alexiosc/cft/documentation/latex/cft_book/cft-hard-fdc.tex

% -*- latex -*-

\HtmlMetaDescription{This chapter (still empty) describes the Floppy
  Drive Controller (FDC) board which allows the connection of up to
  four floppy drives to the CFT. Both Shugart and IBM-style interfaces
  are supported, so that 8-inch units can be attached too.}
%\HtmlMetaGoogleDescription{}
%\HtmlMetaBanner{}
%\HtmlMetaTags{}

\section{Design}

\section{Theory of Operation}

\section{Implementation}

\section{Operation}

\section{Schematics}

The following page shows the full schematic drawing of the FDC
board.

\cleardoublepage
\includeschns{47}{Floppy Drive Controller}{sch2:fdc}
