alexiosc/cft/documentation/latex/cft_book/cft-hard-vdu.tex

% -*- latex -*-
\HtmlMetaDescription{The Video Display Board gives the CFT the ability to display colourful graphics on a monitor, and allows keyboards (and potentially mice) to be attached.}
%\HtmlMetaGoogleDescription{}
%\HtmlMetaBanner{}
%\HtmlMetaTags{}

\label{chap:hard-vdu}

The VDU card is a semi-intelligent Video Display Unit controller inspired by
both the Motorola MC6845 (and various designs based on it) and the Texas
Instruments TMS9918. It is capable of a number of useful features designed to
offload simple tasks from the processor:

\begin{itemize}
\item 640×480 and 320×480 native resolutions.
\item Square pixels at a 4:3 aspect ratio.
\item Text modes include: 40×30, 40×60, 80×30 and 80×60.
\item Low resolution graphics from 40×30 to 160×120.
\item High resolution bitmap graphics include 320×240, 320×480, 640×240 and
  640×480.
\item Any permuation of horizontal and vertical resolution can be used,
  including ones with exotic pixel aspect ratios.
\item Analogue VGA Output.
\item 64 colours (6 bits per pixel) with no look-up tables (palettes).
\item Hardware cursor with blink and colour control.
\item Inverse and Blink attributes.
\item Fully reprogrammable character generator capable of 4,096 16-line
  characters.
\item Up to 1,024 different characters can appear per mode.
\item 24-bit planar storage model multiplexed on 256K×16 Static RAM memory.\footnote{Physical memory may be larger than needed.}
\item Limited terminal-like behaviour.
\item Smooth (pixel-level) horizontal and vertical srolling.
\item Cell-level scrolling and paging in all modes using a 128×512 virtual
  screen.
\item Fully programmable independent split screen modes (top-bottom).
\item Can generate interrupts on vertical sync or when an arbitrary scanline is
  reached.
\end{itemize}

Some of these features were implemented as ‘bells and whistles’ (the generic
nature of split screens and smooth scrolling is an example), but most are side
effects of the simplicity of the rest of the design.

Much of this chapter assumes knowledge of how raster displays work. A full
explanation is beyond the scope of this document, but many can be found online.

\todo{Move these unconnected sections into the standard outline.}

\section{History}

The VDU card has undergone various revisions. The original version
used discrete HC family CMOS logic, and was meant to drive up to
640×400 using the canonical 25.175~MHz VGA pixel clock.

The second revision refined the design, keeping the discrete logic. It
was simulated successfully up to a point, but meeting constraints and
fixing timing bugs became too much of a hassle.

The third revision rebuilt the design on a Xilinx CPLD using the same
resolution and pixel clock.

The fourth and current revision migrated to an Altera Max V CPLD. The
resolution increased to 640×480 using a slightly non-standard 32~MHz
clock — the standard VGA clock is 31.5~MHz. The pixel clock is derived
from a 64~MHz clock used to drive a complex SDRAM memory controller
state machine.

\section{Design}

The main design constraint for the VDU card has been allowing easy access from
the CFT host to the video memory. Most home computer with video capacibilities
were designed {\em around\/} their graphic subsystems rather than vice
versa. This was often done to the extreme: in many cases, the processor clock
rate was lowered a lot to simplify the host/video memory sharing logic. In the
case of the CFT this was never a consideration, and so the processor and VDU
subsystem are in two different clock domains. The CFT runs in a 4 MHz clock
domain, while the VDU card runs in a 25 MHz clock domain.

Also, the CFT uses banked memory, and this considerably limits the convenience
of accessing memory directly, as well as the amount of memory that can easily
be mapped.

The solution to both problems is (somewhat counter-intuitively) to {\em
  never\/} let the CFT access video display memory directly. Once video memory
is entirely the domain of the VDU card, its design is simplified greatly.

Instead of direct access to the memory, an indirect system is provided. In this
way, both the processor and VDU can run at optimal speeds, and communicate
asynchronously.

\subsection{VDU Engine}

The VDU card is designed to be built around a CPLD chip. Like the DEB card,
this may be seen as ‘breaking project rules’, but I have my reasons:

\begin{itemize}
\item Ability to debug. More likely than not, I would need to locate and fix
  numerous issues with the implementation after construction. This would be
  much easier with a CPLD, where the connections between units are described
  rather than made with a soldering iron.
\item Board size. Early on in the project, the VDU board started to compete
  against the processor boards in size and complexity. The chip count of the
  yet unfinished board was nearly 100.
\item Cost. Board size, chip count, and complexity directly translate to
  cost. Building the processor is the heart of the project — having the VDU
  card is nice, but beyond the original scope of the project.
\item Timings. A CPLD chip has 1ns propagation delays. With discretes,
  a large portion of the design effort centres around not violating
  timing constraints.
\item Better derating margins. CPLD chips are designed to run at over
  100~MHz, and this design runs mostly at 32~MHz, with a small portion
  clocked at 64~MHz.
\item Chip availability. A number of 74AC family chips are required
  due to their low (6ns) propagation delays. These are quite hard to
  find in through-hole packages, and costlier.
\item Image quality. I have a good eye, and bad image quality grates on me. With a
  CPLD chip the timings can be tighter, and display quality can be crisp
  without pushing the limits of the technology.
\item Still a learning experience. This would be my first ever surface mount
  project, my first CPLD project, my second 3.3V-based project, my first
  multi-voltage project, and my first video-generating project.
\item Backplane space. There are 19 slots on the CFT backplane, and I would
  like to avoid using all of them. With a CPLD, the entire design can fit
  comfortably on one board.
\end{itemize}

This change in direction may affect other boards, too, to keep costs down.

Using a CPLD opens up the design to cheaper, 3.3V components, but it
also makes it significantly simpler. There are seven active components
on the board: the CPLD, three SRAM chips, two \HCT{245} buffers used
as level shifters, and a 64~MHz oscillator. A rendered version of this
board can be seen in~\fcf{fig:vdu-board}.

\begin{figure}
\centering
\includelarge[width=0.85\columnwidth]{figs/video-max5-revF-top.jpg}\vspace{1em}\\
\caption{\label{fig:vdu-board}A rendered image of the VDU board. The CPLD makes
  the design quite sparse, and routing the board is easy — after all, the pins
  can be assigned any function and re-ordered at will to match the board
  layout.}
\end{figure}

\subsection{Video Format}

A video frame consists of a number of scan lines, each made of a
number of pixels, as shown in~\fcf{fig:video-frame-format}.

Each line is sent to the display serially, left to right. To help monitor
timing, lines start with a horizontal sync pulse (\ns{HSYNC}) to help
synchronise the framebuffer and display. This pulse is preceded by a number of
‘blank’ pixels known as the ‘front porch’, and followed by a similar zone
called the ‘back porch’. The horizontal sync pulse signals the display to begin
a new field. So, counter-intuitively, the front porch is the {\em end\/}
(right) of the previous field, and the back porch is the beginning of the
next. The formal horizontal waveform is shown in~\fcf{fig:vdu-horz-timing}.

Multiple fields are sent to the display serially, top to bottom. A blanked Front
Porch is sent first, followed by a vertical sync pulse (\ns{VSYNC}), followed
by a Back Porch and a number of fields in the format described above. Since
\ns{VSYNC} instructs the display to move to the top of the screen, starting a
new frame, the vertical Front Porch will appear at the bottom of the {\em
  previous\/} frame, while the Back Porch will appear at the top of the next
frame. The formal vertical waveform is shown in~\fcf{fig:vdu-vert-timing}.

The width of each of these subfields of each field and frame is expressed in
ticks of a {\em pixel clock\/}. A video format or mode is thus defined in terms
of the following nine parameters (often expressed in terms of other parameters,
arithmetically derived from these):

\begin{itemize}
\item The frequency or period of the pixel clock. This controls the physical size of each pixel on the screen, as well as the display resolution. It serves as the unit of timing, and all other parameters are expressed in terms of integer multiples of the pixel clock period.
\item The number of horizontal front porch pixels.
\item The number of horizontal video pixels. This is the same as the horizontal resolution in pixels.
\item The number of horizontal back porch pixels.
\item The number of pixels for which horizontal sync is active.
\item The number of vertical front porch pixels.
\item The number of vertical video pixels. This is the same as the vertical resolution in pixels.
\item The number of vertical back porch pixels.
\item The number of pixels for which vertical sync is active.
\end{itemize}

The CFT's VDU produces a single timing mode which produces an almost standard
VESA 640×480 resolution (at 74 frames per second, where VESA specifies 75)
using the following timings:

\begin{center}
\label{table:vdu-timings}
\zebra
\begin{tabular}{lrlrl}
            & Value & Unit & Time & Unit \\
\hline
Pixel clock frequency            &   32.000 & MHz    &  31.2500 & ns \\
\hline
Horizontal Front Porch width     &       24 & pixels &  0.7500 & μs \\
Horizontal Sync width            &       40 & pixels &  1.2500 & μs \\
Horizontal Back Porch width      &      128 & pixels &  4.0000 & μs \\
Horizontal Line width            &      640 & pixels & 20.0000 & μs \\
Total line width                 &      832 & pixels & 26.0000 & μs \\
Line (horizontal sync) frequency &   38.462 & kHz    & 26.0000 & μs \\
\hline
Vertical Front Porch height      &        9 & lines &   0.2340 & ms \\
Vertical Sync height             &        3 & lines &   0.0780 & ms \\
Vertical Back porch height       &       28 & lines &   0.7280 & ms \\
Vertical video height            &      480 & lines &  12.4800 & ms \\
Total frame height               &      520 & lines &  13.5200 & ms \\
Frame frequency (refresh rate)   &   73.965 & Hz    &  13.5200 & ms \\
\hline
\end{tabular}
\end{center}

These timings were generated using the VESA Co-ordinated Timing Generator
spreadsheet\footnote{Available at
  \url{http://files.bedroomlan.org/cft/video-board/CVTd6r1.xls}.} to maximise
compatibility and were tested on a number of monitors.

A horizontal resolution of 640 was chosen because it allows for 80 columns of
8-pixel wide characters. The vertical resolution of 480 was a more difficult
choice. 480 lines provide a classical 4:3 aspect ratio. Even though this is
running at a very slightly non-standard refresh rate, it is well within
tolerance for most, if not all multisync devices and works particularly well
with TFT monitors, producing images as crisp as can be expected from an
interpolated scaled up image.

A number of other resolutions were originally considered and ruled out:

\begin{itemize}
\item the 320×200 MCGA resolution is actually a 640×400 resolution with
  horizontal and vertical pixel doubling, implemented this way because the
  horizontal scan frequency of single-frequency VGA monitors was 31.15~kHz. As
  such, this would reduce the pixel resolution but still have the same timing
  requirements.
\item the 640×200 CGA resolution is, again, a 640×400 resolution with vertical
  line doubling and pixels with an aspect ratio of 8:3 — not particularly
  pleasing or useful. Since the horizontal resolution is the biggest hurdle in
  timing, this was also abandoned.
\item The 640×350 EGA-compatible resolution is a VGA 640×400 resolution with taller front
  and back porches, and the wrong pixel aspect ratio for modern monitors. Like
  the resolutions above, it made no sense to use it.
\item 640×400 was also attempted, and the design ran on this resolution for a
  while.  This is a 16:10 aspect ratio mode, so displays either slightly
  distorted on modern 16:9 devices, or using pillarboxes (narrow black bars at
  the left and right edge of the screen). This depends on the monitor
  used. However, many TFT monitors had trouble displaying a crisp image at this
  resolution. Additionally, the standard VGA pixel clock (25.175~MHz) for
  640×400 could not be used: the VDU design needed a clock double that of the
  pixel clock to allow both video and host accesses to the video memory, and
  there are no 50.35~MHz oscillators in the market.
\end{itemize}

\begin{figure}
 \centering     
 \inputfigure{figure-vdu-frame-format}
 \caption[Video frame format]{\label{fig:video-frame-format} Format of a video
   frame, showing porches, sync signals and video data. The frame is not drawn
   to scale. The definitions of ‘front’ and ‘back’ are sometimes reversed.}
\end{figure}

\subsection{Output Format}

Video data is output via a standard analogue VGA socket, as illustrated
in~\fcf{fig:vdu-vga-pinout}. The video data is split into RGB data and
synchronisation signals.

Video data is output in separate Red, Green and Blue channels as analogue
waveforms in the range 0–0.7V, where 0V ideally represents an absence of colour
in that channel, and 0.7V represents full intensity of that colour. The VDU
card can put four voltages on each line (shown in~\fcfp{fig:vdu-analogue-ramp}):

\begin{center}
\zebra
\begin{tabular}{rccc} 
  Voltage & Intensity & Value & Equivalent X11 hex value \\
  \hline
  0~mV      & 0\%      & 0 &  \hex{00} \\
  233~mV    & 33\%     & 1 & \hex{55} \\
  466~mV    & 66\%     & 2 & \hex{AA} \\
  700~mV    & 100\%    & 3 & \hex{FF} \\
  \hline
\end{tabular}
\end{center}

Since each channel may have four values and there are three channels, there are
$4^3=64$ total colours available. These intensities are identical to the
intensities used in the vast majority of 64-colour display platforms, including
the IBM CGA (though the CGA could only generate 16 of these colours) and IBM
EGA. The entire gamut of colours is illustrated
in~\fcf{fig:vdu-colour-palette}\footnote{But only in principle — printed
documents cannot display video colours correctly.}.

In the spirit of supporting badly calibrated or designed drivers, many monitors
allow for variations in the voltage ramp: some monitors calibrate the minimum
intensity based on voltage measurements during horizontal or vertical
sync. Other devices extend the maximum intensity based on what the driver is
producing, perhaps up to 1V. The VESA standard dictates 0–700mV, however.

\begin{figure*}
  \centering
  \inputfigure[width=6cm]{figs/DE15_Connector_Pinout}
  \vspace{1em}\par

  \zebra
  \begin{tabular}{rlll}
    Pin & Standard VGA & CFT VDU \\
    \hline
    1  & Red video & Red video \\
    2  & Green video & Green video \\
    3  & Blue video & Blue video \\
    4  & ID2/Reserved & Not connected \\
    5  & Ground & Ground \\
    6  & Red return & Analogue ground \\
    7  & Green return & Analogue ground \\
    8  & Blue return & Analogue ground \\
    9  & Key/+5V~DC & +5V~DC \\
    10 & Ground & Ground \\
    11 & ID0/Reserved & Not connected \\
    12 & ID1/SDA & Not connected \\
    13 & Horizontal sync & Horizontal sync \\
    14 & Vertical sync & Vertical sync \\
    15 & ID3/SCL & Not connected \\
    \hline
  \end{tabular}
  \caption[VGA Connector Pin-Out]{\label{fig:vdu-vga-pinout}VGA Connector
    pin-out. This is a view of the mating side of a VGA socket. The \ps{ID0–3}
    signals are obsolete and have been replaced (on a conformant VGA) with an
    I²C two-wire interface to transfer monitor parameters to the host. This is
    ignored on the CFT. The ‘key’ pin was missing on original VGAs to allow
    socket keying, but now carries 5V power.}
\end{figure*}

\begin{figure}
 \centering
 \inputfigure{figure-vdu-analogue-ramp}
 \caption[Analogue Channel Ramp]{\label{fig:vdu-analogue-ramp} Analogue channel
   ramp. The black line represents the VDU's ramp superimposed on the ideal
   (analogue) ramp.}
\end{figure}

\subsection{Memory}

The VDU board addresses 17 bits of 16-bit memory, for a 262,144×16 address
space. This memory is implemented as a single static RAM chip with an access
time of 15~ns or below. This memory is used for three distinct memory blocks,
discussed in~\cf{sec:vdu:memory-org}. Using a single chip keeps the design
simpler, reduces the number of bus signals between the CPLD and memory, keeps
signal integrity high by minimising trace lengths, and simplifies routing the
PCB.

\subsection{Indirect Host Access}

Rather than a complex scheme of multiplexed memory accesses, the VDU card
accesses its memory privately. To facilitate host access, it makes available
addresses, data and VDU commands via I/O ports. All communication with the
processor is now achieved via a mere three registers, with additional ones used
to change other variables of the VDU subsystem.

On most computers, a three-port access would constitute a severe
bottleneck. This is certainly the case for architectures with relative indirect
addressing and linear memory. On the CFT, however, accessing a linearly mapped
VDU device would involve performing address arithmetic, storing the result in a
register, then using this value to perform an indirect memory access. This is
precisely the way it is done by the VDU card. Rather than using a memory space
register to store the intermediate address result, a VDU register is used
instead. Commands allow autoincrement of these addresses in the X and/or Y
direction, and reduce the number of CFT instructions needed to perform most
tasks.

Commands are dispatched to the VDU card asynchronously (as far as it is
concerned), and executed at first opportunity. This can be longer than a CFT
write cycle, especially when using repeated commands. Four techniques may be
combined freely to detect if a command has completed execution:

\begin{enumerate}
\item Polling the \port{CRR} register (for repeated commands only). While the
  value is non-zero, the VDU is busy.
\item Polling the \field{GO} bit in the \port{CMD} register.
\item Reading from the \port{HAR} or \port{CPORT} registers will block with
  with zero or more wait states until the VDU host interface is idle. This
  allows synchronous access without the tedium of polling loops.
\item Interrupt-based operation: if configured to do so, the VDU will signal an
  interrupt when command execution has completed.
\end{enumerate}

%% \subsection{Video}

%% The video side of the VDU card is a simple analogue VGA output using either a
%% DB15 socket or a 5×2 header. Analogue output is achieved by using a resistor
%% ladder with two values per channel. This gives six bits of colour, or 64
%% colours.

%% The timing of the video frame is a compromise between easily obtained
%% oscillators for the pixel clock and compatibility with a wide range of display
%% devices. As illustrated in~\pageref{table:vdu-timings}, the mode displa

%% output is timed for approximate (but not match) the timings of VESA CVT 0.26MA, which is a 640×480
%% display mode with a 31.500~MHz pixel clock and a 75~Hz (actually, 74.228~Hz)
%% refresh rate. This mode is guaranteed to work with a very wide range of display
%% devices because it happens to be the same display mode PC compatibles use to
%% display their power on self-test messages.

%% The video card lacks a programmable frame engine, but this particular set of
%% timings can be used to provide a wide range of modes, from 40×30 to
%% 640×480. That is five octaves per dimension, allowing 25 different base modes.

\section{Logical Design}

This section describes the design in greater detail, focusing on how the VDU
behaves from a software perspective. The discussion is based on the high level
block diagram of the VDU, shown in~\fcf{fig:vdu:block-diagram}.

\begin{description}

\li{The display registers} (\cfp{sec:vdu:display-registers}) allow the VDU's
behaviour to be modified by the host.

\li{The frame engine} (\cfp{sec:vdu:frame-engine}) generates a properly timed
image frame, including video enables and sync signals.

\li{The character generator} (\cfp{sec:vdu:chargen}) receives codepoints,
character set information and screen geometry data from the sequencer, and
yields pixel patterns for the video generator.

\li{The colour/attribute engine} (\cfp{sec:vdu:colour-engine}) receives colour
information from the sequencer, combines it with hardware cursor data, and
provides foreground and background colours for the video generator.

\li{The video out circuitry} (\cfp{sec:vdu:video-out}) receives pixel and
colour data and produces RGB colour and synchronisation signals used to
directly drive a monitor.

\li{The display memory} (\cfp{sec:vdu:memory-org}) stores video data received
from the host, and transmitted to the video generation circuitry via the memory
sequencer.

\li{The memory sequencer} (\cfp{sec:vdu:memory-sequencer}) uses the timing
signals from the video engine to co-ordinate memory accesses, reading from
display memory and generating a data stream used to drive the character
generator and colour/attribute engine.

\li{The host interface} (\cfp{sec:vdu:host-interface}) provides an additional
set of host-accessible registers which give the CFT indirect access to display
memory, but make up for it by providing some advanced functionality to offload
common tasks from the processor to the VDU.

\end{description}

\begin{figure}
 \centering
 \inputfigure{figure-vdu-block-diagram}
 \caption[High Level Block Diagram of the VDU
   Card]{\label{fig:vdu:block-diagram} High Level Block diagram of the VDU
   card.}
\end{figure}

\subsection{Display Registers}
\label{sec:vdu:display-registers}

From the host's point of view, there are twelve display registers (including
the keyboard register), most of which are write-only. They are meant to be
accessible in a block of 16 at I/O addresses \hex{1F0}–\hex{1FF}, the remaining
locations allocated to the host interface and keyboard interface.

From the VDU's point of view, there are many more, narrower registers; they are
simply bundled up into groups of up to 16 bits for easier, simultaneous access
by the host.

There are two copies of some registers, numbered with a ‘0’ or ‘1’
suffix. These are used in split screen layouts, each copy performing the same
task for the top and bottom part of the split.

The register file is shown in~\fcf{fig:vdu-register-file}.

\subsection{Frame Engine}
\label{sec:vdu:frame-engine}

The video engine generates a properly timed image frame, including video
enables and sync signals. It also generates strobes for the sequencer, which it
uses to start memory reads early. This is done so that a full character is read
for display as soon as video is enabled. Since this takes three memory reads
plus decoding, the frame engine signals the sequencer early. This phase
difference is adjustable to allow for implementation differences. It is also
runtime-adjustable between zero and seven pixel clocks. This can be used to
shift the screen one to seven pixels to the left, facilitating smooth
horizontal scrolling.

The horizontal and vertical frame waveforms are very similar. They are shown
in~\fcf{fig:vdu-horz-timing} and~\fcf{fig:vdu-vert-timing}.

Internally, the frame engine is implemented as a relatively unremarkable video
frame state machine, using two counters (for horizontal and vertical
positions), comparators, and a number of single-bit registers to hold the
current state of sync, video enable, and other signals.

The frame engine is clocked at one eighth the pixel clock frequency, because it
deals with whole 8-pixel cells and horizontal frame timings are more often than
not multiples of 8. This is a remnant of the days when the frame engine was a
bank of \HC{590} counters and \HC{688} comparators, where the cell rate was
well within tolerances but the pixel rate was tough to meet. This is also the
historical reason for the frame measurements' divisibility by 8 in the CGA, EGA
and VGA. Even though VGAs never used discrete ICs for frame generation, the
CGA's MC6845 used this technique to meet timings.

\begin{figure*}
\centering
\inputfigure{figure-vdu-horz-timing}
\caption[Horizontal Timing]{\label{fig:vdu-horz-timing} Horizontal video timing. The polarity of \ps{HSYNC} is reversed before driving the monitor (negative horizontal sync).}
\end{figure*}

\begin{figure*}
\centering
\inputfigure{figure-vdu-vert-timing}
\caption[Vertical Timing]{\label{fig:vdu-vert-timing} Vertical video timing. The polarity of \ps{VSYNC} is reversed to drive the monitor (negative vertical sync).}
\end{figure*}

\subsection{Character Generator}
\label{sec:vdu:chargen}

The Character Generator is responsible for interpreting the codepoints in the B
plane and producing their actual, visible representation in pixels. In many
respects, it may be considered as a font renderer. It always renders fonts in
an 8×16 pixel cell, although depending on the mode, not all lines need be
used. It does this by providing an address scheme for a 65,536×8 area in
display memory, using information from various sources.

\begin{bitfield}
  \bitfieldGroup{4}{cfthl!50}{Line}
  \bitfieldGroup{8}{cfthl!25}{B Plane Value}
  \bitfieldGroup{2}{cfthl!50}{CS1}
  \bitfieldGroup{2}{cfthl!25}{CS2}
\end{bitfield}

The \field{Line} field identifies which line of the character cell is
required. An 8×16 character cell means there are 16 lines in each character
shape. The character itself is identified by the the remaining bits in the
address.

The primary source of information comes from the B plane, in the form of the
character codepoint within a character set. There are 256 codepoints (and thus
characters) per character set.

There are sixteen character sets, and four of these may be used per mode,
according to the values of \field{CS1} and \field{CS2}. \field{CS1} is set in
the C plane, so may be set independently for each character displayed. This
implies that up to 1,024 different character shapes may appear simultaneously
on-screen. \field{CS2} is set in the mode register, and thus globally for the
entire screen. The following table shows the character sets and their origin
addresses:

\begin{center}
  \zebra
  \begin{tabular}{rrrc}
    %\noalign{\smallskip}\hline\noalign{\smallskip}
    %\\\hline
    \field{CS2} & \field{CS1} & Set & Start Address\\
    %\noalign{\smallskip}\hline\noalign{\smallskip}
    \hline
    0 & 0 &  0 & \hex{0000} \\
    0 & 1 &  1 & \hex{1000} \\
    0 & 2 &  2 & \hex{2000} \\
    0 & 3 &  3 & \hex{3000} \\
    \hline
    1 & 0 &  4 & \hex{4000} \\
    1 & 1 &  5 & \hex{5000} \\
    1 & 2 &  6 & \hex{6000} \\
    1 & 3 &  7 & \hex{7000} \\
    \hline
    2 & 0 &  8 & \hex{8000} \\
    2 & 1 &  9 & \hex{9000} \\
    2 & 2 & 10 & \hex{a000} \\
    2 & 3 & 11 & \hex{b000} \\
    \hline
    3 & 0 & 12 & \hex{c000} \\
    3 & 1 & 13 & \hex{d000} \\
    3 & 2 & 14 & \hex{e000} \\
    3 & 3 & 15 & \hex{f000} \\
    \hline
  \end{tabular}
\end{center}

Since four bits of the character generator RAM address are always used for the
cell line, all character patterns are formed in a 16-line cell and character
patterns are always aligned with a 16-byte boundary. Depending on the mode,
only some of these patterns will be used:

\begin{center}
  \zebra
  \begin{tabular}{rrll}
    %\noalign{\smallskip}\hline\noalign{\smallskip}
    %\\\hline
    Screen Lines & Cell & Cell lines & CG Address range\\
    %\noalign{\smallskip}\hline\noalign{\smallskip}
    \hline
     30 & 8×16 & 0–15 & \hex{XXXX} (all)\\
     60 & 8x8  & 0–7  & \hex{XXX0}–\hex{XXX7}\\
    120 & 8×4  & 0–3  & \hex{XXX0}–\hex{XXX3}\\
    240 & 8×2  & 0–1  & \hex{XXX0}–\hex{XXX1}\\
    480 & 8×1  & 0    & \hex{XXX0}\\
    \hline
  \end{tabular}
\end{center}

Each 8-bit value in display memory corresponds to a group of eight pixels. A
set bit (\bin{1}) corresponds to a foreground pixel, and a \bin{0} bit
corresponds to a background pixel. The most significant bit is shifted out
first and corresponds to the leftmost pixel in the group. This is the de facto
standard behaviour for most bitmap-based character generators.

\subsection{Colour/Attribute Engine}
\label{sec:vdu:colour-engine}

The colour/attribute engine controls how the character generator's outputs are
interpreted. The character generator outputs binary patterns corresponding to
foreground and background colours. These colours are selected by the
colour/attribute engine using the following information:

\begin{itemize}
  \item The foreground and background colours at this position, as read from the
  C plane.

  \item Whether or not this position contains the hardware cursor, and
  the cursor is on or blinking (and currently in the ‘on’ blink state). If the
  cursor is steadily on or blinking and in the ‘on’ state, the cursor
  foreground and background colours override the current positions's colours as
  retrieved by the C plane.

  \item Whether or not this position has the inverse video attribute. If so, the
  foreground and background colours specified in the C plane are swapped.

  \item Whether or not this position has the blink video attribute, and blinking
  is in the ‘off’ state. If this is the case, the foreground is made equal to
  the background, making pixels ‘disappear’. This is identical to the CGA's
  (and VGA's) blink behaviour, where characters disappear and reappear against
  their background. If both inverse video and blinking are selected, both
  work. The net effect is that inverted blinking has a 180° phase difference to
  normal blinking: characters appear when normal blink characters disappear,
  and vice versa. This is illustrated in \fcf{fig:attribute}.
\end{itemize}

\subsubsection{Colour Space}

The VDU card has a palette of 64 RGB colours. No look-up tables (LUTs)
are used and all colours may be present on the same frame. Colours are
defined in traditional RGB format, with two bits per channel, for a
total of six bits (64 colours).

\begin{nbitfield}{6}
    \bitfieldGroup{2}{red!25}{Red}
    \bitfieldGroup{2}{green!25}{Green}
    \bitfieldGroup{2}{blue!25}{Blue}
\end{nbitfield}

\begin{datastructure}[Bits]{Colour}
  \dsdesc{\hex{0}–\hex{1}}{Bits}{%
    The value of the colour's red component.
  }
  %
  \dsdesc{\hex{2}–\hex{3}}{Bits}{%
    The value of the colour's green component.
  }
  %
  \dsdesc{\hex{4}–\hex{5}}{Bits}{%
    The value of the colour's blue component.
  }
  %
\end{datastructure}

Possible colour components are 0\%, 33\%, 66\% and 100\%. In hexadecimal,
components are \hex{00}, \hex{55}, \hex{AA} and \hex{FF}, which match the
colour components of IBM display cards from the CGA to the EGA (which has the
exact same palette, though it can only display up to 16 colours at a time).

\begin{figure*}
 \centering
 \inputfigure{figure-vdu-colour-palette}
 \caption[The 64-colour palette]{\label{fig:vdu-colour-palette} The 64-colour
   palette. Each colour swatch is numbered as on the CFT, and includes its
   X11-style 24-bit hexacedimal RGB triplet for reference. Please note that
   colours may render slightly differently depending on the medium used. The
   eight classic video colours are 0 (black), 3 (red), 12 (green), 15 (yellow),
   48 (blue), 51 (magenta), 60 (cyan) and 63 (white). There is a four-stage
   grey ramp with 0 (black), 21 (dark grey), 42 (light grey), 63 (white).}
\end{figure*}

\subsubsection{Blinking}

There are two schools of thought on implementing blinking. The Sinclair
approach did it by toggling the inverse video attribute at set intervals. This
resulted in characters' foreground and background colours alternating for a
characteristic look, which does not quite resemble true blinking. The IBM
approach is what most people would expect from blinking: text disappears and
reappears at set intervals. This is the method used by the VDU, as mentioned
above. It is implemented by assigning the background colour to the foreground
colour at set intervals, which effectively makes foreground pixels disappear
into the background.

The intervals in question are using the vertical synchronisation
signal (defining the frame rate) as a clock, so blinking is
synchronised with the frame and all blinking characters on the screen
blink in unison. Three blink rates are produced: fast blink, where the
frame rate is divided by 8, slow blink, where it is divided by 16, and
character blink, where it is divided by 32. Character blinking is used
to blink characters. Slow or fast blink may be used to blink the
hardware cursor, to enhance its visibility. Blink rates are outlined
in the following table, based on the VDU's 73.965~Hz refresh rate.

\begin{tabular}{lrrr}
  Blink type & Divider & Frequency (Hz) & Period (ms) \\
  \hline
  Fast       &   8   &   9.25   &   108 \\
  Slow       &  16   &   4.62   &   216 \\
  Character  &  32   &   2.31   &   432 \\
  \hline
\end{tabular}

\begin{figure}
  \centering
  \ifxetex
    
  \else
    \begin{htmldiv}{includegraphics small png}%
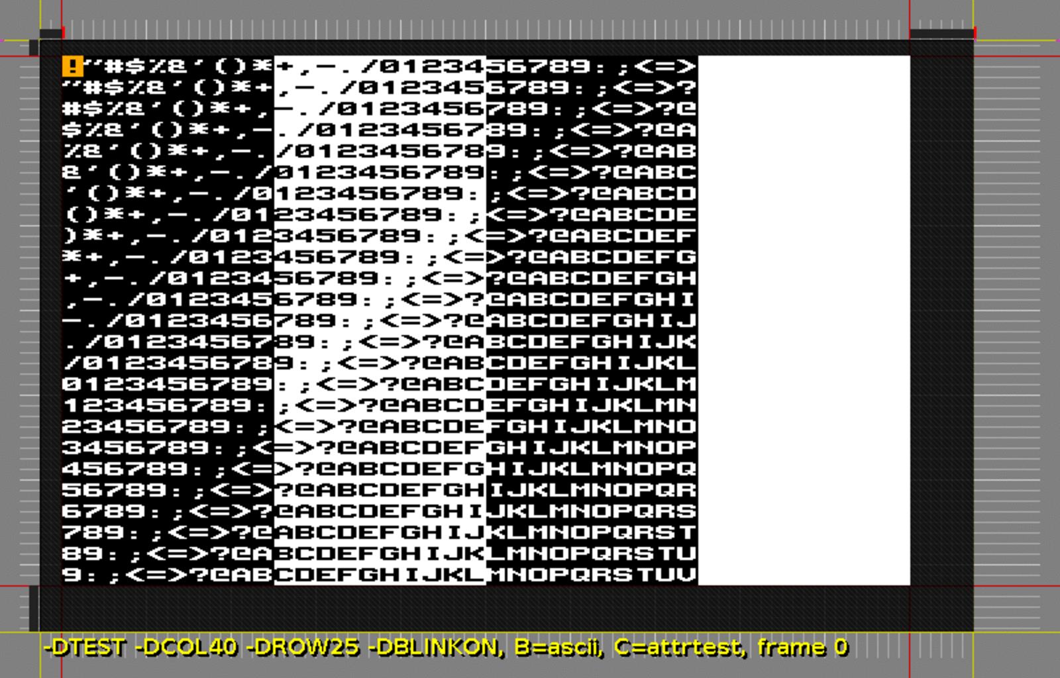
[picture p1: documentation/latex/figs/attribute-test.gif]
      %
    \end{htmldiv}%
  \fi
  \caption[Demonstration of Attributes]{\label{fig:attributes}A demonstration
    of all four attribute combinations using white text on a black
    background. From left to right: normal text, inverse video (black on
    white), blinking, and inverse video with blinking. The top frame is phase 0 of the
    blinking timer, the bottom frame is phase 1, showing how blinking text
    changes over time.}
\end{figure}

\subsubsection{Hardware Cursor}
\label{sec:vdu:cursor}

The hardware cursor is merely a location in video memory where colours are
altered to highlight where data entry is taking place. The location, foreground
and background are freely adjustable using two registers. Additionally, the
cursor appearance may be changed: it may be steadily on, blink slowly, blink
rapidly, or be altogether disabled.

The cursor may be hidden by assigning it to an off-screen location, or by
turning it off using its control register.

There is only one cursor, even in split screen mode. If the two halves of a
split screen mode partially (or wholly, for whatever reason) overlap and the
cursor is within their intersection, it will appear in both, with an identical
appearance. Its size may differ, depending on the modes set in the two halves.

The standard appearance of the cursor is orange background (colour 11, or
\hex{\#FFAA00}), black foreground and fast blink.

Due to the way the cursor is generated, it will always cover the entire cell it
is positioned at. Underline and half-block cursors are not possible, and
neither are shaped cursors like the Apple chequered box. These may, however, be
implemented in software.

\subsubsection{Attributes and the Cursor in Graphics Modes}

High-resolution graphics modes are functionally identical to text modes, and
the colour and attribute engine treats them as such. Conventional use of
graphics modes disables attributes and the hardware cursor. Not so on the VDU
board. The programmer is free to disable the hardware cursor and not use
attributes, but they are still there and can be used.

Special effects may be achieved by using the blink and/or invert attributes,
and even altering the character set field may be useful in some cases. The
cursor may be made visible, but will not be particularly useful: it will appear
as an 8 or 16-pixel wide line.

\subsection{Video Out Circuitry}
\label{sec:vdu:video-out}

This part of the VDU is responsible for generating the video signal as sent to
the monitor. It is sent sync and video enable signals, as well as a pixel
pattern from the character generator and foreground and background RGB data
from the colour/attribute engine.

It enforces video blanking by sending out black pixels while video enable is
off (outside of the visible areas of the image frame). It also appropriately
formats the sync signals — currently, by inverting both of them.

At the centre of the video out circuitry is a shift register and
multiplexer. The shift register shifts the pixel data one bit at a time, most
significant bit first, and uses each bit to select between the background (when
the bit is clear) and foreground (when the bit is set). Both foreground and
background are expressed as three pairs of RGB signals, two bits per
channel.

The colour bits selected by the multiplexer, along with the sync signals are
registered to synchronise them fully, then output to the monitor. The sync
signals are output as is, while the RGB signals directly drive three 2-bit
resistor networks to generate the appropriate voltages.

This is the most timing-critical part of the VDU, as the shift register and
colour registers must be loaded simultaneously, and immediately after the end
of the previous cell data. This is easy with a CPLD, but not as trivial with
discrete logic.

\subsection{Video Memory}
\label{sec:vdu:memory-org}

The VDU board uses three 65,536 sections of memory, one 16 bits wide and two 8
bits wide. This memory is arranged around a 16-bit data bus. The CPLD
multiplexes these sections to fit a single 128K×16 SRAM device, although a
256K×16 device is used. 16-bit SRAM devices may be operated as two disjoint
8-bit devices, which allows the VDU to take better advantage of the space, as
shown in~\fcf{fig:vdu-memory-map}.

Using this feature, two of the three memory areas are folded together and
stored in the same addresses. The 17th address line is used to select between
these two areas and the third, 16-bit one. To reduce the number of signals
between display memory and CPLD, the memory sequencer accesses these areas
sequentially, not simultaneously.

\begin{figure}
 \centering
 \inputfigure{figure-vdu-memory}
 \caption[VDU Memory Map]{\label{fig:vdu-memory-map} Internal VDU memory organisation.}
\end{figure}

The three memory sections are as follows:

\begin{description}
  \li{The B Plane} is 8 bits wide and has one location per character cell. This plane
  contains the \gls{codepoint} of a character in the current character set.

  \li{The C Plane} is 16 bits wide and matches the B plane location for location. It
  describes the colour and appearance of the character contained in the
  corresponding location of the B plane\footnote{There is no A plane — B is for
    ‘bitmap’ and C is for ‘colour’.}.

  For obvious reasons, both B and C planes are the same size. They contain 65,536
  locations.

  \li{The Character Generator RAM} is the third section of memory. For each
  codepoint in the B plane, this section of display memory contains the pixel
  patterns for each line of the character. This section of memory is organised as
  65,536×8 bits. Each character shape is described by 16 bytes, which allows for
  up to 4,096 characters.
\end{description}

\subsubsection{Plane Organisation}

Each plane is organised as 512 rows of 128 columns each, as shown
in~\fcf{fig:plane-org}. This implies that the organisation of a plane is not
linear as is the case with other graphics systems: it is more like a
two-dimensional geometric plane. Each location is identified uniquely by a
16-bit address which may be seen as a co-ordinate data structure:

%\pagebreak

\begin{bitfield}
  \bitfieldGroup{7}{cfthl!50}{Column}
  \bitfieldGroup{9}{cfthl!25}{Row}
\end{bitfield}

\begin{datastructure}[Bits]{PlaneAddressVector}
  \dsdesc{\hex{0}–\hex{6}}{Integer}{%
    The X ordinate in the range 0–127.
  }
  %
  \dsdesc{\hex{7}–\hex{15}}{Integer}{%
    The Y ordinate in the range 0–511.
  }
  %
\end{datastructure}

\noindent This is word-packed as follows:

\noindent This scheme has a number of advantages: it simplifies plane
organisation from the hardware standpoint, avoiding additional counters and
possible modulo-N circuitry. It also makes it very easy to calculate addresses
on a computer that has no hardware multiply instruction. The downside is an
apparent waste of memory, but this is not actually so. The additional memory is
used as a large virtual screen, with the visible portion treated as a smaller
viewport.

To calculate the address of co-ordinates $(x,y)$, it is enough to
evaluate $128y+x$. This may be reduced to a bitwise left shift and a
bitwise or. In C, this would be something as simple as:

\begin{ccode}
#define addr(x,y) (((x) << 7) | (y))
\end{ccode}

In CFT Assembly, assuming $y < 512$ and $x < 128$ and using two left nybble rolls
and one right shift to get a seven-bit shift:

\begin{cftasmcode}
         LOAD y                      ; Load y
         CLL RNL                     ; Clear L and roll left 4 bits
         RNL                         ; Roll left another 4 bits
         SBR                         ; Shift right 1 bit
         OR x                        ; OR X (no addition needed)
\end{cftasmcode}

\noindent Since the X and Y ordinates are encoded separately in the address word, an
address may be seen as a two-dimensional vector. This provides additional
useful side-effects, discussed below.

\begin{itemize}
\item Virtual screens.
\item Hardware scrolling.
\item Double buffering and animation.
\item Toroidal (modulo N) virtual screen topology.
\item Limiting the virtual screen size with Modulo Vectors. 
\end{itemize}

\begin{figure}
 \centering
 \inputfigure{figure-vdu-plane-org}
 \caption[Plane Organisation]{\label{fig:plane-org} Plane organisation and
   addressing.}
\end{figure}

\subsubsection{Virtual Screens}

The visible part of the screen is smaller than the video memory and can be seen
as a viewport into a larger framebuffer. This viewport may be moved arbitrarily
by modifying the Start Address register vector (\cftin{SAR}), allowing a
logical resolution of 128×512. This vector is available as one of the VDU
card's registers.

This layout is illustrated in~\fcf{fig:vdu-virtual-screen}.

\begin{figure}
 \centering
 \inputfigure{figure-vdu-virtual-screen}
 \caption[Virtual Screen]{\label{fig:vdu-virtual-screen} Virtual Screen and
   Viewport. The viewport (which is what the physical screen displays) can be
   moved arbitrarily around the virtual screen. Please note that the diagram is not to scale.
 }
\end{figure}

\subsubsection{Hardware Scrolling}

Moving the visible screen downwards with respect to the logical screen is
indistinguishable from scrolling downwards. All that is needed to implement
scrolling is a single register write and (possibly) clearing the last line.

Of course, scrolling in any of the four cardinal directions is equally trivial.

\subsubsection{Double Buffering and Animation}

Double buffering involves constructing an image off-screen while another image
is being displayed. When the off-screen image is ready, the viewport is set to
display it, and a new image may be constructed in the area that was previously
visible. This allows for smooth animations and gives the impression that images
are set up instantly — a very important feature when the truth is actually far
from that.

The feasibility of a double-buffering setup depends on the mode being used. At
640×480, there is not enough video memory: of the 512 rows, 480 are used. At
640×240, there is space for a whole off-screen page. At 320×240, there is space
for {\em six\/} off-screen pages, arranged in a 3×2 formation in video
memory. All modes based on 40-columns have space for three pages (horizontally
arranged). The rest depends on the vertical size of each mode and whether or
not split screen is used.

A variation on double buffering can also be combined with hardware scrolling:
rather than using an entire page of off-screen data, the next row (for vertical
scrolling) or column (for horizontal scrolling) may be generated off-screen
before being scrolled into view. This technique saves considerable amounts of
video memory and can easily be used even at the full 640×480.

\subsubsection{Toroidal (Modulo N) Virtual Screen Topology}

When the viewport origin is set too close to the right or bottom edge of the
virtual screen, the co-ordinates shown on the physical screen will wrap around
to zero as a side effect of 7-bit and 9-bit ordinates wrapping
around. Ordinates are thus displayed modulo 128 horizontally and modulo 512
vertically and this defines a torus shape\footnote{The same topology as the
  maze in Pac-Man.}. This wrap-around effect is illustrated
in~\fcf{fig:vdu-virtual-screen-torus}.

\begin{figure}
 \centering
 \inputfigure{figure-vdu-virtual-screen-torus}
 \caption[Toroidal Topology of the Virtual
   Screen]{\label{fig:vdu-virtual-screen-torus} Co-ordinates are calculated
   modulo 128 horizontally, and modulo 512 vertically. Here, the viewport wraps
   around to the left of the virtual screen, displaying two disjoint sections
   of the display memory. The viewport can also wrap around the bottom, which
   would make it display four disjoint sections of the virtual screen.}
\end{figure}

\subsubsection{Limiting Virtual Screen Size with Modulo Vectors}
\label{vdu:sec:modulo-address}
Additional, generalised modulo N circuitry limits what is visible on the
viewport. A Modulo Address register (\cftin{MAR}) is provided, the two
ordinates of which are compared to the current address displayed. If an
ordinate equals the modulo ordinate, that ordinate of the display address is
reset back to zero. In C, these two checks (for x and y ordinates) would look
like this:

\begin{ccode}
  current_address.x = current_address.x % (modulo.x + 1);
  current_address.y = current_address.y % (modulo.y + 1);
\end{ccode}

The modulo is off by one, so the address listed is inclusive: it {\em does\/}
get displayed.

There are two distinct behaviours of this. If a modulo ordinate if off-screen
(e.g. greater by 80 or more for the x ordinate in for 80-column modes), the
size of the virtual screen is reduced. If a modulo ordinate is on-screen, part
of the screen will repeat. Some examples:

If \cftin{SAR} is \hex{0000} and \cftin{MAR} is \hex{0000}, the cell at
\hex{0000} will repeat on every column and row of the screen.

If \cftin{SAR} is \hex{0000} and \cftin{MAR} is \hex{007F}, the first line will
repeat down the screen.

In an 80×30 mode, if \cftin{SAR} is \hex{0000} and \cftin{MAR} is \hex{77F}
(co-ordinates $(14,127)$), the top half of the screen will repeat twice.

In an 80×30 mode, with \cftin{SAR} equal to \hex{0000} and \cftin{MAR} equal to
\hex{0ECF} (co-ordinates $(79,29)$), an 80×30 virtual screen is defined and scrolling is limited to this
area.

\begin{figure}
 \centering
 \inputfigure{figure-vdu-mar}
 \caption[Effects of the Modulo Address Register]{\label{fig:vdu-mar} Effects
   of using the Modulo Address Registers to change the point where addresses
   wrap around to zero. The shaded area will never be used. A number of visual
   effects can be achieved this way, including creating two separate areas of
   video memory to be used for split-screen setups, where one may freely use
   hardware-assisted scrolling while the other is slightly more limited in this
   way.}
\end{figure}

\subsection{Memory Sequencer}
\label{sec:vdu:memory-sequencer}

The Memory Sequencer co-ordinates scanline generation using timing hints from
the frame engine. It intermeshes three memory reads per character cell and uses
the spare time to allow host-issued commands to access video memory. It also
produces numerous strobe signals controlling most of the time-critical units in
the VDU.

In its test version, running on an FPGA with \gls{SDRAM} memory, the memory sequencer
also initialises video memory with a test pattern stored in the FPGA's ROM, and
includes an SDRAM state machine capable of issuing all necessary signals for
memory reads and writes, as well as refreshing the dynamic RAM (refresh cycles
happen during horizontal sync). SDRAM is slower than 10~ns SRAM, so the
FPGA-based sequencer implements a limited set of commands.

The \gls{SRAM} version is greatly simplified. The complex dynamic RAM state
machine is no longer needed, and neither are the additional states for
initialising the video memory — on the real VDU card, this is up to the
host. The simplicity allows all host commands to be implemented, and also
allows host commands to run throughout the video frame, not just while video is
enabled.

\todo{Draw SRAM waveforms once CPLD version is tested.}

\subsection{Host Interface}
\label{sec:vdu:host-interface}

The host interface comprises three read/write registers which give commands to
the VDU and access data in display memory. It is also responsible for
signalling various interrupts, if configured to do so.

Register \port{CPORT} provides read/write access to C plane data. \port{CMD}, A
shared command, BPORT and CGPORT register allows commands to be sent to the
VDU, and provides read/write access to B plane data, as well as write-only
access to the character generator RAM. Finally, register \port{CRR} allows
bursts of commands to be repeated up to 512 times.

In terms of design, the host interface is fairly complex since it provides
bridges across the clock domains of the CFT and VDU. On the CFT side, the
interface includes wait state logic to block the CFT from accessing crucial
registers while the VDU is using them. On the VDU side, the host interface is
implemented as a number of states in the memory sequencer state machine. These
states perform one or two memory reads, one or two memory writes, or, in the
case of the high-resolution graphics operators, one memory read and one or two
memory writes.

%% \section{Theory of Operation}

%% \subsection{Video Format}

%% A video frame consists of a number of scan lines called {\em fields}, each
%% made of a number of pixels, as shown in~\fcf{fig:video-frame-format}.

%% Each field is sent to the display serially, left to right. To help monitor
%% timing, fields start with a horizontal sync pulse (\ns{HSYNC}) to help
%% synchronise the framebuffer and display. This pulse is preceded by a number of
%% ‘blank’ pixels known as the ‘front porch’, and followed by a similar zone
%% called the ‘back porch’. The horizontal sync pulse signals the display to begin
%% a new field. So, counter-intuitively, the front porch is the {\em end\/}
%% (right) of the previous field, and the back porch is the beginning of the
%% next. The formal horizontal waveform is shown in~\fcf{fig:vdu-horz-timing}.

%% Multiple fields are sent to the display serially, top to bottom. A blanked Front
%% Porch is sent first, followed by a vertical sync pulse (\ns{VSYNC}), followed
%% by a Back Porch and a number of fields in the format described above. Since
%% \ns{VSYNC} instructs the display to move to the top of the screen, starting a
%% new frame, the vertical Front Porch will appear at the bottom of the {\em
%%   previous\/} frame, while the Back Porch will appear at the top of the next
%% frame. The formal vertical waveform is shown in~\fcf{fig:vdu-vert-timing}.

%% The width of each of these subfields of each field and frame is expressed in
%% ticks of a {\em pixel clock\/}. A video format or mode is thus defined in terms
%% of the following nine parameters (often expressed in terms of other parameters,
%% arithmetically derived from these):

%% \begin{itemize}
%% \item The frequency or period of the pixel clock.
%% \item The number of horizontal front porch pixels.
%% \item The number of horizontal video pixels.
%% \item The number of horizontal back porch pixels.
%% \item The number of pixels for which horizontal sync is active.
%% \item The number of vertical front porch pixels.
%% \item The number of vertical video pixels.
%% \item The number of vertical back porch pixels.
%% \item The number of pixels for which vertical sync is active.
%% \end{itemize}

%% The CFT's VDU produces a single timing mode which produces a standard VESA
%% 640×400 resolution (at 74 frames per second) using the following timings:

%% \begin{center}
%% \zebra
%% \begin{tabular}{lrlrl}
%%             & Quantity & Unit & Time & Unit \\
%% \hline
%% Pixel clock frequency &   25.000 & MHz    &  40.00000 & ns \\
%% \hline
%% Horizontal Front Porch width     &       16 & pixels &  0.64000 & μs \\
%% Horizontal Sync width            &       64 & pixels &  2.56000 & μs \\
%% Horizontal Back Porch width      &       80 & pixels &  3.20000 & μs \\
%% Horizontal Line width            &      640 & pixels & 25.60000 & μs \\
%% Total line width                 &      800 & pixels & 32.00000 & μs \\
%% Line frequency                   &   31.250 & kHz    & 32.00000 & μs \\
%% \hline
%% Vertical Front Porch height      &        3 & lines &   0.09600 & ms \\
%% Vertical Sync height             &        6 & lines &   0.19200 & ms \\
%% Vertical Back porch height       &       12 & lines &   0.38400 & ms \\
%% Vertical video height            &      400 & lines &  12.80000 & ms \\
%% Total frame height               &      421 & lines &  13.47200 & ms \\
%% Frame frequency (refresh rate)   &   74.228 & Hz    &  13.47200 & ms \\
%% \hline
%% \end{tabular}
%% \end{center}

%% These timings were generated using the VESA Co-ordinated Timing Generator
%% spreadsheet\footnote{Available at
%%   \url{http://files.bedroomlan.org/cft/video-board/CVTd6r1.xls}.} to maximise
%% compatibility.

%% A horizontal resolution of 640 was chosen because it allows for 80 columns of
%% 8-pixel wide characters. The vertical resolution of 400 was a more difficult
%% choice, as it provides a 16:10 aspect ratio, not a more classical 4:3 one or
%% the currently fashionable 16:9. However, a 640×400 monochrome bitmap resolution
%% fits in the 32~kByte SRAMs available to the VDU board, and simplifies the
%% design. As a bonus, 32~kByte addresses fit in 15 bits. The remaining bit can be
%% used to address a 32 kWord colour plane.

%% 640×400 at 74 Hz might seem ambitious. Unfortunately, this is the lowest viable
%% resolution that can be dislayed on modern devices. A lower resolution would not
%% make a big difference in complexity, because the majority of currently
%% available monitors expect a minimum horizontal refresh rate of 30~kHz. Having a
%% slower pixel clock would be a great boon in building the VDU board. At 25 MHz,
%% many components cannot be derated enough for comfortable operation, and can be
%% expected to run hot, have a reduced operating life, and produce sub-standard
%% waveforms. However, 25 MHz also produces a valid horizontal refresh rate and is
%% close to one of the two standard VGA pixel clocks (25.175~MHz).

%% A number of other, lower resolutions supported on VGAs are not suitable:

%% \begin{itemize}
%% \item The 320×200 MCGA resolution is actually a 640×400 resolution with
%%   horizontal and vertical pixel doubling, implemented this way because the
%%   horizontal scan frequency of single-frequency VGA monitors was 31.15~kHz.
%% \item The 640×200 CGA resolution is, again, a 640×400 resolution with vertical
%%   line doubling.
%% \item The 640×350 EGA resolution is a VGA 640×400 resolution with taller front
%%   and back porches, and the wrong pixel aspect ratio for modern monitors.
%% \end{itemize}

%% \subsection{The Frame State Machine}

%% The Frame State Machine is responsible for generating the control signals for
%% frame generation, and observing appropriate timings, as shown
%% in~\fcf{fig:video-frame-format}.

%% To keep the state machine simple and allow component reuse, it is customary for
%% many framebuffers to start each frame with the top-left pixel of the visible
%% video frame. This has a number of advantages, and a single disadvantage: the
%% top-most (blanked) field of each frame is truncated, but the first frame is
%% very rarely visible on the screen\footnote{Incidentally, the original IBM VGA
%%   used this exact counting scheme, and this was clearly visible on a standard
%%   IBM VGA monitor.}. This state machine acts in exactly this way.

%% The state machine uses one \HC{590} 8-bit counter, four \HC{688} 8-bit
%% comparators and two \HC{74} D flip-flops for each of the horizontal and
%% vertical parts.

%% The horizontal counter is an 8-bit device, incrementing on every eightth pixel
%% clock tick (counting 8-pixel character cells, not pixels). The four comparators
%% each generate an active low pulse at the end of the video data, front porch,
%% sync pulse, and back porch. The fourth comparator's output (end of back porch)
%% is connected to the counter's active-low reset input, forming a modulo 100
%% counter (modulo 800 in pixel clock ticks).

%% The vertical counter is a 9-bit device made up of an 8-bit counter and a D-flip
%% flop. The four \HC{688} comparators generate pulses at the end of the video
%% data, front porcc, sync pulse, and back porch. Since the comparators are 8-bit
%% units, their active-low enable is used as an implicit ninth bit comparison (for
%% \bin{0} values). Bit 6 of the count is zero for all four of the values, so this
%% one is used. The remaining eight bits are compared against in the normal
%% manner. As is the case with the horizontal counters, the output of the fourth
%% comparator (end of the back porch) is connected back to the counter's reset
%% input. The vertical counter thus counts modulo 421.

%% The eight signals are interpeted as the horizontal and vertical video on, video
%% off, sync on and sync off signals. They all feed the inputs of a \HC{574} 8-bit
%% D flip-flop to synchronise them. The flip-flop is clocked on the rising edge of
%% the \ps{PXCLK÷4} signal, since the counts (and thus the signals) change with a
%% minimum period of 8 pixel clocks.

%% Once synchronised, each active low ‘on’ signal is connected to half a D
%% flip-flop's asynchronous preset input, and each ‘off’ signal drives the same
%% flip-flop's asynchronous clear input. The complement output (\ns{Q}) of each
%% flip-flop provides the corresponding output:

%% \begin{itemize}
%% \item Horizontal Video On and Horizontal Video Off combine to form the
%%   \ns{HVIDEO} signal.
%% \item Horizontal Sync On and Horizontal Sync Off combine to form the
%%   \ns{HSYNC} signal.
%% \item Vertical Video On and Vertical Video Off combine to form the
%%   \ns{VVIDEO} signal.
%% \item Vertical Sync On and Vertical Sync Off combine to form the
%%   \ns{VSYNC} signal.
%% \end{itemize}

%% \subsection{Address Decoding}

%% The VDU card decodes both memory and I/O space.

%% \subsubsection{Memory Space}

%% Memory space is used to access the B and C planes, and the character generator
%% RAM, each of which is 32~kW, for a total of 96~kW. There are only 8 8-kW pages
%% in the logical address space, though, and it helps to be able to have both B
%% and C planes mapped together. This requires a windowing approach: 12 bits
%% (4~kW) of B plane addresses and 12 bits (4~kW) of C plane addresses are mapped
%% to locations \hex{180000}–\hex{181FFF} (physical page \hex{C0}) as follows:

%% \begin{nbitfield}{21}
%%     \bitfieldGroup{12}{cfthl!50}{B Plane offset (0–4095)}
%%     \bitfieldConst{0}
%%     \bitfieldGroup{8}{cfthl!25}{Page (\hex{C0}, \bin{11000000})}
%% \end{nbitfield}

%% \begin{nbitfield}{21}
%%     \bitfieldGroup{12}{cfthl!50}{C Plane offset (0–4095)}
%%     \bitfieldConst{1}
%%     \bitfieldGroup{8}{cfthl!25}{Page (\hex{C0}, \bin{11000000})}
%% \end{nbitfield}

%% Since the B and C planes are 15 bits (32~kW) each, three extra bits of
%% addrressing need to be provided. These are supplied by the three most
%% significant bits of the \cftcode{VWR}.

%% This scheme is perfect for 80×25 text modes which fit in 4~kW, but not ideal
%% for higher resolutions. Additional writes to the \cftcode{VWR} are needed to
%% address the entire plane, making drawing more complicated. The VDU is not meant
%% to be a high-performance graphics engine, however, and this addressing scheme
%% works reasonably well.

%% The character generator memory, which does not need to be accessed often, also
%% follows this scheme, but maps 8~kW to the entirety of physical page
%% \hex{C1}. Since there is 32~kW (15 bits) of character generator RAM and only 13
%% bits are mapped, the remaining two bits are taken from the most significant two
%% bits of the \cftcode{VWR}. The VWR is thus used as a windowing register for
%% both planes and character generator RAM.

\section{Display Modes}
\label{sec:vdu:modes}

The VDU card is essentially a text-only device with a large, fully programmable
character generator. Each character is displayed in a rectangular region called
a cell. A cell is always 8 pixels wide, and can be 1, 2, 4, 8, or 16 lines
high. Since the vertical resolution is constant at 480 lines, this allows for
480, 240, 120, 60, or 30 cell rows per frame.

Of the five available cell heights, only 16 and 8 can be used for text. The 1,
2 or 4-line high cells are not tall enough for letter shapes and can only be
used for graphics. This is done by programming 256 different bitmap patterns
into the character generator to represent the 256 different patterns formed by
groups of 8 pixels (the width of each cell).

This method may seem more obtuse than simply disabling the character generator
engine, but it is a viable means of generating graphics provided the video
memory is fast enough. The Texas Instruments TMS9918 video display controller
chip implemented bitmap graphics the same way, and it was more limited in terms
of memory speed.

In addition to resolution, display modes offer one of four different
dispositions: text, multicolour, semigraphics, or graphics in order of
increasing resolution.

\subsection{Text Modes}

Text modes are used to display human-readable character cells. Character cells
may be either 8×16 or 8×8 pixels, providing for 30 or 60 rows of text. 40 and
80-column modes are available. This allows four permutations: 40×30, 40×60,
80×30 or 80×60. Of these, 40×60 exhibits flattened character cells and is less
practical than the other three. The largest text resolution is 80×60, and the
most legible text mode is 80×30. This is also the default mode, and VDU
registers have been designed to make setting it as easy as possible. The
hardware cursor is generally enabled in text modes.

Both the B and C planes are used in text modes. Each character takes up the
eight bits of the B plane. A whole 16-bit word in the C plane is used to
describe the colours and display attributes of the cell. Each cell may have its
own background and foreground colour, and may blink or be inverted (or
both). 64 colours are available. Setting a character and its colour and
attributes requires between one and three writes, depending on whether or not
the address and attribute needs to be changed from the previous character
written.

\subsection{Multicolour Modes}

Multicolour modes are structurally identical to text modes, with \glspl{PEL}
equal to the size of a character cell. The hardware cursor is usually disabled
or hidden in multicolour modes. Useful multicolour modes are 40×30, 40×60,
80×30, 80×60 and 80×120. Of these, 40×30 and 80×60 have square PELs. Less
practical modes are still possible: 40×120, 40×240, 40×480, 80×240 and 80×480,
but these use PELs with extreme aspect ratios and should be avoided.

For multicolour modes, the B plane is filled with solid block characters. To
display information, the \field{Foreground} field (least significant six bits)
of each character cell in the C plane is set to the desired colour. As with all
modes, the full 64 colours of the palette are available. Setting the colour of
a PEL involves two I/O writes, one to choose the colour, one to issue a write
command to the VDU. These modes have no colour restrictions, hence the name.

Additional variations can be implemented to effectively increase the number of
colours, using (for instance) spaces, 25\%, and 50\% pixel pattern characters
to mix the foreground and background colours. This is a form of ordered
dithering with an effective 8,128 colours ($64 + 2×63×64$). Similar techniques
have been used in the past on computers with limited colour palettes, although
many of them depended on display devices with very low spatial resolution, such
as TV sets.

\subsection{Semigraphics Modes}

Semigraphics modes are slightly more complex, and with higher
resolutions. \glspl{PEL} are available at widths of 4 and 8 pixels, the latter
using \field{C40} to double the width of the cell. This provides horizontal
resolutions of 160 (based on 80 columns) and 80 (based on 40 columns). Given
the standard five vertical resolutions, ten semigraphics modes are
available. The most useful modes are 80×30, 80×60, 80×120, 160×60, 160×120 and
160×240. Square pixels are obtained at 80×60 and 160×120. Less useful
resolution variations include 80×240, 80×480, 160×30 and 160×480.

To obtain a semigraphics mode, the B plane is filled with characters forming
the bit pattern shown in~\fcf{fig:semigraphics-bit-pattern}. The same codepoint
and character set is used for all modes: a different vertical resolution will
use the top lines of the character pattern as required. The C plane can then be
used to control the colours: the \field{Foreground} field controls the left
half of the character cell; the \field{Background} field controls the right
half. The inverse and blink attributes and \field{CS1} character set selector
should not be used and left zeroed as shown below:

\begin{bitfield}
  \bitfieldItem{6}{cfthl!50}{Right PEL Colour}
  \bitfieldRepConst{2}{0}
  \bitfieldItem{6}{cfthl!50}{Left PEL Colour}
  \bitfieldRepConst{2}{0}
\end{bitfield}

Two to three writes are needed to set the colours of two \glspl{PEL}. As always, 64
colours are available. Each PEL can have its own colour.

The hardware cursor is usually disabled or hidden in these modes.

\begin{figure}
 \centering
 \inputfigure{figure-vdu-semigraphics-bit-pattern}
 \caption[Semigraphics bit patterns]{\label{fig:semigraphics-bit-pattern}
   Semigraphics bit patterns for all available semigraphics modes. The
   80-column modes are created with double-width pixels using 40-column
   (\bit{C40}) modes.}
\end{figure}

\subsection{Graphics Modes}

Like all other modes, ‘graphics’ modes are in reality modified text modes. They
provide ten 320 or 640 pixel wide modes, of which the most useful ones are
320×120, 320×240, 320×480, 640×240 and 640×480. Square pixels are available in
320×240 and 640×480 modes. Available variations with pixels of extreme aspect
ratios are 320×30, 320×60, 640×30, 640×60 and 640×120.

Both the B and C planes are used for graphics modes. Each write to the B plane
modifies eight bitmap pixels, and each write to the C plane modifies the
foreground and background colours for the entire group of eight pixels. As is
the case on text modes, the same pair of colours applies to the entire cell,
which is always 8×1 \glspl{PEL} (but may be larger in pixels) in size.

All 256 8-bit patterns are stored in the Character Generator RAM. Writing the
codepoint of one of these bit patterns to the B plane displays the bit pattern
on screen. These bit patterns can cohabit the Character Generator RAM by
storing them in a non-zero \field{CS2} character set. A good value is 3,
putting the patterns at locations 49,152–53,248 (\hex{C000}–\hex{CFFF}) in the
CG RAM.

The effect of the 8×1 colour constraint tends to be very visible on diagonals
with multiple colours, as shown in~\fcf{fig:colour-constraints}.

To simplify graphics generation, the VDU provides commands that apply bitmap
operators to pixels. The OR, AND and XOR operators may be used to turn on, off
or toggle some of the pixels at a time. This saves the host a video memory read
and the corresponding operation. Since the VDU can apply these operations in
bursts, a large amount of high-resolution graphics work can be
offloaded.\footnote{This technique was also followed by the original VGA, which
  used {\em four\/} 1-bit-per-pixel planes for high resolution graphics, so
  onboard graphics operators provided considerable acceleration.} This feature
is described in~\cf{sec:vdu:using-host-iface}.

\begin{figure}
  \centering
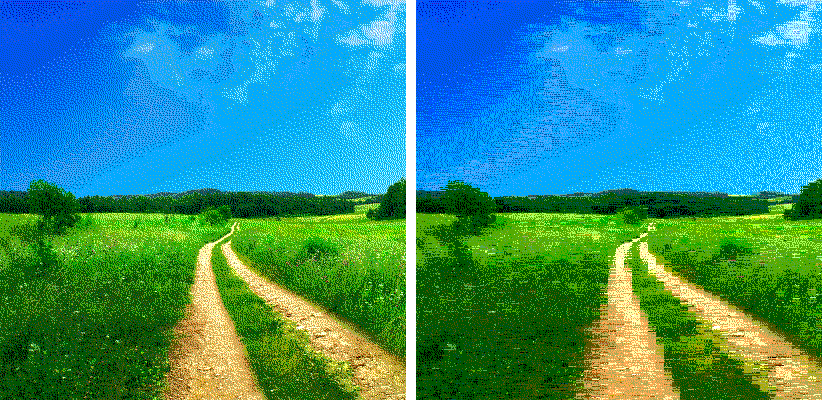
[picture p2: documentation/latex/figs/colour-restrictions.png]
  %
  \caption[Effect of colour constraints]{\label{fig:colour-constraints}The
    effect of the 8×1 colour constraint on graphics modes (640×480, in this
    case). Left, a 64-colour dithered test image, impossible to produce on the
    VDU. Right, the same image with 8×1 colour restrictions, as displayed by
    the VDU.}
\end{figure}

%\subsubsection{Graphics Modes}

%% %\begin{table}
%% \newcommand\vdumodePract[4]{%
%% %                   1       2                   3
%% %\vdumodeImpract{1}{16}{640×25 Graphics}{2 colours per 8×1 pixels.}
%% %\vdumodePract{4}{2}{160×200 Semigraphics}{C-plane. No restrictions.}
%% \bfseries{#3} & \bfseries{{#1}×{#2}} & \bfseries{#4}  \\ %
%% }
%% \newcommand\vdumodeImpract[4]{%
%% #3 & {{#1}×{#2}}%\tikz{\draw[fill=black,scale=0.01](0,0) rectangle (#1, #2); }
%% & #4  \\ %
%% }
%% %\caption{\label{table-vdu-modes}VDU Display modes.}
%% \vspace{1em}
%% \centering
%% \zebrarow{10}
%% \begin{longtable}{lll}
%%   %
%%   % First header
%%   %
%%   \hiderowcolors
%%   Mode & Cell & Description \\
%%   \hline
%%   \noalign{\global\rownum 0\relax}\showrowcolors
%%   \endfirsthead
%%   %
%%   % Subsequent headers
%%   %
%%   \hiderowcolors
%%   \noalign{\smallskip\smallskip}
%%   \multicolumn{3}{l}{\em Continued from previous page.}\\
%%   Mode & Cell & Description \\
%%   \hline
%%   \noalign{\global\rownum 1\relax}\showrowcolors
%%   \endhead
%%   %
%%   % Footer
%%   %
%%   \hiderowcolors
%%   \hline
%%   \noalign{\smallskip\smallskip}
%%   \multicolumn{3}{l}{\em Continued on next page.}\\
%%   \endfoot
%%   %
%%   % Last footer
%%   %
%%   \hiderowcolors
%%   \hline
%%   \endlastfoot
%%   %
%%   % Content
%%   %
%%   \showrowcolors
%%   \hline
%%   \input{../generated/mode-table}
%% \end{longtable}
%% %\end{table}

\begin{figure}
 \centering
 \inputfigure{figure-vdu-video-modes}
 \caption[Video Modes]{\label{fig:video-modes} Video mode chart showing the 34
   available modes (5×5, plus 5 80-column multicolour modes, plus four text
   modes). Unshaded modes are impractical due to the aspect ratio of the
   pixels. Multicolour and semi-graphics modes have no colour
   restrictions. Graphics modes allow two colours per 8×1 pixel block.}
\end{figure}

\section{Useful Display Mode Types}

The set of available display modes is a permutation of a number of options:

\begin{itemize}
  \item Whether the display intent is text or graphics.
  \item Whether 40 or 80 column mode is used.
  \item Whether 16, 8, 4, 2 or 1-line characters are used.
  \item Which block style is used: full-block, two-column block, or eight-column block.
\end{itemize}

Although this technically implies dozens of modes are possible, and all are
allowed by the hardware, many of these modes are:

\begin{itemize}
\item Of no use. For instance, text modes with 2-line characters are no good for text display.
\item Impractical. The 40×480 Multicolour and 640×30 Graphics modes are
  perfectly valid but their pixel shapes are too wide and too tall (respectively) for use.
\item Overshadowed by better modes. A 80×60 Semigraphics mode which only
  allows 2 colours per 4 horizontal pixels is valid, but the 80×60
  Multicolour mode offers the same resolution, no colour restrictions, and
  faster pixel access.
\end{itemize}

\begin{figure*}
  \centering
  
  \ifxetex
    \hfill
  \else
    \vspace{1em}\\
  \fi
  %
  \caption[Two examples of impractical
    modes]{\label{fig:vdu:impractical-modes}Two examples of impractical
    modes. \ifxetex Left\else Top\fi, 40×480. \ifxetex Left\else Bottom\fi, 640×30.
    The pixel aspect ratios are too extreme
    for regular use, although the modes are accepted by the hardware. It should
    be noted that some computers from the past featured similarly extreme
    modes.}
\end{figure*}

\subsection{Mode Demonstrations}

The following pages demonstrate in practical terms what is capable in some of
the graphics modes. The original, unprocessed image is shown
in~\fcf{fig:vdu:original}, followed by renderings in progressively higher
resolution modes. To improve the quality, the image colour-space was quantised
from 8 bits per channel (16,777,216 colours) to 2 bits per channel (64
colours), with the error diffused using the Floyd-Steinberg dithering
algorithm.

\ifxetex
  \begin{figure}
    \centering
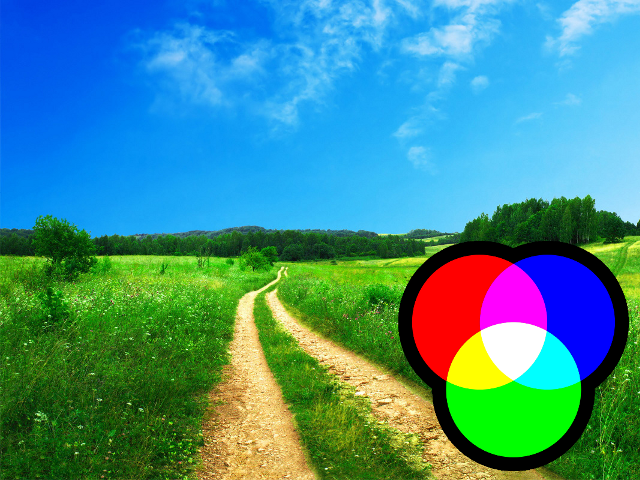
[picture p3: documentation/latex/figs/vdu-test-image3-original.png]
    %
    \caption[Original 640×480 demonstration image]
            {\label{fig:vdu:mode-original}The original true-colour (24-bit colour)
      demonstration image, scaled down to 640×480.
    }
  \end{figure}
  
  \begin{figure}[p]
    \centering
    %
    \caption[40×30 Multicolour mode]
            {\label{fig:vdu:mode-40x30mc}The 40×30 Multicolour mode.
              Each block can have its own independent colour.
              This is the same as the 40×30 text mode with whole-cell block graphics.
    }
  \end{figure}
  
  \begin{figure}[p]
    \centering
    %
    \caption[80×30 Multicolour mode]{\label{fig:vdu:mode-80x30mc}The 80×30 Multicolour mode.
      Each block can have its own independent colour.
      This is the same as the 80×30 text mode with whole-cell block graphics.
    }
  \end{figure}

  \begin{figure}[p]
    \centering
    %
    \caption[80×60 Multicolour mode]{\label{fig:vdu:mode-80x60mc}The 80×60 Multicolour mode.
      Each block can have its own independent colour.
      This is the same as the text mode with whole-cell block graphics.
    }
  \end{figure}
  
  \begin{figure}[p]
    \centering
    %
    \caption[160×60 Semigraphics mode]{\label{fig:vdu:mode-160x60}The 160x60 Semigraphics mode.
      Each block can have its own independent colour.
    }
  \end{figure}
  
  \begin{figure}[p]
    \centering
    %
    \caption[160×120 Semigraphics mode]{\label{fig:vdu:mode-160x120mc}The 160x120 Semigraphics mode.
      Each block can have its own independent colour.
    }
  \end{figure}
  
  \begin{figure}[p]
    \centering
    %
    \caption[160×240 Semigraphics mode]{\label{fig:vdu:mode-160x240mc}The 160x240
      Semigraphics mode.  Each block can have its own independent colour.}
  \end{figure}
  
  \begin{figure}[p]
    \centering
    %
    \caption[320×240 Graphics mode]{\label{fig:vdu:mode-320x240hgr}The 320x240
      Graphics mode.  Two colours are allowed per 8×2 pixel block.  The colour
      restrictions cause obvious artifacts where numerous colours come close
      together.  }
  \end{figure}

  \begin{figure}[p]
    \centering
    %
    \caption[320×480 Graphics mode]{\label{fig:vdu:mode-320x480hgr}The 320x480 Graphics mode.
      Each block of 8×1 pixels can have its own independent colour.
      The colour restrictions cause obvious artifacts where numerous colours come close together.
      Higher vertical resolution alleviates some of this problem, but not in all cases.
    }
  \end{figure}

  \begin{figure}
    \centering
    %
    \caption[640×480 Graphics mode]{\label{fig:vdu:mode-640x480hgr}The 640x480 Graphics mode.
      Each block of 8×1 pixels can have its own independent colour.
      The colour restrictions cause obvious artifacts where numerous colours come close together.
      This is the highest spatial resolution available.
    }
  \end{figure}

\else

  \HCode{}
  \HCode{<script type="text/javascript">}
  \HCode{$(document).ready(function(){makeModeDemoWidget();});} %$
  \HCode{</script>}

\fi

\section{Programming Model}

The following section discusses the software-side operation of the VDU board,
all of which is done via I/O space registers. There are thirteen registers in five groups.

\begin{enumerate}
  \item Registers configuring the entire display. In split screen mode, these
    registers configure the top portion of the split. The first register
    (\port{MCR0}) is also responsible for enabling video output and configuring
    interrupts, and serves as a detection and status register.
  \item Registers configuring the bottom portion of the split, in split screen
    mode. The first register (\port{MCR1}) is also responsible for enabling and
    configuring split-screen mode.
  \item Hardware cursor control registers.
  \item The PS/2 Keyboard register.
  \item Host interface registers.
\end{enumerate}

\begin{figure}
 \centering
 \inputfigure{figure-vdu-register-file}
 \caption[Register File]{\label{fig:vdu-register-file} Register File.}
\end{figure}

\subsection{Registers Controlling the Display}

\begin{ioport}{VDU}{1F0}{--wvehf}{MCR0}{Mode Control Register 0}

  This register controls whether or not the VDU card is enabled, configures
  interrupts, selects an appropriate character set and configures the display
  mode.

  \begin{bitfield}
    \bitfieldItem{3}{cfthl!50}{CRH}
    \bitfieldItem{1}{cfthl!25}{C40}
    \bitfieldItem{2}{cfthl!50}{CS2}
    \bitfieldItem{1}{cfthl!25}{VSI}
    \bitfieldItem{1}{cfthl!50}{SCI}
    \bitfieldItem{1}{cfthl!25}{VRI}
    \bitfieldItem{1}{cfthl!50}{KBI}
    \bitfieldRepConst{5}{0}
    \bitfieldItem{1}{cfthl!25}{EN}
  \end{bitfield}

  \begin{description}
    \li{\field{CRH}} is a three bit field that controls the height of the rows
    of character cells in scanlines. This in turn sets the vertical resolution
    in rows. Valid values are:
    
    \begin{description}
      \li{\bin{000}}: 16 lines per row, 30-row modes.
      \li{\bin{001}}: 8 lines per row, 60-row modes.
      \li{\bin{010}}: 4 lines per row, 120-pixel modes.
      \li{\bin{011}}: 2 lines per row, 240-pixel modes.
      \li{\bin{100}}: 1 line per row, 480-pixel modes.
      \li{\bin{101}}: Reserved, do not use.
      \li{\bin{11X}}: Reserved, do not use.
    \end{description}
    
    \li{\field{C40}} is a single bit flag. Set to \bin{1}, it enables
    40-column (320 pixel) wide modes. Set to \bin{0}, it specifies 80-column
    (640 pixel) modes.
    
    \li{\field{CS2}} is a two-bit quanity. It corresponds to bits 14 and 15
    of the character generator address and is used to set which character set
    of four is used in the current mode:
    
    \begin{description}
      \li{\bin{00}}: \hex{0000}–\hex{3FFF}.
      \li{\bin{01}}: \hex{4000}–\hex{7FFF}.
      \li{\bin{10}}: \hex{8000}–\hex{BFFF}.
      \li{\bin{11}}: \hex{C000}–\hex{FFFF}.
    \end{description}
    
    \li{\field{VSI}} controls the Vertical Sync Interrupt. If this bit is set,
    an interrupt will be signalled when vertical blanking begins. The processor
    can then modify the VDU image with minimum flickering, perhaps to implement
    a double-buffering technique. This flag defaults to \bin{0} when the system
    is reset.
    
    \li{\field{SCI}} controls the Split Count Interrupt. If this bit is set, an
    interrupt will be signalled whenever the scanline specified in \field{SCL}
    (see below) is being output. The interrupt is generated even when split
    screen mode is disabled. This flag defaults to \bin{0} when the system is reset.

    \li{\field{VRI}} controls the VDU Ready Interrupt. If this bit is set, an
    interrupt will be signalled at the completion of every host command.  This
    flag defaults to \bin{0} when the system is reset.

    \li{\field{KBI}} controls the Keyboard Interrupt. If this bit is set, an
    interrupt will be signalled whenever the keyboard has completed
    transmitting a byte of information. This flag defaults to \bin{0} when the
    system is reset.

    \li{\field{EN}} controls whether or not the VDU card is enabled. This
    flag defaults to \bin{0} when the system is reset. It must be set
    explicitly to enable display output.

  \end{description}

\end{ioport}

\begin{ioport}{VDU}{1F0}{-r-vehf}{SR}{Status Register}

  This read-only register shares its location with the \port{MCR0} register and
  mirrors some of the information stored it in. It is used for autodetection of
  the VDU card, and to detect the source of an interrupt.

  \begin{bitfield}
    \bitfieldItem{3}{cfthl!50}{CRH}
    \bitfieldItem{1}{cfthl!25}{C40}
    \bitfieldItem{2}{cfthl!50}{CS2}
    \bitfieldItem{1}{cfthl!25}{VSIS}
    \bitfieldItem{1}{cfthl!50}{SCIS}
    \bitfieldItem{1}{cfthl!25}{VRIS}
    \bitfieldItem{1}{cfthl!50}{KBIS}
    \bitfieldItem{5}{cfthl!50}{Version}
    \bitfieldItem{1}{cfthl!25}{EN}
  \end{bitfield}

  \begin{description}
    \li{\field{CRH}} contains the same value as the \field{CRH} field in the
    \port{MCR0} register.

    \li{\field{C40}} contains the same value as the \field{C40} field in the
    \port{MCR0} register.

    \li{\field{CS2}} contains the same value as the \field{CS2} field in the
    \port{MCR0} register.

    \li{\field{VSIS}} is set if a Vertical Sync Interrupt has been signalled
    since the last read of the \port{SR} register. This bit is cleared after
    the register is read.

    \li{\field{SCIS}} is set if a Split Count Interrupt has been signalled
    since the last read of the \port{SR} register. This bit is cleared after
    the register is read.

    \li{\field{VRIS}} is set if a VDU Ready Interrupt has been signalled since
    the last read of the \port{SR} register. This bit is cleared after the
    register is read.

    \li{\field{KBIS}} is set if a Keyboard Interrupt has been signalled since
    the last read of the \port{SR} register. Unlike other interrupt status
    bits, reading the \port{SR} does {\em not\/} clear this bit. This is done
    by reading the \port{KBD} register instead.

    \li{\field{Version}} is the version of the VDU card. For current revisions
    of the VDU, this field should yield the value \bin{00101}. This may be used
    to autodetect the presence of the card.

    \li{\field{EN}} matches the bit of the same name in the
    \port{MCR0} register. It is set if video generation is enabled. If
    clear, the VDU clocks are stopped and the output remains
    blanked. Most monitors will enter power saving mode within a few
    seconds of this happening.
  \end{description}

\end{ioport}

\begin{ioport}{VDU}{1F1}{--wvehf}{MCR1}{Mode Control Register 1}

  This register controls horizontal split mode, which allows the screen to be
  split in two. One display mode is shown in the top portion, another in the
  bottom portion. Each portion can act independently of the other so that
  scrolling graphics may be displayed in one portion, and text in the other.

  \begin{bitfield}
    \bitfieldItem{3}{cfthl!50}{CRH}
    \bitfieldItem{1}{cfthl!25}{C40}
    \bitfieldItem{2}{cfthl!50}{CS2}
    \bitfieldConst{0}
    \bitfieldGroup{1}{cfthl!25}{SEN}
    \bitfieldItem{8}{cfthl!50}{SCL}
  \end{bitfield}

  \begin{description}
    \li{\field{CRH}} is a three bit field that controls the bottom mode's
    cell row height setting controls the height of the rows of character cells
    in scanlines. It accepts the same values as the \field{CRH} field in the
    \port{MCR0} register.
    
    \li{\field{C40}} is a single bit flag. Set to \bin{1}, it enables
    40-column (320 pixel) wide modes in the bottom portion of the frame. Set
    to \bin{0}, it specifies 80-column (640 pixel) modes.

    \li{\field{CS2}} is a two-bit quanity. It corresponds to bits 14 and 15
    of the character generator address and is used to set the character set
    used in the bottom portion of the frame. It works exactly like the
    \field{CS2} field in the \port{MCR0} register.

    \li{\field{SEN}} when set to \bin{1}, enables split-screen mode.

    \li{\field{SCL}} this 8-bit value controls the scanline of the partition
    between top and bottom screen portions. This field is 8-bits wide while
    scanlines are 9 bits wide. Because of this, the split can be positioned
    with an accuracy of two scanlines. The scanline comparison includes the
    blanked lines, so the number must be offset. To place the split on line
    $n$, set \field{SCL} to $\lfloor\frac{n}{2}\rfloor+4$. For example, a value
    of 124 would put the split on the 240th scanline. If either of the modes is
    a text mode, it would help for the split to happen at a multiple of the
    tallest cell height so the split results in whole rows. Usually, this
    multiplier will be 16 or 8.
  \end{description}
\end{ioport}

\todo {The SCL formula above may be wrong. Verify}

\begin{ioport}{VDU}{1F2}{--wvehf}{SCR0}{Smooth Scroll Register 0}

  This register controls smooth scrolling in the horizontal and vertical
  direction. It applies to the top portion of the screen (or the entire screen,
  if split screen is disabled). It is eight bits wide, with the remaining bits
  set to \bin{0} to facilitate future expansion:

  \begin{bitfield}
    \bitfieldGroup{3}{cfthl!50}{HSCR}
    \bitfieldConst{0}
    \bitfieldGroup{4}{cfthl!50}{VSCR}
    \bitfieldRepConst{8}{0}
  \end{bitfield}

  \begin{description} \li{\field{HSCR}} shifts the displayed image left by a
    number of pixels. A value of \hex{0} does not shift the image; a value
    of \hex{7} shifts it to the left by seven pixels. This represents the range
    of modulo 8 and allows smooth scrolling to be implemented in conjunction
    with the \port{SAR0} register (which can shift in multiples of eight
    pixels).

    \li{\field{VSCR}} shifts the displayed image up by a number of
    pixels. A value of \hex{0} does not shift the image; a value of
    \hex{15} shifts it up by fifteen pixels. This represents the range
    of modulo 16 and allows smooth scrolling to be implemented in
    conjunction with the \port{SAR0} register. Please note that,
    depending on the current mode, the row field of \port{SAR0} can
    shift by 16, 8, 4, 2 or single pixels (30, 60, 120, 240 and 480
    line modes respectively), so the steps needed for smooth vertical
    scrolling depend on the mode.
  \end{description}

\end{ioport}

\begin{ioport}{VDU}{1F3}{--wvehf}{SCR1}{Smooth Scroll Register 1}

  This register controls smooth scrolling in the horizontal and vertical
  direction. It applies to the bottom portion of the screen, when split screen
  is enabled. Like \port{SCR0}, this register is eight bits wide, with the
  remaining bits set to \bin{0} to facilitate future expansion:

  \begin{bitfield}
    \bitfieldGroup{3}{cfthl!50}{HSCR}
    \bitfieldConst{0}
    \bitfieldGroup{4}{cfthl!50}{VSCR}
    \bitfieldRepConst{8}{0}
  \end{bitfield}

  \begin{description} \li{\field{HSCR}} shifts the displayed image left by a
    number of pixels. A value of \hex{0} does not shift the image; a value
    of \hex{7} shifts it to the left by seven pixels. This represents the range
    of modulo 8 and allows smooth scrolling to be implemented in conjunction
    with the \port{SAR1} register (which can shift in multiples of eight
    pixels).

    \li{\field{VSCR}} shifts the displayed image up by a number of
    pixels. A value of \hex{0} does not shift the image; a value of
    \hex{15} shifts it up by fifteen pixels. This represents the range
    of modulo 16 and allows smooth scrolling to be implemented in
    conjunction with the \port{SAR1} register. Please note that,
    depending on the current mode, the row field of \port{SAR1} can
    shift by 16, 8, 4, 2 or single pixels (30, 60, 120, 240 and 480
    line modes respectively), so the steps needed for smooth vertical
    scrolling depend on the mode.
  \end{description}

\end{ioport}

\begin{ioport}{VDU}{1F4}{--wvehf}{SAR0}{Start Address Register 0}

  This register sets the address in the video RAM of the top-left corner of the
  screen. It applies to the top portion of a split screen, or the entire screen
  if the split is not enabled.

  \begin{bitfield}
    \bitfieldGroup{7}{cfthl!50}{Column}
    \bitfieldGroup{9}{cfthl!25}{Row}
  \end{bitfield}

  \begin{description}
  \li{\field{Column}} The column address of the top left cell on the screen.
  \li{\field{Row}} The row address of the top left cell on the screen.
  \end{description}

\end{ioport}

\begin{ioport}{VDU}{1F5}{--wvehf}{SAR1}{Start Address Register 1}

  This register sets the address in the video RAM of the top-left corner of the
  screen. It applies to the bottom portion of a split screen.

  \begin{bitfield}
    \bitfieldGroup{7}{cfthl!50}{Column}
    \bitfieldGroup{9}{cfthl!25}{Row}
  \end{bitfield}

  \begin{description}
  \li{\field{Column}} The column address of the top left cell of the bottom half of a split-screen setup.
  \li{\field{Row}} The row address of the top left cell of the bottom half of a split-screen setup.
  \end{description}

\end{ioport}

\begin{ioport}{VDU}{1F6}{--wvehf}{MAR0}{Modulo Address Register 0}

  This register sets the modulo address. It applies to the top portion of a
  split screen, or the entire screen if the split is not enabled. The effects
  of modulo address registers are described in~\cf{vdu:sec:modulo-address}.

  \begin{bitfield}
    \bitfieldGroup{7}{cfthl!50}{Column}
    \bitfieldGroup{9}{cfthl!25}{Row}
  \end{bitfield}

  \begin{description}
  \li{\field{Column}} The column modulo address of the screen.
  \li{\field{Row}} The row modulo address of the screen.
  \end{description}

\end{ioport}

\begin{ioport}{VDU}{1F7}{--wvehf}{MAR1}{Modulo Address Register 1}

  This register sets the modulo address. It applies to the bottom portion of a
  split screen. The effects of modulo address registers are described
  in~\cf{vdu:sec:modulo-address}.

  \begin{bitfield}
    \bitfieldGroup{7}{cfthl!50}{Column}
    \bitfieldGroup{9}{cfthl!25}{Row}
  \end{bitfield}

  \begin{description}
  \li{\field{Column}} The column modulo address of the bottom half of a split-screen setup.
  \li{\field{Row}} The row modulo address of the bottom half of a split-screen setup.
  \end{description}

\end{ioport}

\begin{ioport}{VDU}{1F8}{--wvehf}{CCR}{Cursor Control Register}

  This register controls the appearance and behaviour of the hardware
  cursor. The cursor's behaviour is described in~\cf{sec:vdu:cursor}.

  \begin{bitfield}
    \bitfieldGroup{6}{cfthl!50}{Foreground}
    \bitfieldGroup{2}{cfthl!25}{CBC}
    \bitfieldGroup{6}{cfthl!50}{Background}
    \bitfieldRepConst{2}{0}
  \end{bitfield}

  \begin{description}
    \li{\field{Foreground}} is the foreground \ds{Colour} of the character
    cell the cursor is on, when it is visible.
    \li{\field{CBC}} is the cursor blink control field. It controls the
    visibility and blink rate of the cursor:
    
    \begin{description}
      \li{\bin{00}} the cursor is always invisible (off).
      \li{\bin{01}} the cursor is always visible (on) and does not blink.
      \li{\bin{10}} the cursor is visible and blinking at double the rate of
      blinking text.
      \li{\bin{11}} the cursor is visible and blinking at the same rate and
      in phase with blinking text.
    \end{description}
    
    \li{\field{Background}} is the background \ds{Colour} of the character
    cell the cursor is on, when it is visible.
  \end{description}

\end{ioport}

\begin{ioport}{VDU}{1F9}{--wvehf}{CAR}{Cursor Address Register}

  This register sets the location of the cursor. The cursor will be visible
  (according to the settings of the \port{CCR} register when the specified
  address is displayed. This implies that the cursor may be off-screen and thus
  invisible. This provides a second way of hiding the cursor (in addition to
  disabling it via the \field{CBC} field in the \port{CCR} register). The
  cursor's full behaviour is described in~\cf{sec:vdu:cursor}.

  \begin{bitfield}
    \bitfieldGroup{7}{cfthl!50}{Cursor Column} The column address of the cursor's location.
    \bitfieldGroup{9}{cfthl!25}{Cursor Row} The row address of the cursor's location.
  \end{bitfield}

\end{ioport}

\subsection{Registers Controlling the Keyboard}

The VDU board contains an optional PS/2 keyboard interface operated by the
\field{KBI} bit in the \port{MCR0} register, the \field{KBIS} in the \port{SR}
register, and the \port{KBD} register, described below. The keyboard interface
is described in detail in~\ccf{chap:kbd}.

\begin{ioport}{VDU}{1FB}{-rwvehf}{KBD}{Keyboard Register}

  This register operates the PS/2 keyboard interface. A full description of
  this interface can be found in~\ccf{chap:kbd}.

  \begin{bitfield}
    \bitfieldGroup{8}{cfthl!25}{Keyboard Data}
    \bitfieldGroup{1}{cfthl!50}{KDP}
    \bitfieldRepConst{4}{0}
    \bitfieldGroup{1}{cfthl!25}{KC}
    \bitfieldGroup{1}{cfthl!50}{KD}
    \bitfieldGroup{1}{cfthl!25}{KDR}
  \end{bitfield}

  \begin{description}
    \li{\field{Keyboard Data}} is a read-only 9-bit value as transmitted by the
    keyboard. The ninth bit (\field{KDP}) is an odd parity bit. It is clear if
    there is an odd number of set bits in the remaining 8 bits, otherwise it is
    set.  \li{\field{KC}} is a direct connection to the keyboard clock
    pin. When reading, the keyboard clock pin will be sampled directly. Writing
    to this bit controls the clock driver. Clearing the bit drives the clock
    line low. Setting it releases the clock line, allowing the keyboard to
    operate. Setting this bit thus allows the keyboard to be inhibited
    programmatically. Setting, then clearing this bit sends a clock pulse to
    the keyboard. Writing to the \port{KBD} register does not change the value
    of this field.

    \li{\field{KD}} is a direct connection to the keyboard data pin. \field{KD}
    and \field{KC} may be used to manually read from the keyboard, one bit at a
    time. When writing to \field{KD}, setting the bit drives the data line
    low. Clearing it releases the data line, allowing it to be pulled up to a
    high state. \field{KD} may be used to send data to the keyboard. The data
    bits must be complemented by the host prior to sending, and the host is
    also responsible for transmitting correct start, parity and stop bits and
    operating the clock line at sufficiently slow rates.

    \li{\field{KDR}} is set if a full byte of keyboard data has been received
    and is ready for processing. After reading from \port{KBD}, if \field{KDR}
    is set, it will be cleared and the keyboard receiver reset. The keyboard
    inhibit condition will be removed and the keyboard will be free to transmit
    another byte when it needs to. The interrupt status bit \field{KBIS} is
    also cleared at this time.
  \end{description}
\end{ioport}

\subsection{Manipulating the Display Memory}

Manipulating the video memory is also performed indirectly, by communicating
with the VDU using an extended instruction (or command register), and three
registers.

\begin{ioport}{VDU}{1FA}{-rwvehf}{HAR}{Host Address Register}

  This read/write register contains the address of the next location to be read
  from or written to by the CFT host. 

  Reading from or writing to this register will generate wait states until or
  unless the VDU's host interface is idle (i.e. any previous command has
  executed fully and \port{CRR}, as well as \field{GO} in \field{CMD} are both
  zero). Reading from the \port{HAR} register is thus a good way to block
  execution while the VDU is running a command.

  \begin{bitfield}
    \bitfieldGroup{7}{cfthl!50}{Column}
    \bitfieldGroup{9}{cfthl!25}{Row}
  \end{bitfield}

\end{ioport}

\begin{ioport}{VDU}{1FD}{-rwvehf}{CRR}{Command Repetition Register}

  The CRR is a 9-bit read-write register. Setting it to a non-zero value prior
  to issuing a host command causes the host command to repeat $\mbox{CRR}+1$
  times. That is, a value of \hex{000} denotes one repetition, and a value of
  \hex{1FF} denotes 512 repetitions. This makes it possible to operate on
  entire rows or columns of the video memory, depending on the command.

  The register is decremented by the VDU engine while commands are being
  executed, and may be used to monitor repeated command progress. When the VDU
  host interface has completed its command, CRR will contain \hex{000}, and the
  \field{GO} field in the \port{CMD} register will be set. Further commands
  will only execute once because of the \hex{000} value.

  \begin{bitfield}
    \bitfieldGroup{9}{cfthl!50}{Repetitions}
    \bitfieldRepConst{7}{0}
  \end{bitfield}

  Only the least significant nine bits are in use at this location. All other
  bits are ignored on writes, and reads return \bin{0000000} for the most
  significant seven bits.

  Reading from this register is one way of polling for command completion, but
  only for the completion of a repeated command. To poll the completion of any
  command, check the \field{GO} field in the \port{CMD} register.

  Writing to this register will generate wait states until or unless the VDU's
  host interface is idle.

\end{ioport}

\begin{ioport}{VDU}{1FE}{-rwvehf}{CPORT}{C Plane Register}

  This read/write register contains data retrieved from the C plane, or to be written to
  the C plane. It is 16 bits wide and follows the layout of the C plane itself:

  \begin{bitfield}
    \bitfieldGroup{6}{cfthl!50}{Foreground}
    \bitfieldGroup{2}{cfthl!25}{CS1}
    \bitfieldGroup{6}{cfthl!50}{Background}
    \bitfieldGroup{1}{cfthl!25}{INV}
    \bitfieldGroup{1}{cfthl!25}{BLN}
  \end{bitfield}

  \begin{description}
    \li{\field{Foreground}} is the foreground \ds{Colour} of the
    corresponding character in the B Plane.
    \li{\field{CS1}} is a two-bit quanity. It corresponds to bits 12 and 13
    of the character generator address and is used to set which character set
    is used by the corresponding character in the B plane. Field \field{CS2} in
    either \port{MCR0} or \port{MCR1} provides bits 14 and 15. The character
    itself provides the remaining 12 bits (256 characters, 16 lines each).
    \li{\field{Background}} is the background \ds{Colour} of the character
    cell corresponding to this value.
    \li{\field{INV}} is the ‘inverse video’ attribute. When this bit is
    \bin{1}, the foreground and background colours specified here are
    swapped. Inverse video is used to highlight text.
    \li{\field{BLN}} is the ‘blink’ attribute. When this bit is \bin{1}, the
    foreground colour is periodically set to be the foreground colour. This
    makes foreground pixels disappear and reappear periodically, causing them
    to blink. The blink frequency is 2.3Hz.
  \end{description}

  Reading from or writing to this register will generate wait states until or unless the VDU's
  host interface is idle (i.e. any previous command has executed fully and
  \port{CRR} is zero). 

\end{ioport}

\begin{ioport}{VDU}{1FF}{crwvehf}{CMD/BPORT/CGPORT}{Command, B Plane port, CG RAM port Register}

  This read/write register combines read/write access to the B Plane
  and Character Generator RAM, and supplies the VDU card with host
  interface commands and their options.

  \begin{bitfield}
    \bitfieldGroup{8}{cfthl!50}{B/CG Data}
    \bitfieldGroup{1}{cfthl!25}{XINC}
    \bitfieldItem{1}{cfthl!50}{YINC}
    \bitfieldGroup{4}{cfthl!25}{Command}
    \bitfieldRepConst{1}{0}
    \bitfieldItem{1}{cfthl!50}{GO}
  \end{bitfield}

  \begin{description}
    \li{\field{B/CG Data}} holds data read from or about to be written to the
    B plane, or data about to be written to the Character Generator RAM.
    
    \li{\field{XINC}} if set to \bin{1}, the column address of the \port{HAR}
    will be incremented by one after the command runs.
    
    \li{\field{YINC}} if set to \bin{1}, the row address of the \port{HAR}
    will be incremented by one after the command runs (i.e. the \port{HAR} will
    be incremented by 128).
    
    \li{\field{Command}} identifies the operation to be performed. The
    following commands are available:
    \begin{description}
      \li{\bin{0000}} Write to B and C planes.
      \li{\bin{0001}} Write to B plane.
      \li{\bin{0010}} OR value with B plane value, write to C plane.
      \li{\bin{0011}} OR value with B plane value.
      \li{\bin{0100}} Mask (AND) value with B plane value, write to C plane.
      \li{\bin{0101}} Mask (AND) value with B plane value.
      \li{\bin{0110}} Toggle (XOR) value with B plane value, write to C plane.
      \li{\bin{0111}} Toggle (XOR) value with B plane value.
      %
      \li{\bin{1000}} Write to C plane only.
      \li{\bin{1011}} Write to Character Generator RAM.
      \li{\bin{1101}} Read from B and C planes.
      %
    \end{description}

    All other values are reserved for future expansion and should not be used.

    \li{\field{GO}} Must {\em always\/} be clear (\bin{0}) to start a
    command. Once the command has been executed, this bit is set to \bin{1}.
    This also happens if the command is one of the reserved opcodes.
  \end{description}

  These commands are explained in detail
  in~\cf{sec:vdu:using-host-iface}. Please note that incrementation of the
  \port{HAR} is not subject to the \port{MAR0}/port{MAR1} registers: though
  conventionally interpreted as a column/row vector register, this is really a
  16-bit scalar register incremented as a whole. X increments simply add the
  value \hex{0001} to the register, while Y increments add the value
  \hex{0080}.

  Writing to this register will generate wait states until or unless the VDU's
  host interface is idle (i.e. any previous command has executed fully
  and \port{CRR} is zero). Reading from the register does not introduce wait
  states, making this a good way to poll for command completion. Generating
  wait states on write (when busy) allows the processor to send the VDU a
  stream of commands without waiting for each command to complete.

\end{ioport}

\subsection{Using the Host Interface}
\label{sec:vdu:using-host-iface}

The indirect nature of the VDU-to-host interface makes it appear daunting at
first, but this complexity is a boon to the CFT programmer, since the VDU
offloads a significant amount of work.

The algorithm for writing data to the VDU is quite straightforward: first, and
optionally (the location may already be correct) set the location to write to
by writing its address to the \port{HAR}. If modifying colour information for
that location, set the \port{CPORT} register. If modifying multiple locations
at once, set the \port{CRR} register. Then, write a command and character (B
plane) data to \port{CMD}. Repeat as required. If the VDU isn't ready for a new
command yet, writing to the \port{HAR}, \port{CPORT} or \port{CRR} will block
execution with wait states.

The algorithm for reading data is simpler: write a command to \port{CMD}, then
read character (B plane) or character generator data from it. Optionally, also
read \port{CPORT} to get C plane data.

Below is a detailed list of all supported commands with suggested mnemonics and
values (in binary), as listed above.

\begin{description}
  \li{\textsf{WB} (\bin{0001)}: Write to B plane.} A single write to the B plane is
  performed, at the location in \port{HAR}, using data supplied in the
  \port{CMD} register. Colours and attributes are not modified. One memory
  write is performed.

  \li{\textsf{WBC} (\bin{0000}): Write to B and C planes.} Same as above, but in addition the
  value of the \port{CPORT} register is stored at the C plane location in
  \port{HAR}, modifying the colours and attributes of the current location. Two
  memory writes are performed.

  \li{\textsf{ORB} (\bin{0011}): OR value with B plane value.} The B plane value at the
  location in \port{HAR} is read, and ORred with the value in the \port{CMD}
  register. The result is written back to the same B plane location and is also
  made available in the \field{BPORT} field of \port{CMD}. Mostly useful for
  bitmap graphics, this command is ideal for setting individual pixels without
  having to perform host-side reads or \asm{OR} operations. One memory read and
  one memory write are performed.

  \li{\textsf{ORBWC} (\bin{0010}): OR value with B plane value, write to C plane.} Same as
  above, but in addition the value of the \port{CPORT} register is stored at
  the C plane location in \port{HAR}, modifying the colours and attributes of
  the current location. One memory read is performed, followed by
  two memory writes.

  \li{\textsf{ANDB} (\bin{0101}): Mask (AND) value with B plane value.} The B plane value at
  the location in \port{HAR} is read, and ANDed with the value in the
  \port{CMD} register. The result is written back to the same B plane location
  and is also made available in the \field{BPORT} field of \port{CMD}. Mostly
  useful for bitmap graphics, this command is ideal for clearing or masking
  individual pixels without having to perform host-side reads or \asm{AND}
  operations. As expected, the bitmap value to clear must be inverted with
  \asm{NOT} prior to this operation. One memory read and one memory write are
  performed.

  \li{\textsf{ANDBWC} (\bin{0100}): Mask (AND) value with B plane value, write to C plane.} Same
  as above, but in addition the value of the \port{CPORT} register is stored at
  the C plane location in \port{HAR}, modifying the colours and attributes of
  the current location. One memory read is performed, followed by
  two memory writes.

  \li{\textsf{XORB} (\bin{0111}): Toggle (XOR) value with B plane value.} The B plane value at
  the location in \port{HAR} is read, and XORed with the value in the
  \port{CMD} register. The result is written back to the same B plane location
  and is also made available in the \field{BPORT} field of \port{CMD}. Mostly
  useful for bitmap graphics, this command is ideal for toggling individual
  pixels without having to perform host-side reads or \asm{XOR}
  operations. This operation is useful for ‘rubber-bands’ or cursors, as
  performing it twice negates its effects. One memory read and one memory write
  are performed.

  \li{\textsf{XORBWC} (\bin{0110}): Toggle (XOR) value with B plane value, write to C plane.}
  Same as above, but in addition the value of the \port{CPORT} register is
  stored at the C plane location in \port{HAR}, modifying the colours and
  attributes of the current location. One memory read is performed, followed by
  two memory writes.

  \li{\textsf{WC} (\bin{1000}): Write to C plane only.} The value of the \port{CPORT}
  register is stored at the C plane location in \port{HAR}, modifying the
  colours and attributes of the current location without changing character or
  bitmap data. This command is useful for multicolour modes, or for simply
  painting over B plane data with colour. One memory write is performed.

  \li{\textsf{WCG} (\bin{1011}): Write to Character Generator RAM.} The value of the
  \field{CGPORT} field in the \port{CMD} register is written to the Character
  Generator RAM position in \port{HAR}, modifying part of a character
  pattern. This instruction is used to update font data. One memory write is
  performed.

  \li{\textsf{RBC} (\bin{1101}): Read from B and C planes.} The 8-bit value at the B plane
  location in \port{HAR} is read into the \field{BPORT} field in the \port{CMD}
  register. The 16-bit value at the C plane location in \port{HAR} is read into
  the \port{CPORT} register. Two memory reads are performed.

  %
\end{description}

All other commands are reserved for future expansion and should not be used. If
requested, the VDU will perform no task and will return to the ready state
immediately, setting the \field{GO} bit in the \port{CMD} register.

After execution of each command, the value of \port{HAR} is incremented by
\hex{0001} if \field{XINC} is set in the \port{CMD} register, and by \hex{0080}
if \field{YINC} is set. Although this is of limited use, both may be specified,
which increments \port{HAR} by \hex{0081} (along the main diagonal).

Repeating commands with neither \field{XINC} not \field{YINC} set is,
naturally, pointless as the address does not change between iterations.

\subsection{Examples}

\subsubsection{Write a Character With Colour}

This is a complete example to write an arbitrary character with a particular
colour.

\begin{cftasmcode}
         LI &82                      ; coordinates (2,1) (2 + 1 * 128)
         OUT VDU HAR                 ; Set address
         LOAD colour                 ; Load the colour attribute
         OUT VDU CPORT               ; Set the colour attribute
         LOAD cmd                    ; Load command
         OR char                     ; OR the character
         OUT VDU CMD                 ; Initiate the command
         HALT

colour:  .word &003F                 ; white on black
char:    .word 65                    ; ASCII 65 ('A')
cmd:     .word #000:000:0:1:00000000 ; Command 000, XINC = 1
\end{cftasmcode}

\noindent The code to write subsequent characters with the same colour and attributes is
considerably simpler because of the address auto-increment and the persistence
of the \port{CPORT} register:

\begin{cftasmcode}
         LOAD cmd                    ; Load command
         OR char                     ; OR the character
         OUT VDU CMD                 ; Initiate the command
\end{cftasmcode}

\noindent This seems a little excessive for writing a single character, but given the
nature of CFT Assembly, it is actually shorter than doing the same thing on a
hypothetical, non-planar memory-mapped VDU card, where colours are stored in
even locations and characters in odd ones\footnote{Exactly the way it is done
  in MDA, CGA, EGA, MCGA and VGA text modes.}:

\begin{cftasmcode}
         LI &82                      ; coordinates (2,1) (2 + 1 * 128)
         SBL                         ; Multiply by two
         ADD baddr1                  ; Add VDU base address (attrs)
         STORE R &80                 ; Use an autoincrement register
         ADD baddr2                  ; Add VDU base address (chars)
         STORE R &81                 ; Use another autoinc register

         LOAD colour                 ; Load the colour attribute
         STORE I R &80               ; Store the attribute
         LOAD char                   ; Load the character
         STORE I R &81               ; Store it
         HALT

baddr1:  .word &a000                 ; Base addr (attrs)
baddr2:  .word &a001                 ; Base addr (chars)
colour:  .word &003F                 ; white on black
char:    .word 65                    ; ASCII 65 ('A')
\end{cftasmcode}

\noindent The downside on dumb, memory-mapped devices is that writing {\em subsequent\/}
characters still takes more instructions:

\begin{cftasmcode}
         LOAD colour                 ; Load the colour attribute
         STORE I R &80               ; Store the attribute
         LOAD char                   ; Load the character
         STORE I R &81               ; Store it
\end{cftasmcode}

\noindent With the limited intelligence of the VDU card, writing two characters
with their colour values took 13 words and 10 instructions, while a
memory-mapped VGA-like device would need 17 words and 14 instructions, ignoring
the \asm{HALT} instruction.

\subsubsection{Write Two Characters Without Modifying Colours}

This changes the B plane without changing the C plane, keeping the colours and
attributes intact. The only difference from the previous example is the command
used:

\begin{cftasmcode}
         LI &82                      ; coordinates (2,1) (2 + 1 * 128)
         OUT VDU HAR                 ; Set address
         LOAD cmd                    ; Load command
         OR char1                    ; OR the character
         OUT VDU CMD                 ; Initiate the command

         LOAD cmd                    ; Load command
         OR char2                    ; OR the character
         OUT VDU CMD                 ; Initiate the command
         HALT

char1:   .word 65                    ; ASCII 65 ('A')
char2:   .word 66                    ; ASCII 65 ('B')
cmd:     .word #000:001:0:1:00000000 ; Command 001, XINC = 1
\end{cftasmcode}

\subsubsection{Paint Colour Attributes Without Modifying Characters}

This changes the C plane without touching the B plane, keeping the characters
intact but changing the colours and attributes. Again, the only difference is
in the command used, but modifying four consecutive positions is quite simple:

\begin{cftasmcode}
         LI &82                      ; coordinates (2,1) (2 + 1 * 128)
         OUT VDU HAR                 ; Set address
         LOAD colour                 ; Set the colour
         OUT VDU CPORT
         LOAD repeats                ; Set the number of repetitions
         OUT VDU
         LOAD cmd                    ; Initiate the command
         OUT VDU CMD
         HALT

colour:  .word &3f00                 ; Black on white
repeats: .word 3                     ; Number of characters +1
cmd:     .word #000:010:0:1:00000000 ; Command 010, XINC = 1
\end{cftasmcode}

\subsubsection{Creating a New Character Pattern}

This program programs the Character Generator by writing to the CG
Plane a pattern suitable for a 16-line ‘A’ glyph. It demonstrates how
to calculate CG plane addresses and demonstrates how the CFT Standard
Assembler's advanced features can simplify font generation.

\begin{cftasmcode}
         LI 65                       ; set the pattern for 'A'
         CLL RNL                     ; Multiply by 16
         OUT VDU HAR                 ; Set address
         LOAD pattern                ; Load start address of pattern
         STORE R &80                 ; Use an autoincrement register
         LI 16                       ; Loop 16 times
         NEG
         STORE R &10
loop:    LOAD I R &80                ; Load pattern data
         OR cmd
         OUT VDU CMD                 ; Send command and CG data
         ISZ R &10                   ; Loop?
         JMP loop
         HALT

cmd:     .word #000:011:0:1:00000000 ; Command 011, XINC = 1
pattern: .word #--------             ; Ascender, line 1
         .word #--------             ; Ascender, line 2
         .word #--------             ; Ascender, line 3
         .word #---1----             ; Top line of letters
         .word #--111---             ; 2
         .word #-11-11--             ; 3
         .word #11---11-             ; 4
         .word #11---11-             ; 5
         .word #1111111-             ; 6
         .word #1111111-             ; 7
         .word #11---11-             ; 8
         .word #11---11-             ; 9
         .word #11---11-             ; Bottom line of letters
         .word #--------             ; Descender, line 1
         .word #--------             ; Descender, line 2
         .word #--------             ; Descender, line 3
\end{cftasmcode}

\subsubsection{Read a Screen Row}

This example uses the read command to read all 128 cells of the first row of
the VDU memory. Both the B and C planes are read and stored in an interlaced
manner, suitable for writing to mass storage.

\begin{cftasmcode}
         LI 128                      ; Read 128 values
         NEG 
         STORE R &10
         LI 0                        ; Start address
         OUT VDU HAR                 ; Set it
         LOAD dest                   ; Get the destination
         STORE R &80                 ; Use an autoincrement register
         LOAD cmd
         OUT VDU CMD                 ; Issue the read command

loop:    IN VDU CPORT                ; First read from the C plane
         STORE I R &80               ; Store it
         IN VDU BPORT                ; Reading from the B PORT
                                     ; triggers the next read
         STORE I R &80
         ISZ R &10                   ; Loop?
         JMP loop
         HALT

source:  .word &0000                 ; Source VDU address
dest:    .word &8000                 ; Destination buffer
cmd:     .word #000:100:0:1:00000000 ; Command 100, XINC = 1
\end{cftasmcode}

\noindent Because of the way read increments are structured, to read the entire
display memory would require wrapping this code in an outer loop (which sets
the \port{HAR}) and up to 512 iterations.

\subsection{Suggested Mode Settings}

The following sections list suggested register values to configure various
useful modes, including some common variations. In all these samples, unless
stated otherwise, interrupt signalling is disabled and characters use character
set 0. The start address is reset to location \hex{0000}.

\subsubsection{80×30 Text/Semigraphics/Multicolour Mode}

This is the standard 80×30 text mode. After setting registers, the video memory
may be configured as a text, 160×30 semigraphics or 80×30 multicolour mode as
described in~\cf{sec:vdu:modes}. Of these, the text mode is the most useful.

\begin{center}
  \zebra
  \begin{tabular}{rccl}
    %\noalign{\smallskip}\hline\noalign{\smallskip}
    %\\\hline
    Address & Register & Value & Notes \\
    %\noalign{\smallskip}\hline\noalign{\smallskip}
    \hline
    \hex{1F0} & \hex{MCR0}  & \hex{8000} & Enable, 80 columns, 30 rows\\
    \hex{1F1} & \hex{MCR1}  & \hex{0000} & No split mode \\
    \hex{1F2} & \hex{SCR0}  & \hex{0000} & No smooth scroll \\
    \hex{1F4} & \hex{SAR0}  & \hex{0000} & Viewport origin at (0,0)\\
    \hex{1F6} & \hex{MAR0}  & \hex{FFFF} & Modulo at (127,511)\\
    \hex{1F8} & \hex{CCR}   & \hex{0B80} & Fast blinking orange cursor\\
    \hex{1F9} & \hex{CAR}   & \hex{0000} & Cursor at (0,0)\\
    \hex{1FA} & \hex{HAR}   & \hex{0000} & Next character at (0,0)\\
    \hex{1FD} & \hex{CPORT} & \hex{003F} & Set white on black for next character\\
    \hline
  \end{tabular}
\end{center}

\subsubsection{80×60 Text/Semigraphics/Multicolour Mode}

This is the 80×60 text mode, where character cells are 8×8, less legible than
the 8×16 of the corresponding 30-line mode. After setting registers, the video
memory may be configured as a text, 160×60 semigraphics or 80×60 multicolour mode
as described in~\cf{sec:vdu:modes}. The latter has square \glspl{PEL} and is
quite useful.

\begin{center}
  \zebra
  \begin{tabular}{rccl}
    %\noalign{\smallskip}\hline\noalign{\smallskip}
    %\\\hline
    Address & Register & Value & Notes \\
    %\noalign{\smallskip}\hline\noalign{\smallskip}
    \hline
    \hex{1F0} & \hex{MCR0}  & \hex{8011} & Enable, font 4, 80 columns, 60 rows\\
    \hex{1F1} & \hex{MCR1}  & \hex{0000} & No split mode \\
    \hex{1F2} & \hex{SCR0}  & \hex{0000} & No smooth scroll \\
    \hex{1F4} & \hex{SAR0}  & \hex{0000} & Viewport origin at (0,0)\\
    \hex{1F6} & \hex{MAR0}  & \hex{FFFF} & Modulo at (127,511)\\
    \hex{1F8} & \hex{CCR}   & \hex{0B80} & Fast blinking orange cursor\\
    \hex{1F9} & \hex{CAR}   & \hex{0000} & Cursor at (0,0)\\
    \hex{1FA} & \hex{HAR}   & \hex{0000} & Next character at (0,0)\\
    \hex{1FD} & \hex{CPORT} & \hex{003F} & Set white on black for next character\\
    \hline
  \end{tabular}
\end{center}

\subsubsection{40×30 Text/Semigraphics/Multicolour Mode}

This text mode is highly legible from a distance, and has square characters,
making it useful for games and graphics display. After setting registers, the
video memory may be configured as a text, 80×30 semigraphics or 40×30
multicolour mode as described in~\cf{sec:vdu:modes}. The latter has the largest
square \glspl{PEL} of any mode. The 80×30 semigraphics mode is not particularly
useful. The 80×30 multicolour is identical in features and easier to use.

\begin{center}
  \zebra
  \begin{tabular}{rccl}
    %\noalign{\smallskip}\hline\noalign{\smallskip}
    %\\\hline
    Address & Register & Value & Notes \\
    %\noalign{\smallskip}\hline\noalign{\smallskip}
    \hline
    \hex{1F0} & \hex{MCR0}  & \hex{8009} & Enable, 40 columns, 30 rows\\
    \hex{1F1} & \hex{MCR1}  & \hex{0000} & No split mode \\
    \hex{1F2} & \hex{SCR0}  & \hex{0000} & No smooth scroll \\
    \hex{1F4} & \hex{SAR0}  & \hex{0000} & Viewport origin at (0,0)\\
    \hex{1F6} & \hex{MAR0}  & \hex{FFFF} & Modulo at (127,511)\\
    \hex{1F8} & \hex{CCR}   & \hex{0B80} & Fast blinking orange cursor\\
    \hex{1F9} & \hex{CAR}   & \hex{0000} & Cursor at (0,0)\\
    \hex{1FA} & \hex{HAR}   & \hex{0000} & Next character at (0,0)\\
    \hex{1FD} & \hex{CPORT} & \hex{003F} & Set white on black for next character\\
    \hline
  \end{tabular}
\end{center}

\subsubsection{160×120 Semigraphics Mode}

The lowest 4:3-aspect graphics mode displays 160×120 \glspl{PEL}, each 4×4
native resolution pixels in size. There are no colour restrictions.

\begin{center}
  \zebra
  \begin{tabular}{rccl}
    %\noalign{\smallskip}\hline\noalign{\smallskip}
    %\\\hline
    Address & Register & Value & Notes \\
    %\noalign{\smallskip}\hline\noalign{\smallskip}
    \hline
    \hex{1F0} & \hex{MCR0}  & \hex{8002} & Enable, 80 columns, 120 rows\\
    \hex{1F1} & \hex{MCR1}  & \hex{0000} & No split mode \\
    \hex{1F2} & \hex{SCR0}  & \hex{0000} & No smooth scroll \\
    \hex{1F4} & \hex{SAR0}  & \hex{0000} & Viewport origin at (0,0)\\
    \hex{1F6} & \hex{MAR0}  & \hex{FFFF} & Modulo at (127,511)\\
    \hex{1F8} & \hex{CCR}   & \hex{0000} & Cursor off\\
    \hex{1F9} & \hex{CAR}   & \hex{0000} & Cursor off\\
    \hex{1FA} & \hex{HAR}   & \hex{0000} & Next character at (0,0)\\
    \hex{1FD} & \hex{CPORT} & \hex{003F} & Set white on black for next character\\
    \hline
  \end{tabular}
\end{center}

\subsubsection{320×240 Graphics Mode}

The lowest 4:3-aspect full graphics mode displays 320×240 \glspl{PEL}, each 2×2
native resolution pixels in size. It is based on the 40-column timings. As with
all graphics modes, every 8×1 PEL region can only have one foreground and one
background colour.

\begin{center}
  \zebra
  \begin{tabular}{rccl}
    %\noalign{\smallskip}\hline\noalign{\smallskip}
    %\\\hline
    Address & Register & Value & Notes \\
    %\noalign{\smallskip}\hline\noalign{\smallskip}
    \hline
    \hex{1F0} & \hex{MCR0}  & \hex{800C} & Enable, 40 columns, 240 rows\\
    \hex{1F1} & \hex{MCR1}  & \hex{0000} & No split mode \\
    \hex{1F2} & \hex{SCR0}  & \hex{0000} & No smooth scroll \\
    \hex{1F4} & \hex{SAR0}  & \hex{0000} & Viewport origin at (0,0)\\
    \hex{1F6} & \hex{MAR0}  & \hex{FFFF} & Modulo at (127,511)\\
    \hex{1F8} & \hex{CCR}   & \hex{0000} & Cursor off\\
    \hex{1F9} & \hex{CAR}   & \hex{0000} & Cursor off\\
    \hex{1FA} & \hex{HAR}   & \hex{0000} & Next character at (0,0)\\
    \hex{1FD} & \hex{CPORT} & \hex{003F} & Set white on black for next character\\
    \hline
  \end{tabular}
\end{center}

\subsubsection{640×480 Graphics Mode}

This is the full resolution of the VDU card, configured using 80-column
timings, with single pixel rows. Each 8×1 pixel region can only have one
foreground and one background colour.

\begin{center}
  \zebra
  \begin{tabular}{rccl}
    %\noalign{\smallskip}\hline\noalign{\smallskip}
    %\\\hline
    Address & Register & Value & Notes \\
    %\noalign{\smallskip}\hline\noalign{\smallskip}
    \hline
    \hex{1F0} & \hex{MCR0}  & \hex{8004} & Enable, 80 columns, 480 rows\\
    \hex{1F1} & \hex{MCR1}  & \hex{0000} & No split mode \\
    \hex{1F2} & \hex{SCR0}  & \hex{0000} & No smooth scroll \\
    \hex{1F4} & \hex{SAR0}  & \hex{0000} & Viewport origin at (0,0)\\
    \hex{1F6} & \hex{MAR0}  & \hex{FFFF} & Modulo at (127,511)\\
    \hex{1F8} & \hex{CCR}   & \hex{0000} & Cursor off\\
    \hex{1F9} & \hex{CAR}   & \hex{0000} & Cursor off\\
    \hex{1FA} & \hex{HAR}   & \hex{0000} & Next character at (0,0)\\
    \hex{1FD} & \hex{CPORT} & \hex{003F} & Set white on black for next character\\
    \hline
  \end{tabular}
\end{center}

\subsubsection{640×448 Graphics Mode with Four Lines of 8×8 Text}

This is a simple example of what can be achieved with split screen modes. The
top portion of the screen is configured as a full-resolution graphics mode. The
split is placed on scanline 448, making this a 640×448 mode. The bottom half of
the split is configured as an 80-column text mode. It is 32 scanlines high and
configured for 8×8 character cells, allowing for 4 rows of text. This mode
resembles the graphics-and-text split screen modes of many home micros.

\todo{Verify MCR1 value here. The split line is probably incorrect.}

\begin{center}
  \zebra
  \begin{tabular}{rccl}
    %\noalign{\smallskip}\hline\noalign{\smallskip}
    %\\\hline
    Address & Register & Value & Notes \\
    %\noalign{\smallskip}\hline\noalign{\smallskip}
    \hline
    \hex{1F0} & \hex{MCR0}  & \hex{8004} & Enable, 80 columns, 480 rows\\
    \hex{1F1} & \hex{MCR1}  & \hex{DA91} & Split on line 368, font 4, 8×8 \\
    \hex{1F2} & \hex{SCR0}  & \hex{0000} & No smooth scroll (top) \\
    \hex{1F3} & \hex{SCR1}  & \hex{0000} & No smooth scroll (bottom) \\
    \hex{1F4} & \hex{SAR0}  & \hex{0000} & Viewport origin at (0,0)\\
    \hex{1F5} & \hex{SAR1}  & \hex{D000} & Text portion starts at (0,416)\\
    \hex{1F6} & \hex{MAR0}  & \hex{C07F} & End at (127,384)\\
    \hex{1F7} & \hex{MAR1}  & \hex{FFFF} & End at (127,511)\\
    \hex{1F8} & \hex{CCR}   & \hex{0B80} & Fast blinking orange cursor\\
    \hex{1F9} & \hex{CAR}   & \hex{D000} & Cursor at (0,0) of text area\\
    \hex{1FA} & \hex{HAR}   & \hex{D000} & Next access at (0,0) of text area\\
    \hex{1FD} & \hex{CPORT} & \hex{003F} & Set white on black for next character\\
    \hline
  \end{tabular}
\end{center}

%% \subsection{Register File}
%% \subsubsection{Address Register}
%% \subsubsection{Cursor Address Register}

%% \subsection{Address Counters}
%% \subsection{Planes}

%% \subsection{Cursor Address Comparator}

%% \subsection{Colour Multiplexer}

%% \subsection{Pixel Shift Register}

%% \subsection{Pipeline}

%% \begin{figure*}
%% \centering
%% \begin{tikztimingtable}
%%   \ps{PIXCLK}          & 16{2L2H} \\
%%   \ps{PIXCLK÷8}        & 2H 16L 16H 16L 14H \\
%%   \ns{Address step}    & 2H 2L 30H 2L 14H 14H \\
%%   \ns{Memory cycle}    & 6H 2L 30H 2L 14H 10H \\
%%   \ns{Memory}          & 6Z 14D{\textcond MEMORY READ} Z 13D{\textcond HOST ACCESS} 4Z 14D{\textcond MEMORY READ} 12Z \\
%%   \ns{Bitmap load}     & 18H 2L 14H 16H 2L 12H \\
%%   \ns{Pixel shift}     & 4{2H2L} 4H 7{2H2L} 4H 3{2H2L}\\
%% \end{tikztimingtable}
%% \caption[Memory access timing]{\label{fig:mem-access-timing} Memory access timing.}
%% \end{figure*}

%% \subsection{DAC}

%% \section{Operation}

%% \subsection{Mode Demonstrations}

%% The following pages demonstrate in practical terms what is capable in some of
%% the graphics modes. The original, unprocessed image is shown
%% in~\fcf{fig:vdu:original}, followed by renderings in progressively higher
%% resolution modes. To improve the quality, the image colour-space was quantised
%% from 8 bits per channel (16,777,216 colours) to 2 bits per channel (64
%% colours), with the error diffused using the Floyd-Steinberg dithering
%% algorithm.

%% \begin{figure}
%%   \centering
%%   \includegraphics[width=0.9\columnwidth]{figs/vdu-test-image3-original.png}%
%%   \caption[Original 640×480 demonstration image]
%%           {\label{fig:vdu:mode-original}The original true-colour (24-bit colour)
%%     demonstration image, scaled down to 640×480.
%%   }
%% \end{figure}

%% \section{Theory of Operation}
%% \subsection{Colour Selection}

%% Choice of colour depending on whether a pixel is set, whether blinking
%% is in selected and in the ‘off’ state, and the setting of the inverse attribute.

%% \begin{center}
%%   \zebra
%%   \begin{tabular}{*{4}{>{\textsf\bgroup}c<{\egroup}}l}
%%     %\noalign{\smallskip}\hline\noalign{\smallskip}
%%     %\\\hline
%%     \ps{BLINK} & \ps{INVERT} & \ps{PIXEL} & \ps{FG/}\ns{BG} & Colour selection and notes\\
%%     %\noalign{\smallskip}\hline\noalign{\smallskip}
%%     \hline
%%     0 & 0 & 0 & 0 & Background colour\\
%%     0 & 0 & 1 & 1 & Foreground colour\\
%%     0 & 1 & 0 & 1 & Inverse: foreground colour\\
%%     0 & 1 & 1 & 0 & Inverse: background colour\\
%%     1 & 0 & 0 & 0 & Blinking (off): background colour\\
%%     1 & 0 & 1 & 0 & Blinking (off): background colour\\
%%     1 & 1 & 0 & 1 & Inverse, Blinking (off): foreground colour\\
%%     1 & 1 & 1 & 1 & Inverse, Blinking (off): foreground colour\\
%%     \hline
%%   \end{tabular}
%% \end{center}

%% \section{Notes}

%% \notes{../../notes/video.txt}

%% \todo{Still to be done.}

%% %% \begin{figure}
%% %%   \centering
%% %%   %% \includegraphics[width=0.4\columnwidth]{../generated/vdu-test-image3-small-dithered-320x25HGR.png}%
%% %%   %% \hfill%
%% %%   %% \includegraphics[width=0.4\columnwidth]{../generated/vdu-test-image3-small-dithered-640x25HGR.png}\\
%% %%   %% \vspace{.01\columnwidth}

%% %%   %% \includegraphics[width=0.45\columnwidth]{../generated/vdu-test-image3-small-dithered-320x50HGR.png}%
%% %%   %% \hspace{.01\columnwidth}%
%% %%   %% \includegraphics[width=0.45\columnwidth]{../generated/vdu-test-image3-small-dithered-640x50HGR.png}\\
%% %%   %% \vspace{.01\columnwidth}

%% %%   \includegraphics[width=0.45\columnwidth]{../generated/vdu-test-image3-small-dithered-320x100HGR.png}%
%% %%   \hspace{.01\columnwidth}%
%% %%   \includegraphics[width=0.45\columnwidth]{../generated/vdu-test-image3-small-dithered-640x100HGR.png}\\
%% %%   \vspace{.01\columnwidth}

%% %%   \includegraphics[width=0.45\columnwidth]{../generated/vdu-test-image3-small-dithered-320x240HGR.png}%
%% %%   \hspace{.01\columnwidth}%
%% %%   \includegraphics[width=0.45\columnwidth]{../generated/vdu-test-image3-small-dithered-640x240HGR.png}\\
%% %%   \vspace{.01\columnwidth}

%% %%   \includegraphics[width=0.45\columnwidth]{../generated/vdu-test-image3-small-dithered-320x480HGR.png}%
%% %%   \hspace{.01\columnwidth}%
%% %%   \includegraphics[width=0.45\columnwidth]{../generated/vdu-test-image3-small-dithered-640x480HGR.png}\\

%% %%   \caption{\label{fig:vdu:hgr-modes}Comparison of the most practical graphics
%% %%     modes. From top to bottom, then left to right: 320×100, 320×240, 320×480,
%% %%     640×100, 640×240, 640×480. Dithering is used to improve the colour range of
%% %%     the image display. The colour restrictions are obvious along the edges of
%% %%     the trail and the edges of the RGB disks.}

%% %% \end{figure}

%% %  \includegraphics[width=0.454\columnwidth]{../generated/vdu-test-image3-small-dithered.png}%

\section{Testing}

The design was coded in Verilog HDL and verified in stages. In the first stage,
Icarus Verilog was used and waveforms were observed using GTKWave. 

\subsection{Monitor Emulation}

Once the design appeared to be working sufficiently, a {\em monitor emulator\/}
was built for second stage testing.

The monitor emulator reads simple RGB and debugging output from the simulated
design, and constructs a visual representation of what a monitor might do with
the data. This is an ideal single-sync monitor. It only scans at one rate, but
accepts zero-width sync pulses and has zero-time fly-back. The image is
displayed using visual visual cues about the proper location and width of sync
pulses, and marks incorrect behaviour. Unlike a real monitor, the screen of the
monitor emulator shows the blanked/flyback areas. This is done to ensure that
no video data is sent during blanking. It is trivial to detect visually when
this is the case, but the emulator also draws red bars in the margins to aid in
detecting and locating unwanted behaviour.

\begin{figure}[htb]
  \centering
  
  \caption[Monitor Emulator Window Layout]{\label{fig:vdu:monitor-emu}The
    layout of a monitor emulator window. }
\end{figure}

The monitor emulator is illustrated in action in~\fcf{fig:vdu:monitor-emu}. In
this screenshot, the striped dark grey area represents sections where video was
blanked. The extents of horizontal and vertical blanking are also shown as
horizontal and vertical dark grey bars along the top and left hand side of the
image, respectively. Blanking when video should be enabled is marked with
bright red bars. In this example, two such cases are marked. Video during
blanking is indicated with magenta bars (not shown here). Yellow crop marks
indicate the extents of the image, including blanking. Dark red crop marks
indicate the extents of the visible video frame. Light grey lines mark
multiples of 8 pixels and can be used to detect misalignments of various
counters in the design. And, naturally, the video data is displayed. This frame
displays a number of issues. The first scanline is completely invalid since the
card has not gone through reset and its counters contain invalid values. It
extends past the end of even the monitor emulator's window. Horizontal video
enables a few pixels late for at least one scanline, and vertical video
disables one pixel too early. The image, displaying an 80×50\footnote{The
  monitor emulator was used when the VDU operated at a base mode of 640×400,
  before the switch to 640×480.} 64-colour stripe. There is an issue with the
colours every 16 columns. The cause was located in the sequencer, which did not
allow the horizontal address counters to propagate carry before using their
value, resulting in addresses that went from 15 to 0, then to 17 when the carry
propageted across the 4-bit boundary. This was when the design was meant for
4-bit \HC{193} counters, before its conversion to a CPLD.

\begin{figure*}
  \centering
  \begin{htmldiv}{center inline}
    \includesmall[width=0.48\columnwidth]{../figs/simulating-video-5.png}
    \hfill
    \includesmall[width=0.48\columnwidth]{../figs/simulating-video-cpld-1.png}
  \end{htmldiv}
  \vspace{1em}

  \begin{htmldiv}{center inline}
    \includesmall[width=0.48\columnwidth]{../figs/simulating-video-4.png}
    \hfill
    \includesmall[width=0.48\columnwidth]{../figs/simulating-video-cpld-4a.png}
  \end{htmldiv}
  \vspace{1em}

  \begin{htmldiv}{center inline}
    \includesmall[width=0.48\columnwidth]{../figs/simulating-video-cpld-5.png}
    \hfill
    \includesmall[width=0.48\columnwidth]{../figs/simulating-video-cpld-3.png}
  \end{htmldiv}
  \caption[Monitor Emulator Examples]{\label{fig:vdu:monitor-emu-examples}Examples of the monitor
    emulator decoding and displaying early 640×400 video waveforms from designs
    running in Verilog simulators. From left to right, and top to bottom: a
    40×25 colour test; a 40×25 text mode test; 80×25 test with buggy address
    generation; 80×25 with fine horizontal displacement (smooth scrolling);
    640×400 with buggy plane reads; and a split screen setup with 640×240 high
    resolution graphics (top) and 40×10 text (bottom).}
\end{figure*}

\subsection{Development Platform Testing}

Once the design was generating stable frames with all the required features, it
was transferred to physical hardware for the third stage of testing. For this
stage, the design was ported to a development board with an Altera Cyclone IV
FPGA and reworked until all features were again working properly.

The FPGA is configured with a test video pattern in ROM, which it displays on
reset, using the memory sequencer to copy from ROM to video memory. It also
interfaces with \gls{SDRAM}, not \gls{SRAM}, which makes the sequencer much
more complex, but also slightly less capable — dynamic memories are slower than
static ones. For this design, only writes are supported. Memory refreshes take
place during horizontal sync.

On this test platform, the CFT bus interface is present, but the CFT host is
simulated. The simulation accepts commands via JTAG, which it interprets as
reads or writes in I/O space. This is considerably slower than a real host, but
works for testing purposes. The Altera Virtual JTAG interface is driven by a
server process written in TCL\footnote{The scripting language chosen by Altera
  for their Quartus II IDE.}, which is in turn connected to and operated by
Python scripts.

A brief video of this arrangement demonstrating many features of the VDU board
may be found at \url{http://www.youtube.com/watch?v=BibdmHzaENE}.

\subsection{Hardware Testing}

This is intended to be the final round of testing and fine tuning, this time
running on an actual CPLD on the intended VDU board, with all ancillary
hardware in place. This testing is expected to be carried out using the CFT
itself as a test platform.

\section{Font Map}

The following pages illustrate the font used by the CFT. Since the VDU card has
no ROM, this is by no means a ROM font: it is downloaded to the card from the
host at boot time, partially and on demand: the ASCII section of the font is in
the CFT's ROM and is installed at boot time. Additional characters are then
downloaded as required, including the 256 bitmap patterns needed for high
resolution graphics.

A tentative, sparse list of character sets is as follows:

\begin{description}

\li{Character set \hex{0}}: the ASCII character set for 16-line modes,
augmented with line drawing and block graphic characters.

\li{Character set \hex{4}}: the ASCII character set for 8-line modes,
augmented with line drawing and block graphic characters.

\li{Character set \hex{C}}: space reserved for the 256 bitmap patterns.
\end{description}

\begin{figure}
  \centering
  
  \caption{Character set 0, page 1 of 4.}
\end{figure}

\begin{figure}
  \centering
  
  \caption{Character set 0, page 2 of 4.}
\end{figure}

\begin{figure}
  \centering
  
  \caption{Character set 0, page 3 of 4.}
\end{figure}

\begin{figure}
  \centering
  
  \caption{Character set 0, page 4 of 4.}
\end{figure}

%% %% \begin{figure}
%% %%   \centering
%% %%   \begin{tikzpicture}
%% %%     \input{../generated/fontmap-00b}
%% %%   \end{tikzpicture}
%% %% \end{figure}

%% %% \begin{figure}
%% %%   \centering
%% %%   \begin{tikzpicture}
%% %%     \input{../generated/fontmap-00c}
%% %%   \end{tikzpicture}
%% %% \end{figure}

%% %% \begin{figure}
%% %%   \centering
%% %%   \begin{tikzpicture}
%% %%     \input{../generated/fontmap-00d}
%% %%   \end{tikzpicture}
%% %% \end{figure}

%% }}

\section{Construction}

\begin{figure}
  \centering
  \includelarge{figs/video-max5-top.png}\\
  %
  \includelarge{figs/video-max5-top-silk.png}

  \caption{Video board printed circuit board, top side. Top, a
  simulated un-milled board (larger than the final result). Bottom, part placement.}
\end{figure}

\begin{figure}
  \centering
  \includelarge{figs/video-max5-bottom.png}\\
  %
  \includelarge{figs/video-max5-bottom-silk.png}

  \caption{Video board printed circuit board, bottom side. Top, a
  simulated board. Bottom, part placement.}
\end{figure}

\htmlbreak\clearpage
\section{Schematics}

The following pages show the schematic drawing of the \gls{VDU} board on five sheets.

\cleardoublepage
{
  \def\schematicsFile{figs/video-max5}
  \includeschns{2}{VDU Board}{sch2:vdu2}
  \includeschns{3}{VDU Board (Video Out with ESD protection)}{sch2:vdu3}
  \includeschns{4}{VDU Board (Other Connectors, Miscellaneous)}{sch2:vdu4}
  \includeschns{5}{VDU Board (CFT Expansion Bus)}{sch2:vdu5}
}

% End of file.
