alexiosc/cft/documentation/latex/cft_book/figure-datapath3.tex

% -*- latex -*-
\documentclass[class=memoir,border=200pt]{standalone}
\input{preamble-2018}
\input{macros-2018}

\begin{document}%
%\tikzexternaldisable%
\begin{tikzpicture}%

  \tikzstyle{major} = [heavy,col1]
  \tikzstyle{minor} = [major,col2]
  \tikzstyle{unit} = [major,col3]
  \tikzstyle{mux} = [major,col4,fill=white]
  \tikzstyle{bus} = [line width=3pt, rounded corners=15pt]
  \tikzstyle{smallbus} = [line width=2pt]
  \tikzstyle{signal} = [line width=1.5pt]

  \newcommand\majorReg[1]{
    \draw[major](0,0) rectangle(1.5,1);
    \draw(0.75,0.5) node {#1};
  }

  \newcommand\anyReg[2]{
    \draw[major,#1](0,0) rectangle(1.5,1);
    \draw(0.75,0.5) node {#2};
  }

  \newcommand\minorReg[1]{
    \draw[minor](0,0) rectangle(0.6,0.6);
    \draw(0.3,0.3) node {#1};
  }

  \newcommand\bitsliceabove[3]{
    \begin{scope}[xshift=#1,yshift=#2]
      \node[anchor=south,xshift=1mm,yshift=0.5mm]{\footnotesize #3};
      \draw(-0.05,-0.1) -- (0.05,0.1);
    \end{scope}
  }

  \newcommand\bitslicebelow[3]{
    \begin{scope}[xshift=#1,yshift=#2]
      \node[anchor=north,xshift=-1mm,yshift=-0.5mm]{\footnotesize #3};
      \draw(-0.05,-0.1) -- (0.05,0.1);
    \end{scope}
  }

  % The IBUS
  \draw[bus, stealth-](8,3.5) -- (8, 0) -- (0, 0) -- ++(0, 6.5) -- ++(14,0) -- ++(0,-2.5);
  \node[anchor=south east,align=right,xshift=14cm,yshift=3.9cm]{\IBUS};
  %\draw[bus, -stealth](8,0) -- (8,3.5);

  % The major registers
  \begin{scope}[xshift=1cm, yshift=2cm]
    \begin{scope}[yshift=3cm]
      \majorReg{\PC}
      \draw[bus, stealth-stealth] (-1,0.5) -- (0,0.5);
    \end{scope}
    \begin{scope}[yshift=1.5cm]
      \majorReg{\DR}
      \draw[bus, stealth-stealth] (-1,0.5) -- (0,0.5);
    \end{scope}
    \begin{scope}[yshift=0cm]
      \majorReg{\AC}
      \draw[bus, stealth-stealth] (-1,0.5) -- (0,0.5);
    \end{scope}
  \end{scope}

  % The Z and N regs
  \begin{scope}[xshift=1cm, yshift=0.9cm]
    \minorReg{\Zreg}
    \draw[signal,-stealth] (0.3,1.1) -- (0.3,0.6);
  \end{scope}
  \begin{scope}[xshift=1.9cm, yshift=0.9cm]
    \minorReg{\Nreg}
    \draw[signal,-stealth] (0.3,1.1) -- (0.3,0.6);
  \end{scope}

  % The L reg
  \begin{scope}[xshift=4.8cm,yshift=3cm]
    \minorReg{\Lreg}
  \end{scope}
  \draw[signal,-stealth] (4.8,3.3) -- (3.5,3.3) -- (3.5,2.7) -- ++(0.5,0);
  \draw[signal,-stealth] (5.5,2) -- (6,2) -- (6,3.3) -- (5.4,3.3);

  % The ALU
  \begin{scope}[xshift=4cm,yshift=0.5cm]
    \draw[unit] (0,0) -- ++(0,1) -- ++(0.5,0.25) -- ++(-0.5,0.25) -- ++(0,1) --
    ++(1.5,-0.75) -- ++(0,-1) -- cycle;
    \draw(1,1.25) node {ALU};
    \draw[bus,stealth-](0,0.5) -- ++(-1,0) -- ++(0,-1);
    %\draw[bus,sharp corners, stealth-](0,1.75) -- ++(-0.9,0) -- ++(0,0.3) -- ++(-0.6,0);
    \draw[bus,sharp corners, stealth-](0,1.75) -- ++(-1.5,0);
    \draw[bus,-stealth](1.5,1) -- ++(1,0) -- ++(0,-1.5);

    % The V reg
    \begin{scope}[xshift=3cm, yshift=0.95cm]
      \minorReg{\Vreg}
      \draw[signal,-stealth](-1.5,0.3) -- (0,0.3);
    \end{scope}
  \end{scope}

  % The IR
  \begin{scope}[xshift=7.25cm,yshift=3.5cm]
    \anyReg{col5}{\IR}
  \end{scope}

  % The Control Unit
  \begin{scope}[xshift=9.75cm,yshift=3.5cm]
    \draw[unit,col6] (0,0) rectangle (1.5,1.5);
    \draw (0.75,0.95) node {Control};
    \draw (0.75,0.55) node {Unit};
    \draw[bus, stealth-](0,0.5) -- ++(-1,0);
  \end{scope}

  % The Reset vector
  \begin{scope}[xshift=11.75cm,yshift=5cm]
    \draw[unit] (0,0) rectangle (1.5,1);
    \draw (0.75,0.5) node {Reset};
    \draw[bus,-stealth](1.5,0.5) -- ++(0.75,0);
  \end{scope}

  % The I reg
  \begin{scope}[xshift=10.2cm,yshift=5.5cm]
    \minorReg{\Ireg}
    \draw[signal, stealth-](0.3,0) -- ++(0,-0.5);
  \end{scope}

  % The AGL
  \begin{scope}[xshift=7.25cm,yshift=5cm]
    \draw[unit](0,0) rectangle(1.5,1);
    \draw(0.75,0.5) node {AGL};
    \draw[bus, -stealth] (1.5,0.5) -- ++(1,0) -- ++(0,1);
    \draw[smallbus, stealth-](0,0.3) -- ++(-0.75,0) -- ++(0,-1.2) -- ++(0.75,0);
    \bitslicebelow{-0.45cm}{-0.9cm}{10 LSB}
  \end{scope}

  % The AGL Mux
  \begin{scope}[xshift=5.5cm,yshift=5cm]
    \draw[mux](0,0) rectangle (0.4,1);
    \draw[smallbus, stealth-] (0,0.7)-- ++(-0.75,0); % The 000000 source
    \bitsliceabove{-0.45cm}{0.7cm}{6}
    \draw[right](-2.1,0.7) node{\bin{000000}};
    \draw[smallbus, stealth-] (0,0.3)-- ++(-3,0); % From PC
    \bitslicebelow{-0.65cm}{0.3cm}{6 MSB}
    \draw[smallbus, -stealth] (0.4,0.7) -- ++(1.35,0); % To AGL
    \bitsliceabove{1.07cm}{0.7cm}{6}
  \end{scope}

  % The AR
  \begin{scope}[xshift=9cm,yshift=2cm]
    \anyReg{col5}{\AR}
    \draw[bus,stealth-](0,0.5) -- ++(-1,0) -- ++(0,-1);
    \draw[bus,-stealth](1.5,0.7) -- ++(3.5,0);
    \node[anchor=west,align=left,xshift=5cm,yshift=0.7cm]{Address bus};
    \bitsliceabove{4.39cm}{0.7cm}{16}
  \end{scope}

  % The MBU
  \begin{scope}[xshift=11.5cm,yshift=1.25cm]
    \anyReg{col5}{MBU}
    \draw[smallbus,stealth-](0,0.5) -- ++(-0.7,0) -- ++(0,.5) -- ++(-0.3,0);
    \draw[smallbus,-stealth](1.5,0.5) -- ++(1,0);
    \node[anchor=west,align=left,xshift=2.5cm,yshift=0.5cm]{AExt};
    \bitslicebelow{-0.45cm}{0.5cm}{3 MSB}
    \bitsliceabove{1.9cm}{0.5cm}{8}
  \end{scope}

  % Data bus drivers
  \begin{scope}[xshift=9cm,yshift=0.5cm]
    \anyReg{col5}{Data Bus}
    \draw[bus,stealth-stealth](0,0.5) -- ++(-1,0);% -- ++(0,-0.5);
    \draw[bus,stealth-stealth](1.5,0.3) -- ++(3.5,0);
    \bitsliceabove{4.39cm}{0.3cm}{16}
    \node[anchor=west,align=left,xshift=5cm,yshift=0.3cm]{Data bus};
  \end{scope}

  %% \input{partial-addressing-modes}

  %% % The IR
  %% \AddressingModeIR{0}{1}

  %% % Six bits of zeroes.
  %% \begin{scope}[,yshift=-1.5cm]
  %%   \SixBitsOfZeroes
  %% \end{scope}

  %% % The Accumulator.
  %% \begin{scope}[,yshift=-3cm]
  %%   \begin{scope}[thin,draw opacity=0,line width=0pt]
  %%     %% \foreach \x in {0, 1, 2, 3, 4, 5, 6, 7}{
  %%     %%   \draw[fill=cfthl!50,xshift=\x cm](0,0) rectangle (0.5,0.6);
  %%     %%   \draw[fill=cfthl!25,xshift=\x cm](0.5,0) rectangle (1,0.6);
  %%     %% }
  %%     \draw[fill=cfthl!25](0,0) rectangle (3,0.6);
  %%     \draw[fill=cfthl!50](3,0) rectangle (8,0.6);
  %%   \end{scope}
  %%   \draw[thick](3,-0.1) -- (3,0.6);
  %%   \foreach \x in {0.5, 1, ..., 7.5}{
  %%     \draw[thin] (\x cm, 0) -- (\x cm, -0.1cm);
  %%   }
  %%   \foreach \x in {0, 1, ..., 5}{
  %%     \draw (0.25 + 0.5 * \x, 0.3) node { \bin{0} };
  %%   }
  %%   \draw (5.5, 0.3) node { Address \hex{0000}–\hex{03FF} };
  %%   \draw[line width=2pt](0,0) rectangle (8,0.6);
  %%   \draw (8,0) node[below] { \footnotesize 0 };
  %%   \draw (.25,0) node[below] { \footnotesize 15 };
  %%   \draw (8.2,0.3) node[right] { \PC };
  %% \end{scope}

  %% % The arrows
  %% \foreach \x in {0.25, 0.75, ..., 2.75} {
  %%   \draw[arrow, -stealth] (\x, -1.5) -- (\x, -2.4);
  %% }
  %% \foreach \x in {3.25, 3.75, ..., 7.75} {
  %%   \draw[arrow, -stealth] (\x, 0) -- (\x, -2.4);
  %% }
    
\end{tikzpicture}%
%\tikzexternalenable%
\end{document}

% End of file.
