alexiosc/cft/documentation/latex/cft_book/figure-major-states.tex

% -*- latex -*-
\documentclass[border=200pt,class=memoir]{standalone}
\input{preamble-new}

\begin{document}%
%\tikzexternaldisable%

\begin{tikzpicture}%

    \begin{scope}[line width=1pt]
      \tikzset{initial text={Power on}}
      \begin{scope}[line width=2pt]
        \node[state,initial,col1]         (R) {R};
        \node[state,col2]         (F) [right =of R] {F};
        \node[state,col3]         (E) [right =of F] {E};
        \node[state,col4]         (S) [above =of F] {S};
        \node[state,col5]         (I) [below =of F] {I};
      \end{scope}

      \draw[->] (R.338) .. controls +(338:3mm) and +(202:3mm) .. (F.202);
      \draw[->] (F.158) .. controls +(158:3mm) and +(22:3mm) .. (R.22);
      \draw[->] (F.338) .. controls +(338:3mm) and +(202:3mm) .. (E.202);
      \draw[->] (E.158) .. controls +(158:3mm) and +(22:3mm) .. (F.22);
      \draw[->] (E.north) .. controls +(up:35mm) and +(up:35mm) .. (R.north);
      \draw[->] (E) -- (I);
      \draw[->] (I) -- (R);
      \draw[->] (I) -- (F);
      \draw[->] (E) -- (S);
      \draw[->] (S) -- (R);
      \draw[->] (S) -- (F);
    \end{scope}

\end{tikzpicture}
%\tikzexternalenable%
\end{document}

% End of file.
