alexiosc/cft/documentation/latex/cft_book/preamble.tex

% -*- latex -*-
\usepackage{pgf}
\usepackage{tikz}
%\usetikzlibrary{arrows,positioning,automata,shadows,fit,shapes,counters}
\usetikzlibrary{arrows,positioning,automata,shadows,fit,shapes,patterns}
%\usetikzlibrary{external}
%\tikzexternalize[prefix=tikz/]
%\tikzset{external/system call={xelatex \tikzexternalcheckshellescape -halt-on-error -interaction=batchmode -jobname "\image" "\texsource"}}
\usepackage{standalone}

\usepackage{layout}

%\usepackage[tocindentauto]{tocstyle}

%\usepackage[cam,a4,center]{crop}

\hypersetup{
    pdftitle={CFT Minicomputer Programming Guide},
    pdfauthor={Alexios Chouchoulas},
    pdfkeywords={},
    bookmarksnumbered,
    pagebackref=true,
    breaklinks=true,
%    pdfview=FitH,       % Or try pdfstartview={FitV}, This lead to uncorrect bookmarks
    urlcolor=darkblue,
    colorlinks=true,
    citecolor=cftoutline,          %citeref's color
    linkcolor=cftoutline,
        }

\makeindex
\makeglossaries
\input{glossary}

\usepackage{listings}
\lstset{%
  xleftmargin=35pt,
  xrightmargin=5pt,
  basicstyle={\ttfamily},
  backgroundcolor=\color{cfthl!25},
  rulecolor=\color{cfthl!25},
  framesep=5pt,
  rulesep=5pt,
  frame=tlrb,
  framexleftmargin=10pt,
  flexiblecolumns=true,
  keepspaces=true,
  numbers=left,
  numbersep=5pt,
  numberstyle={\scriptsize\sffamily\color{cftlight}}
}

%%%%%%%%%%%%%%%%%%%%%%%%%%%%%%%%%%%%%%%%%%%%%%%%%%%%%%%%%%%%%%%%%%%%%%%%%%%%%%%
%%
%% LISTS OF THINGS
%%
%%%%%%%%%%%%%%%%%%%%%%%%%%%%%%%%%%%%%%%%%%%%%%%%%%%%%%%%%%%%%%%%%%%%%%%%%%%%%%%

%% %%%\addtolength\cftfignumwidth{1.5em}
\makeatletter
%% \addtolength{\cftchapternumwidth}{0.5em}
%% \addtolength{\cftsectionnumwidth}{0.5em}
%% \addtolength{\cftsubsectionnumwidth}{0.5em}
%% \addtolength{\cftfigurenumwidth}{0.5em}
%% \addtolength{\cfttablenumwidth}{0.5em}
\renewcommand*\l@section{\@dottedtocline{1}{1.5em}{2.3em}}
\renewcommand*\l@subsection{\@dottedtocline{2}{3.8em}{3.2em}}
\renewcommand*\l@subsubsection{\@dottedtocline{3}{7.0em}{4.1em}}
\renewcommand*\l@paragraph{\@dottedtocline{4}{10em}{5em}}
\renewcommand*\l@subparagraph{\@dottedtocline{5}{12em}{6em}}
\setcounter{maxsecnumdepth}{3}

%\addtolength{\cftschematicsnumwidth}{1em}
\renewcommand{\@pnumwidth}{3em}
\renewcommand{\@tocrmarg}{4em}
\makeatother

%\newcommand\listalgname{List of Algorithms} 
%\newlistof{alg}{algorithm}

%
% Schematics
%

\newcommand\listschematicname{List of Schematics} 
\newlistof{listofschematic}{los}{\listschematicname}
\newcounter{schematic}
\newcommand{\schematic}[1]{%
  \refstepcounter{schematic}%
  \par\noindent\textbf{Schematic \theschematic. #1}
  \addcontentsline{los}{section}{\protect\numberline{\theschematic}#1}\par%
}
\newcommand\listofschematics\listofschematic

%
% I/O Ports
%

\newcommand\listioportname{List of Input/Output Ports} 
\newlistof{listofioport}{loioport}{\listioportname}
%% \newcommand{\registerioport}[1]{%
%%   \refstepcounter{ioport}%
%%   \addcontentsline{loioport}{section}{\protect\numberline{\ }%
%% }
\newcommand\listofioports\listofioport

\newcommand\caution[1]{\textcolor{caution}{\textbf{#1}}}
%\newcommand\todo[1]{\textcolor{caution}{\bf{TODO: #1}}}

%
% Tasks
%

\newcommand\listtasksname{List of Incomplete Tasks} 
\newlistof{listoftask}{lotasks}{\listtasksname}
\newcounter{task}
\newcommand{\todo}[1]{%
  \refstepcounter{task}%
  {\textcolor{caution}{\textbf{TODO: #1}}}
  \addcontentsline{lotasks}{section}{\protect\numberline{\arabic{task}}To Do: #1}\par%
}
\newcommand{\bug}[2]{%
  \refstepcounter{task}%
  {\textcolor{caution}{\textbf{BUG: #1 #2}}}
  \addcontentsline{lotasks}{section}{\protect\numberline{\arabic{task}}Bug: #1}\par%
}
\newcommand\listoftasks\listoftask

%
% Data structures
%

\newcommand\listdatastructurename{List of Data Structures} 
\newlistof{listofdatastructure}{lods}{\listdatastructurename}
\newcounter{datastructure}
%\newcommand{\datastructure}[1]{%
%  \refstepcounter{datastructure}%
%  \par\noindent\textbf{Data Structure \thedatastructure. #1}
%  \addcontentsline{lods}{section}{\protect\numberline{\thedatastructure}#1}\par%
%}
\newcommand\listofdatastructures\listofdatastructure

%%%%%%%%%%%%%%%%%%%%%%%%%%%%%%%%%%%%%%%%%%%%%%%%%%%%%%%%%%%%%%%%%%%%%%%%%%%%%%%
%%
%% SECTION STYLING
%%
%%%%%%%%%%%%%%%%%%%%%%%%%%%%%%%%%%%%%%%%%%%%%%%%%%%%%%%%%%%%%%%%%%%%%%%%%%%%%%%

%% \usepackage{kpfonts}
\usepackage[explicit]{titlesec}

\counterwithin*{chapter}{part}
\counterwithin*{figure}{chapter}
\counterwithin*{schematic}{chapter}
\counterwithin*{datastructure}{chapter}
\counterwithin*{table}{chapter}

%%%%%%%%%%%%%%%%%%%%%%%%%%%%%%%%%%%%%%%%%%%%%%%%%%%%%%%%%%%%%%%%%%%%%%%%%%%%%%%

\renewcommand\thepart{\Alph{part}}
\cftpagenumbersoff{part}
%\newcommand*\partlabel{}

\makeatletter
\patchcmd{\l@part}{\hss#2}{}{}{}
\makeatother

\renewcommand\partnamefont{\normalfont\sffamily\Huge\scshape}
\renewcommand\partnumfont{\bfseries}
\renewcommand\printparttitle[1]{
  \thispagestyle{empty}
    \begin{tikzpicture}[remember picture,overlay]
      \node[yshift=-\paperheight, draw opacity=0] at (current page.north west)
           {\begin{tikzpicture}[remember picture, overlay]
               \draw[fill=cftlight] (0,0) rectangle
               (\paperwidth,\paperheight);
               \draw[fill=cftoutline] (0,1cm) rectangle
               (\paperwidth,0);
               \node[anchor=east,yshift=0.5\paperheight,xshift=.87\paperwidth,rectangle]
                    {\scalebox{2}{\color{white}\printpartname~\printpartnum}};
                    \node[anchor=east,yshift=0.43\paperheight,xshift=.87\paperwidth,rectangle]
                         {\scalebox{1.5}{\color{white} #1}};
             \end{tikzpicture}
           };
    \end{tikzpicture}
}

\newcommand*\chapterlabel{}
\titleformat{\chapter}
  {\gdef\chapterlabel{}
   \normalfont\sffamily\Huge}
  {\gdef\chapterlabel{\thechapter\ }}{0pt}
  {%
    \setcounter{page}{1}
    \begin{tikzpicture}[remember picture,overlay]
    \node[yshift=-5cm, draw opacity=0] at (current page.north west)
      {\begin{tikzpicture}[remember picture, overlay]
        \draw[fill=cftlight] (0,0) rectangle
          (\paperwidth,5cm);
        \draw[fill=cftoutline] (0,0.25cm) rectangle
          (\paperwidth,0);
        \node[anchor=east,yshift=2cm,xshift=.87\paperwidth,rectangle]
              {\color{white}\chapterlabel#1};
       \end{tikzpicture}
      };
   \end{tikzpicture}
  }
\titlespacing*{\chapter}{0pt}{50pt}{20pt}

\titleformat{\section}
            {\gdef\sectionlabel{}\normalfont\sffamily\Large}
            {\gdef\sectionlabel{\thesection\ }}{0pt}
            {\color{cftoutline}\thesection\quad #1\\
              \titlerule[2pt]
            }[{\vspace{-30pt}\color{cftoutline}\rule{\textwidth}{2pt}}]

\titleformat{\subsection}
  {\gdef\subsectionlabel{}
   \normalfont\sffamily\bfseries\large}
  {\gdef\subsectionlabel{\thesubsection\ }}{0pt}
  {\color{cftoutline}\thesubsection\quad #1}

\titleformat{\subsubsection}
  {\gdef\subsubsectionlabel{}
   \normalfont\sffamily\large}
  {\gdef\subsubsectionlabel{\thesubsubsection\ }}{0pt}
  {\color{cftoutline}#1}

%%%%%%%%%%%%%%%%%%%%%%%%%%%%%%%%%%%%%%%%%%%%%%%%%%%%%%%%%%%%%%%%%%%%%%%%%%%%%%%

%% \titleformat{\paragraph}
%%   {\gdef\chapterlabel{}
%%    \normalfont\bfseries}
%%   {\gdef\chapterlabel{\theparagraph\ }}{0pt}
%%   {\color{cftoutline}#1}

%\geometry{a4paper, hoffset=0in, voffset=-.25in, left=1.5cm, right=1.5cm,
%  top=2.5cm, bottom=2.5cm}
%\geometry{paperwidth=17.5cm, paperheight=23.1cm, hoffset=0in, voffset=-.25in, left=1in, right=1in,
%  top=1in, bottom=1in}
\geometry{a4paper, hoffset=0in, left=1.2in, right=1.2in,
  top=1.2in, bottom=1.2in, includefoot, footskip=40pt}
%\sloppy

% Fonts
%\defaultfontfeatures{Mapping=tex-text}
\setmainfont{Minion Pro}
\setsansfont{Myriad Pro}
\setmonofont[]{Inconsolata}

% Not really used here, but never mind.
\setlength\columnsep{7mm}

% Input our local macro definitions
\input{typographic-conventions}
\input{bom}

%%%%%%%%%%%%%%%%%%%%%%%%%%%%%%%%%%%%%%%%%%%%%%%%%%%%%%%%%%%%%%%%%%%%%%%%%%%%%%%
%%%%%%%%%%%%%%%%%%%%%%%%%%%%%%%%%%%%%%%%%%%%%%%%%%%%%%%%%%%%%%%%%%%%%%%%%%%%%%%
%%%%%%%%%%%%%%%%%%%%%%%%%%%%%%%%%%%%%%%%%%%%%%%%%%%%%%%%%%%%%%%%%%%%%%%%%%%%%%%
%%%%%%%%%%%%%%%%%%%%%%%%%%%%%%%%%%%%%%%%%%%%%%%%%%%%%%%%%%%%%%%%%%%%%%%%%%%%%%%
