alexiosc/cft/documentation/latex/cft_book/figure-vdu-semigraphics-bit-pattern.tex

% -*- latex -*-
\documentclass[class=memoir,border=200pt]{standalone}
\input{preamble-new}

\begin{document}%
%\tikzexternaldisable%
\begin{tikzpicture}%

   \def\modeWidth{20mm}
   \def\modeHeight{16mm}

   \begin{scope}
     \draw[step=0.25cm,color=cfthl!90] (0,0) grid (2,4);
     \draw[fill=black] (0,0) rectangle (1,4);
     \draw[step=0.25cm,draw opacity=0.5,color=cfthl!90] (0,0) grid (1,4);
     \draw[heavy,fill=none] (0,0) rectangle (2,4);
     \draw (1,0) node[below] {160×30};
   \end{scope}

   \begin{scope}[xshift=2.5cm,xscale=2]
     \draw[step=0.25cm,color=cfthl!90] (0,0) grid (2,4);
     \draw[fill=black] (0,0) rectangle (1,4);
     \draw[step=0.25cm,draw opacity=0.5,color=cfthl!90] (0,0) grid (1,4);
     \draw[heavy,fill=none] (0,0) rectangle (2,4);
     \draw (1,0) node[below] {80×30};
   \end{scope}

   \begin{scope}[yshift=-2.75cm]
     \begin{scope}
       \draw[step=0.25cm,color=cfthl!90] (0,0) grid (2,2);
       \draw[fill=black] (0,0) rectangle (1,2);
       \draw[step=0.25cm,draw opacity=0.5,color=cfthl!90] (0,0) grid (1,2);
       \draw[heavy,fill=none] (0,0) rectangle (2,2);
       \draw (1,0) node[below] {160×60};
     \end{scope}

     \begin{scope}[xshift=2.5cm,xscale=2]
       \draw[step=0.25cm,color=cfthl!90] (0,0) grid (2,2);
       \draw[fill=black] (0,0) rectangle (1,2);
       \draw[step=0.25cm,draw opacity=0.5,color=cfthl!90] (0,0) grid (1,2);
       \draw[heavy,fill=none] (0,0) rectangle (2,2);
       \draw (1,0) node[below] {80×60};
     \end{scope}
   \end{scope}

   \begin{scope}[yshift=-4.5cm]
     \begin{scope}
       \draw[step=0.25cm,color=cfthl!90] (0,0) grid (2,1);
       \draw[fill=black] (0,0) rectangle (1,1);
       \draw[step=0.25cm,draw opacity=0.5,color=cfthl!90] (0,0) grid (1,1);
       \draw[heavy,fill=none] (0,0) rectangle (2,1);
       \draw (1,0) node[below] {160×120};
     \end{scope}

     \begin{scope}[xshift=2.5cm,xscale=2]
       \draw[step=0.25cm,color=cfthl!90] (0,0) grid (2,1);
       \draw[fill=black] (0,0) rectangle (1,1);
       \draw[step=0.25cm,draw opacity=0.5,color=cfthl!90] (0,0) grid (1,1);
       \draw[heavy,fill=none] (0,0) rectangle (2,1);
       \draw (1,0) node[below] {80×120};
     \end{scope}
   \end{scope}

   \begin{scope}[yshift=-5.75cm]
     \begin{scope}
       \draw[step=0.25cm,color=cfthl!90] (0,0) grid (2,0.5);
       \draw[fill=black] (0,0) rectangle (1,0.5);
       \draw[step=0.25cm,draw opacity=0.5,color=cfthl!90] (0,0) grid (1,0.5);
       \draw[heavy,fill=none] (0,0) rectangle (2,0.5);
       \draw (1,0) node[below] {160×240};
     \end{scope}

     \begin{scope}[xshift=2.5cm,xscale=2]
       \draw[step=0.25cm,color=cfthl!90] (0,0) grid (2,0.5);
       \draw[fill=black] (0,0) rectangle (1,0.5);
       \draw[step=0.25cm,draw opacity=0.5,color=cfthl!90] (0,0) grid (1,0.5);
       \draw[heavy,fill=none] (0,0) rectangle (2,0.5);
       \draw (1,0) node[below] {80×240};
     \end{scope}
   \end{scope}

   \begin{scope}[yshift=-6.75cm]
     \begin{scope}
       \draw[step=0.25cm,color=cfthl!90] (0,0) grid (2,0.25);
       \draw[fill=black] (0,0) rectangle (1,0.25);
       \draw[step=0.25cm,draw opacity=0.5,color=cfthl!90] (0,0) grid (1,0.25);
       \draw[heavy,fill=none] (0,0) rectangle (2,0.25);
       \draw (1,0) node[below] {160×480};
     \end{scope}

     \begin{scope}[xshift=2.5cm,xscale=2]
       \draw[step=0.25cm,color=cfthl!90] (0,0) grid (2,0.25);
       \draw[fill=black] (0,0) rectangle (1,0.25);
       \draw[step=0.25cm,draw opacity=0.5,color=cfthl!90] (0,0) grid (1,0.25);
       \draw[heavy,fill=none] (0,0) rectangle (2,0.25);
       \draw (1,0) node[below] {80×480};
     \end{scope}
   \end{scope}

\end{tikzpicture}%
%\tikzexternalenable%
\end{document}

% End of file.
