alexiosc/cft/documentation/latex/figs/din41612.pdf

C

32

A1B

DIN41612 -C

a c

Ground
+5V
Reserved

Test point A

Ground
+5V
Reserved

Test point C

+12V | +12V
+5V | +5V
Pin A1 | Pin C1
Pin A32 | Pin C32
