alexiosc/cft/documentation/latex/cft_book/cft-prog-programming-model.tex

% -*- latex -*-

\HtmlMetaDescription{This chapter describes the CFT's programming
  model at the machine code level.}
%\HtmlMetaGoogleDescription{}
%\HtmlMetaBanner{}
%\HtmlMetaTags{}

%% %\twocolumn[
%% \centering
%% \includegraphics{figs/cft-logo-v1.pdf}\vspace{2em}\\
%% {\LARGE\bfseries CFT Minicomputer Programming Guide}
%% \vspace{10pt}

%% {\Large Alexios Chouchoulas}\\\vspace{5pt}
%% {\large \hyperemail{alexios@bedroomlan.org}}

%% \vspace{20pt}

%% %  \begin{abstract}
%%     \small
    
%%   This document discusses the architecture of the CFT computer from a
%%   programmer's perspective. The CFT is a solid-state, 16-bit,
%%   microcoded architecture reminiscent, among others, of the DEC
%%   PDP-8. The computer incorporates a 16-bit word width with separate
%%   memory and input/output addressing spaces and a minimal, orthogonal
%%   instruction set that is still particularly versatile. The design
%%   includes separate internal (processor) and external (peripheral)
%%   buses and is extensible both via processor extensions and
%%   peripherals.

%%   A brief explanation of the architecture is provided, along with a
%%   discussion of its programming model, instruction set, and
%%   limitations. Short examples of CFT Assembly code are provided, along
%%   with a complete opcode table with semantics and timing information.
    
%  \end{abstract}
  
%  \chapter{History of Changes}

  {\bfseries 2011-10-10} First draft compiled from notes, hardware description
  and schematics.

  {\bfseries 2011-10-18} Fixed hexadecimal opcode of macro \instr{ING} in the
  instruction table. Corrected minor semantic and typesetting errors.
  
  {\bfseries 2011-11-06} Added datapath diagram and description. Minor typo
  corrections.

  {\bfseries 2011-11-15} Added \instr{SEL} macro.

  {\bfseries 2011-11-17} Overflow detection and new instructions. Covered
  changes from Microcode Version 3 (\instr{OP1} and \instr{OP2} changes),
  register descriptions, new instructions.

  {\bfseries 2011-11-23} Accumulator acronym is now \A. Memory Address
  Register is now the Address Register (\AR). Various minor
  nomenclature changes and typographical errata.

  {\bfseries 2012-01-23} The {\sffamily R} instuction field is now reversed
  (microcode version 4).

  {\bfseries 2012-05-12} Further editing to account for microcode version 4,
  reworked figures.

%] % End of \twocolumn

%% \tikzset{boxes/.style={line width=2pt}}
%% \begin{figure*}[t!]
%%   \centering
%%   \begin{tikzpicture}[boxes]
%%     \begin{scope}[yshift=0cm]
%%       \draw[boxes, fill=red!30](0,0) rectangle (8,1);
%%       \draw (4,0.5) node {Microcode};
%%     \end{scope}

%%     \begin{scope}[yshift=1cm]
%%       \draw[boxes, fill=orange!30](0,0) rectangle (8,1);
%%       \draw (4,0.5) node {Instruction Set};
%%     \end{scope}

%%     \begin{scope}[yshift=2cm]
%%       \draw[boxes, fill=orange!30](0,0) rectangle (8,1);
%%       \draw (4,0.5) node {Instruction Macros and Extensions};
%%     \end{scope}

%%     \begin{scope}[yshift=3cm]
%%       \draw[boxes, fill=yellow!30](0,0) rectangle (8,1);
%%       \draw (4,0.5) node {Assembler Macros};
%%     \end{scope}

%%     \begin{scope}[yshift=4cm]
%%       \draw[boxes, fill=yellow!30](0,0) rectangle (8,1);
%%       \draw (4,0.5) node {Assembly Sub-programs};
%%     \end{scope}

%%     \begin{scope}[yshift=5cm]
%%       \draw[boxes, fill=green!30](0,0) rectangle (8,1);
%%       \draw (4,0.5) node {Forth Code Words};
%%     \end{scope}

%%     \begin{scope}[yshift=6cm]
%%       \draw[boxes, fill=cyan!30](0,0) rectangle (8,1);
%%       \draw (4,0.5) node {Native Forth Words};
%%     \end{scope}

%%     %% \begin{scope}[yshift=7cm]
%%     %%   \draw[boxes, fill=blue!30](0,0) rectangle (8,1);
%%     %%   \draw (4,0.5) node {Forth Applications};
%%     %% \end{scope}

%%     %% \begin{scope}[yshift=8cm]
%%     %%   \draw[boxes, fill=magenta!30](0,0) rectangle (8,1);
%%     %%   \draw (4,0.5) node {Higher Levels...};
%%     %% \end{scope}

%%   \end{tikzpicture}

%%   \caption{\label{fig-progmodel}Various levels of the CFT Programming Model.}

%% \end{figure*}

\section{Introduction}

  This document discusses the architecture of the CFT computer from a
  programmer's perspective. The CFT is a solid-state, 16-bit
  architecture reminiscent, among others, of the DEC
  PDP-8.\footnote{Newer versions of this document and additional
    documentation and downloads may be found at the following URL:\\
    \link{www.bedroomlan.org/hardware/cft}.}

  The computer incorporates a 16-bit word, 65,536 words of addressable
  main memory and 65,536 words of input/output (I/O) space.

  Instructions are 16-bits. There are ten \glspl{register} (five are 16-bits
  wide, the remaining five are single-bit flags) and a simple, nearly
  orthogonal instruction set. The computer is able to initialise itself without
  operator intervention using read-only ROM and a hardwired, turn-key bootstrap
  address. Communication to the outside world is attained using an interrupt
  facility, as part of a single expansion bus that connects to both main memory
  and peripherals. An autoindexing feature allows for very tightly coded
  looping structures.

  The design is microcoded for ease of upgrading.

\section{Architecture}

The CFT is a \gls{von Neumann architecture} \gls{stored program computer}. Data
is primarily manipulated in memory, using the system's single general-purpose
internal \gls{register} as an intermediate. The design is such that up to 1,024
general purpose memory-based registers may be accessed at any time. The
computer is completely solid-state, implemented using modern 74xxx integrated
circuits and some LSI memory.

The datapath of the CFT computer is shown in~\fcf{fig-datapath}. For
simplicity, it is built around a single bus, the \IBUS. All major
registers are connected to this bus.

The computer is microcoded. This simplifies upgrading and patching the
architecture to provide new features. Microcode consists of a number
of microprograms, each handling one CFT major state or
instruction. Each microprogram consists of up to 16 24-bit
microinstructions which operate directly the various physical units in
the computer and control the connection of registers and units to the
\IBUS.

The entire architecture is built around a 16-bit word. All data and
instructions is stored in 16-bit quantities, and all registers except
two are 16 bits wide. This allows programs and data to share the same
16-bit memory, and also makes programming significantly easier. A
rational, orthogonal instruction set with 16 main instructions and a
number of sub-instructions allows for ease of programming, yet
significant versatility.

The computer has separate address spaces for memory and input/output
devices, allowing the two to be kept separate. Through microcode
alterations additional wait states may be introduced for I/O, while
leaving memory accesses fast. This also allows processor extensions to
be built in I/O space, such as multiplication and division units,
novel instructions, et cetera.

\begin{figure*}
\vspace{2em}\\
\caption[Datapath]{\label{fig-datapath} The CFT datapath is organised around a
  single internal bus, the \IBUS. The {\em \gls{Accumulator}\/} (\A, bottom
  left) is the sole general-purpose internal register of the machine
  and is operated on by most instructions. A {\em Flag Unit\/} decodes
  the value of \A{} and accepts input from the \ALU{} to provide the
  basis for flow control. The \ALU{} performs all arithmetic and logic
  operations except register increments which are handled within the
  circuitry of those major registers that require it. The {\em Link\/}
  register (\Lreg) acts as a carry out register and extends \A{} by a
  single bit for certain operations. The {\em Control Unit\/} (centre)
  interprets microcode in response the the current instruction, which
  is stored in the {\em Instruction Register\/}. The {\em I Register}
  controls the reception of interrupts. The {\em Program Counter\/}
  (\PC) holds the location in memory of the next instruction to be
  fetched. The {\em Data Register\/} is an intermediate register used
  to implement indirect memory addressing. The {\em Memory Address
    Register\/} buffers addresses and directly drives the external
  address bus. The {\em Data Bus Transceiver\/} is a simple
  transceiver unit. When necessary, it connects the \IBUS{} to the
  external data bus to facilitate memory and I/O access. Finally, the
  {\em Constant Source\/} outputs to the \IBUS{} various constant
  values needed for resetting, address vectors, and other internal
  tasks.  }
\end{figure*}

\subsection{Word Size}

The word size is 16 bits. There are no facilities for accessing
quantities smaller than one word, and no single-instruction facilities
for accessing quantities longer than one word.

In this context, one kiloWord (kWord) is $2^{10}$ or 1,024 Words.

\subsection{Data Types}

CFT defines a single data type: a 16-bit unsigned integer,
i.e. integers in the range 0–65,535. There are no instructions
explicitly intended to handle signed numbers, but two's complement
operations may still be performed and the hardware has been designed
to make this easier.

\subsection{Addressing}

The CFT architecture can address up to 64~KWords of memory, plus up to
64~KWords of I/O space\footnote{Although, for practical reasons, 1
  KWord of I/O space is more readily available.}.

\subsubsection{Memory Space}
\label{sec:memory-space}

Main memory is split up into 64 {\em \gls{Page}s\/}, each 1 KWord in
size. Instructions usually reference memory addresses relative to the
page they are executing in.

The first page, Page Zero, is given special treatment by the
instruction set. If bit 10 (starting at zero) of an instruction is
clear, addresses in Page Zero may be accessed. This is the fastest and
most convenient way of accessing memory beyond the current page. As
such, Page Zero is always used for system variables, constants and
other data that must be globally accessible.

The 128 words in Zero Page addresses \hex{0080}–\hex{00FF} (inclusive)
are so-called Autoindex \glspl{register}. Using the Autoindex addressing
mode, each time one of these addresses is referenced, it is
automatically incremented by one. This allows loops to be coded very
tightly, with index register increments happening at the microcode
level.

\begin{figure}[bt]
  \centering
  \zebrahdr
  \begin{tabular}{cl}
    \hex{0000} & \asm{SUBRET} — return address for last \instr{JSR}.\\
    \hex{0001} & \asm{TRAPRET} — return address for last \instr{TRAP}\\
    \hex{0002} & \asm{ISRRET} — return address for last ISR.\\
    \hex{0080} & \asm{IR0} — first autoindex register.\\
    \hex{00FF} & \asm{IR7F} — last (128th) autoindex register.\\
    $\vdots$ & $\vdots$ \\
    \hex{03FF} & Last word of Page Zero.\\
    \hex{1000} & First word of Page 1.\\
    $\vdots$ & $\vdots$ \\
    \hex{8000} & First word of Page 32.\\
    $\vdots$ & $\vdots$ \\
    \hex{FC00} & First word of Page 63.\\
    \hex{FFF0} & Boot/reset address.\\
    \hex{FFF8} & Interrupt service routine.\\
    \hex{FFFF} & Highest memory address.\\
  \end{tabular}
  \caption{\label{fig-mm}Memory map of the CFT CPU's memory space.}
\end{figure}

\subsubsection{I/O Space}

Although there are 64 KWords of I/O space, this is limited by practical
limitations: Only the first 1,024 I/O addresses may be accessed from anywhere
in memory space (using the R field). Due to page-relative addressing, accessing
the rest of the I/O space is mostly convenient via indirect addressing. For
speed and ease of use, most I/O devices will thus occupy the first KWord of
address space. Page-relative addressing is discussed in detail in
\cf{sec-pagerel}.

\subsection{Registers}
\label{sec:registers}

\begin{figure}[tb]
  \centering
  \inputfigure{figure-register-file}
  \caption{\label{fig-rf}Full Register file. Only the \A{} major
    register and the five flag registers are accessible to the user,
    and only \A{} is directly accessible.}
\end{figure}

There are ten \glspl{register} in the CFT architecture. They are split into
the major registers, minor registers, and flag registers. Major and minor
registers are all 16 bits wide. Flag registers are one bit wide.

\subsubsection{Major Registers}

These registers are used directly by the programming model. These are
all 16-bit registers. They hardware provides facilities for these
registers to be read, written and incremented.

\paragraph{Accumulator (\A)}
\label{sec:accumulator}

This is a 16 bit register. It is the only 16-bit register directly and
fully accessible via the instruction set and the one almost all
instructions operate on. The value of \A{} influences directly the
values of the flag registers \Nreg (negative flag) and \Zreg (zero
flag).

\paragraph{Program Counter (\PC)}

A 16-bit register. It contains the address of the next instruction to
be executed. It may not be read, but can be indirectly affected by way
of skips, jumps, subroutine calls, traps, and interrupts.

\paragraph{Data Register (\DR)}

This is a 16-bit register used internally by the CFT to buffer
addresses during indirect addressing. It cannot be accessed directly
by the user.

\subsubsection{Minor Registers}

These registers are used internally by the system, and are built with
less functionality than major registers.

\paragraph{Instruction Register (\IR)}

The Instruction Register (\IR) holds the instruction currently being
executed. It is 16 bits wide and is used internally only. There is no
way to access it.

\paragraph{Address Register (\AR)}

The Address Register (\AR) is a 16-bit register that buffers addresses
that are put out on the CFT address bus. \AR{} is responsible for all
memory and I/O addressing with the exception of indirect addressing,
which also uses the \DR. Like the \IR, the {\AR} cannot be accessed by
the user.

\subsubsection{Flag Registers}

These are single-bit flags. They are used to sense or set the state of
the system and form the basis of flow control.

\paragraph{Link Register (\Lreg)}

Used as a carry bit during arithmetic, extending the \A{} register and
as the 17th bit during roll instructions. It may be used as a generic
flag by user programs and may be set or cleared by user programs.

\paragraph{Negative Flag (\Nreg)}

Directly linked to 16th bit of the \A{} register. This register may
not be directly controlled by the programmer. If set, the \A{}
register may be negative. This, of course, depends on the
interpretation of the contents of \A{}. If treating \A{} as an
unsigned quantity, the \Nreg{} register is a good means of testing the
highest-order bit of \A{}.

\paragraph{Zero Flag (\Zreg)}

Cannot be controlled directly by the user. This flag register is set
when \A{} is zero. This is among the fastest means of numerical
comparison on the CFT architecture.

\paragraph{Overflow Flag (\Vreg)}

Cannot be controlled directly by the user. This flag is set when an
addition results in a result that will not fit in 16 bits. Its
interpretation depends on the interpretation of the value of \A.

\paragraph{Interrupt Register (\Ireg)}

This single-bit register controls the computer's behaviour on
detecting an interrupt request. The register may be manipulated by the
user to allow or mask interrupts.

\subsubsection{Page Zero Registers}

In addition to the processor registers, the programming model treats memory
addresses \hex{0000}–\hex{03FF} as 1,024 \gls{Page Zero} registers. These are
often termed simply ‘registers’ in the context of CFT Assembly. This is not
ambiguous, since Assembly only ever deals with one processor register directly,
the \gls{Accumulator}.

This is identical to the way the PDP-8 treated its own page zero, and similar
to the way the 6502 treats {\em its\/} page zero.

In practical use, a ‘register’ in this context is the equivalent of a global
variable, and it is up to the operating system to decide how \gls{Page Zero} is
laid out and utilised.

\subsection{Instruction Format}
\label{sec:instruction-format}

\begin{figure}[tb]
  \centering
  \inputfigure{figure-instruction-format}
  \caption{\label{fig-if}Instruction Format of the CFT architecture.}
\end{figure}

The CFT computer uses a single instruction format. All instructions are exactly
16 bits wide and comprise the same fields, as shown in~\fcf{fig-if}. Each
instruction contains four fields. From most to least significant, they are:

\begin{description}
\item{\bfseries The Instruction opcode (most significant 4 bits)}. This
  field identifies the instruction to be performed.
\item{\bfseries The Indirection mode (1 bit)}. Depending on the instruction,
  this bit selects between the literal and direct, or the direct and
  indirect addressing mode.
\item{\bfseries The Register Mode (1 bit)}. This bit controls whether
  addresses and literals are relative to the current page, or relative
  to page zero (the register page).
\item{\bfseries The Operand or address offset (least significant 10
  bits)}. This allows only ten bits of literals or addresses to be
  specified in an instruction. The most significant six bits are
  filled in from one of two sources as follows:
  \begin{itemize}
  \item If the Register Mode bit is set (1), the six most significant bits
    of the \PC\ register are used. This is page-relative addressing.
  \item If the Register Mode bit is clear (0), the six most
    significant bits of the operand are zero. This is Register
    addressing, also known as Page-Zero addressing, since Page Zero is
    used for system registers.
  \end{itemize}
  This introduces a number of limitations, discussed in~\cf{sec-pagerel}.
\end{description}

\subsection{Page-Relative Limitations}
\label{sec-pagerel}

Unless the Register Mode (R) bit is set (field R in the instruction
equal to \bin{1}), an instruction at address {\ttfamily addr} may only access
memory (and I/O) address between {\ttfamily addr AND FC00} and {\ttfamily (ADDR
  AND FC00) OR 3FF}. This introduces a number of limitations and
defines the programming style of CFT more than any other single aspect
of the design.

There are four obvious solutions to the limitation:

Subprograms need to store temporary data on the local page, or to use
special ‘scratch’ registers in Page Zero. Both \glspl{Addressing Mode}
take the same time to execute.

In the case of constants, the programmer can either limit themselves
to constants in the range \hex{0000}–\hex{03FF}, store commonly-used
large constants (such as -1, \hex{FFFF} and -2, \hex{FFFE}) in a Page
Zero constant table, or a combination of these techniques\footnote{A
  note for PDP-8 programmers: the CFT has a \instr{LI} (Load Immediate
  or LIteral) instruction that can load the \gls{Accumulator} with a 10-bit
  literal. This is considerably faster the the only PDP-8 alternative,
  constructing basic constants using microcoded instructions.}.

Special care needs to be taken for subprograms longer than 1,024
words. If code crosses a page boundary, references to any local data
will in fact refer to the same offset within the {\em new\/} page, and
will of course be invalid.

The standard assembler issues a cross-page warning when using symbolic
names (labels) for such local data, which is a very good practice.

Jumps, subroutine calls and traps suffer from the same issue. Indirect
Register addressing is commonly used as a solution to this problem:
the address (vector) of the subprogram in question is stored in a Page
Zero location, and the jump is made using indirection. This has the
added benefit of allowing the vectors to be changed so that system
services may be overridden.

Perhaps the most significant limitation, however, is on the size of the I/O
address space. When performing page-relative I/O operations (\instr{IN},
\instr{OUT} and \instr{IOT}), the most significant six bits of the I/O
address will {\em still\/} be taken from the six most significant bits of
the \PC. Because of this, different I/O devices will be accessed depending on
the location of the program in memory. There are two ways to avoid this: the
primary one is to only use 10 bits of I/O space. Either the R field in all I/O
instructions must be \bin{1}, or the hardware must decode only the 10 least
significant address lines\footnote{Thus providing six don't care bits, which is
64 copies of every I/O device, one for every page.}, or a combination of
both. The secondary means of avoiding this issue is indirect addressing. It is
assumed that a mixture of these techniques will be used in practice. Please
refer to your system documentation for exact details.

\subsection{Addressing Modes}
\label{sec:addressing-modes}

CFT instructions have two bits that modify how instructions interpret the
operand field: the R (register) field, and the I (indirection) field.

The R field controls how the six most significant bits of the operand are
derived, as described in~\cf{sec:instruction-format}. When R is \bin{0}, the
six most significant bits of the \PC{} are used to form the default,
page-relative modes\footnote{Please note that ‘page-relative’ is the default
  and not indicated in the names of \glspl{Addressing Mode}.}. When R is
\bin{1}, the six most significant bits of the address are \bin{000000},
addressing \gls{Page Zero} (\hex{0000}–\hex{03FF}), and thus accessing
\gls{Page Zero} registers.

The I field controls how the resultant operand is used. This depends on the
instruction, but in most cases, setting the I field adds one level of
indirection to the operation.

Combined, these two bits allow up to four \glspl{Addressing Mode} per
instruction. An additional Autoindex variant mode is available for most
instructions. This is automatically enabled when both I and R fields are set,
and addresses in the range \hex{0080}–\hex{00FF} are used.

Thus, most instructions support up to five addressing modes from the full range
of fourteen. No instruction supports all addressing modes, and some instructions
perform tasks that do not conform to the canonical definition of ‘addressing
mode’. These ignore either or both of the R and I fields. The addressing modes
are tabulated by instruction type and number of memory accesses
in~\tcf{table:addressing-modes}.

Despite this somewhat limited model, because of the microcoded nature of the
CFT, a surprising 14 addressing modes are available, some of which are quite
complex:

\begin{itemize}
  \item Immediate (\cfp{sec:immediate-mode}).
  \item Address (\cfp{sec:address-mode}).
  \item Register Address (\cfp{sec:register-address-mode}).
  \item Indirect Address (\cfp{sec:indirect-address-mode}).
  \item Register Indirect Address (\cfp{sec:register-indirect-address-mode}).
  %% Not possible with 2013-02-19 changes to Autoindex circuit.
  %%\item Autoindex Address (\cfp{sec:autoindex-address-mode}).
  \item Autoindex Address (\cfp{sec:autoindex-address-mode}).
  \item Direct (\cfp{sec:direct-mode}).
  \item Register Direct (\cfp{sec:register-direct-mode}).
  \item Indirect (\cfp{sec:indirect-mode}).
  \item Register Indirect (\cfp{sec:register-indirect-mode}).
  %% Not possible with 2013-02-19 changes to Autoindex circuit.
  %%\item Autoindex (\cfp{sec:autoindex-mode}).
  \item Autoindex (\cfp{sec:autoindex-mode}).
  \item Conditional (\cfp{sec:conditional-mode}).
  \item Double Indirect (\cfp{sec:double-indirect-mode}).
  \item Autoindex Decrement (\cfp{sec:autoindex-decrement-mode}).
\end{itemize}

\begin{table}
  \centering
  \zebra
  \begin{tabular}{l*{2}{>{\textsf\bgroup}c<{\egroup}}cl}
    Addressing Mode & I & R & MC & Notes \\
    %\noalign{\smallskip}\hline\noalign{\smallskip}
    \hline
    Address                    & X & 0 & 0 & \instr{LIA} instruction only. \\
    Immediate                  & X & 1 & 0 & \instr{LI} macro only. \\
    %
    %
    Address                    & 0 & 0 & 0 & Flow control instructions. \\
    Register Address           & 0 & 1 & 0 & Flow control instructions. \\
    %
    Indirect Address           & 1 & 0 & 1 & Flow control instructions. \\
    Register Indirect Address  & 1 & 1 & 1 & Flow control instructions. \\
    %
    Autoindex Address          & 1 & 1 & 2 & Flow control instructions. \\
    %
    %
    Direct                     & 0 & 0 & 1 & Memory, I/O, Arithmetic \& Logic instructions. \\
    Register Direct            & 0 & 1 & 1 & Memory, I/O, Arithmetic \& Logic instructions. \\
    %
    Indirect                   & 1 & 0 & 2 & Memory, I/O, Arithmetic \& Logic instructions. \\
    Register Indirect          & 1 & 1 & 2 & Memory, I/O, Arithmetic \& Logic instructions. \\
    %
    Autoindex                  & 1 & 1 & 3 & Memory, I/O, Arithmetic \& Logic instructions. \\
    %
    %
    Conditional                & X & X & - & \instr{OP1} and \instr{OP2} instructions. \\
    %
    Double Indirect            & X & X & 0 & \instr{JMPII} instruction. \\
    \hline
  \end{tabular}

  \caption[Effective Addressing Modes]{\label{table:addressing-modes}Effective
  Addressing Modes based on behaviour and number of memory accesses (and hence
  timing). The ‘MC’ column shows the number of memory cycles required in each
  addressing mode, excluding the instruction fetch. Note that ‘memory cycle’ is
  used loosely: it does not apply exactly to I/O instructions.}
\end{table}

\subsubsection{Immediate Mode}
\label{sec:immediate-mode}

When using applicable instructions with R=1 and I=0, the value field
in the instruction is used as the least significant 10 bits of a
literal value. The most significant six bits are zero. This allows
literal values in the range \hex{0000}–\hex{03FF} to be
specified. This is illustrated in~\fcf{fig:immediate-mode}.

For example, executing the Load Immediate (\asm{LI R}) instruction \asm{LI R
0350} will set \A=\hex{0350}.

This addressing moed does not involve any memory cycles aside from the
instruction fetch.

\begin{figure}[htb]
 \centering
 \inputfigure{figure-immediate-mode}    
\caption[Immediate Mode]{\label{fig:immediate-mode} Operation of Immediate
  Mode. The \AC{} is loaded with the bit pattern in the operand field of the
  \IR. The six most significant bits are zeroed. This addressing mode is only
  used by the \asm{LIA R} instruction, commonly used as the Load Immediate
  macro, \instr{LI}.}
\end{figure}

\subsubsection{Address Mode}
\label{sec:address-mode}

When using applicable instructions with R=0 and I=0, the value field in the
instruction is used as the least significant 10 bits of a literal value. The
most significant six bits are taken from the \PC to generate an address
relative to the current page's origin. This is illustrated
in~\fcf{fig:address-mode}.

For example, executing the instruction \asm{JMP 9} at address \hex{FFF8} (page
\hex{3F}, page origin \hex{FC00}) would set the \PC{} to \hex{FC09}.

Like Immediate mode, this addressing mode does not involve any memory cycles
aside from the instruction set. Address Mode is used by the \instr{LIA} (Load
Immediate Address) instruction, and by all flow control instructions
(\instr{TRAP}, \instr{JSR} and \instr{JMP}).

\begin{figure}[htb]
 \centering
 \inputfigure{figure-address-mode}
\caption[Address Mode]{\label{fig:address-mode} Operation of Address Mode. The
  \AC{} (or \PC{}, in the case of flow control instructions) is loaded with the
  bit pattern in the operand field of the \IR. The six most significant bits
  are taken from the six most significant bits of the \PC, forming the current
  page number.}
\end{figure}

\subsubsection{Register Address Mode}
\label{sec:register-address-mode}

Register Address Mode is functionally equivalent to the Immediate Mode. It is
used by flow control instructions with I=0 and R=1 to specify addresses in
\gls{Page Zero}. Like Immediate Mode, the 10-bit instruction operand is padded
with zeroes to 16 bits and used directly as an address. This is shown
in~\fcf{fig:register-address-mode}.

Register Address Mode instructions only apply to the \PC, while the single
Immediate Mode instruction applies to the \AC.

Like Immediate Mode,this addressing moed does not involve any memory cycles
aside from the instruction fetch.

\begin{figure}[htb]
 \centering
 \inputfigure{figure-register-address-mode}    
 \caption[Register Address Mode]{\label{fig:register-address-mode} Operation
   of Register Address Mode.}
\end{figure}

\subsubsection{Indirect Address Mode}
\label{sec:indirect-address-mode}

Indirect Address Mode is used for jumptables, subroutine vectors, or C's
equivalent of function pointers. It is used by flow control instructions and
selected when I=1 and R=0. The instruction operand specifies a page-relative
memory address. The memory at this address contains the address to load into
the \PC.

The semantics of this are $\mbox{\PC}\eq\mem{a}$, where $a$ is the
page-relative address in the instruction operand. This is shown
in~\fcf{fig:indirect-address-mode}.

This addressing mode involves one memory read cycle in addition to the one
required to fetch the instruction.

\begin{figure}[htb]
 \centering
 \inputfigure{figure-indirect-address-mode}    
\caption[Indirect Address Mode]{\label{fig:indirect-address-mode} Operation
  of Indirect Address Mode.}
\end{figure}

\subsubsection{Register Indirect Address Mode}
\label{sec:register-indirect-address-mode}

Register Indirect Address Mode works in the same way as Indirect Address Mode,
except in that memory is indexed by a Page Zero address, not a page-relative
address. It is selected for flow control instructions when I=1 and R=1 and can
be used to reference operating system-wide jump tables or subroutine vectors in
Page Zero.

The semantics are $\mbox{\PC}\eq\mem{r}$, where $r$ is the \gls{Page Zero}
address in the instruction operand (in the range \hex{000}–\hex{3FF}). The
addressing mode is illustrated in~\fcf{fig:register-indirect-address-mode}.

This addressing mode is used by the standard macros \instr{RET} (return from
subroutine) and \instr{RTT} (return from trap), since these instructions save the
return address in \gls{Page Zero}. Register Indirect Address mode is then used
to jump to the address stored in the corresponding Zero Page address from
anywhere in memory. It requires one memory read cycle in addition to the fetch
cycle.

\begin{figure}[htb]
 \centering
 \inputfigure{figure-register-indirect-address-mode}    
\caption[Register Indirect Address Mode]{\label{fig:register-indirect-address-mode} Operation
  of Register Indirect Address Mode.}
\end{figure}

%% \subsubsection{Autoindex Address Mode}
%% \label{sec:autoindex-address-mode}

%% Autoindex Address Mode is selected for flow control instructions when I=1, R=0
%% and the address referenced is between \hex{0080} and \hex{00FF}. This
%% addressing mode is less than useful: Autoindex Address mode will not be
%% selected in page-relative mode unless the code is running {\em in\/} \gls{Page
%%   Zero} (addresses \hex{0000}–\hex{03FF}). This is an unusual situation, so it
%% is more common to encounter Register Autoindex instead\footnote{Though still
%%   not very common at all.}.

%% The mode works very much like Indirect Address Mode
%% (\cfp{sec:indirect-address-mode}). It sets the \PC to the value found by reading
%% from the memory address specified in the instruction operand. The difference is
%% that this memory address will then be incremented. Understandably, this is not
%% a very useful addressing mode, and exists less as a direct design decision and
%% more as a side-effect of the way \glspl{Addressing Mode} work on the CFT.

%% The semantics are $\mbox{\PC}\eq\mem{a}, \mem{a}\eq\mem{a}+1$, where $a$ is the
%% page-relative address in the instruction operand, $\mbox{\hex{0080}}\leq a\leq
%% \mbox{\hex{00FF}}$. This addressing mode requires, in addition to the fetch
%% memory cycle, one read memory cycle (to obtain the value for the \PC) and one
%% write memory cycle (to update the incremented value).

%% \begin{figure}[htb]
%%  \centering
%%  \input{figure-autoindex-address-mode}    
%% \caption[Autoindex Address Mode]{\label{fig:autoindex-address-mode} Operation
%%   of Autoindex Address Mode.}
%% \end{figure}

\subsubsection{Autoindex Address Mode}
\label{autoindex-address-mode}

Autoindex Address Mode is selected for flow control instructions when
I=1, R=1 and the address referenced is between \hex{0080} and
\hex{00FF}. This is an exotic, less commonly needed mode. It is
illustrated in~\fcf{fig:autoindex-mode}.

The mode sets the \PC to the value found by reading from the \gls{Page
  Zero} memory address specified in the instruction operand. The
memory location read is incremented after being used.

The semantics are $\mbox{\PC}\eq\mem{r}, \mem{r}\eq\mem{r}+1$, where
$r$ is the Page Zero address in the instruction operand,
$\mbox{\hex{0080}}\leq r\leq \mbox{\hex{00FF}}$. This addressing mode
requires, in addition to the fetch memory cycle, one read memory cycle
(to obtain the value for the \PC), and one write memory cycle (to
update the incremented value).

\begin{figure}[htb]
 \centering
 \inputfigure{figure-autoindex-address-mode}    
\caption[Autoindex Address Mode]{\label{fig:autoindex-address-mode} Operation
  of Autoindex Address Mode.}
\end{figure}

\subsubsection{Direct Mode}
\label{sec:direct-mode}

Direct Mode is one of the most useful and commonly used addressing modes. It is
used in memory, I/O, arithmetic and logic instructions when I=0 and R=0. It
interprets the instruction operand as a page-relative address in memory. The
\AC{} is assigned the value read from this address in memory. The operation of
the \gls{Addressing Mode} is shown in~\fcf{fig:direct-mode}.

The semantics for most such instructions are $\mbox{\AC}\eq\mem{a}$, where $a$
is the page-relative address to load. There are some exceptions for complex
instructions (\instr{ISZ} and \instr{IOT}) and write instructions (\instr{STORE} and
\instr{OUT}), but these are discussed further on.

Direct mode usually requires one additional memory or I/O cycle in addition to
the one used to fetch the instruction.

\begin{figure}[htb]
 \centering
 \inputfigure{figure-direct-mode}
\caption[Direct Mode]{\label{fig:direct-mode} Operation of Direct Mode.}
\end{figure}

\subsubsection{Register Direct Mode}
\label{sec:register-direct-mode}

Register Direct Mode is one of the most useful and commonly used addressing
modes. It is used in memory, I/O, arithmetic and logic instructions when I=0
and R=1. It interprets the instruction operand as a \gls{Page Zero} address,
which is used to read from memory or I/O space. The \AC{} is assigned the value
read. The operation of the \gls{Addressing Mode} is shown
in~\fcf{fig:register-direct-mode}.

The semantics for most such instructions are $\mbox{\AC}\eq\mem{r}$, where $r$
is the Page Zero address to read. There are some exceptions for complex
instructions (\instr{ISZ} and \instr{IOT}) and write instructions (\instr{STORE} and
\instr{OUT}), but these are discussed further on.

Like Direct mode, Register Direct mode usually requires one additional memory
or I/O cycle in addition to the one used to fetch the instruction.

\begin{figure}[htb]
 \centering
 \inputfigure{figure-register-direct-mode}    
 \caption[Register Direct Mode]{\label{fig:register-direct-mode} Operation
   of Register Direct Mode.}
\end{figure}

\subsubsection{Indirect Mode}
\label{sec:indirect-mode}

This complex addressing mode is illustrated in~\fcf{fig:indirect-mode}. Like
Direct mode, it is a very useful \gls{Addressing Mode} and employed in a wide
range of functions. The mode is selected for Memory, I/O, Arithmetic and Logic
instructions when I=0 and R=0. The instruction operand is treated as a
page-relative memory address. The memory location specified is read to obtain
an address which is then operated on by the instruction. This is the CFT
equivalent of a C or Pascal pointer.

The semantics for a memory read instruction in Indirect Mode are
$\mbox{\AC}\eq\memmem{a}$, where $a$ is the page-relative address specified in
the instruction operand.

The Indirect addressing mode obviously requires one memory read cycle and one memory or
I/O read or write cycle (depending on the instruction), in addition to the
memory cycle needed to fetch the instruction.

\begin{figure}[htb]
 \centering
 \inputfigure{figure-indirect-mode}
 \caption[Indirect Mode]{\label{fig:indirect-mode} Operation
   of Indirect Mode.}
\end{figure}

\subsubsection{Register Indirect Mode}
\label{sec:register-indirect-mode}

This addressing mode works like Indirect Mode, but accesses data whose address
is stored in a Page Zero location. It is selected when a Memory, I/O,
Arithmetic or Logic instruction is executed with I=0 and R=1. The instruction
operand is treated as a Page Zero memory address, which is read to obtain an
address which is then operated on by the instruction. This is the CFT
equivalent of a C or Pascal pointer.

The semantics for a memory read instruction in Indirect Mode are
$\mbox{\AC}\eq\memmem{r}$, where $r$ is the Page Zero address specified in the
instruction operand.

The Register Indirect addressing mode requires one memory read cycle and one
memory or I/O read or write cycle (depending on the instruction), in addition
to the memory cycle needed to fetch the instruction.

\begin{figure}[htb]
 \centering
 \inputfigure{figure-register-indirect-mode}
\caption[Register Indirect Mode]{\label{fig:register-indirect-mode} Operation
  of Register Indirect Mode.}
\end{figure}

\subsubsection{Autoindex Mode}
\label{sec:autoindex-mode}

This is the most complex \gls{Addressing Mode} available on the
CFT. It is used when a Memory, I/O, Arithmetic or Logic instruction is
executed with I=1, R=1 and an operand in the range
\hex{080}–\hex{0FF}.

The addressing mode works like Indirect mode, but the memory location read is
incremented after use. This allows the CFT to manipulate contiguous blocks of
data in a very compact manner, without having to increment a pointer
explicitly, saving three instructions per loop iteration. For a load
instruction, the C equivalent would be \cftin{ac = memory[i++]}, where
\cftin{i} is the value at the memory location of the instruction operand. The
value at the memory location can be seen as an index pointer.

Even though the instruction set has not yet been discussed, a short example can
show how to set up a pointer to an array of words, and add the first four of
them using Autoindexing.

\begin{cftasmcode}
&20:                 ; Assemble code at address 32 (decimal).
        LI &300      ; AC = 768 (decimal)
        STORE &80    ; Store 768 at mem[128].
        LOAD I &80   ; AC = mem[mem[128]], i.e. AC = mem[768]
        ADD I &80    ; AC = AC + mem[769]
        ADD I &80    ; AC = AC + mem[770]
        ADD I &80    ; AC = AC + mem[771]
\end{cftasmcode}

The mode is illustrated in~\fcf{fig:autoindex-mode}. In addition to the memory
read cycle needed to fetch the instruction, it requires one memory read cycle
to fetch the index pointer from memory, one or more memory or I/O cycles as
dictated by the instruction, plus one memory write cycle to write back the
incremented index pointer.

\begin{figure}[htb]
 \centering
 \inputfigure{figure-autoindex-mode}    
\caption[Autoindex Mode]{\label{fig:autoindex-mode} Operation
  of Autoindex Mode.}
\end{figure}

%% \subsubsection{Register Autoindex Mode}
%% \label{sec:register-autoindex-mode}

%% This \gls{Addressing Mode} is illustrated
%% in~\fcf{fig:register-autoindex-mode}. It is used for Memory, I/O, Arithmetic
%% and Logic instructions when I=1 and R=1. It works like Autoindex mode, except
%% in that the instruction operand identifies a location in \gls{Page Zero}.

%% Since the location {\em must\/} be in Page Zero, and specifically between
%% \hex{0080} and \hex{00FF}, this way of leveraging autoindex mode is used almost
%% exclusively on the CFT.

%% In addition to the memory read cycle needed to fetch the instruction, it
%% requires one memory read cycle to fetch the index pointer from memory, one or
%% more memory or I/O cycles as dictated by the instruction, plus one memory write
%% cycle to write back the incremented index pointer.

%% \begin{figure}[htb]
%%  \centering
%%  \input{figure-register-autoindex-mode}    
%% \caption[Register Autoindex Mode]{\label{fig:register-autoindex-mode} Operation
%%   of Register Autoindex Mode.}
%% \end{figure}

\subsubsection{Conditional Mode}
\label{sec:conditional-mode}

This mode is not an actual {\em addressing} mode, in that it does not address
memory. The two instructions that use this, \instr{OP1} and \instr{OP2} treat the
instruction operand as a 10-bit vector. Each bit, or in some cases groups of
bits, may be set to conditionally perform a particular task, one task per
processor cycle. Available tasks include clearing or complementing the \AC,
manipulating various flags, carrying out rolls and shifts, and conditonal flow
control.

If no bits are set, the instruction does nothing. If all bits are set, all of
the instruction's minor operations are performed, one at a time, in a
predefined order.

For more information, please refer to~cf{sec:op1} and cf{sec:op2}. The concept
of these instructions comes straight from the PDP-8's ‘microcoded’ instructions
(the term does not denote microcode in the commonly understood sense of the
word).

\subsubsection{Double Indirect Mode}
\label{sec:double-indirect-mode}

This mode is only supported by the \asm{JMPII} instruction, which supports no
other modes except Double Indirect and Autoindex. \asm{JMPII} is a variant of
\asm{JMP} that performs two indirection steps.

\todo{Draw diagram}

\subsubsection{Autoindex Decrement Mode}
\label{sec:autoindex-decrement-mode}

This mode is only supported by the \asm{DAL} instruction, also known as
\asm{POP}. It decrements the value at the memory address specified in the
instruction operand, stores the value back to memory, then uses that value.

\todo{Draw diagram}

\subsection{Operating States}

The CFT processor has four major operating states, discussed in detail
in~cf{sec:major-states}: Reset, Fetch, Execute, Interrupt and Stop.

\subsubsection{Reset}

When the computer initialises via a system reset or initial boot, it first
clears the major registers \A, \PC{} and \DR{}. Shortly after the reset pulse,
\PC{} is loaded with the boot address \hex{FFF0} and the \Ireg\ register is
cleared in order to disallow interrupts.  Other registers and machine states
are undefined and may contain arbitrary values — naturally, boot code should
initialise all of the system as early as possible. Normal operation is then
resumed.

\subsubsection{Fetch and Execute}

During normal fetch-execute operation, the computer's microcode fetches
instructions from the main memory address stored in the \PC, increments the
\PC, then executes the fetched instructions. This is the state the computer
spends most of its time in.

\subsubsection{Interrupt}

When the computer encounters an interrupt, and if the \Ireg\ register is {\ttfamily
  1} (allowing interrupts), the event is buffered in a minor state
register. When the currently executing instruction is completed, the
\Ireg\ register is cleared to disable further interrupts and the current value
of the \PC\ is written to memory address \hex{0002}. Finally, the \PC\ is
loaded with the value \hex{FFF8}, which is the address of the Interrupt Service
Routine (ISR). Normal operation is then resumed.

\subsubsection{Stop}

On occasion, external slow hardware or the operator's console may halt the
processor's clocks. In this state, the sequencer does not work through the
microcode and the computer does not operate.

This mode may be entered at any time. The Programmer's Front Panel
(\ccfp{chap:pfp}) and Debugging Board (\ccfp{chap:deb}) allow it to be entered
either inside a microprogram, or immediately before the fetch state.

The Wait State is transient: as soon as the appropriate signals are de-asserted
by the hardware, the previous state resumes.

\section{Instruction Set Reference}
\label{sec:instruction-set-reference}

The first edition of the CFT microcode allowed for fourteen different
instructions. The second edition added the \instr{IOT} instruction,
which makes for fifteen mutually orthogonal instructions:

\begin{itemize}
\item \instr{TRAP}: save the \PC\ and jump to the specified location. Used
  for operating system services. (\cfp{sec:instruction-TRAP})
\item \instr{IOT}: write accumulator to a specified output device, then
  read a result back from it. Used to implement computer extensions via
  I/O-addressable extension units. (\cfp{sec:instruction-IOT})
\item \instr{LOAD}: load accumulator from memory. Introduced in version 2.0
  of the microcode. (\cfp{sec:instruction-LOAD})
\item \instr{STORE}: write accumulator to memory. (\cfp{sec:instruction-STORE})
\item \instr{IN}: read accumulator from an input device. (\cfp{sec:instruction-IN})
\item \instr{OUT}: write accumulator to an output device. (\cfp{sec:instruction-OUT})
\item \instr{JMP}: unconditional jump to the specified location. (\cfp{sec:instruction-JMP})
\item \instr{JSR}: save the \PC{} and jump unconditionally to the specified
  location. (\cfp{sec:instruction-JSR})
\item \instr{ADD}: load from memory and add to the
  accumulator. (\cfp{sec:instruction-ADD})
\item \instr{AND}: load from memory and perform a bitwise AND with the
  value in the accumulator. (\cfp{sec:instruction-AND})
\item \instr{OR}: load from memory and perform a bitwise OR with the value
  in the accumulator. (\cfp{sec:instruction-OR})
\item \instr{XOR}: load from memory and perform a bitwise exclusive OR with
  the value in the accumulator. (\cfp{sec:instruction-XOR})
\item \instr{OP1}: minor operations, group one. (\cfp{sec:instruction-OP1})
\item \instr{OP2}: minor operations, group two. (\cfp{sec:instruction-OP2})
\item \instr{ISZ}: new in version 4.0 of the microcode, replacing the
  previous \op{INCM} insruction. Loads a memory value into \A, increments it,
  and writes it back. The incremented value remains in \A{}. If \A{} is zero,
  the next instruction is skipped. This simplifies coding
  loops. (\cfp{sec:instruction-ISZ})
\item \instr{LIA}: load accumulator with literal value or
  address. (\cfp{sec:instruction-LIA})
\end{itemize}

To simplify understanding of the instruction set, opcode mnemonics are
used rather than actual machine code. In many cases, the notation used
is that of the Standard CFT Assembly language which merits some
description. This is not a full definition of CFT Assembly language,
merely enough of it to facilitate discussing the instruction set in
a more human-readable form.

CFT Assemblers parse lexical tokens denoting either symbolic
instruction names or hexadecimal numbers. Symbols are converted to
numbers using symbol tables. The resultant numbers, which must be 16
bits in width, are ORred together to form an instruction%
% (no longer the case)
%% \footnote{One
%%   exception is the \instr{R} symbol, which {\em clears\/} bit 10 of the
%%   instruction to turn on Page Zero/register addressing modes. In
%%   practice, this is not actually an exception. After assembling an
%%   instruction, however, the Assembler performs an \instr{XOR} with the
%%   hexadecimal value \hex{0400} (complementing bit 10), which allows
%%   the bitwise Or semantics to work for everything, including the R
%%   flag, and the resultant code to run as expected.}
.

This provides great simplicity and generality at the expense of making
the code slightly less readable from a modern Assembly
perspective\footnote{PDP-8 Assembly programmers will feel right at
  home, though.}).

Anything after the first semicolon (\asm{;}) on a line is considered a comment
and ignored.

A brief example of CFT Assembly language can be found in~\fcf{fig-asm}.

\begin{figure}
\small
\begin{cftasmcode}
LOAD 0000     ; Load direct
LOAD I 0342   ; Load indirect
0342 I LOAD   ; Valid, but against conventions.
LOAD I R 007F ; Load zero page and indirect
LOAD I R 0080 ; Load, autoindexing
IN R PANEL 0  ; Read panel switches
CLL RBL       ; Shift left one bit
HALT          ; Halt the system
\end{cftasmcode}
\caption{\label{fig-asm}Examples of CFT instructions in Assembly language .}
\end{figure}

\subsection{Memory}

The following instructions operate on memory space.

\newcommand\AMGroupOne{Direct, Register Direct, Indirect, Register Indirect,
  Autoindex and Register Autoindex\ }

\newcommand\AMGroupTwo{Address, Register Address, Indirect Address, Register
  Indirect Address, Autoindex Address, and Register Autoindex Address\ }

\subsubsection{\asm{LOAD} — Load Accumulator}
\label{sec:instruction-LOAD}

Load a word from memory into \A. \AMGroupOne modes are available.

\subsubsection{\asm{POP} — Decrement and Load}

Added as of Microcode version 6, this instruction is useful in implementing
stacks upwards growing stacks. The location specified is decremented, and its
value is used to address memory. The value at the addressed location is loaded
into the Accumulator.

The canonical name of this instruction is \asm{DAL}, but \asm{POP} is a common
alias. The only mode used with this instruction is the unique Autoindex
Decrement mode, which is selected regardless of the value of R and the
instruction operand. I must always be 1 to use this instruction, but this is
implicit in the machine code value of this instruction (\hex{D800}).

The instruction is meant to be the opposite of {\asm STORE} in Autoindex
Mode. Where that instruction is often used to implement a single-instruction
stack push, \asm{DAL} can be used to implement the corresponding pop.

\label{sec:instruction-LOAD}

Load a word from memory into \A. \AMGroupOne modes are available.

\subsubsection{\asm{STORE} — Store Accumulator}
\label{sec:instruction-STORE}

Write \A\ to the specified memory location. \AMGroupOne modes are available.

\subsubsection{\asm{ISZ} — Increment memory and Skip if Zero}
\label{sec:instruction-ISZ}

Load a word from memory into \A. Increment \A{}, and write its value back to
the same memory location. \AMGroupOne modes are available. In the autoindex
modes, autoincrement occurs only once — after the memory write. After the
memory write, if \AC{} is zero, the next instruction is skipped. This allows
loops to be coded very tightly, using two instructions to set up the loop, and
two instructions to iterate:

\begin{cftasmcode}
start:  NEG          ; AC = -AC
        STORE R 10   ; Loop variable
loop:   
        ...          ; Loop body
        ISZ R 10     ; ++loop
        JMP loop     ; Skipped if R 10 == 0.
        ...          ; Exit from loop
\end{cftasmcode}

\subsection{I/O}

The following instructions operate on I/O space.

\subsubsection{\asm{IN} — Read from I/O Device}
\label{sec:instruction-IN}

Read a word from I/O space into \A. \AMGroupOne modes are available. \asm{IN}
instructions may have additional side-effects that depend on the peripheral
being addressed.

\subsubsection{\asm{OUT} — Write to I/O Device}
\label{sec:instruction-OUT}

Write the contents of \A\ to the specified I/O space address. \AMGroupOne modes
are available. \instr{OUT} instructions almost always have side-effects that
depend on the peripheral being addressed.

\subsubsection{\asm{IOT} — I/O Transaction}
\label{sec:instruction-IOT}

Implements a processor extension. The \instr{IOT} instruction writes A to I/O
space, the reads \A{} back from the same address. The I/O-mapped processor
extension can introduce wait states at the end of the I/O space read cycle, in
order to get more time to perform its task. \AMGroupOne modes are available.

\subsection{Arithmetic and Logic}

The following instructions perform common arithmetic and logic
operations. \AMGroupOne modes apply to this group of instructions.

\subsubsection{\asm{ADD} — Add to Accumulator}
\label{sec:instruction-ADD}

Read a word from memory and add it to \A. If the addition results in a
carry-out, \Lreg\ is toggled. \AMGroupOne modes are available.

\subsubsection{\asm{AND} — Bitwise And with Accumulator}
\label{sec:instruction-AND}

Read a word from memory and perform a bitwise AND operation with A. Direct,
\AMGroupOne modes are available.

\subsubsection{\asm{OR} — Bitwise Or with Accumulator}
\label{sec:instruction-OR}

Read a word from memory and perform a bitwise OR operation with A. \AMGroupOne
modes are available.

\subsubsection{\asm{XOR} — Bitwise Exclusive OR with Accumulator}
\label{sec:instruction-XOR}

Read a word from memory and perform a bitwise XOR operation with A. \AMGroupOne
modes are available.

\subsection{Flow Control}

The following instructions implement flow control via modification of the
\PC\ register.

\subsubsection{\asm{TRAP} — Jump to System Service}
\label{sec:instruction-TRAP}

Writes the value of the \PC{} to memory location \hex{0001}, then sets the \PC
to the address specified in the instruction. \AMGroupTwo modes are available.

\subsubsection{\asm{JMP} — Jump to Address}
\label{sec:instruction-JMP}

Sets the \PC{} to the address specified in the instruction. \AMGroupTwo modes
are available.

\subsubsection{\asm{JMPII} — Jump to Address with Double Indirection}
\label{sec:instruction-JMPII}

Sets the \PC{} to the address specified at the location pointed to by the
address specified in the operand. This instruction is useful in executing
chains of subroutines in a table, such as compiled Forth words. A pointer to
the next location to jump to is stored in memory, and \asm{JMPII} is used to
dereference that address twice and jump to it.

Double Indirect and Autoindex modes are available. In Autoindex mode, the
pointer is incremented after setting the PC. This allows a Forth inner
interpreter to be written in a single instruction and is similarly invaluable
in executing other interpreted, tokenised languages such as BASIC.

\subsubsection{\asm{JSR} — Jump to Subroutine}
\label{sec:instruction-JSR}

Writes the value of the \PC{} to memory location \hex{0000}, then sets the
\PC{} to the address specified in the instruction. \AMGroupTwo modes are
available.

\subsection{Specials}

These are operations that do not fit in the categories above.

\subsubsection{\asm{OP1} — Operations 1}
\label{sec:op1}

\begin{figure*}[tb]
  \centering
  \inputfigure{figure-rolls}

  \caption{\label{fig-roll}Roll Instructions.}
\end{figure*}

The \instr{OP1} instruction provides a number of minor operations, any number
of which may be performed in a preset order. This is very similar to the PDP-8
‘microcoded’ instructions. It does not technically address memory, but this
instruction uses the Conditional addressing mode.

The operand of the \instr{OP1} instruction is seen as a bitfield, where
set bits trigger a particular minor operation. The table below
outlines the possible operations that can be ORred together.

\vspace{1em}\noindent\begin{center}
\zebra
\begin{tabular}{ll}
  Bitfield & \instr{OP1} Instruction \\\noalign{\smallskip}\hline%\noalign{\smallskip}
  \texttt{1---------} & \asm{IFL} — Execute the rest only if \Lreg{} set.\\
  \texttt{-1--------} & \asm{IFV} — Execute the rest only if \Vreg{} set.\\
  \texttt{--1-------} & \asm{CLA} — Clear \A \\
  \texttt{---1------} & \asm{CLL} — Clear \Lreg \\
  \texttt{----1-----} & \asm{NOT} — Complement \A \\
  \texttt{-----1----} & \asm{INC} — Increment (\Lreg,\A) by one. \\
  \texttt{------1---} & \asm{CPL} — Complement \Lreg \\
  \texttt{-------010} & \asm{RBL} — Roll Bit Left (\Lreg,\A) \\
  \texttt{-------001} & \asm{RBR} — Roll Bit Right (\Lreg,\A) \\
  \texttt{-------110} & \asm{RNL} — Roll Nybble Left (\Lreg,\A) \\
  \texttt{-------101} & \asm{RNR} — Roll Nybble Right (\Lreg,\A) \\\hline
\end{tabular}
\end{center}\vspace{1em}

These operations is performed in the order in which they appear above,
from top to bottom. If no operations are specified, i.e. the
instruction is \hex{C000}, the instruction is effectively a NOP. The
four roll instructions are mutually exclusive. The notation (\Lreg,\A)
indicates that both \Lreg\ and \A\ are used together as a 17-bit
quantity, with \Lreg\ becoming the most significant bit.

The first two operations end execution of the rest of the instruction
unless the \Lreg{} and \Vreg{} are set, respectively. These operations
simplify the rippling of carry, borrow or overflow effects.

To clear both \A{} and \Lreg, the instruction would be \asm{OP1 CLA CLL}.

If the \asm{INC} instruction is issued when \A=\hex{FFFF}, \Lreg\ is
toggled. As expected, \A\ becomes \hex{0000}.

To calculate the two's complement of \A{} \asm{OP1 NOT INC} (hexadecimal
instruction \hex{C030}) will first invert \A{}, then increment it by
one. Note that \asm{OP1 INC NOT} has exactly the same result, as the
order in which minor operations are performed is fixed.

A binary left shift by one bit can be defined as \asm{OP1 CLL RBL}
(\hex{C102}).

The standard Assembler defines many of these combinations of instructions as
convenient macros. When using these macros, specifying \instr{OP1} is optional.

The exact operation of the four roll instructions is illustrated
in~\npfcf{fig-roll}.

\subsubsection{\asm{OP2} — Operations 2}
\label{sec:instruction-OP2}

This instruction is very similar to the \instr{OP1} instruction. The main
feature of the \instr{OP2} instruction is skipping. Skip instructions skip over
the following instruction if the corresponding condition is true. The following
table lists the \instr{OP2} bitfield values that may be ORred together. Like
the \instr{OP1} instruction, this instruction operates on the Conditional
‘addressing’ mode.

\vspace{1em}\noindent\begin{center}
\zebra
\begin{tabular}{ll}
  Bitfield & \instr{OP2} Instruction \\\noalign{\smallskip}\hline%\noalign{\smallskip}
  \texttt{-----01---} & \asm{SNA} — Skip if \A{} negative (G1)\\
  \texttt{-----0-1--} & \asm{SZA} — Skip if \A{} zero (G1) \\
  \texttt{-----0--1-} & \asm{SSL} — Skip if \Lreg{} set (G1) \\
  \texttt{-----0---1} & \asm{SSV} — Skip if \Vreg{} set (G1) \\
  \texttt{-----10000} & \asm{SKIP} — Always skip (G2) \\
  \texttt{-----11---} & \asm{SNN} — Skip if \A{} non-negative (G2) \\
  \texttt{-----1-1--} & \asm{SNZ} — Skip if \A{} non-zero (G2) \\
  \texttt{-----1--1-} & \asm{SCL} — Skip if \Lreg{} clear (G2) \\
  \texttt{-----1---1} & \asm{SCV} — Skip if \Vreg{} clear (G2) \\
  \texttt{--1-------} & \asm{CLA} — Clear \A{} \\
  \texttt{---1------} & \asm{CLI} — Clear \Ireg{} flag \\
  \texttt{----1-----} & \asm{STI} — Set \Ireg{} flag \\%
  \hline%\noalign{\smallskip}
\end{tabular}
\end{center}\vspace{1em}

There are two groups of branching instructions: G1 (bit 4 of the
instruction operand is \bin{0}) and G2 (bit 4 of the instruction
operand is \bin{1}). When G1 instructions \asm{SNA}, \asm{SZA}, {\ttfamily
  SSL} and \asm{SSV} are specified together, the skip is performed
when {\em any\/} of the specified conditions hold (logical disjunction
or Or). For example, the instruction \asm{SZA SNA} is ‘skip if \A{} less
than or equal to zero’, or ‘skip if \A{} non-positive’ (which is the
standard CFT Assembly macro \asm{SNP}).

When G2 instructions are specified together, the skip is performed
when {\em all\/} of the specified conditions hold (logical conjunction
or And). For example, \asm{SNN SNZ} is ‘skip if \A{} is non-zero and
non-negative’, or ‘skip if \A{} is positive’ (the standard Assembler
macro for this is \asm{SPA}). The full set of combinations to check
the value of \Areg{} is as follows:

\vspace{1em}\noindent\begin{center}
\zebra
\begin{tabular}{lll}
  Instruction & Macro & Semantics \\\noalign{\smallskip}\hline%\noalign{\smallskip}
  \asm{SNA }     &           & Skip if $\mbox{A} < 0$ \\
  \asm{SNA SZA } & \asm{SNP} & Skip if $\mbox{A} ≤ 0$ \\
  \asm{SZA }     &           & Skip if $\mbox{A} = 0$ \\
  \asm{SNZ }     &           & Skip if $\mbox{A} ≠ 0$ \\
  \asm{SNN }     &           & Skip if $\mbox{A} ≥ 0$ \\
  \asm{SNN SNZ } & \asm{SPA} & Skip if $\mbox{A} > 0$ \\
  \hline%\noalign{\smallskip}
\end{tabular}
\end{center}\vspace{1em}

\paragraph{Why Two \asm{CLA} operations?}
\label{sec:instruction-CLA2}
Superficially, having two \asm{CLA} operations is unnecessary, and wastes
space that could be used by another minor operation. However, clearing
\A{} is a very useful operation, and having it in both \instr{OP1} and
  \instr{OP2} makes it available to more use cases.

Both \asm{CLA} operations have the same bitfield value, \hex{080}. The \asm{OP1
  CLA} operation is \hex{C080}, and the \asm{OP2 CLA} operation is
\hex{D080}. To resolve the obvious ambiguity in the naming, standard CFT
Assembly {\em always\/} defines \asm{CLA} as \hex{C080}. This works in all
three combinations of \asm{CLA} appearances in instructions:

\begin{itemize}
\item{\textbf\asm{CLA}:} the symbol table resolves this to \hex{C080}, which is
  \asm{OP1 CLA}.
\item{\textbf\asm{OP1 CLA}:} since Assembly ORs all fields together,
  this results in \hex{C000 OR C080}, which is again \hex{C080}, or
  \asm{OP1 CLA}.
\item{\textbf\asm{OP2 CLA}:} again, ORring fields together yields
  \hex{D000 OR C080} which is \hex{D080}, which is \asm{OP2 CLA}.
\end{itemize}

The only minor drawback of this arrangement is that, should the
programmer somehow require the \asm{CLA} operation to be executed by
the \instr{OP2} instruction explicitly, \asm{OP2 CLA} must be specified
in full.

\subsubsection{\asm{LIA} — Load Immediate Address}
\label{sec:instruction-LIA}
\label{sec:instruction-LI}

Loads \A{} with the literal value specified in the instruction. The
page-relative form of this instruction is used to load \A{} with a
page-relative address, operating in the Address addressing mode.

When R=0, \instr{LIA} becomes the Load Immediate (\instr{LI}) instruction,
which can load a value in the range \hex{0000}–\hex{03FF} into \A. \instr{LIA}
works either in the Immediate mode (if loading a literal value), or the Address
mode (if loading a \gls{Page Zero} address). The distinction is purely one of
semantics, since both instructions work in exactly the same way.

The value of the instruction I bit is {\em ignored}.

\subsection{Standard Macros}
\subsubsection{\asm{RET} — Return from Subroutine}

This is defined as \asm{JMP I R 0000}. It jumps to the return address
saved by the \instr{JSR} instruction, which stores it at memory address
\hex{0000}.

\subsubsection{\asm{RTT} — Return from Trap} 

This is defined as \asm{JMP I R 0001}. It jumps to the return address
saved by the \instr{TRAP} instruction, which stores it at memory address
\hex{0001}.

\subsubsection{\asm{NEG} — Negate \A}

Obtains the two's complement of \A{} by performing \asm{OP1 NOT INC}.

\subsubsection{\asm{ING} — Increment and Negate \A}

Obtains the two's complement of \A{} and increases it, thereby
calculating $\mbox{AC} \leftarrow -(\mbox{AC} + 1)$. Due to the use of
two's complement for arithmetic negation, this is equivalent to a
simple \op{OP1 NOT}. The \op{ING} instruction is useful in some
types of loops in conjunction with \op{ISZ}.

\subsubsection{\asm{SEL} — Set L}

This macro sets \Lreg{} by combining the \op{CLL} and \op{CPL} instructions.

\subsubsection{\asm{LI} — Load Immediate}

This is equivalent to \asm{LIA R}. It loads \A{} with the 10-bit literal
value specified as operand. The most significant six bits are zero.

\subsubsection{\asm{SPA} — Skip if Positive \A}

This is equivalent to \asm{OP2 SNN SNZ}. It skips the next instruction
if \A{} is neither negative, nor zero (thus positive).

\subsubsection{\asm{SNP} — Skip if Non-Positive \A}

This is equivalent to \asm{OP2 SNA SZA}. It skips the next instruction
if \A{} is less than or equal to zero (non-positive).

\subsubsection{\asm{SBL}, \asm{SBR} — Bitwise shifts}

The two bitwise shift macros are formed by combining \asm{OP1 CLL} with
the corresponding \instr{OP1} roll operations. They provide bitwise
(unsigned arithmetic) shift operations which are fundamental in
implementing multiplication and division, among others.

Please note that there are no nybble-oriented shift operations because
there is no way to clear the lower order three bits of \A{} with an
\instr{OP1} instruction.

\subsection{Common Tasks}

This section shows how some common, simple Assembly language tasks can
be performed using the CFT instruction set.

\subsubsection{Addition With Carry}

The \Lreg{} flag may be used as carry in using this short program:
\begin{cftasmcode}
adc:   IFL INC      ; Skip if L=0
       ADD addr
\end{cftasmcode}

The program increases the \gls{Accumulator} by one if the \Lreg{} register is set,
then performs addition as normal.

\subsubsection{Subtraction}

There is no explicit subtraction instruction, but the benefit of two's
complement is that one is unnecessary. Subtraction can be reduced to
addition as follows:

\begin{cftasmcode}
sub:    NEG         ; OP1 NOT INC
        ADD addr
\end{cftasmcode}

The program does a one's complement (binary negation) of the accumulator, then
increments it by one, which is a two's complement (decimal negation). This is
the \asm{NEG} macro. The addition is then performed with the negative value of
the \gls{Accumulator}, to obtain the value $\mbox{\asm{addr}} - \mbox{\AC}$.

\subsubsection{Negation of a 32-bit Quantity}

The following code negates the two's complement representation of a
32-bit signed integer stored in locations \asm{xh} (high word) and
\asm{xl} (low word):

\begin{cftasmcode}
neg32:  SEL         ; Set carry
        LOAD xl     ; Negate low word
        NEG         ; Two's complement
        STORE xl

        LOAD xh     ; Negate high word
        IFL INC     ; Propagate carry
        NEG         ; Two's complement
        STORE xh
\end{cftasmcode}

\subsubsection{Addition of two 32-bit Values}

To add two 32-bit values stored in locations \asm{al}, \asm{ah} (\A{} low
and high words respectively), and \asm{bl}, \asm{bh} (B low and high
words respectively), it is necessary to propagate the carry bit
stored in the \Lreg{} register:

\begin{cftasmcode}
add32:  CLL         ; Clear carry
        LOAD al     ; Load low A
        ADD bl      ; Add to low B
        STORE xl    ; Store it

        LOAD ah     ; Load high A
        IFL INC     ; Propagate carry
        ADD bh      ; Add to high B
        STORE xh
\end{cftasmcode}

\subsubsection{Subtraction of two 32-bit Values}

This program subtracts two signed, two's complement 32-bit values
stored in locations \asm{al}, \asm{ah} (\A{} low and high words
respectively), and \asm{bl}, \asm{bh} (B low and high words
respectively). It does so by negating B, storing it to the result
location X, and then adding \A{} to that location while propagating
carry.

\begin{cftasmcode}
sub32:  SEL         ; Set carry
        LOAD bl     ; Negate low word
        NEG         ; Two's complement
        STORE xl

        LOAD bh     ; Negate high word
        IFL INC     ; Propagate carry
        NEG         ; Two's complement
        STORE xh

        CLL         ; Clear carry
        LOAD al     ; Load low A
        ADD xl      ; AC = AC + -B
        STORE xl    ; Store it

        LOAD ah     ; Load high A
        IFL INC     ; Propagate carry
        ADD xh      ; Add to high B
        STORE xh    ; Store it.
\end{cftasmcode}

%\subsubsection{Two's Complement of a 32-bit Quantity}
%
%There is no explicit subtraction instruction, but the benefit of two's
%complement is that one is unnecessary. Subtraction can be reduced to
%addition as follows:
%
%\begin{lstlisting}
%neg32:  SEL
%        ADD addr
%\end{cftasmcode}
%
%The program does a one's complement (binary negation) of the
%accumulator, then increments it by one, which is a two's complement
%(decimal negation). This is the \asm{NEG} macro. The addition is then
%performed with the negative value of the Accumulator, to obtain the
%value {\ttfamily addr - A}.

\subsubsection{Bitwise Shifts}

To convert bitwise rolls to bitwise shifts, the \Lreg\ register needs
to be cleared before the roll takes place. The following code performs
a bitwise (or unsigned arithmetic) shift one bit to the right.

\begin{cftasmcode}
shr:    CLL RBR
\end{cftasmcode}

This operation is mathematically tantamount to
$\lfloor\mbox{\A}/2\rfloor$. Obviously, other roll instructions may be
substituted for \asm{RBR}. Please note that these shifts are already available
as the standard Assembly macros \asm{SBR} and \asm{SBL}. There are no nybble
shift operations.

\subsubsection{Arithmetic Shifts}

Sign-extending shifts are only slightly more involved.

\begin{cftasmcode}
asr:    CLL       ; Clear L (L=0)
        SNN       ; Skip if AC >= 0
        CPL       ;   AC < 0: toggle L (L=1)
        RBR       ;   Roll 1 bit right.
\end{cftasmcode}

At the end of this short program, the most significant (i.e. sign) bit
of \A\ will be the same as before. Due to the use of two's complement,
this is still equivalent to $\lfloor\mbox{\A}/2\rfloor$, but the
behaviour is now specialised to signed numbers.

\subsubsection{Bitwise Or of a Small Array}

The autoindex registers can be used to simplify short loops. Here, the
\A\ is loaded with the address of the first word of the array. The
first 5 elements of it will be ORred together, and the result left in
\A.

\begin{cftasmcode}
or6:    STORE R 80  ; Autoindex register
        LOAD I R 80 ; Load 1st value
        OR I R 80   ; OR with 2nd value
        OR I R 80   ; OR with 3rd value
        OR I R 80   ; OR with 4rd value
        OR I R 80   ; Or with 5th value
\end{cftasmcode}

\subsubsection{Simple Loops}

This is a simple loop. It iterates as many times as the value of
\A\ on entry to the subroutine. In this example, the loop body sends
the hexadecimal value {\ttfamily 2A} to an I/O device designated \asm{TTY0
  0}. The routine is expected to be called with \asm{JSR stars}.

\begin{cftasmcode}
stars:  NEG          ; AC = -AC
        STORE R 10   ; Loop variable
loop:   LIA 2A       ; AC = 002A (ASCII '*')
        OUT TTY0 0   ; Send it out.
        ISZ R 10     ; Step the loop counter.
        JMP loop     ; Loop again.
        RET          ; Return if R 10 == 0.
\end{cftasmcode}

If the operating system has set up a Page Zero store of commonly used
constants, and it includes the conventional constant \asm{MINUS1} (which
contains -1 (\hex{FFFF}), an easy alternate form of this loop using
counter decrements is as follows:

\begin{cftasmcode}
stars:  STORE R 10   ; Loop variable
loop:   SNZ          ; AC = 0?
        RET          ;   Yes. Return.
        ADD minus1   ; Decrement loop counter
        STORE R 10   ; Store it back.
        LIA 21       ; AC = 0021 (ASCII '!')
        OUT TTY0 0   ; Send it out
        LOAD R 10    ; Load the loop counter.
        JMP loop     ; Loop again.
\end{cftasmcode}

\subsubsection{Sum of a Block of Words}

A somewhat more complex example leverages the Autoindex feature to
calculate the sum (modulo 65,536) of a block of words. A pointer to
the block of words should be stored at location \hex{0010}, and the
size (in words) should be in \A. On exit, memory address \hex{0012}
will contain the sum of the words.

\begin{cftasmcode}
sum_n:  NEG
        STORE R 11   ; Loop variable
        LOAD R 10    ; Array base
        STORE I R 80 ; Autoindex
        LI 0         ; 
        STORE I R 12 ; Sum = 0
        LOAD R 11    ; Number of words left
loop:   LOAD R 12    ; Load running total
        ADD I R 80   ; Sum a word
        STORE R 12   ; Store it back
        ISZ R 11     ; Step loop variable
        JMP loop     ; Loop again
        RET          ; Done.
\end{cftasmcode}

%% \section{Further reading}

%% For further information on the CFT computer, please consult the
%% following URL:

%% \begin{center}
%% \link{www.bedroomlan.org/hardware/cft}
%% \end{center}

\section{Instruction Table}

The table below shows all CFT instructions, standard macros, and minor
operations. \asm{I} is the indirection bit. \asm{R} is the register mode
bit. Dashes in the instruction bit pattern indicate ‘don't care’ values.

{
  %\newcommand\mk[1]{\ (#1)}
  %\newcommand\mka{\mk{a}}
  %\newcommand\mkb{\mk{b}}
  %\newcommand\mkc{\mk{c}}
  %\newcommand\mkd{\mk{d}}
  \newcommand\mk[1]{$^{#1}$}
  \newcommand\mka{\mk{1}}
  \newcommand\mkb{\mk{2}}
  \newcommand\mkc{\mk{3}}
  \newcommand\mkd{\mk{4}}
  \newcommand\mke{\mk{5}}
  {\input{instrtable}}

  \paragraph{Notes}

  \begin{description}
  \item \mka~Processor Cycles shown for Direct/Indirect/Autoindex modes or
    Address/Indirect Address/Autoindex Address modes, where available. The
    timing for Register variants is identical to that for non-Register
    modes. \todo{Update this: the timings are not right for Microcode Version
      5.}
  \item \mkb~Any number of these sub-instructions may be combined and will
    always need exactly 11 cycles in total.
  \item \mkc~Any number of these sub-instructions may be combined for a total
    of exactly 12 cycles.
  \item \mkd~G1 and G2 skips are groupwise mutually exclusive. When G1 skips
    are combined, their conditions are disjuncted (ORred). When G2 skips are
    combined, their conditions are conjuncted (ANDed).
  \item \mke~This is a convenience macro, not an independent instruction.
  \end{description}

}

%% \caption[Instruction Set]{\label{tab-is}CFT Instruction Set. I is the indirection bit. R is the
%%   register mode bit. Dashes in the instruction bit pattern indicate ‘don't
%%   care’ values. Notes: \mka~Processor Cycles shown for
%%   Direct/Indirect/Autoindex modes, where available. \mkb~Any number of these
%%   sub-instructions may be combined and will always need exactly 11 cycles in
%%   total. \mkc~Any number of these sub-instructions may be combined for a total
%%   of exactly 12 cycles. \mkd~G1 and G2 skips are groupwise mutually
%%   exclusive. When G1 skips are combined, their conditions are disjuncted
%%   (ORred). When G2 skips are combined, their conditions are conjuncted
%%   (ANDed). \mke~This is a convenience macro, not an independent instruction.}
%% \end{table*}
