alexiosc/cft/documentation/latex/cft_book/cft-soft-fs.tex

% -*- latex -*-

% Definitions for this chapter.

\input{partial-fs-magic}

\chapter{Data Storage}
\label{sec:fs}

\HtmlMetaDescription{This chapter describes the particulars of CFT
  data storage, including disk, ROM and tape labels, the CFT
  filesystem, and their constituent parts.}
%\HtmlMetaGoogleDescription{}
%\HtmlMetaBanner{}
%\HtmlMetaTags{}

\begin{figure}
  \centering
  \includelarge[width=0.75\columnwidth]{figs/Floppy_Disk_Drives_8_5_3.jpg}
  \caption[Floppy drives]{Floppy drives. 8-inch (left), full-height
    5¼-inch (middle), 3½-inch (right). The ‘full-height’ 5¼-inch unit
    is the size of two stacked internal CD/DVD drives (the desktop versions).}
\end{figure}

This chapter describes how CFT storage media are organised. Currently, the only
media in planning are IDE (parallel ATA) disk and disk-like devices such as CF
cards. IDE CD-ROMs may be attached and eventually supported but this is not
planned.

I initially considered supporting floppy drives using one of the older
WD37C65 Floppy Drive Controller chips, which are still relatively easy
to find (used). I have a number of Shugart 8-inch devices and several
of the smaller capacity IBM/Tandon 5¼-inch units, and enough floppy
disks. An immense 8-inch floppy drive controlled by the CFT would be
appropriate and interesting to look at (and provide interesting
mini-computer-like sound effects with its head loading/unloding
sounds), but IDE storage is easier to interface to, more convenient
and devices are simpler to find, attach, and run. The floppy
sub-project is still likely to go ahead, but not as the main means of
storage for the CFT.

A cassette tape interface is much simpler to build than a floppy
controller, and I may attempt this as part of a multi-I/O board for
the novelty factor. Desktop cassette decks of the type used in the
Eighties are not very common and their rubber parts need maintenance
which makes them not age well. Thankfully, analogue audio will always
be with us, and a multitude of devices could be used to store and play
back data streams: from digital voice recorders, to mobile phones and
other computers.

\section{Fundamentals}

Every storage medium is ultimately a memory array. Unlike memory, storage is
addressed in blocks. Standard Forth blocks are always 1,024 bytes (512 words)
in size, but storage blocks are most often 256–4,096 bytes (128–2,048 words) in
size. Storage is accessed in whole blocks, i.e. a block is the quantum of
storage. 

Every medium uses its own way of addressing individual
blocks. Three-dimensional vectors (head, cylinder, sector) are used for
floppies and (at the lowest level) for hard disks. On hard disks, the on-board
controller hides this and presents the disk as a simple array of (almost
always) 256-word blocks.

\section{Units of Measurement}

This discussion (and much of this chapter) often makes reference to
{\em bytes\/} which are defined to be eight-bit quantities. This is
done so that quantities make sense to the average reader, who is used
to multiples of bytes, but not of words. Whenever bytes are
referenced, quantities in Words are also provided. For the purpose of
this chapter, multiples of bytes and words are base two:

\begin{center}
  \zebra
  \begin{tabular}{lll}
    Prefix & Unit    & Description\\\hline
    Kilo-  & kB      & 1 Kilobyte = $2^{10}=1,024$ Bytes (512 Words) \\
    Mega-  & MB      & 1 Megabyte = $2^{20}=1,048,576$ Bytes (512 kWords) \\
    Giga-  & GB      & 1 Megabyte = $2^{30}=1,073,741,824$ Bytes (512 MWords) \\
    Tera-  & TB      & 1 Terabyte = $2^{40}=1,099,511,627,776$ Bytes (512 GWords) \\
    \hline
  \end{tabular}
\end{center}%
%
\noindent This may seem counter to modern practice, but the design of
CFT mirrors the design of similar computers before marketing reasons
made storage device manufacturers decimalise their units. Binary units
make sense for storage devices, since their block sizes are powers of
two, even though the total storage capacity is not. It is, however, a
multiple of a power of two (the block size), and is better expressed
in binary units.

\section{Byte Oriented Storage Media}

Some storage media are byte oriented, others are word oriented. IDE
disk drives use a 16-bit word, which is ideal for use on the CFT
architecture: reading a traditional\footnote{Modern IDE blocks are
  4,096 bytes long.} 512 byte IDE block requires 256 reads from the
drive.

Other devices, like floppy drives, are byte oriented. In this case, for
the typical 512 byte sector, the processor must perform 512 8-bit
transactions using a state machine that shifts the first byte read 8
bits to the right, making it the MSB.

\todo{Check this!}
Byte ordering terms do not apply to a word-oriented machine, but this
makes the CFT a big-endian architecture, at least in the way it reads
from 8-bit devices.

\section{Some Data Structures}

This chapter makes reference to a number of simple (or common) data
structures, which are defined below:

\begin{description}
  \item\simpledatastructure{Word} this is the familiar 16-bit quantity, the
    smallest amount of data the CFT can access from memory. Words represent
    values in the range 0–65,535.
  \item\simpledatastructure{Cell} same as \ds{Word}. Used when discussing
    Forth.
  \item\simpledatastructure{Code} one or more 16-bit words representing CFT
    instructions.
  \item\simpledatastructure{DWord} short for ‘double word’. This is a sequence
    of two words representing an unsigned, 32-bit integer. The \gls{MSB} is the
    first word (lowest offset or address). A \ds{DWord} can represent values in
    the range 0–4,294,967,295.
  \item\simpledatastructure{Reserved} not a true data structure. This is used
    to mark one or more words that are reserved for future expansion.
  \item\simpledatastructure{Date} A 16-bit value representing a date. This is a
    bitfield with the following structure\footnote{Readers with a good memory
      or traumatic experiences will identify this as the same data structure
      used by MS-DOS. This is pure co-incidence, guided by the fact that MS-DOS
      was 16-bit, and the Gregorian calendar hasn't changed much since the late
      1970s.}:

    \begin{cbitfield}
      \bitfieldItem{5}{cfthl!50}{Day}
      \bitfieldItem{4}{cfthl!25}{Month}
      \bitfieldItem{7}{cfthl!50}{Year}
    \end{cbitfield}

    \begin{description}
      \item {\bfseries Day:} the day of the month as an unsigned integer in the range 1–31.
      \item {\bfseries Month:} the month as an unsigned integer in the range 1–12.
      \item {\bfseries Year:} the year as an unsigned integer in the range
        0–127. The CFT Epoch Year, 1960, is added to this, to allow years in
        the range 1960–2087.
    \end{description}

  \item\simpledatastructure{Time} A 16-bit value representing a timestamp. This
    is a bitfield with the following structure\footnote{Again, this is
      identical to the MS-DOS timestamp due to the similarity in limits and
      requirements.}:

    \begin{cbitfield}
      \bitfieldItem{5}{cfthl!50}{Seconds}
      \bitfieldItem{6}{cfthl!25}{Minutes}
      \bitfieldItem{5}{cfthl!50}{Hours}
    \end{cbitfield}

    \begin{description}
      \item {\bfseries Seconds:} the seconds of the timestamp in the range
        0–31. Note that this range is unable to represent the required 0–59
        range. Seconds are shifted one bit to the right, effectively multiplied
        by two. This gives a range of 0–58 in increments of two. The CFT can
        thus record timestamps with a precision of 2 seconds. This is
        sufficient for many needs. MS-DOS did the same and few users noticed
        the low accuracy.
      \item {\bfseries Minutes:} the minutes of the timestsamp in the range
        0–59.
      \item {\bfseries Hours:} the hours of the timestamp, in the range 0–23
        (24-hour format).
    \end{description}

  \item\simpledatastructure{PString} this data structure occupies one or more
    words, depending on its use. It is used to hold a CFT packed string, a
    compact method of recording strings of identifier characters. Packed
    strings contain 127-bit US ASCII values. Every word contains two such
    characters. Odd-numbered characters take up the lower 8 bits, even-numbered
    characters take up the upper 8 bits. The last character in the string is
    denoted by setting the eighth bit (\cftcode{END}) for any character:

    \begin{cbitfield}
      \bitfieldGroup{7}{cfthl!50}{Character index 0}
      \bitfieldItem{1}{cfthl!25}{END}
      \bitfieldGroup{7}{cfthl!50}{Character index 1}
      \bitfieldItem{1}{cfthl!25}{END}
    \end{cbitfield}

    Packed strings are also discussed in~\cf{sec:asm-pstring}.

  \item\simpledatastructure{BlockPtr} this is a \ds{DWord} value: a 32-bit
    unsigned integer, MSB first. It is interpreted as a pointer to a block
    within a volume. Non-zero values refer to a block by its number. A zero
    (\hex{00000000}) denotes the pointer \cftcode{NULL} value, usually
    interpreted as ‘no block’ in this context.
\end{description}

In addition, a complex data structure, \ds{DateTime} is defined to record the
date and time of a timestamp:

\begin{datastructure}[Offset]{DateTime}
    \dsdesc{\hex{00}}{Date}{%
      The \ds{Date} part of the timestamp.
      }
    %
    \dsdesc{\hex{01}}{Time}{%
      The \ds{Time} part of the timestamp.
    }
    %
\end{datastructure}

\section{Translating Native Geometry to Block Addresses}

Most physical storage devices are block-oriented, but their blocks are
addressed in native schemes. Functions are provided to map from these
native schemes to block counts (and the reverse).

\subsection{IDE Hard Drives}

IDE hard drives traditionally used a three-dimensional cylinder-head-sector
addressing scheme. All but the oldest IDE-compatible drives also provide a
block-level view of the disk. The disk's embedded controller is responsible for
the mapping from one scheme to the other, so the CFT operating system does not
need to.

\subsection{Floppy Disks}

Floppy disks always use cylinder-head-sector addressing, but floppy disk
controllers do not provide a logical block mapping in hardware. The operating
system must provide a mapping function in software. One complication here is
that the number of cylinders and sectors are not necessarily powers of two, so
software multiplications or an in-memory offset table would be needed.

%% This can be avoided by padding cylinders and sectors to a power of two, and
%% using the entire vector as a block number. Floppy cylinders are commonly in the
%% range 0–40 to 0–80. 7 bits can be used for this. Sector numbers start at 1. The
%% number of sectors per track differs between floppy drive technology, but 5 bits
%% would be more than enough. The head ordinate is either 0 or 1. One mapping
%% function could thus be $64c + 32h + s - 1$. This allows a sparse, 13-bit block
%% map. To avoid allocating 

\subsection{Tapes}

Tapes are sequential access devives and are operated at the pulse level. There
are blocks, and tapes cannot hold a CFT filesystem, so no block translation is
needed.

\section{Disk Label}
\label{sec:disk-label}
\label{sec:disklabel}
\label{sec:disk-slices}

All disks, including floppy disks, have a \gls{disk label}. The disk
label is at block 0 of the device. It identifies the device as
properly prepared for use. It contains the magic number
\magicDiskLabel (used to detect the presence of the disk label), space
for 126 words of optional boot code, and defines between one and
sixteen \glspl{disk slice}.

\begin{figure}
 \centering
 \inputfigure{figure-storage-medium-organisation}

 \caption[Disk Label]{\label{fig:storage-medium-organisation} The CFT
   Disk Label. The first block on each usable storage medium contains
   this data structure, which includes a magic number (for detection
   reasons), some optional boot code, and pointers to 1–16 \glspl{disk
     slice}. The storage medium itself is partitioned according to the
   definition of these slices. Each slice can contain anything, but
   usually holds a \gls{filesystem}.}
\end{figure}

Disk labels assume the lowest common denominator of block sizes, 256
words. This matches the hardware sector size of both hard drives and
standard-format floppy disks\footnote{Most modern floppy disks are
  soft-sectored, so exotic formats {\em are\/} possible, if undesirable
  because of their incompatibility with other platforms.}. The memory
map of the disk label is as follows:

\begin{datastructure}[Offset]{DiskLabel}
    \dsdesc{\hex{00}}{Word}{%
      If ROM boot code should be used, this
      word should hold the \asm{RET} instruction, \hex{6400}. Otherwise,
      it should be a \asm{SKIP} instruction (\hex{D010}), and boot code
      should be provided starting at block offset \hex{02}.}
    %
    \dsdesc{\hex{01}}{Word}{%
      The disk label magic number, always \magicDiskLabel. This works
      in tandem with offset \hex{00}, so the magic number could be
      considered to be the 32-bit value \hex{6400CF75} (CFT disk
      label, ROM boot code) or \hex{D010CF75} (CFT disk label, custom boot
      code).}
    %
    \dsdesc{\hex{02}–\hex{7F}}{Code}{%
      Up to 126 words of optional boot code. If
      not used for booting, the contents of the part of the disk label are
      unspecified and may be used for any other ad hoc purpose.
    }
    %
    \dsdesc{\hex{80}–\hex{FF}}{SliceDesc}{
      Sixteen identical slice
      descriptors, each 8 words long, corresponding to slices 0–15 in
      order. Not all slices need to be used, and they do not need to be
      used contiguously. Slices do not need to be contiguous, and may
      overlap as no checking is performed (of course, writing to
      overlapping slices may corrupt all involved filesystems). The
      corresponding 8 words for unused slices must be filled with the
      value \hex{FFFF}.
    }
\end{datastructure}%
%
Each slice descriptor (\ds{SliceDesc}) consists of eight words as follows:

\pagebreak
\begin{datastructure}[Offset]{SliceDesc}
  \dsdesc{\hex{0}}{Word}{%
    The type of volume held in this slice. Currently,
    the following values are valid:
    \begin{itemize}
      \item{\bfseries\hex{F501}}: a CFT Filesystem.
      \item{\bfseries\hex{FFFF}}: an unused slice descriptor.
    \end{itemize}
    }
  %
  \dsdesc{\hex{1}}{Word}{%
    Slice flags. This value is currently unused and
    should hold the value \hex{0000} for used slices, \hex{FFFF} for unused
    ones.
  }
  %
  \dsdesc{\hex{2}–\hex{3}}{DWord}{%
    32 bits, with the \gls{MSB} at offset
    \hex{2}. Number of the first hardware-sized block (256 words) of the
    slice. Valid numbers are \hex{00000001} to \hex{FFFFFFFF}, though in
    practice the limit is the capacity of the storage device. Block
    \hex{00000000} is the disk label.
  }
  %
  \dsdesc{\hex{4}–\hex{5}}{DWord}{%
    32 bits, with the \gls{MSB} at offset
    \hex{4}. Number of hardware-sized blocks (256 words) in the slice. The
    minimum value is \hex{00000001}, and the maximum depends on the location of
    the next slice or the end of the storage medium.%
  }
  %
  \dsdesc{\hex{6}}{Word}{%
    This word is reserved for future expansion and should be set to \hex{FFFF}.
  }
  %
  \dsdesc{\hex{7}}{Word}{%
    This word is reserved for future expansion and should be set to \hex{FFFF}.
  }
\end{datastructure}

\noindent On PC architectures, floppies contain a boot sector but no
partition table. The CFT has a single disk label format, and it
applies to all random access peripheral storage media. Due to their
size, floppies are expected to have a single slice.

\subsection{Accessing Disk Slices}

Most Unix-based architectures include tools for accessing filesystems
at arbitrary locations of a container device. On Linux, the
\cftout{dmsetup} and \cftout{losetup} tools can both do this using
different kernel drivers.

A driver for the CFT filesystem will, of course, need to be written
first. This has so far not been done, and chances are it will be a
user-space driver (which Linux allows through the FUSE framework). As
such, and since it will be written in ANSI C, it should be simple to
write drivers for other platforms.

\section{Filesystem}
\label{sec:fs}

This section describes the CFT Filesystem. Most filesystems are difficult to
describe in a linear fashion because their components are interlinked in
complex ways. In reading this discussion, it may be necessary to jump forward
or back to cover data structures and concepts not yet encountered.

The CFT \gls{filesystem} was inspired very heavily by Apple's ProDOS filesystem
as used in the Apple II series.\footnote{For a full discussion of ProDOS 8
  internals, including the filesystem format, please refer to the
  \ahref{http://www.easy68k.com/paulrsm/6502/PDOS8TRM.HTM}{ProDOS 8 Technical
    Reference Manual}.}

The CFT Filesystem has a number of useful features:

\begin{itemize}
\item Works on both small and large devices. On the 8-bit Apples,
  ProDOS worked with 90 kByte floppy disks, but could use the much
  larger hard disks of the day. Using 2,048-word blocks, the CFT
  filesystem can address a staggering 16~TB (8~Terawords). Using the
  more common 1,024-word block size, the filesystem can store up to
  8~TB (4~Terawords).
\item Allows large files. Up to 16 GB ($2^{30}$) can be stored in a single
  file.
\item Organises files in nested subdirectories.
\item Low overheads. An 8~Megaword (256-word blocks) filesystem needs 10 blocks
  (2 kWord, 0.02\%) for overheads.
\item Allows different block sizes: 256, 512 or 1,024 Word blocks,
  with later upwards expansion available.
\item Blocks can span multiple hardware sectors.
\item Sparse files are easy to implement and can be supported at a later time.
\end{itemize}

A filesystem block is defined in terms of the hardware block (sector) size and
is usually a small multiple of it. It is chosen when the filesystem is created
and remains constant for the lifetime of the filesystem. Since it affects
various filesystem limits and overheads, it makes sense for a single filesystem
block to span multiple hardware blocks or sectors. This parallels the concept
of a Unix block, or that of the ‘cluster’ in the MS-DOS FAT filesystem.

\subsection{Filesystems and Volumes}

In this chapter, a filesystem is defined as the data structure used to store
files on a random access storage medium. A particular instance of this
filesystem residing on a particular storage medium is a termed (in accordance
with ProDOS tradition) a {\em volume\/}. That is, there is currently only one
CFT filesystem, but there may be dozens of volumes formatted using this
filesystem.

This is slightly counter to some Unix terminology, where a filesystem is the
actual data on disk.

\subsection{Data Structures}

To simplify coding the filesystem, a lot of the data structures are defined in
terms of a base data structure, in a concept essentially identical to that of
inheritance in \gls{OOP}. For example, the entire volume is
described by a data structure which is almost identical to that of a
directory. Thus, the same code that traverses sub-directories can be used to
traverse the top-level directory of a volume.

Another \gls{OOP} concept in use is polymorphism. All directory entries are
derived from the same base data structure, and share a number of metadata
fields. They also have the same size, which makes them fit neatly in the
directory entry array.

\subsection{Redundancy}

There are a number of purposefully redundant features in the filesystem
design. This was done to allow sanity checking, which helps detect corruption
in volumes. Redundancy has an obvious space cost, and sanity checks have an
obvious time cost. It was important to balance those against the need for a
compact, simple filesystem for a simple computer.

Some redundant features are costly in time but helpful in recovering a broken
filesystem. Using a doubly linked list for directory blocks is one of
them. Having directory names in two places is another. A repair program could
scan through the filesystem to locate broken directories and hopefully relink
the directory hierarchy.

\section{Filesystem Contents}

Filesystem blocks may be one of several types:

\begin{itemize}
\item A boot block.
\item A volume directory block, describing the filesystem and containing
  entries for its first files and sub-directories.
\item A bitmap block, which shows the computer which blocks are in use.
\item A directory block, describing a directory or subdirectory (this is almost
  identical to volume directory blocks above).
\item A file index block.
\item A block allocated to a file.
\item A free block.
\end{itemize}

The role of a particular block depends on its position (block number), its
relation to other blocks, or a block type field stored in the block
itself. Each type of block is described below. The layout of a newly
constructed volume is shown in~\fcf{fig:filesystem-structure}.

\begin{figure}
 \centering
 \inputfigure{figure-filesystem-structure}
 \caption[CFT filesystem overview]{\label{fig:filesystem-structure} High level
   view of how a newly created CFT filesystem is organised on disk.}
\end{figure}

\subsection{Boot Blocks}

The first two blocks of every filesystem are reserved for boot code. If more
boot code is necessary, additional blocks may be reserved in the filesystem's
free area. Naturally, the size of the boot blocks in words varies with the size
of the filesystem block.

In most cases, these boot blocks will not be used. ROM boot code should take
care of booting in most cases (stage 0 bootstrap). Additional, optional space
for custom boot requirements is provided in the disk label (stage 1
bootstrap). The boot blocks in the filesystem can hold stage 2 bootstrap
code.

\subsection{Volume Directory}

The \gls{VD} (\ds{VolumeDir} data structure) acts as the filesystem header or
superblock. Structurally, it is identical to a directory, except for its block
type field (magic number) and the contents of its first entry. The whole volume
behaves like a directory without a parent.

Directories are discussed in~\cf{sec:fs-directories}. The specifics of the
\gls{VD} are discussed in~\cf{sec:fs-containers}. The data structure itself is
illustrated in~\fcf{fig:fs-volumedir}.

\begin{figure}
 \centering
 \inputfigure{figure-fs-volumedir}
 \caption[CFT Volume data structure]{\label{fig:fs-volumedir} The
   \ds{VolumeDir} data structure is a specialised \ds{Directory} with a
   Volume Descriptor (\ds{VolumeDesc}) for a header. It contains
   metadata on the entire volume.}
\end{figure}

\subsection{The Bitmap}
\label{sec:fs-bitmap}

The bitmap is used to mark what blocks are in use. Each block of the volume is
represented by a single bit in the bitmap, 16 blocks to a word. The size of the
bitmap depends on the volume's block size and the volume's size (in
blocks).

Each bitmap block contains information on $16b$ blocks, where $b$ is the
filesystem block size. For a filesystem of $n$ blocks, $\lceil n/16b\rceil$
bitmap blocks are needed.

Bit 0 (the \gls{LSB}) of word 0 of block 0 of the bitmap represents block 0 of
the volume (the first boot block).

The bitmap is a simple bitfield without magic numbers or other fields. For each
bit, a value of \bin{0} indicates a free block, and a value of \bin{1}
indicates a used block. The bitmap maps {\em all\/} blocks in the volume,
including support structures such as the boot blocks, volume directory block
and the bitmap itself. These blocks are, naturally, marked used at volume
creation.

A \gls{block pointer} to the first block of the bitmap is stored in the
\gls{VD} structure (\ds{VolumeDir}). The number of bitmap blocks may be
calculated when the operating system opens the volume and stored in RAM to
allow limit checking (though the same function can be performed easily by
shifting the number of volume blocks (also stored in the \ds{VolumeDir}) 4 bits
to the right).

If the volume size is not a multiple of the block size times 16, the bitmap
will have bits at the end of the last bitmap block that do not correspond to a
valid filesystem block. To simplify operations and avoid attempts to allocate
blocks past the end of the volume, these bits should always be set.

\subsection{Directories}
\label{sec:fs-directories}

Directories\footnote{Known as ‘folders’ on some architectures.} are
\glspl{container} (see~\cfp{sec:fs-containers}) for files, other directories,
and other arbitrary objects not yet specified.

Directories may be nested without limits, although the operating system may
impose a practical limits for storage reasons.

For detailed information on how directories and other containers work, please
refer to~\cf{sec:fs-containers}). Directories are encoded as a \ds{Directory}
container data structure, illustrated in~\fcf{fig:fs-directory}.

\begin{figure}
 \centering
 \inputfigure{figure-fs-directory}
 \caption[CFT Directory data structure]{\label{fig:fs-directory} The
   CFT \ds{Directory} data structure and its header, the Directory
   Descriptor (\ds{DirDesc}).}
\end{figure}

\section{Containers}
\label{sec:fs-containers}

Containers are data structures that contain other filesystem objects, including
other containers. The container concept is what makes CFT filesystems
hierarchical. Every \gls{volume} is a container. It may contain files or
directories. They may, in turn, contain files and other sub-directories, and so
on. This forms a tree where the leaves are files (and other non-container
objects). This is illustrated in~\fcf{fig:fs-tree}.

A container is a block-level data structure: it occupies one (or more) entire
blocks. Each block contains a maximum number of \glspl{descriptor} (discussed
below), of which the container's own metadata (header) is the first. When first
allocated, the data structure only occupies one block. When its array of
Descriptors is full, another block is allocated, a continuation block. This
block has no metadata of its own, and forms a doubly-linked list. Additional
continuation blocks may be allocated until the limit of 65,536 descriptors is
reached. This is illustrated in~\fcf{fig:fs-directory-ll}. The number of
descriptors that can fit in container blocks is shown
in~\tcf{table:fs-desc-bs}:

\begin{table}[htb]
  \centering
  \zebra
  \begin{tabular}{rrr}
    Block Size & Slots/block & Unused space \\
    \hline
    256 Words   &  8 & 15 words\\
    512 Words   & 17 & 10 words\\
    1,024 Words & 35 &  0 words\\
    2,048 Words & 70 &  9 words\\
    \hline
  \end{tabular}
  \caption[Number of Descriptors by Block Size]{\label{table:fs-desc-bs} Number
    of descriptors that fit in a single container block depending on the volume
    block size. Since descriptors do not fit the block size exactly, each block
    size has a number of unused space at the end of the descriptor array.}
\end{table}

\noindent Currently, there are two types of container objects defined:

\begin{description}
\item {\bfseries\ds{VolumeDir}} (\fcfp{fig:fs-volumedir}) describes the entire
  volume. In Unix terms, this is the root directory and filesystem superblock
  combined. \ds{VolumeDir}s have a magic number of \magicVolume.
\item {\bfseries\ds{Directory}} describes a directory or sub-directory. Its
  structure is illustrated in~\fcf{fig:fs-directory}. Directories use
  \magicDirectory{} for their magic number.
\end{description}

Each container has a number of standard fields, common among all container types:

\begin{datastructure}[Offset]{Container}
    \dsdesc{\hex{00}}{Word}{%
      A block type number of magic number to distinguish this type of block
      from others. If this is a continuation block, the magic number is always
      \magicDirectoryCont. Otherwise, it depends on the container type.
    }
    %
    \dsdesc{\hex{01}–\hex{02}}{BlockPtr}{%
      A 32-bit (\gls{MSB} first) \gls{block pointer} to the previous \gls{DD}
      in the chain, or \hex{00000000} if this is the last one.
    }
    %
    \dsdesc{\hex{03}–\hex{04}}{BlockPtr}{%
      A \gls{block pointer} to the next \gls{DD} in the chain, or
      \hex{00000000} if this is the first one.
    }
    %
    \dsdesc{\hex{05}–\hex{08}}{Reserved}{%
      A block of words reserved for future expansion.
    }
    %
    \dsdesc{\hex{09}–}{DirDesc}{%
      An array of Descriptors, the size of which depends on the volume block
      size, and is listed in~\tcf{table:fs-desc-bs}.
    }
\end{datastructure}

The payload a container is an array of \glspl{descriptor}. The first of these
describes the container itself. The remaining ones describe the contained
objects. Descriptors are discussed below.

%% The {\em first\/} \gls{DD} (i.e. non-continuation) block in a linked list
%% contains the container's metadata (header) \gls{Descriptor} as its first
%% entry. This describes the container itself. The format of these metadata
%% structures, as well as the format of contained object \glspl{Descriptor} is
%% described below:
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
