alexiosc/cft/documentation/latex/cft_book/figure-address-mode.tex

% -*- latex -*-
\documentclass[class=memoir,border=200pt]{standalone}
\input{preamble-2018}
\input{macros-2018}

\begin{document}%
%\tikzexternaldisable%
\begin{tikzpicture}%

  \input{partial-addressing-modes}

  % The IR
  \AddressingModeIR{0}{0}{col10!50}

  % The PC
  \begin{scope}[,yshift=-1.5cm]
    \PageFromPC{col14!50}
  \end{scope}

  % The Accumulator.
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
