alexiosc/cft/documentation/case/textures/front-panel-module-revC-top.png

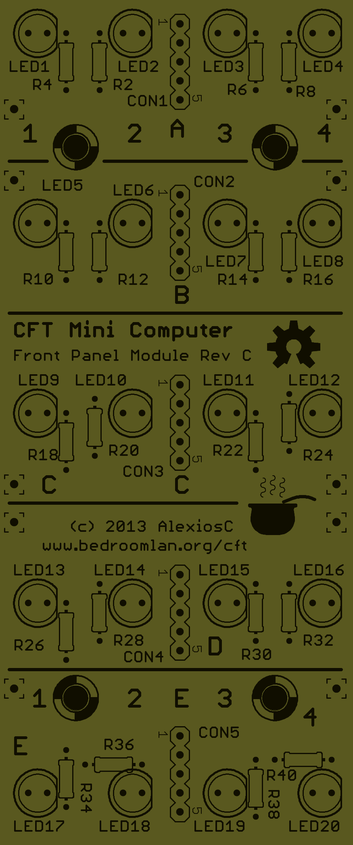
documentation/case/textures/front-panel-module-revC-top.png
