alexiosc/cft/documentation/panel/front-panel-small.png

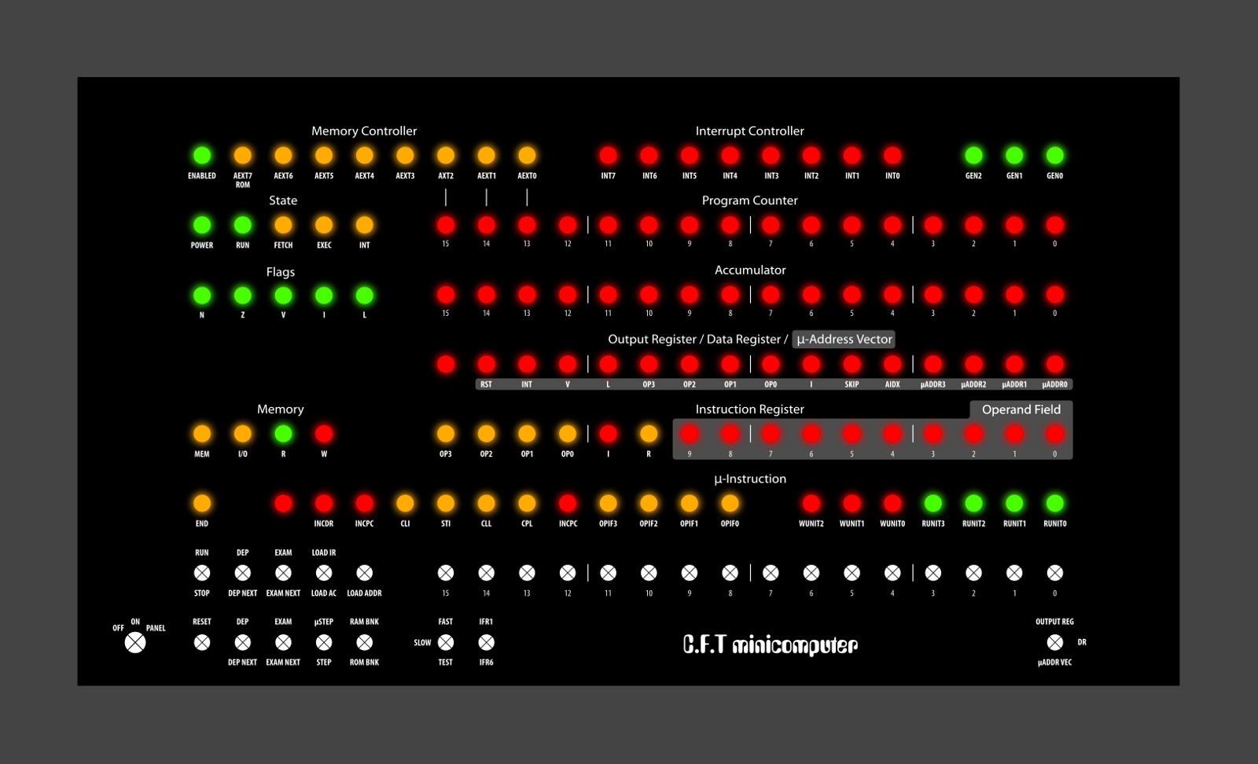
documentation/panel/front-panel-small.png
