alexiosc/cft/documentation/panel/front-panel.png

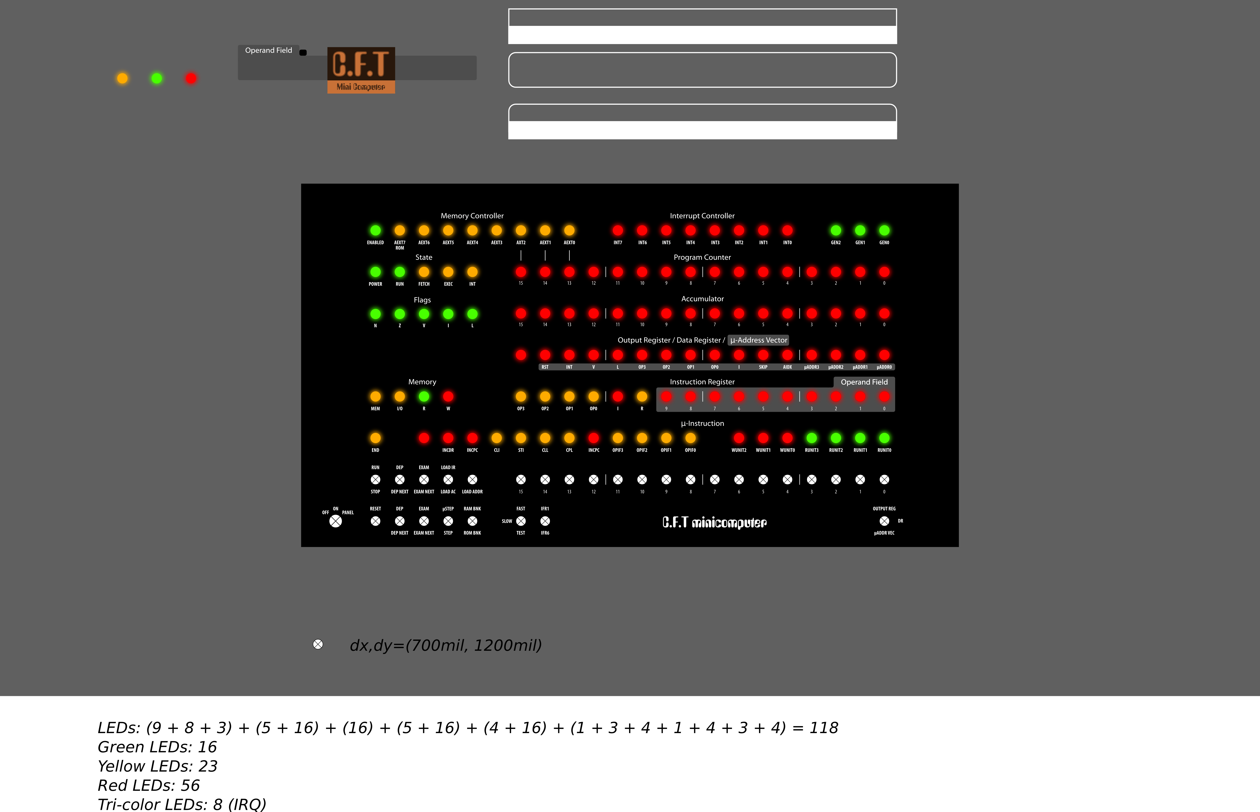
documentation/panel/front-panel.png
