alexiosc/cft/documentation/planning/Panel.png

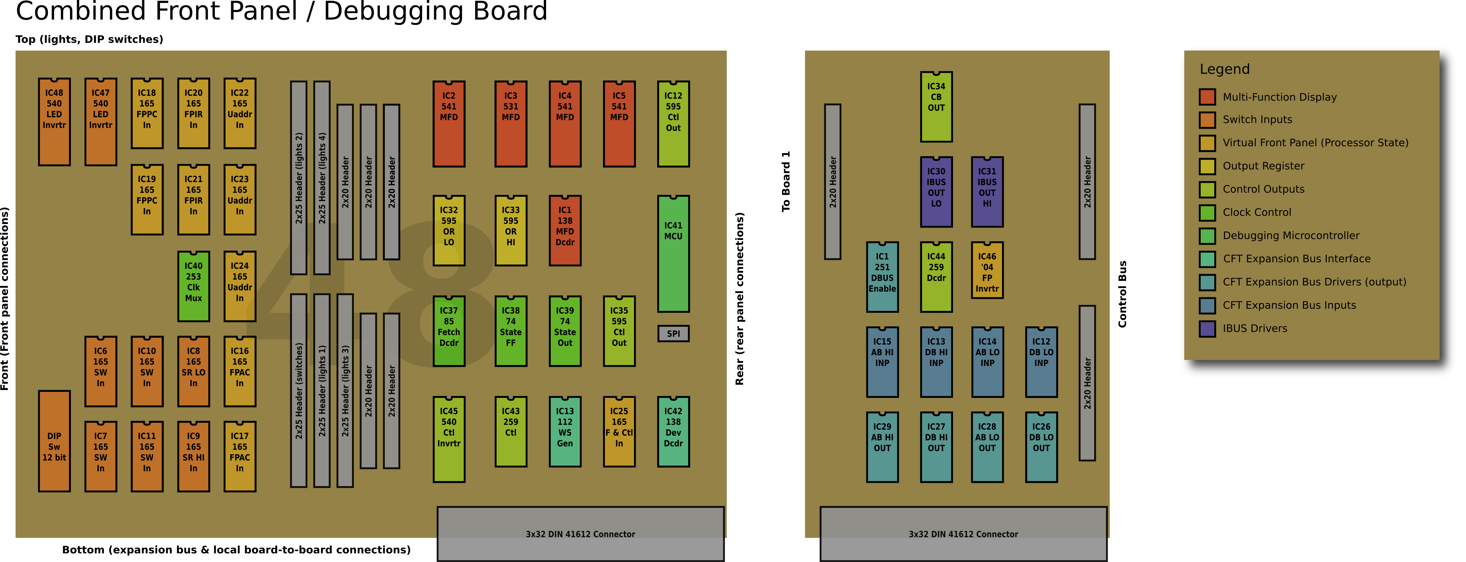
documentation/planning/Panel.png
