alexiosc/cft/documentation/latex/assembler_guide/cft-bom-parts.tex

\schpt{C1}–\schpt{C9} & 0.1μF ceramic capacitor & Farnell US 1694337 (£0.019@100), RS 721-5240 (£0.051@50), Farnell 9411887 (£0.062) &  \\
\schpt{C10} & 1μF capacitor & Farnell US 1600879 (£0.041@25), Farnell 3322210 (£0.148), RS 538-1578 (£0.292), Farnell 1100398 (£0.38) &  \\
\schpt{C11}–\schpt{C14} & 0.1μF ceramic capacitor & Farnell US 1694337 (£0.019@100), RS 721-5240 (£0.051@50), Farnell 9411887 (£0.062) &  \\
\schpt{C15}–\schpt{C16} & 10µF electrolytic capacitor & Farnell 1902928 (£0.033), RS 440-6547 (£0.026@50) &  \\
\schpt{C17}–\schpt{C21} & 0.1μF ceramic capacitor & Farnell US 1694337 (£0.019@100), RS 721-5240 (£0.051@50), Farnell 9411887 (£0.062) &  \\
\schpt{C22} & 1μF capacitor & Farnell US 1600879 (£0.041@25), Farnell 3322210 (£0.148), RS 538-1578 (£0.292), Farnell 1100398 (£0.38) &  \\
\schpt{C23}–\schpt{C28} & 0.1μF ceramic capacitor & Farnell US 1694337 (£0.019@100), RS 721-5240 (£0.051@50), Farnell 9411887 (£0.062) &  \\
\schpt{C29}–\schpt{C32} & 1μF capacitor & Farnell US 1600879 (£0.041@25), Farnell 3322210 (£0.148), RS 538-1578 (£0.292), Farnell 1100398 (£0.38) &  \\
\schpt{C33}–\schpt{C37} & 0.1μF ceramic capacitor & Farnell US 1694337 (£0.019@100), RS 721-5240 (£0.051@50), Farnell 9411887 (£0.062) &  \\
\schpt{C38} & 1μF capacitor & Farnell US 1600879 (£0.041@25), Farnell 3322210 (£0.148), RS 538-1578 (£0.292), Farnell 1100398 (£0.38) &  \\
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
\schpt{C159} & 1μF capacitor & Farnell US 1600879 (£0.041@25), Farnell 3322210 (£0.148), RS 538-1578 (£0.292), Farnell 1100398 (£0.38) &  \\
\schpt{C160}–\schpt{C165} & 0.1μF ceramic capacitor & Farnell US 1694337 (£0.019@100), RS 721-5240 (£0.051@50), Farnell 9411887 (£0.062) &  \\
\schpt{C166}–\schpt{C170} & 1μF capacitor & Farnell US 1600879 (£0.041@25), Farnell 3322210 (£0.148), RS 538-1578 (£0.292), Farnell 1100398 (£0.38) &  \\
\schpt{C171} & 0.1μF ceramic capacitor & Farnell US 1694337 (£0.019@100), RS 721-5240 (£0.051@50), Farnell 9411887 (£0.062) &  \\
\schpt{C172} & 1μF capacitor & Farnell US 1600879 (£0.041@25), Farnell 3322210 (£0.148), RS 538-1578 (£0.292), Farnell 1100398 (£0.38) &  \\
\schpt{C173} & 0.1μF ceramic capacitor & Farnell US 1694337 (£0.019@100), RS 721-5240 (£0.051@50), Farnell 9411887 (£0.062) &  \\
\schpt{C174}–\schpt{C175} & 1μF capacitor & Farnell US 1600879 (£0.041@25), Farnell 3322210 (£0.148), RS 538-1578 (£0.292), Farnell 1100398 (£0.38) &  \\
\schpt{C176}–\schpt{C187} & 1 μF electrolytic capacitor & Farnell 1236655 (£0.034) & Through hole \\
\schpt{C188}–\schpt{C190} & 10 µF electrolytic capacitor & Farnell 1902928 (£0.033), RS 440-6547 (£0.026@50) &  \\
\schpt{C191}–\schpt{C195} & 0.1μF ceramic capacitor & Farnell US 1694337 (£0.019@100), RS 721-5240 (£0.051@50), Farnell 9411887 (£0.062) &  \\
\schpt{C196}–\schpt{C197} & 1μF capacitor & Farnell US 1600879 (£0.041@25), Farnell 3322210 (£0.148), RS 538-1578 (£0.292), Farnell 1100398 (£0.38) &  \\
\schpt{C198}–\schpt{C211} & 0.1μF ceramic capacitor & Farnell US 1694337 (£0.019@100), RS 721-5240 (£0.051@50), Farnell 9411887 (£0.062) &  \\
\schpt{C212}–\schpt{C213} & 22 pF ceramic capacitor & Farnell 9411674 (£0.035@25) &  \\
\schpt{C214} & 1μF capacitor & Farnell US 1600879 (£0.041@25), Farnell 3322210 (£0.148), RS 538-1578 (£0.292), Farnell 1100398 (£0.38) &  \\
\schpt{C215}–\schpt{C220} & 0.1μF ceramic capacitor & Farnell US 1694337 (£0.019@100), RS 721-5240 (£0.051@50), Farnell 9411887 (£0.062) &  \\
\schpt{C221} & 1μF capacitor & Farnell US 1600879 (£0.041@25), Farnell 3322210 (£0.148), RS 538-1578 (£0.292), Farnell 1100398 (£0.38) &  \\
\schpt{C222} & 100uF Electrolytic capacitor & \href{http://uk.farnell.com/jsp/search/productdetail.jsp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\%2FglobalsearchE14.jsp}{Farnell 1902882} &  \\
\schpt{C223}–\schpt{C226} & 1μF electrolytic capacitor & Farnell 1236655 (£0.034) &  \\
\schpt{C227} & 22nF capacitor & \href{http://uk.farnell.com/jsp/search/productdetail.jsp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\%2FglobalsearchE14.jsp}{Farnell 9411860} &  \\
\schpt{C228} & 4.7μF Electrolytic capacitor & \href{http://uk.farnell.com/jsp/search/productdetail.jsp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\%2FglobalsearchE14.jsp}{Farnell 1902916} &  \\
\schpt{C229}–\schpt{C230} & 1μF capacitor & Farnell US 1600879 (£0.041@25), Farnell 3322210 (£0.148), RS 538-1578 (£0.292), Farnell 1100398 (£0.38) &  \\
\schpt{C231}–\schpt{C238} & 1μF electrolytic capacitor & Farnell 1236655 (£0.034) &  \\
\schpt{C239}–\schpt{C240} & 0.1μF ceramic capacitor & Farnell US 1694337 (£0.019@100), RS 721-5240 (£0.051@50), Farnell 9411887 (£0.062) &  \\
\schpt{C241}–\schpt{C244} & 1μF electrolytic capacitor & Farnell 1236655 (£0.034) &  \\
\schpt{C245}–\schpt{C247} & 0.1μF ceramic capacitor & Farnell US 1694337 (£0.019@100), RS 721-5240 (£0.051@50), Farnell 9411887 (£0.062) &  \\
\schpt{C248}–\schpt{C249} & 1μF capacitor & Farnell US 1600879 (£0.041@25), Farnell 3322210 (£0.148), RS 538-1578 (£0.292), Farnell 1100398 (£0.38) &  \\
\schpt{C250}–\schpt{C256} & 0.1μF ceramic capacitor & Farnell US 1694337 (£0.019@100), RS 721-5240 (£0.051@50), Farnell 9411887 (£0.062) &  \\
\schpt{C257} & 1μF capacitor & Farnell US 1600879 (£0.041@25), Farnell 3322210 (£0.148), RS 538-1578 (£0.292), Farnell 1100398 (£0.38) &  \\
\schpt{C258}–\schpt{C261} & 0.1μF ceramic capacitor & Farnell US 1694337 (£0.019@100), RS 721-5240 (£0.051@50), Farnell 9411887 (£0.062) &  \\
\schpt{C262}–\schpt{C270} & 1μF capacitor & Farnell US 1600879 (£0.041@25), Farnell 3322210 (£0.148), RS 538-1578 (£0.292), Farnell 1100398 (£0.38) &  \\
\schpt{C271} & 10μF/10V Electrolytic capacitor & \href{http://uk.farnell.com/jsp/search/productdetail.jsp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\%2FglobalsearchE14.jsp}{Farnell 1902928} &  \\
\schpt{C272}–\schpt{C281} & 0.1μF ceramic capacitor & Farnell US 1694337 (£0.019@100), RS 721-5240 (£0.051@50), Farnell 9411887 (£0.062) &  \\
\schpt{C282} & 1μF capacitor & Farnell US 1600879 (£0.041@25), Farnell 3322210 (£0.148), RS 538-1578 (£0.292), Farnell 1100398 (£0.38) &  \\
\schpt{C283}–\schpt{C287} & 0.1μF ceramic capacitor & Farnell US 1694337 (£0.019@100), RS 721-5240 (£0.051@50), Farnell 9411887 (£0.062) &  \\
\schpt{C288} & 1μF capacitor & Farnell US 1600879 (£0.041@25), Farnell 3322210 (£0.148), RS 538-1578 (£0.292), Farnell 1100398 (£0.38) &  \\
\schpt{C289}–\schpt{C298} & 0.1μF ceramic capacitor & Farnell US 1694337 (£0.019@100), RS 721-5240 (£0.051@50), Farnell 9411887 (£0.062) &  \\
\schpt{C299} & 1μF capacitor & Farnell US 1600879 (£0.041@25), Farnell 3322210 (£0.148), RS 538-1578 (£0.292), Farnell 1100398 (£0.38) &  \\
\schpt{C300}–\schpt{C303} & 0.1μF ceramic capacitor & Farnell US 1694337 (£0.019@100), RS 721-5240 (£0.051@50), Farnell 9411887 (£0.062) &  \\
\schpt{C304} & 1 μF electrolytic capacitor & Farnell 1236655 (£0.034) & Through hole \\
\schpt{CON1}–\schpt{CON10} & 8x1 pin 2.54mm centre header & Farnell 1756826 (£0.122@10) + Farnell 3991271 (£0.179@10) & Molex KK® series header \\
\schpt{CON11}–\schpt{CON12} & DB9 male or 2×5 pin header & Farnell 1099289 (£0.48@5) &  \\
\schpt{CON13} & DB9 female or 2×5-pin header & Farnell 1099294 (£0.48@5) &  \\
\schpt{CON14}–\schpt{CON15} & 2x20 pin shrouded header & RS 670-1825 (£0.972@5), Farnell 1099261 (£1.07) & IDE socket \\
\schpt{CON16}–\schpt{CON19} & 8x1 pin 2.54mm centre header & Farnell 1756826 (£0.122@10) + Farnell 3991271 (£0.179@10) & Molex KK® series header \\
\schpt{CON20} & 9x1 pin 2.54mm centre header & \href{http://uk.farnell.com/jsp/search/productdetail.jsp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\%2FglobalsearchE14.jsp}{Farnell 1756827} & Molex KK® series header \\
\schpt{CON21}–\schpt{CON31} & 8x1 pin 2.54mm centre header & Farnell 1756826 (£0.122@10) + Farnell 3991271 (£0.179@10) & Molex KK® series header \\
\schpt{CON32} & 9x1 pin 2.54mm centre header & \href{http://uk.farnell.com/jsp/search/productdetail.jsp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\%2FglobalsearchE14.jsp}{Farnell 1756827} & Molex KK® series header \\
\schpt{CON33}–\schpt{CON37} & 8x1 pin 2.54mm centre header & Farnell 1756826 (£0.122@10) + Farnell 3991271 (£0.179@10) & Molex KK® series header \\
\schpt{D1} & 1N5817 Schottky barrier rectifier & Farnell 1843507 (£0.023) &  \\
\schpt{D2}–\schpt{D4} & 1N4148 diode & Farnell 9565124 (£0.011), RS 436-7341 (£0.003@100) & Or any fast signal diode \\
\schpt{EXP} & 96-pin (A+B+C) DIN-41612 Bauform ‘C’ plug & Farnell 1656159 (£1.84) & Right angle through hole \\
\schpt{FPPOWER} & Wago 2x screw clamp &  &  \\
\schpt{IC1} & 74HC253 Dual 4:1 multiplexer, 3-state & Farnell 1753491 (£0.28), RS 709-3046 (£0.147@10) &  \\
\schpt{IC2} & Dual J-K negative edge triggered FLIP FLOP, preset and clear & RS 663-1893 (£0.219@10), Farnell 1749804 (£0.39) &  \\
\schpt{IC3}–\schpt{IC4} & 74HC00 4× NAND gate & RS 169-6012 (£0.26), Farnell 9590889 (£0.38) &  \\
\schpt{IC5} & 74HC253 Dual 4:1 multiplexer, 3-state & Farnell 1753491 (£0.28), RS 709-3046 (£0.147@10) &  \\
\schpt{IC6} & Dual J-K negative edge triggered FLIP FLOP, preset and clear & RS 663-1893 (£0.219@10), Farnell 1749804 (£0.39) &  \\
\schpt{IC7} & 74HC00 4× NAND gate & RS 169-6012 (£0.26), Farnell 9590889 (£0.38) &  \\
\schpt{IC8} & LM556N Dual timer & Farnell 9488260 (£1.18), RS 536-0947 (£0.77@10) & May replace with 2×555 + 1×decoupling cap \\
\schpt{IC9} & 74HC14N Hex inverting Schmitt trigger & Farnell 7455513 (£0.133@10), RS 714-0899 (£0.164@20) &  \\
\schpt{IC10} & 74HC05 6× open drain inverter & Farnell 1470855 (£0.54), RS 442-921 (£0.52) &  \\
\schpt{IC11}–\schpt{IC12} & 74HC541N Octal 3-state buffer & RS 714-0953 (£0.18@20), Farnell 1470755 (£0.25@10) &  \\
\schpt{IC13} & 74HC590 8-bit registered binary counter & Farnell 1652001 (£0.52), RS 709-2523 (£0.236@5) &  \\
\schpt{IC14} & 74HC00 4× NAND gate & RS 169-6012 (£0.26), Farnell 9590889 (£0.38) &  \\
\schpt{IC15} & 41xx DEVICE & Farnell 380600 (£0.48), 380600 (£0.36@10), RS 709-2113 (£0.143@10) &  \\
\schpt{IC16}–\schpt{IC18} & 29x010 1 MBit (128k x 8) Flash RAM & Farnell 1907092 (£1.58) & May use '020 or '040 if not available. \\
\schpt{IC19}–\schpt{IC21} & 74HC541N Octal 3-state buffer & RS 714-0953 (£0.18@20), Farnell 1470755 (£0.25@10) &  \\
\schpt{IC22}–\schpt{IC23} & 74HC540N Octal 3-state inverting buffer & Farnell US 1163595 (£0.482), Farnell 1753515 (£0.60), Farnell 1753515 (£0.46@10), RS 714-7932 (£0.195@20), RS 443-249 (£0.61) &  \\
\schpt{IC24}–\schpt{IC25} & 74HC138N 3-to-8 line Decoder & Farnell US 1318508 (£0.172@10), RS 663-0036 (£0.267@10), Farnell 1826779 (£0.29) &  \\
\schpt{IC26} & 74HC32 4× OR gate & RS 709-3021 (£0.201@10), Farnell 1739939 (£0.27@10) &  \\
\schpt{IC27}–\schpt{IC28} & 74HC541N Octal 3-state buffer & RS 714-0953 (£0.18@20), Farnell 1470755 (£0.25@10) &  \\
\schpt{IC29} & 74HC32 4× OR gate & RS 709-3021 (£0.201@10), Farnell 1739939 (£0.27@10) &  \\
\schpt{IC30} & 74HC08 4× AND gate & RS 709-2845 (£0.201@10), Farnell 9665803 (£0.22@10) &  \\
\schpt{IC31} & Quad 2-input EXCLUSIVE-OR (XOR) gate & Farnell US 1075957 (£0.169), RS 169-7380 (£0.26) &  \\
\schpt{IC32} & 74HC32 4× OR gate & RS 709-3021 (£0.201@10), Farnell 1739939 (£0.27@10) &  \\
\schpt{IC33} & 74HC00 4× NAND gate & RS 169-6012 (£0.26), Farnell 9590889 (£0.38) &  \\
\schpt{IC34}–\schpt{IC35} & 1 of 8 data SELECTOR/MULTIPLEXER, 3-state & Farnell 9591320 (£0.22), Farnell 9591320 (£0.151@10), RS 663-0203 (£0.423@10) &  \\
\schpt{IC36} & Qadruple D type FLIP FLOP, clear & RS 169-7481 (£0.39), RS 663-0111 (£0.20@10) &  \\
\schpt{IC37} & 74HC374 Octal D-type transparent latch, positive edge triggered & RS 714-0931 (£0.191@20), RS 169-6141 (£0.38), Farnell 380763 (£0.57), Farnell 380763 (£0.38@10) &  \\
\schpt{IC38}–\schpt{IC39} & 74HC541N Octal 3-state buffer & RS 714-0953 (£0.18@20), Farnell 1470755 (£0.25@10) &  \\
\schpt{IC40}–\schpt{IC41} & Octal D type FLIP FLOP, clear & Farnell 9591397 (£0.34), RS 714-0925 (£0.175@20) &  \\
\schpt{IC42}–\schpt{IC43} & 74HC541N Octal 3-state buffer & RS 714-0953 (£0.18@20), Farnell 1470755 (£0.25@10) &  \\
\schpt{IC44} & 74HC08 4× AND gate & RS 709-2845 (£0.201@10), Farnell 9665803 (£0.22@10) &  \\
\schpt{IC45}–\schpt{IC46} & Octal D type FLIP FLOP, clear & Farnell 9591397 (£0.34), RS 714-0925 (£0.175@20) &  \\
\schpt{IC47}–\schpt{IC48} & 74HC541N Octal 3-state buffer & RS 714-0953 (£0.18@20), Farnell 1470755 (£0.25@10) &  \\
\schpt{IC49} & 74HC688 8-bit magnitude/identity comparator & RS 709-2179 (£0.168@5), Farnell 9591672 (£0.67@10) &  \\
\schpt{IC50}–\schpt{IC51} & 74HC541N Octal 3-state buffer & RS 714-0953 (£0.18@20), Farnell 1470755 (£0.25@10) &  \\
\schpt{IC52} & Dual J-K negative edge triggered FLIP FLOP, preset and clear & RS 663-1893 (£0.219@10), Farnell 1749804 (£0.39) &  \\
\schpt{IC53} & 74HC688 8-bit magnitude/identity comparator & RS 709-2179 (£0.168@5), Farnell 9591672 (£0.67@10) &  \\
\schpt{IC54} & 74HC138N 3-to-8 line Decoder & Farnell US 1318508 (£0.172@10), RS 663-0036 (£0.267@10), Farnell 1826779 (£0.29) &  \\
\schpt{IC55} & 74HC08 4× AND gate & RS 709-2845 (£0.201@10), Farnell 9665803 (£0.22@10) &  \\
\schpt{IC56} & 74HC32 4× OR gate & RS 709-3021 (£0.201@10), Farnell 1739939 (£0.27@10) &  \\
\schpt{IC57}–\schpt{IC59} & Dual J-K negative edge triggered FLIP FLOP, preset and clear & RS 663-1893 (£0.219@10), Farnell 1749804 (£0.39) &  \\
\schpt{IC60} & 74HC08 4× AND gate & RS 709-2845 (£0.201@10), Farnell 9665803 (£0.22@10) &  \\
\schpt{IC61}–\schpt{IC62} & 74HC245 Octal bus transceiver, 3-state & RS 714-0916 (£0.18@20), RS 169-6113 (£0.38), Farnell 380714 (£0.49) &  \\
\schpt{IC63}–\schpt{IC64} & 74HC541N Octal 3-state buffer & RS 714-0953 (£0.18@20), Farnell 1470755 (£0.25@10) &  \\
\schpt{IC65} & 74HC32 4× OR gate & RS 709-3021 (£0.201@10), Farnell 1739939 (£0.27@10) &  \\
\schpt{IC66} & 74HC04N Hex inverter & Farnell US 2374080 (£0.086), Farnell 9590951 (£0.38), Farnell 9590951 (£0.23@10), RS 714-0877 (£0.149@20), RS 662-9997 (£0.233@10) &  \\
\schpt{IC67}–\schpt{IC70} & Presettable Synchronous Binary Up/Down Counter & Farnell 1470793 (£0.34), RS 527-372 (£0.29@25) &  \\
\schpt{IC71}–\schpt{IC74} & 74HC541N Octal 3-state buffer & RS 714-0953 (£0.18@20), Farnell 1470755 (£0.25@10) &  \\
\schpt{IC75}–\schpt{IC78} & Presettable Synchronous Binary Up/Down Counter & Farnell 1470793 (£0.34), RS 527-372 (£0.29@25) &  \\
\schpt{IC79}–\schpt{IC82} & 74HC541N Octal 3-state buffer & RS 714-0953 (£0.18@20), Farnell 1470755 (£0.25@10) &  \\
\schpt{IC83}–\schpt{IC86} & Presettable Synchronous Binary Up/Down Counter & Farnell 1470793 (£0.34), RS 527-372 (£0.29@25) &  \\
\schpt{IC87}–\schpt{IC88} & 74HC541N Octal 3-state buffer & RS 714-0953 (£0.18@20), Farnell 1470755 (£0.25@10) &  \\
\schpt{IC89}–\schpt{IC90} & 74HC688 8-bit magnitude/identity comparator & RS 709-2179 (£0.168@5), Farnell 9591672 (£0.67@10) &  \\
\schpt{IC91} & 74HC04N Hex inverter & Farnell US 2374080 (£0.086), Farnell 9590951 (£0.38), Farnell 9590951 (£0.23@10), RS 714-0877 (£0.149@20), RS 662-9997 (£0.233@10) &  \\
\schpt{IC92}–\schpt{IC93} & 74HC541N Octal 3-state buffer & RS 714-0953 (£0.18@20), Farnell 1470755 (£0.25@10) &  \\
\schpt{IC94} & 74HC08 4× AND gate & RS 709-2845 (£0.201@10), Farnell 9665803 (£0.22@10) &  \\
\schpt{IC95} & 74HC00 4× NAND gate & RS 169-6012 (£0.26), Farnell 9590889 (£0.38) &  \\
\schpt{IC96} & 74HC32 4× OR gate & RS 709-3021 (£0.201@10), Farnell 1739939 (£0.27@10) &  \\
\schpt{IC97} & Dual J-K negative edge triggered FLIP FLOP, preset and clear & RS 663-1893 (£0.219@10), Farnell 1749804 (£0.39) &  \\
\schpt{IC98}–\schpt{IC99} & 74HC574 8-bit D Flip Flop bus driver & RS 714-0950 (£0.18@20), Farnell 380830 (£0.42@10) &  \\
\schpt{IC100} & 74HC32 4× OR gate & RS 709-3021 (£0.201@10), Farnell 1739939 (£0.27@10) &  \\
\schpt{IC101} & 74HC253 Dual 4:1 multiplexer, 3-state & Farnell 1753491 (£0.28), RS 709-3046 (£0.147@10) &  \\
\schpt{IC102} & 74HC138N 3-to-8 line Decoder & Farnell US 1318508 (£0.172@10), RS 663-0036 (£0.267@10), Farnell 1826779 (£0.29) &  \\
\schpt{IC103}–\schpt{IC104} & 74HC541N Octal 3-state buffer & RS 714-0953 (£0.18@20), Farnell 1470755 (£0.25@10) &  \\
\schpt{IC105}–\schpt{IC107} & 29x010 1 MBit (128k x 8) Flash RAM & Farnell 1907092 (£1.58) & May use '020 or '040 if not available. \\
\schpt{IC108} & 74HC08 4× AND gate & RS 709-2845 (£0.201@10), Farnell 9665803 (£0.22@10) &  \\
\schpt{IC109} & Dual D type positive edge triggered FLIP FLOP, preset and clear & Farnell 1013916 (£0.103), RS 714-0975 (£0.15@20) &  \\
\schpt{IC110}–\schpt{IC111} & 2-mbit (256x8) Flash memory in a PLCC32 package (with socket). AM29F020 is an example of this. & Farnell 8749493 (£2.84) / Farnell 1565992 & Using 040 due to lack of availability. \\
\schpt{IC112} & 29x010 1 MBit (128k x 8) Flash RAM & Farnell 1907092 (£1.58) & May use '020 or '040 if not available. \\
\schpt{IC113} & 74HC32 4× OR gate & RS 709-3021 (£0.201@10), Farnell 1739939 (£0.27@10) &  \\
\schpt{IC114}–\schpt{IC115} & 74HC138N 3-to-8 line Decoder & Farnell US 1318508 (£0.172@10), RS 663-0036 (£0.267@10), Farnell 1826779 (£0.29) &  \\
\schpt{IC116} & 74HC08 4× AND gate & RS 709-2845 (£0.201@10), Farnell 9665803 (£0.22@10) &  \\
\schpt{IC117} & Dual J-K negative edge triggered FLIP FLOP, preset and clear & RS 663-1893 (£0.219@10), Farnell 1749804 (£0.39) &  \\
\schpt{IC118}–\schpt{IC119} & 74HC670 4×4-bit register file, 3-state & Farnell 1753519 (£1.31), Farnell 1753520 (£0.77) & Cheaper order code is for SOIC (better stocks) \\
\schpt{IC120}–\schpt{IC121} & 74HC541N Octal 3-state buffer & RS 714-0953 (£0.18@20), Farnell 1470755 (£0.25@10) &  \\
\schpt{IC122}–\schpt{IC123} & 74HC670 4×4-bit register file, 3-state & Farnell 1753519 (£1.31), Farnell 1753520 (£0.77) & Cheaper order code is for SOIC (better stocks) \\
\schpt{IC124} & 74HC541N Octal 3-state buffer & RS 714-0953 (£0.18@20), Farnell 1470755 (£0.25@10) &  \\
\schpt{IC125} & Dual J-K negative edge triggered FLIP FLOP, preset and clear & RS 663-1893 (£0.219@10), Farnell 1749804 (£0.39) &  \\
\schpt{IC126} & 74HC138N 3-to-8 line Decoder & Farnell US 1318508 (£0.172@10), RS 663-0036 (£0.267@10), Farnell 1826779 (£0.29) &  \\
\schpt{IC127} & Dual J-K negative edge triggered FLIP FLOP, preset and clear & RS 663-1893 (£0.219@10), Farnell 1749804 (£0.39) &  \\
\schpt{IC128} & 74HC540N Octal 3-state inverting buffer & Farnell US 1163595 (£0.482), Farnell 1753515 (£0.60), Farnell 1753515 (£0.46@10), RS 714-7932 (£0.195@20), RS 443-249 (£0.61) &  \\
\schpt{IC129}–\schpt{IC131} & Dual J-K negative edge triggered FLIP FLOP, preset and clear & RS 663-1893 (£0.219@10), Farnell 1749804 (£0.39) &  \\
\schpt{IC132} & 74HC574 8-bit D Flip Flop bus driver & RS 714-0950 (£0.18@20), Farnell 380830 (£0.42@10) &  \\
\schpt{IC133} & 74HC08 4× AND gate & RS 709-2845 (£0.201@10), Farnell 9665803 (£0.22@10) &  \\
\schpt{IC134} & 74HC541N Octal 3-state buffer & RS 714-0953 (£0.18@20), Farnell 1470755 (£0.25@10) &  \\
\schpt{IC135} & 74HC08 4× AND gate & RS 709-2845 (£0.201@10), Farnell 9665803 (£0.22@10) &  \\
\schpt{IC136} & 74HC541N Octal 3-state buffer & RS 714-0953 (£0.18@20), Farnell 1470755 (£0.25@10) &  \\
\schpt{IC137} & 74HC138N 3-to-8 line Decoder & Farnell US 1318508 (£0.172@10), RS 663-0036 (£0.267@10), Farnell 1826779 (£0.29) &  \\
\schpt{IC138} & 29x040 4 MBit (512k x 8) Flash RAM & Farnell 8749493 (£2.84) / Farnell 1565992 &  \\
\schpt{IC139} & 4 MBit (512k x 8) Static RAM & Farnell 1562900 (£4.71) &  \\
\schpt{IC140} & 29x040 4 MBit (512k x 8) Flash RAM & Farnell 8749493 (£2.84) / Farnell 1565992 &  \\
\schpt{IC141} & 4 MBit (512k x 8) Static RAM & Farnell 1562900 (£4.71) &  \\
\schpt{IC142} & 74HC540N Octal 3-state inverting buffer & Farnell US 1163595 (£0.482), Farnell 1753515 (£0.60), Farnell 1753515 (£0.46@10), RS 714-7932 (£0.195@20), RS 443-249 (£0.61) &  \\
\schpt{IC143} & 74HC138N 3-to-8 line Decoder & Farnell US 1318508 (£0.172@10), RS 663-0036 (£0.267@10), Farnell 1826779 (£0.29) &  \\
\schpt{IC144}–\schpt{IC145} & 26C92 Dual UART & Farnell 1294820 (£2.18), RS 821-756 (£5) &  \\
\schpt{IC146}–\schpt{IC148} & MAX-232 RS-232 transceiver & Farnell 1648737 (£0.73), RS 660-8613 (£0.68@5) &  \\
\schpt{IC149} & 74HC138N 3-to-8 line Decoder & Farnell US 1318508 (£0.172@10), RS 663-0036 (£0.267@10), Farnell 1826779 (£0.29) &  \\
\schpt{IC150} & 74HC05 6× open drain inverter & Farnell 1470855 (£0.54), RS 442-921 (£0.52) &  \\
\schpt{IC151}–\schpt{IC152} & 74HC245 Octal bus transceiver, 3-state & RS 714-0916 (£0.18@20), RS 169-6113 (£0.38), Farnell 380714 (£0.49) &  \\
\schpt{IC153} & 74HC14N Hex inverting Schmitt trigger & Farnell 7455513 (£0.133@10), RS 714-0899 (£0.164@20) &  \\
\schpt{IC154} & 74HC138N 3-to-8 line Decoder & Farnell US 1318508 (£0.172@10), RS 663-0036 (£0.267@10), Farnell 1826779 (£0.29) &  \\
\schpt{IC155} & 74HC374 Octal D-type transparent latch, positive edge triggered & RS 714-0931 (£0.191@20), RS 169-6141 (£0.38), Farnell 380763 (£0.57), Farnell 380763 (£0.38@10) &  \\
\schpt{IC156} & 74HC138N 3-to-8 line Decoder & Farnell US 1318508 (£0.172@10), RS 663-0036 (£0.267@10), Farnell 1826779 (£0.29) &  \\
\schpt{IC157}–\schpt{IC158} & 74HC374 Octal D-type transparent latch, positive edge triggered & RS 714-0931 (£0.191@20), RS 169-6141 (£0.38), Farnell 380763 (£0.57), Farnell 380763 (£0.38@10) &  \\
\schpt{IC159} & 74HC32 4× OR gate & RS 709-3021 (£0.201@10), Farnell 1739939 (£0.27@10) &  \\
\schpt{IC160} & 74HC03N Quad 2-input NAND gate, open collector output & Farnell 1282849 (£0.17) &  \\
\schpt{IC161} & 74HC32 4× OR gate & RS 709-3021 (£0.201@10), Farnell 1739939 (£0.27@10) &  \\
\schpt{IC162} & 5V, 16 kbit (2k×8) NVRAM & RTC & Farnell 1224444 (£13.14) &  \\
\schpt{IC163}–\schpt{IC164} & Dual 4-line to 1-line data SELECTOR/MULTIPLEXER & RS 443-075 (£0.50), Farnell 1753485 (£0.56) &  \\
\schpt{IC165}–\schpt{IC166} & Intersil 82C54 Programmable Timer & Farnell 1018175 (£6.69), RS 496-688 (£6.71) &  \\
\schpt{IC167} & 74HC14N Hex inverting Schmitt trigger & Farnell 7455513 (£0.133@10), RS 714-0899 (£0.164@20) &  \\
\schpt{IC168} & 74LS123N Dual retriggerable monostable multivibrator & RS 307-632 (£0.61), Farnell 1470902 (£0.64), RS 368-6001 (£0.43@25) &  \\
\schpt{IC169} & LM555N Timer & RS 534-3469 (£0.62), Farnell 1564692 (£0.52@10) &  \\
\schpt{IC170} & 74HC04N Hex inverter & Farnell US 2374080 (£0.086), Farnell 9590951 (£0.38), Farnell 9590951 (£0.23@10), RS 714-0877 (£0.149@20), RS 662-9997 (£0.233@10) &  \\
\schpt{IC171} & 74HCT00N Quad 2-input NAND gate & RS 217-5702 (£0.14), Farnell US 2373749 (£0.125), Farnell 9591745 (£0.24) &  \\
\schpt{IC172} & 74HC373 Octal D-type transparent latch, negative edge triggered & RS 714-0922 (£0.182@20), Farnell 1607705 (£0.52@10) &  \\
\schpt{IC173}–\schpt{IC174} & 74HC14N Hex inverting Schmitt trigger & Farnell 7455513 (£0.133@10), RS 714-0899 (£0.164@20) &  \\
\schpt{IC175}–\schpt{IC176} & 74HC04N Hex inverter & Farnell US 2374080 (£0.086), Farnell 9590951 (£0.38), Farnell 9590951 (£0.23@10), RS 714-0877 (£0.149@20), RS 662-9997 (£0.233@10) &  \\
\schpt{IC177} & 74HC14N Hex inverting Schmitt trigger & Farnell 7455513 (£0.133@10), RS 714-0899 (£0.164@20) &  \\
\schpt{IC178} & 74HC04N Hex inverter & Farnell US 2374080 (£0.086), Farnell 9590951 (£0.38), Farnell 9590951 (£0.23@10), RS 714-0877 (£0.149@20), RS 662-9997 (£0.233@10) &  \\
\schpt{IC179} & 74HC03N Quad 2-input NAND gate, open collector output & Farnell 1282849 (£0.17) &  \\
\schpt{IC180} & 74LS123N Dual retriggerable monostable multivibrator & RS 307-632 (£0.61), Farnell 1470902 (£0.64), RS 368-6001 (£0.43@25) &  \\
\schpt{IC181} & 74HC138N 3-to-8 line Decoder & Farnell US 1318508 (£0.172@10), RS 663-0036 (£0.267@10), Farnell 1826779 (£0.29) &  \\
\schpt{IC182}–\schpt{IC187} & 74HC541N Octal 3-state buffer & RS 714-0953 (£0.18@20), Farnell 1470755 (£0.25@10) &  \\
\schpt{IC188} & 74HC85N 4-bit Magnitude Comparator & Farnell US 1387859 (£0.543), Farnell 380489 (£0.61), RS 527-801 (£0.544@25) &  \\
\schpt{IC189}–\schpt{IC192} & 74LS123N Dual retriggerable monostable multivibrator & RS 307-632 (£0.61), Farnell 1470902 (£0.64), RS 368-6001 (£0.43@25) &  \\
\schpt{IC193} & 74HC138N 3-to-8 line Decoder & Farnell US 1318508 (£0.172@10), RS 663-0036 (£0.267@10), Farnell 1826779 (£0.29) &  \\
\schpt{IC194}–\schpt{IC195} & 74HC541N Octal 3-state buffer & RS 714-0953 (£0.18@20), Farnell 1470755 (£0.25@10) &  \\
\schpt{IC196}–\schpt{IC197} & 74HC138N 3-to-8 line Decoder & Farnell US 1318508 (£0.172@10), RS 663-0036 (£0.267@10), Farnell 1826779 (£0.29) &  \\
\schpt{IC198}–\schpt{IC199} & 74HC574 8-bit D Flip Flop bus driver & RS 714-0950 (£0.18@20), Farnell 380830 (£0.42@10) &  \\
\schpt{IC200}–\schpt{IC201} & Dual 4-input AND gate & Farnell 1740011 (£0.23), RS 709-2665 (£0.163@20) &  \\
\schpt{IC202}–\schpt{IC203} & 74HC541N Octal 3-state buffer & RS 714-0953 (£0.18@20), Farnell 1470755 (£0.25@10) &  \\
\schpt{IC204} & 74HC00 4× NAND gate & RS 169-6012 (£0.26), Farnell 9590889 (£0.38) &  \\
\schpt{IC205} & Dual J-K negative edge triggered FLIP FLOP, preset and clear & RS 663-1893 (£0.219@10), Farnell 1749804 (£0.39) &  \\
\schpt{IC206} & 74HC03N Quad 2-input NAND gate, open collector output & Farnell 1282849 (£0.17) &  \\
\schpt{IC207}–\schpt{IC208} & 74HC00 4× NAND gate & RS 169-6012 (£0.26), Farnell 9590889 (£0.38) &  \\
\schpt{IC209} & Dual 4-input AND gate & Farnell 1740011 (£0.23), RS 709-2665 (£0.163@20) &  \\
\schpt{IC210}–\schpt{IC211} & 74LS123N Dual retriggerable monostable multivibrator & RS 307-632 (£0.61), Farnell 1470902 (£0.64), RS 368-6001 (£0.43@25) &  \\
\schpt{IC212} & 74HC08 4× AND gate & RS 709-2845 (£0.201@10), Farnell 9665803 (£0.22@10) &  \\
\schpt{IC213}–\schpt{IC214} & Quad 2-input OR gate & Farnell 1013995 (£0.109), RS 156-9651 (£0.26) &  \\
\schpt{IC215}–\schpt{IC216} & Quad bus BUFFER, 3-state & Farnell 9591036 (£0.48), RS 709-2009 (£0.21@10), RS 169-7403 (£0.32) &  \\
\schpt{IC217} & Octal BUFFER and LINE DRIVER, 3-state & Farnell 382425 (£0.50), RS 169-7908 (£0.39) &  \\
\schpt{J1}–\schpt{J4} & 3-pin 2.54mm header & RS 251-8092 (£0.078@25) &  \\
\schpt{JP1} & JUMPER &  &  \\
\schpt{JP2} & PIN HEADER &  &  \\
\schpt{JP3} & JUMPER &  &  \\
\schpt{JP4} & 2×20-pin shrouded/keyed header & RS 670-1825 (£0.972@5), Farnell 1099261 (£1.07) &  \\
\schpt{JP5}–\schpt{JP8} & 3-pin 2.54mm header & RS 251-8092 (£0.078@25) &  \\
\schpt{JP9}–\schpt{JP10} & 2-pin 2.54mm header & RS 251-8086 (£0.046@25) &  \\
\schpt{JP11}–\schpt{JP15} & 3-pin 2.54mm header & RS 251-8092 (£0.078@25) &  \\
\schpt{JP16} & 2×20-pin shrouded/keyed header & RS 670-1825 (£0.972@5), Farnell 1099261 (£1.07) &  \\
\schpt{LED1}–\schpt{LED13} & 5mm green LED & RS 228-6004 (£0.042), Farnell 1855549 (£0.42) &  \\
\schpt{LED14}–\schpt{LED22} & 5mm red LED & RS 228-5988 (£0.042@5), Farnell 1581217 (£0.165) &  \\
\schpt{LED23}–\schpt{LED25} & 5mm green LED & RS 228-6004 (£0.042), Farnell 1855549 (£0.42) &  \\
\schpt{LED26}–\schpt{LED43} & 5mm red LED & RS 228-5988 (£0.042@5), Farnell 1581217 (£0.165) &  \\
\schpt{LED44}–\schpt{LED51} & 5mm amber/orange/yellow LED & RS 228-6010 (£0.042), Farnell 1142581 (£0.21) &  \\
\schpt{LED52} & 5mm green LED & RS 228-6004 (£0.042), Farnell 1855549 (£0.42) &  \\
\schpt{LED53}–\schpt{LED78} & 5mm red LED & RS 228-5988 (£0.042@5), Farnell 1581217 (£0.165) &  \\
\schpt{LED79} & 5mm amber/orange/yellow LED & RS 228-6010 (£0.042), Farnell 1142581 (£0.21) &  \\
\schpt{LED80} & 5mm red LED & RS 228-5988 (£0.042@5), Farnell 1581217 (£0.165) &  \\
\schpt{LED81}–\schpt{LED84} & 5mm amber/orange/yellow LED & RS 228-6010 (£0.042), Farnell 1142581 (£0.21) &  \\
\schpt{LED85}–\schpt{LED88} & 5mm green LED & RS 228-6004 (£0.042), Farnell 1855549 (£0.42) &  \\
\schpt{LED89}–\schpt{LED91} & 5mm red LED & RS 228-5988 (£0.042@5), Farnell 1581217 (£0.165) &  \\
\schpt{LED92}–\schpt{LED95} & 5mm amber/orange/yellow LED & RS 228-6010 (£0.042), Farnell 1142581 (£0.21) &  \\
\schpt{LED96} & 5mm red LED & RS 228-5988 (£0.042@5), Farnell 1581217 (£0.165) &  \\
\schpt{LED97}–\schpt{LED100} & 5mm amber/orange/yellow LED & RS 228-6010 (£0.042), Farnell 1142581 (£0.21) &  \\
\schpt{LED101}–\schpt{LED103} & 5mm red LED & RS 228-5988 (£0.042@5), Farnell 1581217 (£0.165) &  \\
\schpt{LED104}–\schpt{LED105} & 5mm amber/orange/yellow LED & RS 228-6010 (£0.042), Farnell 1142581 (£0.21) &  \\
\schpt{LED106} & 5mm green LED & RS 228-6004 (£0.042), Farnell 1855549 (£0.42) &  \\
\schpt{LED107} & 5mm red LED & RS 228-5988 (£0.042@5), Farnell 1581217 (£0.165) &  \\
\schpt{LED108} & 5mm amber/orange/yellow LED & RS 228-6010 (£0.042), Farnell 1142581 (£0.21) &  \\
\schpt{LED109}–\schpt{LED114} & 5mm green LED & RS 228-6004 (£0.042), Farnell 1855549 (£0.42) &  \\
\schpt{LED115} & 5mm red LED & RS 228-5988 (£0.042@5), Farnell 1581217 (£0.165) &  \\
\schpt{LED116}–\schpt{LED118} & 5mm amber/orange/yellow LED & RS 228-6010 (£0.042), Farnell 1142581 (£0.21) &  \\
\schpt{LED119}–\schpt{LED121} & 5mm green LED & RS 228-6004 (£0.042), Farnell 1855549 (£0.42) &  \\
\schpt{LED122}–\schpt{LED145} & 5mm red LED & RS 228-5988 (£0.042@5), Farnell 1581217 (£0.165) &  \\
\schpt{LED146}–\schpt{LED153} & 5mm green LED & RS 228-6004 (£0.042), Farnell 1855549 (£0.42) &  \\
\schpt{P1} & 8x1 2.54mm female wirewrap header &  & Or other stackable \\
\schpt{P2} & 6x1 2.54mm female wirewrap header &  & Or other stackable \\
\schpt{P3} & 8x1 2.54mm female wirewrap header &  & Or other stackable \\
\schpt{P4}–\schpt{P7} & 6x1 2.54mm female wirewrap header &  & Or other stackable \\
\schpt{R1}–\schpt{R4} & 47kΩ resistor, 0.25W & RS 131-334 (£0.014@10), Farnell 9339540 (£0.011@50) &  \\
\schpt{R5} & 330Ω resistor, 0.25W & RS 707-7622 (£0.014@10), Farnell 9339418 (£0.011@50) &  \\
\schpt{R6} & 470Ω resistor, 0.25W & RS 131-211 (£0.014@10), Farnell 9339531 (£0.011@50) &  \\
\schpt{R7} & 47kΩ resistor, 0.25W & RS 131-334 (£0.014@10), Farnell 9339540 (£0.011@50) &  \\
\schpt{R8} & 100Ω resistor, 0.25W & RS 131-132 (£0.014@10), Farnell 9339043 (£0.011@50) &  \\
\schpt{R9} & 1kΩ resistor, 0.25W & RS 131-255 (£0.014@10), Farnell 9339051 (£0.011@50) &  \\
\schpt{R10} & 50kΩ resistor, 0.25W & RS 131-457 (£0.014@10), Farnell 9339558 (£0.011@50) & Actually 47kΩ (cheaper) \\
\schpt{R11} & 330Ω resistor, 0.25W & RS 707-7622 (£0.014@10), Farnell 9339418 (£0.011@50) &  \\
\schpt{R12}–\schpt{R18} & 47kΩ resistor, 0.25W & RS 131-334 (£0.014@10), Farnell 9339540 (£0.011@50) &  \\
\schpt{R19}–\schpt{R24} & 47Ω resistor, 0.25W & RS 131-097 (£0.014@10), Farnell 9339523 (£0.011@50) &  \\
\schpt{R25}–\schpt{R27} & 47kΩ resistor, 0.25W & RS 131-334 (£0.014@10), Farnell 9339540 (£0.011@50) &  \\
\schpt{R28}–\schpt{R29} & 330Ω resistor, 0.25W & RS 707-7622 (£0.014@10), Farnell 9339418 (£0.011@50) &  \\
\schpt{R30}–\schpt{R34} & 47kΩ resistor, 0.25W & RS 131-334 (£0.014@10), Farnell 9339540 (£0.011@50) &  \\
\schpt{R35}–\schpt{R39} & 330Ω resistor, 0.25W & RS 707-7622 (£0.014@10), Farnell 9339418 (£0.011@50) &  \\
\schpt{R40}–\schpt{R42} & 1MΩ resistor 0.25W & RS 131-615 (£0.014@10), Farnell 9339086 (£0.011@50) &  \\
\schpt{R43}–\schpt{R44} & 47kΩ resistor, 0.25W & RS 131-334 (£0.014@10), Farnell 9339540 (£0.011@50) &  \\
\schpt{R45}–\schpt{R46} & 330Ω resistor, 0.25W & RS 707-7622 (£0.014@10), Farnell 9339418 (£0.011@50) &  \\
\schpt{R47} & 10MΩ resistor, 0.25W & RS 135-667 (£0.014@10), Farnell 1186248 (£0.012@50) &  \\
\schpt{R48} & 300kΩ resistor, 0.25W & RS 707-7864 (£0.015@10), Farnell 9341714 (£0.025@50) &  \\
\schpt{R49}–\schpt{R50} & 47kΩ resistor, 0.25W & RS 131-334 (£0.014@10), Farnell 9339540 (£0.011@50) &  \\
\schpt{R51} & 200k linear potentiometer/trimmer & \href{http://uk.farnell.com/jsp/search/productdetail.jsp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\%2FglobalsearchE14.jsp}{Farnell 1689846} &  \\
\schpt{R52} & 180kΩ resistor, 0.25W & RS 131-520 (£0.014@10), Farnell 9339264 (£0.011@50) &  \\
\schpt{R53} & 1kΩ resistor, 0.25W & RS 131-255 (£0.014@10), Farnell 9339051 (£0.011@50) &  \\
\schpt{R54} & 200k linear potentiometer/trimmer & \href{http://uk.farnell.com/jsp/search/productdetail.jsp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\%2FglobalsearchE14.jsp}{Farnell 1689846} &  \\
\schpt{R55} & 330Ω resistor, 0.25W & RS 707-7622 (£0.014@10), Farnell 9339418 (£0.011@50) &  \\
\schpt{R56} & 300kΩ resistor, 0.25W & RS 707-7864 (£0.015@10), Farnell 9341714 (£0.025@50) &  \\
\schpt{R57} & 47kΩ resistor, 0.25W & RS 131-334 (£0.014@10), Farnell 9339540 (£0.011@50) &  \\
\schpt{R58}–\schpt{R65} & 300kΩ resistor, 0.25W & RS 707-7864 (£0.015@10), Farnell 9341714 (£0.025@50) &  \\
\schpt{R66} & 47kΩ resistor, 0.25W & RS 131-334 (£0.014@10), Farnell 9339540 (£0.011@50) &  \\
\schpt{R67} & 1kΩ resistor, 0.25W & RS 131-255 (£0.014@10), Farnell 9339051 (£0.011@50) &  \\
\schpt{R68}–\schpt{R69} & 47kΩ resistor, 0.25W & RS 131-334 (£0.014@10), Farnell 9339540 (£0.011@50) &  \\
\schpt{R70} & 1kΩ resistor, 0.25W & RS 131-255 (£0.014@10), Farnell 9339051 (£0.011@50) &  \\
\schpt{RN1} & 8×4.7kΩ resistor network & Farnell US 1602072 (£0.036@10), RS 522-4289 (£0.31@25) &  \\
\schpt{RN2} & SIL RESISTOR & Farnell 1973120 (£0.065@10) & Using 5-element (G05R) part. \\
\schpt{RN3} & 5×4.7kΩ resistor network & Farnell 1973120 (£0.065@10) &  \\
\schpt{RN4} & 3×4.7kΩ resistor network & Farnell 9356347 (£0.24@5) &  \\
\schpt{RN5}–\schpt{RN7} & 8×4.7kΩ resistor network & Farnell US 1602072 (£0.036@10), RS 522-4289 (£0.31@25) &  \\
\schpt{RN8} & 7×4.7kΩ resistor network & Farnell 1973129 (£0.085@10) &  \\
\schpt{RN9}–\schpt{RN12} & 8×330Ω resistor, DIL packaged & RS 707-7622 (£0.014@10), Farnell 9339418 (£0.011@50) & Discretes used for protytping. \\
\schpt{RN13} & 8×4.7kΩ resistor network & Farnell US 1602072 (£0.036@10), RS 522-4289 (£0.31@25) &  \\
\schpt{RN14}–\schpt{RN15} & 8×330Ω resistor network & Farnell 9356975 (£0.30@5) &  \\
\schpt{RN16}–\schpt{RN17} & 8×4.7kΩ resistor network & Farnell US 1602072 (£0.036@10), RS 522-4289 (£0.31@25) &  \\
\schpt{RN18} & 7×4.7kΩ resistor network & Farnell 1973129 (£0.085@10) &  \\
\schpt{RN19} & 8×10kΩ resistor network & Farnell 1973130 (£0.085@10) &  \\
\schpt{RN20} & 8×50kΩ resistor network & RS 131-457 (£0.014@10), Farnell 9339558 (£0.011@50) & Uses 47kΩ discretes for prototyping. \\
\schpt{RN21} & 8×10kΩ resistor network & Farnell 1973130 (£0.085@10) &  \\
\schpt{RN22} & 8×50kΩ resistor network & RS 131-457 (£0.014@10), Farnell 9339558 (£0.011@50) & Uses 47kΩ discretes for prototyping. \\
\schpt{RN23} & 10kΩ 6x bussed SIL resistor & \href{http://uk.farnell.com/jsp/search/productdetail.jsp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\%2FglobalsearchE14.jsp}{Farnell 1973163} &  \\
\schpt{RN24} & 8×50kΩ resistor network & RS 131-457 (£0.014@10), Farnell 9339558 (£0.011@50) & Uses 47kΩ discretes for prototyping. \\
\schpt{RN25}–\schpt{RN31} & 8×330Ω resistor network & Farnell 1602072 (£0.041), RS 522-4289 (£0.31@25) &  \\
\schpt{RN32} & 180Ω 8x bussed SIL resistor & \href{http://uk.farnell.com/jsp/search/productdetail.jsp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\%2FglobalsearchE14.jsp}{Farnell 9356843} &  \\
\schpt{RN33}–\schpt{RN36} & 8×330Ω resistor network & Farnell 1602072 (£0.041), RS 522-4289 (£0.31@25) &  \\
\schpt{RN37}–\schpt{RN40} & 8×4.7kΩ resistor network & Farnell US 1602072 (£0.036@10), RS 522-4289 (£0.31@25) &  \\
\schpt{RN41} & 3×4.7kΩ resistor network & Farnell 9356347 (£0.24@5) &  \\
\schpt{RN42}–\schpt{RN43} & 8×4.7kΩ resistor network & Farnell US 1602072 (£0.036@10), RS 522-4289 (£0.31@25) &  \\
\schpt{RN44}–\schpt{RN45} & 8×330Ω resistor network & Farnell 1602072 (£0.041), RS 522-4289 (£0.31@25) &  \\
\schpt{RN46}–\schpt{RN47} & 8×330Ω resistor network & Farnell 9356975 (£0.30@5) &  \\
\schpt{RN48}–\schpt{RN51} & 8×4.7kΩ resistor network & Farnell US 1602072 (£0.036@10), RS 522-4289 (£0.31@25) &  \\
\schpt{RV1} & 470Ω linear potentiometer & Farnell 1227517 (£0.24) &  \\
\schpt{RV2} & 4.7kΩ linear potentiometer & Farnell 1227523 (£0.23) &  \\
\schpt{S1} & Tactile switch & Farnell 1813689 (£0.185) &  \\
\schpt{S2}–\schpt{S17} & On-On toggle switch &  & Switch body and separate black/red actuators \\
\schpt{S18} & Double-pole 3-position key switch & \href{http://uk.rs-online.com/web/p/products/2195835/}{RS 219-5835}, \href{http://uk.rs-online.com/web/p/products/6932284/}{RS 693-2284} & Make-before-break \\
\schpt{S19}–\schpt{S20} & On-On toggle switch &  & Switch body and separate black/red actuators \\
\schpt{S21} & On-Off-On toggle switch & \href{http://uk.farnell.com/jsp/search/productdetail.jsp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\%2FglobalsearchE14.jsp}{Farnell 9473807} & Also add lever actuator \\
\schpt{S22} & Mom-Off-Mom toggle switch & \href{http://uk.farnell.com/jsp/search/productdetail.jsp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\%2FglobalsearchE14.jsp}{Farnell 9473769} &  \\
\schpt{S23} & Mom-Off-Mom toggle switch & \href{http://uk.farnell.com/jsp/search/productdetail.jsp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\%2FglobalsearchE14.jsp}{Farnell 9473815} &  \\
\schpt{S24}–\schpt{S25} & Mom-Off-Mom toggle switch & \href{http://uk.farnell.com/jsp/search/productdetail.jsp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\%2FglobalsearchE14.jsp}{Farnell 9473769} &  \\
\schpt{S26}–\schpt{S29} & Mom-Off-Mom toggle switch & \href{http://uk.farnell.com/jsp/search/productdetail.jsp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\%2FglobalsearchE14.jsp}{Farnell 9473815} &  \\
\schpt{S30} & On-Off-On toggle switch & \href{http://uk.farnell.com/jsp/search/productdetail.jsp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\%2FglobalsearchE14.jsp}{Farnell 9473807} & Also add lever actuator \\
\schpt{S31}–\schpt{S32} & Mom-Off-Mom toggle switch & \href{http://uk.farnell.com/jsp/search/productdetail.jsp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\%2FglobalsearchE14.jsp}{Farnell 9473769} &  \\
\schpt{SV1}–\schpt{SV10} & PIN HEADER &  &  \\
\schpt{SV11} & 3x2 pin header &  &  \\
\schpt{SW1} & 3x dip switch or 2x3 pin header & \href{http://uk.farnell.com/jsp/search/productdetail.jsp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\%2FglobalsearchE14.jsp}{Farnell 1522004} &  \\
\schpt{SW2}–\schpt{SW3} & 8-way DIP switch & RS 712-2576 (£0.50), Farnell 9471596 (£0.66) & Through hole \\
\schpt{X2} & WAGO SCREW CLAMP &  &  \\
\schpt{XTAL1} & 16 MHz & RS 547-5487 (£1.43) Farnell 7942710 (£1.54) & May need to reduce frequency. 4 MHz: RS 547-5392. 10 MHz: 547-5421. 12 MHz: RS 547-5459 \\
\schpt{XTAL2} & 3.6864 MHz oscillator & RS 547-5386 (£1.53), Farnell 9510095 (£2.94) & For RS-232 interfaces \\
