alexiosc/cft/documentation/latex/assembler_guide/cft-bom-values.tex

207$\times$ & 0.1μF ceramic capacitor & \schpt{C1}–\schpt{C9}, \schpt{C11}–\schpt{C14}, \schpt{C17}–\schpt{C21}, \schpt{C23}–\schpt{C28}, \schpt{C33}–\schpt{C37}, \schpt{C39}–\schpt{C46}, \schpt{C48}–\schpt{C50}, \schpt{C52}–\schpt{C55}, \schpt{C57}–\schpt{C65}, \schpt{C67}–\schpt{C71}, \schpt{C73}–\schpt{C77}, \schpt{C79}–\schpt{C86}, \schpt{C88}–\schpt{C95}, \schpt{C97}–\schpt{C106}, \schpt{C108}–\schpt{C111}, \schpt{C113}–\schpt{C116}, \schpt{C118}–\schpt{C122}, \schpt{C127}–\schpt{C129}, \schpt{C134}–\schpt{C145}, \schpt{C147}–\schpt{C158}, \schpt{C160}–\schpt{C165}, \schpt{C171}, \schpt{C173}, \schpt{C191}–\schpt{C195}, \schpt{C198}–\schpt{C211}, \schpt{C215}–\schpt{C220}, \schpt{C239}–\schpt{C240}, \schpt{C245}–\schpt{C247}, \schpt{C250}–\schpt{C256}, \schpt{C258}–\schpt{C261}, \schpt{C272}–\schpt{C281}, \schpt{C283}–\schpt{C287}, \schpt{C289}–\schpt{C298}, \schpt{C300}–\schpt{C303} & Farnell US 1694337 (£0.019@100), RS 721-5240 (£0.051@50), Farnell 9411887 (£0.062) &  \\
57$\times$ & 1μF capacitor & \schpt{C10}, \schpt{C22}, \schpt{C29}–\schpt{C32}, \schpt{C38}, \schpt{C47}, \schpt{C51}, \schpt{C56}, \schpt{C66}, \schpt{C72}, \schpt{C78}, \schpt{C87}, \schpt{C96}, \schpt{C107}, \schpt{C112}, \schpt{C117}, \schpt{C123}–\schpt{C126}, \schpt{C130}–\schpt{C133}, \schpt{C146}, \schpt{C159}, \schpt{C166}–\schpt{C170}, \schpt{C172}, \schpt{C174}–\schpt{C175}, \schpt{C196}–\schpt{C197}, \schpt{C214}, \schpt{C221}, \schpt{C229}–\schpt{C230}, \schpt{C248}–\schpt{C249}, \schpt{C257}, \schpt{C262}–\schpt{C270}, \schpt{C282}, \schpt{C288}, \schpt{C299} & Farnell US 1600879 (£0.041@25), Farnell 3322210 (£0.148), RS 538-1578 (£0.292), Farnell 1100398 (£0.38) &  \\
2$\times$ & 10µF electrolytic capacitor & \schpt{C15}–\schpt{C16} & Farnell 1902928 (£0.033), RS 440-6547 (£0.026@50) &  \\
13$\times$ & 1 μF electrolytic capacitor & \schpt{C176}–\schpt{C187}, \schpt{C304} & Farnell 1236655 (£0.034) & Through hole \\
3$\times$ & 10 µF electrolytic capacitor & \schpt{C188}–\schpt{C190} & Farnell 1902928 (£0.033), RS 440-6547 (£0.026@50) &  \\
2$\times$ & 22 pF ceramic capacitor & \schpt{C212}–\schpt{C213} & Farnell 9411674 (£0.035@25) &  \\
1$\times$ & 100uF Electrolytic capacitor & \schpt{C222} & \href{http://uk.farnell.com/jsp/search/productdetail.jsp?\_dyncharset=UTF-8&searchTerms=1902882&\_D%3AsearchTerms=+&%2Fpf%2Fsearch%2FTextSearchFormHandler.search=GO&\_D%3A%2Fpf%2Fsearch%2FTextSearchFormHandler.search=+&s=&%2Fpf%2Fsearch%2FTextSearchFormHandler.suggestions=false&\_D%3A%2Fpf%2Fsearch%2FTextSearchFormHandler.suggestions=+&%2Fpf%2Fsearch%2FTextSearchFormHandler.ref=globalsearch&\_D%3A%2Fpf%2Fsearch%2FTextSearchFormHandler.ref=+&\_D%3ArohsVal=+&%2Fpf%2Fsearch%2FTextSearchFormHandler.onlyRoHSProductsActive=true&\_D%3A%2Fpf%2Fsearch%2FTextSearchFormHandler.onlyRoHSProductsActive=+&\_DARGS=%2Fjsp%2Fcommonfragments\%2FglobalsearchE14.jsp}{Farnell 1902882} &  \\
16$\times$ & 1μF electrolytic capacitor & \schpt{C223}–\schpt{C226}, \schpt{C231}–\schpt{C238}, \schpt{C241}–\schpt{C244} & Farnell 1236655 (£0.034) &  \\
1$\times$ & 22nF capacitor & \schpt{C227} & \href{http://uk.farnell.com/jsp/search/productdetail.jsp?\_dyncharset=UTF-8&searchTerms=9411860&\_D%3AsearchTerms=+&%2Fpf%2Fsearch%2FTextSearchFormHandler.search=GO&\_D%3A%2Fpf%2Fsearch%2FTextSearchFormHandler.search=+&s=&%2Fpf%2Fsearch%2FTextSearchFormHandler.suggestions=false&\_D%3A%2Fpf%2Fsearch%2FTextSearchFormHandler.suggestions=+&%2Fpf%2Fsearch%2FTextSearchFormHandler.ref=globalsearch&\_D%3A%2Fpf%2Fsearch%2FTextSearchFormHandler.ref=+&\_D%3ArohsVal=+&%2Fpf%2Fsearch%2FTextSearchFormHandler.onlyRoHSProductsActive=true&\_D%3A%2Fpf%2Fsearch%2FTextSearchFormHandler.onlyRoHSProductsActive=+&\_DARGS=%2Fjsp%2Fcommonfragments\%2FglobalsearchE14.jsp}{Farnell 9411860} &  \\
1$\times$ & 4.7μF Electrolytic capacitor & \schpt{C228} & \href{http://uk.farnell.com/jsp/search/productdetail.jsp?\_dyncharset=UTF-8&searchTerms=1902916&\_D%3AsearchTerms=+&%2Fpf%2Fsearch%2FTextSearchFormHandler.search=GO&\_D%3A%2Fpf%2Fsearch%2FTextSearchFormHandler.search=+&s=&%2Fpf%2Fsearch%2FTextSearchFormHandler.suggestions=false&\_D%3A%2Fpf%2Fsearch%2FTextSearchFormHandler.suggestions=+&%2Fpf%2Fsearch%2FTextSearchFormHandler.ref=globalsearch&\_D%3A%2Fpf%2Fsearch%2FTextSearchFormHandler.ref=+&\_D%3ArohsVal=+&%2Fpf%2Fsearch%2FTextSearchFormHandler.onlyRoHSProductsActive=true&\_D%3A%2Fpf%2Fsearch%2FTextSearchFormHandler.onlyRoHSProductsActive=+&\_DARGS=%2Fjsp%2Fcommonfragments\%2FglobalsearchE14.jsp}{Farnell 1902916} &  \\
1$\times$ & 10μF/10V Electrolytic capacitor & \schpt{C271} & \href{http://uk.farnell.com/jsp/search/productdetail.jsp?\_dyncharset=UTF-8&searchTerms=1902928&\_D%3AsearchTerms=+&%2Fpf%2Fsearch%2FTextSearchFormHandler.search=GO&\_D%3A%2Fpf%2Fsearch%2FTextSearchFormHandler.search=+&s=&%2Fpf%2Fsearch%2FTextSearchFormHandler.suggestions=false&\_D%3A%2Fpf%2Fsearch%2FTextSearchFormHandler.suggestions=+&%2Fpf%2Fsearch%2FTextSearchFormHandler.ref=globalsearch&\_D%3A%2Fpf%2Fsearch%2FTextSearchFormHandler.ref=+&\_D%3ArohsVal=+&%2Fpf%2Fsearch%2FTextSearchFormHandler.onlyRoHSProductsActive=true&\_D%3A%2Fpf%2Fsearch%2FTextSearchFormHandler.onlyRoHSProductsActive=+&\_DARGS=%2Fjsp%2Fcommonfragments\%2FglobalsearchE14.jsp}{Farnell 1902928} &  \\
30$\times$ & 8x1 pin 2.54mm centre header & \schpt{CON1}–\schpt{CON10}, \schpt{CON16}–\schpt{CON19}, \schpt{CON21}–\schpt{CON31}, \schpt{CON33}–\schpt{CON37} & Farnell 1756826 (£0.122@10) + Farnell 3991271 (£0.179@10) & Molex KK® series header \\
2$\times$ & DB9 male or 2×5 pin header & \schpt{CON11}–\schpt{CON12} & Farnell 1099289 (£0.48@5) &  \\
1$\times$ & DB9 female or 2×5-pin header & \schpt{CON13} & Farnell 1099294 (£0.48@5) &  \\
2$\times$ & 2x20 pin shrouded header & \schpt{CON14}–\schpt{CON15} & RS 670-1825 (£0.972@5), Farnell 1099261 (£1.07) & IDE socket \\
2$\times$ & 9x1 pin 2.54mm centre header & \schpt{CON20}, \schpt{CON32} & \href{http://uk.farnell.com/jsp/search/productdetail.jsp?\_dyncharset=UTF-8&searchTerms=1756827&\_D%3AsearchTerms=+&%2Fpf%2Fsearch%2FTextSearchFormHandler.search=GO&\_D%3A%2Fpf%2Fsearch%2FTextSearchFormHandler.search=+&s=&%2Fpf%2Fsearch%2FTextSearchFormHandler.suggestions=false&\_D%3A%2Fpf%2Fsearch%2FTextSearchFormHandler.suggestions=+&%2Fpf%2Fsearch%2FTextSearchFormHandler.ref=globalsearch&\_D%3A%2Fpf%2Fsearch%2FTextSearchFormHandler.ref=+&\_D%3ArohsVal=+&%2Fpf%2Fsearch%2FTextSearchFormHandler.onlyRoHSProductsActive=true&\_D%3A%2Fpf%2Fsearch%2FTextSearchFormHandler.onlyRoHSProductsActive=+&\_DARGS=%2Fjsp%2Fcommonfragments\%2FglobalsearchE14.jsp}{Farnell 1756827} & Molex KK® series header \\
1$\times$ & 1N5817 Schottky barrier rectifier & \schpt{D1} & Farnell 1843507 (£0.023) &  \\
3$\times$ & 1N4148 diode & \schpt{D2}–\schpt{D4} & Farnell 9565124 (£0.011), RS 436-7341 (£0.003@100) & Or any fast signal diode \\
1$\times$ & 96-pin (A+B+C) DIN-41612 Bauform ‘C’ plug & \schpt{EXP} & Farnell 1656159 (£1.84) & Right angle through hole \\
1$\times$ & Wago 2x screw clamp & \schpt{FPPOWER} &  &  \\
3$\times$ & 74HC253 Dual 4:1 multiplexer, 3-state & \schpt{IC1}, \schpt{IC5}, \schpt{IC101} & Farnell 1753491 (£0.28), RS 709-3046 (£0.147@10) &  \\
14$\times$ & 74HC112N & \schpt{IC2}, \schpt{IC6}, \schpt{IC52}, \schpt{IC57}–\schpt{IC59}, \schpt{IC97}, \schpt{IC117}, \schpt{IC125}, \schpt{IC127}, \schpt{IC129}–\schpt{IC131}, \schpt{IC205} & RS 663-1893 (£0.219@10), Farnell 1749804 (£0.39) &  \\
9$\times$ & 74HC00 4× NAND gate & \schpt{IC3}–\schpt{IC4}, \schpt{IC7}, \schpt{IC14}, \schpt{IC33}, \schpt{IC95}, \schpt{IC204}, \schpt{IC207}–\schpt{IC208} & RS 169-6012 (£0.26), Farnell 9590889 (£0.38) &  \\
1$\times$ & LM556N Dual timer & \schpt{IC8} & Farnell 9488260 (£1.18), RS 536-0947 (£0.77@10) & May replace with 2×555 + 1×decoupling cap \\
6$\times$ & 74HC14N Hex inverting Schmitt trigger & \schpt{IC9}, \schpt{IC153}, \schpt{IC167}, \schpt{IC173}–\schpt{IC174}, \schpt{IC177} & Farnell 7455513 (£0.133@10), RS 714-0899 (£0.164@20) &  \\
1$\times$ & 74HC05 6× open drain inverter & \schpt{IC10} & Farnell 1470855 (£0.54), RS 442-921 (£0.52) &  \\
46$\times$ & 74HC541N Octal 3-state buffer & \schpt{IC11}–\schpt{IC12}, \schpt{IC19}–\schpt{IC21}, \schpt{IC27}–\schpt{IC28}, \schpt{IC38}–\schpt{IC39}, \schpt{IC42}–\schpt{IC43}, \schpt{IC47}–\schpt{IC48}, \schpt{IC50}–\schpt{IC51}, \schpt{IC63}–\schpt{IC64}, \schpt{IC71}–\schpt{IC74}, \schpt{IC79}–\schpt{IC82}, \schpt{IC87}–\schpt{IC88}, \schpt{IC92}–\schpt{IC93}, \schpt{IC103}–\schpt{IC104}, \schpt{IC120}–\schpt{IC121}, \schpt{IC124}, \schpt{IC134}, \schpt{IC136}, \schpt{IC182}–\schpt{IC187}, \schpt{IC194}–\schpt{IC195}, \schpt{IC202}–\schpt{IC203} & RS 714-0953 (£0.18@20), Farnell 1470755 (£0.25@10) &  \\
1$\times$ & 74HC590 8-bit registered binary counter & \schpt{IC13} & Farnell 1652001 (£0.52), RS 709-2523 (£0.236@5) &  \\
1$\times$ & 74HC161 & \schpt{IC15} & Farnell 380600 (£0.48), 380600 (£0.36@10), RS 709-2113 (£0.143@10) &  \\
3$\times$ & 29x010 1 MBit (128k x 8) Flash RAM & \schpt{IC16}–\schpt{IC18} & Farnell 1907092 (£1.58) & May use '020 or '040 if not available. \\
4$\times$ & 74HC540N Octal 3-state inverting buffer & \schpt{IC22}–\schpt{IC23}, \schpt{IC128}, \schpt{IC142} & Farnell US 1163595 (£0.482), Farnell 1753515 (£0.60), Farnell 1753515 (£0.46@10), RS 714-7932 (£0.195@20), RS 443-249 (£0.61) &  \\
16$\times$ & 74HC138N 3-to-8 line Decoder & \schpt{IC24}–\schpt{IC25}, \schpt{IC54}, \schpt{IC102}, \schpt{IC114}–\schpt{IC115}, \schpt{IC126}, \schpt{IC137}, \schpt{IC143}, \schpt{IC149}, \schpt{IC154}, \schpt{IC156}, \schpt{IC181}, \schpt{IC193}, \schpt{IC196}–\schpt{IC197} & Farnell US 1318508 (£0.172@10), RS 663-0036 (£0.267@10), Farnell 1826779 (£0.29) &  \\
10$\times$ & 74HC32 4× OR gate & \schpt{IC26}, \schpt{IC29}, \schpt{IC32}, \schpt{IC56}, \schpt{IC65}, \schpt{IC96}, \schpt{IC100}, \schpt{IC113}, \schpt{IC159}, \schpt{IC161} & RS 709-3021 (£0.201@10), Farnell 1739939 (£0.27@10) &  \\
10$\times$ & 74HC08 4× AND gate & \schpt{IC30}, \schpt{IC44}, \schpt{IC55}, \schpt{IC60}, \schpt{IC94}, \schpt{IC108}, \schpt{IC116}, \schpt{IC133}, \schpt{IC135}, \schpt{IC212} & RS 709-2845 (£0.201@10), Farnell 9665803 (£0.22@10) &  \\
1$\times$ & 74HC86N & \schpt{IC31} & Farnell US 1075957 (£0.169), RS 169-7380 (£0.26) &  \\
2$\times$ & 74HC251N & \schpt{IC34}–\schpt{IC35} & Farnell 9591320 (£0.22), Farnell 9591320 (£0.151@10), RS 663-0203 (£0.423@10) &  \\
1$\times$ & 74HC175D & \schpt{IC36} & RS 169-7481 (£0.39), RS 663-0111 (£0.20@10) &  \\
4$\times$ & 74HC374 Octal D-type transparent latch, positive edge triggered & \schpt{IC37}, \schpt{IC155}, \schpt{IC157}–\schpt{IC158} & RS 714-0931 (£0.191@20), RS 169-6141 (£0.38), Farnell 380763 (£0.57), Farnell 380763 (£0.38@10) &  \\
4$\times$ & 74HC273N & \schpt{IC40}–\schpt{IC41}, \schpt{IC45}–\schpt{IC46} & Farnell 9591397 (£0.34), RS 714-0925 (£0.175@20) &  \\
4$\times$ & 74HC688 8-bit magnitude/identity comparator & \schpt{IC49}, \schpt{IC53}, \schpt{IC89}–\schpt{IC90} & RS 709-2179 (£0.168@5), Farnell 9591672 (£0.67@10) &  \\
4$\times$ & 74HC245 Octal bus transceiver, 3-state & \schpt{IC61}–\schpt{IC62}, \schpt{IC151}–\schpt{IC152} & RS 714-0916 (£0.18@20), RS 169-6113 (£0.38), Farnell 380714 (£0.49) &  \\
6$\times$ & 74HC04N Hex inverter & \schpt{IC66}, \schpt{IC91}, \schpt{IC170}, \schpt{IC175}–\schpt{IC176}, \schpt{IC178} & Farnell US 2374080 (£0.086), Farnell 9590951 (£0.38), Farnell 9590951 (£0.23@10), RS 714-0877 (£0.149@20), RS 662-9997 (£0.233@10) &  \\
12$\times$ & 74HC193N & \schpt{IC67}–\schpt{IC70}, \schpt{IC75}–\schpt{IC78}, \schpt{IC83}–\schpt{IC86} & Farnell 1470793 (£0.34), RS 527-372 (£0.29@25) &  \\
5$\times$ & 74HC574 8-bit D Flip Flop bus driver & \schpt{IC98}–\schpt{IC99}, \schpt{IC132}, \schpt{IC198}–\schpt{IC199} & RS 714-0950 (£0.18@20), Farnell 380830 (£0.42@10) &  \\
4$\times$ & 29x010 1 MBit (128k x 8) Flash RAM & \schpt{IC105}–\schpt{IC107}, \schpt{IC112} & Farnell 1907092 (£1.58) & May use '020 or '040 if not available. \\
1$\times$ & 74HC74N & \schpt{IC109} & Farnell 1013916 (£0.103), RS 714-0975 (£0.15@20) &  \\
2$\times$ & 29F020 & \schpt{IC110}–\schpt{IC111} & Farnell 8749493 (£2.84) / Farnell 1565992 & Using 040 due to lack of availability. \\
4$\times$ & 74HC670 4×4-bit register file, 3-state & \schpt{IC118}–\schpt{IC119}, \schpt{IC122}–\schpt{IC123} & Farnell 1753519 (£1.31), Farnell 1753520 (£0.77) & Cheaper order code is for SOIC (better stocks) \\
2$\times$ & 29x040 4 MBit (512k x 8) Flash RAM & \schpt{IC138}, \schpt{IC140} & Farnell 8749493 (£2.84) / Farnell 1565992 &  \\
2$\times$ & 4 MBit (512k x 8) Static RAM & \schpt{IC139}, \schpt{IC141} & Farnell 1562900 (£4.71) &  \\
2$\times$ & 26C92 Dual UART & \schpt{IC144}–\schpt{IC145} & Farnell 1294820 (£2.18), RS 821-756 (£5) &  \\
3$\times$ & MAX-232 RS-232 transceiver & \schpt{IC146}–\schpt{IC148} & Farnell 1648737 (£0.73), RS 660-8613 (£0.68@5) &  \\
1$\times$ & 74HC05 6× open drain inverter & \schpt{IC150} & Farnell 1470855 (£0.54), RS 442-921 (£0.52) &  \\
3$\times$ & 74HC03N Quad 2-input NAND gate, open collector output & \schpt{IC160}, \schpt{IC179}, \schpt{IC206} & Farnell 1282849 (£0.17) &  \\
1$\times$ & 5V, 16 kbit (2k×8) NVRAM & RTC & \schpt{IC162} & Farnell 1224444 (£13.14) &  \\
2$\times$ & 74HC153N & \schpt{IC163}–\schpt{IC164} & RS 443-075 (£0.50), Farnell 1753485 (£0.56) &  \\
2$\times$ & 82C54 & \schpt{IC165}–\schpt{IC166} & Farnell 1018175 (£6.69), RS 496-688 (£6.71) &  \\
8$\times$ & 74LS123N Dual retriggerable monostable multivibrator & \schpt{IC168}, \schpt{IC180}, \schpt{IC189}–\schpt{IC192}, \schpt{IC210}–\schpt{IC211} & RS 307-632 (£0.61), Farnell 1470902 (£0.64), RS 368-6001 (£0.43@25) &  \\
1$\times$ & LM555N Timer & \schpt{IC169} & RS 534-3469 (£0.62), Farnell 1564692 (£0.52@10) &  \\
1$\times$ & 74HCT00N Quad 2-input NAND gate & \schpt{IC171} & RS 217-5702 (£0.14), Farnell US 2373749 (£0.125), Farnell 9591745 (£0.24) &  \\
1$\times$ & 74HC373 Octal D-type transparent latch, negative edge triggered & \schpt{IC172} & RS 714-0922 (£0.182@20), Farnell 1607705 (£0.52@10) &  \\
1$\times$ & 74HC85N 4-bit Magnitude Comparator & \schpt{IC188} & Farnell US 1387859 (£0.543), Farnell 380489 (£0.61), RS 527-801 (£0.544@25) &  \\
3$\times$ & 74HC21N & \schpt{IC200}–\schpt{IC201}, \schpt{IC209} & Farnell 1740011 (£0.23), RS 709-2665 (£0.163@20) &  \\
2$\times$ & 74HCT32N & \schpt{IC213}–\schpt{IC214} & Farnell 1013995 (£0.109), RS 156-9651 (£0.26) &  \\
2$\times$ & 74HC125N & \schpt{IC215}–\schpt{IC216} & Farnell 9591036 (£0.48), RS 709-2009 (£0.21@10), RS 169-7403 (£0.32) &  \\
1$\times$ & 74HCT541N & \schpt{IC217} & Farnell 382425 (£0.50), RS 169-7908 (£0.39) &  \\
13$\times$ & 3-pin 2.54mm header & \schpt{J1}–\schpt{J4}, \schpt{JP5}–\schpt{JP8}, \schpt{JP11}–\schpt{JP15} & RS 251-8092 (£0.078@25) &  \\
2$\times$ &  & \schpt{JP1}, \schpt{JP3} &  &  \\
1$\times$ &  & \schpt{JP2} &  &  \\
2$\times$ & 2×20-pin shrouded/keyed header & \schpt{JP4}, \schpt{JP16} & RS 670-1825 (£0.972@5), Farnell 1099261 (£1.07) &  \\
2$\times$ & 2-pin 2.54mm header & \schpt{JP9}–\schpt{JP10} & RS 251-8086 (£0.046@25) &  \\
39$\times$ & 5mm green LED & \schpt{LED1}–\schpt{LED13}, \schpt{LED23}–\schpt{LED25}, \schpt{LED52}, \schpt{LED85}–\schpt{LED88}, \schpt{LED106}, \schpt{LED109}–\schpt{LED114}, \schpt{LED119}–\schpt{LED121}, \schpt{LED146}–\schpt{LED153} & RS 228-6004 (£0.042), Farnell 1855549 (£0.42) &  \\
87$\times$ & 5mm red LED & \schpt{LED14}–\schpt{LED22}, \schpt{LED26}–\schpt{LED43}, \schpt{LED53}–\schpt{LED78}, \schpt{LED80}, \schpt{LED89}–\schpt{LED91}, \schpt{LED96}, \schpt{LED101}–\schpt{LED103}, \schpt{LED107}, \schpt{LED115}, \schpt{LED122}–\schpt{LED145} & RS 228-5988 (£0.042@5), Farnell 1581217 (£0.165) &  \\
27$\times$ & 5mm amber/orange/yellow LED & \schpt{LED44}–\schpt{LED51}, \schpt{LED79}, \schpt{LED81}–\schpt{LED84}, \schpt{LED92}–\schpt{LED95}, \schpt{LED97}–\schpt{LED100}, \schpt{LED104}–\schpt{LED105}, \schpt{LED108}, \schpt{LED116}–\schpt{LED118} & RS 228-6010 (£0.042), Farnell 1142581 (£0.21) &  \\
2$\times$ & 8x1 2.54mm female wirewrap header & \schpt{P1}, \schpt{P3} &  & Or other stackable \\
5$\times$ & 6x1 2.54mm female wirewrap header & \schpt{P2}, \schpt{P4}–\schpt{P7} &  & Or other stackable \\
28$\times$ & 47kΩ resistor, 0.25W & \schpt{R1}–\schpt{R4}, \schpt{R7}, \schpt{R12}–\schpt{R18}, \schpt{R25}–\schpt{R27}, \schpt{R30}–\schpt{R34}, \schpt{R43}–\schpt{R44}, \schpt{R49}–\schpt{R50}, \schpt{R57}, \schpt{R66}, \schpt{R68}–\schpt{R69} & RS 131-334 (£0.014@10), Farnell 9339540 (£0.011@50) &  \\
12$\times$ & 330Ω resistor, 0.25W & \schpt{R5}, \schpt{R11}, \schpt{R28}–\schpt{R29}, \schpt{R35}–\schpt{R39}, \schpt{R45}–\schpt{R46}, \schpt{R55} & RS 707-7622 (£0.014@10), Farnell 9339418 (£0.011@50) &  \\
1$\times$ & 470Ω resistor, 0.25W & \schpt{R6} & RS 131-211 (£0.014@10), Farnell 9339531 (£0.011@50) &  \\
1$\times$ & 100Ω resistor, 0.25W & \schpt{R8} & RS 131-132 (£0.014@10), Farnell 9339043 (£0.011@50) &  \\
4$\times$ & 1kΩ resistor, 0.25W & \schpt{R9}, \schpt{R53}, \schpt{R67}, \schpt{R70} & RS 131-255 (£0.014@10), Farnell 9339051 (£0.011@50) &  \\
1$\times$ & 50kΩ resistor, 0.25W & \schpt{R10} & RS 131-457 (£0.014@10), Farnell 9339558 (£0.011@50) & Actually 47kΩ (cheaper) \\
6$\times$ & 47Ω resistor, 0.25W & \schpt{R19}–\schpt{R24} & RS 131-097 (£0.014@10), Farnell 9339523 (£0.011@50) &  \\
3$\times$ & 1MΩ resistor 0.25W & \schpt{R40}–\schpt{R42} & RS 131-615 (£0.014@10), Farnell 9339086 (£0.011@50) &  \\
1$\times$ & 10MΩ resistor, 0.25W & \schpt{R47} & RS 135-667 (£0.014@10), Farnell 1186248 (£0.012@50) &  \\
10$\times$ & 300kΩ resistor, 0.25W & \schpt{R48}, \schpt{R56}, \schpt{R58}–\schpt{R65} & RS 707-7864 (£0.015@10), Farnell 9341714 (£0.025@50) &  \\
2$\times$ & 200k linear potentiometer/trimmer & \schpt{R51}, \schpt{R54} & \href{http://uk.farnell.com/jsp/search/productdetail.jsp?\_dyncharset=UTF-8&searchTerms=1689846&\_D%3AsearchTerms=+&%2Fpf%2Fsearch%2FTextSearchFormHandler.search=GO&\_D%3A%2Fpf%2Fsearch%2FTextSearchFormHandler.search=+&s=&%2Fpf%2Fsearch%2FTextSearchFormHandler.suggestions=false&\_D%3A%2Fpf%2Fsearch%2FTextSearchFormHandler.suggestions=+&%2Fpf%2Fsearch%2FTextSearchFormHandler.ref=globalsearch&\_D%3A%2Fpf%2Fsearch%2FTextSearchFormHandler.ref=+&\_D%3ArohsVal=+&%2Fpf%2Fsearch%2FTextSearchFormHandler.onlyRoHSProductsActive=true&\_D%3A%2Fpf%2Fsearch%2FTextSearchFormHandler.onlyRoHSProductsActive=+&\_DARGS=%2Fjsp%2Fcommonfragments\%2FglobalsearchE14.jsp}{Farnell 1689846} &  \\
1$\times$ & 180kΩ resistor, 0.25W & \schpt{R52} & RS 131-520 (£0.014@10), Farnell 9339264 (£0.011@50) &  \\
17$\times$ & 8×4.7kΩ resistor network & \schpt{RN1}, \schpt{RN5}–\schpt{RN7}, \schpt{RN13}, \schpt{RN16}–\schpt{RN17}, \schpt{RN37}–\schpt{RN40}, \schpt{RN42}–\schpt{RN43}, \schpt{RN48}–\schpt{RN51} & Farnell US 1602072 (£0.036@10), RS 522-4289 (£0.31@25) &  \\
1$\times$ & 4k7 & \schpt{RN2} & Farnell 1973120 (£0.065@10) & Using 5-element (G05R) part. \\
1$\times$ & 5×4.7kΩ resistor network & \schpt{RN3} & Farnell 1973120 (£0.065@10) &  \\
2$\times$ & 3×4.7kΩ resistor network & \schpt{RN4}, \schpt{RN41} & Farnell 9356347 (£0.24@5) &  \\
2$\times$ & 7×4.7kΩ resistor network & \schpt{RN8}, \schpt{RN18} & Farnell 1973129 (£0.085@10) &  \\
4$\times$ & 8×330Ω resistor, DIL packaged & \schpt{RN9}–\schpt{RN12} & RS 707-7622 (£0.014@10), Farnell 9339418 (£0.011@50) & Discretes used for protytping. \\
4$\times$ & 8×330Ω resistor network & \schpt{RN14}–\schpt{RN15}, \schpt{RN46}–\schpt{RN47} & Farnell 9356975 (£0.30@5) &  \\
2$\times$ & 8×10kΩ resistor network & \schpt{RN19}, \schpt{RN21} & Farnell 1973130 (£0.085@10) &  \\
3$\times$ & 8×50kΩ resistor network & \schpt{RN20}, \schpt{RN22}, \schpt{RN24} & RS 131-457 (£0.014@10), Farnell 9339558 (£0.011@50) & Uses 47kΩ discretes for prototyping. \\
1$\times$ & 10kΩ 6x bussed SIL resistor & \schpt{RN23} & \href{http://uk.farnell.com/jsp/search/productdetail.jsp?\_dyncharset=UTF-8&searchTerms=1973163&\_D%3AsearchTerms=+&%2Fpf%2Fsearch%2FTextSearchFormHandler.search=GO&\_D%3A%2Fpf%2Fsearch%2FTextSearchFormHandler.search=+&s=&%2Fpf%2Fsearch%2FTextSearchFormHandler.suggestions=false&\_D%3A%2Fpf%2Fsearch%2FTextSearchFormHandler.suggestions=+&%2Fpf%2Fsearch%2FTextSearchFormHandler.ref=globalsearch&\_D%3A%2Fpf%2Fsearch%2FTextSearchFormHandler.ref=+&\_D%3ArohsVal=+&%2Fpf%2Fsearch%2FTextSearchFormHandler.onlyRoHSProductsActive=true&\_D%3A%2Fpf%2Fsearch%2FTextSearchFormHandler.onlyRoHSProductsActive=+&\_DARGS=%2Fjsp%2Fcommonfragments\%2FglobalsearchE14.jsp}{Farnell 1973163} &  \\
13$\times$ & 8×330Ω resistor network & \schpt{RN25}–\schpt{RN31}, \schpt{RN33}–\schpt{RN36}, \schpt{RN44}–\schpt{RN45} & Farnell 1602072 (£0.041), RS 522-4289 (£0.31@25) &  \\
1$\times$ & 180Ω 8x bussed SIL resistor & \schpt{RN32} & \href{http://uk.farnell.com/jsp/search/productdetail.jsp?\_dyncharset=UTF-8&searchTerms=9356843&\_D%3AsearchTerms=+&%2Fpf%2Fsearch%2FTextSearchFormHandler.search=GO&\_D%3A%2Fpf%2Fsearch%2FTextSearchFormHandler.search=+&s=&%2Fpf%2Fsearch%2FTextSearchFormHandler.suggestions=false&\_D%3A%2Fpf%2Fsearch%2FTextSearchFormHandler.suggestions=+&%2Fpf%2Fsearch%2FTextSearchFormHandler.ref=globalsearch&\_D%3A%2Fpf%2Fsearch%2FTextSearchFormHandler.ref=+&\_D%3ArohsVal=+&%2Fpf%2Fsearch%2FTextSearchFormHandler.onlyRoHSProductsActive=true&\_D%3A%2Fpf%2Fsearch%2FTextSearchFormHandler.onlyRoHSProductsActive=+&\_DARGS=%2Fjsp%2Fcommonfragments\%2FglobalsearchE14.jsp}{Farnell 9356843} &  \\
1$\times$ & 470Ω linear potentiometer & \schpt{RV1} & Farnell 1227517 (£0.24) &  \\
1$\times$ & 4.7kΩ linear potentiometer & \schpt{RV2} & Farnell 1227523 (£0.23) &  \\
1$\times$ & Tactile switch & \schpt{S1} & Farnell 1813689 (£0.185) &  \\
18$\times$ & On-On toggle switch & \schpt{S2}–\schpt{S17}, \schpt{S19}–\schpt{S20} &  & Switch body and separate black/red actuators \\
1$\times$ & Double-pole 3-position key switch & \schpt{S18} & \href{http://uk.rs-online.com/web/p/products/2195835/}{RS 219-5835}, \href{http://uk.rs-online.com/web/p/products/6932284/}{RS 693-2284} & Make-before-break \\
2$\times$ & On-Off-On toggle switch & \schpt{S21}, \schpt{S30} & \href{http://uk.farnell.com/jsp/search/productdetail.jsp?\_dyncharset=UTF-8&searchTerms=9473807&\_D%3AsearchTerms=+&%2Fpf%2Fsearch%2FTextSearchFormHandler.search=GO&\_D%3A%2Fpf%2Fsearch%2FTextSearchFormHandler.search=+&s=&%2Fpf%2Fsearch%2FTextSearchFormHandler.suggestions=false&\_D%3A%2Fpf%2Fsearch%2FTextSearchFormHandler.suggestions=+&%2Fpf%2Fsearch%2FTextSearchFormHandler.ref=globalsearch&\_D%3A%2Fpf%2Fsearch%2FTextSearchFormHandler.ref=+&\_D%3ArohsVal=+&%2Fpf%2Fsearch%2FTextSearchFormHandler.onlyRoHSProductsActive=true&\_D%3A%2Fpf%2Fsearch%2FTextSearchFormHandler.onlyRoHSProductsActive=+&\_DARGS=%2Fjsp%2Fcommonfragments\%2FglobalsearchE14.jsp}{Farnell 9473807} & Also add lever actuator \\
5$\times$ & Mom-Off-Mom toggle switch & \schpt{S22}, \schpt{S24}–\schpt{S25}, \schpt{S31}–\schpt{S32} & \href{http://uk.farnell.com/jsp/search/productdetail.jsp?\_dyncharset=UTF-8&searchTerms=9473769&\_D%3AsearchTerms=+&%2Fpf%2Fsearch%2FTextSearchFormHandler.search=GO&\_D%3A%2Fpf%2Fsearch%2FTextSearchFormHandler.search=+&s=&%2Fpf%2Fsearch%2FTextSearchFormHandler.suggestions=false&\_D%3A%2Fpf%2Fsearch%2FTextSearchFormHandler.suggestions=+&%2Fpf%2Fsearch%2FTextSearchFormHandler.ref=globalsearch&\_D%3A%2Fpf%2Fsearch%2FTextSearchFormHandler.ref=+&\_D%3ArohsVal=+&%2Fpf%2Fsearch%2FTextSearchFormHandler.onlyRoHSProductsActive=true&\_D%3A%2Fpf%2Fsearch%2FTextSearchFormHandler.onlyRoHSProductsActive=+&\_DARGS=%2Fjsp%2Fcommonfragments\%2FglobalsearchE14.jsp}{Farnell 9473769} &  \\
5$\times$ & Mom-Off-Mom toggle switch & \schpt{S23}, \schpt{S26}–\schpt{S29} & \href{http://uk.farnell.com/jsp/search/productdetail.jsp?\_dyncharset=UTF-8&searchTerms=9473815&\_D%3AsearchTerms=+&%2Fpf%2Fsearch%2FTextSearchFormHandler.search=GO&\_D%3A%2Fpf%2Fsearch%2FTextSearchFormHandler.search=+&s=&%2Fpf%2Fsearch%2FTextSearchFormHandler.suggestions=false&\_D%3A%2Fpf%2Fsearch%2FTextSearchFormHandler.suggestions=+&%2Fpf%2Fsearch%2FTextSearchFormHandler.ref=globalsearch&\_D%3A%2Fpf%2Fsearch%2FTextSearchFormHandler.ref=+&\_D%3ArohsVal=+&%2Fpf%2Fsearch%2FTextSearchFormHandler.onlyRoHSProductsActive=true&\_D%3A%2Fpf%2Fsearch%2FTextSearchFormHandler.onlyRoHSProductsActive=+&\_DARGS=%2Fjsp%2Fcommonfragments\%2FglobalsearchE14.jsp}{Farnell 9473815} &  \\
5$\times$ &  & \schpt{SV1}, \schpt{SV5}–\schpt{SV8} &  &  \\
2$\times$ &  & \schpt{SV2}–\schpt{SV3} &  &  \\
3$\times$ &  & \schpt{SV4}, \schpt{SV9}–\schpt{SV10} &  &  \\
1$\times$ & 3x2 pin header & \schpt{SV11} &  &  \\
1$\times$ & 3x dip switch or 2x3 pin header & \schpt{SW1} & \href{http://uk.farnell.com/jsp/search/productdetail.jsp?\_dyncharset=UTF-8&searchTerms=1522004&\_D%3AsearchTerms=+&%2Fpf%2Fsearch%2FTextSearchFormHandler.search=GO&\_D%3A%2Fpf%2Fsearch%2FTextSearchFormHandler.search=+&s=&%2Fpf%2Fsearch%2FTextSearchFormHandler.suggestions=false&\_D%3A%2Fpf%2Fsearch%2FTextSearchFormHandler.suggestions=+&%2Fpf%2Fsearch%2FTextSearchFormHandler.ref=globalsearch&\_D%3A%2Fpf%2Fsearch%2FTextSearchFormHandler.ref=+&\_D%3ArohsVal=+&%2Fpf%2Fsearch%2FTextSearchFormHandler.onlyRoHSProductsActive=true&\_D%3A%2Fpf%2Fsearch%2FTextSearchFormHandler.onlyRoHSProductsActive=+&\_DARGS=%2Fjsp%2Fcommonfragments\%2FglobalsearchE14.jsp}{Farnell 1522004} &  \\
2$\times$ & 8-way DIP switch & \schpt{SW2}–\schpt{SW3} & RS 712-2576 (£0.50), Farnell 9471596 (£0.66) & Through hole \\
1$\times$ &  & \schpt{X2} &  &  \\
1$\times$ & 16 MHz & \schpt{XTAL1} & RS 547-5487 (£1.43) Farnell 7942710 (£1.54) & May need to reduce frequency. 4 MHz: RS 547-5392. 10 MHz: 547-5421. 12 MHz: RS 547-5459 \\
1$\times$ & 3.6864 MHz oscillator & \schpt{XTAL2} & RS 547-5386 (£1.53), Farnell 9510095 (£2.94) & For RS-232 interfaces \\
1$\times$ & 32.768 kHz crystal & \schpt{XTAL3} & Farnell 1652573 (£0.098) &  \\
