alexiosc/cft/documentation/latex/hardware_guide/cft-bom-parts.tex

\schpt{C1}–\schpt{C9} & 0.1μF ceramic capacitor & RS 721-5240 (£0.051@50) / Farnell 9411887 (£0.062) &  \\
\schpt{C10} & 1μF capacitor & Farnell 3322210 (£0.148), RS 538-1578 (£0.292), Farnell 1100398 (£0.38) &  \\
\schpt{C11}–\schpt{C14} & 0.1μF ceramic capacitor & RS 721-5240 (£0.051@50) / Farnell 9411887 (£0.062) &  \\
\schpt{C15}–\schpt{C16} & 10µF electrolytic capacitor & Farnell 1902928 (£0.033), RS 440-6547 (£0.026@50) &  \\
\schpt{C17}–\schpt{C21} & 0.1μF ceramic capacitor & RS 721-5240 (£0.051@50) / Farnell 9411887 (£0.062) &  \\
\schpt{C22} & 1μF capacitor & Farnell 3322210 (£0.148), RS 538-1578 (£0.292), Farnell 1100398 (£0.38) &  \\
\schpt{C23}–\schpt{C28} & 0.1μF ceramic capacitor & RS 721-5240 (£0.051@50) / Farnell 9411887 (£0.062) &  \\
\schpt{C29}–\schpt{C32} & 1μF capacitor & Farnell 3322210 (£0.148), RS 538-1578 (£0.292), Farnell 1100398 (£0.38) &  \\
\schpt{C33}–\schpt{C37} & 0.1μF ceramic capacitor & RS 721-5240 (£0.051@50) / Farnell 9411887 (£0.062) &  \\
\schpt{C38} & 1μF capacitor & Farnell 3322210 (£0.148), RS 538-1578 (£0.292), Farnell 1100398 (£0.38) &  \\
\schpt{C39}–\schpt{C46} & 0.1μF ceramic capacitor & RS 721-5240 (£0.051@50) / Farnell 9411887 (£0.062) &  \\
\schpt{C47} & 1μF capacitor & Farnell 3322210 (£0.148), RS 538-1578 (£0.292), Farnell 1100398 (£0.38) &  \\
\schpt{C48}–\schpt{C50} & 0.1μF ceramic capacitor & RS 721-5240 (£0.051@50) / Farnell 9411887 (£0.062) &  \\
\schpt{C51} & 1μF capacitor & Farnell 3322210 (£0.148), RS 538-1578 (£0.292), Farnell 1100398 (£0.38) &  \\
\schpt{C52}–\schpt{C55} & 0.1μF ceramic capacitor & RS 721-5240 (£0.051@50) / Farnell 9411887 (£0.062) &  \\
\schpt{C56} & 1μF capacitor & Farnell 3322210 (£0.148), RS 538-1578 (£0.292), Farnell 1100398 (£0.38) &  \\
\schpt{C57}–\schpt{C65} & 0.1μF ceramic capacitor & RS 721-5240 (£0.051@50) / Farnell 9411887 (£0.062) &  \\
\schpt{C66} & 1μF capacitor & Farnell 3322210 (£0.148), RS 538-1578 (£0.292), Farnell 1100398 (£0.38) &  \\
\schpt{C67}–\schpt{C71} & 0.1μF ceramic capacitor & RS 721-5240 (£0.051@50) / Farnell 9411887 (£0.062) &  \\
\schpt{C72} & 1μF capacitor & Farnell 3322210 (£0.148), RS 538-1578 (£0.292), Farnell 1100398 (£0.38) &  \\
\schpt{C73}–\schpt{C77} & 0.1μF ceramic capacitor & RS 721-5240 (£0.051@50) / Farnell 9411887 (£0.062) &  \\
\schpt{C78} & 1μF capacitor & Farnell 3322210 (£0.148), RS 538-1578 (£0.292), Farnell 1100398 (£0.38) &  \\
\schpt{C79}–\schpt{C86} & 0.1μF ceramic capacitor & RS 721-5240 (£0.051@50) / Farnell 9411887 (£0.062) &  \\
\schpt{C87} & 1μF capacitor & Farnell 3322210 (£0.148), RS 538-1578 (£0.292), Farnell 1100398 (£0.38) &  \\
\schpt{C88}–\schpt{C95} & 0.1μF ceramic capacitor & RS 721-5240 (£0.051@50) / Farnell 9411887 (£0.062) &  \\
\schpt{C96} & 1μF capacitor & Farnell 3322210 (£0.148), RS 538-1578 (£0.292), Farnell 1100398 (£0.38) &  \\
\schpt{C97}–\schpt{C106} & 0.1μF ceramic capacitor & RS 721-5240 (£0.051@50) / Farnell 9411887 (£0.062) &  \\
\schpt{C107} & 1μF capacitor & Farnell 3322210 (£0.148), RS 538-1578 (£0.292), Farnell 1100398 (£0.38) &  \\
\schpt{C108}–\schpt{C111} & 0.1μF ceramic capacitor & RS 721-5240 (£0.051@50) / Farnell 9411887 (£0.062) &  \\
\schpt{C112} & 1μF capacitor & Farnell 3322210 (£0.148), RS 538-1578 (£0.292), Farnell 1100398 (£0.38) &  \\
\schpt{C113}–\schpt{C116} & 0.1μF ceramic capacitor & RS 721-5240 (£0.051@50) / Farnell 9411887 (£0.062) &  \\
\schpt{C117} & 1μF capacitor & Farnell 3322210 (£0.148), RS 538-1578 (£0.292), Farnell 1100398 (£0.38) &  \\
\schpt{C118}–\schpt{C122} & 0.1μF ceramic capacitor & RS 721-5240 (£0.051@50) / Farnell 9411887 (£0.062) &  \\
\schpt{C123}–\schpt{C126} & 1μF capacitor & Farnell 3322210 (£0.148), RS 538-1578 (£0.292), Farnell 1100398 (£0.38) &  \\
\schpt{C127}–\schpt{C129} & 0.1μF ceramic capacitor & RS 721-5240 (£0.051@50) / Farnell 9411887 (£0.062) &  \\
\schpt{C130}–\schpt{C133} & 1μF capacitor & Farnell 3322210 (£0.148), RS 538-1578 (£0.292), Farnell 1100398 (£0.38) &  \\
\schpt{C134}–\schpt{C145} & 0.1μF ceramic capacitor & RS 721-5240 (£0.051@50) / Farnell 9411887 (£0.062) &  \\
\schpt{C146} & 1μF capacitor & Farnell 3322210 (£0.148), RS 538-1578 (£0.292), Farnell 1100398 (£0.38) &  \\
\schpt{C147}–\schpt{C158} & 0.1μF ceramic capacitor & RS 721-5240 (£0.051@50) / Farnell 9411887 (£0.062) &  \\
\schpt{C159} & 1μF capacitor & Farnell 3322210 (£0.148), RS 538-1578 (£0.292), Farnell 1100398 (£0.38) &  \\
\schpt{C160}–\schpt{C165} & 0.1μF ceramic capacitor & RS 721-5240 (£0.051@50) / Farnell 9411887 (£0.062) &  \\
\schpt{C166}–\schpt{C170} & 1μF capacitor & Farnell 3322210 (£0.148), RS 538-1578 (£0.292), Farnell 1100398 (£0.38) &  \\
\schpt{C171} & 0.1μF ceramic capacitor & RS 721-5240 (£0.051@50) / Farnell 9411887 (£0.062) &  \\
\schpt{C172} & 1μF capacitor & Farnell 3322210 (£0.148), RS 538-1578 (£0.292), Farnell 1100398 (£0.38) &  \\
\schpt{C173} & 0.1μF ceramic capacitor & RS 721-5240 (£0.051@50) / Farnell 9411887 (£0.062) &  \\
\schpt{C174}–\schpt{C175} & 1μF capacitor & Farnell 3322210 (£0.148), RS 538-1578 (£0.292), Farnell 1100398 (£0.38) &  \\
\schpt{C176}–\schpt{C187} & 1 μF electrolytic capacitor & Farnell 1236655 (£0.034) & Through hole \\
\schpt{C188}–\schpt{C190} & 10 µF electrolytic capacitor & Farnell 1902928 (£0.033), RS 440-6547 (£0.026@50) &  \\
\schpt{C191}–\schpt{C195} & 0.1μF ceramic capacitor & RS 721-5240 (£0.051@50) / Farnell 9411887 (£0.062) &  \\
\schpt{C196}–\schpt{C197} & 1μF capacitor & Farnell 3322210 (£0.148), RS 538-1578 (£0.292), Farnell 1100398 (£0.38) &  \\
\schpt{C198}–\schpt{C211} & 0.1μF ceramic capacitor & RS 721-5240 (£0.051@50) / Farnell 9411887 (£0.062) &  \\
\schpt{C212}–\schpt{C213} & 22 pF ceramic capacitor & Farnell 9411674 (£0.035@25) &  \\
\schpt{C214} & 1μF capacitor & Farnell 3322210 (£0.148), RS 538-1578 (£0.292), Farnell 1100398 (£0.38) &  \\
\schpt{C215}–\schpt{C220} & 0.1μF ceramic capacitor & RS 721-5240 (£0.051@50) / Farnell 9411887 (£0.062) &  \\
\schpt{C221} & 1μF capacitor & Farnell 3322210 (£0.148), RS 538-1578 (£0.292), Farnell 1100398 (£0.38) &  \\
\schpt{C222} & 100uF Electrolytic capacitor & \href{http://uk.farnell.com/jsp/search/productdetail.jsp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\%2FglobalsearchE14.jsp}{Farnell 1902882} &  \\
\schpt{C223}–\schpt{C226} & 1μF electrolytic capacitor & Farnell 1236655 (£0.034) &  \\
\schpt{C227} & 22nF capacitor & \href{http://uk.farnell.com/jsp/search/productdetail.jsp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\%2FglobalsearchE14.jsp}{Farnell 9411860} &  \\
\schpt{C228} & 4.7μF Electrolytic capacitor & \href{http://uk.farnell.com/jsp/search/productdetail.jsp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\%2FglobalsearchE14.jsp}{Farnell 1902916} &  \\
\schpt{C229}–\schpt{C230} & 1μF capacitor & Farnell 3322210 (£0.148), RS 538-1578 (£0.292), Farnell 1100398 (£0.38) &  \\
\schpt{C231}–\schpt{C238} & 1μF electrolytic capacitor & Farnell 1236655 (£0.034) &  \\
\schpt{C239}–\schpt{C240} & 0.1μF ceramic capacitor & RS 721-5240 (£0.051@50) / Farnell 9411887 (£0.062) &  \\
\schpt{C241}–\schpt{C244} & 1μF electrolytic capacitor & Farnell 1236655 (£0.034) &  \\
\schpt{C245}–\schpt{C247} & 0.1μF ceramic capacitor & RS 721-5240 (£0.051@50) / Farnell 9411887 (£0.062) &  \\
\schpt{C248}–\schpt{C249} & 1μF capacitor & Farnell 3322210 (£0.148), RS 538-1578 (£0.292), Farnell 1100398 (£0.38) &  \\
\schpt{C250}–\schpt{C256} & 0.1μF ceramic capacitor & RS 721-5240 (£0.051@50) / Farnell 9411887 (£0.062) &  \\
\schpt{C257} & 1μF capacitor & Farnell 3322210 (£0.148), RS 538-1578 (£0.292), Farnell 1100398 (£0.38) &  \\
\schpt{C258}–\schpt{C261} & 0.1μF ceramic capacitor & RS 721-5240 (£0.051@50) / Farnell 9411887 (£0.062) &  \\
\schpt{C262}–\schpt{C270} & 1μF capacitor & Farnell 3322210 (£0.148), RS 538-1578 (£0.292), Farnell 1100398 (£0.38) &  \\
\schpt{C271} & 10μF/10V Electrolytic capacitor & \href{http://uk.farnell.com/jsp/search/productdetail.jsp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\%2FglobalsearchE14.jsp}{Farnell 1902928} &  \\
\schpt{C272}–\schpt{C281} & 0.1μF ceramic capacitor & RS 721-5240 (£0.051@50) / Farnell 9411887 (£0.062) &  \\
\schpt{C282} & 1μF capacitor & Farnell 3322210 (£0.148), RS 538-1578 (£0.292), Farnell 1100398 (£0.38) &  \\
\schpt{C283}–\schpt{C287} & 0.1μF ceramic capacitor & RS 721-5240 (£0.051@50) / Farnell 9411887 (£0.062) &  \\
\schpt{C288} & 1μF capacitor & Farnell 3322210 (£0.148), RS 538-1578 (£0.292), Farnell 1100398 (£0.38) &  \\
\schpt{C289}–\schpt{C298} & 0.1μF ceramic capacitor & RS 721-5240 (£0.051@50) / Farnell 9411887 (£0.062) &  \\
\schpt{C299} & 1μF capacitor & Farnell 3322210 (£0.148), RS 538-1578 (£0.292), Farnell 1100398 (£0.38) &  \\
\schpt{C300}–\schpt{C303} & 100nF capacitor & \href{http://uk.farnell.com/jsp/search/productdetail.jsp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\%2FglobalsearchE14.jsp}{Farnell 1469310} &  \\
\schpt{C304} & 1 μF electrolytic capacitor & Farnell 1236655 (£0.034) & Through hole \\
\schpt{CON1}–\schpt{CON10} & 8x1 pin 2.54mm centre header & \href{http://uk.farnell.com/jsp/search/productdetail.jsp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\%2FglobalsearchE14.jsp}{Farnell 1756826} & Molex KK® series header \\
\schpt{CON11}–\schpt{CON12} & DB9 male or 2×5 pin header & Farnell 1099289 (£0.48@5) &  \\
\schpt{CON13} & DB9 female or 2×5-pin header & Farnell 1099294 (£0.48@5) &  \\
\schpt{CON14}–\schpt{CON15} & 2x20 pin shrouded header & RS 670-1825 (£0.972@5), Farnell 1099261 (£1.07) & IDE socket \\
\schpt{CON16}–\schpt{CON19} & 8x1 pin 2.54mm centre header & \href{http://uk.farnell.com/jsp/search/productdetail.jsp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\%2FglobalsearchE14.jsp}{Farnell 1756826} & Molex KK® series header \\
\schpt{CON20} & 9x1 pin 2.54mm centre header & \href{http://uk.farnell.com/jsp/search/productdetail.jsp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\%2FglobalsearchE14.jsp}{Farnell 1756827} & Molex KK® series header \\
\schpt{CON21}–\schpt{CON31} & 8x1 pin 2.54mm centre header & \href{http://uk.farnell.com/jsp/search/productdetail.jsp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\%2FglobalsearchE14.jsp}{Farnell 1756826} & Molex KK® series header \\
\schpt{CON32} & 9x1 pin 2.54mm centre header & \href{http://uk.farnell.com/jsp/search/productdetail.jsp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\%2FglobalsearchE14.jsp}{Farnell 1756827} & Molex KK® series header \\
\schpt{CON33}–\schpt{CON37} & 8x1 pin 2.54mm centre header & \href{http://uk.farnell.com/jsp/search/productdetail.jsp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\%2FglobalsearchE14.jsp}{Farnell 1756826} & Molex KK® series header \\
\schpt{D1} & 1N5817 Schottky barrier rectifier & Farnell 1843507 (£0.023) &  \\
\schpt{D2}–\schpt{D4} & 1N4148 diode & \href{http://uk.farnell.com/jsp/search/productdetail.jsp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\%2FglobalsearchE14.jsp}{Farnell 9565124} & Or any fast signal diode \\
\schpt{EXP} & 96-pin (A+B+C) DIN-41612 Bauform ‘C’ plug & Farnell 1656159 (£1.84) & Right angle through hole \\
\schpt{FPPOWER} & Wago 2x screw clamp &  &  \\
\schpt{IC1} & 74HC253 Dual 4:1 multiplexer, 3-state & Farnell 1753491 (£0.28), RS 709-3046 (£0.147@10) &  \\
\schpt{IC2} & Dual J-K negative edge triggered FLIP FLOP, preset and clear & RS 663-1893 (£0.219@10), Farnell 1749804 (£0.39) &  \\
\schpt{IC3}–\schpt{IC4} & 74HC00 4× NAND gate & RS 169-6012 (£0.26), Farnell 9590889 (£0.38) &  \\
\schpt{IC5} & 74HC253 Dual 4:1 multiplexer, 3-state & Farnell 1753491 (£0.28), RS 709-3046 (£0.147@10) &  \\
\schpt{IC6} & Dual J-K negative edge triggered FLIP FLOP, preset and clear & RS 663-1893 (£0.219@10), Farnell 1749804 (£0.39) &  \\
\schpt{IC7} & 74HC00 4× NAND gate & RS 169-6012 (£0.26), Farnell 9590889 (£0.38) &  \\
\schpt{IC8} & LM556N Dual timer & Farnell 9488260 (£1.18), RS 536-0947 (£0.77@10) & May replace with 2×555 + 1×decoupling cap \\
\schpt{IC9} & 74HC14N Hex inverting Schmitt trigger & Farnell 7455513 (£0.133@10), RS 714-0899 (£0.164@20) &  \\
\schpt{IC10} & 74HC05 6× open drain inverter & Farnell 1470855 (£0.54), RS 442-921 (£0.52) &  \\
\schpt{IC11}–\schpt{IC12} & 74HC541N Octal 3-state buffer & RS 714-0953 (£0.18@20), Farnell 1470755 (£0.25) &  \\
\schpt{IC13} & 8-bit binary COUNTER, output register &  &  \\
\schpt{IC14} & Quad 2-input AND gate &  &  \\
\schpt{IC15} & 41xx DEVICE &  &  \\
\schpt{IC16}–\schpt{IC18} & 29x010 1 MBit (128k x 8) Flash RAM & Farnell 1907092 (£1.58) & May use '020 or '040 if not available. \\
\schpt{IC19}–\schpt{IC21} & 74HC541N Octal 3-state buffer & RS 714-0953 (£0.18@20), Farnell 1470755 (£0.25) &  \\
\schpt{IC22}–\schpt{IC23} & 74HC540N Octal 3-state inverting buffer & \href{http://uk.farnell.com/jsp/search/productdetail.jsp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\%2FglobalsearchE14.jsp}{Farnell 1868632} &  \\
\schpt{IC24} & 41xx DEVICE &  &  \\
\schpt{IC25}–\schpt{IC26} & 74HC138N 3-to-8 line Decoder & RS 663-0036 (£0.267@10), Farnell 1826779 (£0.29) &  \\
\schpt{IC27} & Quad 2-input OR gate &  &  \\
\schpt{IC28}–\schpt{IC29} & 74HC541N Octal 3-state buffer & RS 714-0953 (£0.18@20), Farnell 1470755 (£0.25) &  \\
\schpt{IC30} & Quad 2-input OR gate &  &  \\
\schpt{IC31} & Quad 2-input AND gate &  &  \\
\schpt{IC32} & Quad 2-input EXCLUSIVE-OR (XOR) gate &  &  \\
\schpt{IC33} & Quad 2-input OR gate &  &  \\
\schpt{IC34} & 74AC00 4× NAND gate & Farnell 1607805 (£0.48), RS 709-2223 (£0.124@10) &  \\
\schpt{IC35}–\schpt{IC36} & 1 of 8 data SELECTOR/MULTIPLEXER, 3-state &  &  \\
\schpt{IC37} & Qadruple D type FLIP FLOP, clear &  &  \\
\schpt{IC38} & 74HC373 Octal D-type transparent latch, negative edge triggered & RS 714-0922 (£0.182@20), Farnell 1607705 (£0.52@10) &  \\
\schpt{IC39}–\schpt{IC40} & Octal BUFFER and LINE DRIVER, 3-state &  &  \\
\schpt{IC41}–\schpt{IC42} & 74HC574 8-bit D Flip Flop bus driver & RS 714-0950 (£0.18@20), Farnell 380830 (£0.42@10) &  \\
\schpt{IC43}–\schpt{IC44} & 74HC541N Octal 3-state buffer & RS 714-0953 (£0.18@20), Farnell 1470755 (£0.25) &  \\
\schpt{IC45} & 74HC08 4× AND gate & RS 709-2845 (£0.201@10), Farnell 9665803 (£0.22@10) &  \\
\schpt{IC46}–\schpt{IC47} & Octal D type FLIP FLOP, clear & Farnell 9591397 (£0.34), RS 714-0925 (£0.175@20) &  \\
\schpt{IC48}–\schpt{IC49} & 74HC541N Octal 3-state buffer & RS 714-0953 (£0.18@20), Farnell 1470755 (£0.25) &  \\
\schpt{IC50} & 74HC688 8-bit magnitude/identity comparator & RS 709-2179 (£0.168@5), Farnell 9591672 (£0.67@10) &  \\
\schpt{IC51}–\schpt{IC52} & 74HC541N Octal 3-state buffer & RS 714-0953 (£0.18@20), Farnell 1470755 (£0.25) &  \\
\schpt{IC53} & Qadruple D type FLIP FLOP, clear &  &  \\
\schpt{IC54} & 74HC688 8-bit magnitude/identity comparator & RS 709-2179 (£0.168@5), Farnell 9591672 (£0.67@10) &  \\
\schpt{IC55} & 74HC138N 3-to-8 line Decoder & RS 663-0036 (£0.267@10), Farnell 1826779 (£0.29) &  \\
\schpt{IC56} & 74HC08 4× AND gate & RS 709-2845 (£0.201@10), Farnell 9665803 (£0.22@10) &  \\
\schpt{IC57} & Quad 2-input OR gate &  &  \\
\schpt{IC58}–\schpt{IC60} & Dual J-K negative edge triggered FLIP FLOP, preset and clear & RS 663-1893 (£0.219@10), Farnell 1749804 (£0.39) &  \\
\schpt{IC61} & Dual 4-input AND gate & Farnell 1740011 (£0.23), RS 709-2665 (£0.163@20) &  \\
\schpt{IC62}–\schpt{IC63} & 74HC245 Octal bus transceiver, 3-state & RS 714-0916 (£0.18@20), RS 169-6113 (£0.38), Farnell 380714 (£0.49) &  \\
\schpt{IC64}–\schpt{IC65} & Octal BUFFER and LINE DRIVER, 3-state &  &  \\
\schpt{IC66} & Hex INVERTER, open collector high-voltage output &  &  \\
\schpt{IC67}–\schpt{IC70} & Presettable Synchronous Binary Up/Down Counter & Farnell 1470793 (£0.34), RS 527-372 (£0.29@25) &  \\
\schpt{IC71}–\schpt{IC74} & 74HC541N Octal 3-state buffer & RS 714-0953 (£0.18@20), Farnell 1470755 (£0.25) &  \\
\schpt{IC75}–\schpt{IC78} & Presettable Synchronous Binary Up/Down Counter & Farnell 1470793 (£0.34), RS 527-372 (£0.29@25) &  \\
\schpt{IC79}–\schpt{IC82} & 74HC541N Octal 3-state buffer & RS 714-0953 (£0.18@20), Farnell 1470755 (£0.25) &  \\
\schpt{IC83}–\schpt{IC86} & Presettable Synchronous Binary Up/Down Counter & Farnell 1470793 (£0.34), RS 527-372 (£0.29@25) &  \\
\schpt{IC87}–\schpt{IC88} & 74HC541N Octal 3-state buffer & RS 714-0953 (£0.18@20), Farnell 1470755 (£0.25) &  \\
\schpt{IC89}–\schpt{IC90} & 74HC688 8-bit magnitude/identity comparator & RS 709-2179 (£0.168@5), Farnell 9591672 (£0.67@10) &  \\
\schpt{IC91}–\schpt{IC92} & 74HC541N Octal 3-state buffer & RS 714-0953 (£0.18@20), Farnell 1470755 (£0.25) &  \\
\schpt{IC93} & 74HC08 4× AND gate & RS 709-2845 (£0.201@10), Farnell 9665803 (£0.22@10) &  \\
\schpt{IC94} & 74HC00 4× NAND gate & RS 169-6012 (£0.26), Farnell 9590889 (£0.38) &  \\
\schpt{IC95} & Quad 2-input OR gate &  &  \\
\schpt{IC96} & Dual J-K negative edge triggered FLIP FLOP, preset and clear & RS 663-1893 (£0.219@10), Farnell 1749804 (£0.39) &  \\
\schpt{IC97}–\schpt{IC98} & 74HC574 8-bit D Flip Flop bus driver & RS 714-0950 (£0.18@20), Farnell 380830 (£0.42@10) &  \\
\schpt{IC99} & Quad 2-input OR gate &  &  \\
\schpt{IC100} & 74HC253 Dual 4:1 multiplexer, 3-state & Farnell 1753491 (£0.28), RS 709-3046 (£0.147@10) &  \\
\schpt{IC101} & 74HC138N 3-to-8 line Decoder & RS 663-0036 (£0.267@10), Farnell 1826779 (£0.29) &  \\
\schpt{IC102}–\schpt{IC104} & 29x010 1 MBit (128k x 8) Flash RAM & Farnell 1907092 (£1.58) & May use '020 or '040 if not available. \\
\schpt{IC105} & 74HC08 4× AND gate & RS 709-2845 (£0.201@10), Farnell 9665803 (£0.22@10) &  \\
\schpt{IC106} & Dual D type positive edge triggered FLIP FLOP, preset and clear &  &  \\
\schpt{IC107}–\schpt{IC108} & 2-mbit (256x8) Flash memory in a PLCC32 package (with socket). AM29F020 is an example of this. & Farnell 8749493 (£2.84) / Farnell 1565992 & Using 040 due to lack of availability. \\
\schpt{IC109} & 29x010 1 MBit (128k x 8) Flash RAM & Farnell 1907092 (£1.58) & May use '020 or '040 if not available. \\
\schpt{IC110} & Quad 2-input OR gate &  &  \\
\schpt{IC111}–\schpt{IC112} & 74HC138N 3-to-8 line Decoder & RS 663-0036 (£0.267@10), Farnell 1826779 (£0.29) &  \\
\schpt{IC113} & 74HC08 4× AND gate & RS 709-2845 (£0.201@10), Farnell 9665803 (£0.22@10) &  \\
\schpt{IC114} & Dual J-K negative edge triggered FLIP FLOP, preset and clear & RS 663-1893 (£0.219@10), Farnell 1749804 (£0.39) &  \\
\schpt{IC115}–\schpt{IC116} & 74HC670 4×4-bit register file, 3-state & Farnell 1753519 (£1.31), Farnell 1753520 (£0.77) & Cheaper order code is for SOIC (better stocks) \\
\schpt{IC117}–\schpt{IC118} & 74HC541N Octal 3-state buffer & RS 714-0953 (£0.18@20), Farnell 1470755 (£0.25) &  \\
\schpt{IC119}–\schpt{IC120} & 74HC670 4×4-bit register file, 3-state & Farnell 1753519 (£1.31), Farnell 1753520 (£0.77) & Cheaper order code is for SOIC (better stocks) \\
\schpt{IC121} & 74HC541N Octal 3-state buffer & RS 714-0953 (£0.18@20), Farnell 1470755 (£0.25) &  \\
\schpt{IC122} & Dual J-K negative edge triggered FLIP FLOP, preset and clear & RS 663-1893 (£0.219@10), Farnell 1749804 (£0.39) &  \\
\schpt{IC123} & 74HC138N 3-to-8 line Decoder & RS 663-0036 (£0.267@10), Farnell 1826779 (£0.29) &  \\
\schpt{IC124} & Dual J-K negative edge triggered FLIP FLOP, preset and clear & RS 663-1893 (£0.219@10), Farnell 1749804 (£0.39) &  \\
\schpt{IC125} & 74HC540N Octal 3-state inverting buffer & \href{http://uk.farnell.com/jsp/search/productdetail.jsp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\%2FglobalsearchE14.jsp}{Farnell 1868632} &  \\
\schpt{IC126}–\schpt{IC128} & Dual J-K negative edge triggered FLIP FLOP, preset and clear & RS 663-1893 (£0.219@10), Farnell 1749804 (£0.39) &  \\
\schpt{IC129} & 74HC574 8-bit D Flip Flop bus driver & RS 714-0950 (£0.18@20), Farnell 380830 (£0.42@10) &  \\
\schpt{IC130} & 74HC08 4× AND gate & RS 709-2845 (£0.201@10), Farnell 9665803 (£0.22@10) &  \\
\schpt{IC131} & 74HC541N Octal 3-state buffer & RS 714-0953 (£0.18@20), Farnell 1470755 (£0.25) &  \\
\schpt{IC132} & 74HC08 4× AND gate & RS 709-2845 (£0.201@10), Farnell 9665803 (£0.22@10) &  \\
\schpt{IC133} & 74HC541N Octal 3-state buffer & RS 714-0953 (£0.18@20), Farnell 1470755 (£0.25) &  \\
\schpt{IC134} & 74HC138N 3-to-8 line Decoder & RS 663-0036 (£0.267@10), Farnell 1826779 (£0.29) &  \\
\schpt{IC135} & 29x040 4 MBit (512k x 8) Flash RAM & Farnell 8749493 (£2.84) / Farnell 1565992 &  \\
\schpt{IC136} & 4 MBit (512k x 8) Static RAM & Farnell 1562900 (£4.71) &  \\
\schpt{IC137} & 29x040 4 MBit (512k x 8) Flash RAM & Farnell 8749493 (£2.84) / Farnell 1565992 &  \\
\schpt{IC138} & 4 MBit (512k x 8) Static RAM & Farnell 1562900 (£4.71) &  \\
\schpt{IC139} & 74HC540N Octal 3-state inverting buffer & \href{http://uk.farnell.com/jsp/search/productdetail.jsp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\%2FglobalsearchE14.jsp}{Farnell 1868632} &  \\
\schpt{IC140} & 74HC138N 3-to-8 line Decoder & RS 663-0036 (£0.267@10), Farnell 1826779 (£0.29) &  \\
\schpt{IC141}–\schpt{IC142} & 26C92 Dual UART & Farnell 1294820 (£2.18), RS 821-756 (£5) &  \\
\schpt{IC143}–\schpt{IC145} & MAX-232 RS-232 transceiver & Farnell 1648737 (£0.73), RS 660-8613 (£0.68@5) &  \\
\schpt{IC146} & 74HC138N 3-to-8 line Decoder & RS 663-0036 (£0.267@10), Farnell 1826779 (£0.29) &  \\
\schpt{IC147} & 74HC05 6× open drain inverter & Farnell 1470855 (£0.54), RS 442-921 (£0.52) &  \\
\schpt{IC148}–\schpt{IC149} & 74HC245 Octal bus transceiver, 3-state & RS 714-0916 (£0.18@20), RS 169-6113 (£0.38), Farnell 380714 (£0.49) &  \\
\schpt{IC150} & 74HC14N Hex inverting Schmitt trigger & Farnell 7455513 (£0.133@10), RS 714-0899 (£0.164@20) &  \\
\schpt{IC151} & 74HC138N 3-to-8 line Decoder & RS 663-0036 (£0.267@10), Farnell 1826779 (£0.29) &  \\
\schpt{IC152} & 74HC374 Octal D-type transparent latch, positive edge triggered & RS 714-0931 (£0.191@20), RS 169-6141 (£0.38), Farnell 380763 (£0.57), Farnell 380763 (£0.38@10) &  \\
\schpt{IC153} & 74HC138N 3-to-8 line Decoder & RS 663-0036 (£0.267@10), Farnell 1826779 (£0.29) &  \\
\schpt{IC154}–\schpt{IC155} & 74HC374 Octal D-type transparent latch, positive edge triggered & RS 714-0931 (£0.191@20), RS 169-6141 (£0.38), Farnell 380763 (£0.57), Farnell 380763 (£0.38@10) &  \\
\schpt{IC156} & Quad 2-input OR gate &  &  \\
\schpt{IC157} & 74HC03N Quad 2-input NAND gate, open collector output & \href{http://uk.farnell.com/jsp/search/productdetail.jsp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\%2FglobalsearchE14.jsp}{Farnell 1282849} &  \\
\schpt{IC158} & Quad 2-input OR gate &  &  \\
\schpt{IC159} & 5V, 16 kbit (2k×8) NVRAM & RTC & Farnell 1224444 (£13.14) &  \\
\schpt{IC160}–\schpt{IC161} & Dual 4-line to 1-line data SELECTOR/MULTIPLEXER &  &  \\
\schpt{IC162}–\schpt{IC163} & Intersil 82C54 Programmable Timer & \href{http://uk.farnell.com/jsp/search/productdetail.jsp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\%2FglobalsearchE14.jsp}{Farnell 1018175} &  \\
\schpt{IC164} & 74HC14N Hex inverting Schmitt trigger & Farnell 7455513 (£0.133@10), RS 714-0899 (£0.164@20) &  \\
\schpt{IC165} & 74LS123N Dual retriggerable monostable multivibrator & \href{http://uk.farnell.com/jsp/search/productdetail.jsp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\%2FglobalsearchE14.jsp}{Farnell 1470902} &  \\
\schpt{IC166} & LM555N Timer & RS 534-3469 (£0.62), Farnell 1564692 (£0.52@10) &  \\
\schpt{IC167} & 74HC04N Hex inverter & \href{http://uk.farnell.com/jsp/search/productdetail.jsp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\%2FglobalsearchE14.jsp}{Farnell 2374080} &  \\
\schpt{IC168} & 74HCT00N Quad 2-input NAND gate & \href{http://uk.farnell.com/jsp/search/productdetail.jsp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\%2FglobalsearchE14.jsp}{Farnell 2373749} &  \\
\schpt{IC169} & 74HC373 Octal D-type transparent latch, negative edge triggered & RS 714-0922 (£0.182@20), Farnell 1607705 (£0.52@10) &  \\
\schpt{IC170}–\schpt{IC171} & 74HC14N Hex inverting Schmitt trigger & Farnell 7455513 (£0.133@10), RS 714-0899 (£0.164@20) &  \\
\schpt{IC172}–\schpt{IC173} & 74HC04N Hex inverter & \href{http://uk.farnell.com/jsp/search/productdetail.jsp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\%2FglobalsearchE14.jsp}{Farnell 2374080} &  \\
\schpt{IC174} & 74HC14N Hex inverting Schmitt trigger & Farnell 7455513 (£0.133@10), RS 714-0899 (£0.164@20) &  \\
\schpt{IC175} & 74HC04N Hex inverter & \href{http://uk.farnell.com/jsp/search/productdetail.jsp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\%2FglobalsearchE14.jsp}{Farnell 2374080} &  \\
\schpt{IC176} & 74HC03N Quad 2-input NAND gate, open collector output & \href{http://uk.farnell.com/jsp/search/productdetail.jsp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\%2FglobalsearchE14.jsp}{Farnell 1282849} &  \\
\schpt{IC177} & 74LS123N Dual retriggerable monostable multivibrator & \href{http://uk.farnell.com/jsp/search/productdetail.jsp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\%2FglobalsearchE14.jsp}{Farnell 1470902} &  \\
\schpt{IC178} & 74HC138N 3-to-8 line Decoder & RS 663-0036 (£0.267@10), Farnell 1826779 (£0.29) &  \\
\schpt{IC179}–\schpt{IC184} & 74HC541N Octal 3-state buffer & RS 714-0953 (£0.18@20), Farnell 1470755 (£0.25) &  \\
\schpt{IC185} & 74HC85N 4-bit Magnitude Comparator & \href{http://uk.farnell.com/jsp/search/productdetail.jsp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\%2FglobalsearchE14.jsp}{Farnell 1868642} &  \\
\schpt{IC186}–\schpt{IC189} & 74LS123N Dual retriggerable monostable multivibrator & \href{http://uk.farnell.com/jsp/search/productdetail.jsp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\%2FglobalsearchE14.jsp}{Farnell 1470902} &  \\
\schpt{IC190} & 74HC138N 3-to-8 line Decoder & RS 663-0036 (£0.267@10), Farnell 1826779 (£0.29) &  \\
\schpt{IC191}–\schpt{IC192} & 74HC541N Octal 3-state buffer & RS 714-0953 (£0.18@20), Farnell 1470755 (£0.25) &  \\
\schpt{IC193}–\schpt{IC194} & 74HC138N 3-to-8 line Decoder & RS 663-0036 (£0.267@10), Farnell 1826779 (£0.29) &  \\
\schpt{IC195}–\schpt{IC196} & 74HC574 8-bit D Flip Flop bus driver & RS 714-0950 (£0.18@20), Farnell 380830 (£0.42@10) &  \\
\schpt{IC197}–\schpt{IC198} & Dual 4-input AND gate & Farnell 1740011 (£0.23), RS 709-2665 (£0.163@20) &  \\
\schpt{IC199}–\schpt{IC200} & 74HC541N Octal 3-state buffer & RS 714-0953 (£0.18@20), Farnell 1470755 (£0.25) &  \\
\schpt{IC201} & 74HC00 4× NAND gate & RS 169-6012 (£0.26), Farnell 9590889 (£0.38) &  \\
\schpt{IC202} & Dual J-K negative edge triggered FLIP FLOP, preset and clear & RS 663-1893 (£0.219@10), Farnell 1749804 (£0.39) &  \\
\schpt{IC203} & 74HC01N Quad 2-input NAND gate, open drain &  &  \\
\schpt{IC204}–\schpt{IC205} & 74HC00 4× NAND gate & RS 169-6012 (£0.26), Farnell 9590889 (£0.38) &  \\
\schpt{IC206} & Dual 4-input AND gate & Farnell 1740011 (£0.23), RS 709-2665 (£0.163@20) &  \\
\schpt{IC207}–\schpt{IC208} & 74LS123N Dual retriggerable monostable multivibrator & \href{http://uk.farnell.com/jsp/search/productdetail.jsp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\%2FglobalsearchE14.jsp}{Farnell 1470902} &  \\
\schpt{IC209} & 74HC08 4× AND gate & RS 709-2845 (£0.201@10), Farnell 9665803 (£0.22@10) &  \\
\schpt{IC210}–\schpt{IC211} & Quad 2-input OR gate &  &  \\
\schpt{IC212}–\schpt{IC213} & Quad bus BUFFER, 3-state &  &  \\
\schpt{IC214} & Octal BUFFER and LINE DRIVER, 3-state &  &  \\
\schpt{J1}–\schpt{J4} & 3-pin 2.54mm header & RS 251-8092 (£0.078@25) &  \\
\schpt{JP1} & JUMPER &  &  \\
\schpt{JP2} & PIN HEADER &  &  \\
\schpt{JP3} & 2×20-pin shrouded/keyed header & RS 670-1825 (£0.972@5), Farnell 1099261 (£1.07) &  \\
\schpt{JP4}–\schpt{JP6} & 3-pin 2.54mm header & RS 251-8092 (£0.078@25) &  \\
\schpt{JP7}–\schpt{JP8} & 2-pin 2.54mm header & RS 251-8086 (£0.046@25) &  \\
\schpt{JP9}–\schpt{JP13} & 3-pin 2.54mm header & RS 251-8092 (£0.078@25) &  \\
\schpt{JP14} & 2×20-pin shrouded/keyed header & RS 670-1825 (£0.972@5), Farnell 1099261 (£1.07) &  \\
\schpt{LED1} & 3mm PCB LED. &  &  \\
\schpt{LED2} & 5mm LED &  &  \\
\schpt{LED3}–\schpt{LED13} & 5mm green LED & RS 228-6004 (£0.042), Farnell 1855549 (£0.42) &  \\
\schpt{LED14}–\schpt{LED22} & 5mm red LED & RS 228-5988 (£0.042@5), Farnell 1581217 (£0.165) &  \\
\schpt{LED23}–\schpt{LED25} & 5mm green LED & RS 228-6004 (£0.042), Farnell 1855549 (£0.42) &  \\
\schpt{LED26}–\schpt{LED43} & 5mm red LED & RS 228-5988 (£0.042@5), Farnell 1581217 (£0.165) &  \\
\schpt{LED44}–\schpt{LED51} & 5mm amber/orange/yellow LED & RS 228-6010 (£0.042), Farnell 1142581 (£0.21) &  \\
\schpt{LED52} & 5mm green LED & RS 228-6004 (£0.042), Farnell 1855549 (£0.42) &  \\
\schpt{LED53}–\schpt{LED78} & 5mm red LED & RS 228-5988 (£0.042@5), Farnell 1581217 (£0.165) &  \\
\schpt{LED79} & 5mm amber/orange/yellow LED & RS 228-6010 (£0.042), Farnell 1142581 (£0.21) &  \\
\schpt{LED80} & 5mm red LED & RS 228-5988 (£0.042@5), Farnell 1581217 (£0.165) &  \\
\schpt{LED81}–\schpt{LED84} & 5mm amber/orange/yellow LED & RS 228-6010 (£0.042), Farnell 1142581 (£0.21) &  \\
\schpt{LED85}–\schpt{LED88} & 5mm green LED & RS 228-6004 (£0.042), Farnell 1855549 (£0.42) &  \\
\schpt{LED89}–\schpt{LED91} & 5mm red LED & RS 228-5988 (£0.042@5), Farnell 1581217 (£0.165) &  \\
\schpt{LED92}–\schpt{LED95} & 5mm amber/orange/yellow LED & RS 228-6010 (£0.042), Farnell 1142581 (£0.21) &  \\
\schpt{LED96} & 5mm red LED & RS 228-5988 (£0.042@5), Farnell 1581217 (£0.165) &  \\
\schpt{LED97}–\schpt{LED100} & 5mm amber/orange/yellow LED & RS 228-6010 (£0.042), Farnell 1142581 (£0.21) &  \\
\schpt{LED101}–\schpt{LED103} & 5mm red LED & RS 228-5988 (£0.042@5), Farnell 1581217 (£0.165) &  \\
\schpt{LED104}–\schpt{LED105} & 5mm amber/orange/yellow LED & RS 228-6010 (£0.042), Farnell 1142581 (£0.21) &  \\
\schpt{LED106} & 5mm green LED & RS 228-6004 (£0.042), Farnell 1855549 (£0.42) &  \\
\schpt{LED107} & 5mm red LED & RS 228-5988 (£0.042@5), Farnell 1581217 (£0.165) &  \\
\schpt{LED108} & 5mm amber/orange/yellow LED & RS 228-6010 (£0.042), Farnell 1142581 (£0.21) &  \\
\schpt{LED109}–\schpt{LED114} & 5mm green LED & RS 228-6004 (£0.042), Farnell 1855549 (£0.42) &  \\
\schpt{LED115} & 5mm red LED & RS 228-5988 (£0.042@5), Farnell 1581217 (£0.165) &  \\
\schpt{LED116}–\schpt{LED118} & 5mm amber/orange/yellow LED & RS 228-6010 (£0.042), Farnell 1142581 (£0.21) &  \\
\schpt{LED119}–\schpt{LED121} & 5mm green LED & RS 228-6004 (£0.042), Farnell 1855549 (£0.42) &  \\
\schpt{LED122}–\schpt{LED145} & 5mm red LED & RS 228-5988 (£0.042@5), Farnell 1581217 (£0.165) &  \\
\schpt{LED146}–\schpt{LED153} & 5mm green LED & RS 228-6004 (£0.042), Farnell 1855549 (£0.42) &  \\
\schpt{P1} & 8x1 2.54mm female wirewrap header &  & Or other stackable \\
\schpt{P2} & 6x1 2.54mm female wirewrap header &  & Or other stackable \\
\schpt{P3} & 8x1 2.54mm female wirewrap header &  & Or other stackable \\
\schpt{P4}–\schpt{P7} & 6x1 2.54mm female wirewrap header &  & Or other stackable \\
\schpt{Q1} & CRYSTAL &  &  \\
\schpt{R1}–\schpt{R4} & 47kΩ resistor, 0.25W & RS 131-334 (£0.014@10), Farnell 9339540 (£0.011@50) &  \\
\schpt{R5} & 330Ω resistor, 0.25W & RS 707-7622 (£0.014@10), Farnell 9339418 (£0.011@50) &  \\
\schpt{R6} & 470Ω resistor, 0.25W & RS 131-211 (£0.014@10), Farnell 9339531 (£0.011@50) &  \\
\schpt{R7} & 47kΩ resistor, 0.25W & RS 131-334 (£0.014@10), Farnell 9339540 (£0.011@50) &  \\
\schpt{R8} & 100Ω resistor, 0.25W & RS 131-132 (£0.014@10), Farnell 9339043 (£0.011@50) &  \\
\schpt{R9} & 1kΩ resistor, 0.25W & RS 131-255 (£0.014@10), Farnell 9339051 (£0.011@50) &  \\
\schpt{R10} & 330Ω resistor, 0.25W & RS 707-7622 (£0.014@10), Farnell 9339418 (£0.011@50) &  \\
\schpt{R12} & 50kΩ resistor, 0.25W & RS 131-457 (£0.014@10), Farnell 9339558 (£0.011@50) & Actually 47kΩ (cheaper) \\
\schpt{R13} & 330Ω resistor, 0.25W & RS 707-7622 (£0.014@10), Farnell 9339418 (£0.011@50) &  \\
\schpt{R14}–\schpt{R20} & 47kΩ resistor, 0.25W & RS 131-334 (£0.014@10), Farnell 9339540 (£0.011@50) &  \\
\schpt{R21}–\schpt{R26} & 47Ω resistor, 0.25W & RS 131-097 (£0.014@10), Farnell 9339523 (£0.011@50) &  \\
\schpt{R27}–\schpt{R29} & 47kΩ resistor, 0.25W & RS 131-334 (£0.014@10), Farnell 9339540 (£0.011@50) &  \\
\schpt{R30}–\schpt{R36} & 330Ω resistor, 0.25W & RS 707-7622 (£0.014@10), Farnell 9339418 (£0.011@50) &  \\
\schpt{R37}–\schpt{R39} & 1MΩ resistor 0.25W & RS 131-615 (£0.014@10), Farnell 9339086 (£0.011@50) &  \\
\schpt{R40}–\schpt{R41} & 47kΩ resistor, 0.25W & RS 131-334 (£0.014@10), Farnell 9339540 (£0.011@50) &  \\
\schpt{R42}–\schpt{R43} & 330Ω resistor, 0.25W & RS 707-7622 (£0.014@10), Farnell 9339418 (£0.011@50) &  \\
\schpt{R44} & 10MΩ resistor, 0.25W & RS 135-667 (£0.014@10), Farnell 1186248 (£0.012@50) &  \\
\schpt{R45} & 300kΩ resistor, 0.25W & RS 707-7864 (£0.015@10), Farnell 9341714 (£0.025@50) &  \\
\schpt{R46}–\schpt{R47} & 47kΩ resistor, 0.25W & RS 131-334 (£0.014@10), Farnell 9339540 (£0.011@50) &  \\
\schpt{R48} & 200k linear potentiometer/trimmer & \href{http://uk.farnell.com/jsp/search/productdetail.jsp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\%2FglobalsearchE14.jsp}{Farnell 1689846} &  \\
\schpt{R49} & 180kΩ resistor, 0.25W & RS 131-520 (£0.014@10), Farnell 9339264 (£0.011@50) &  \\
\schpt{R50} & 1kΩ resistor, 0.25W & RS 131-255 (£0.014@10), Farnell 9339051 (£0.011@50) &  \\
\schpt{R51} & 200k linear potentiometer/trimmer & \href{http://uk.farnell.com/jsp/search/productdetail.jsp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\%2FglobalsearchE14.jsp}{Farnell 1689846} &  \\
\schpt{R52} & 300kΩ resistor, 0.25W & RS 707-7864 (£0.015@10), Farnell 9341714 (£0.025@50) &  \\
\schpt{R53} & 47kΩ resistor, 0.25W & RS 131-334 (£0.014@10), Farnell 9339540 (£0.011@50) &  \\
\schpt{R54}–\schpt{R61} & 300kΩ resistor, 0.25W & RS 707-7864 (£0.015@10), Farnell 9341714 (£0.025@50) &  \\
\schpt{R62} & 47kΩ resistor, 0.25W & RS 131-334 (£0.014@10), Farnell 9339540 (£0.011@50) &  \\
\schpt{R63} & 1kΩ resistor, 0.25W & RS 131-255 (£0.014@10), Farnell 9339051 (£0.011@50) &  \\
\schpt{R64}–\schpt{R65} & 47kΩ resistor, 0.25W & RS 131-334 (£0.014@10), Farnell 9339540 (£0.011@50) &  \\
\schpt{R66} & 1kΩ resistor, 0.25W & RS 131-255 (£0.014@10), Farnell 9339051 (£0.011@50) &  \\
\schpt{RN1} & 8×4.7kΩ resistor network & Farnell 1602072 (£0.041), RS 522-4289 (£0.31@25) &  \\
\schpt{RN2} & 3×4.7kΩ resistor network & Farnell 9356347 (£0.24@5) &  \\
\schpt{RN3} & 5×4.7kΩ resistor network & Farnell 1973120 (£0.065@10) &  \\
\schpt{RN4}–\schpt{RN6} & 8×4.7kΩ resistor network & Farnell 1602072 (£0.041), RS 522-4289 (£0.31@25) &  \\
\schpt{RN7} & 7×4.7kΩ resistor network & Farnell 1973129 (£0.085@10) &  \\
\schpt{RN8}–\schpt{RN11} & 8×330Ω resistor, DIL packaged & RS 707-7622 (£0.014@10), Farnell 9339418 (£0.011@50) & Discretes used for protytping. \\
\schpt{RN12} & 3×4.7kΩ resistor network & Farnell 9356347 (£0.24@5) &  \\
\schpt{RN13} & 8×4.7kΩ resistor network & Farnell 1602072 (£0.041), RS 522-4289 (£0.31@25) &  \\
\schpt{RN14}–\schpt{RN15} & 8×330Ω resistor network & Farnell 9356975 (£0.30@5) &  \\
\schpt{RN16}–\schpt{RN17} & 8×4.7kΩ resistor network & Farnell 1602072 (£0.041), RS 522-4289 (£0.31@25) &  \\
\schpt{RN18} & 7×4.7kΩ resistor network & Farnell 1973129 (£0.085@10) &  \\
\schpt{RN19} & 8×10kΩ resistor network & Farnell 1973130 (£0.085@10) &  \\
\schpt{RN20} & 8×50kΩ resistor network & RS 131-457 (£0.014@10), Farnell 9339558 (£0.011@50) & Uses 47kΩ discretes for prototyping. \\
\schpt{RN21} & 8×10kΩ resistor network & Farnell 1973130 (£0.085@10) &  \\
\schpt{RN22} & 8×50kΩ resistor network & RS 131-457 (£0.014@10), Farnell 9339558 (£0.011@50) & Uses 47kΩ discretes for prototyping. \\
\schpt{RN23} & 10kΩ 6x bussed SIL resistor & \href{http://uk.farnell.com/jsp/search/productdetail.jsp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\%2FglobalsearchE14.jsp}{Farnell 1973163} &  \\
\schpt{RN24} & 8×50kΩ resistor network & RS 131-457 (£0.014@10), Farnell 9339558 (£0.011@50) & Uses 47kΩ discretes for prototyping. \\
\schpt{RN25}–\schpt{RN31} & 8×330Ω resistor network & Farnell 1602072 (£0.041), RS 522-4289 (£0.31@25) &  \\
\schpt{RN32} & 180Ω 8x bussed SIL resistor & \href{http://uk.farnell.com/jsp/search/productdetail.jsp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\%2FglobalsearchE14.jsp}{Farnell 9356843} &  \\
\schpt{RN33}–\schpt{RN36} & 8×330Ω resistor network & Farnell 1602072 (£0.041), RS 522-4289 (£0.31@25) &  \\
\schpt{RN37}–\schpt{RN40} & 8×4.7kΩ resistor network & Farnell 1602072 (£0.041), RS 522-4289 (£0.31@25) &  \\
\schpt{RN41} & 3×4.7kΩ resistor network & Farnell 9356347 (£0.24@5) &  \\
\schpt{RN42}–\schpt{RN43} & 8×4.7kΩ resistor network & Farnell 1602072 (£0.041), RS 522-4289 (£0.31@25) &  \\
\schpt{RN44}–\schpt{RN45} & 8×330Ω resistor network & Farnell 1602072 (£0.041), RS 522-4289 (£0.31@25) &  \\
\schpt{RN46} & 8×330Ω resistor network & Farnell 9356975 (£0.30@5) &  \\
\schpt{RN48}–\schpt{RN51} & 8×4.7kΩ resistor network & Farnell 1602072 (£0.041), RS 522-4289 (£0.31@25) &  \\
\schpt{RN52} & 8×330Ω resistor network & Farnell 9356975 (£0.30@5) &  \\
\schpt{RV10} & 470Ω linear potentiometer & Farnell 1227517 (£0.24) &  \\
\schpt{RV11} & 4.7kΩ linear potentiometer & Farnell 1227523 (£0.23) &  \\
\schpt{S1} & Tactile switch & Farnell 1813689 (£0.185) &  \\
\schpt{S2}–\schpt{S17} & On-On toggle switch & Farnell 9473785 (£0.57) + Farnell 9812229 (£0.46) & Switch body and separate black/red actuators \\
\schpt{S18} & Double-pole 3-position key switch & \href{http://uk.rs-online.com/web/p/products/2195835/}{RS 219-5835}, \href{http://uk.rs-online.com/web/p/products/6932284/}{RS 693-2284} & Make-before-break \\
\schpt{S19}–\schpt{S20} & On-On toggle switch & Farnell 9473785 (£0.57) + Farnell 9812229 (£0.46) & Switch body and separate black/red actuators \\
\schpt{S21} & On-Off-On toggle switch & \href{http://uk.farnell.com/jsp/search/productdetail.jsp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\%2FglobalsearchE14.jsp}{Farnell 9473807} & Also add lever actuator \\
\schpt{S22} & Mom-Off-Mom toggle switch & \href{http://uk.farnell.com/jsp/search/productdetail.jsp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\%2FglobalsearchE14.jsp}{Farnell 9473769} &  \\
\schpt{S23} & Mom-Off-Mom toggle switch & \href{http://uk.farnell.com/jsp/search/productdetail.jsp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\%2FglobalsearchE14.jsp}{Farnell 9473815} &  \\
\schpt{S24}–\schpt{S25} & Mom-Off-Mom toggle switch & \href{http://uk.farnell.com/jsp/search/productdetail.jsp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\%2FglobalsearchE14.jsp}{Farnell 9473769} &  \\
\schpt{S26}–\schpt{S29} & Mom-Off-Mom toggle switch & \href{http://uk.farnell.com/jsp/search/productdetail.jsp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\%2FglobalsearchE14.jsp}{Farnell 9473815} &  \\
\schpt{S30} & On-Off-On toggle switch & \href{http://uk.farnell.com/jsp/search/productdetail.jsp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\%2FglobalsearchE14.jsp}{Farnell 9473807} & Also add lever actuator \\
\schpt{S31}–\schpt{S32} & Mom-Off-Mom toggle switch & \href{http://uk.farnell.com/jsp/search/productdetail.jsp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\%2FglobalsearchE14.jsp}{Farnell 9473769} &  \\
\schpt{SV1}–\schpt{SV9} & PIN HEADER &  &  \\
\schpt{SV10} & 3x2 pin header &  &  \\
\schpt{SW1} & 3x dip switch or 2x3 pin header & \href{http://uk.farnell.com/jsp/search/productdetail.jsp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\%2FglobalsearchE14.jsp}{Farnell 1522004} &  \\
\schpt{SW2}–\schpt{SW3} & 8-way DIP switch &  & Through hole \\
\schpt{X3} & WAGO SCREW CLAMP &  &  \\
\schpt{XTAL1} & 16 MHz & RS 547-5487 (£1.43) Farnell 7942710 (£1.54) & May need to reduce frequency. 4 MHz: RS 547-5392. 10 MHz: 547-5421. 12 MHz: RS 547-5459 \\
