alexiosc/cft/documentation/latex/hardware_guide/cft-bom-values.tex

203$\times$ & 0.1μF ceramic capacitor & \schpt{C1}–\schpt{C9}, \schpt{C11}–\schpt{C14}, \schpt{C17}–\schpt{C21}, \schpt{C23}–\schpt{C28}, \schpt{C33}–\schpt{C37}, \schpt{C39}–\schpt{C46}, \schpt{C48}–\schpt{C50}, \schpt{C52}–\schpt{C55}, \schpt{C57}–\schpt{C65}, \schpt{C67}–\schpt{C71}, \schpt{C73}–\schpt{C77}, \schpt{C79}–\schpt{C86}, \schpt{C88}–\schpt{C95}, \schpt{C97}–\schpt{C106}, \schpt{C108}–\schpt{C111}, \schpt{C113}–\schpt{C116}, \schpt{C118}–\schpt{C122}, \schpt{C127}–\schpt{C129}, \schpt{C134}–\schpt{C145}, \schpt{C147}–\schpt{C158}, \schpt{C160}–\schpt{C165}, \schpt{C171}, \schpt{C173}, \schpt{C191}–\schpt{C195}, \schpt{C198}–\schpt{C211}, \schpt{C215}–\schpt{C220}, \schpt{C239}–\schpt{C240}, \schpt{C245}–\schpt{C247}, \schpt{C250}–\schpt{C256}, \schpt{C258}–\schpt{C261}, \schpt{C272}–\schpt{C281}, \schpt{C283}–\schpt{C287}, \schpt{C289}–\schpt{C298} & RS 721-5240 (£0.051@50) / Farnell 9411887 (£0.062) &  \\
57$\times$ & 1μF capacitor & \schpt{C10}, \schpt{C22}, \schpt{C29}–\schpt{C32}, \schpt{C38}, \schpt{C47}, \schpt{C51}, \schpt{C56}, \schpt{C66}, \schpt{C72}, \schpt{C78}, \schpt{C87}, \schpt{C96}, \schpt{C107}, \schpt{C112}, \schpt{C117}, \schpt{C123}–\schpt{C126}, \schpt{C130}–\schpt{C133}, \schpt{C146}, \schpt{C159}, \schpt{C166}–\schpt{C170}, \schpt{C172}, \schpt{C174}–\schpt{C175}, \schpt{C196}–\schpt{C197}, \schpt{C214}, \schpt{C221}, \schpt{C229}–\schpt{C230}, \schpt{C248}–\schpt{C249}, \schpt{C257}, \schpt{C262}–\schpt{C270}, \schpt{C282}, \schpt{C288}, \schpt{C299} & Farnell 3322210 (£0.148), RS 538-1578 (£0.292), Farnell 1100398 (£0.38) &  \\
2$\times$ & 10µF electrolytic capacitor & \schpt{C15}–\schpt{C16} & Farnell 1902928 (£0.033), RS 440-6547 (£0.026@50) &  \\
13$\times$ & 1 μF electrolytic capacitor & \schpt{C176}–\schpt{C187}, \schpt{C304} & Farnell 1236655 (£0.034) & Through hole \\
3$\times$ & 10 µF electrolytic capacitor & \schpt{C188}–\schpt{C190} & Farnell 1902928 (£0.033), RS 440-6547 (£0.026@50) &  \\
2$\times$ & 22 pF ceramic capacitor & \schpt{C212}–\schpt{C213} & Farnell 9411674 (£0.035@25) &  \\
1$\times$ & 100uF Electrolytic capacitor & \schpt{C222} & \href{http://uk.farnell.com/jsp/search/productdetail.jsp?\_dyncharset=UTF-8&searchTerms=1902882&\_D%3AsearchTerms=+&%2Fpf%2Fsearch%2FTextSearchFormHandler.search=GO&\_D%3A%2Fpf%2Fsearch%2FTextSearchFormHandler.search=+&s=&%2Fpf%2Fsearch%2FTextSearchFormHandler.suggestions=false&\_D%3A%2Fpf%2Fsearch%2FTextSearchFormHandler.suggestions=+&%2Fpf%2Fsearch%2FTextSearchFormHandler.ref=globalsearch&\_D%3A%2Fpf%2Fsearch%2FTextSearchFormHandler.ref=+&\_D%3ArohsVal=+&%2Fpf%2Fsearch%2FTextSearchFormHandler.onlyRoHSProductsActive=true&\_D%3A%2Fpf%2Fsearch%2FTextSearchFormHandler.onlyRoHSProductsActive=+&\_DARGS=%2Fjsp%2Fcommonfragments\%2FglobalsearchE14.jsp}{Farnell 1902882} &  \\
16$\times$ & 1μF electrolytic capacitor & \schpt{C223}–\schpt{C226}, \schpt{C231}–\schpt{C238}, \schpt{C241}–\schpt{C244} & Farnell 1236655 (£0.034) &  \\
1$\times$ & 22nF capacitor & \schpt{C227} & \href{http://uk.farnell.com/jsp/search/productdetail.jsp?\_dyncharset=UTF-8&searchTerms=9411860&\_D%3AsearchTerms=+&%2Fpf%2Fsearch%2FTextSearchFormHandler.search=GO&\_D%3A%2Fpf%2Fsearch%2FTextSearchFormHandler.search=+&s=&%2Fpf%2Fsearch%2FTextSearchFormHandler.suggestions=false&\_D%3A%2Fpf%2Fsearch%2FTextSearchFormHandler.suggestions=+&%2Fpf%2Fsearch%2FTextSearchFormHandler.ref=globalsearch&\_D%3A%2Fpf%2Fsearch%2FTextSearchFormHandler.ref=+&\_D%3ArohsVal=+&%2Fpf%2Fsearch%2FTextSearchFormHandler.onlyRoHSProductsActive=true&\_D%3A%2Fpf%2Fsearch%2FTextSearchFormHandler.onlyRoHSProductsActive=+&\_DARGS=%2Fjsp%2Fcommonfragments\%2FglobalsearchE14.jsp}{Farnell 9411860} &  \\
1$\times$ & 4.7μF Electrolytic capacitor & \schpt{C228} & \href{http://uk.farnell.com/jsp/search/productdetail.jsp?\_dyncharset=UTF-8&searchTerms=1902916&\_D%3AsearchTerms=+&%2Fpf%2Fsearch%2FTextSearchFormHandler.search=GO&\_D%3A%2Fpf%2Fsearch%2FTextSearchFormHandler.search=+&s=&%2Fpf%2Fsearch%2FTextSearchFormHandler.suggestions=false&\_D%3A%2Fpf%2Fsearch%2FTextSearchFormHandler.suggestions=+&%2Fpf%2Fsearch%2FTextSearchFormHandler.ref=globalsearch&\_D%3A%2Fpf%2Fsearch%2FTextSearchFormHandler.ref=+&\_D%3ArohsVal=+&%2Fpf%2Fsearch%2FTextSearchFormHandler.onlyRoHSProductsActive=true&\_D%3A%2Fpf%2Fsearch%2FTextSearchFormHandler.onlyRoHSProductsActive=+&\_DARGS=%2Fjsp%2Fcommonfragments\%2FglobalsearchE14.jsp}{Farnell 1902916} &  \\
1$\times$ & 10μF/10V Electrolytic capacitor & \schpt{C271} & \href{http://uk.farnell.com/jsp/search/productdetail.jsp?\_dyncharset=UTF-8&searchTerms=1902928&\_D%3AsearchTerms=+&%2Fpf%2Fsearch%2FTextSearchFormHandler.search=GO&\_D%3A%2Fpf%2Fsearch%2FTextSearchFormHandler.search=+&s=&%2Fpf%2Fsearch%2FTextSearchFormHandler.suggestions=false&\_D%3A%2Fpf%2Fsearch%2FTextSearchFormHandler.suggestions=+&%2Fpf%2Fsearch%2FTextSearchFormHandler.ref=globalsearch&\_D%3A%2Fpf%2Fsearch%2FTextSearchFormHandler.ref=+&\_D%3ArohsVal=+&%2Fpf%2Fsearch%2FTextSearchFormHandler.onlyRoHSProductsActive=true&\_D%3A%2Fpf%2Fsearch%2FTextSearchFormHandler.onlyRoHSProductsActive=+&\_DARGS=%2Fjsp%2Fcommonfragments\%2FglobalsearchE14.jsp}{Farnell 1902928} &  \\
4$\times$ & 100nF capacitor & \schpt{C300}–\schpt{C303} & \href{http://uk.farnell.com/jsp/search/productdetail.jsp?\_dyncharset=UTF-8&searchTerms=1469310&\_D%3AsearchTerms=+&%2Fpf%2Fsearch%2FTextSearchFormHandler.search=GO&\_D%3A%2Fpf%2Fsearch%2FTextSearchFormHandler.search=+&s=&%2Fpf%2Fsearch%2FTextSearchFormHandler.suggestions=false&\_D%3A%2Fpf%2Fsearch%2FTextSearchFormHandler.suggestions=+&%2Fpf%2Fsearch%2FTextSearchFormHandler.ref=globalsearch&\_D%3A%2Fpf%2Fsearch%2FTextSearchFormHandler.ref=+&\_D%3ArohsVal=+&%2Fpf%2Fsearch%2FTextSearchFormHandler.onlyRoHSProductsActive=true&\_D%3A%2Fpf%2Fsearch%2FTextSearchFormHandler.onlyRoHSProductsActive=+&\_DARGS=%2Fjsp%2Fcommonfragments\%2FglobalsearchE14.jsp}{Farnell 1469310} &  \\
30$\times$ & 8x1 pin 2.54mm centre header & \schpt{CON1}–\schpt{CON10}, \schpt{CON16}–\schpt{CON19}, \schpt{CON21}–\schpt{CON31}, \schpt{CON33}–\schpt{CON37} & \href{http://uk.farnell.com/jsp/search/productdetail.jsp?\_dyncharset=UTF-8&searchTerms=1756826&\_D%3AsearchTerms=+&%2Fpf%2Fsearch%2FTextSearchFormHandler.search=GO&\_D%3A%2Fpf%2Fsearch%2FTextSearchFormHandler.search=+&s=&%2Fpf%2Fsearch%2FTextSearchFormHandler.suggestions=false&\_D%3A%2Fpf%2Fsearch%2FTextSearchFormHandler.suggestions=+&%2Fpf%2Fsearch%2FTextSearchFormHandler.ref=globalsearch&\_D%3A%2Fpf%2Fsearch%2FTextSearchFormHandler.ref=+&\_D%3ArohsVal=+&%2Fpf%2Fsearch%2FTextSearchFormHandler.onlyRoHSProductsActive=true&\_D%3A%2Fpf%2Fsearch%2FTextSearchFormHandler.onlyRoHSProductsActive=+&\_DARGS=%2Fjsp%2Fcommonfragments\%2FglobalsearchE14.jsp}{Farnell 1756826} & Molex KK® series header \\
2$\times$ & DB9 male or 2×5 pin header & \schpt{CON11}–\schpt{CON12} & Farnell 1099289 (£0.48@5) &  \\
1$\times$ & DB9 female or 2×5-pin header & \schpt{CON13} & Farnell 1099294 (£0.48@5) &  \\
2$\times$ & 2x20 pin shrouded header & \schpt{CON14}–\schpt{CON15} & RS 670-1825 (£0.972@5), Farnell 1099261 (£1.07) & IDE socket \\
2$\times$ & 9x1 pin 2.54mm centre header & \schpt{CON20}, \schpt{CON32} & \href{http://uk.farnell.com/jsp/search/productdetail.jsp?\_dyncharset=UTF-8&searchTerms=1756827&\_D%3AsearchTerms=+&%2Fpf%2Fsearch%2FTextSearchFormHandler.search=GO&\_D%3A%2Fpf%2Fsearch%2FTextSearchFormHandler.search=+&s=&%2Fpf%2Fsearch%2FTextSearchFormHandler.suggestions=false&\_D%3A%2Fpf%2Fsearch%2FTextSearchFormHandler.suggestions=+&%2Fpf%2Fsearch%2FTextSearchFormHandler.ref=globalsearch&\_D%3A%2Fpf%2Fsearch%2FTextSearchFormHandler.ref=+&\_D%3ArohsVal=+&%2Fpf%2Fsearch%2FTextSearchFormHandler.onlyRoHSProductsActive=true&\_D%3A%2Fpf%2Fsearch%2FTextSearchFormHandler.onlyRoHSProductsActive=+&\_DARGS=%2Fjsp%2Fcommonfragments\%2FglobalsearchE14.jsp}{Farnell 1756827} & Molex KK® series header \\
1$\times$ & 1N5817 Schottky barrier rectifier & \schpt{D1} & Farnell 1843507 (£0.023) &  \\
3$\times$ & 1N4148 diode & \schpt{D2}–\schpt{D4} & \href{http://uk.farnell.com/jsp/search/productdetail.jsp?\_dyncharset=UTF-8&searchTerms=9565124&\_D%3AsearchTerms=+&%2Fpf%2Fsearch%2FTextSearchFormHandler.search=GO&\_D%3A%2Fpf%2Fsearch%2FTextSearchFormHandler.search=+&s=&%2Fpf%2Fsearch%2FTextSearchFormHandler.suggestions=false&\_D%3A%2Fpf%2Fsearch%2FTextSearchFormHandler.suggestions=+&%2Fpf%2Fsearch%2FTextSearchFormHandler.ref=globalsearch&\_D%3A%2Fpf%2Fsearch%2FTextSearchFormHandler.ref=+&\_D%3ArohsVal=+&%2Fpf%2Fsearch%2FTextSearchFormHandler.onlyRoHSProductsActive=true&\_D%3A%2Fpf%2Fsearch%2FTextSearchFormHandler.onlyRoHSProductsActive=+&\_DARGS=%2Fjsp%2Fcommonfragments\%2FglobalsearchE14.jsp}{Farnell 9565124} & Or any fast signal diode \\
1$\times$ & 96-pin (A+B+C) DIN-41612 Bauform ‘C’ plug & \schpt{EXP} & Farnell 1656159 (£1.84) & Right angle through hole \\
1$\times$ & Wago 2x screw clamp & \schpt{FPPOWER} &  &  \\
3$\times$ & 74HC253 Dual 4:1 multiplexer, 3-state & \schpt{IC1}, \schpt{IC5}, \schpt{IC100} & Farnell 1753491 (£0.28), RS 709-3046 (£0.147@10) &  \\
13$\times$ & 74HC112N & \schpt{IC2}, \schpt{IC6}, \schpt{IC58}–\schpt{IC60}, \schpt{IC96}, \schpt{IC114}, \schpt{IC122}, \schpt{IC124}, \schpt{IC126}–\schpt{IC128}, \schpt{IC202} & RS 663-1893 (£0.219@10), Farnell 1749804 (£0.39) &  \\
7$\times$ & 74HC00 4× NAND gate & \schpt{IC3}–\schpt{IC4}, \schpt{IC7}, \schpt{IC94}, \schpt{IC201}, \schpt{IC204}–\schpt{IC205} & RS 169-6012 (£0.26), Farnell 9590889 (£0.38) &  \\
1$\times$ & LM556N Dual timer & \schpt{IC8} & Farnell 9488260 (£1.18), RS 536-0947 (£0.77@10) & May replace with 2×555 + 1×decoupling cap \\
6$\times$ & 74HC14N Hex inverting Schmitt trigger & \schpt{IC9}, \schpt{IC150}, \schpt{IC164}, \schpt{IC170}–\schpt{IC171}, \schpt{IC174} & Farnell 7455513 (£0.133@10), RS 714-0899 (£0.164@20) &  \\
1$\times$ & 74HC05 6× open drain inverter & \schpt{IC10} & Farnell 1470855 (£0.54), RS 442-921 (£0.52) &  \\
40$\times$ & 74HC541N Octal 3-state buffer & \schpt{IC11}–\schpt{IC12}, \schpt{IC19}–\schpt{IC21}, \schpt{IC28}–\schpt{IC29}, \schpt{IC43}–\schpt{IC44}, \schpt{IC48}–\schpt{IC49}, \schpt{IC51}–\schpt{IC52}, \schpt{IC71}–\schpt{IC74}, \schpt{IC79}–\schpt{IC82}, \schpt{IC87}–\schpt{IC88}, \schpt{IC91}–\schpt{IC92}, \schpt{IC117}–\schpt{IC118}, \schpt{IC121}, \schpt{IC131}, \schpt{IC133}, \schpt{IC179}–\schpt{IC184}, \schpt{IC191}–\schpt{IC192}, \schpt{IC199}–\schpt{IC200} & RS 714-0953 (£0.18@20), Farnell 1470755 (£0.25) &  \\
1$\times$ & 74HC590N & \schpt{IC13} &  &  \\
1$\times$ & 74HC08 & \schpt{IC14} &  &  \\
2$\times$ & 74HC161 & \schpt{IC15}, \schpt{IC24} &  &  \\
7$\times$ & 29x010 1 MBit (128k x 8) Flash RAM & \schpt{IC16}–\schpt{IC18}, \schpt{IC102}–\schpt{IC104}, \schpt{IC109} & Farnell 1907092 (£1.58) & May use '020 or '040 if not available. \\
4$\times$ & 74HC540N Octal 3-state inverting buffer & \schpt{IC22}–\schpt{IC23}, \schpt{IC125}, \schpt{IC139} & \href{http://uk.farnell.com/jsp/search/productdetail.jsp?\_dyncharset=UTF-8&searchTerms=1868632&\_D%3AsearchTerms=+&%2Fpf%2Fsearch%2FTextSearchFormHandler.search=GO&\_D%3A%2Fpf%2Fsearch%2FTextSearchFormHandler.search=+&s=&%2Fpf%2Fsearch%2FTextSearchFormHandler.suggestions=false&\_D%3A%2Fpf%2Fsearch%2FTextSearchFormHandler.suggestions=+&%2Fpf%2Fsearch%2FTextSearchFormHandler.ref=globalsearch&\_D%3A%2Fpf%2Fsearch%2FTextSearchFormHandler.ref=+&\_D%3ArohsVal=+&%2Fpf%2Fsearch%2FTextSearchFormHandler.onlyRoHSProductsActive=true&\_D%3A%2Fpf%2Fsearch%2FTextSearchFormHandler.onlyRoHSProductsActive=+&\_DARGS=%2Fjsp%2Fcommonfragments\%2FglobalsearchE14.jsp}{Farnell 1868632} &  \\
16$\times$ & 74HC138N 3-to-8 line Decoder & \schpt{IC25}–\schpt{IC26}, \schpt{IC55}, \schpt{IC101}, \schpt{IC111}–\schpt{IC112}, \schpt{IC123}, \schpt{IC134}, \schpt{IC140}, \schpt{IC146}, \schpt{IC151}, \schpt{IC153}, \schpt{IC178}, \schpt{IC190}, \schpt{IC193}–\schpt{IC194} & RS 663-0036 (£0.267@10), Farnell 1826779 (£0.29) &  \\
1$\times$ & 74HC32D & \schpt{IC27} &  &  \\
2$\times$ & 74AC32N & \schpt{IC30}, \schpt{IC33} &  &  \\
1$\times$ & 74AC08N & \schpt{IC31} &  &  \\
1$\times$ & 74AC86N & \schpt{IC32} &  &  \\
1$\times$ & 74AC00 4× NAND gate & \schpt{IC34} & Farnell 1607805 (£0.48), RS 709-2223 (£0.124@10) &  \\
2$\times$ & 74AC251D & \schpt{IC35}–\schpt{IC36} &  &  \\
1$\times$ & 74AC175D & \schpt{IC37} &  &  \\
2$\times$ & 74HC373 Octal D-type transparent latch, negative edge triggered & \schpt{IC38}, \schpt{IC169} & RS 714-0922 (£0.182@20), Farnell 1607705 (£0.52@10) &  \\
4$\times$ & 74AC541N & \schpt{IC39}–\schpt{IC40}, \schpt{IC64}–\schpt{IC65} &  &  \\
7$\times$ & 74HC574 8-bit D Flip Flop bus driver & \schpt{IC41}–\schpt{IC42}, \schpt{IC97}–\schpt{IC98}, \schpt{IC129}, \schpt{IC195}–\schpt{IC196} & RS 714-0950 (£0.18@20), Farnell 380830 (£0.42@10) &  \\
8$\times$ & 74HC08 4× AND gate & \schpt{IC45}, \schpt{IC56}, \schpt{IC93}, \schpt{IC105}, \schpt{IC113}, \schpt{IC130}, \schpt{IC132}, \schpt{IC209} & RS 709-2845 (£0.201@10), Farnell 9665803 (£0.22@10) &  \\
2$\times$ & 74HC273N & \schpt{IC46}–\schpt{IC47} & Farnell 9591397 (£0.34), RS 714-0925 (£0.175@20) &  \\
4$\times$ & 74HC688 8-bit magnitude/identity comparator & \schpt{IC50}, \schpt{IC54}, \schpt{IC89}–\schpt{IC90} & RS 709-2179 (£0.168@5), Farnell 9591672 (£0.67@10) &  \\
1$\times$ & 74HC175N & \schpt{IC53} &  &  \\
6$\times$ & 74HC32N & \schpt{IC57}, \schpt{IC95}, \schpt{IC99}, \schpt{IC110}, \schpt{IC156}, \schpt{IC158} &  &  \\
4$\times$ & 74HC21N & \schpt{IC61}, \schpt{IC197}–\schpt{IC198}, \schpt{IC206} & Farnell 1740011 (£0.23), RS 709-2665 (£0.163@20) &  \\
4$\times$ & 74HC245 Octal bus transceiver, 3-state & \schpt{IC62}–\schpt{IC63}, \schpt{IC148}–\schpt{IC149} & RS 714-0916 (£0.18@20), RS 169-6113 (£0.38), Farnell 380714 (£0.49) &  \\
1$\times$ & 74ACT06N & \schpt{IC66} &  &  \\
12$\times$ & 74HC193N & \schpt{IC67}–\schpt{IC70}, \schpt{IC75}–\schpt{IC78}, \schpt{IC83}–\schpt{IC86} & Farnell 1470793 (£0.34), RS 527-372 (£0.29@25) &  \\
1$\times$ & 74HC74N & \schpt{IC106} &  &  \\
2$\times$ & 29F020 & \schpt{IC107}–\schpt{IC108} & Farnell 8749493 (£2.84) / Farnell 1565992 & Using 040 due to lack of availability. \\
4$\times$ & 74HC670 4×4-bit register file, 3-state & \schpt{IC115}–\schpt{IC116}, \schpt{IC119}–\schpt{IC120} & Farnell 1753519 (£1.31), Farnell 1753520 (£0.77) & Cheaper order code is for SOIC (better stocks) \\
2$\times$ & 29x040 4 MBit (512k x 8) Flash RAM & \schpt{IC135}, \schpt{IC137} & Farnell 8749493 (£2.84) / Farnell 1565992 &  \\
2$\times$ & 4 MBit (512k x 8) Static RAM & \schpt{IC136}, \schpt{IC138} & Farnell 1562900 (£4.71) &  \\
2$\times$ & 26C92 Dual UART & \schpt{IC141}–\schpt{IC142} & Farnell 1294820 (£2.18), RS 821-756 (£5) &  \\
3$\times$ & MAX-232 RS-232 transceiver & \schpt{IC143}–\schpt{IC145} & Farnell 1648737 (£0.73), RS 660-8613 (£0.68@5) &  \\
1$\times$ & 74HC05 6× open drain inverter & \schpt{IC147} & Farnell 1470855 (£0.54), RS 442-921 (£0.52) &  \\
3$\times$ & 74HC374 Octal D-type transparent latch, positive edge triggered & \schpt{IC152}, \schpt{IC154}–\schpt{IC155} & RS 714-0931 (£0.191@20), RS 169-6141 (£0.38), Farnell 380763 (£0.57), Farnell 380763 (£0.38@10) &  \\
2$\times$ & 74HC03N Quad 2-input NAND gate, open collector output & \schpt{IC157}, \schpt{IC176} & \href{http://uk.farnell.com/jsp/search/productdetail.jsp?\_dyncharset=UTF-8&searchTerms=1282849&\_D%3AsearchTerms=+&%2Fpf%2Fsearch%2FTextSearchFormHandler.search=GO&\_D%3A%2Fpf%2Fsearch%2FTextSearchFormHandler.search=+&s=&%2Fpf%2Fsearch%2FTextSearchFormHandler.suggestions=false&\_D%3A%2Fpf%2Fsearch%2FTextSearchFormHandler.suggestions=+&%2Fpf%2Fsearch%2FTextSearchFormHandler.ref=globalsearch&\_D%3A%2Fpf%2Fsearch%2FTextSearchFormHandler.ref=+&\_D%3ArohsVal=+&%2Fpf%2Fsearch%2FTextSearchFormHandler.onlyRoHSProductsActive=true&\_D%3A%2Fpf%2Fsearch%2FTextSearchFormHandler.onlyRoHSProductsActive=+&\_DARGS=%2Fjsp%2Fcommonfragments\%2FglobalsearchE14.jsp}{Farnell 1282849} &  \\
1$\times$ & 5V, 16 kbit (2k×8) NVRAM & RTC & \schpt{IC159} & Farnell 1224444 (£13.14) &  \\
2$\times$ & 74HC153N & \schpt{IC160}–\schpt{IC161} &  &  \\
2$\times$ & 82C54 & \schpt{IC162}–\schpt{IC163} & \href{http://uk.farnell.com/jsp/search/productdetail.jsp?\_dyncharset=UTF-8&searchTerms=1018175&\_D%3AsearchTerms=+&%2Fpf%2Fsearch%2FTextSearchFormHandler.search=GO&\_D%3A%2Fpf%2Fsearch%2FTextSearchFormHandler.search=+&s=&%2Fpf%2Fsearch%2FTextSearchFormHandler.suggestions=false&\_D%3A%2Fpf%2Fsearch%2FTextSearchFormHandler.suggestions=+&%2Fpf%2Fsearch%2FTextSearchFormHandler.ref=globalsearch&\_D%3A%2Fpf%2Fsearch%2FTextSearchFormHandler.ref=+&\_D%3ArohsVal=+&%2Fpf%2Fsearch%2FTextSearchFormHandler.onlyRoHSProductsActive=true&\_D%3A%2Fpf%2Fsearch%2FTextSearchFormHandler.onlyRoHSProductsActive=+&\_DARGS=%2Fjsp%2Fcommonfragments\%2FglobalsearchE14.jsp}{Farnell 1018175} &  \\
8$\times$ & 74LS123N Dual retriggerable monostable multivibrator & \schpt{IC165}, \schpt{IC177}, \schpt{IC186}–\schpt{IC189}, \schpt{IC207}–\schpt{IC208} & \href{http://uk.farnell.com/jsp/search/productdetail.jsp?\_dyncharset=UTF-8&searchTerms=1470902&\_D%3AsearchTerms=+&%2Fpf%2Fsearch%2FTextSearchFormHandler.search=GO&\_D%3A%2Fpf%2Fsearch%2FTextSearchFormHandler.search=+&s=&%2Fpf%2Fsearch%2FTextSearchFormHandler.suggestions=false&\_D%3A%2Fpf%2Fsearch%2FTextSearchFormHandler.suggestions=+&%2Fpf%2Fsearch%2FTextSearchFormHandler.ref=globalsearch&\_D%3A%2Fpf%2Fsearch%2FTextSearchFormHandler.ref=+&\_D%3ArohsVal=+&%2Fpf%2Fsearch%2FTextSearchFormHandler.onlyRoHSProductsActive=true&\_D%3A%2Fpf%2Fsearch%2FTextSearchFormHandler.onlyRoHSProductsActive=+&\_DARGS=%2Fjsp%2Fcommonfragments\%2FglobalsearchE14.jsp}{Farnell 1470902} &  \\
1$\times$ & LM555N Timer & \schpt{IC166} & RS 534-3469 (£0.62), Farnell 1564692 (£0.52@10) &  \\
4$\times$ & 74HC04N Hex inverter & \schpt{IC167}, \schpt{IC172}–\schpt{IC173}, \schpt{IC175} & \href{http://uk.farnell.com/jsp/search/productdetail.jsp?\_dyncharset=UTF-8&searchTerms=2374080&\_D%3AsearchTerms=+&%2Fpf%2Fsearch%2FTextSearchFormHandler.search=GO&\_D%3A%2Fpf%2Fsearch%2FTextSearchFormHandler.search=+&s=&%2Fpf%2Fsearch%2FTextSearchFormHandler.suggestions=false&\_D%3A%2Fpf%2Fsearch%2FTextSearchFormHandler.suggestions=+&%2Fpf%2Fsearch%2FTextSearchFormHandler.ref=globalsearch&\_D%3A%2Fpf%2Fsearch%2FTextSearchFormHandler.ref=+&\_D%3ArohsVal=+&%2Fpf%2Fsearch%2FTextSearchFormHandler.onlyRoHSProductsActive=true&\_D%3A%2Fpf%2Fsearch%2FTextSearchFormHandler.onlyRoHSProductsActive=+&\_DARGS=%2Fjsp%2Fcommonfragments\%2FglobalsearchE14.jsp}{Farnell 2374080} &  \\
1$\times$ & 74HCT00N Quad 2-input NAND gate & \schpt{IC168} & \href{http://uk.farnell.com/jsp/search/productdetail.jsp?\_dyncharset=UTF-8&searchTerms=2373749&\_D%3AsearchTerms=+&%2Fpf%2Fsearch%2FTextSearchFormHandler.search=GO&\_D%3A%2Fpf%2Fsearch%2FTextSearchFormHandler.search=+&s=&%2Fpf%2Fsearch%2FTextSearchFormHandler.suggestions=false&\_D%3A%2Fpf%2Fsearch%2FTextSearchFormHandler.suggestions=+&%2Fpf%2Fsearch%2FTextSearchFormHandler.ref=globalsearch&\_D%3A%2Fpf%2Fsearch%2FTextSearchFormHandler.ref=+&\_D%3ArohsVal=+&%2Fpf%2Fsearch%2FTextSearchFormHandler.onlyRoHSProductsActive=true&\_D%3A%2Fpf%2Fsearch%2FTextSearchFormHandler.onlyRoHSProductsActive=+&\_DARGS=%2Fjsp%2Fcommonfragments\%2FglobalsearchE14.jsp}{Farnell 2373749} &  \\
1$\times$ & 74HC85N 4-bit Magnitude Comparator & \schpt{IC185} & \href{http://uk.farnell.com/jsp/search/productdetail.jsp?\_dyncharset=UTF-8&searchTerms=1868642&\_D%3AsearchTerms=+&%2Fpf%2Fsearch%2FTextSearchFormHandler.search=GO&\_D%3A%2Fpf%2Fsearch%2FTextSearchFormHandler.search=+&s=&%2Fpf%2Fsearch%2FTextSearchFormHandler.suggestions=false&\_D%3A%2Fpf%2Fsearch%2FTextSearchFormHandler.suggestions=+&%2Fpf%2Fsearch%2FTextSearchFormHandler.ref=globalsearch&\_D%3A%2Fpf%2Fsearch%2FTextSearchFormHandler.ref=+&\_D%3ArohsVal=+&%2Fpf%2Fsearch%2FTextSearchFormHandler.onlyRoHSProductsActive=true&\_D%3A%2Fpf%2Fsearch%2FTextSearchFormHandler.onlyRoHSProductsActive=+&\_DARGS=%2Fjsp%2Fcommonfragments\%2FglobalsearchE14.jsp}{Farnell 1868642} &  \\
1$\times$ & 74HC01N Quad 2-input NAND gate, open drain & \schpt{IC203} &  &  \\
2$\times$ & 74HCT32N & \schpt{IC210}–\schpt{IC211} &  &  \\
2$\times$ & 74HC125N & \schpt{IC212}–\schpt{IC213} &  &  \\
1$\times$ & 74HCT541N & \schpt{IC214} &  &  \\
12$\times$ & 3-pin 2.54mm header & \schpt{J1}–\schpt{J4}, \schpt{JP4}–\schpt{JP6}, \schpt{JP9}–\schpt{JP13} & RS 251-8092 (£0.078@25) &  \\
1$\times$ &  & \schpt{JP1} &  &  \\
1$\times$ &  & \schpt{JP2} &  &  \\
2$\times$ & 2×20-pin shrouded/keyed header & \schpt{JP3}, \schpt{JP14} & RS 670-1825 (£0.972@5), Farnell 1099261 (£1.07) &  \\
2$\times$ & 2-pin 2.54mm header & \schpt{JP7}–\schpt{JP8} & RS 251-8086 (£0.046@25) &  \\
1$\times$ &  & \schpt{LED1} &  &  \\
1$\times$ &  & \schpt{LED2} &  &  \\
37$\times$ & 5mm green LED & \schpt{LED3}–\schpt{LED13}, \schpt{LED23}–\schpt{LED25}, \schpt{LED52}, \schpt{LED85}–\schpt{LED88}, \schpt{LED106}, \schpt{LED109}–\schpt{LED114}, \schpt{LED119}–\schpt{LED121}, \schpt{LED146}–\schpt{LED153} & RS 228-6004 (£0.042), Farnell 1855549 (£0.42) &  \\
87$\times$ & 5mm red LED & \schpt{LED14}–\schpt{LED22}, \schpt{LED26}–\schpt{LED43}, \schpt{LED53}–\schpt{LED78}, \schpt{LED80}, \schpt{LED89}–\schpt{LED91}, \schpt{LED96}, \schpt{LED101}–\schpt{LED103}, \schpt{LED107}, \schpt{LED115}, \schpt{LED122}–\schpt{LED145} & RS 228-5988 (£0.042@5), Farnell 1581217 (£0.165) &  \\
27$\times$ & 5mm amber/orange/yellow LED & \schpt{LED44}–\schpt{LED51}, \schpt{LED79}, \schpt{LED81}–\schpt{LED84}, \schpt{LED92}–\schpt{LED95}, \schpt{LED97}–\schpt{LED100}, \schpt{LED104}–\schpt{LED105}, \schpt{LED108}, \schpt{LED116}–\schpt{LED118} & RS 228-6010 (£0.042), Farnell 1142581 (£0.21) &  \\
2$\times$ & 8x1 2.54mm female wirewrap header & \schpt{P1}, \schpt{P3} &  & Or other stackable \\
5$\times$ & 6x1 2.54mm female wirewrap header & \schpt{P2}, \schpt{P4}–\schpt{P7} &  & Or other stackable \\
1$\times$ & 32.768kHz & \schpt{Q1} &  &  \\
23$\times$ & 47kΩ resistor, 0.25W & \schpt{R1}–\schpt{R4}, \schpt{R7}, \schpt{R14}–\schpt{R20}, \schpt{R27}–\schpt{R29}, \schpt{R40}–\schpt{R41}, \schpt{R46}–\schpt{R47}, \schpt{R53}, \schpt{R62}, \schpt{R64}–\schpt{R65} & RS 131-334 (£0.014@10), Farnell 9339540 (£0.011@50) &  \\
12$\times$ & 330Ω resistor, 0.25W & \schpt{R5}, \schpt{R10}, \schpt{R13}, \schpt{R30}–\schpt{R36}, \schpt{R42}–\schpt{R43} & RS 707-7622 (£0.014@10), Farnell 9339418 (£0.011@50) &  \\
1$\times$ & 470Ω resistor, 0.25W & \schpt{R6} & RS 131-211 (£0.014@10), Farnell 9339531 (£0.011@50) &  \\
1$\times$ & 100Ω resistor, 0.25W & \schpt{R8} & RS 131-132 (£0.014@10), Farnell 9339043 (£0.011@50) &  \\
4$\times$ & 1kΩ resistor, 0.25W & \schpt{R9}, \schpt{R50}, \schpt{R63}, \schpt{R66} & RS 131-255 (£0.014@10), Farnell 9339051 (£0.011@50) &  \\
1$\times$ & 50kΩ resistor, 0.25W & \schpt{R12} & RS 131-457 (£0.014@10), Farnell 9339558 (£0.011@50) & Actually 47kΩ (cheaper) \\
6$\times$ & 47Ω resistor, 0.25W & \schpt{R21}–\schpt{R26} & RS 131-097 (£0.014@10), Farnell 9339523 (£0.011@50) &  \\
3$\times$ & 1MΩ resistor 0.25W & \schpt{R37}–\schpt{R39} & RS 131-615 (£0.014@10), Farnell 9339086 (£0.011@50) &  \\
1$\times$ & 10MΩ resistor, 0.25W & \schpt{R44} & RS 135-667 (£0.014@10), Farnell 1186248 (£0.012@50) &  \\
10$\times$ & 300kΩ resistor, 0.25W & \schpt{R45}, \schpt{R52}, \schpt{R54}–\schpt{R61} & RS 707-7864 (£0.015@10), Farnell 9341714 (£0.025@50) &  \\
2$\times$ & 200k linear potentiometer/trimmer & \schpt{R48}, \schpt{R51} & \href{http://uk.farnell.com/jsp/search/productdetail.jsp?\_dyncharset=UTF-8&searchTerms=1689846&\_D%3AsearchTerms=+&%2Fpf%2Fsearch%2FTextSearchFormHandler.search=GO&\_D%3A%2Fpf%2Fsearch%2FTextSearchFormHandler.search=+&s=&%2Fpf%2Fsearch%2FTextSearchFormHandler.suggestions=false&\_D%3A%2Fpf%2Fsearch%2FTextSearchFormHandler.suggestions=+&%2Fpf%2Fsearch%2FTextSearchFormHandler.ref=globalsearch&\_D%3A%2Fpf%2Fsearch%2FTextSearchFormHandler.ref=+&\_D%3ArohsVal=+&%2Fpf%2Fsearch%2FTextSearchFormHandler.onlyRoHSProductsActive=true&\_D%3A%2Fpf%2Fsearch%2FTextSearchFormHandler.onlyRoHSProductsActive=+&\_DARGS=%2Fjsp%2Fcommonfragments\%2FglobalsearchE14.jsp}{Farnell 1689846} &  \\
1$\times$ & 180kΩ resistor, 0.25W & \schpt{R49} & RS 131-520 (£0.014@10), Farnell 9339264 (£0.011@50) &  \\
17$\times$ & 8×4.7kΩ resistor network & \schpt{RN1}, \schpt{RN4}–\schpt{RN6}, \schpt{RN13}, \schpt{RN16}–\schpt{RN17}, \schpt{RN37}–\schpt{RN40}, \schpt{RN42}–\schpt{RN43}, \schpt{RN48}–\schpt{RN51} & Farnell 1602072 (£0.041), RS 522-4289 (£0.31@25) &  \\
3$\times$ & 3×4.7kΩ resistor network & \schpt{RN2}, \schpt{RN12}, \schpt{RN41} & Farnell 9356347 (£0.24@5) &  \\
1$\times$ & 5×4.7kΩ resistor network & \schpt{RN3} & Farnell 1973120 (£0.065@10) &  \\
2$\times$ & 7×4.7kΩ resistor network & \schpt{RN7}, \schpt{RN18} & Farnell 1973129 (£0.085@10) &  \\
4$\times$ & 8×330Ω resistor, DIL packaged & \schpt{RN8}–\schpt{RN11} & RS 707-7622 (£0.014@10), Farnell 9339418 (£0.011@50) & Discretes used for protytping. \\
4$\times$ & 8×330Ω resistor network & \schpt{RN14}–\schpt{RN15}, \schpt{RN46}, \schpt{RN52} & Farnell 9356975 (£0.30@5) &  \\
2$\times$ & 8×10kΩ resistor network & \schpt{RN19}, \schpt{RN21} & Farnell 1973130 (£0.085@10) &  \\
3$\times$ & 8×50kΩ resistor network & \schpt{RN20}, \schpt{RN22}, \schpt{RN24} & RS 131-457 (£0.014@10), Farnell 9339558 (£0.011@50) & Uses 47kΩ discretes for prototyping. \\
1$\times$ & 10kΩ 6x bussed SIL resistor & \schpt{RN23} & \href{http://uk.farnell.com/jsp/search/productdetail.jsp?\_dyncharset=UTF-8&searchTerms=1973163&\_D%3AsearchTerms=+&%2Fpf%2Fsearch%2FTextSearchFormHandler.search=GO&\_D%3A%2Fpf%2Fsearch%2FTextSearchFormHandler.search=+&s=&%2Fpf%2Fsearch%2FTextSearchFormHandler.suggestions=false&\_D%3A%2Fpf%2Fsearch%2FTextSearchFormHandler.suggestions=+&%2Fpf%2Fsearch%2FTextSearchFormHandler.ref=globalsearch&\_D%3A%2Fpf%2Fsearch%2FTextSearchFormHandler.ref=+&\_D%3ArohsVal=+&%2Fpf%2Fsearch%2FTextSearchFormHandler.onlyRoHSProductsActive=true&\_D%3A%2Fpf%2Fsearch%2FTextSearchFormHandler.onlyRoHSProductsActive=+&\_DARGS=%2Fjsp%2Fcommonfragments\%2FglobalsearchE14.jsp}{Farnell 1973163} &  \\
13$\times$ & 8×330Ω resistor network & \schpt{RN25}–\schpt{RN31}, \schpt{RN33}–\schpt{RN36}, \schpt{RN44}–\schpt{RN45} & Farnell 1602072 (£0.041), RS 522-4289 (£0.31@25) &  \\
1$\times$ & 180Ω 8x bussed SIL resistor & \schpt{RN32} & \href{http://uk.farnell.com/jsp/search/productdetail.jsp?\_dyncharset=UTF-8&searchTerms=9356843&\_D%3AsearchTerms=+&%2Fpf%2Fsearch%2FTextSearchFormHandler.search=GO&\_D%3A%2Fpf%2Fsearch%2FTextSearchFormHandler.search=+&s=&%2Fpf%2Fsearch%2FTextSearchFormHandler.suggestions=false&\_D%3A%2Fpf%2Fsearch%2FTextSearchFormHandler.suggestions=+&%2Fpf%2Fsearch%2FTextSearchFormHandler.ref=globalsearch&\_D%3A%2Fpf%2Fsearch%2FTextSearchFormHandler.ref=+&\_D%3ArohsVal=+&%2Fpf%2Fsearch%2FTextSearchFormHandler.onlyRoHSProductsActive=true&\_D%3A%2Fpf%2Fsearch%2FTextSearchFormHandler.onlyRoHSProductsActive=+&\_DARGS=%2Fjsp%2Fcommonfragments\%2FglobalsearchE14.jsp}{Farnell 9356843} &  \\
1$\times$ & 470Ω linear potentiometer & \schpt{RV10} & Farnell 1227517 (£0.24) &  \\
1$\times$ & 4.7kΩ linear potentiometer & \schpt{RV11} & Farnell 1227523 (£0.23) &  \\
1$\times$ & Tactile switch & \schpt{S1} & Farnell 1813689 (£0.185) &  \\
18$\times$ & On-On toggle switch & \schpt{S2}–\schpt{S17}, \schpt{S19}–\schpt{S20} & Farnell 9473785 (£0.57) + Farnell 9812229 (£0.46) & Switch body and separate black/red actuators \\
1$\times$ & Double-pole 3-position key switch & \schpt{S18} & \href{http://uk.rs-online.com/web/p/products/2195835/}{RS 219-5835}, \href{http://uk.rs-online.com/web/p/products/6932284/}{RS 693-2284} & Make-before-break \\
2$\times$ & On-Off-On toggle switch & \schpt{S21}, \schpt{S30} & \href{http://uk.farnell.com/jsp/search/productdetail.jsp?\_dyncharset=UTF-8&searchTerms=9473807&\_D%3AsearchTerms=+&%2Fpf%2Fsearch%2FTextSearchFormHandler.search=GO&\_D%3A%2Fpf%2Fsearch%2FTextSearchFormHandler.search=+&s=&%2Fpf%2Fsearch%2FTextSearchFormHandler.suggestions=false&\_D%3A%2Fpf%2Fsearch%2FTextSearchFormHandler.suggestions=+&%2Fpf%2Fsearch%2FTextSearchFormHandler.ref=globalsearch&\_D%3A%2Fpf%2Fsearch%2FTextSearchFormHandler.ref=+&\_D%3ArohsVal=+&%2Fpf%2Fsearch%2FTextSearchFormHandler.onlyRoHSProductsActive=true&\_D%3A%2Fpf%2Fsearch%2FTextSearchFormHandler.onlyRoHSProductsActive=+&\_DARGS=%2Fjsp%2Fcommonfragments\%2FglobalsearchE14.jsp}{Farnell 9473807} & Also add lever actuator \\
5$\times$ & Mom-Off-Mom toggle switch & \schpt{S22}, \schpt{S24}–\schpt{S25}, \schpt{S31}–\schpt{S32} & \href{http://uk.farnell.com/jsp/search/productdetail.jsp?\_dyncharset=UTF-8&searchTerms=9473769&\_D%3AsearchTerms=+&%2Fpf%2Fsearch%2FTextSearchFormHandler.search=GO&\_D%3A%2Fpf%2Fsearch%2FTextSearchFormHandler.search=+&s=&%2Fpf%2Fsearch%2FTextSearchFormHandler.suggestions=false&\_D%3A%2Fpf%2Fsearch%2FTextSearchFormHandler.suggestions=+&%2Fpf%2Fsearch%2FTextSearchFormHandler.ref=globalsearch&\_D%3A%2Fpf%2Fsearch%2FTextSearchFormHandler.ref=+&\_D%3ArohsVal=+&%2Fpf%2Fsearch%2FTextSearchFormHandler.onlyRoHSProductsActive=true&\_D%3A%2Fpf%2Fsearch%2FTextSearchFormHandler.onlyRoHSProductsActive=+&\_DARGS=%2Fjsp%2Fcommonfragments\%2FglobalsearchE14.jsp}{Farnell 9473769} &  \\
5$\times$ & Mom-Off-Mom toggle switch & \schpt{S23}, \schpt{S26}–\schpt{S29} & \href{http://uk.farnell.com/jsp/search/productdetail.jsp?\_dyncharset=UTF-8&searchTerms=9473815&\_D%3AsearchTerms=+&%2Fpf%2Fsearch%2FTextSearchFormHandler.search=GO&\_D%3A%2Fpf%2Fsearch%2FTextSearchFormHandler.search=+&s=&%2Fpf%2Fsearch%2FTextSearchFormHandler.suggestions=false&\_D%3A%2Fpf%2Fsearch%2FTextSearchFormHandler.suggestions=+&%2Fpf%2Fsearch%2FTextSearchFormHandler.ref=globalsearch&\_D%3A%2Fpf%2Fsearch%2FTextSearchFormHandler.ref=+&\_D%3ArohsVal=+&%2Fpf%2Fsearch%2FTextSearchFormHandler.onlyRoHSProductsActive=true&\_D%3A%2Fpf%2Fsearch%2FTextSearchFormHandler.onlyRoHSProductsActive=+&\_DARGS=%2Fjsp%2Fcommonfragments\%2FglobalsearchE14.jsp}{Farnell 9473815} &  \\
2$\times$ &  & \schpt{SV1}–\schpt{SV2} &  &  \\
3$\times$ &  & \schpt{SV3}, \schpt{SV8}–\schpt{SV9} &  &  \\
4$\times$ &  & \schpt{SV4}–\schpt{SV7} &  &  \\
1$\times$ & 3x2 pin header & \schpt{SV10} &  &  \\
1$\times$ & 3x dip switch or 2x3 pin header & \schpt{SW1} & \href{http://uk.farnell.com/jsp/search/productdetail.jsp?\_dyncharset=UTF-8&searchTerms=1522004&\_D%3AsearchTerms=+&%2Fpf%2Fsearch%2FTextSearchFormHandler.search=GO&\_D%3A%2Fpf%2Fsearch%2FTextSearchFormHandler.search=+&s=&%2Fpf%2Fsearch%2FTextSearchFormHandler.suggestions=false&\_D%3A%2Fpf%2Fsearch%2FTextSearchFormHandler.suggestions=+&%2Fpf%2Fsearch%2FTextSearchFormHandler.ref=globalsearch&\_D%3A%2Fpf%2Fsearch%2FTextSearchFormHandler.ref=+&\_D%3ArohsVal=+&%2Fpf%2Fsearch%2FTextSearchFormHandler.onlyRoHSProductsActive=true&\_D%3A%2Fpf%2Fsearch%2FTextSearchFormHandler.onlyRoHSProductsActive=+&\_DARGS=%2Fjsp%2Fcommonfragments\%2FglobalsearchE14.jsp}{Farnell 1522004} &  \\
2$\times$ & 8-way DIP switch & \schpt{SW2}–\schpt{SW3} &  & Through hole \\
1$\times$ &  & \schpt{X3} &  &  \\
1$\times$ & 16 MHz & \schpt{XTAL1} & RS 547-5487 (£1.43) Farnell 7942710 (£1.54) & May need to reduce frequency. 4 MHz: RS 547-5392. 10 MHz: 547-5421. 12 MHz: RS 547-5459 \\
1$\times$ & 3.6864 MHz oscillator & \schpt{XTAL2} & RS 547-5386 (£1.53), Farnell 9510095 (£2.94) & For RS-232 interfaces \\
