alexiosc/cft/documentation/BOM/CFT-PB2-smd-revD.html

Qty | Value | Device | Parts
1 |  | VG96-3K | EXP
38 | 0.1uF | C-EUC0805K | C1, C2, C3, C4, C5, C6, C7, C8, C9, C11, C12, C13, C14, C15, C16, C17, C18, C19, C22, C23, C24, C25, C26, C27, C28, C29, C30, C33, C34, C35, C36, C37, C38, C39, C40, C41, C42, C43
8 | 1uF | C-EUC0805K | C10, C20, C21, C31, C32, C44, C45, C48
3 | 30R | CTS742C083 | RN1, RN2, RN3
13 | 30R | R-EU_R0805 | R1, R2, R3, R4, R5, R6, R7, R8, R9, R10, R11, R12, R14
2 | 47uF | CPOL-EUE2.5-5 | C46, C47
2 | 74AHC1G04DBV | 74AHC1G04DBV | IC10, IC36
2 | 74AHC1G08DBV | 74AHC1G08DBV | IC1, IC39
1 | 74HC74D | 74HC74D | IC7
2 | 74HC138D | 74HC138D | IC4, IC9
1 | 74HC139D | 74HC139D | IC19
12 | 74HC193D | 74HC193D | IC11, IC12, IC13, IC14, IC20, IC21, IC22, IC23, IC28, IC29, IC30, IC31
14 | 74HC541DW | 74HC541DW | IC5, IC6, IC15, IC16, IC17, IC18, IC24, IC25, IC26, IC27, IC32, IC33, IC37, IC38
2 | 74HC574D | 74HC574D | IC2, IC3
3 | 74HC688DW | 74HC688DW | IC8, IC34, IC35
4 | 2540-5 | 2540-5 | P1, P2, P3, P4
4 | HOLE | HOLE | U1, U2, U3, U4
2 | OSHW-LOGOL | OSHW-LOGOL | $4_39_$, $4_39_$1
1 | QRCODE-CFT | QRCODE-CFT | $4_40_$
1 | SIGNAL-RENAME | SIGNAL-RENAME | X1
1 | SIGNATURESILK | SIGNATURESILK | $4_37_$
