alexiosc/cft/documentation/BOM/CFT-PB3-revC.html

Qty | Value | Device | Parts
1 |  | SJW | SJ1
1 |  | VG96-3K | EXP
34 | 0.1uF | C-EUC0805K | C1, C2, C3, C4, C5, C6, C7, C8, C9, C10, C11, C12, C13, C14, C17, C18, C19, C20, C21, C27, C28, C29, C33, C34, C35, C36, C37, C38, C39, C40, C41, C42, C43, C44
10 | 1uF | C-EUC0805K | C15, C16, C22, C23, C24, C25, C26, C30, C31, C32
5 | 4k7 | R-EU_R0805 | R7, R8, R11, R12, R13
6 | 29F040 | 29F040PLCC32 | IC17, IC18, IC19, IC22, IC23, IC24
4 | 30R | CTS742C083 | RN1, RN2, RN3, RN4
8 | 30R | R-EU_R0805 | R1, R2, R3, R4, R5, R6, R9, R10
2 | 47uF | CPOL-EUE2.5-5 | C45, C46
1 | 057-020-1 | 057-020-1 | P1
1 | 74AHC1G00DBV | 74AHC1G00DBV | IC4
1 | 74AHC1G04DBV | 74AHC1G04DBV | IC2
3 | 74AHC1G08DBV | 74AHC1G08DBV | IC1, IC3, IC26
1 | 74AHC1G32DBV | 74AHC1G32DBV | IC12
1 | 74HC32D | 74HC32D | IC6
2 | 74HC74D | 74HC74D | IC21, IC27
1 | 74HC112D | 74HC112D | IC7
2 | 74HC138D | 74HC138D | IC14, IC25
1 | 74HC139D | 74HC139D | IC29
3 | 74HC253D | 74HC253D | IC13, IC20, IC28
5 | 74HC541DW | 74HC541DW | IC15, IC16, IC34, IC35, IC36
4 | 74HC574D | 74HC574D | IC8, IC9, IC10, IC11
4 | 74HC670D | 74HC670D | IC30, IC31, IC32, IC33
1 | 330R | R-EU_R0805 | R14
1 | 741G10DBV | 741G10DBV | IC5
2 | 2540-5 | 2540-5 | P2, P3
4 | HOLE | HOLE | U1, U2, U3, U4
1 | LED-5MM-GREEN | LEDCHIPLED_0805 | LED1
2 | OSHW-LOGOL | OSHW-LOGOL | $4_39_$, $4_39_$1
1 | QRCODE-CFT | QRCODE-CFT | $4_40_$
1 | SIGNATURESILK | SIGNATURESILK | $4_37_$
