alexiosc/cft/documentation/BOM/cft-bom-purchase-plan.pdf

source

Qty Part | Eagle Part | Description
2500.1μF ceramic capacitor | C-EU025-024X044 | 0.1μF ceramic capacitor
137330Ω resistor, 0.25W | R-EU_0204/7 | 330Ω resistor, 0.25W
1075mm red LED | LED-5MM-RED | 5mm red LED
531μF capacitor | C-EU025-024X044 | 1μF capacitor
5274HC541N Octal 3-state buffer | 74HC541N | 74HC541N Octal 3-state buffer
444.7kΩ resistor, 0.25W | R-EU_0204/7 | 4.7kΩ resistor, 0.25W
395mm amber/orange/yellow LED | LED-5MM-AMBER | 5mm amber/orange/yellow LED
345mm green LED | LED-5MM-GREEN | 5mm green LED
291 μF electrolytic capacitor | CPOL-EUE2.5-5 | 1 μF electrolytic capacitor
228x1 pin 2.54mm centre header | 22-23-2081 | 8x1 pin 2.54mm centre header
2274HC138N 3-to-8 line Decoder | 74HC138N | 74HC138N 3-to-8 line Decoder
20 On-On toggle switch | TL36PO | On-On toggle switch
178×4.7kΩ resistor network | G08R | 8×4.7kΩ resistor network
161μF electrolytic capacitor | CPOL-EUE1.8-4 | 1μF electrolytic capacitor
15100nF Ceramic Capacitor | C-EU025-024X044 | 100nF Ceramic Capacitor
1574HC574 8-bit D Flip Flop bus driver | 74HC574N | 74HC574 8-bit D Flip Flop bus driver
143-pin 2.54mm header | JP2E | 3-pin 2.54mm header
1474HC193N | 74HC193N
1210k | R-EU_0204/7
1129x040 4 MBit (512k x 8) Flash RAM | 29F040PLCC32 | 29x040 4 MBit (512k x 8) Flash RAM
10 Mom-Off-Mom toggle switch | TL37PO | Mom-Off-Mom toggle switch
10 Mom-Off-Mom toggle switch | TL47PO | Mom-Off-Mom toggle switch
9 10 µF electrolytic capacitor | CPOL-EUE2.5-5 | 10 µF electrolytic capacitor
9 74HC00 4× NAND gate | 74HC00N | 74HC00 4× NAND gate
9 74HC04N Hex inverter | 74HC04N | 74HC04N Hex inverter
8 74HC32 4× OR gate | 74HC32N | 74HC32 4× OR gate
8 74HC112N | 74HC112N
8 LM556N Dual timer | LM556N | LM556N Dual timer
7 2-pin 2.54mm header | JP1E | 2-pin 2.54mm header
7 | MA04-2
7 8×10kΩ resistor, DIL packaged | 8R-N | 8×10kΩ resistor, DIL packaged
7 74HC08 4× AND gate | 74HC08N | 74HC08 4× AND gate
7 74HC74N | 74HC74N
7 20-pin shrouded header | 2540- | 20-pin shrouded header
5 6x1 2.54mm female wirewrap header | FE06-1 | 6x1 2.54mm female wirewrap header
5 1kΩ resistor, 0.25W | R-EU_0204/7 | 1kΩ resistor, 0.25W
5 74HC05 6× open drain inverter | 74HC05N | 74HC05 6× open drain inverter
5 74HC14N Hex inverting Schmitt trigger | 74HC14N | 74HC14N Hex inverting Schmitt trigger

source

5 74HC245 Octal bus transceiver, 3-state | 74HC245N | 74HC245 Octal bus transceiver, 3-state
5 74HC374 Octal D-type transparent latch, positive edge triggered | 74HC374N | 74HC374 Octal D-type transparent latch, positive edge triggered
5 74HC540N Octal 3-state inverting buffer | 74HC540N | 74HC540N Octal 3-state inverting buffer
5 74HC688 8-bit magnitude/identity comparator | 74HC688N | 74HC688 8-bit magnitude/identity comparator
4 | MA06-1
4 2k2 | R-EU_0204/7
4 22 pF ceramic capacitor | C-EU025-024X044 | 22 pF ceramic capacitor
4 74HC273N | 74HC273N
4 8×330Ω resistor network | G08R | 8×330Ω resistor network
4 330R | R-EU_0207/7
4 BC548 NPN Transistor | BC548 | BC548 NPN Transistor
4 On-Off-On toggle switch | TL49PO | On-Off-On toggle switch
3 | MA09-2
3 | PINHD-1X2
3 1MΩ resistor 0.25W | R-EU_0204/7 | 1MΩ resistor 0.25W
3 1N4148 diode | 1N4148DO35-7 | 1N4148 diode
3 3.9kΩ, ¼W Resistor | R-EU_0207/7 | 3.9kΩ, ¼W Resistor
3 33pF ceramic capacitor | C-EU025-024X044 | 33pF ceramic capacitor
3 8×50kΩ resistor network | 8R-N | 8×50kΩ resistor network
3 74HC253 Dual 4:1 multiplexer, 3-state | 74HC253N | 74HC253 Dual 4:1 multiplexer, 3-state
3 74HCT00N Quad 2-input NAND gate | 74HCT00N | 74HCT00N Quad 2-input NAND gate
3 MAX-232 RS-232 transceiver | MAX232 | MAX-232 RS-232 transceiver
3 MCP23016 | MCP23016
2 Double-pole 3-position key switch | 320-938 | Double-pole 3-position key switch
2 8x1 2.54mm female wirewrap header | FE08-1 | 8x1 2.54mm female wirewrap header
2 DB9 male or 2×5 pin header | M09HP | DB9 male or 2×5 pin header
2 | PINHD-1X5
2 | PINHD-1X8
2 2×20-pin shrouded/keyed header | PINHD-2X20 | 2×20-pin shrouded/keyed header
2 8-way DIP switch | SW_DIP-8 | 8-way DIP switch
2 Tactile switch | TAC_SWITCHPTH | Tactile switch
2 96-pin (A+B+C) DIN-41612 Bauform ‘C’ plug | VG96-3K | 96-pin (A+B+C) DIN-41612 Bauform ‘C’ plug
2 1k | R-EU_0207/7
2 3×4.7kΩ resistor network | G03R | 3×4.7kΩ resistor network
2 7×4.7kΩ resistor network | G06R | 7×4.7kΩ resistor network
2 4k7 | R-EU_0207/7
2 10MΩ resistor, 0.25W | R-EU_0204/7 | 10MΩ resistor, 0.25W
2 10Ω, ¼W Resistor | R-EU_0204/7 | 10Ω, ¼W Resistor
2 8×10kΩ resistor network | G08R | 8×10kΩ resistor network
2 27kΩ, ¼W Resistor | R-EU_0204/7 | 27kΩ, ¼W Resistor

source

2 47nF ceramic capacitor | C-EU025-024X044 | 47nF ceramic capacitor
2 47µF electrolytic capacitor | CPOL-EUE2.5-5 | 47µF electrolytic capacitor
2 74HC02N | 74HC02N
2 74HC03N Quad 2-input NAND gate, open collector output | 74HC03N | 74HC03N Quad 2-input NAND gate, open collector output
2 74HC21N | 74HC21N
2 74HC125N | 74HC125N
2 74HC153N | 74HC153N
2 74HC164N | 74HC164N
2 74HC166N | 74HC166N
2 74HC174N | 74HC174N
2 74HC251N | 74HC251N
2 82C54 | 82C54
2 100kΩ linear Trimmer/Potentiometer | TRIM_EU-CT6 | 100kΩ linear Trimmer/Potentiometer
2 220µF electrolytic capacitor | CPOL-EUE2.5-5 | 220µF electrolytic capacitor
2 470Ω resistor, 0.25W | R-EU_0204/7 | 470Ω resistor, 0.25W
2 Speaker, 8 ohm | AL11P | Speaker, 8 ohm
2 4 MBit (512k x 8) Static RAM | 29F040DIP32 | 4 MBit (512k x 8) Static RAM
2 2x20 pin shrouded header | IDE-CONNECTOR | 2x20 pin shrouded header
2 LM386N-1 | LM386N-1
2 LM555N Timer | LM555N | LM555N Timer
2 16C2550 Dual 16550 UART | 16C2550 | 16C2550 Dual 16550 UART
1 DB9 female or 2×5-pin header | F09VP | DB9 female or 2×5-pin header
1 | JP5Q
1 | MA03-1
1 | MA05-1
1 | MA10-2
1 Mini DIN socket, 6-pin (PS/2 keyboard), chassis-mount | MINI_DIN_6 | Mini DIN socket, 6-pin (PS/2 keyboard), chassis-mount
1 | PINHD-1X3
1 | PINHD-1X9
1 3x dip switch or 2x3 pin header | SW_DIP-3 | 3x dip switch or 2x3 pin header
1 | W237-102
1 100nF electrolytic capacitor | CPOL-EUE2.5-5 | 100nF electrolytic capacitor
1 1.8432 MHz Oscillator | XO2-08-14-SOCKET 1.8432 MHz Oscillator
1 1N4002 diode | DIODE-DO41-10 | 1N4002 diode
1 1N5817 Schottky barrier rectifier | 1N5817-B | 1N5817 Schottky barrier rectifier
1 3x2 pin header | MA03-2 | 3x2 pin header
1 4 MHz crystal | XTAL/S | 4 MHz crystal
1 4k7 | G04R
1 5×4.7kΩ resistor network | G05R | 5×4.7kΩ resistor network
1 4.7kΩ linear potentiometer | TRIM_EU-CT6 | 4.7kΩ linear potentiometer

source

1 10kΩ 6x bussed SIL resistor | G06R | 10kΩ 6x bussed SIL resistor
1 10k log | 3RP/1610G
1 10μF/10V Electrolytic capacitor | CPOL-EUE2.5-7 | 10μF/10V Electrolytic capacitor
1 14.7456 MHz Crystal | CRYSTALHC49U-V | 14.7456 MHz Crystal
1 16 MHz Crystal | XO2-08-14-SOCKET 16 MHz Crystal
1 9x1 pin 2.54mm centre header | 22-23-2091 | 9x1 pin 2.54mm centre header
1 32.768 kHz Crystal | CRYSTALTC38H | 32.768 kHz Crystal
1 50kΩ resistor, 0.25W | R-EU_R0805 | 50kΩ resistor, 0.25W
1 50k log | TRIM_EU-CT6
1 74HC85N 4-bit Magnitude Comparator | 74HC85N | 74HC85N 4-bit Magnitude Comparator
1 74HC86N | 74HC86N
1 74HC139N | 74HC139N
1 74HC161 | 4161P
1 74HC373 Octal D-type transparent latch, negative edge triggered | 74HC373N | 74HC373 Octal D-type transparent latch, negative edge triggered
1 74HC590 8-bit registered binary counter | 74HC590N | 74HC590 8-bit registered binary counter
1 74HCT253N | 74HCT253N
1 100Ω resistor, 0.25W | R-EU_0204/7 | 100Ω resistor, 0.25W
1 240Ω, ¼W Resistor | R-EU_0207/7 | 240Ω, ¼W Resistor
1 300kΩ resistor, 0.25W | R-EU_0204/7 | 300kΩ resistor, 0.25W
1 8×330Ω resistor network | GE08R | 8×330Ω resistor network
1 390Ω ¼W Resistor | R-EU_0207/7 | 390Ω ¼W Resistor
1 470Ω linear potentiometer | TRIM_EU-CT6 | 470Ω linear potentiometer
1 560Ω, ¼W Resistor | R-EU_0204/7 | 560Ω, ¼W Resistor
1 680Ω, ¼W Resistor | R-EU_0204/7 | 680Ω, ¼W Resistor
1 1503_09 | 1503_09
1 ATMEGA168 | MEGA8-P
1 AY-3-8910 | AY-3-8910
1 5V, 16 kbit (2k×8) NVRAM & RTC | M48T02 | 5V, 16 kbit (2k×8) NVRAM & RTC
1 SPEAKJET | SPEAKJET
1 WIZ812MJ Ethernet module | WIZ812MJ | WIZ812MJ Ethernet module

source

Farnell | Farnell US | RS Online
Notes | Order Code Price Unit Order Code Price Unit Order Code Price
1694337 0,019 100 | 1694337 0,019 100721-5240 | 0,051
9339418 0,011 | 50 | 707-7622 | 0,014
1581217 0,165 | 1 | 228-5988 | 0,042
3322210 0,148 | 1 | 1600879 0,041 | 25538-1578 | 0,292
1470755 0,25 | 10 | 714-0953 | 0,18
9339540 0,011 | 50 | 131-334 | 0,014
1142581 0,21 | 1 | 228-6010 | 0,042
1855549 0,42 | 1 | 228-6004 | 0,042
Through hole | 1236655 0,034 | 1
Molex KK® series header
1826779 0,29 | 1 | 1318508 0,172 | 10663-0036 | 0,267
Switch body and separate black/red actuators
1602072 0,036 | 10522-4289 | 0,31
1236655 0,034 | 1
9411852 0,059 | 25 | 1694335 0,016 | 10
380830 0,42 | 10 | 714-0950 | 0,18
251-8092 | 0,078
1470793 0,34 | 1 | 527-372 | 0,29
10kΩ, ¼W Resistor | 9339060 0,011 | 50
Socket: Farnell 1103872 (£0.48@10) | 1565992 1,18 | 10
1902928 0,033 | 1 | 440-6547 | 0,026
9590889 0,38 | 1 | 169-6012 | 0,26
9590951 0,23 | 10 | 2374080 0,086 | 1662-9997 | 0,233
1739939 0,27 | 10 | 709-3021 | 0,201
1749804 0,39 | 1 | 663-1893 | 0,219
May replace with 2×555 + 1×decoupling cap | 9488260 1,18 | 1 | 536-0947 | 0,77
251-8086 | 0,046
Discretes used for prototyping | 9339418 0,011 | 50 | 707-7622 | 0,014
9665803 0,22 | 10 | 709-2845 | 0,201
1013916 0,103 | 1 | 714-0975 | 0,15
1099261 1,07 | 1 | 1258972 0,66 | 1670-1825 | 0,972
Or other stackable
9339051 0,011 | 50 | 131-255 | 0,014
1470855 0,54 | 1 | 442-921 | 0,52
7455513 0,133 | 10 | 714-0899 | 0,164

source

Page

6

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
1602072 0,041 | 1 | 522-4289 | 0,31
9339477 0,011 | 50
1227517 0,24 | 1
9339590 0,011 | 50
9339655 0,011 | 50
1224444 13,14 | 1
SpeakJet speech synthesiser

source

Page

9

Unit
50
10
251

20
1011

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
source

1115

20

10
100

10
101551

10

source

2011

101

1051

source

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
Sheet2

Part | Eagle Part | Description
0.1μF ceramic capacitor | C-EU025-024X044 | 0.1μF ceramic capacitor
330Ω resistor, 0.25W | R-EU_0204/7 | 330Ω resistor, 0.25W
5mm red LED | LED-5MM-RED | 5mm red LED
1μF capacitor | C-EU025-024X044 | 1μF capacitor
74HC541N Octal 3-state buffer | 74HC541N | 74HC541N Octal 3-state buffer
4.7kΩ resistor, 0.25W | R-EU_0204/7 | 4.7kΩ resistor, 0.25W
5mm amber/orange/yellow LED | LED-5MM-AMBER | 5mm amber/orange/yellow LED
5mm green LED | LED-5MM-GREEN | 5mm green LED
1 μF electrolytic capacitor | CPOL-EUE2.5-5 | 1 μF electrolytic capacitor
8x1 pin 2.54mm centre header | 22-23-2081 | 8x1 pin 2.54mm centre header
74HC138N 3-to-8 line Decoder | 74HC138N | 74HC138N 3-to-8 line Decoder
On-On toggle switch | TL36PO | On-On toggle switch
8×4.7kΩ resistor network | G08R | 8×4.7kΩ resistor network
1μF electrolytic capacitor | CPOL-EUE1.8-4 | 1μF electrolytic capacitor
74HC574 8-bit D Flip Flop bus driver | 74HC574N | 74HC574 8-bit D Flip Flop bus driver
100nF Ceramic Capacitor | C-EU025-024X044 | 100nF Ceramic Capacitor
74HC193N | 74HC193N
3-pin 2.54mm header | JP2E | 3-pin 2.54mm header
10k | R-EU_0204/7
29x040 4 MBit (512k x 8) Flash RAM | 29F040PLCC32 | 29x040 4 MBit (512k x 8) Flash RAM
Mom-Off-Mom toggle switch | TL37PO | Mom-Off-Mom toggle switch
Mom-Off-Mom toggle switch | TL47PO | Mom-Off-Mom toggle switch
74HC112N | 74HC112N
74HC00 4× NAND gate | 74HC00N | 74HC00 4× NAND gate
74HC32 4× OR gate | 74HC32N | 74HC32 4× OR gate
74HC04N Hex inverter | 74HC04N | 74HC04N Hex inverter
10 µF electrolytic capacitor | CPOL-EUE2.5-5 | 10 µF electrolytic capacitor
LM556N Dual timer | LM556N | LM556N Dual timer

MA04-2
20-pin shrouded header | 2540- | 20-pin shrouded header
74HC08 4× AND gate | 74HC08N | 74HC08 4× AND gate
2-pin 2.54mm header | JP1E | 2-pin 2.54mm header
74HC74N | 74HC74N
8×10kΩ resistor, DIL packaged | 8R-N | 8×10kΩ resistor, DIL packaged
6x1 2.54mm female wirewrap header | FE06-1 | 6x1 2.54mm female wirewrap header
74HC05 6× open drain inverter | 74HC05N | 74HC05 6× open drain inverter
74HC374 Octal D-type transparent latch, positive edge triggered 74HC374N | 74HC374 Octal D-type transparent latch, positive edge triggered
74HC245 Octal bus transceiver, 3-state | 74HC245N | 74HC245 Octal bus transceiver, 3-state
74HC540N Octal 3-state inverting buffer | 74HC540N | 74HC540N Octal 3-state inverting buffer
74HC14N Hex inverting Schmitt trigger | 74HC14N | 74HC14N Hex inverting Schmitt trigger
1kΩ resistor, 0.25W | R-EU_0204/7 | 1kΩ resistor, 0.25W
BC548 NPN Transistor | BC548 | BC548 NPN Transistor
74HC688 8-bit magnitude/identity comparator | 74HC688N | 74HC688 8-bit magnitude/identity comparator
22 pF ceramic capacitor | C-EU025-024X044 | 22 pF ceramic capacitor
74HC273N | 74HC273N
2k2 | R-EU_0204/7
| MA06-1
8×330Ω resistor network | G08R | 8×330Ω resistor network
330R | R-EU_0207/7
On-Off-On toggle switch | TL49PO | On-Off-On toggle switch
| MA09-2
MCP23016 | MCP23016
MAX-232 RS-232 transceiver | MAX232 | MAX-232 RS-232 transceiver
8×50kΩ resistor network | 8R-N | 8×50kΩ resistor network
74HC253 Dual 4:1 multiplexer, 3-state | 74HC253N | 74HC253 Dual 4:1 multiplexer, 3-state
3.9kΩ, ¼W Resistor | R-EU_0207/7 | 3.9kΩ, ¼W Resistor
1N4148 diode | 1N4148DO35-7 | 1N4148 diode
74HCT00N Quad 2-input NAND gate | 74HCT00N | 74HCT00N Quad 2-input NAND gate

PINHD-1X2
33pF ceramic capacitor | C-EU025-024X044 | 33pF ceramic capacitor
1MΩ resistor 0.25W | R-EU_0204/7 | 1MΩ resistor 0.25W
Double-pole 3-position key switch | 320-938 | Double-pole 3-position key switch
8x1 2.54mm female wirewrap header | FE08-1 | 8x1 2.54mm female wirewrap header
| PINHD-1X5
| PINHD-1X8
100kΩ linear Trimmer/Potentiometer | TRIM_EU-CT6 | 100kΩ linear Trimmer/Potentiometer
4 MBit (512k x 8) Static RAM | 29F040DIP32 | 4 MBit (512k x 8) Static RAM
16C2550 Dual 16550 UART | 16C2550 | 16C2550 Dual 16550 UART
96-pin (A+B+C) DIN-41612 Bauform ‘C’ plug | VG96-3K | 96-pin (A+B+C) DIN-41612 Bauform ‘C’ plug
2×20-pin shrouded/keyed header | PINHD-2X20 | 2×20-pin shrouded/keyed header
Speaker, 8 ohm | AL11P | Speaker, 8 ohm
DB9 male or 2×5 pin header | M09HP | DB9 male or 2×5 pin header
2x20 pin shrouded header | IDE-CONNECTOR | 2x20 pin shrouded header
LM555N Timer | LM555N | LM555N Timer
82C54 | 82C54
8-way DIP switch | SW_DIP-8 | 8-way DIP switch
74HC153N | 74HC153N
LM386N-1 | LM386N-1
74HC164N | 74HC164N
3×4.7kΩ resistor network | G03R | 3×4.7kΩ resistor network
74HC166N | 74HC166N
74HC02N | 74HC02N
74HC125N | 74HC125N
74HC174N | 74HC174N
7×4.7kΩ resistor network | G06R | 7×4.7kΩ resistor network
8×10kΩ resistor network | G08R | 8×10kΩ resistor network
74HC21N | 74HC21N
74HC251N | 74HC251N

Tactile switch | TAC_SWITCHPTH | Tactile switch
1k | R-EU_0207/7
4k7 | R-EU_0207/7
10Ω, ¼W Resistor | R-EU_0204/7 | 10Ω, ¼W Resistor
27kΩ, ¼W Resistor | R-EU_0204/7 | 27kΩ, ¼W Resistor
74HC03N Quad 2-input NAND gate, open collector output | 74HC03N | 74HC03N Quad 2-input NAND gate, open collector output
220µF electrolytic capacitor | CPOL-EUE2.5-5 | 220µF electrolytic capacitor
47µF electrolytic capacitor | CPOL-EUE2.5-5 | 47µF electrolytic capacitor
47nF ceramic capacitor | C-EU025-024X044 | 47nF ceramic capacitor
10MΩ resistor, 0.25W | R-EU_0204/7 | 10MΩ resistor, 0.25W
470Ω resistor, 0.25W | R-EU_0204/7 | 470Ω resistor, 0.25W
3x dip switch or 2x3 pin header | SW_DIP-3 | 3x dip switch or 2x3 pin header
3x2 pin header | MA03-2 | 3x2 pin header
10kΩ 6x bussed SIL resistor | G06R | 10kΩ 6x bussed SIL resistor
10k log | 3RP/1610G
10μF/10V Electrolytic capacitor | CPOL-EUE2.5-7 | 10μF/10V Electrolytic capacitor
9x1 pin 2.54mm centre header | 22-23-2091 | 9x1 pin 2.54mm centre header
50k log | TRIM_EU-CT6
240Ω, ¼W Resistor | R-EU_0207/7 | 240Ω, ¼W Resistor
300kΩ resistor, 0.25W | R-EU_0204/7 | 300kΩ resistor, 0.25W
AY-3-8910 | AY-3-8910
5V, 16 kbit (2k×8) NVRAM & RTC | M48T02 | 5V, 16 kbit (2k×8) NVRAM & RTC
SPEAKJET | SPEAKJET

JP5Q
MA03-1
MA05-1
MA10-2
PINHD-1X3

PINHD-1X9
W237-102
WIZ812MJ Ethernet module | WIZ812MJ | WIZ812MJ Ethernet module
1.8432 MHz Oscillator | XO2-08-14-SOCKET | 1.8432 MHz Oscillator
74HC373 Octal D-type transparent latch, negative edge triggered 74HC373N | 74HC373 Octal D-type transparent latch, negative edge triggered
16 MHz Crystal | XO2-08-14-SOCKET | 16 MHz Crystal
DB9 female or 2×5-pin header | F09VP | DB9 female or 2×5-pin header
Mini DIN socket, 6-pin (PS/2 keyboard), chassis-mount | MINI_DIN_6 | Mini DIN socket, 6-pin (PS/2 keyboard), chassis-mount
8×330Ω resistor network | GE08R | 8×330Ω resistor network
74HC85N 4-bit Magnitude Comparator | 74HC85N | 74HC85N 4-bit Magnitude Comparator
74HC590 8-bit registered binary counter | 74HC590N | 74HC590 8-bit registered binary counter
74HC161 | 4161P
74HCT253N | 74HCT253N
74HC139N | 74HC139N
4k7 | G04R
5×4.7kΩ resistor network | G05R | 5×4.7kΩ resistor network
560Ω, ¼W Resistor | R-EU_0204/7 | 560Ω, ¼W Resistor
1503_09 | 1503_09
ATMEGA168 | MEGA8-P
680Ω, ¼W Resistor | R-EU_0204/7 | 680Ω, ¼W Resistor
4.7kΩ linear potentiometer | TRIM_EU-CT6 | 4.7kΩ linear potentiometer
74HC86N | 74HC86N
100nF electrolytic capacitor | CPOL-EUE2.5-5 | 100nF electrolytic capacitor
4 MHz crystal | XTAL/S | 4 MHz crystal
14.7456 MHz Crystal | CRYSTALHC49U-V | 14.7456 MHz Crystal
32.768 kHz Crystal | CRYSTALTC38H | 32.768 kHz Crystal
390Ω ¼W Resistor | R-EU_0207/7 | 390Ω ¼W Resistor
50kΩ resistor, 0.25W | R-EU_R0805 | 50kΩ resistor, 0.25W
100Ω resistor, 0.25W | R-EU_0204/7 | 100Ω resistor, 0.25W
1N4002 diode | DIODE-DO41-10 | 1N4002 diode

470Ω linear potentiometer | TRIM_EU-CT6 | 470Ω linear potentiometer
1N5817 Schottky barrier rectifier | 1N5817-B | 1N5817 Schottky barrier rectifier

Pin headers, 72pin (2x36), 2.54mm pitch | Pin headers, 72pin (2x36), 2.54mm pitch
Ribbon Cable, 40-way, 1.27mm pitch
Roth Elektronik RE840-LF PCB, 233×160mm (53×89)
Roth Elektronik RE320-HP PCB, 160×100mm (37×53)
DIN 41612 connector type 063515 | Bauform C, rows A+C, 64 pin, right angle (card)
2.54mm,pin,DIN 41612,solder,PCB,90°,96w | Bauform C, rows A+B+C, 64 pin, right angle (card)
VeroWire Combs (from RS)
VeroWire Gold/Pink spooled wire for PCB
Wiring pen for PCB
DIP 8 socket
DIP 14 socket

DIP 16 socket
DIP 18 socket
DIP 20 socket
DIP 24 socket
DIP 32 socket
DIP 40 socket
PLCC 32 socket
PLCC 44 socket
IDC 40-pin cable-side socket with relief 40-pin right angle header, shrouded

VAT | 20,00%
Farnell US Surcharge | £15.95
Extra Quantity | 10,00%
Grand Total

Farnell
Notes | Qty Qty + extra Min Qty+ | Bought | Remaining | Order Code Price (£) Unit
| 250 | 275 | 275 | 250 | 25 | 1694337 | 0.019 | 100
| 137 | 151 | 151 | 50 | 101 | 9339418 | 0.011 | 50
| 107 | 118 | 118 | 10 | 108 | 1581217 | 0.165 | 1
| 53 | 58 | 58 | 30 | 28 | 3322210 | 0.148 | 1
| 52 | 57 | 57 | 40 | 17 | 1470755 | 0.250 | 10
| 44 | 48 | 48 | 48 | 0 | 9339540 | 0.011 | 50
| 39 | 43 | 43 | 10 | 33 | 1142581 | 0.210 | 1
| 34 | 37 | 37 | 10 | 27 | 1855549 | 0.420 | 1
Through hole | 29 | 32 | 32 | | 32 | 1236655 | 0.034 | 1
Molex KK® series header | 22 | 24 | 24 | | 24 | | 0.000 | 0
| 22 | 24 | 24 | 12 | 12 | 1826779 | 0.290 | 1
Switch body and separate black/red actuators | 20 | 22 | 22 | | 22 | | 0.000 | 0
| 17 | 19 | 19 | 19 | 0 | | 0.000 | 0
| 16 | 18 | 18 | | 18 | 1236655 | 0.034 | 1
| 15 | 17 | 17 | | 17 | 380830 | 0.420 | 10
| 15 | 17 | 17 | 40 | -23 | 9411852 | 0.059 | 25
| 14 | 15 | 15 | 15 | 0 | 1470793 | 0.340 | 1
| 14 | 15 | 15 | | 15 | | 0.000 | 0
10kΩ, ¼W Resistor | 12 | 13 | 13 | 13 | 0 | 9339060 | 0.011 | 50
Socket: Farnell 1103872 (£0.48@10) | 11 | 12 | 12 | 12 | 0 | 1565992 | 1.180 | 10
| 10 | 11 | 11 | | 11 | | 0.000 | 0
| 10 | 11 | 11 | | 11 | | 0.000 | 0
| 8 | 9 | 9 | 9 | 0 | 1749804 | 0.390 | 1
| 9 | 10 | 10 | 5 | 5 | 9590889 | 0.380 | 1
| 8 | 9 | 9 | 9 | 0 | 1739939 | 0.270 | 10
| 9 | 10 | 10 | 10 | 0 | 9590951 | 0.230 | 10
| 9 | 10 | 10 | 20 | -10 | 1902928 | 0.033 | 1
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
NO PRICING NO PRICING NO PRICING
1183573 | 30 | 2.85

1183574 | 40 | 3.48
1183575 | 5 | 0.60
1183577 | 60 | 7.14
1157740 | 3 | 0.62
1654375 | 2 | 0.54
1183580 | 2 | 0.48
1103872 | 13 | 6.24
2078146 | 3 | 1.46
1099242 | 10 | 6.70
1099251 | 10 | 11.30

285.97
60.38
15.95

362.30
