alexiosc/cft/documentation/latex/cft_book/bom.tex

%%%%%%%%%%%%%%%%%%%%%%%%%%%%%%%%%%%%%%%%%%%%%%%%%%%%%%%%%%%%%%%%%%%%%%%%%%%%%%%
%
% BILL OF MATERIALS (AUTOMATICALLY GENERATED)
%
%%%%%%%%%%%%%%%%%%%%%%%%%%%%%%%%%%%%%%%%%%%%%%%%%%%%%%%%%%%%%%%%%%%%%%%%%%%%%%%

\newcommand\bomv[1]{{%
    \footnotesize
    \zebrarow{10}
    \begin{longtable}{r%
        %@{{\scriptsize(line \number\rownum)\ }}%
        P{0.2\textwidth}P{0.2\textwidth}P{0.15\textwidth}P{0.2\textwidth}}
      %
      % First header
      %
      \hiderowcolors
    \noalign{\smallskip}\hline\noalign{\smallskip}
    \textbf{Qty} & \textbf{Description} & \textbf{Parts} & \textbf{Order No} & \textbf{Notes} \\
    \noalign{\smallskip}\hline\noalign{\smallskip}
    \noalign{\global\rownum 0\relax}\showrowcolors
    \endfirsthead
    %
    % Subsequent headers
    %
    \hiderowcolors
    \multicolumn{5}{l}{\em Continued from previous page.}\\
    \noalign{\smallskip\smallskip}\hline\noalign{\smallskip}
    \textbf{Qty} & \textbf{Description} & \textbf{Parts} & \textbf{Order No} & \textbf{Notes} \\
    \noalign{\smallskip}\hline\noalign{\smallskip}
    \noalign{\global\rownum 1\relax}\showrowcolors
    \endhead
    %
    % Footer
    %
    \hiderowcolors
    \noalign{\smallskip\smallskip}
    \multicolumn{5}{l}{\em Continued on next page.}\\
    \endfoot
    %
    % Last footer
    %
    \hiderowcolors
    \noalign{\smallskip}\hline\noalign{\smallskip}
    \endlastfoot
    %
    % Content
    %
    \showrowcolors
    \input{../generated/#1-bom-values}
  \end{longtable}
}}

%%%%%%%%%%%%%%%%%%%%%%%%%%%%%%%%%%%%%%%%%%%%%%%%%%%%%%%%%%%%%%%%%%%%%%%%%%%%%%%
%
% INDEX OF PARTS (AUTOMATICALLY GENERATED)
%
%%%%%%%%%%%%%%%%%%%%%%%%%%%%%%%%%%%%%%%%%%%%%%%%%%%%%%%%%%%%%%%%%%%%%%%%%%%%%%%

\newcommand\bomp[1]{{%
  \footnotesize
  \zebra
  \begin{longtable}{P{0.15\textwidth}P{0.3\textwidth}P{0.2\textwidth}P{0.2\textwidth}}
    %
    % First header
    %
    \hiderowcolors
    \noalign{\smallskip}\hline\noalign{\smallskip}
    {\textbf{Part}} & {\textbf{Description}} & {\textbf{Order No}} & {\textbf{Notes}}\\
    \noalign{\smallskip}\hline\noalign{\smallskip}
    \noalign{\global\rownum 1\relax}\showrowcolors
    \endfirsthead
    %
    % Subsequent headers
    %
    \hiderowcolors
    \multicolumn{4}{l}{\em Continued from previous page.}\\
    \noalign{\smallskip\smallskip}\hline\noalign{\smallskip}
    {\textbf{Part}} & {\textbf{Description}} & {\textbf{Order No}} & {\textbf{Notes}}\\
    \noalign{\smallskip}\hline\noalign{\smallskip}
    \noalign{\global\rownum 1\relax}\showrowcolors
    \endhead
    %
    % Footer
    %
    \hiderowcolors
    \noalign{\smallskip\smallskip}
    \multicolumn{4}{l}{\em Continued on next page.}\\
    \endfoot
    %
    % Last footer
    %
    \hiderowcolors
    \noalign{\smallskip}\hline\noalign{\smallskip}
    \endlastfoot
    %
    % Content
    %
    \showrowcolors
    \input{../generated/#1-bom-parts}
  \end{longtable}
}}

% End of file.
