alexiosc/cft/documentation/BOM/front-panel-bom.html

Qty | Value | Device | Parts
4 |  | 2,54/1,0 | NC1, NC2, NC3, NC4
1 |  | G04R | RN7
12 |  | JP2E | JP1, JP2, JP3, JP4, JP5, JP6, JP7, JP8, JP9, JP10, JP11, JP12
39 |  | MA05-1 | CON-LM-1, CON-LM-2, CON-LMA-1, CON-LMA-2, CON-LMA-3, CON-LMA-4, CON-LMB-1, CON-LMB-2, CON-LMC-1, CON-LMC-2, CON-LMC-3, CON-LMC-4, CON-LMC-5, CON-LMD-1, CON-LMD-2, CON-LMD-3, CON-LMD-4, CON-LMD-5, CON-LME-1, CON-LME-2, CON-LME-3, CON-LME-4, CON-LME-5, CON-LMF-1, CON-LMF-2, CON-LMF-3, CON-LMF-4, CON-LMF-5, CON-LMG-1, CON-LMG-2, CON-LMG-3, CON-LMG-4, CON-LMG-5, CON-LMH-1, CON-LMH-2, CON-LMH-3, CON-LMH-4, CON-LMH-5, P3
1 |  | SW_DIP-3 | SW1
1 |  | SW_DIP-4 | SW2
1 |  | SW_DIP-8 | SW3
1 |  | VG96-3K | EXP
2 | 0.01uF | C-EU025-024X044 | C29, C32
36 | 0.1uF | C-EU025-024X044 | C18, C19, C20, C21, C22, C23, C24, C25, C26, C30, C31, C33, C34, C35, C36, C37, C38, C39, C40, C41, C42, C43, C45, C46, C47, C48, C49, C50, C51, C58, C59, C60, C61, C62, C63, C64
17 | 1N4148 | 1N4148DO35-7 | D1, D2, D3, D4, D5, D6, D7, D8, D9, D10, D11, D12, D13, D14, D15, D16, D17
2 | 1k | R-EU_0204/7 | R24, R25
21 | 1uF | C-EU025-024X044 | C1, C2, C3, C4, C5, C6, C7, C8, C9, C10, C11, C12, C13, C14, C15, C16, C17, C27, C44, C52, C57
2 | 1uF | C-EUC0805K | C53, C54
1 | 4k7 | G03R | RN4
9 | 4k7 | G08R | RN5, RN6, RN8, RN9, RN10, RN11, RN12, RN13, RN14
5 | 4k7 | R-EU_0204/7 | R21, R22, R23, R26, R27
1 | 4k7 | TRIM_EU-CT6 | RV1
1 | 10k | G03R | RN3
2 | 10k | G08R | RN1, RN2
1 | 10uF | C-EU025-024X044 | C28
2 | 47uF | CPOL-EUE2.5-5 | C55, C56
17 | 50k | R-EU_0204/7 | R1, R2, R3, R4, R5, R6, R7, R8, R9, R10, R11, R12, R13, R14, R15, R16, R17
1 | 057-020-1 | 057-020-1 | P8
1 | 74HC00N | 74HC00N | IC24
1 | 74HC02N | 74HC02N | IC31
5 | 74HC03N | 74HC03N | IC10, IC32, IC33, IC34, IC35
4 | 74HC04N | 74HC04N | IC4, IC5, IC6, IC23
1 | 74HC08N | 74HC08N | IC59
3 | 74HC14N | 74HC14N | IC1, IC2, IC3
1 | 74HC74D | 74HC74D | IC15
3 | 74HC74N | 74HC74N | IC28, IC30, IC40
1 | 74HC85N | 74HC85N | IC37
6 | 74HC138N | 74HC138N | IC20, IC21, IC22, IC48, IC49, IC52
1 | 74HC139N | 74HC139N | IC29
2 | 74HC148N | 74HC148N | IC7, IC8
1 | 74HC157N | 74HC157N | IC11
2 | 74HC175N | 74HC175N | IC19, IC27
5 | 74HC251N | 74HC251N | IC13, IC16, IC17, IC25, IC26
2 | 74HC253N | 74HC253N | IC14, IC39
12 | 74HC541N | 74HC541N | IC41, IC42, IC43, IC44, IC46, IC47, IC53, IC54, IC55, IC56, IC57, IC58
4 | 74HC574N | 74HC574N | IC9, IC12, IC50, IC51
1 | 74HC590N | 74HC590N | IC38
1 | 74HC688N | 74HC688N | IC45
1 | 91k | R-EU_0204/7 | R18
2 | 680R | R-EU_0204/7 | R19, R20
7 | 2540-5 | 2540-5 | P4, P5, P6, P7, P9, P10, P11
2 | 2550- | 2550- | P1, P2
2 | BC548 | BC548 | Q1, Q2
4 | HOLE | HOLE | U1, U2, U3, U4
2 | LM556N | LM556N | IC18, IC36
1 | M2012TNW01 | TL36PO | S9
1 | M2013TNW01 | TL39PO | S6
2 | M2018TNW01 | TL37PO | S3, S25
1 | OSHW-LOGOL | OSHW-LOGOL | $4_39_$
1 | QRCODE-CFT | QRCODE-CFT | $4_40_$
1 | SIGNAL-RENAME | SIGNAL-RENAME | X1
1 | SIGNATURESILK | SIGNATURESILK | $4_37_$
19 | TL36PO | TL36PO | S1, S2, S7, S10, S11, S12, S13, S14, S15, S16, S17, S18, S19, S20, S21, S22, S23, S24, S31
8 | TL37PO | TL37PO | S4, S5, S26, S27, S28, S29, S30, S32
1 | TL39PO | TL39PO | S8
1 | TPPAD1-13 | TPPAD1-13 | TP2
