alexiosc/cft/documentation/latex/cft_book/figure-instruction-format.tex

% -*- latex -*-
\documentclass[class=memoir,border=200pt]{standalone}
\input{preamble-new}

\begin{document}%
%\tikzexternaldisable%
\begin{tikzpicture}%

    \begin{scope}[thin,draw opacity=0,line width=0pt]
    \foreach \x in {0, 1, 2, 3, 4, 5, 6, 7}{
      \draw[fill=cfthl!50,xshift=\x cm](0,0) rectangle (0.5,0.6);
      \draw[fill=cfthl!25,xshift=\x cm](0.5,0) rectangle (1,0.6);
    }
    \end{scope}
    \foreach \x in {0.5, 1, ..., 7.5}{
      \draw[thin] (\x cm, 0) -- (\x cm, -0.1cm);
    }
    \draw[line width=2pt](0,0) rectangle (8,0.6);
    \draw (8,0) node[below] { \footnotesize 0 };
    \draw (2,0) node[below left] { \footnotesize 12 };
    \draw (2,0) node[below right] { \footnotesize 11 };
    \draw (2.5,0) node[below right] { \footnotesize 10 };
    \draw (3,0) node[below right] { \footnotesize 9 };
    \draw (0,0) node[below] { \footnotesize 15 };
    \draw[thick](2,-0.1) -- (2,0.6);
    \draw[thick](2.5,-0.1) -- (2.5,0.6);
    \draw[thick](3,-0.1) -- (3,0.6);
    \draw (1, 0.3) node { Opcode };
    \draw (2.25, 0.3) node { I };
    \draw (2.75, 0.3) node { R };
    \draw (5.5, 0.3) node { Operand };

\end{tikzpicture}%
%\tikzexternalenable%
\end{document}

% End of file.
