alexiosc/cft/documentation/latex/bus_guide/cft-fig3.tex

\documentclass{article}
\input tmp.inputs
\pagestyle{empty}
\begin{document}
      \begin{pspicture}(-1,-1)(8,8)

        \rput(0,4){
          \rput[Bm](0.225,2.9){L}
          \rput[Bl](0.75,2.9){A}
          \rput[Br](7.95,2.9){RBL}
               {
                 \psset{linewidth=3\pslinewidth}

                 \psframe(0,0)(0.45,0.75)
                 \psframe(0.75,0)(7.95,0.75)

                 \psframe(0,1.9)(0.45,2.65)
                 \psframe(0.75,1.9)(7.95,2.65)
               }

               \multips{0}(1.2,0)(0.45,0){15}{
                 \psline{-}(0,0)(0,0.75)
                 \psline{-}(0,1.9)(0,2.65)
                 \psline{*->}(0.225,2.275)(-0.225,0.3)
               }
               \psline{*->}(1.05,2.275)(0.225,0.3)
               \psline[linearc=0.25]{*->}(0.225,2.275)(0.225,1.3)(7.725,1.3)(7.725,0.3)
               \rput[tl](0.75,-0.1){\footnotesize 15}
               \rput[tr](7.95,-0.1){\footnotesize 0}
        }

        \rput(0,0){
          \rput[Bm](0.225,2.9){L}
          \rput[Bl](0.75,2.9){A}
          \rput[Br](7.95,2.9){RBR}
               {
                 \psset{linewidth=3\pslinewidth}

                 \psframe(0,0)(0.45,0.75)
                 \psframe(0.75,0)(7.95,0.75)

                 \psframe(0,1.9)(0.45,2.65)
                 \psframe(0.75,1.9)(7.95,2.65)
               }

               \multips{0}(1.2,0)(0.45,0){15}{
                 \psline{-}(0,0)(0,0.75)
                 \psline{-}(0,1.9)(0,2.65)
                 \psline{*->}(-0.225,2.275)(0.225,0.3)
               }
               \psline{*->}(0.225,2.275)(1.05,0.3)
               \psline[linearc=0.25]{*->}(7.725,2.275)(7.725,1.3)(0.225,1.3)(0.225,0.3)
               \rput[tl](0.75,-0.1){\footnotesize 15}
               \rput[tr](7.95,-0.1){\footnotesize 0}
        }
      \end{pspicture}
    
\end{document}
