alexiosc/cft/documentation/panel/panel-assembly.png

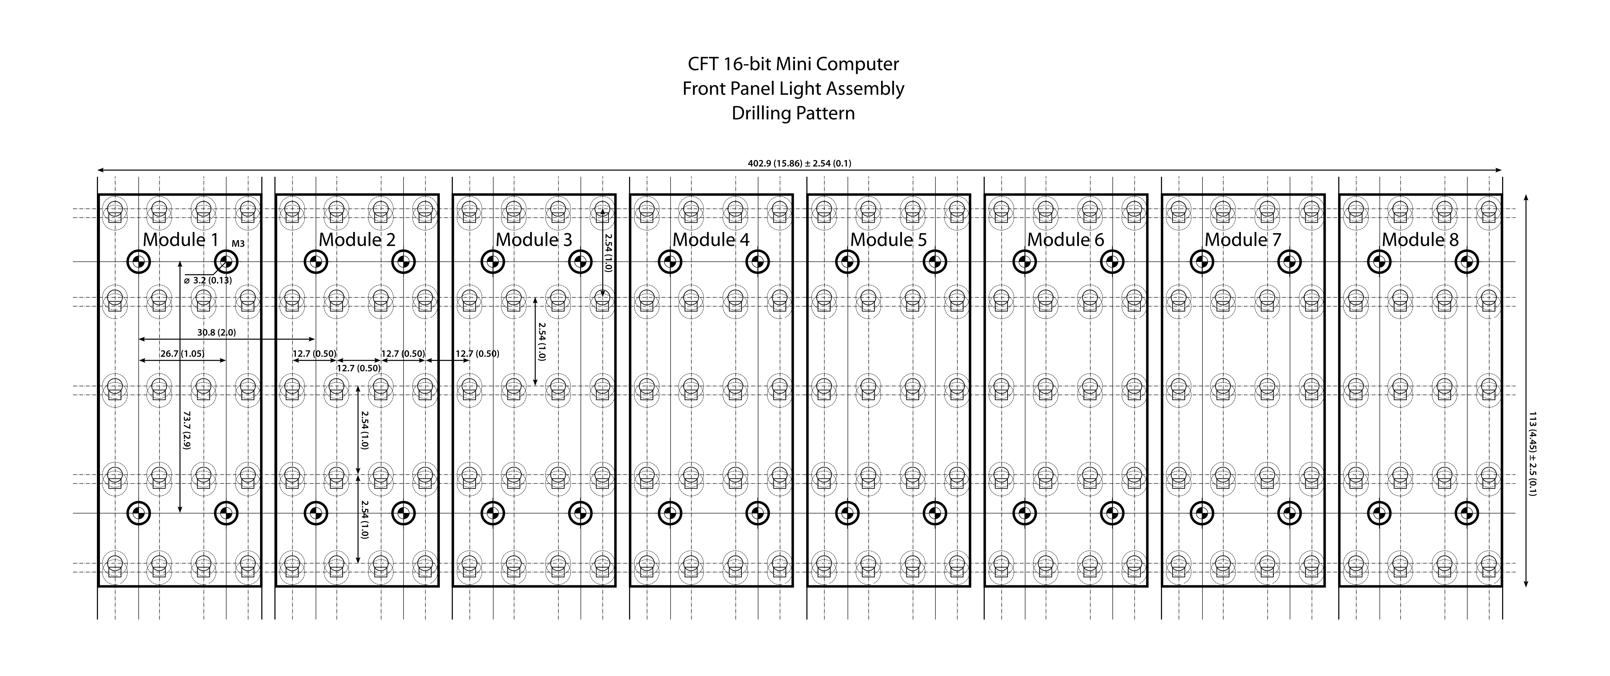
documentation/panel/panel-assembly.png
