alexiosc/cft/documentation/latex/figs/bus-termination.pdf

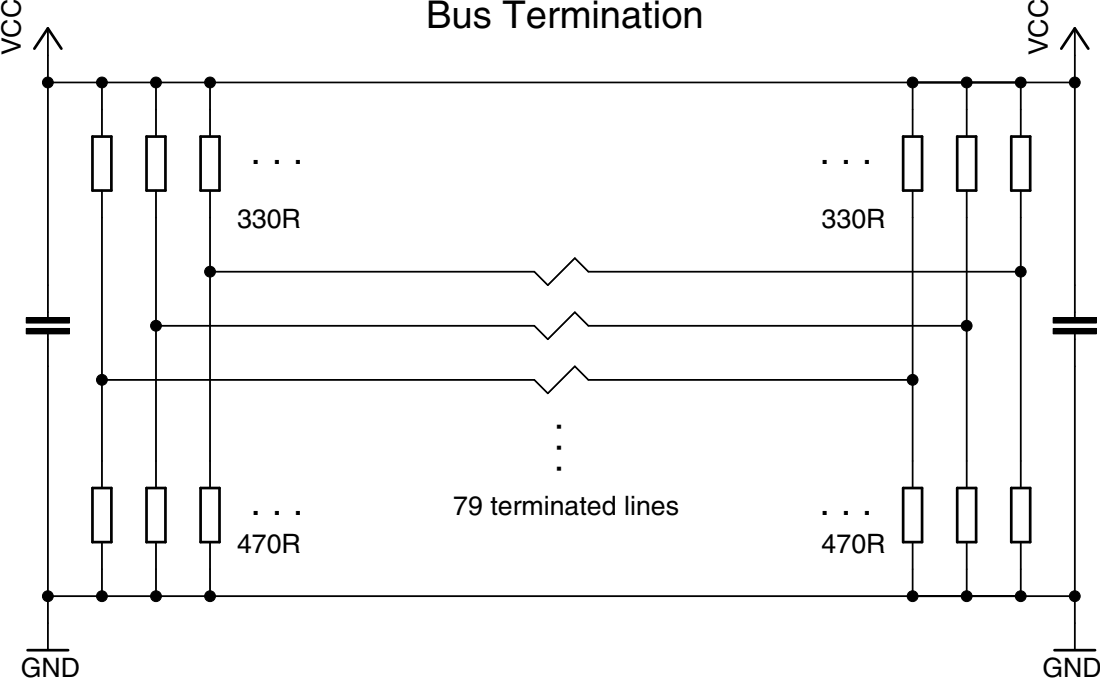
[picture p44: page 1]
