alexiosc/cft/documentation/latex/figs/datapath2.pdf

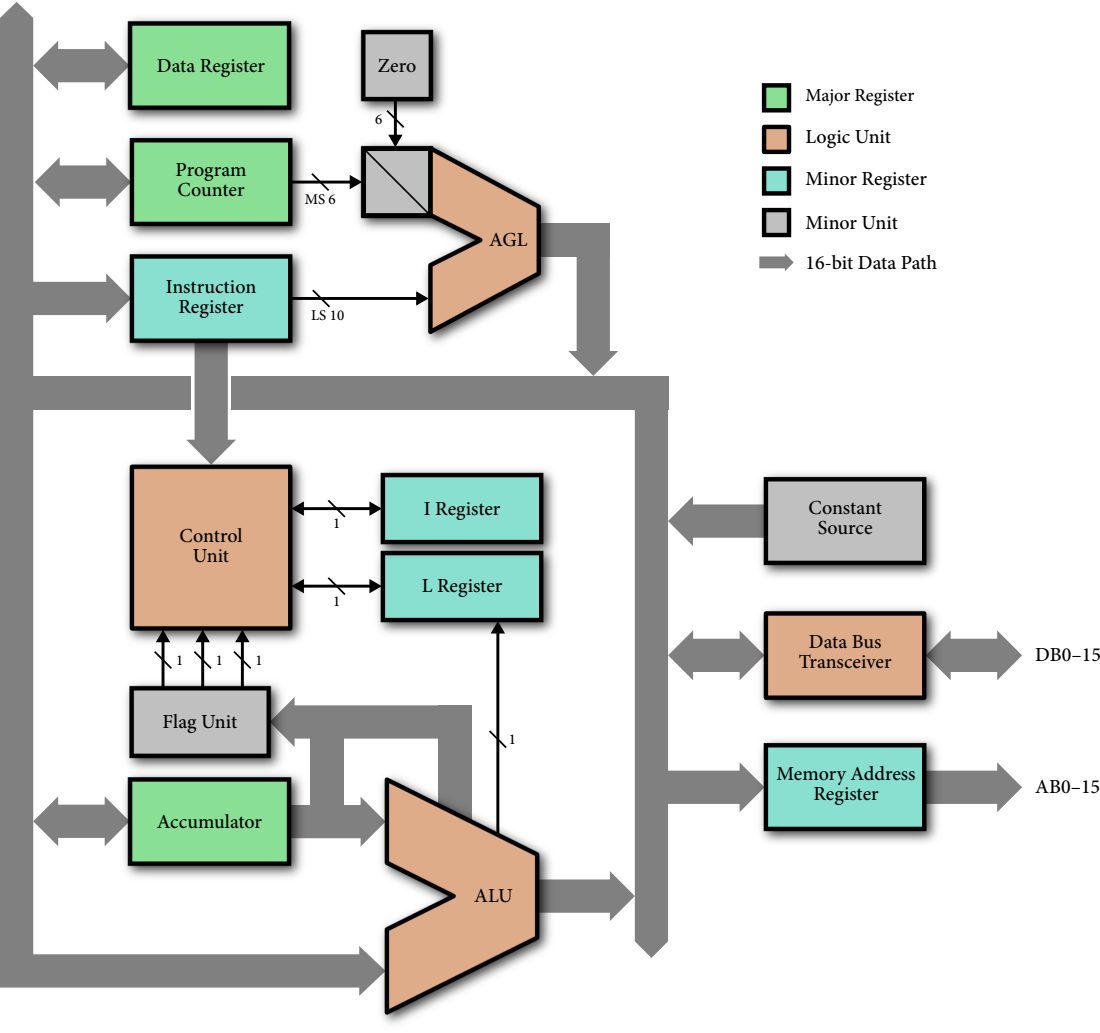
[picture p45: page 1]
Accumulator; Data Register; Data Bus; Transceiver; Program Counter; Instruction Register; Memory Address; Register; Control Unit; Zero; AGL; ALU; L Register; Flag Unit; I Register 1; Major Register; Logic Unit; Minor Register; Minor Unit; Constant Source

16-bit Data Path
