alexiosc/cft/documentation/latex/figs/deb-bus-interface.pdf

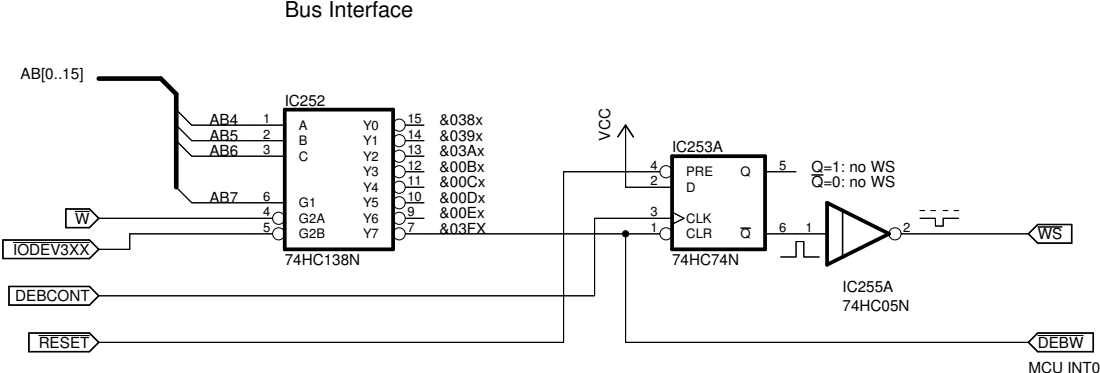
[picture p46: page 1]
