alexiosc/cft/documentation/latex/figs/debouncing.pdf

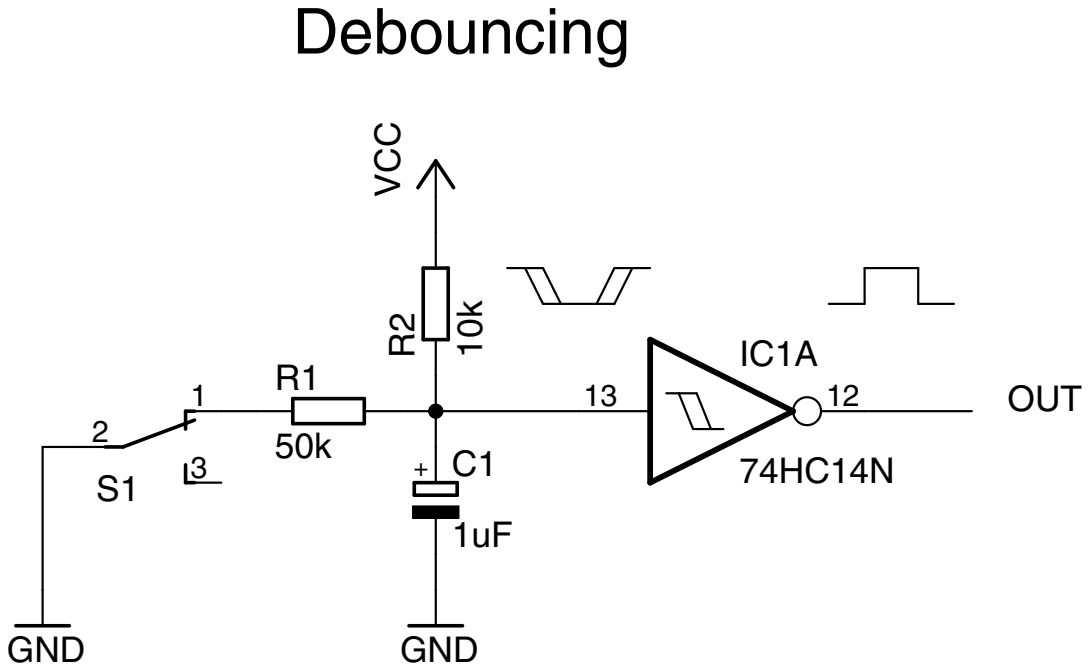
[picture p47: page 1]
