alexiosc/cft/documentation/latex/figs/fig-555-astable.pdf

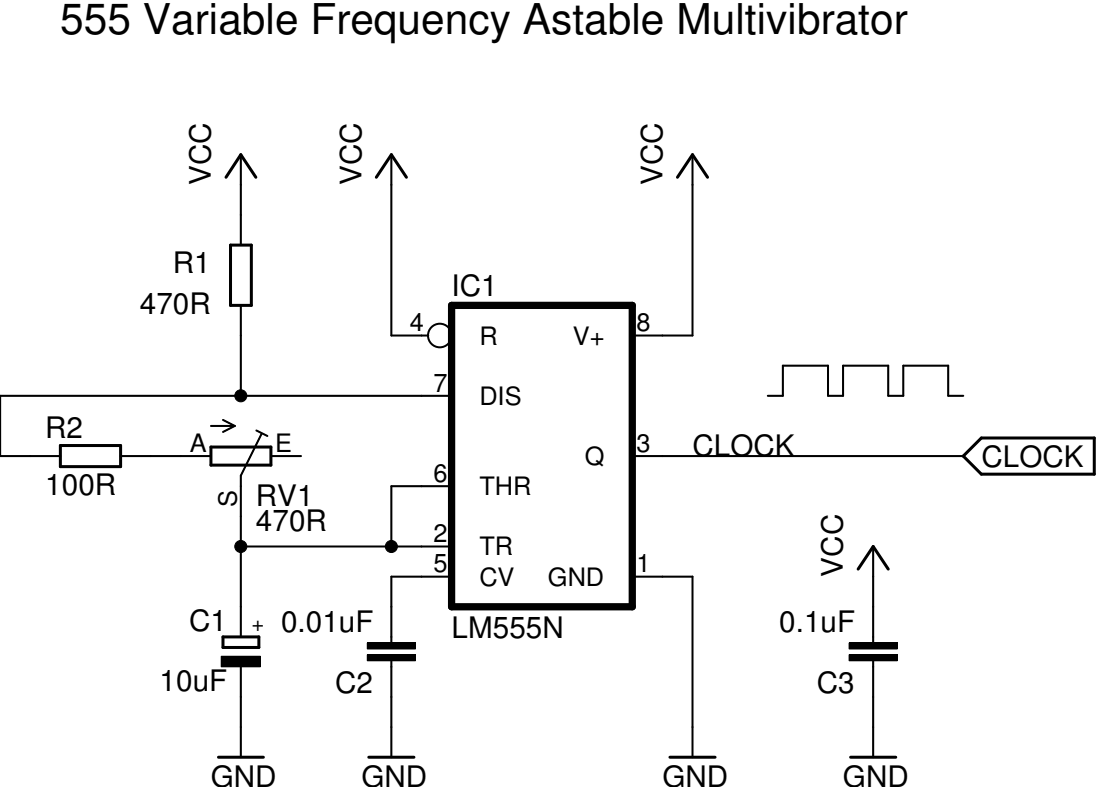
[picture p48: page 1]

555 Variable Frequency Astable Multivibrator
