alexiosc/cft/documentation/latex/figs/cft-logo-v1.pdf

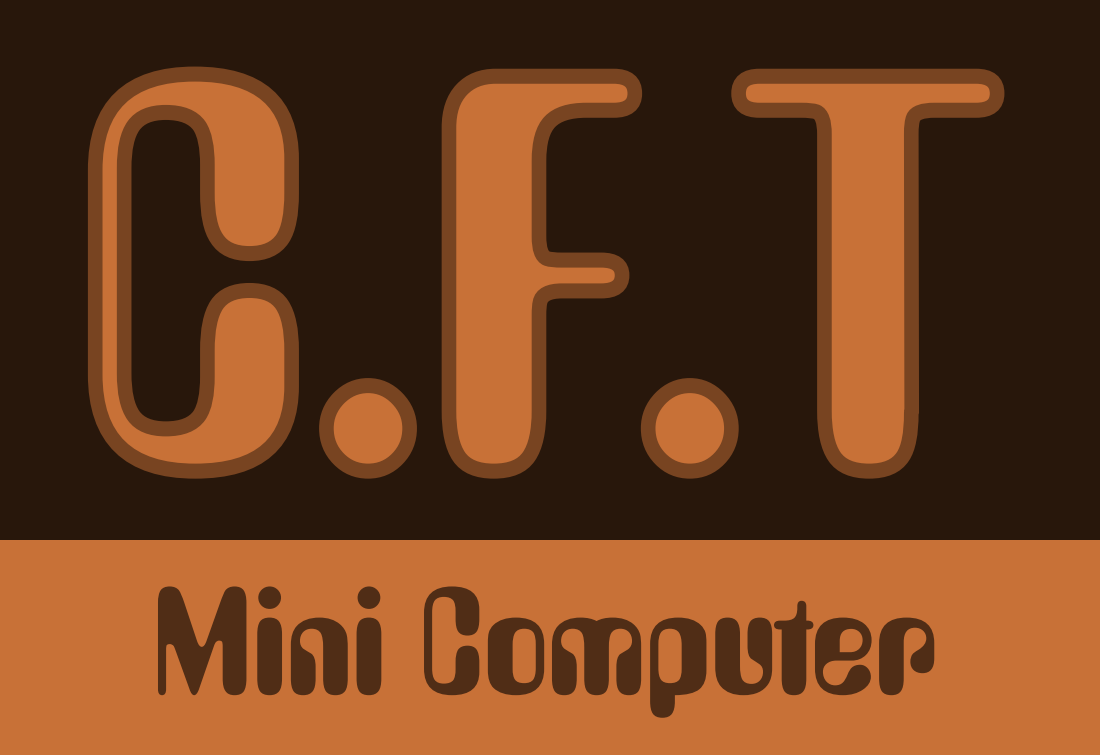
[picture p49: page 1]
