alexiosc/cft/documentation/panel/front-panel-v2.pdf

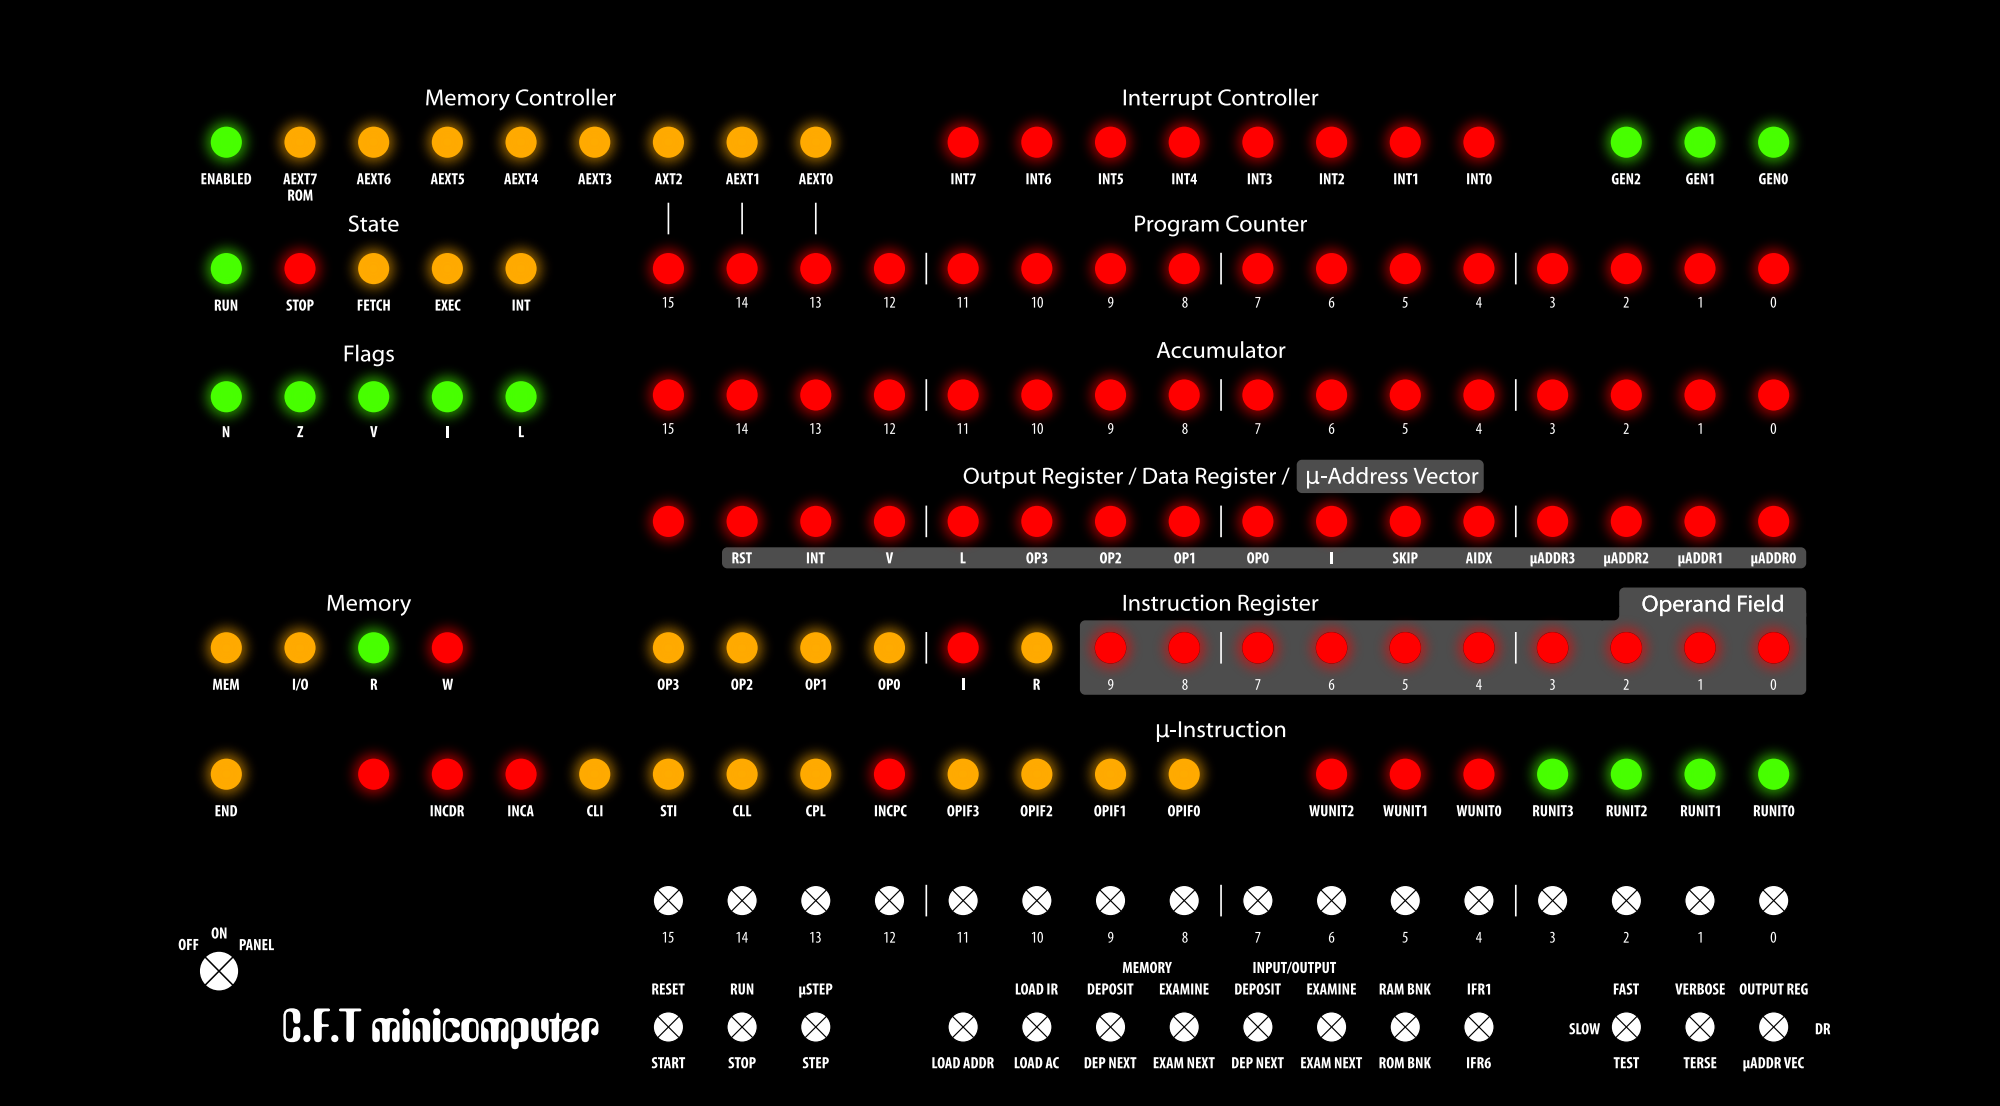
[picture p50: page 1]
