alexiosc/cft/documentation/panel/front-panel-v3.pdf

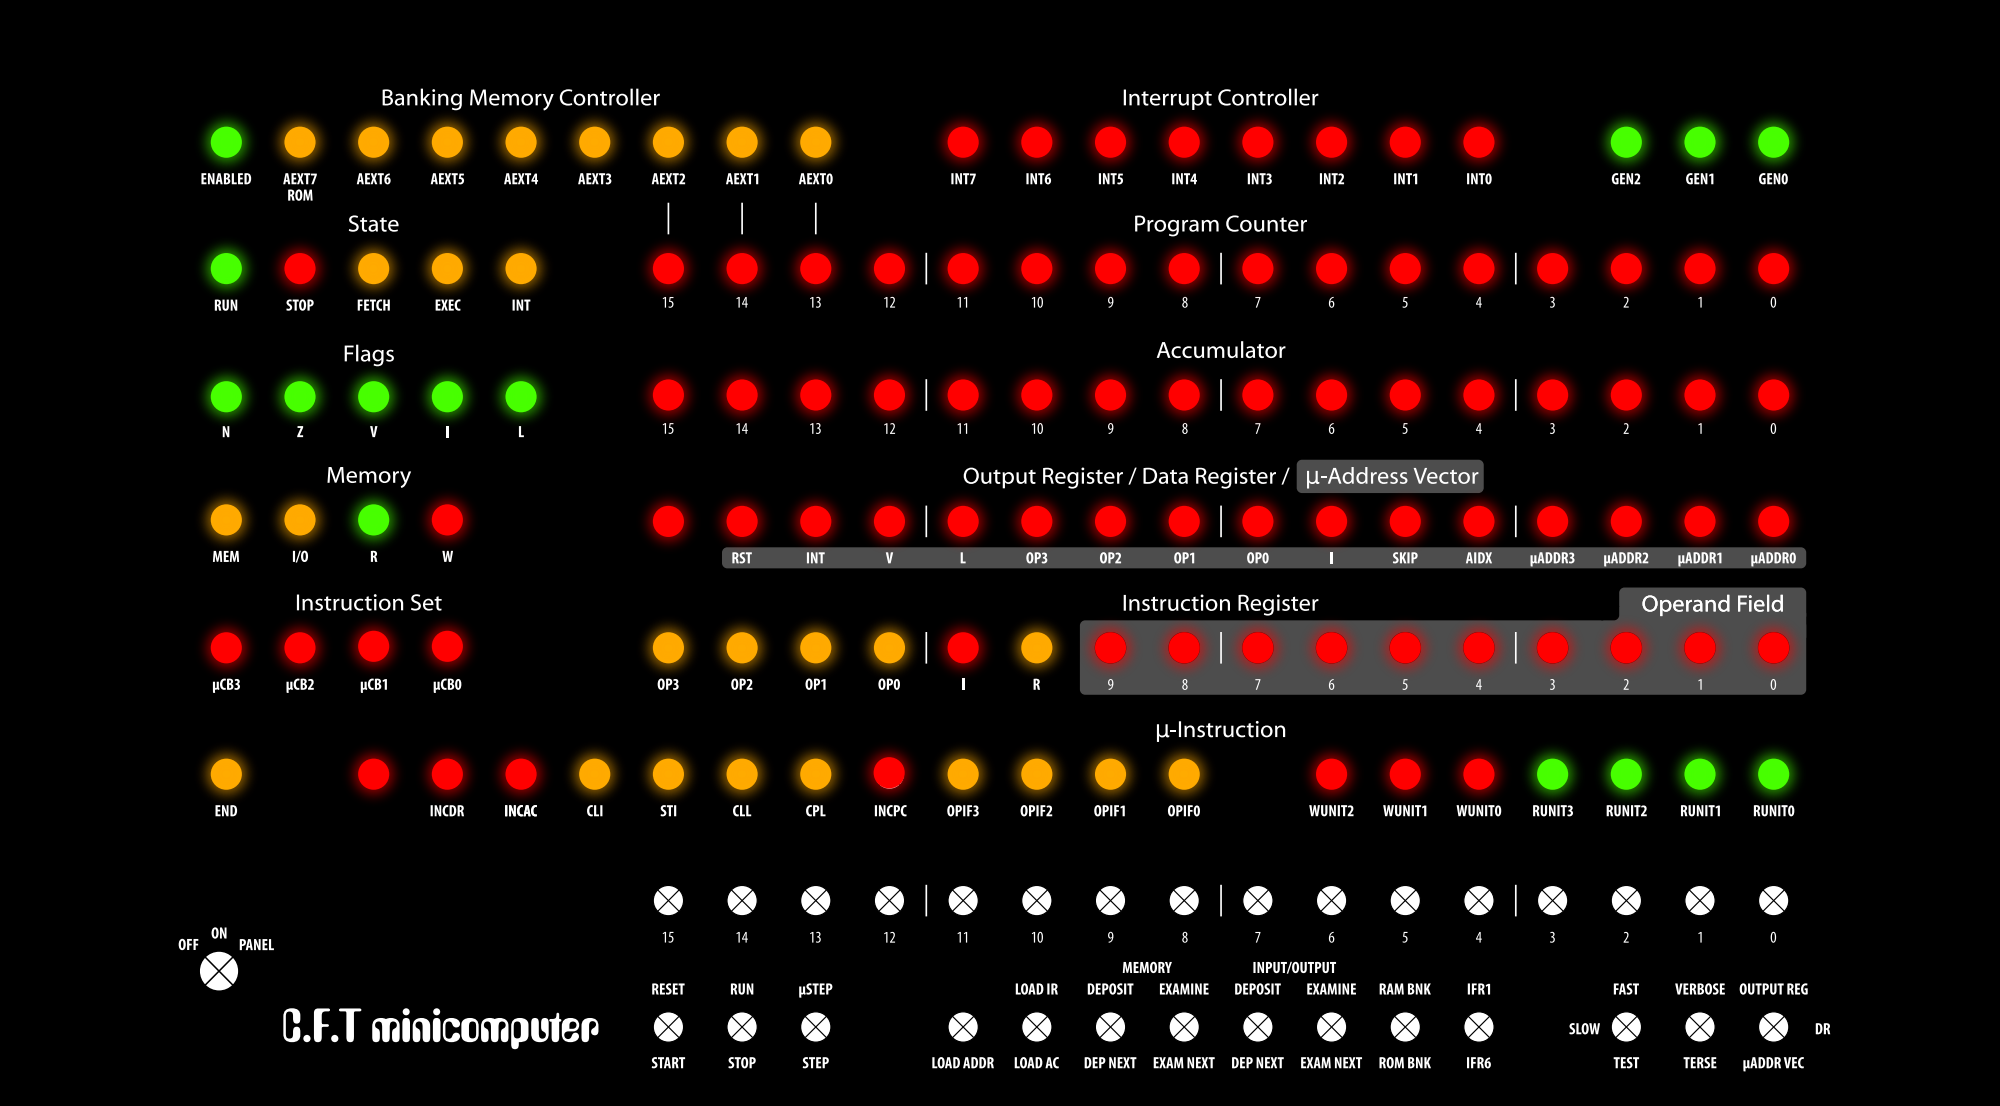
[picture p51: page 1]
