alexiosc/cft/kicad/cft/cft-board1/cft-bus.kicad_pcb

## KiCad design kicad/cft/cft-board1/cft-bus.kicad_pcb (2020-11-13)

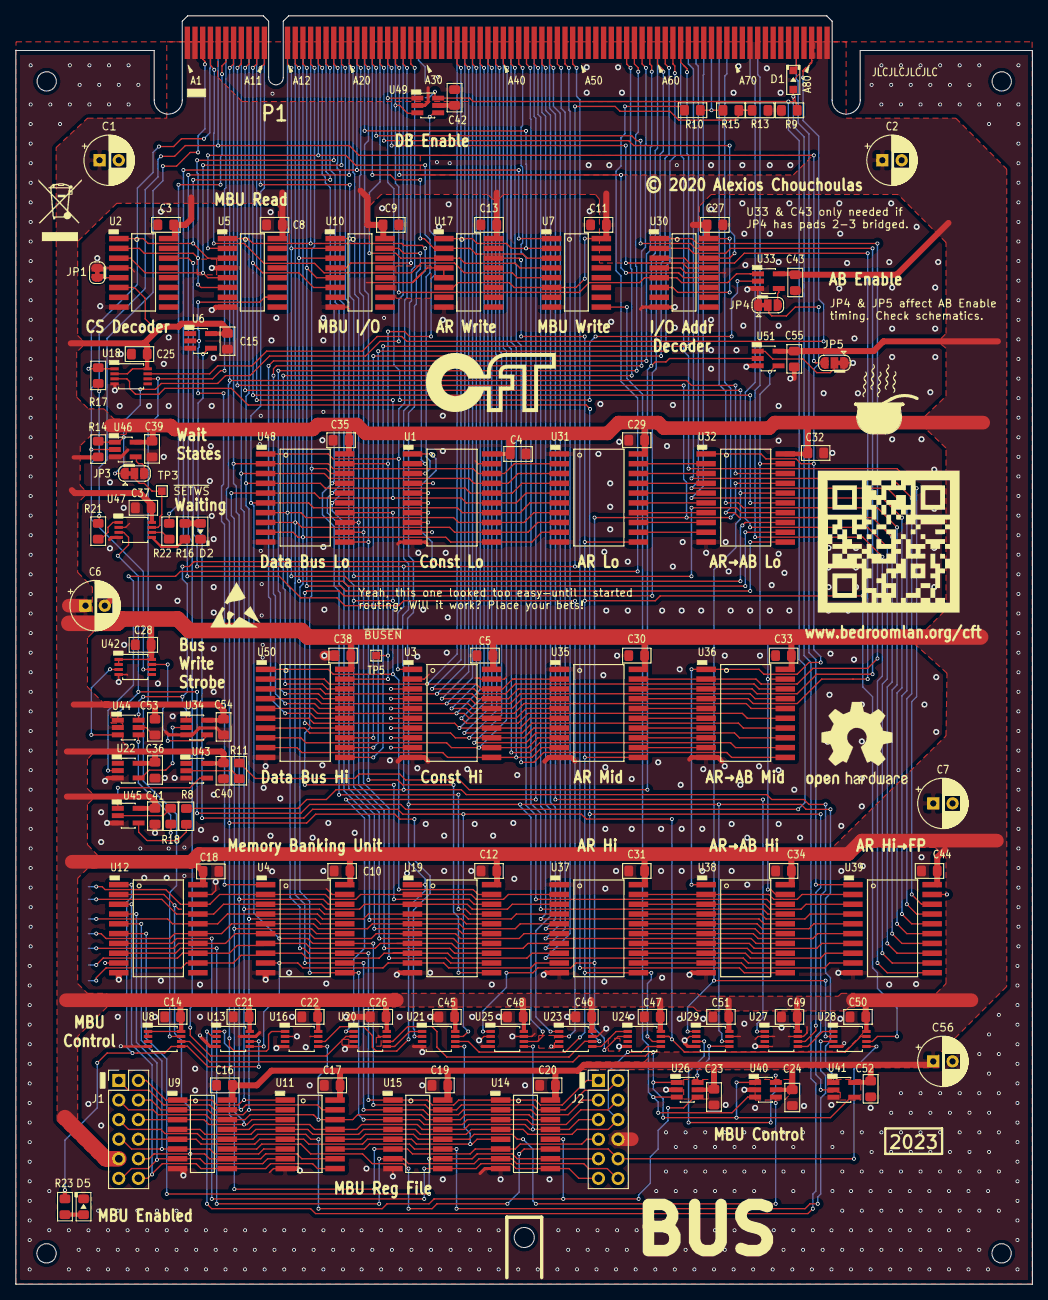
[picture p79: board cft-bus.kicad_pcb from above]

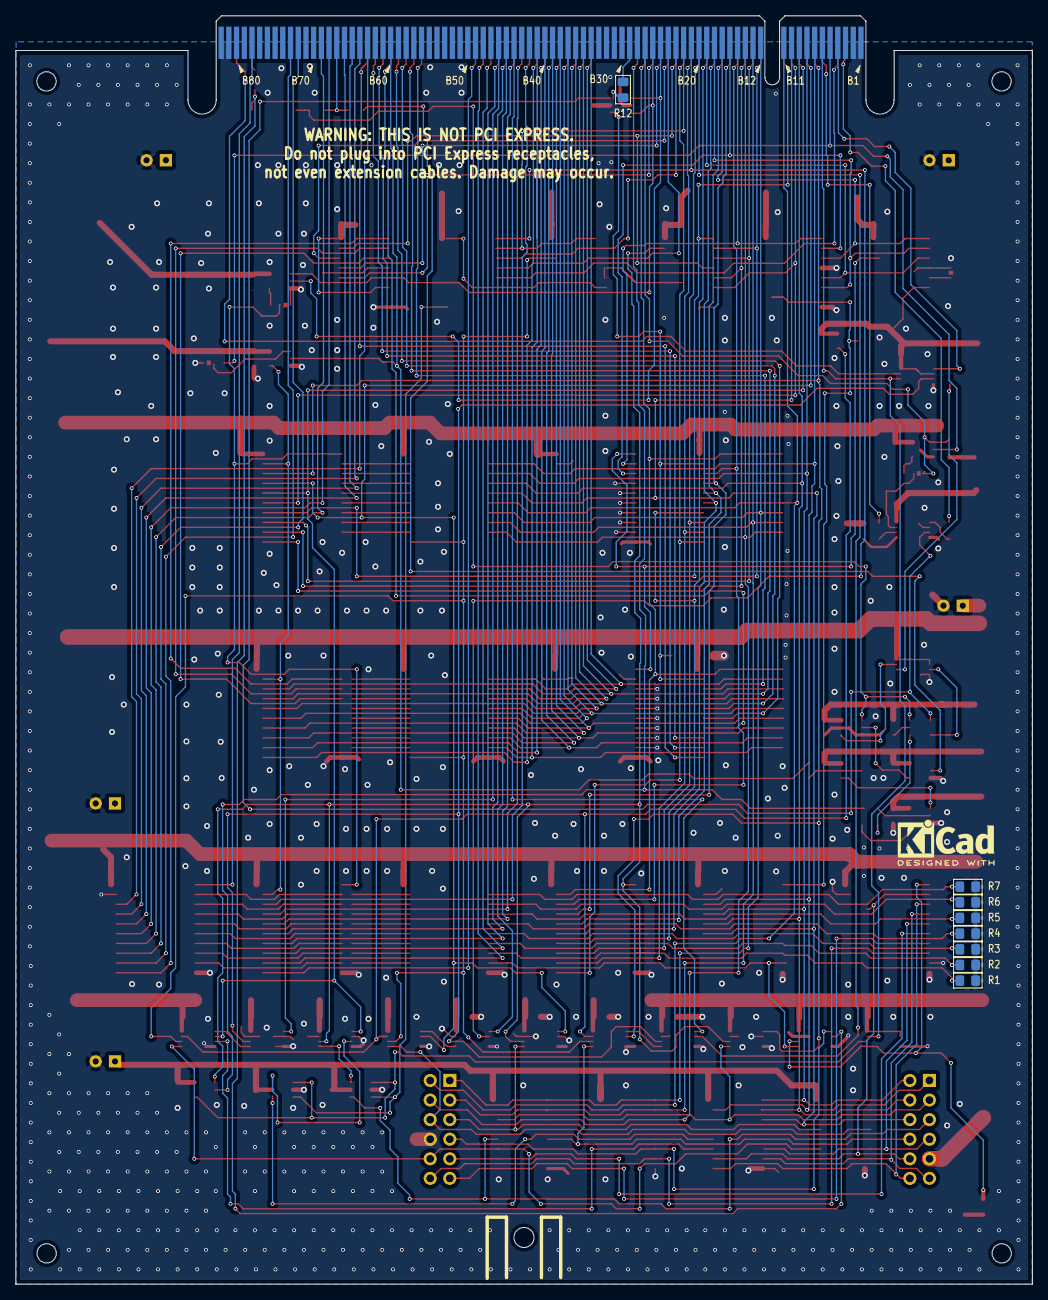
[picture p80: board cft-bus.kicad_pcb from below]

Board: 2 copper layers, 131.9 x 164.6 mm, 140 parts (8 on the bottom side), 188 nets.

Parts:
C1, C2, C6, C7, C56: 47µF; CP_Radial_D6.3mm_P2.50mm
C3, C4, C5, C8, C9, C10, C11, C12, C13, C14, C15, C16, C17, C18, C19, C20, C21, C22, C23, C24, C25, C26, C27, C28, C29, C30, C31, C32, C33, C34, C35, C36, C37, C38, C39, C40, C41, C42, C43, C44, C45, C46, C47, C48, C49, C50, C51, C52, C53, C54, C55: 100nF; C_SMD_0805_2012Metric_Pad1.15x1.40mm_HandSolder
D1: D_ALT; SOD-323
D2, D5: LED_ALT; LED_0805_2012Metric_Pad1.15x1.40mm_HandSolder
J1, J2: Conn_02x06_Counter_Clockwise; PinHeader_2x06_P2.54mm_Vertical
JP1: SolderJumper_2_Bridged; SolderJumper-2_P1.3mm_Bridged_RoundedPad1.0x1.5mm
JP3, JP4, JP5: Jumper_3_Bridged12; SolderJumper-3_P1.3mm_Bridged12_RoundedPad1.0x1.5mm
P1: CFT-2019-Bus; CFT-2019-Card-Edge
R1, R2, R3, R4, R5, R6, R7, R9, R13, R14: 4.7kΩ; R_SMD_0805_2012Metric_Pad1.15x1.40mm_HandSolder
R8, R10, R11, R12, R15, R17, R18, R21, R22: 0Ω; R_SMD_0805_2012Metric_Pad1.15x1.40mm_HandSolder
R16, R23: 680Ω; R_SMD_0805_2012Metric_Pad1.15x1.40mm_HandSolder
TP3, TP5: TestPoint; TestPoint_Pad_1.0x1.0mm
U1, U3, U12: 74AC541; SOIC-20W
U2, U5, U7, U10, U17, U30: 74HC138; SOIC-16
U4, U19, U32, U36, U38, U39: 74HC541; SOIC-20W
U6, U22, U43: 74LVC1G04; SOT-23-5_HandSoldering
U8, U18, U42, U47: 74LVC1G74; TSSOP-8_3x3mm_P0.65mm
U9, U11, U14, U15: 74HC670; SOIC-16
U13, U16, U20, U21, U23, U24, U25, U27, U28, U29: 74LVC2G157; TSSOP-8_3x3mm_P0.65mm
U26, U40, U44: 74LVC1G0832; SOT-23-6_Handsoldering
U31, U35, U37: 74HC574; SOIC-20W
U33: 74LVC1G08; SOT-23-5_HandSoldering
U34, U41, U46, U51: 74LVC1G32; SOT-23-5_HandSoldering
U45: 74LVC1G125; SOT-23-5_HandSoldering
U48, U50: 74ACT245; SOIC-20W
U49: 74LVC1G11; SOT-23-6_Handsoldering

Connections:
+5V: C1.1, C2.1, C3.1, C4.1, C5.1, C6.1, C7.1, C8.1, C9.1, C10.1, C11.1, C12.1, C13.1, C14.1, C15.1, C16.1, C17.1, C18.1, C19.1, C20.1, C21.1, C22.1, C23.1, C24.1, C25.1, C26.1, C27.1, C28.1, C29.1, C30.1, C31.1, C32.1, C33.1, C34.1, C35.1, C36.1, C37.1, C38.1, C39.1, C40.1, C41.1, C42.1, C43.1, C44.1, C45.1, C46.1, C47.1, C48.1, C49.1, C50.1, C51.1, C52.1, C53.1, C54.1, C55.1, C56.1, J1.9, P1.A1, P1.A2, P1.A81, P1.A82, R9.2, R13.2, R14.1, U1.20, U2.6, U2.16, U3.20, U4.20, U5.16, U6.5, U7.6, U7.16, U8.1, U8.2, U8.8, U9.16, U10.16, U11.16, U12.20, U13.8, U14.16, U15.16, U16.8, U17.6, U17.16, U18.2, U18.8, U19.20, U20.8, U21.8, U22.5, U23.8, U24.8, U25.8, U26.5, U27.8, U28.8, U29.8, U30.6, U30.16, U31.20, U32.20, U33.5, U34.5, U35.20, U36.20, U37.20, U38.20, U39.20, U40.5, U41.5, U42.1, U42.2, U42.8, U43.5, U44.2, U45.5, U46.5, U47.8, U48.20, U49.5, U50.20, U51.5
/Address Register (AR)/AB0: P1.A7, U16.1, U21.2, U32.18
/Address Register (AR)/AB1: P1.A8, U24.2, U25.1, U32.17
/Address Register (AR)/AB2: P1.A9, U28.2, U29.1, U32.16
/Address Register (AR)/AB3: P1.A10, U10.6, U32.15
/Address Register (AR)/AB4: P1.A11, U10.1, U32.14
/Address Register (AR)/AB5: P1.A12, U10.2, U32.13
/Address Register (AR)/AB6: P1.A13, U10.3, U32.12
/Address Register (AR)/AB7: P1.A14, U10.5, U32.11
/Address Register (AR)/AB8: P1.A34, U36.18
/Address Register (AR)/AB9: P1.A35, U36.17
/Address Register (AR)/AB10: P1.A36, U36.16
/Address Register (AR)/AB11: P1.A37, U36.15
/Address Register (AR)/AB12: P1.A38, U36.14
/Address Register (AR)/AB13: P1.A39, U36.13
/Address Register (AR)/AB14: P1.A40, U36.12
/Address Register (AR)/AB15: P1.A41, U36.11
/Address Register (AR)/AB16: P1.A42, U38.18
/Address Register (AR)/AB17: P1.A43, U38.17
/Address Register (AR)/AB18: P1.A44, U38.16
/Address Register (AR)/AB19: P1.A45, U38.15
/Address Register (AR)/AB20: P1.A46, U38.14
/Address Register (AR)/AB21: P1.A47, U38.13
/Address Register (AR)/AB22: P1.A48, U38.12
/Address Register (AR)/AB23: P1.A49, U38.11
/Address Register (AR)/AEXT0: R7.2, U4.2, U12.18, U19.2, U37.2
/Address Register (AR)/AEXT1: R6.2, U4.3, U12.17, U19.3, U37.3
/Address Register (AR)/AEXT2: R5.2, U4.4, U12.16, U19.4, U37.4
/Address Register (AR)/AEXT3: R4.2, U4.5, U12.15, U19.5, U37.5
/Address Register (AR)/AEXT4: R3.2, U4.6, U12.14, U19.6, U37.6
/Address Register (AR)/AEXT5: R2.2, U4.7, U12.13, U19.7, U37.7
/Address Register (AR)/AEXT6: R1.2, U4.8, U12.12, U19.8, U37.8
/Address Register (AR)/AEXT7: U4.9, U13.5, U19.9, U37.9
/Address Register (AR)/AR0: U31.19, U32.2
/Address Register (AR)/AR1: U31.18, U32.3
/Address Register (AR)/AR2: U31.17, U32.4
/Address Register (AR)/AR3: U31.16, U32.5
/Address Register (AR)/AR4: U31.15, U32.6
/Address Register (AR)/AR5: U31.14, U32.7
/Address Register (AR)/AR6: U31.13, U32.8
/Address Register (AR)/AR7: U31.12, U32.9
/Address Register (AR)/AR8: U30.1, U35.19, U36.2
/Address Register (AR)/AR9: U30.2, U35.18, U36.3
/Address Register (AR)/AR10: U30.3, U35.17, U36.4
/Address Register (AR)/AR11: U35.16, U36.5
/Address Register (AR)/AR12: U35.15, U36.6
/Address Register (AR)/AR13: U35.14, U36.7
/Address Register (AR)/AR14: U35.13, U36.8
/Address Register (AR)/AR15: U35.12, U36.9
/Address Register (AR)/AR16: U37.19, U38.2, U39.2
/Address Register (AR)/AR17: U37.18, U38.3, U39.3
/Address Register (AR)/AR18: U37.17, U38.4, U39.4
/Address Register (AR)/AR19: U37.16, U38.5, U39.5
/Address Register (AR)/AR20: U37.15, U38.6, U39.6
/Address Register (AR)/AR21: U37.14, U38.7, U39.7
/Address Register (AR)/AR22: U37.13, U38.8, U39.8
/Address Register (AR)/AR23: U37.12, U38.9, U39.9
/Address Register (AR)/FPD0: P1.B63, U39.18
/Address Register (AR)/FPD1: P1.B64, U39.17
/Address Register (AR)/FPD2: P1.B65, U39.16
/Address Register (AR)/FPD3: P1.B66, U39.15
/Address Register (AR)/FPD4: P1.B68, U39.14
/Address Register (AR)/FPD5: P1.B69, U39.13
/Address Register (AR)/FPD6: P1.B72, U39.12
/Address Register (AR)/FPD7: P1.B73, U39.11
/Address Register (AR)/IBUS0: J1.1, P1.B7, U1.18, U4.18, U9.15, U11.15, U31.2, U48.2
/Address Register (AR)/IBUS1: J1.2, P1.B8, U1.17, U4.17, U9.1, U11.1, U31.3, U48.3
/Address Register (AR)/IBUS2: J1.4, P1.B9, U1.16, U4.16, U9.2, U11.2, U31.4, U48.4
/Address Register (AR)/IBUS3: J1.6, P1.B10, U1.15, U4.15, U9.3, U11.3, U31.5, U48.5
/Address Register (AR)/IBUS4: J2.2, P1.B11, U1.14, U4.14, U14.15, U15.15, U31.6, U48.6
/Address Register (AR)/IBUS5: J2.1, P1.B12, U1.13, U4.13, U14.1, U15.1, U31.7, U48.7
/Address Register (AR)/IBUS6: J2.3, P1.B13, U1.12, U4.12, U14.2, U15.2, U31.8, U48.8
/Address Register (AR)/IBUS7: J2.4, P1.B14, U1.11, U4.11, U14.3, U15.3, U31.9, U48.9
/Address Register (AR)/IBUS8: P1.B34, U3.18, U35.2, U50.2
/Address Register (AR)/IBUS9: P1.B35, U3.17, U35.3, U50.3
/Address Register (AR)/IBUS10: P1.B36, U3.16, U35.4, U50.4
/Address Register (AR)/IBUS11: P1.B37, U3.15, U35.5, U50.5
/Address Register (AR)/IBUS12: P1.B38, U3.14, U35.6, U50.6
/Address Register (AR)/IBUS13: P1.B39, U3.13, U35.7, U50.7
/Address Register (AR)/IBUS14: P1.B40, U3.12, U35.8, U50.8
/Address Register (AR)/IBUS15: P1.B41, U3.11, U35.9, U50.9
/Address Register (AR)/~ABEN1: JP4.2, U32.1, U36.1, U38.1
/Address Register (AR)/~ABEN2: U32.19, U36.19, U38.19, U51.4
/CLK2: P1.B4, R17.1, U18.1
/CLK3: P1.A3, R21.1
/CLK4: P1.A4, U7.5
/Constant Store/RADDR0: P1.B15, U1.2, U5.1
/Constant Store/RADDR1: P1.B16, U1.3, U5.2
/Constant Store/RADDR2: P1.B17, U2.1, U5.3
/Constant Store/RADDR3: P1.B18, U2.2, U5.6
/Constant Store/RADDR4: P1.B19, U2.3, U5.5
/Constant Store/~CSEN: JP1.2, U2.5
/Constant Store/~CSOE: U1.1, U2.14, U3.1
/HALT: U43.4, U45.1
/IR0: P1.B44, U20.1
/IR1: P1.B45, U23.1
/IR2: P1.B46, U27.1
/Memory Bank Unit (MBU)/8×8 Register File/RD0: J1.10, U9.10, U11.10, U12.2
/Memory Bank Unit (MBU)/8×8 Register File/RD1: J1.12, U9.9, U11.9, U12.3
/Memory Bank Unit (MBU)/8×8 Register File/RD2: J1.11, U9.7, U11.7, U12.4
/Memory Bank Unit (MBU)/8×8 Register File/RD3: J1.7, U9.6, U11.6, U12.5
/Memory Bank Unit (MBU)/8×8 Register File/RD4: J2.9, U12.6, U14.10, U15.10
/Memory Bank Unit (MBU)/8×8 Register File/RD5: J2.11, U12.7, U14.9, U15.9
/Memory Bank Unit (MBU)/8×8 Register File/RD6: J2.12, U12.8, U14.7, U15.7
/Memory Bank Unit (MBU)/8×8 Register File/RD7: J2.7, U13.1, U14.6, U15.6
/Memory Bank Unit (MBU)/Control Logic/CUR0: U20.5, U21.1
/Memory Bank Unit (MBU)/Control Logic/CUR1: U23.5, U24.1
/Memory Bank Unit (MBU)/Control Logic/CUR2: U27.5, U28.1
/Memory Bank Unit (MBU)/Control Logic/~IR-IDXR: U18.3, U20.6, U23.6, U27.6
/Memory Bank Unit (MBU)/DB0: P1.A15, U19.18, U48.18
/Memory Bank Unit (MBU)/DB1: P1.A16, U19.17, U48.17
/Memory Bank Unit (MBU)/DB2: P1.A17, U19.16, U48.16
/Memory Bank Unit (MBU)/DB3: P1.A18, U19.15, U48.15
/Memory Bank Unit (MBU)/DB4: P1.A19, U19.14, U48.14
/Memory Bank Unit (MBU)/DB5: P1.A20, U19.13, U48.13
/Memory Bank Unit (MBU)/DB6: P1.A21, U19.12, U48.12
/Memory Bank Unit (MBU)/DB7: P1.A22, U19.11, U48.11
/Memory Bank Unit (MBU)/RA0: J1.8, U9.5, U11.5, U14.5, U15.5, U21.5
/Memory Bank Unit (MBU)/RA1: J2.6, U9.4, U11.4, U14.4, U15.4, U24.5
/Memory Bank Unit (MBU)/ROM: D1.2, R9.1, U13.2
/Memory Bank Unit (MBU)/WA0: J1.3, U9.14, U11.14, U14.14, U15.14, U16.5
/Memory Bank Unit (MBU)/WA1: J2.5, U9.13, U11.13, U14.13, U15.13, U25.5
/Memory Bank Unit (MBU)/WADDR0: P1.B20, U20.2
/Memory Bank Unit (MBU)/WADDR1: P1.B21, U7.1, U23.2
/Memory Bank Unit (MBU)/WADDR2: P1.B22, U7.2, U17.1
/Memory Bank Unit (MBU)/WADDR3: P1.B23, U7.3, U17.2
/Memory Bank Unit (MBU)/WADDR4: P1.B24, U7.4, U17.3
/Memory Bank Unit (MBU)/~EN: R23.1, U8.5, U12.1, U13.6
/Memory Bank Unit (MBU)/~IOMBR: U10.15, U16.6, U19.1, U25.6, U29.6, U41.1
/Memory Bank Unit (MBU)/~IOWMBR: U8.6, U26.1, U40.1, U41.4
/Memory Bank Unit (MBU)/~REN0: J2.10, U9.11, U14.11, U28.5
/Memory Bank Unit (MBU)/~REN1: U11.11, U15.11, U28.3
/Memory Bank Unit (MBU)/~RG: U6.4, U21.7, U24.7, U28.7
/Memory Bank Unit (MBU)/~RMBP: U4.1, U5.10, U6.2
/Memory Bank Unit (MBU)/~WEN0: J1.5, U9.12, U14.12, U26.4
/Memory Bank Unit (MBU)/~WEN1: U11.12, U15.12, U40.4
/Memory Bank Unit (MBU)/~WMBP: U7.9, U26.3, U40.3
/Wait States & Write Strobes/CLK2': R17.2, U42.6
/Wait States & Write Strobes/DB8: P1.A56, U50.18
/Wait States & Write Strobes/DB9: P1.A57, U50.17
/Wait States & Write Strobes/DB10: P1.A58, U50.16
/Wait States & Write Strobes/DB11: P1.A59, U50.15
/Wait States & Write Strobes/DB12: P1.A60, U50.14
/Wait States & Write Strobes/DB13: P1.A61, U50.13
/Wait States & Write Strobes/DB14: P1.A62, U50.12
/Wait States & Write Strobes/DB15: P1.A63, U50.11
/Wait States & Write Strobes/~BUSEN: TP5.1, U48.19, U49.4, U50.19
/Wait States & Write Strobes/~SETWS: JP3.2, TP3.1, U47.7
/Wait States & Write Strobes/~WAITING0: R12.2, U44.1, U47.3, U49.6
/Wait States & Write Strobes/~WEN-DELAYED: R13.1, R15.2, U34.1, U44.6
/Wait States & Write Strobes/~WS-in-T34: JP3.3, U46.4
/Wait States & Write Strobes/~WSTB: U42.3, U44.3
/Wait States & Write Strobes/~W₀: R18.1, U44.4
/~FPAEXT: P1.B78, U39.1
/~FPRAM~∕ROM: D1.1, P1.A78
/~HALT: P1.B60, R11.1, U51.2
/~IO: P1.B26, U30.5, U33.1, U49.3
/~IODEV1xx: P1.A24, U30.14
/~IODEV2xx: P1.A25, U30.13
/~IODEV3xx: P1.A26, U30.12
/~IR-IDX: P1.A80, U18.7
/~MEM: P1.B25, U33.2, U49.1
/~R: P1.A27, U19.19, U48.1, U50.1
/~RESET: P1.B6, U8.7, U18.6
/~RSTHOLD: P1.A6, R22.1
/~SYSDEV: P1.A23, U10.4, U30.15
/~T34: JP5.3, P1.B5, U46.2
/~W: P1.A28, R8.1, U41.2
/~WAITING: P1.B29, R12.1
/~WAR: U17.14, U21.6, U24.6, U28.6, U31.11, U35.11, U37.11
/~WEN: P1.B67, R10.1, R15.1
/~WS: JP3.1, P1.B27, R14.2, U46.1
GND: C1.2, C2.2, C3.2, C4.2, C5.2, C6.2, C7.2, C8.2, C9.2, C10.2, C11.2, C12.2, C13.2, C14.2, C15.2, C16.2, C17.2, C18.2, C19.2, C20.2, C21.2, C22.2, C23.2, C24.2, C25.2, C26.2, C27.2, C28.2, C29.2, C30.2, C31.2, C32.2, C33.2, C34.2, C35.2, C36.2, C37.2, C38.2, C39.2, C40.2, C41.2, C42.2, C43.2, C44.2, C45.2, C46.2, C47.2, C48.2, C49.2, C50.2, C51.2, C52.2, C53.2, C54.2, C55.2, C56.2, D2.1, D5.1, J2.8, JP1.1, JP4.1, JP5.1, P1.A72, P1.A73, P1.B1, P1.B2, P1.B81, P1.B82, R1.1, R2.1, R3.1, R4.1, R5.1, R6.1, R7.1, U1.4, U1.5, U1.6, U1.7, U1.8, U1.9, U1.10, U1.19, U2.4, U2.8, U3.2, U3.3, U3.4, U3.5, U3.6, U3.7, U3.8, U3.9, U3.10, U3.19, U4.10, U4.19, U5.4, U5.8, U6.3, U7.8, U8.4, U9.8, U10.8, U11.8, U12.9, U12.10, U12.19, U13.4, U13.7, U14.8, U15.8, U16.2, U16.4, U16.7, U17.4, U17.5, U17.8, U18.4, U19.10, U20.4, U20.7, U21.4, U22.3, U23.4, U23.7, U24.4, U25.2, U25.4, U25.7, U26.2, U27.2, U27.4, U27.7, U28.4, U29.2, U29.4, U29.7, U30.4, U30.8, U31.1, U31.10, U32.10, U33.3, U34.3, U35.1, U35.10, U36.10, U37.1, U37.10, U38.10, U39.10, U39.19, U40.2, U41.3, U42.4, U43.3, U44.5, U45.3, U46.3, U47.2, U47.4, U48.10, U49.2, U50.10, U51.3
unnamed: D2.2, R16.1
unnamed: D5.2, R23.2
unnamed: JP4.3, U33.4
unnamed: JP5.2, U51.1
unnamed: R8.2, U45.4
unnamed: R10.2, U22.2
unnamed: R11.2, U43.2
unnamed: R16.2, U47.5
unnamed: R18.2, U45.2
unnamed: R21.2, U47.1
unnamed: R22.2, U47.6
unnamed: U22.4, U34.2
unnamed: U26.6, U29.5
unnamed: U29.3, U40.6
unnamed: U34.4, U42.7
