alexiosc/cft/kicad/cft/cft-board0/cft-board0.kicad_pcb

## KiCad design kicad/cft/cft-board0/cft-board0.kicad_pcb (2021-03-05)

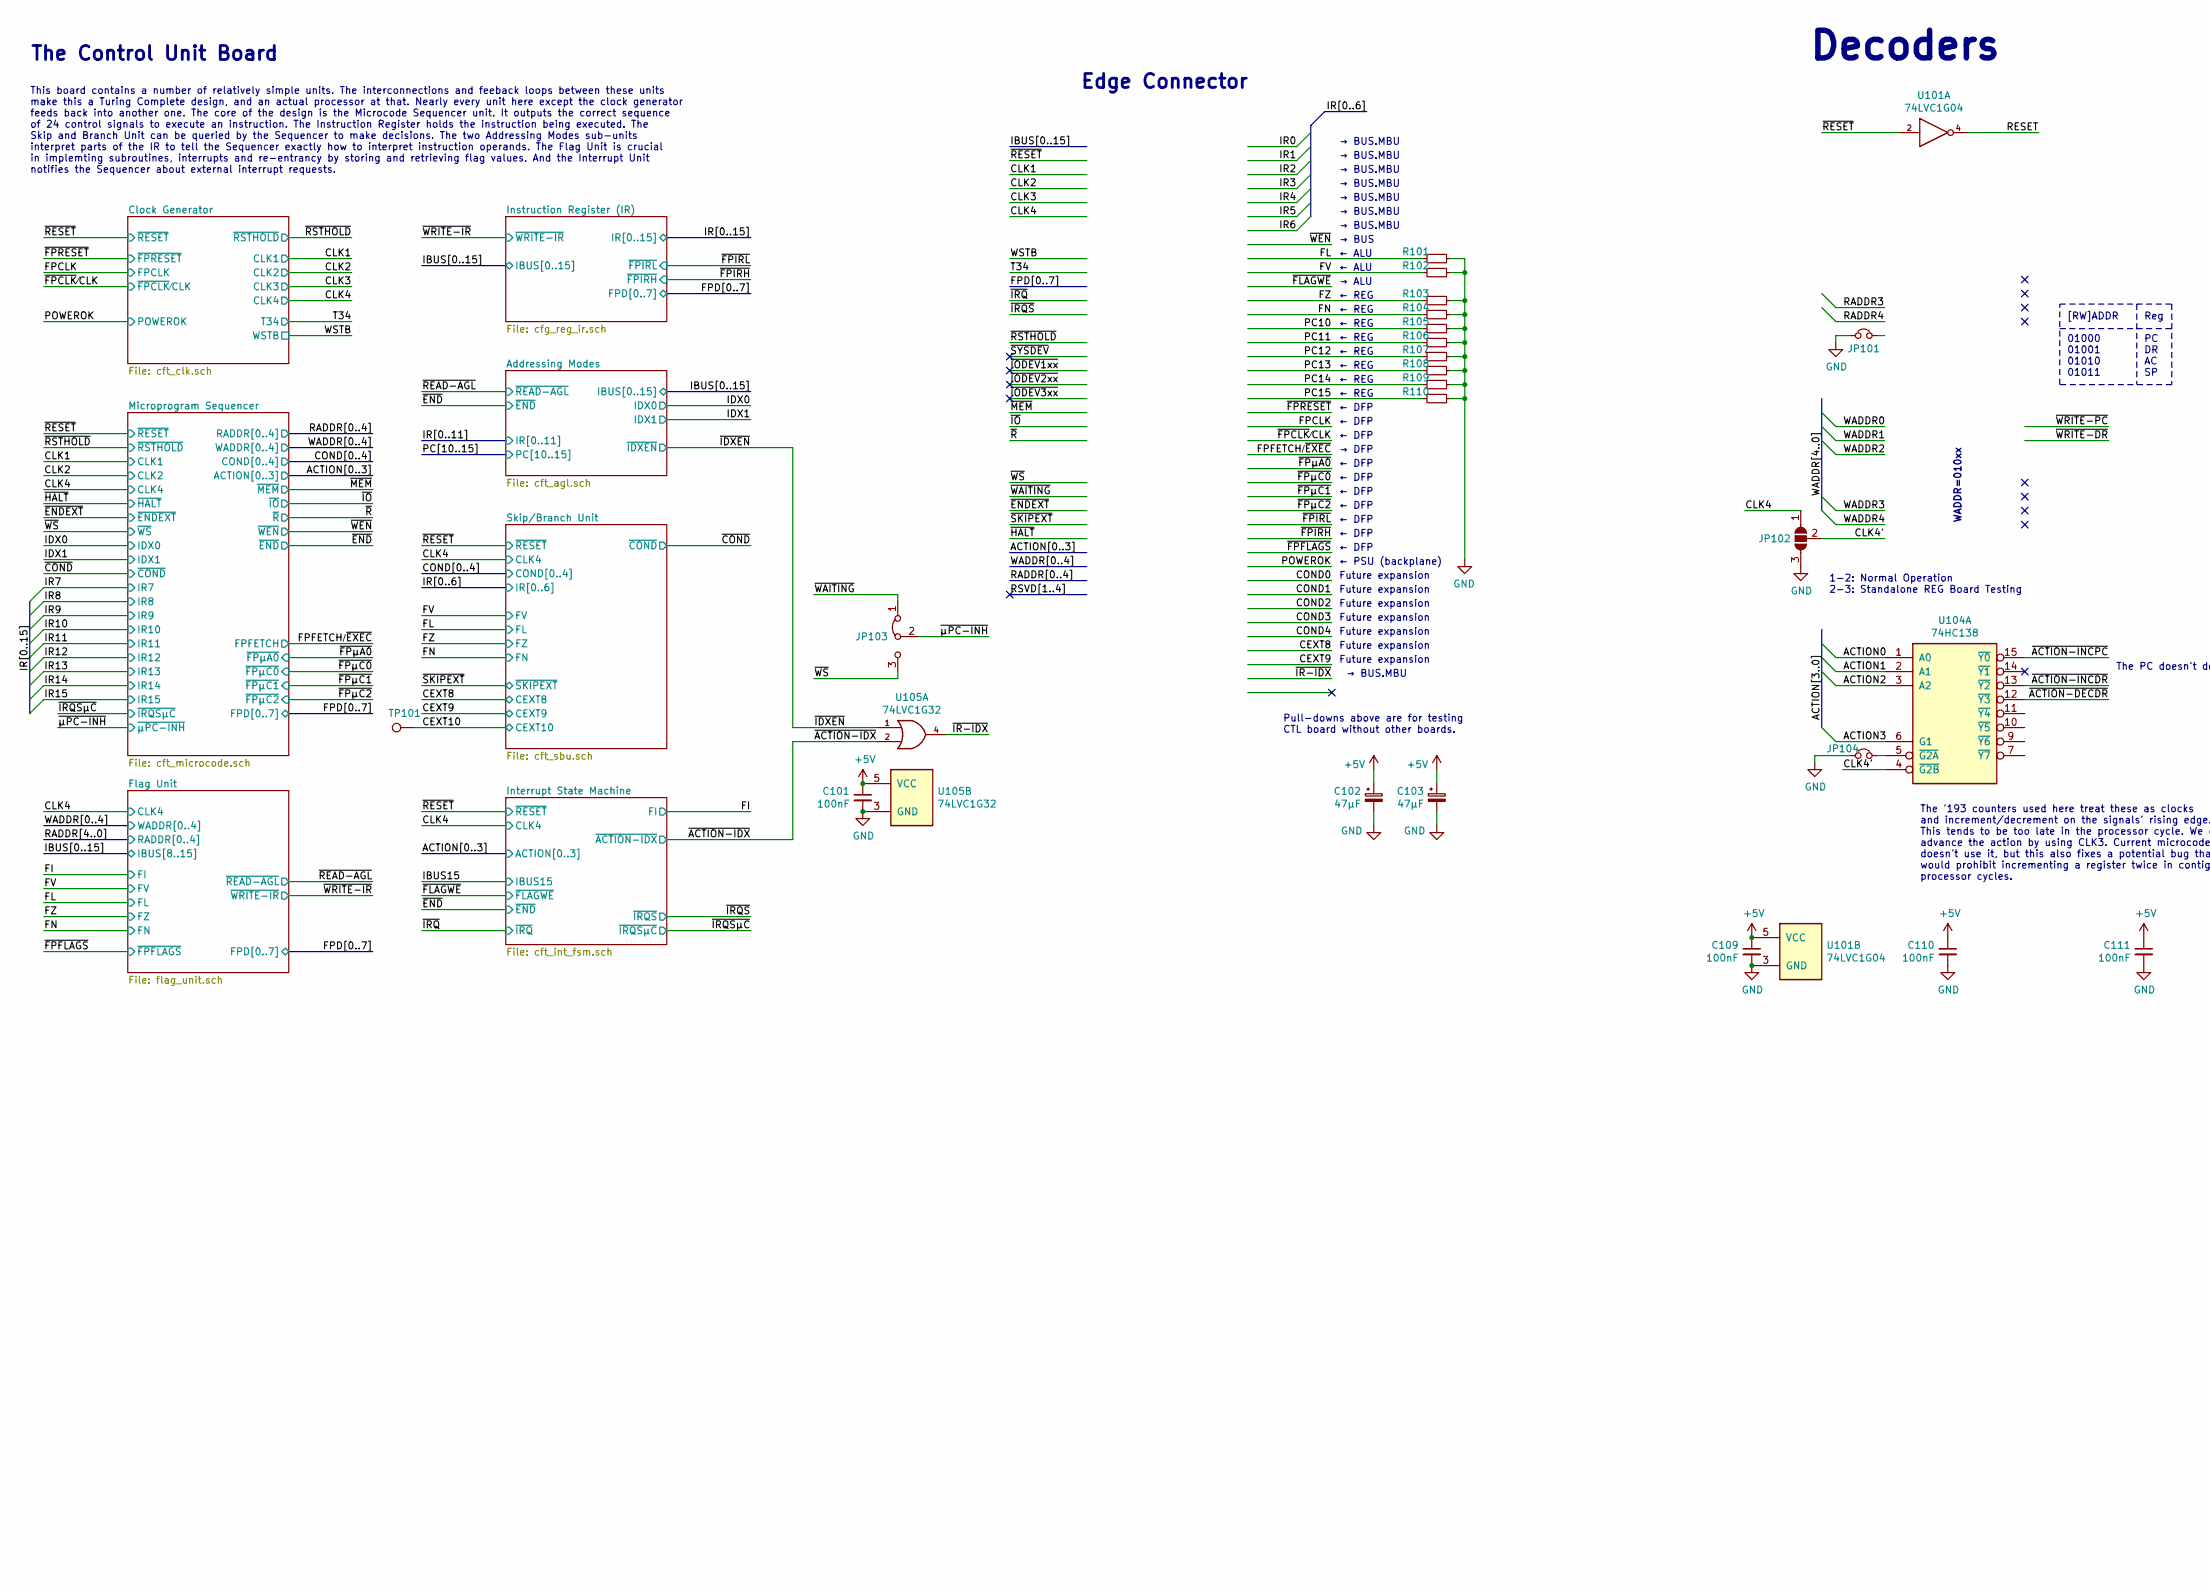
[picture p81: schematic cft-board0.sch, Control Unit Board, part in row 1, column 1]

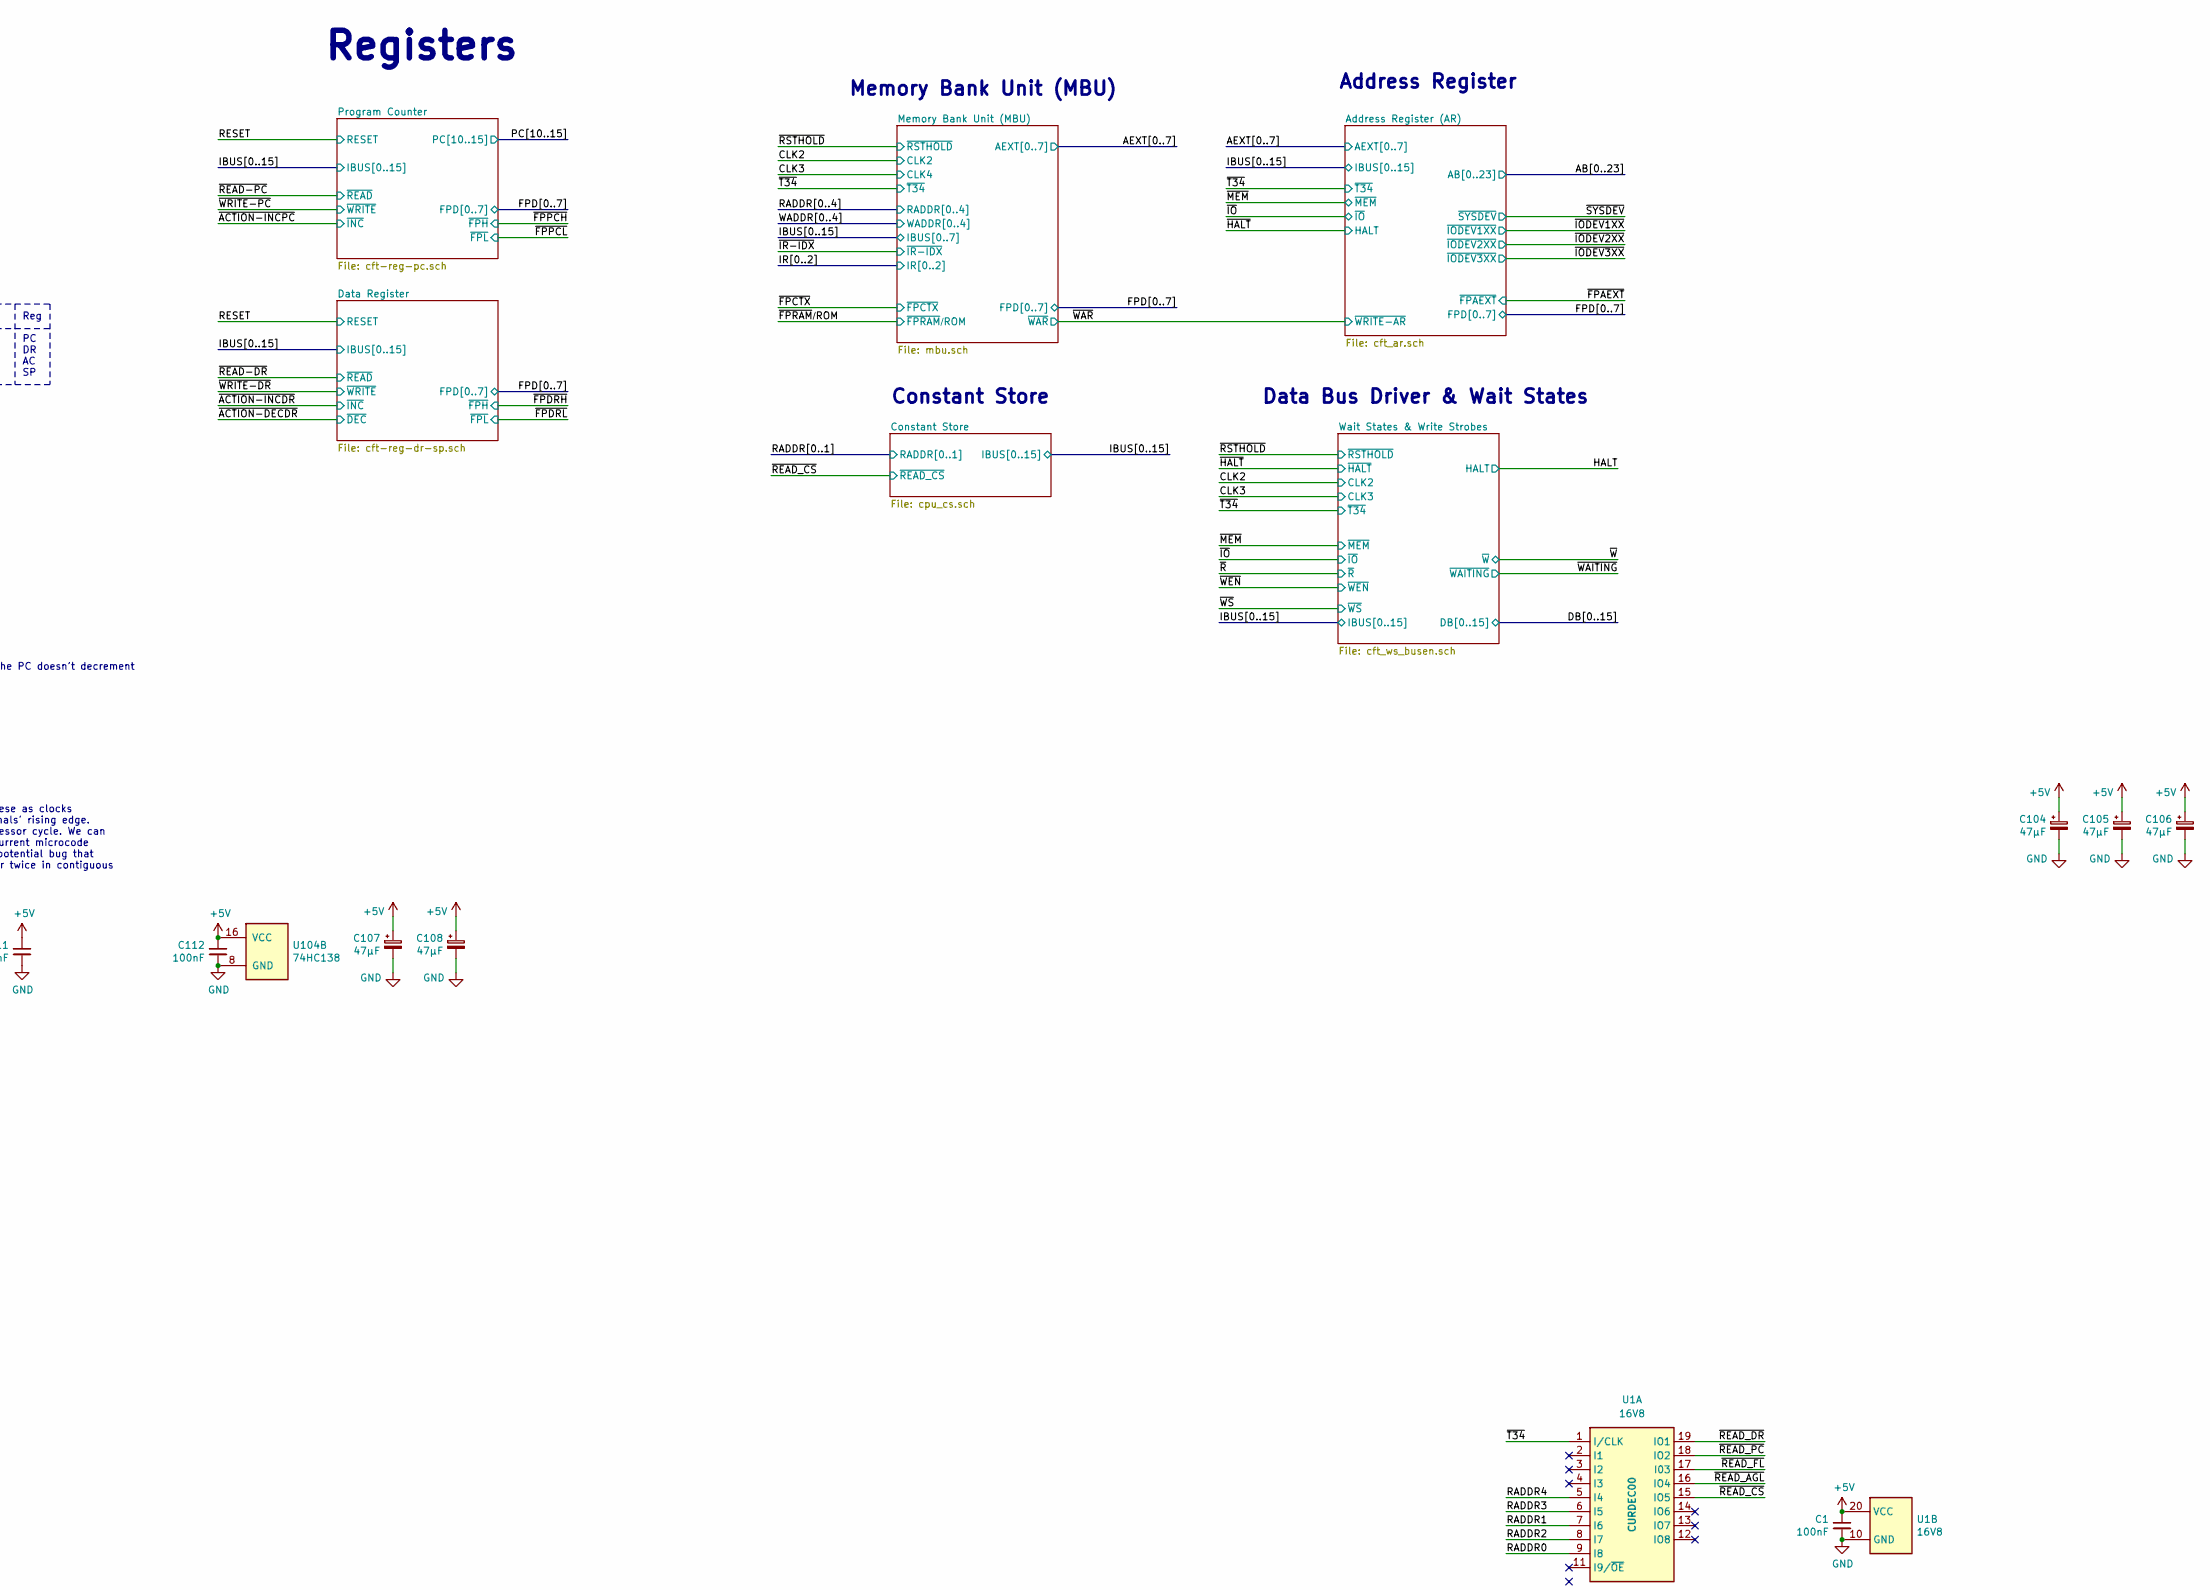
[picture p82: schematic cft-board0.sch, Control Unit Board, part in row 1, column 2]

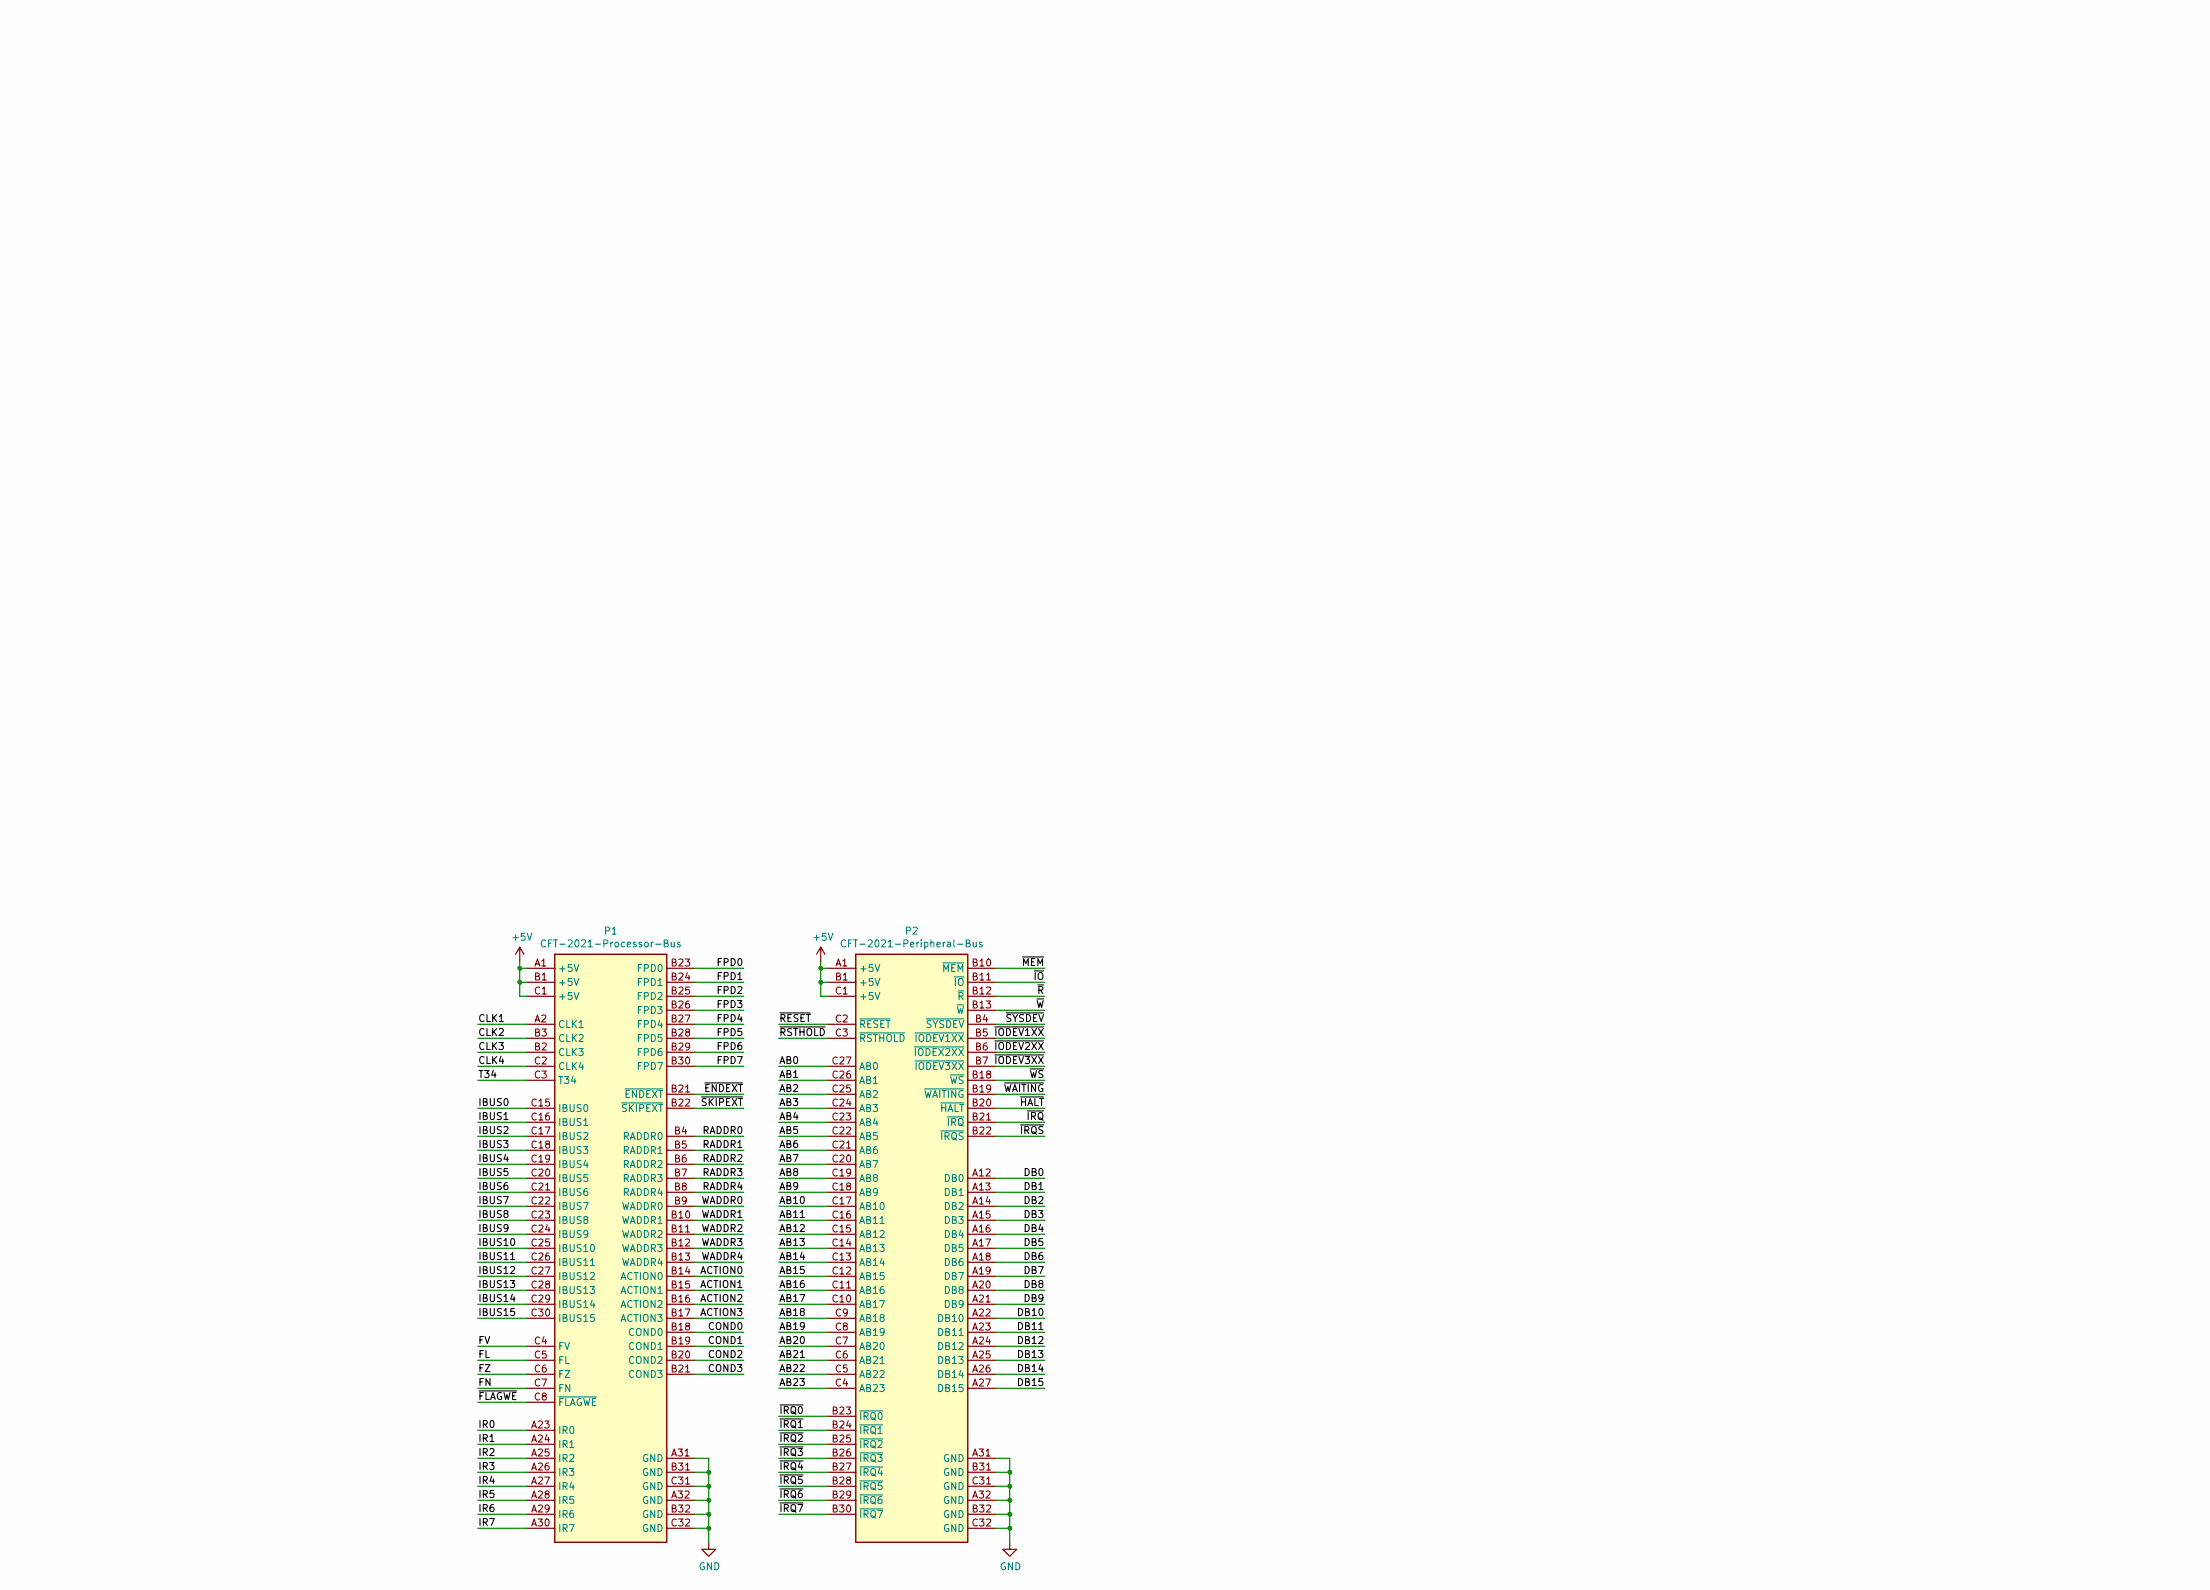
[picture p83: schematic cft-board0.sch, Control Unit Board, part in row 2, column 1]

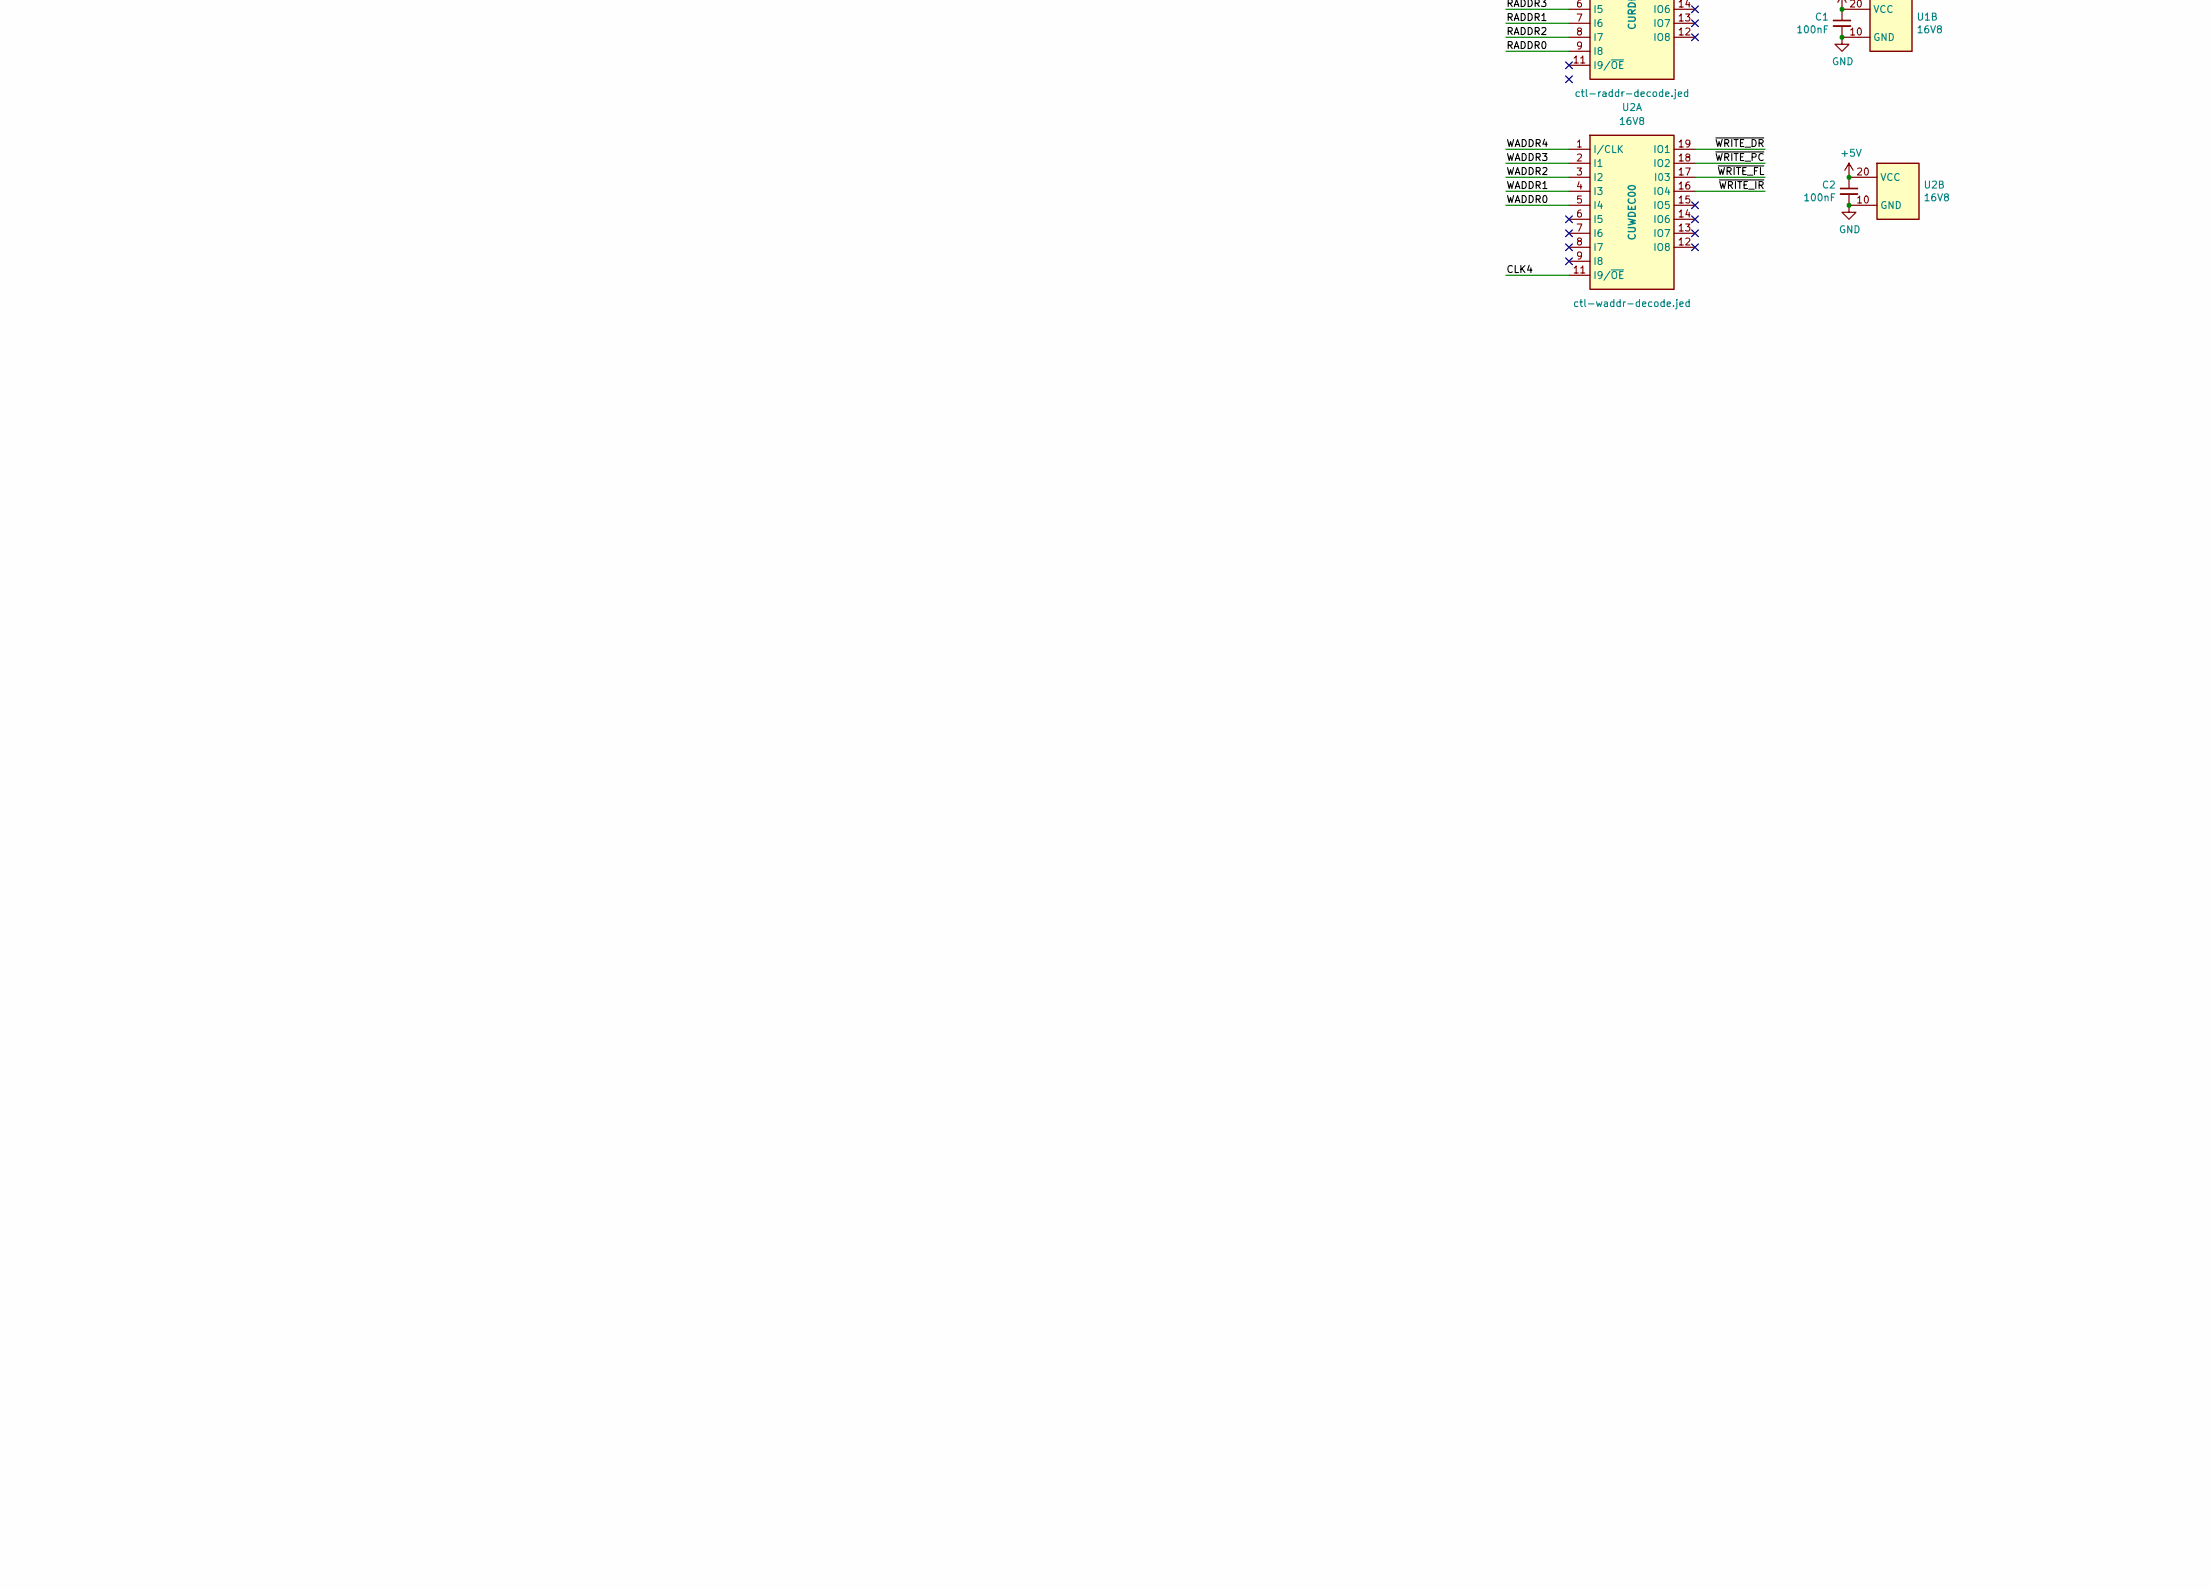
[picture p84: schematic cft-board0.sch, Control Unit Board, part in row 2, column 2]

Parts:
C1, C2, C109, C110, C111, C112: 100nF; SMD_0805_2012Metric_Pad1.15x1.40mm_HandSolder
C101: 100nF; C_SMD_0805_2012Metric_Pad1.15x1.40mm_HandSolder
C102, C103, C104, C105, C106, C107, C108: 47µF; CP_Radial_D6.3mm_P2.50mm
JP101, JP104: Jumper_NC_Small; SolderJumper-2_P1.3mm_Bridged_RoundedPad1.0x1.5mm
JP102: SolderJumper_3_Open; SolderJumper-3_P1.3mm_Open_RoundedPad1.0x1.5mm
JP103: Jumper_3_Bridged12; SolderJumper-3_P1.3mm_Bridged12_RoundedPad1.0x1.5mm
P1: CFT-2021-Processor-Bus; DIN41612_B_3x32_Horizontal
P2: CFT-2021-Peripheral-Bus; DIN41612_B_3x32_Horizontal
R101, R102, R103, R104, R105, R106, R107, R108, R109, R110: 4.7kΩ; R_SMD_0805_2012Metric_Pad1.15x1.40mm_HandSolder
TP101: TestPoint; TestPoint_Pad_1.0x1.0mm
U1, U2: 16V8; DIP-20_W7.62mm_Socket
U101: 74LVC1G04; SOT-23-5_HandSoldering
U104: 74HC138; DIP-16_W7.62mm_Socket
U105: 74LVC1G32; SOT-23-5_HandSoldering

Connections:
+5V: C1.1, C2.1, C101.1, C102.1, C103.1, C104.1, C105.1, C106.1, C107.1, C108.1, C109.1, C110.1, C111.1, C112.1, P1.A1 (+5V), P1.B1 (+5V), P1.C1 (+5V), P2.A1 (+5V), P2.B1 (+5V), P2.C1 (+5V), U1.20 (VCC), U2.20 (VCC), U101.5 (VCC), U104.16 (VCC), U105.5 (VCC); also elsewhere on the board
/AB0: P2.C27 (AB0); also elsewhere on the board
/AB1: P2.C26 (AB1); also elsewhere on the board
/AB2: P2.C25 (AB2); also elsewhere on the board
/AB3: P2.C24 (AB3); also elsewhere on the board
/AB4: P2.C23 (AB4); also elsewhere on the board
/AB5: P2.C22 (AB5); also elsewhere on the board
/AB6: P2.C21 (AB6); also elsewhere on the board
/AB7: P2.C20 (AB7); also elsewhere on the board
/AB8: P2.C19 (AB8); also elsewhere on the board
/AB9: P2.C18 (AB9); also elsewhere on the board
/AB10: P2.C17 (AB10); also elsewhere on the board
/AB11: P2.C16 (AB11); also elsewhere on the board
/AB12: P2.C15 (AB12); also elsewhere on the board
/AB13: P2.C14 (AB13); also elsewhere on the board
/AB14: P2.C13 (AB14); also elsewhere on the board
/AB15: P2.C12 (AB15); also elsewhere on the board
/AB16: P2.C11 (AB16); also elsewhere on the board
/AB17: P2.C10 (AB17); also elsewhere on the board
/AB18: P2.C9 (AB18); also elsewhere on the board
/AB19: P2.C8 (AB19); also elsewhere on the board
/AB20: P2.C7 (AB20); also elsewhere on the board
/AB21: P2.C6 (AB21); also elsewhere on the board
/AB22: P2.C5 (AB22); also elsewhere on the board
/AB23: P2.C4 (AB23); also elsewhere on the board
/ACTION0: P1.B14 (ACTION0), U104.1 (A0); also elsewhere on the board
/ACTION1: P1.B15 (ACTION1), U104.2 (A1); also elsewhere on the board
/ACTION2: P1.B16 (ACTION2), U104.3 (A2); also elsewhere on the board
/ACTION3: P1.B17 (ACTION3), U104.6 (G1); also elsewhere on the board
/CEXT10: TP101.1; also elsewhere on the board
/CLK1: P1.A2 (CLK1); also elsewhere on the board
/CLK2: P1.B3 (CLK2); also elsewhere on the board
/CLK3: P1.B2 (CLK3); also elsewhere on the board
/CLK4: JP102.1 (A), P1.C2 (CLK4), U2.11 (I9/~OE~); also elsewhere on the board
/CLK4': JP102.2 (C), U104.4 (~G2B)
/COND0: P1.B18 (COND0); also elsewhere on the board
/COND1: P1.B19 (COND1); also elsewhere on the board
/COND2: P1.B20 (COND2); also elsewhere on the board
/COND3: P1.B21 (COND3); also elsewhere on the board
/DB0: P2.A12 (DB0); also elsewhere on the board
/DB1: P2.A13 (DB1); also elsewhere on the board
/DB2: P2.A14 (DB2); also elsewhere on the board
/DB3: P2.A15 (DB3); also elsewhere on the board
/DB4: P2.A16 (DB4); also elsewhere on the board
/DB5: P2.A17 (DB5); also elsewhere on the board
/DB6: P2.A18 (DB6); also elsewhere on the board
/DB7: P2.A19 (DB7); also elsewhere on the board
/DB8: P2.A20 (DB8); also elsewhere on the board
/DB9: P2.A21 (DB9); also elsewhere on the board
/DB10: P2.A22 (DB10); also elsewhere on the board
/DB11: P2.A23 (DB11); also elsewhere on the board
/DB12: P2.A24 (DB12); also elsewhere on the board
/DB13: P2.A25 (DB13); also elsewhere on the board
/DB14: P2.A26 (DB14); also elsewhere on the board
/DB15: P2.A27 (DB15); also elsewhere on the board
/FL: P1.C5 (FL), R101.1; also elsewhere on the board
/FN: P1.C7 (FN), R104.1; also elsewhere on the board
/FPD0: P1.B23 (FPD0); also elsewhere on the board
/FPD1: P1.B24 (FPD1); also elsewhere on the board
/FPD2: P1.B25 (FPD2); also elsewhere on the board
/FPD3: P1.B26 (FPD3); also elsewhere on the board
/FPD4: P1.B27 (FPD4); also elsewhere on the board
/FPD5: P1.B28 (FPD5); also elsewhere on the board
/FPD6: P1.B29 (FPD6); also elsewhere on the board
/FPD7: P1.B30 (FPD7); also elsewhere on the board
/FV: P1.C4 (FV), R102.1; also elsewhere on the board
/FZ: P1.C6 (FZ), R103.1; also elsewhere on the board
/IBUS0: P1.C15 (IBUS0); also elsewhere on the board
/IBUS1: P1.C16 (IBUS1); also elsewhere on the board
/IBUS2: P1.C17 (IBUS2); also elsewhere on the board
/IBUS3: P1.C18 (IBUS3); also elsewhere on the board
/IBUS4: P1.C19 (IBUS4); also elsewhere on the board
/IBUS5: P1.C20 (IBUS5); also elsewhere on the board
/IBUS6: P1.C21 (IBUS6); also elsewhere on the board
/IBUS7: P1.C22 (IBUS7); also elsewhere on the board
/IBUS8: P1.C23 (IBUS8); also elsewhere on the board
/IBUS9: P1.C24 (IBUS9); also elsewhere on the board
/IBUS10: P1.C25 (IBUS10); also elsewhere on the board
/IBUS11: P1.C26 (IBUS11); also elsewhere on the board
/IBUS12: P1.C27 (IBUS12); also elsewhere on the board
/IBUS13: P1.C28 (IBUS13); also elsewhere on the board
/IBUS14: P1.C29 (IBUS14); also elsewhere on the board
/IBUS15: P1.C30 (IBUS15); also elsewhere on the board
/IR0: P1.A23 (IR0); also elsewhere on the board
/IR1: P1.A24 (IR1); also elsewhere on the board
/IR2: P1.A25 (IR2); also elsewhere on the board
/IR3: P1.A26 (IR3); also elsewhere on the board
/IR4: P1.A27 (IR4); also elsewhere on the board
/IR5: P1.A28 (IR5); also elsewhere on the board
/IR6: P1.A29 (IR6); also elsewhere on the board
/IR7: P1.A30 (IR7); also elsewhere on the board
/PC10: R105.1; also elsewhere on the board
/PC11: R106.1; also elsewhere on the board
/PC12: R107.1; also elsewhere on the board
/PC13: R108.1; also elsewhere on the board
/PC14: R109.1; also elsewhere on the board
/PC15: R110.1; also elsewhere on the board
/RADDR0: P1.B4 (RADDR0), U1.9 (I8); also elsewhere on the board
/RADDR1: P1.B5 (RADDR1), U1.7 (I6); also elsewhere on the board
/RADDR2: P1.B6 (RADDR2), U1.8 (I7); also elsewhere on the board
/RADDR3: P1.B7 (RADDR3), U1.6 (I5); also elsewhere on the board
/RADDR4: P1.B8 (RADDR4), U1.5 (I4); also elsewhere on the board
/RESET: U101.4; also elsewhere on the board
/T34: P1.C3 (T34); also elsewhere on the board
/WADDR0: P1.B9 (WADDR0), U2.5 (I4); also elsewhere on the board
/WADDR1: P1.B10 (WADDR1), U2.4 (I3); also elsewhere on the board
/WADDR2: P1.B11 (WADDR2), U2.3 (I2); also elsewhere on the board
/WADDR3: P1.B12 (WADDR3), U2.2 (I1); also elsewhere on the board
/WADDR4: P1.B13 (WADDR4), U2.1 (I/CLK); also elsewhere on the board
/~ACTION-DECDR: U104.12 (~Y3); also elsewhere on the board
/~ACTION-IDX: U105.2; also elsewhere on the board
/~ACTION-INCDR: U104.13 (~Y2); also elsewhere on the board
/~ACTION-INCPC: U104.15 (~Y0); also elsewhere on the board
/~FLAGWE: P1.C8 (~FLAGWE); also elsewhere on the board
/~HALT: P2.B20 (~HALT); also elsewhere on the board
/~IDXEN: U105.1; also elsewhere on the board
/~IO: P2.B11 (~IO); also elsewhere on the board
/~IODEV1XX: P2.B5 (~IODEV1XX); also elsewhere on the board
/~IODEV2XX: P2.B6 (~IODEX2XX); also elsewhere on the board
/~IODEV3XX: P2.B7 (~IODEV3XX); also elsewhere on the board
/~IR-IDX: U105.4; also elsewhere on the board
/~IRQ: P2.B21 (~IRQ); also elsewhere on the board
/~IRQ0: P2.B23 (~IRQ0)
/~IRQ1: P2.B24 (~IRQ1)
/~IRQ2: P2.B25 (~IRQ2)
/~IRQ3: P2.B26 (~IRQ3)
/~IRQ4: P2.B27 (~IRQ4)
/~IRQ5: P2.B28 (~IRQ5)
/~IRQ6: P2.B29 (~IRQ6)
/~IRQ7: P2.B30 (~IRQ7)
/~IRQS: P2.B22 (~IRQS); also elsewhere on the board
/~MEM: P2.B10 (~MEM); also elsewhere on the board
/~R: P2.B12 (~R); also elsewhere on the board
/~READ_AGL: U1.16 (IO4)
/~READ_CS: U1.15 (IO5); also elsewhere on the board
/~READ_DR: U1.19 (IO1)
/~READ_FL: U1.17 (I03)
/~READ_PC: U1.18 (IO2)
/~RESET: P2.C2 (~RESET), U101.2; also elsewhere on the board
/~RSTHOLD: P2.C3 (~RSTHOLD); also elsewhere on the board
/~SKIPEXT: P1.B22 (~SKIPEXT); also elsewhere on the board
/~SYSDEV: P2.B4 (~SYSDEV); also elsewhere on the board
/~T34: U1.1 (I/CLK); also elsewhere on the board
/~W: P2.B13 (~W); also elsewhere on the board
/~WAITING: JP103.1 (A), P2.B19 (~WAITING); also elsewhere on the board
/~WRITE_DR: U2.19 (IO1)
/~WRITE_FL: U2.17 (I03)
/~WRITE_IR: U2.16 (IO4)
/~WRITE_PC: U2.18 (IO2)
/~WS: JP103.3 (B), P2.B18 (~WS); also elsewhere on the board
/~µPC-INH: JP103.2 (C); also elsewhere on the board
GND: C1.2, C2.2, C101.2, C102.2, C103.2, C104.2, C105.2, C106.2, C107.2, C108.2, C109.2, C110.2, C111.2, C112.2, JP101.1, JP102.3 (B), JP104.1, P1.A31 (GND), P1.A32 (GND), P1.B31 (GND), P1.B32 (GND), P1.C31 (GND), P1.C32 (GND), P2.A31 (GND), P2.A32 (GND), P2.B31 (GND), P2.B32 (GND), P2.C31 (GND), P2.C32 (GND), R101.2, R102.2, R103.2, R104.2, R105.2, R106.2, R107.2, R108.2, R109.2, R110.2, U1.10 (GND), U2.10 (GND), U101.3 (GND), U104.8 (GND), U105.3 (GND); also elsewhere on the board
unnamed: JP104.2, U104.5 (~G2A)

Notes on the sheet:
Registers
Decoders
WADDR=010xx
The PC doesn't decrement
[RW]ADDR 01000 01001 01010 01011
Reg PC DR AC SP
The '193 counters used here treat these as clocks and increment/decrement on the signals' rising edge. This tends to be too late in the processor cycle. We can advance the action by using CLK3. Current microcode doesn't use it, but this also fixes a potential bug that would prohibit incrementing a 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
1-2: Normal Operation 2-3: Standalone REG Board Testing
Memory Bank Unit (MBU)
Data Bus Driver & Wait States
Constant Store
Address Register
Edge Connector
← ALU
→ BUS.MBU
→ ALU
← REG
← DFP
← PSU (backplane)
→ DFP
The Control Unit Board
This board contains a number of relatively simple units. The interconnections and feeback loops between these units make this a Turing Complete design, and an actual processor at that. Nearly every unit here except the clock generator feeds back into another one. The core of the design is the Micro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
Future expansion
→ BUS
Pull-downs above are for testing CTL board without other boards.
