alexiosc/cft/kicad/cft/cft-board0/cft-board0.kicad_pcb

## KiCad design kicad/cft/cft-board0/cft-board0.kicad_pcb (continued)

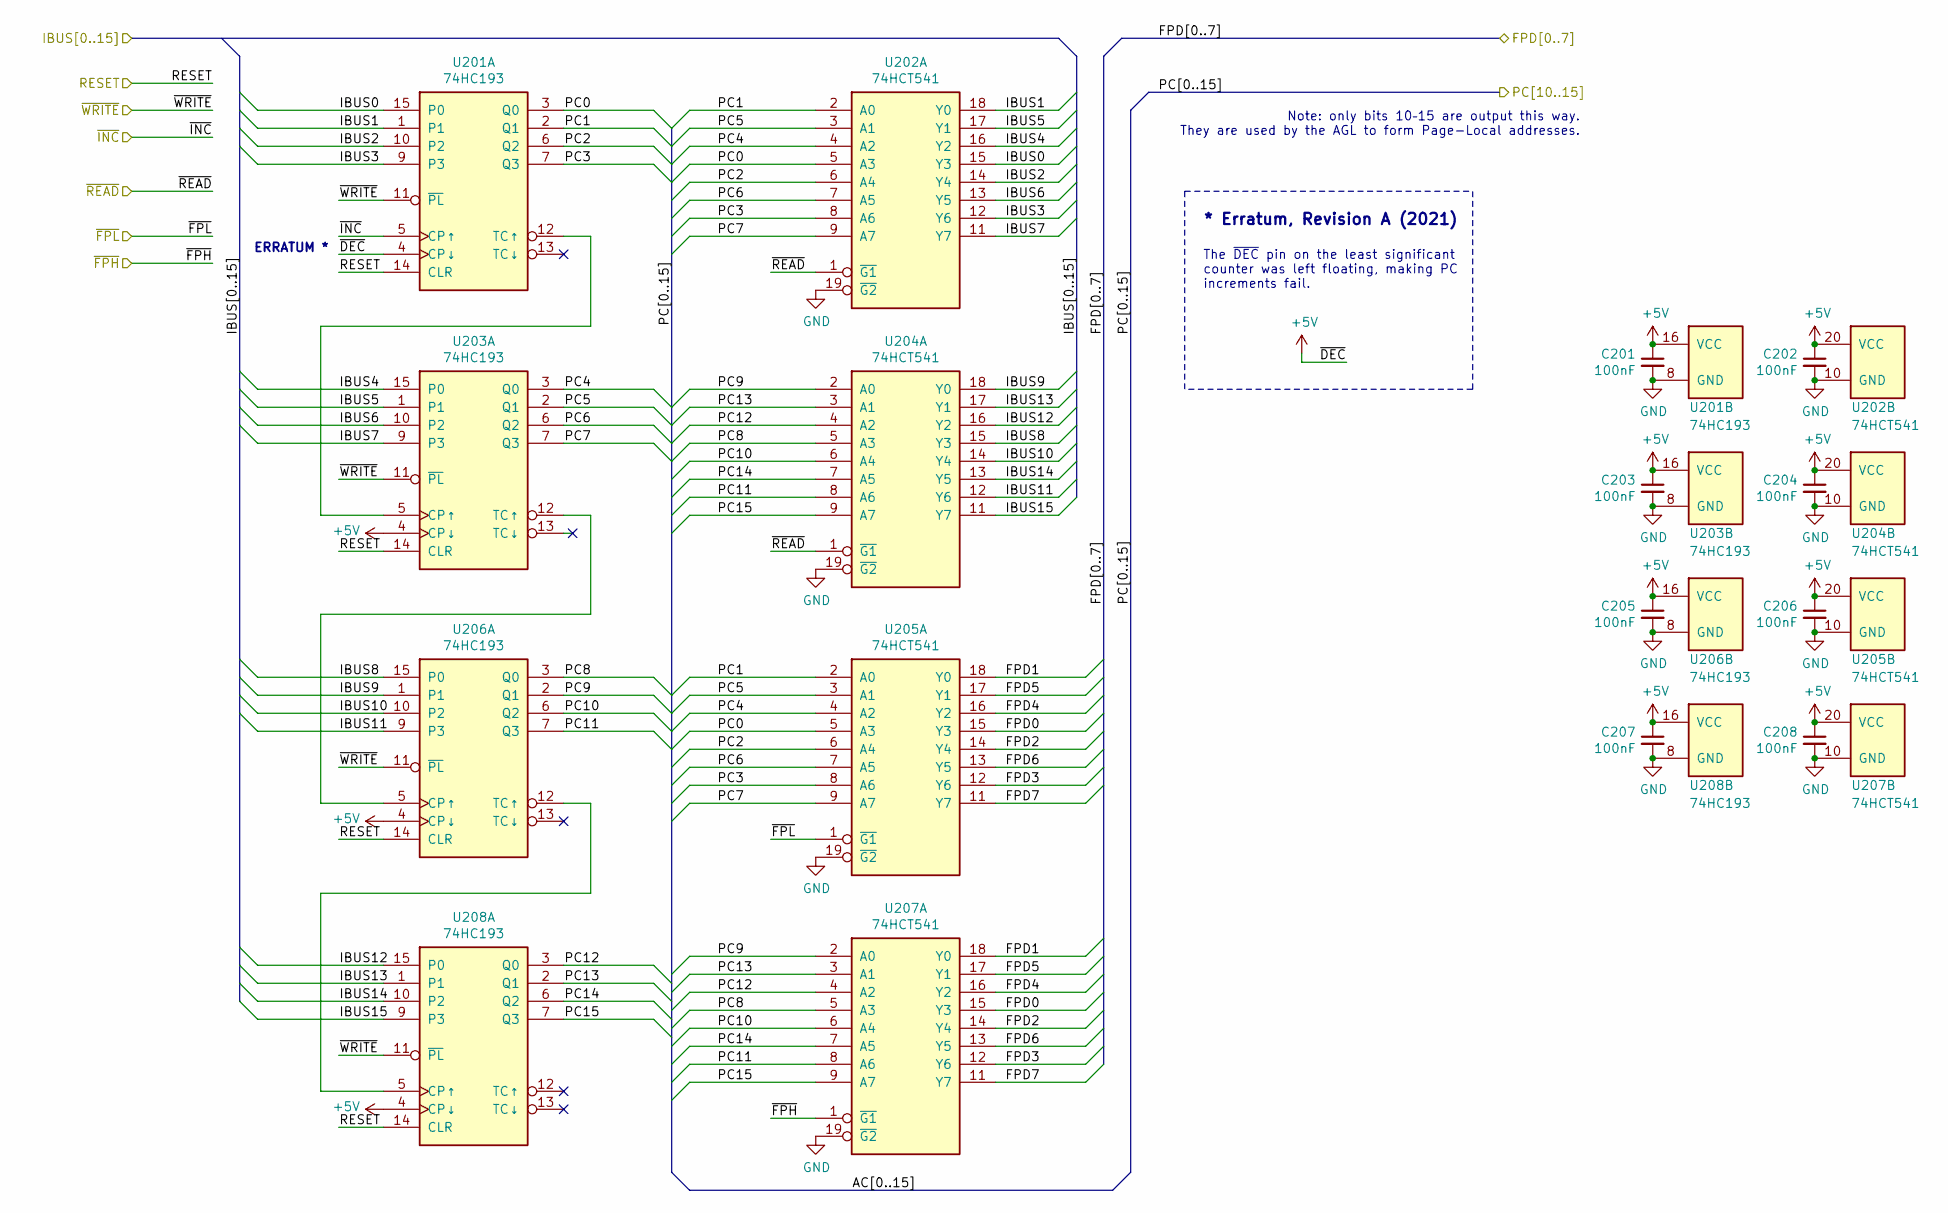
[picture p85: schematic cft-reg-pc.sch, Program Counter (PC)]

Parts:
C201, C202, C203, C204, C205, C206, C207, C208: 100nF; SMD_0805_2012Metric_Pad1.15x1.40mm_HandSolder
U201, U203, U206, U208: 74HC193; DIP-16_W7.62mm_Socket
U202, U204, U205, U207: 74HCT541; DIP-20_W7.62mm_Socket

Connections:
+5V: C201.1, C202.1, C203.1, C204.1, C205.1, C206.1, C207.1, C208.1, U201.4 (CP↓), U201.16 (VCC), U202.20 (VCC), U203.4 (CP↓), U203.16 (VCC), U204.20 (VCC), U205.20 (VCC), U206.4 (CP↓), U206.16 (VCC), U207.20 (VCC), U208.4 (CP↓), U208.16 (VCC); also elsewhere on the board
/FPD0: U205.15 (Y3), U207.15 (Y3); also elsewhere on the board
/FPD1: U205.18 (Y0), U207.18 (Y0); also elsewhere on the board
/FPD2: U205.14 (Y4), U207.14 (Y4); also elsewhere on the board
/FPD3: U205.12 (Y6), U207.12 (Y6); also elsewhere on the board
/FPD4: U205.16 (Y2), U207.16 (Y2); also elsewhere on the board
/FPD5: U205.17 (Y1), U207.17 (Y1); also elsewhere on the board
/FPD6: U205.13 (Y5), U207.13 (Y5); also elsewhere on the board
/FPD7: U205.11 (Y7), U207.11 (Y7); also elsewhere on the board
/IBUS0: U201.15 (P0), U202.15 (Y3); also elsewhere on the board
/IBUS1: U201.1, U202.18 (Y0); also elsewhere on the board
/IBUS2: U201.10 (P2), U202.14 (Y4); also elsewhere on the board
/IBUS3: U201.9 (P3), U202.12 (Y6); also elsewhere on the board
/IBUS4: U202.16 (Y2), U203.15 (P0); also elsewhere on the board
/IBUS5: U202.17 (Y1), U203.1; also elsewhere on the board
/IBUS6: U202.13 (Y5), U203.10 (P2); also elsewhere on the board
/IBUS7: U202.11 (Y7), U203.9 (P3); also elsewhere on the board
/IBUS8: U204.15 (Y3), U206.15 (P0); also elsewhere on the board
/IBUS9: U204.18 (Y0), U206.1; also elsewhere on the board
/IBUS10: U204.14 (Y4), U206.10 (P2); also elsewhere on the board
/IBUS11: U204.12 (Y6), U206.9 (P3); also elsewhere on the board
/IBUS12: U204.16 (Y2), U208.15 (P0); also elsewhere on the board
/IBUS13: U204.17 (Y1), U208.1; also elsewhere on the board
/IBUS14: U204.13 (Y5), U208.10 (P2); also elsewhere on the board
/IBUS15: U204.11 (Y7), U208.9 (P3); also elsewhere on the board
/PC10: U204.6 (A4), U206.6 (Q2), U207.6 (A4); also elsewhere on the board
/PC11: U204.8 (A6), U206.7 (Q3), U207.8 (A6); also elsewhere on the board
/PC12: U204.4 (A2), U207.4 (A2), U208.3 (Q0); also elsewhere on the board
/PC13: U204.3 (A1), U207.3 (A1), U208.2 (Q1); also elsewhere on the board
/PC14: U204.7 (A5), U207.7 (A5), U208.6 (Q2); also elsewhere on the board
/PC15: U204.9 (A7), U207.9 (A7), U208.7 (Q3); also elsewhere on the board
/Program Counter/PC0: U201.3 (Q0), U202.5 (A3), U205.5 (A3)
/Program Counter/PC1: U201.2 (Q1), U202.2 (A0), U205.2 (A0)
/Program Counter/PC2: U201.6 (Q2), U202.6 (A4), U205.6 (A4)
/Program Counter/PC3: U201.7 (Q3), U202.8 (A6), U205.8 (A6)
/Program Counter/PC4: U202.4 (A2), U203.3 (Q0), U205.4 (A2)
/Program Counter/PC5: U202.3 (A1), U203.2 (Q1), U205.3 (A1)
/Program Counter/PC6: U202.7 (A5), U203.6 (Q2), U205.7 (A5)
/Program Counter/PC7: U202.9 (A7), U203.7 (Q3), U205.9 (A7)
/Program Counter/PC8: U204.5 (A3), U206.3 (Q0), U207.5 (A3)
/Program Counter/PC9: U204.2 (A0), U206.2 (Q1), U207.2 (A0)
/RESET: U201.14 (CLR), U203.14 (CLR), U206.14 (CLR), U208.14 (CLR); also elsewhere on the board
/~ACTION-INCPC: U201.5 (CP↑); also elsewhere on the board
/~FPPCH: U207.1 (~G1)
/~FPPCL: U205.1 (~G1)
/~READ-PC: U202.1 (~G1), U204.1 (~G1)
/~WRITE-PC: U201.11 (~PL), U203.11 (~PL), U206.11 (~PL), U208.11 (~PL)
GND: C201.2, C202.2, C203.2, C204.2, C205.2, C206.2, C207.2, C208.2, U201.8 (GND), U202.10 (GND), U202.19 (~G2), U203.8 (GND), U204.10 (GND), U204.19 (~G2), U205.10 (GND), U205.19 (~G2), U206.8 (GND), U207.10 (GND), U207.19 (~G2), U208.8 (GND); also elsewhere on the board
unnamed: U201.12 (TC↑), U203.5 (CP↑)
unnamed: U203.12 (TC↑), U206.5 (CP↑)
unnamed: U206.12 (TC↑), U208.5 (CP↑)

Notes on the sheet:
Note: only bits 10–15 are output this way. They are used by the AGL to form Page-Local addresses.
* Erratum, Revision A (2021)
The ~DEC~ pin on the least significant counter was left floating, making PC increments fail.
ERRATUM *

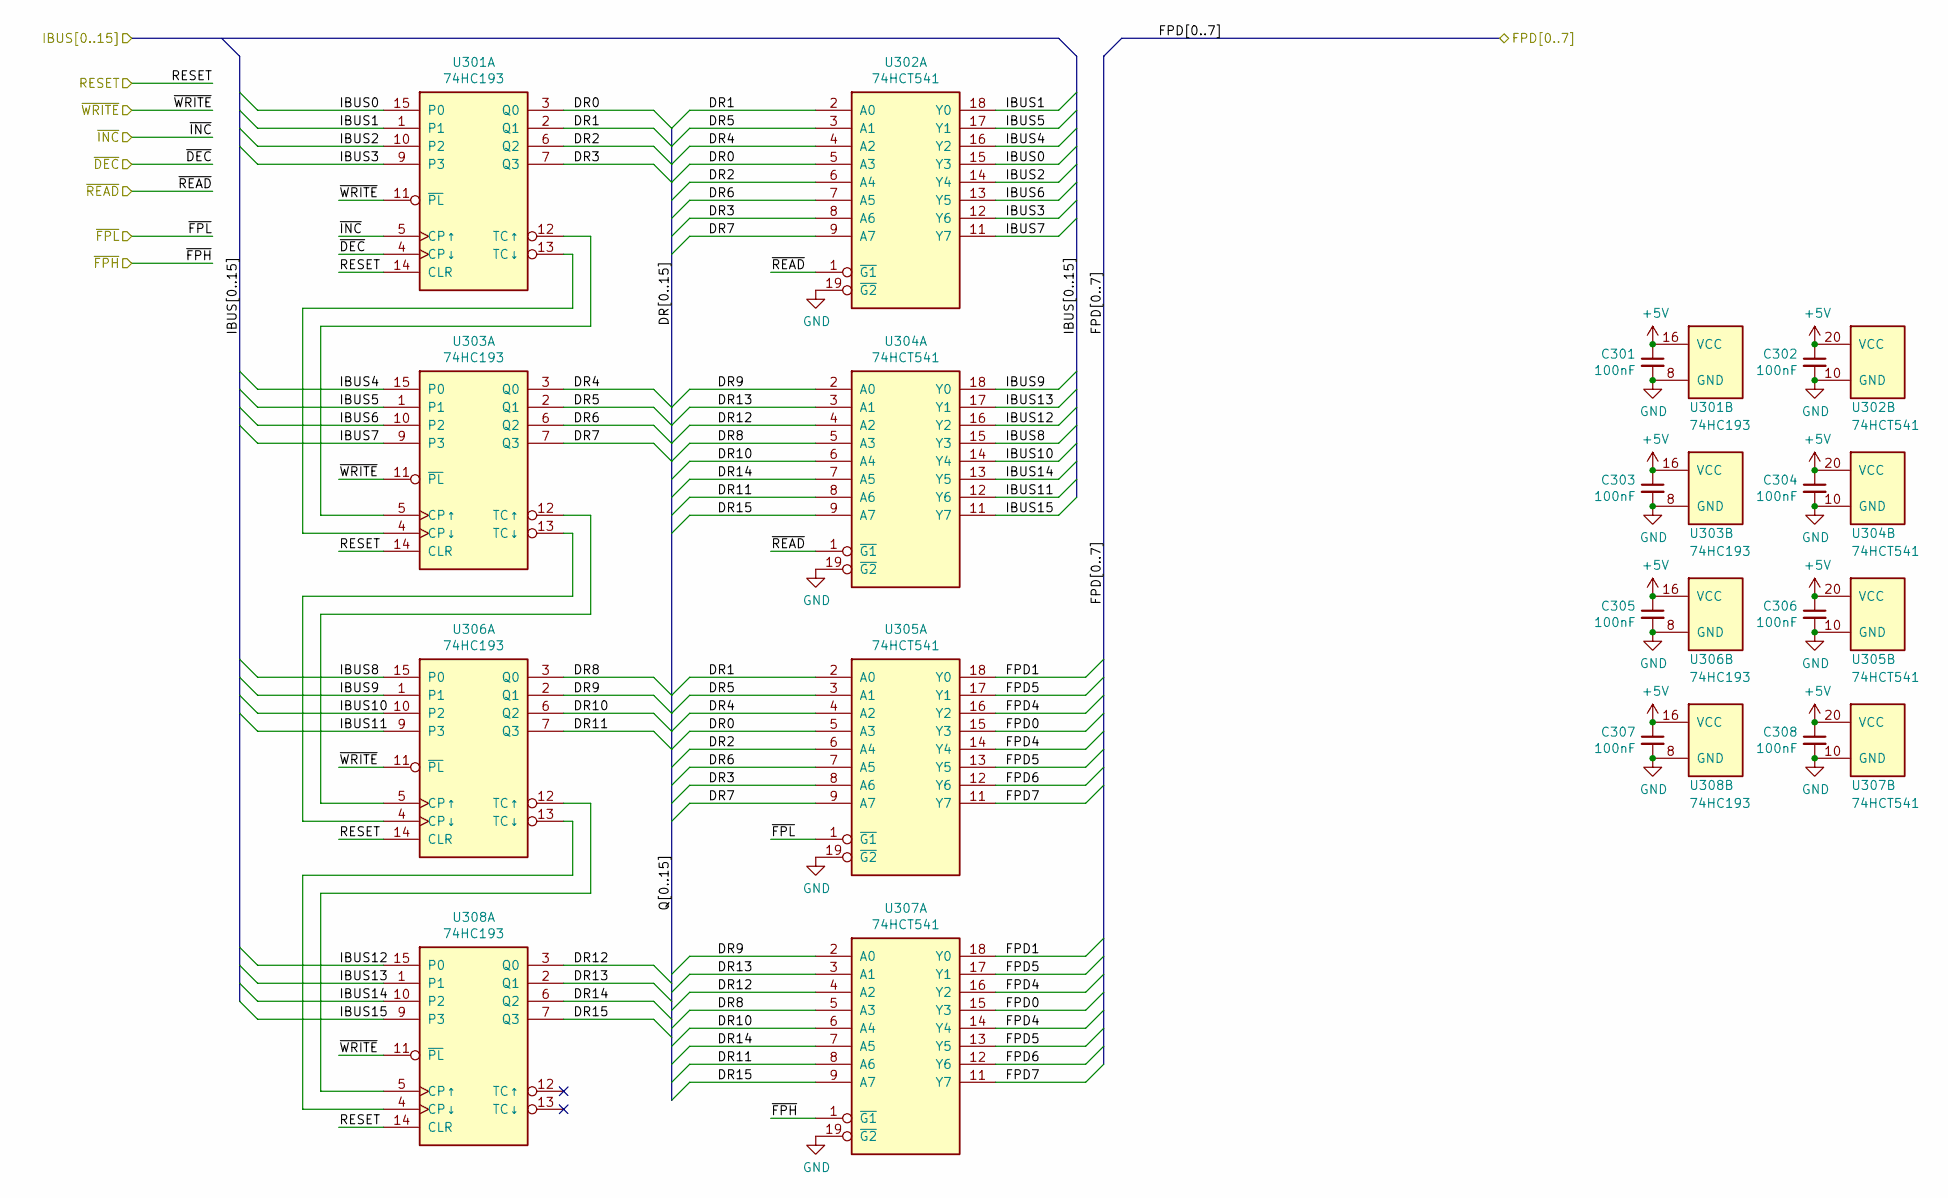
[picture p86: schematic cft-reg-dr-sp.sch, Data Register (DR)]

Parts:
C301, C302, C303, C304, C305, C306, C307, C308: 100nF; SMD_0805_2012Metric_Pad1.15x1.40mm_HandSolder
U301, U303, U306, U308: 74HC193; DIP-16_W7.62mm_Socket
U302, U304, U305, U307: 74HCT541; DIP-20_W7.62mm_Socket

Connections:
+5V: C301.1, C302.1, C303.1, C304.1, C305.1, C306.1, C307.1, C308.1, U301.16 (VCC), U302.20 (VCC), U303.16 (VCC), U304.20 (VCC), U305.20 (VCC), U306.16 (VCC), U307.20 (VCC), U308.16 (VCC); also elsewhere on the board
/Data Register/DR0: U301.3 (Q0), U302.5 (A3), U305.5 (A3)
/Data Register/DR1: U301.2 (Q1), U302.2 (A0), U305.2 (A0)
/Data Register/DR2: U301.6 (Q2), U302.6 (A4), U305.6 (A4)
/Data Register/DR3: U301.7 (Q3), U302.8 (A6), U305.8 (A6)
/Data Register/DR4: U302.4 (A2), U303.3 (Q0), U305.4 (A2)
/Data Register/DR5: U302.3 (A1), U303.2 (Q1), U305.3 (A1)
/Data Register/DR6: U302.7 (A5), U303.6 (Q2), U305.7 (A5)
/Data Register/DR7: U302.9 (A7), U303.7 (Q3), U305.9 (A7)
/Data Register/DR8: U304.5 (A3), U306.3 (Q0), U307.5 (A3)
/Data Register/DR9: U304.2 (A0), U306.2 (Q1), U307.2 (A0)
/Data Register/DR10: U304.6 (A4), U306.6 (Q2), U307.6 (A4)
/Data Register/DR11: U304.8 (A6), U306.7 (Q3), U307.8 (A6)
/Data Register/DR12: U304.4 (A2), U307.4 (A2), U308.3 (Q0)
/Data Register/DR13: U304.3 (A1), U307.3 (A1), U308.2 (Q1)
/Data Register/DR14: U304.7 (A5), U307.7 (A5), U308.6 (Q2)
/Data Register/DR15: U304.9 (A7), U307.9 (A7), U308.7 (Q3)
/FPD0: U305.15 (Y3), U307.15 (Y3); also elsewhere on the board
/FPD1: U305.18 (Y0), U307.18 (Y0); also elsewhere on the board
/FPD4: U305.14 (Y4), U305.16 (Y2), U307.14 (Y4), U307.16 (Y2); also elsewhere on the board
/FPD5: U305.13 (Y5), U305.17 (Y1), U307.13 (Y5), U307.17 (Y1); also elsewhere on the board
/FPD6: U305.12 (Y6), U307.12 (Y6); also elsewhere on the board
/FPD7: U305.11 (Y7), U307.11 (Y7); also elsewhere on the board
/IBUS0: U301.15 (P0), U302.15 (Y3); also elsewhere on the board
/IBUS1: U301.1, U302.18 (Y0); also elsewhere on the board
/IBUS2: U301.10 (P2), U302.14 (Y4); also elsewhere on the board
/IBUS3: U301.9 (P3), U302.12 (Y6); also elsewhere on the board
/IBUS4: U302.16 (Y2), U303.15 (P0); also elsewhere on the board
/IBUS5: U302.17 (Y1), U303.1; also elsewhere on the board
/IBUS6: U302.13 (Y5), U303.10 (P2); also elsewhere on the board
/IBUS7: U302.11 (Y7), U303.9 (P3); also elsewhere on the board
/IBUS8: U304.15 (Y3), U306.15 (P0); also elsewhere on the board
/IBUS9: U304.18 (Y0), U306.1; also elsewhere on the board
/IBUS10: U304.14 (Y4), U306.10 (P2); also elsewhere on the board
/IBUS11: U304.12 (Y6), U306.9 (P3); also elsewhere on the board
/IBUS12: U304.16 (Y2), U308.15 (P0); also elsewhere on the board
/IBUS13: U304.17 (Y1), U308.1; also elsewhere on the board
/IBUS14: U304.13 (Y5), U308.10 (P2); also elsewhere on the board
/IBUS15: U304.11 (Y7), U308.9 (P3); also elsewhere on the board
/RESET: U301.14 (CLR), U303.14 (CLR), U306.14 (CLR), U308.14 (CLR); also elsewhere on the board
/~ACTION-DECDR: U301.4 (CP↓); also elsewhere on the board
/~ACTION-INCDR: U301.5 (CP↑); also elsewhere on the board
/~FPDRH: U307.1 (~G1)
/~FPDRL: U305.1 (~G1)
/~READ-DR: U302.1 (~G1), U304.1 (~G1)
/~WRITE-DR: U301.11 (~PL), U303.11 (~PL), U306.11 (~PL), U308.11 (~PL)
GND: C301.2, C302.2, C303.2, C304.2, C305.2, C306.2, C307.2, C308.2, U301.8 (GND), U302.10 (GND), U302.19 (~G2), U303.8 (GND), U304.10 (GND), U304.19 (~G2), U305.10 (GND), U305.19 (~G2), U306.8 (GND), U307.10 (GND), U307.19 (~G2), U308.8 (GND); also elsewhere on the board
unnamed: U301.12 (TC↑), U303.5 (CP↑)
unnamed: U301.13 (TC↓), U303.4 (CP↓)
unnamed: U303.12 (TC↑), U306.5 (CP↑)
unnamed: U303.13 (TC↓), U306.4 (CP↓)
unnamed: U306.12 (TC↑), U308.5 (CP↑)
unnamed: U306.13 (TC↓), U308.4 (CP↓)

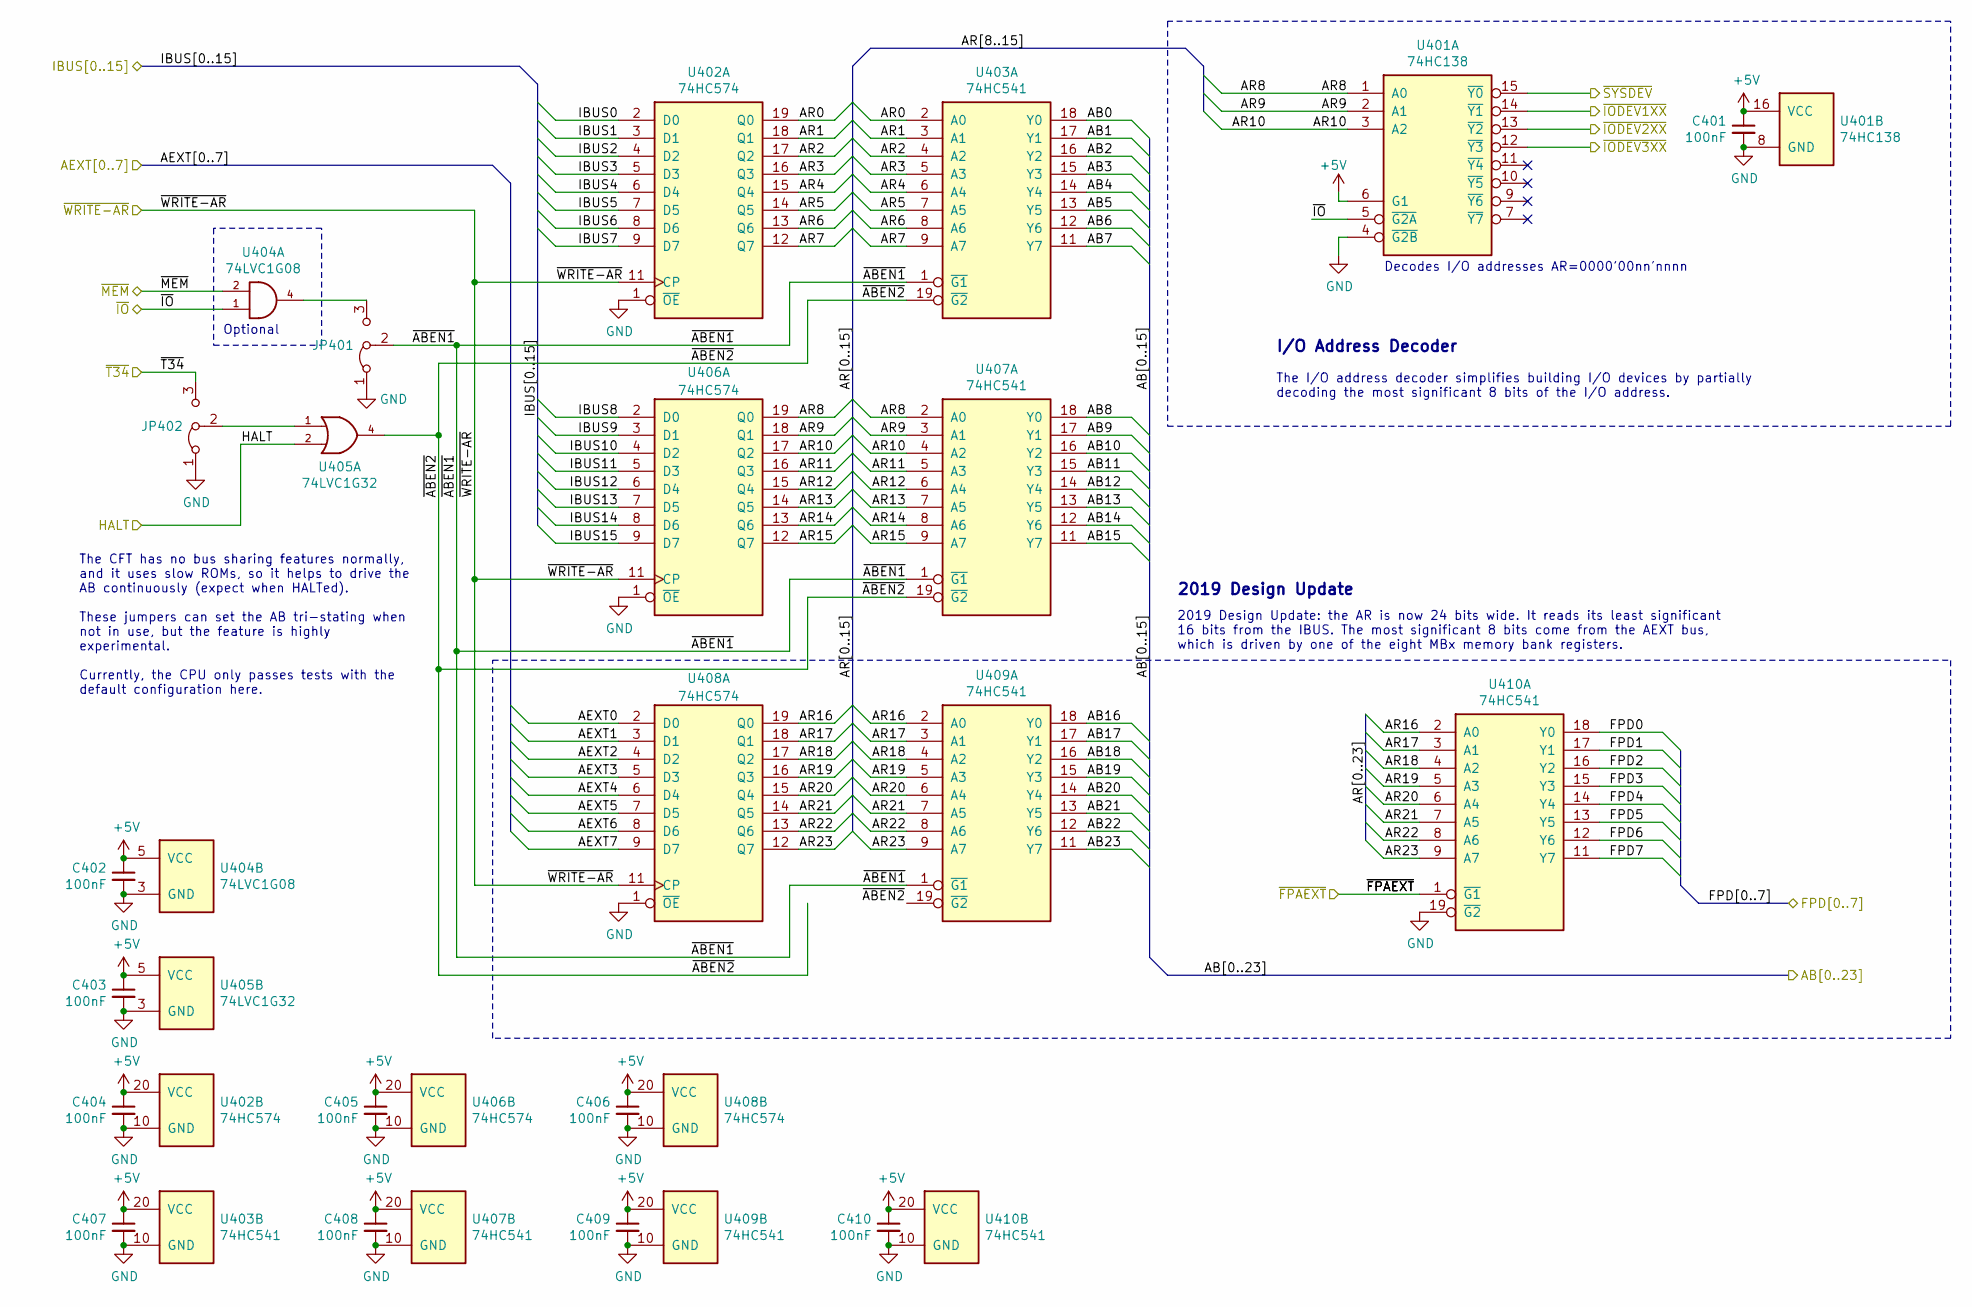
[picture p87: schematic cft_ar.sch, 24-bit Address Register (AR)]

Parts:
C401, C402, C403, C404, C405, C406, C407, C408, C409, C410: 100nF; C_SMD_0805_2012Metric_Pad1.15x1.40mm_HandSolder
JP401, JP402: Jumper_3_Bridged12; SolderJumper-3_P1.3mm_Bridged12_RoundedPad1.0x1.5mm
U401: 74HC138; DIP-16_W7.62mm_Socket
U402, U406, U408: 74HC574; DIP-20_W7.62mm_Socket
U403, U407, U409, U410: 74HC541; DIP-20_W7.62mm_Socket
U404: 74LVC1G08; SOT-23-5_HandSoldering
U405: 74LVC1G32; SOT-23-5_HandSoldering

Connections:
+5V: C401.1, C402.1, C403.1, C404.1, C405.1, C406.1, C407.1, C408.1, C409.1, C410.1, U401.6 (G1), U401.16 (VCC), U402.20 (VCC), U403.20 (VCC), U404.5 (VCC), U405.5 (VCC), U406.20 (VCC), U407.20 (VCC), U408.20 (VCC), U409.20 (VCC), U410.20 (VCC); also elsewhere on the board
/AB0: U403.18 (Y0); also elsewhere on the board
/AB1: U403.17 (Y1); also elsewhere on the board
/AB2: U403.16 (Y2); also elsewhere on the board
/AB3: U403.15 (Y3); also elsewhere on the board
/AB4: U403.14 (Y4); also elsewhere on the board
/AB5: U403.13 (Y5); also elsewhere on the board
/AB6: U403.12 (Y6); also elsewhere on the board
/AB7: U403.11 (Y7); also elsewhere on the board
/AB8: U407.18 (Y0); also elsewhere on the board
/AB9: U407.17 (Y1); also elsewhere on the board
/AB10: U407.16 (Y2); also elsewhere on the board
/AB11: U407.15 (Y3); also elsewhere on the board
/AB12: U407.14 (Y4); also elsewhere on the board
/AB13: U407.13 (Y5); also elsewhere on the board
/AB14: U407.12 (Y6); also elsewhere on the board
/AB15: U407.11 (Y7); also elsewhere on the board
/AB16: U409.18 (Y0); also elsewhere on the board
/AB17: U409.17 (Y1); also elsewhere on the board
/AB18: U409.16 (Y2); also elsewhere on the board
/AB19: U409.15 (Y3); also elsewhere on the board
/AB20: U409.14 (Y4); also elsewhere on the board
/AB21: U409.13 (Y5); also elsewhere on the board
/AB22: U409.12 (Y6); also elsewhere on the board
/AB23: U409.11 (Y7); also elsewhere on the board
/Address Register (AR)/AEXT0: U408.2 (D0); also elsewhere on the board
/Address Register (AR)/AEXT1: U408.3 (D1); also elsewhere on the board
/Address Register (AR)/AEXT2: U408.4 (D2); also elsewhere on the board
/Address Register (AR)/AEXT3: U408.5 (D3); also elsewhere on the board
/Address Register (AR)/AEXT4: U408.6 (D4); also elsewhere on the board
/Address Register (AR)/AEXT5: U408.7 (D5); also elsewhere on the board
/Address Register (AR)/AEXT6: U408.8 (D6); also elsewhere on the board
/Address Register (AR)/AEXT7: U408.9 (D7); also elsewhere on the board
/Address Register (AR)/AR0: U402.19 (Q0), U403.2 (A0)
/Address Register (AR)/AR1: U402.18 (Q1), U403.3 (A1)
/Address Register (AR)/AR2: U402.17 (Q2), U403.4 (A2)
/Address Register (AR)/AR3: U402.16 (Q3), U403.5 (A3)
/Address Register (AR)/AR4: U402.15 (Q4), U403.6 (A4)
/Address Register (AR)/AR5: U402.14 (Q5), U403.7 (A5)
/Address Register (AR)/AR6: U402.13 (Q6), U403.8 (A6)
/Address Register (AR)/AR7: U402.12 (Q7), U403.9 (A7)
/Address Register (AR)/AR8: U401.1 (A0), U406.19 (Q0), U407.2 (A0)
/Address Register (AR)/AR9: U401.2 (A1), U406.18 (Q1), U407.3 (A1)
/Address Register (AR)/AR10: U401.3 (A2), U406.17 (Q2), U407.4 (A2)
/Address Register (AR)/AR11: U406.16 (Q3), U407.5 (A3)
/Address Register (AR)/AR12: U406.15 (Q4), U407.6 (A4)
/Address Register (AR)/AR13: U406.14 (Q5), U407.7 (A5)
/Address Register (AR)/AR14: U406.13 (Q6), U407.8 (A6)
/Address Register (AR)/AR15: U406.12 (Q7), U407.9 (A7)
/Address Register (AR)/AR16: U408.19 (Q0), U409.2 (A0), U410.2 (A0)
/Address Register (AR)/AR17: U408.18 (Q1), U409.3 (A1), U410.3 (A1)
/Address Register (AR)/AR18: U408.17 (Q2), U409.4 (A2), U410.4 (A2)
/Address Register (AR)/AR19: U408.16 (Q3), U409.5 (A3), U410.5 (A3)
/Address Register (AR)/AR20: U408.15 (Q4), U409.6 (A4), U410.6 (A4)
/Address Register (AR)/AR21: U408.14 (Q5), U409.7 (A5), U410.7 (A5)
/Address Register (AR)/AR22: U408.13 (Q6), U409.8 (A6), U410.8 (A6)
/Address Register (AR)/AR23: U408.12 (Q7), U409.9 (A7), U410.9 (A7)
/Address Register (AR)/~ABEN1: JP401.2 (C), U403.1 (~G1), U407.1 (~G1), U409.1 (~G1)
/Address Register (AR)/~ABEN2: U403.19 (~G2), U405.4, U407.19 (~G2)
/FPD0: U410.18 (Y0); also elsewhere on the board
/FPD1: U410.17 (Y1); also elsewhere on the board
/FPD2: U410.16 (Y2); also elsewhere on the board
/FPD3: U410.15 (Y3); also elsewhere on the board
/FPD4: U410.14 (Y4); also elsewhere on the board
/FPD5: U410.13 (Y5); also elsewhere on the board
/FPD6: U410.12 (Y6); also elsewhere on the board
/FPD7: U410.11 (Y7); also elsewhere on the board
/IBUS0: U402.2 (D0); also elsewhere on the board
/IBUS1: U402.3 (D1); also elsewhere on the board
/IBUS2: U402.4 (D2); also elsewhere on the board
/IBUS3: U402.5 (D3); also elsewhere on the board
/IBUS4: U402.6 (D4); also elsewhere on the board
/IBUS5: U402.7 (D5); also elsewhere on the board
/IBUS6: U402.8 (D6); also elsewhere on the board
/IBUS7: U402.9 (D7); also elsewhere on the board
/IBUS8: U406.2 (D0); also elsewhere on the board
/IBUS9: U406.3 (D1); also elsewhere on the board
/IBUS10: U406.4 (D2); also elsewhere on the board
/IBUS11: U406.5 (D3); also elsewhere on the board
/IBUS12: U406.6 (D4); also elsewhere on the board
/IBUS13: U406.7 (D5); also elsewhere on the board
/IBUS14: U406.8 (D6); also elsewhere on the board
/IBUS15: U406.9 (D7); also elsewhere on the board
/~FPAEXT: U410.1 (~G1)
/~HALT: U405.2; also elsewhere on the board
/~IO: U401.5 (~G2A), U404.1; also elsewhere on the board
/~IODEV1XX: U401.14 (~Y1); also elsewhere on the board
/~IODEV2XX: U401.13 (~Y2); also elsewhere on the board
/~IODEV3XX: U401.12 (~Y3); also elsewhere on the board
/~MEM: U404.2; also elsewhere on the board
/~SYSDEV: U401.15 (~Y0); also elsewhere on the board
/~T34: JP402.3 (B); also elsewhere on the board
/~WAR: U402.11 (CP), U406.11 (CP), U408.11 (CP); also elsewhere on the board
GND: C401.2, C402.2, C403.2, C404.2, C405.2, C406.2, C407.2, C408.2, C409.2, C410.2, JP401.1 (A), JP402.1 (A), U401.4 (~G2B), U401.8 (GND), U402.1 (~OE), U402.10 (GND), U403.10 (GND), U404.3 (GND), U405.3 (GND), U406.1 (~OE), U406.10 (GND), U407.10 (GND), U408.1 (~OE), U408.10 (GND), U409.10 (GND), U410.10 (GND), U410.19 (~G2); also elsewhere on the board
unnamed: JP401.3 (B), U404.4
unnamed: JP402.2 (C), U405.1

Notes on the sheet:
2019 Design Update: the AR is now 24 bits wide. It reads its least significant 16 bits from the IBUS. The most significant 8 bits come from the AEXT bus, which is driven by one of the eight MBx memory bank registers.
2019 Design Update
I/O Address Decoder
Decodes I/O addresses AR=0000'00nn'nnnn
The I/O address decoder simplifies building I/O devices by partially decoding the most significant 8 bits of the I/O address.
The CFT has no bus sharing features normally, and it uses slow ROMs, so it helps to drive the AB continuously (expect when HALTed). These jumpers can set the AB tri-stating when not in use, but the feature is highly experimental. Currently, the CPU only passes tests with the default configuration h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
Optional

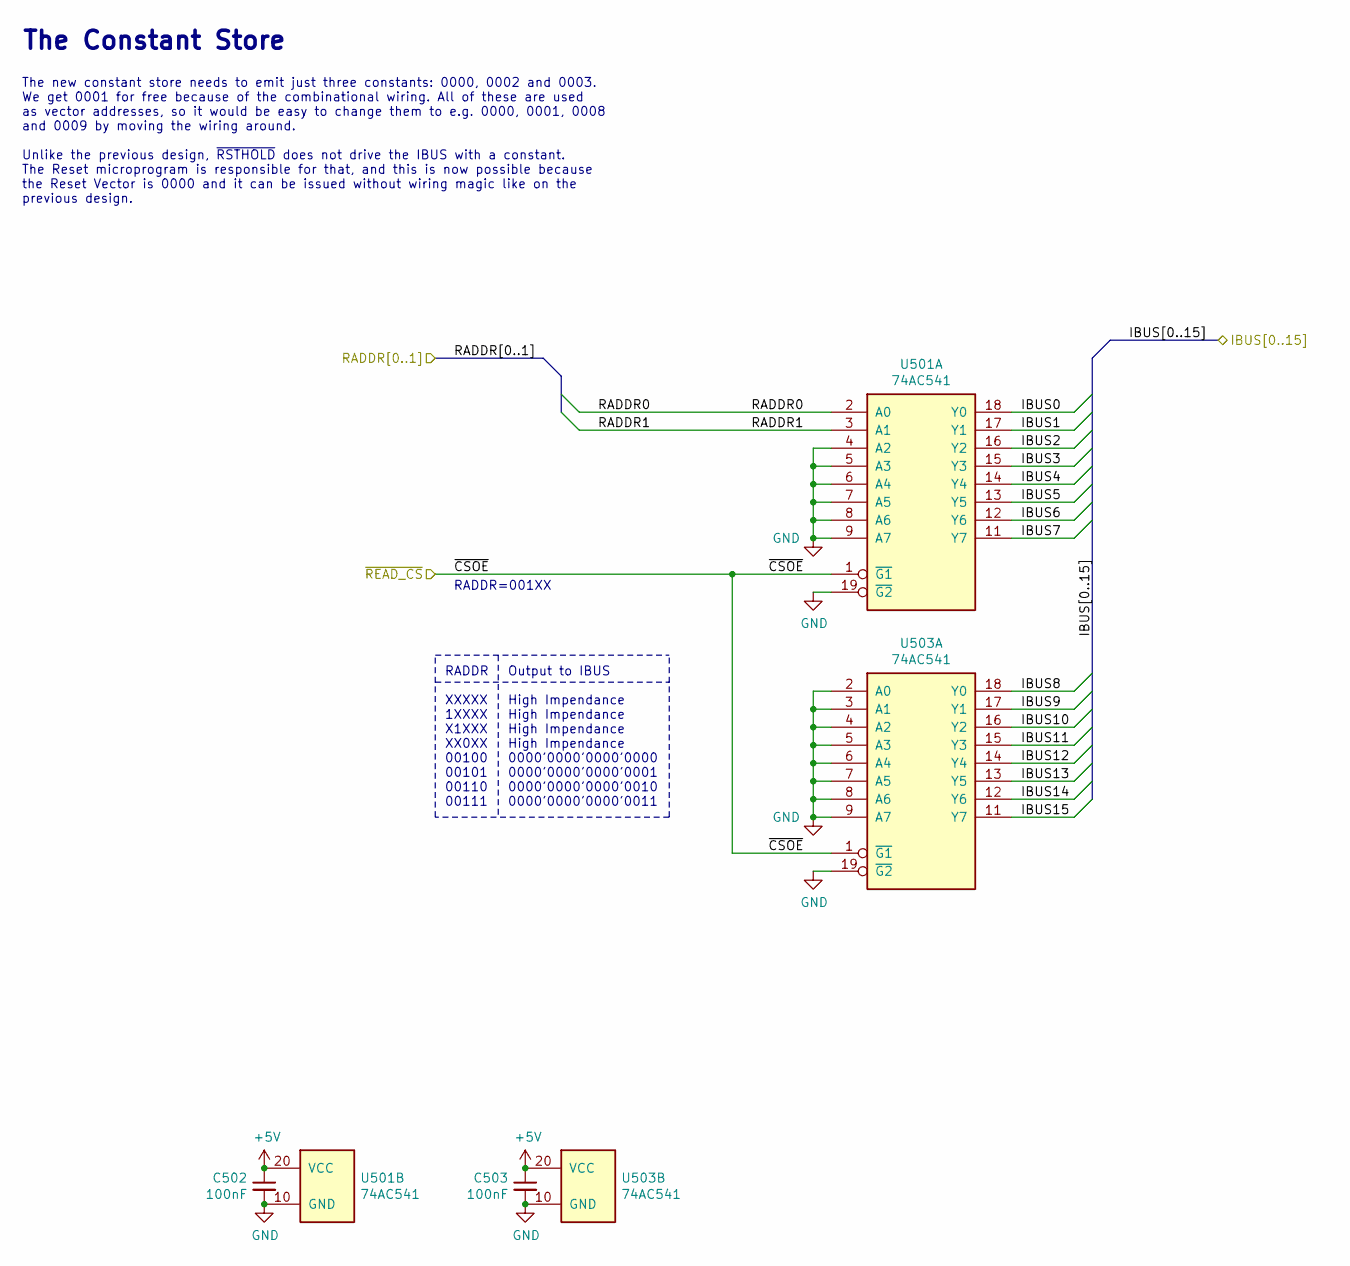
[picture p88: schematic cpu_cs.sch, Constant Store]

Parts:
C502, C503: 100nF; C_SMD_0805_2012Metric_Pad1.15x1.40mm_HandSolder
U501, U503: 74AC541; DIP-20_W7.62mm_Socket

Connections:
+5V: C502.1, C503.1, U501.20 (VCC), U503.20 (VCC); also elsewhere on the board
/IBUS0: U501.18 (Y0); also elsewhere on the board
/IBUS1: U501.17 (Y1); also elsewhere on the board
/IBUS2: U501.16 (Y2); also elsewhere on the board
/IBUS3: U501.15 (Y3); also elsewhere on the board
/IBUS4: U501.14 (Y4); also elsewhere on the board
/IBUS5: U501.13 (Y5); also elsewhere on the board
/IBUS6: U501.12 (Y6); also elsewhere on the board
/IBUS7: U501.11 (Y7); also elsewhere on the board
/IBUS8: U503.18 (Y0); also elsewhere on the board
/IBUS9: U503.17 (Y1); also elsewhere on the board
/IBUS10: U503.16 (Y2); also elsewhere on the board
/IBUS11: U503.15 (Y3); also elsewhere on the board
/IBUS12: U503.14 (Y4); also elsewhere on the board
/IBUS13: U503.13 (Y5); also elsewhere on the board
/IBUS14: U503.12 (Y6); also elsewhere on the board
/IBUS15: U503.11 (Y7); also elsewhere on the board
/RADDR0: U501.2 (A0); also elsewhere on the board
/RADDR1: U501.3 (A1); also elsewhere on the board
/~READ_CS: U501.1 (~G1), U503.1 (~G1); also elsewhere on the board
GND: C502.2, C503.2, U501.4 (A2), U501.5 (A3), U501.6 (A4), U501.7 (A5), U501.8 (A6), U501.9 (A7), U501.10 (GND), U501.19 (~G2), U503.2 (A0), U503.3 (A1), U503.4 (A2), U503.5 (A3), U503.6 (A4), U503.7 (A5), U503.8 (A6), U503.9 (A7), U503.10 (GND), U503.19 (~G2); also elsewhere on the board

Notes on the sheet:
RADDR=001XX
RADDR XXXXX 1XXXX X1XXX XX0XX 00100 00101 00110 00111
The new constant store needs to emit just three constants: 0000, 0002 and 0003. We get 0001 for free because of the combinational wiring. All of these are used as vector addresses, so it would be easy to change them to e.g. 0000, 0001, 0008 and 0009 by moving the wiring around. Unlike the previous 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
Output to IBUS High Impendance High Impendance High Impendance High Impendance 0000'0000'0000'0000 0000'0000'0000'0001 0000'0000'0000'0010 0000'0000'0000'0011
The Constant Store
