alexiosc/cft/kicad/cft/cft-board0/cft-board0.kicad_pcb

## KiCad design kicad/cft/cft-board0/cft-board0.kicad_pcb (continued)

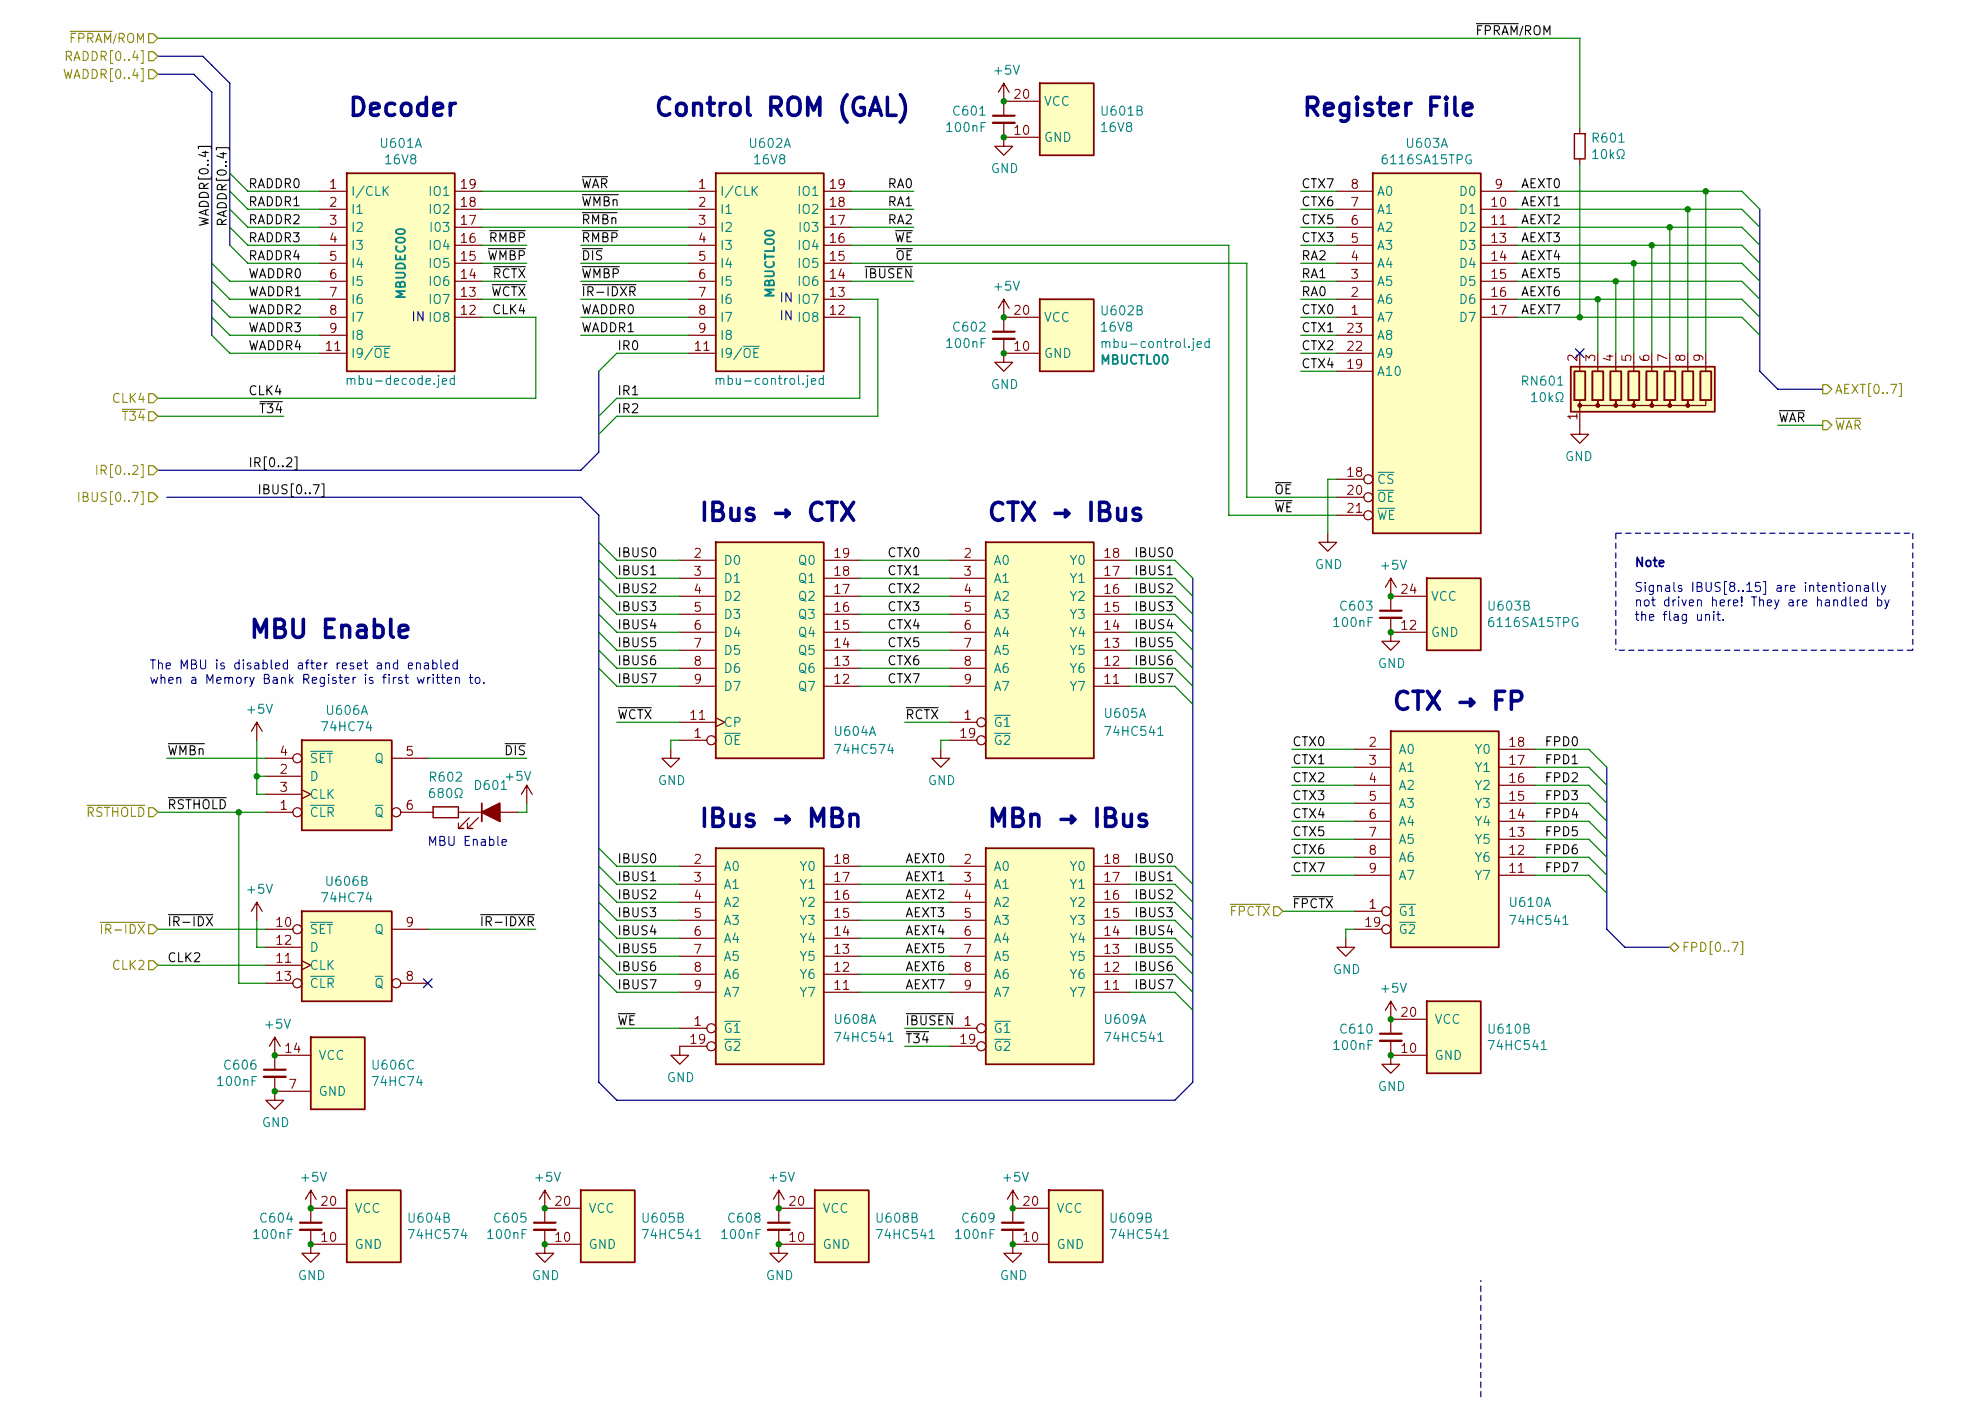
[picture p89: schematic mbu.sch, Memory Bank Unit]

Parts:
C601, C602, C603, C604, C605, C606, C608, C609, C610: 100nF; C_SMD_0805_2012Metric_Pad1.15x1.40mm_HandSolder
D601: LED_ALT; LED_0805_2012Metric_Pad1.15x1.40mm_HandSolder
R601: 10kΩ; R_SMD_0805_2012Metric_Pad1.15x1.40mm_HandSolder
R602: 680Ω; R_SMD_0805_2012Metric_Pad1.15x1.40mm_HandSolder
RN601: 10kΩ; R_Array_SIP9
U601, U602: 16V8; DIP-20_W7.62mm_Socket
U603: 6116SA15TPG; DIP-24_W7.62mm_Socket
U604: 74HC574; DIP-20_W7.62mm_Socket
U605, U608, U609, U610: 74HC541; DIP-20_W7.62mm_Socket
U606: 74HC74; DIP-14_W7.62mm_Socket

Connections:
+5V: C601.1, C602.1, C603.1, C604.1, C605.1, C606.1, C608.1, C609.1, C610.1, D601.2 (A), U601.20 (VCC), U602.20 (VCC), U603.24 (VCC), U604.20 (VCC), U605.20 (VCC), U606.2 (D), U606.3 (CLK), U606.12 (D), U606.14 (VCC), U608.20 (VCC), U609.20 (VCC), U610.20 (VCC); also elsewhere on the board
/Address Register (AR)/AEXT0: RN601.9 (R8), U603.9 (D0), U608.18 (Y0), U609.2 (A0); also elsewhere on the board
/Address Register (AR)/AEXT1: RN601.8 (R7), U603.10 (D1), U608.17 (Y1), U609.3 (A1); also elsewhere on the board
/Address Register (AR)/AEXT2: RN601.7 (R6), U603.11 (D2), U608.16 (Y2), U609.4 (A2); also elsewhere on the board
/Address Register (AR)/AEXT3: RN601.6 (R5), U603.13 (D3), U608.15 (Y3), U609.5 (A3); also elsewhere on the board
/Address Register (AR)/AEXT4: RN601.5 (R4), U603.14 (D4), U608.14 (Y4), U609.6 (A4); also elsewhere on the board
/Address Register (AR)/AEXT5: RN601.4 (R3), U603.15 (D5), U608.13 (Y5), U609.7 (A5); also elsewhere on the board
/Address Register (AR)/AEXT6: RN601.3 (R2), U603.16 (D6), U608.12 (Y6), U609.8 (A6); also elsewhere on the board
/Address Register (AR)/AEXT7: R601.2, U603.17 (D7), U608.11 (Y7), U609.9 (A7); also elsewhere on the board
/CLK2: U606.11 (CLK); also elsewhere on the board
/CLK3: U601.12 (IO8); also elsewhere on the board
/FPD0: U610.18 (Y0); also elsewhere on the board
/FPD1: U610.17 (Y1); also elsewhere on the board
/FPD2: U610.16 (Y2); also elsewhere on the board
/FPD3: U610.15 (Y3); also elsewhere on the board
/FPD4: U610.14 (Y4); also elsewhere on the board
/FPD5: U610.13 (Y5); also elsewhere on the board
/FPD6: U610.12 (Y6); also elsewhere on the board
/FPD7: U610.11 (Y7); also elsewhere on the board
/IBUS0: U604.2 (D0), U605.18 (Y0), U608.2 (A0), U609.18 (Y0); also elsewhere on the board
/IBUS1: U604.3 (D1), U605.17 (Y1), U608.3 (A1), U609.17 (Y1); also elsewhere on the board
/IBUS2: U604.4 (D2), U605.16 (Y2), U608.4 (A2), U609.16 (Y2); also elsewhere on the board
/IBUS3: U604.5 (D3), U605.15 (Y3), U608.5 (A3), U609.15 (Y3); also elsewhere on the board
/IBUS4: U604.6 (D4), U605.14 (Y4), U608.6 (A4), U609.14 (Y4); also elsewhere on the board
/IBUS5: U604.7 (D5), U605.13 (Y5), U608.7 (A5), U609.13 (Y5); also elsewhere on the board
/IBUS6: U604.8 (D6), U605.12 (Y6), U608.8 (A6), U609.12 (Y6); also elsewhere on the board
/IBUS7: U604.9 (D7), U605.11 (Y7), U608.9 (A7), U609.11 (Y7); also elsewhere on the board
/IR0: U602.11 (I9/~OE~); also elsewhere on the board
/IR1: U602.12 (IO8); also elsewhere on the board
/IR2: U602.13 (IO7); also elsewhere on the board
/Memory Bank Unit (MBU)/CTX0: U603.1 (A7), U604.19 (Q0), U605.2 (A0), U610.2 (A0)
/Memory Bank Unit (MBU)/CTX1: U603.23 (A8), U604.18 (Q1), U605.3 (A1), U610.3 (A1)
/Memory Bank Unit (MBU)/CTX2: U603.22 (A9), U604.17 (Q2), U605.4 (A2), U610.4 (A2)
/Memory Bank Unit (MBU)/CTX3: U603.5 (A3), U604.16 (Q3), U605.5 (A3), U610.5 (A3)
/Memory Bank Unit (MBU)/CTX4: U603.19 (A10), U604.15 (Q4), U605.6 (A4), U610.6 (A4)
/Memory Bank Unit (MBU)/CTX5: U603.6 (A2), U604.14 (Q5), U605.7 (A5), U610.7 (A5)
/Memory Bank Unit (MBU)/CTX6: U603.7 (A1), U604.13 (Q6), U605.8 (A6), U610.8 (A6)
/Memory Bank Unit (MBU)/CTX7: U603.8 (A0), U604.12 (Q7), U605.9 (A7), U610.9 (A7)
/Memory Bank Unit (MBU)/RA0: U602.19 (IO1), U603.2 (A6)
/Memory Bank Unit (MBU)/RA1: U602.18 (IO2), U603.3 (A5)
/Memory Bank Unit (MBU)/RA2: U602.17 (I03), U603.4 (A4)
/Memory Bank Unit (MBU)/~DIS: U602.5 (I4), U606.5 (Q)
/Memory Bank Unit (MBU)/~IBUSEN: U602.14 (IO6), U609.1 (~G1)
/Memory Bank Unit (MBU)/~IR-IDXR: U602.7 (I6), U606.9 (Q)
/Memory Bank Unit (MBU)/~OE: U602.15 (IO5), U603.20 (~OE)
/Memory Bank Unit (MBU)/~RCTX: U601.14 (IO6), U605.1 (~G1)
/Memory Bank Unit (MBU)/~RMBP: U601.16 (IO4), U602.4 (I3)
/Memory Bank Unit (MBU)/~RMBn: U601.17 (I03), U602.3 (I2)
/Memory Bank Unit (MBU)/~WCTX: U601.13 (IO7), U604.11 (CP)
/Memory Bank Unit (MBU)/~WE: U602.16 (IO4), U603.21 (~WE), U608.1 (~G1)
/Memory Bank Unit (MBU)/~WMBP: U601.15 (IO5), U602.6 (I5)
/Memory Bank Unit (MBU)/~WMBn: U601.18 (IO2), U602.2 (I1), U606.4 (~SET)
/RADDR0: U601.1 (I/CLK); also elsewhere on the board
/RADDR1: U601.2 (I1); also elsewhere on the board
/RADDR2: U601.3 (I2); also elsewhere on the board
/RADDR3: U601.4 (I3); also elsewhere on the board
/RADDR4: U601.5 (I4); also elsewhere on the board
/WADDR0: U601.6 (I5), U602.8 (I7); also elsewhere on the board
/WADDR1: U601.7 (I6), U602.9 (I8); also elsewhere on the board
/WADDR2: U601.8 (I7); also elsewhere on the board
/WADDR3: U601.9 (I8); also elsewhere on the board
/WADDR4: U601.11 (I9/~OE~); also elsewhere on the board
/~FPCTX: U610.1 (~G1)
/~FPRAM~∕ROM: R601.1
/~IR-IDX: U606.10 (~SET); also elsewhere on the board
/~RSTHOLD: U606.1 (~CLR), U606.13 (~CLR); also elsewhere on the board
/~T34: U609.19 (~G2); also elsewhere on the board
/~WAR: U601.19 (IO1), U602.1 (I/CLK); also elsewhere on the board
GND: C601.2, C602.2, C603.2, C604.2, C605.2, C606.2, C608.2, C609.2, C610.2, RN601.1 (common), U601.10 (GND), U602.10 (GND), U603.12 (GND), U603.18 (~CS), U604.1 (~OE), U604.10 (GND), U605.10 (GND), U605.19 (~G2), U606.7 (GND), U608.10 (GND), U608.19 (~G2), U609.10 (GND), U610.10 (GND), U610.19 (~G2); also elsewhere on the board
unnamed: D601.1 (K), R602.2
unnamed: R602.1, U606.6 (~Q)

Notes on the sheet:
Signals IBUS[8..15] are intentionally not driven here! They are handled by the flag unit.
Note
Control ROM (GAL)
CTX → IBus
IBus → CTX
Register File
Decoder
IBus → MBn
MBn → IBus
MBU Enable
The MBU is disabled after reset and enabled when a Memory Bank Register is first written to.
CTX → FP

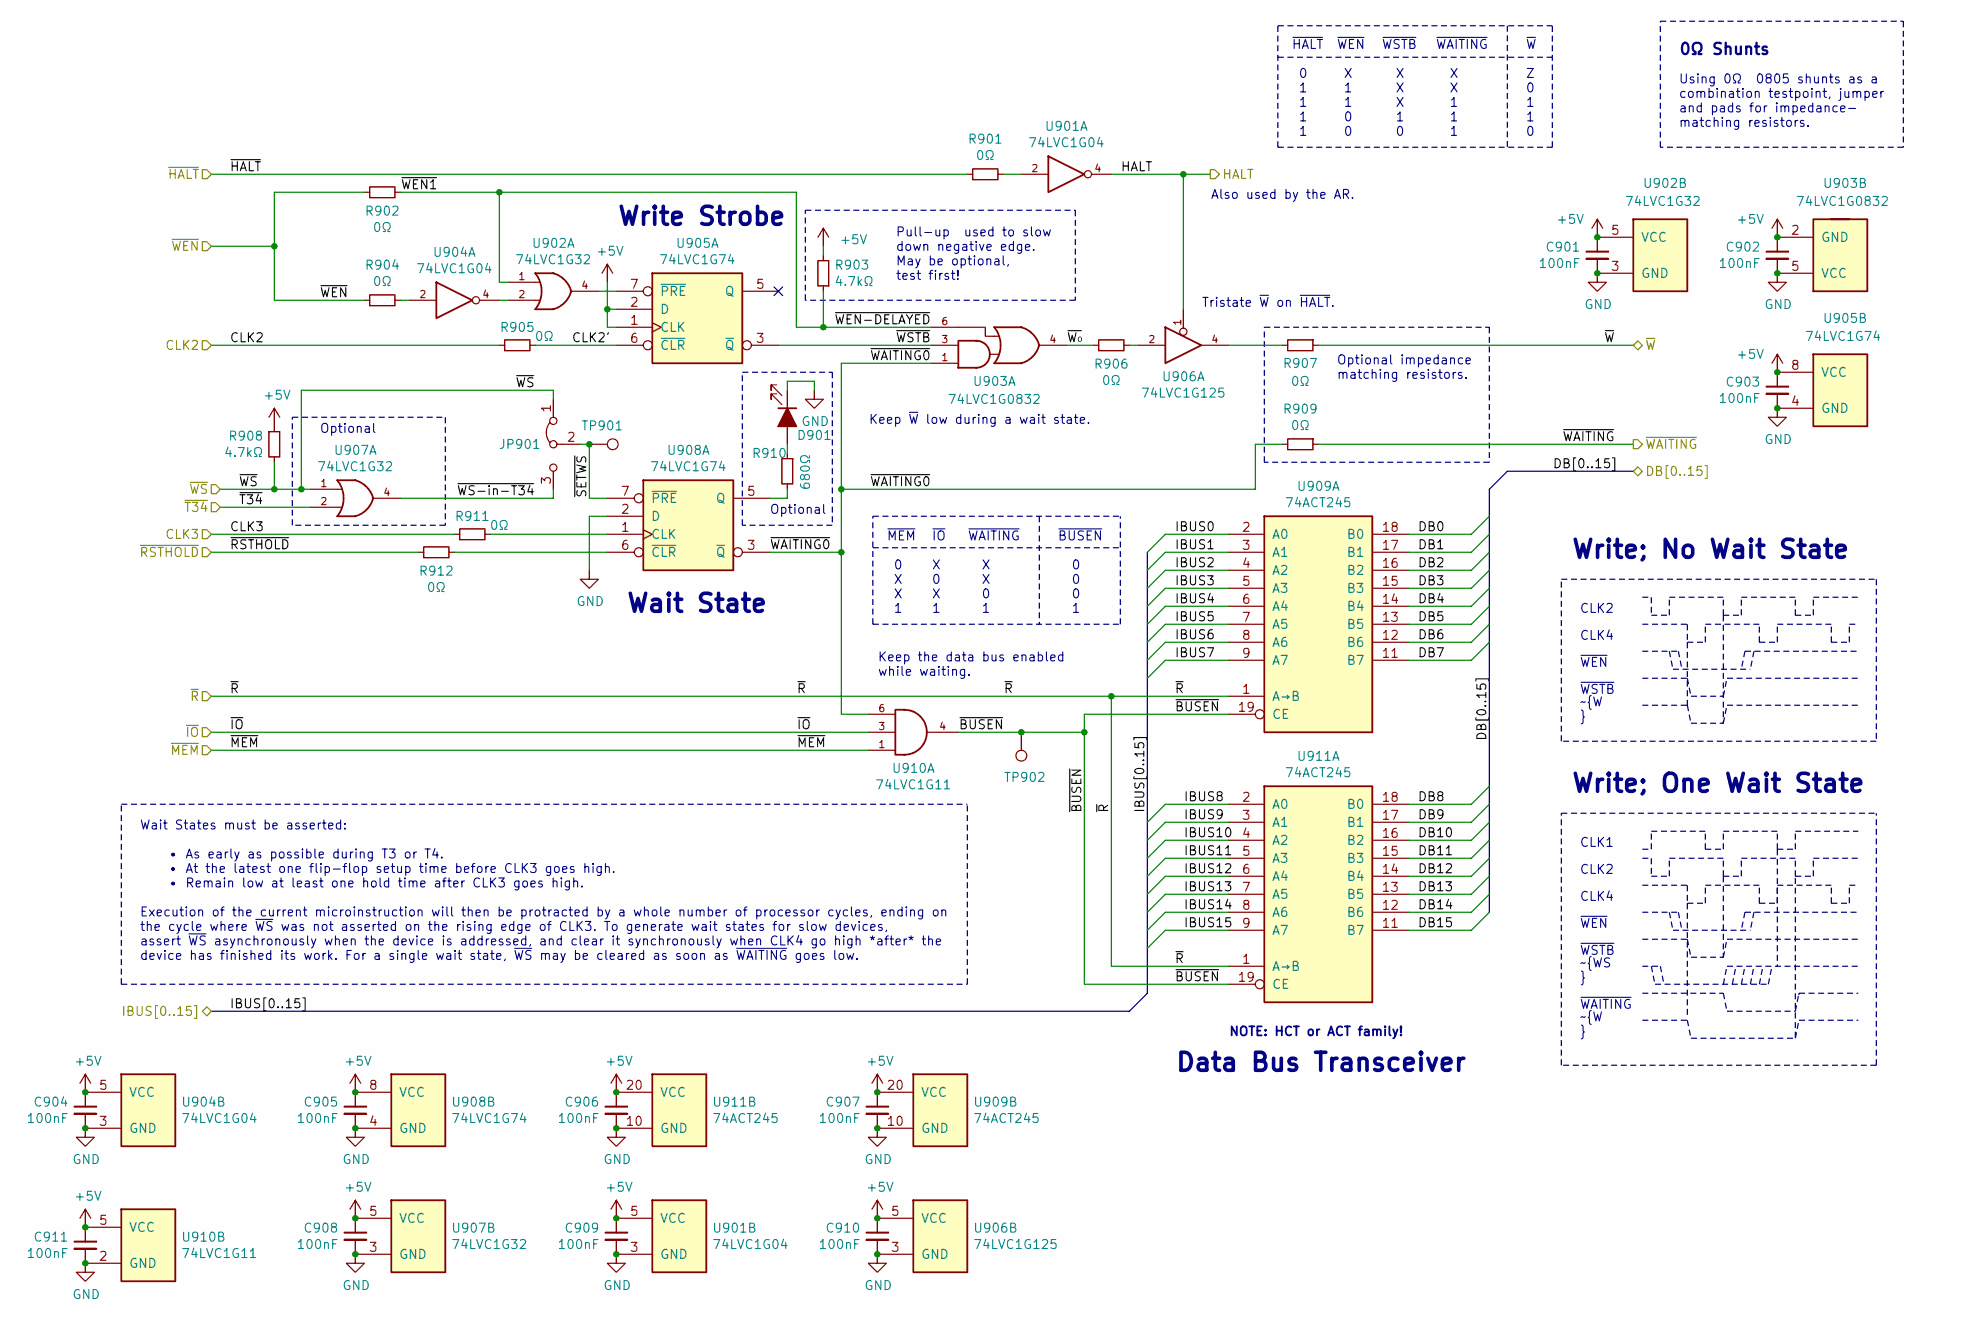
[picture p90: schematic cft_ws_busen.sch, Data Bus & Wait States]

Parts:
C901, C902, C903, C904, C905, C906, C907, C908, C909, C910, C911: 100nF; C_SMD_0805_2012Metric_Pad1.15x1.40mm_HandSolder
D901: LED_ALT; LED_0805_2012Metric_Pad1.15x1.40mm_HandSolder
JP901: Jumper_3_Bridged12; SolderJumper-3_P1.3mm_Bridged12_RoundedPad1.0x1.5mm
R901, R902, R904, R905, R906, R907, R909, R911, R912: 0Ω; R_SMD_0805_2012Metric_Pad1.15x1.40mm_HandSolder
R903, R908: 4.7kΩ; R_SMD_0805_2012Metric_Pad1.15x1.40mm_HandSolder
R910: 680Ω; R_SMD_0805_2012Metric_Pad1.15x1.40mm_HandSolder
TP901, TP902: TestPoint; TestPoint_Pad_1.0x1.0mm
U901, U904: 74LVC1G04; SOT-23-5_HandSoldering
U902, U907: 74LVC1G32; SOT-23-5_HandSoldering
U903: 74LVC1G0832; SOT-23-6_Handsoldering
U905, U908: 74LVC1G74; TSSOP-8_3x3mm_P0.65mm
U906: 74LVC1G125; SOT-23-5_HandSoldering
U909, U911: 74ACT245; DIP-20_W7.62mm_Socket
U910: 74LVC1G11; SOT-23-6_Handsoldering

Connections:
+5V: C901.1, C902.1, C903.1, C904.1, C905.1, C906.1, C907.1, C908.1, C909.1, C910.1, C911.1, R903.2, R908.1, U901.5 (VCC), U902.5 (VCC), U903.2 (GND), U904.5 (VCC), U905.1 (CLK), U905.2 (D), U905.8 (VCC), U906.5 (VCC), U907.5 (VCC), U908.8 (VCC), U909.20 (VCC), U910.5 (VCC), U911.20 (VCC); also elsewhere on the board
/CLK2: R905.1; also elsewhere on the board
/CLK3: R911.1; also elsewhere on the board
/DB0: U909.18 (B0); also elsewhere on the board
/DB1: U909.17 (B1); also elsewhere on the board
/DB2: U909.16 (B2); also elsewhere on the board
/DB3: U909.15 (B3); also elsewhere on the board
/DB4: U909.14 (B4); also elsewhere on the board
/DB5: U909.13 (B5); also elsewhere on the board
/DB6: U909.12 (B6); also elsewhere on the board
/DB7: U909.11 (B7); also elsewhere on the board
/DB8: U911.18 (B0); also elsewhere on the board
/DB9: U911.17 (B1); also elsewhere on the board
/DB10: U911.16 (B2); also elsewhere on the board
/DB11: U911.15 (B3); also elsewhere on the board
/DB12: U911.14 (B4); also elsewhere on the board
/DB13: U911.13 (B5); also elsewhere on the board
/DB14: U911.12 (B6); also elsewhere on the board
/DB15: U911.11 (B7); also elsewhere on the board
/HALT: U901.4, U906.1
/IBUS0: U909.2 (A0); also elsewhere on the board
/IBUS1: U909.3 (A1); also elsewhere on the board
/IBUS2: U909.4 (A2); also elsewhere on the board
/IBUS3: U909.5 (A3); also elsewhere on the board
/IBUS4: U909.6 (A4); also elsewhere on the board
/IBUS5: U909.7 (A5); also elsewhere on the board
/IBUS6: U909.8 (A6); also elsewhere on the board
/IBUS7: U909.9 (A7); also elsewhere on the board
/IBUS8: U911.2 (A0); also elsewhere on the board
/IBUS9: U911.3 (A1); also elsewhere on the board
/IBUS10: U911.4 (A2); also elsewhere on the board
/IBUS11: U911.5 (A3); also elsewhere on the board
/IBUS12: U911.6 (A4); also elsewhere on the board
/IBUS13: U911.7 (A5); also elsewhere on the board
/IBUS14: U911.8 (A6); also elsewhere on the board
/IBUS15: U911.9 (A7); also elsewhere on the board
/Wait States & Write Strobes/CLK2': R905.2, U905.6 (~CLR)
/Wait States & Write Strobes/~BUSEN: TP902.1, U909.19 (CE), U910.4, U911.19 (CE)
/Wait States & Write Strobes/~SETWS: JP901.2 (C), TP901.1, U908.7 (~PRE)
/Wait States & Write Strobes/~WAITING0: R909.2, U903.1, U908.3 (~Q), U910.6
/Wait States & Write Strobes/~WEN-DELAYED: R902.2, R903.1, U902.1, U903.6
/Wait States & Write Strobes/~WS-in-T34: JP901.3 (B), U907.4
/Wait States & Write Strobes/~WSTB: U903.3, U905.3 (~Q)
/Wait States & Write Strobes/~W₀: R906.1, U903.4
/~HALT: R901.1; also elsewhere on the board
/~IO: U910.3; also elsewhere on the board
/~MEM: U910.1; also elsewhere on the board
/~R: U909.1 (A→B), U911.1 (A→B); also elsewhere on the board
/~RSTHOLD: R912.1; also elsewhere on the board
/~T34: U907.2; also elsewhere on the board
/~W: R907.1; also elsewhere on the board
/~WAITING: R909.1; also elsewhere on the board
/~WEN: R902.1, R904.1; also elsewhere on the board
/~WS: JP901.1 (A), R908.2, U907.1; also elsewhere on the board
GND: C901.2, C902.2, C903.2, C904.2, C905.2, C906.2, C907.2, C908.2, C909.2, C910.2, C911.2, D901.1 (K), U901.3 (GND), U902.3 (GND), U903.5 (VCC), U904.3 (GND), U905.4 (GND), U906.3 (GND), U907.3 (GND), U908.2 (D), U908.4 (GND), U909.10 (GND), U910.2 (GND), U911.10 (GND); also elsewhere on the board
unnamed: D901.2 (A), R910.1
unnamed: R901.2, U901.2
unnamed: R904.2, U904.2
unnamed: R906.2, U906.2
unnamed: R907.2, U906.4
unnamed: R910.2, U908.5 (Q)
unnamed: R911.2, U908.1 (CLK)
unnamed: R912.2, U908.6 (~CLR)
unnamed: U902.2, U904.4
unnamed: U902.4, U905.7 (~PRE)

Notes on the sheet:
~WEN~ X 1 1 0 0
~HALT~ 0 1 1 1 1
~WAITING~ X X 1 1 1
~MEM~ 0 X X 1
~BUSEN~ 0 0 0 1
~WAITING~ X X 0 1
Data Bus Transceiver
Keep the data bus enabled while waiting.
~WSTB~ X X X 1 0
Wait State
NOTE: HCT or ACT family!
Optional impedance matching resistors.
Pull-up used to slow down negative edge. May be optional, test first!
Tristate ~W~ on ~HALT~.
~W~ Z 0 1 1 0
CLK2
~WSTB
~WEN
Write; No Wait State
Write; One Wait State
CLK4
~WAITING
CLK1
~WS
Wait States must be asserted: • As early as possible during T3 or T4. • At the latest one flip-flop setup time before CLK3 goes high. • Remain low at least one hold time after CLK3 goes high. Execution of the current microinstruction will then be protracted by a whole number of processor cycles, en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
~IO~ X 0 X 1
Optional
Write Strobe
Using 0Ω 0805 shunts as a combination testpoint, jumper and pads for impedance- matching resistors.
0Ω Shunts
Keep ~W~ low during a wait state.
Also used by the AR.

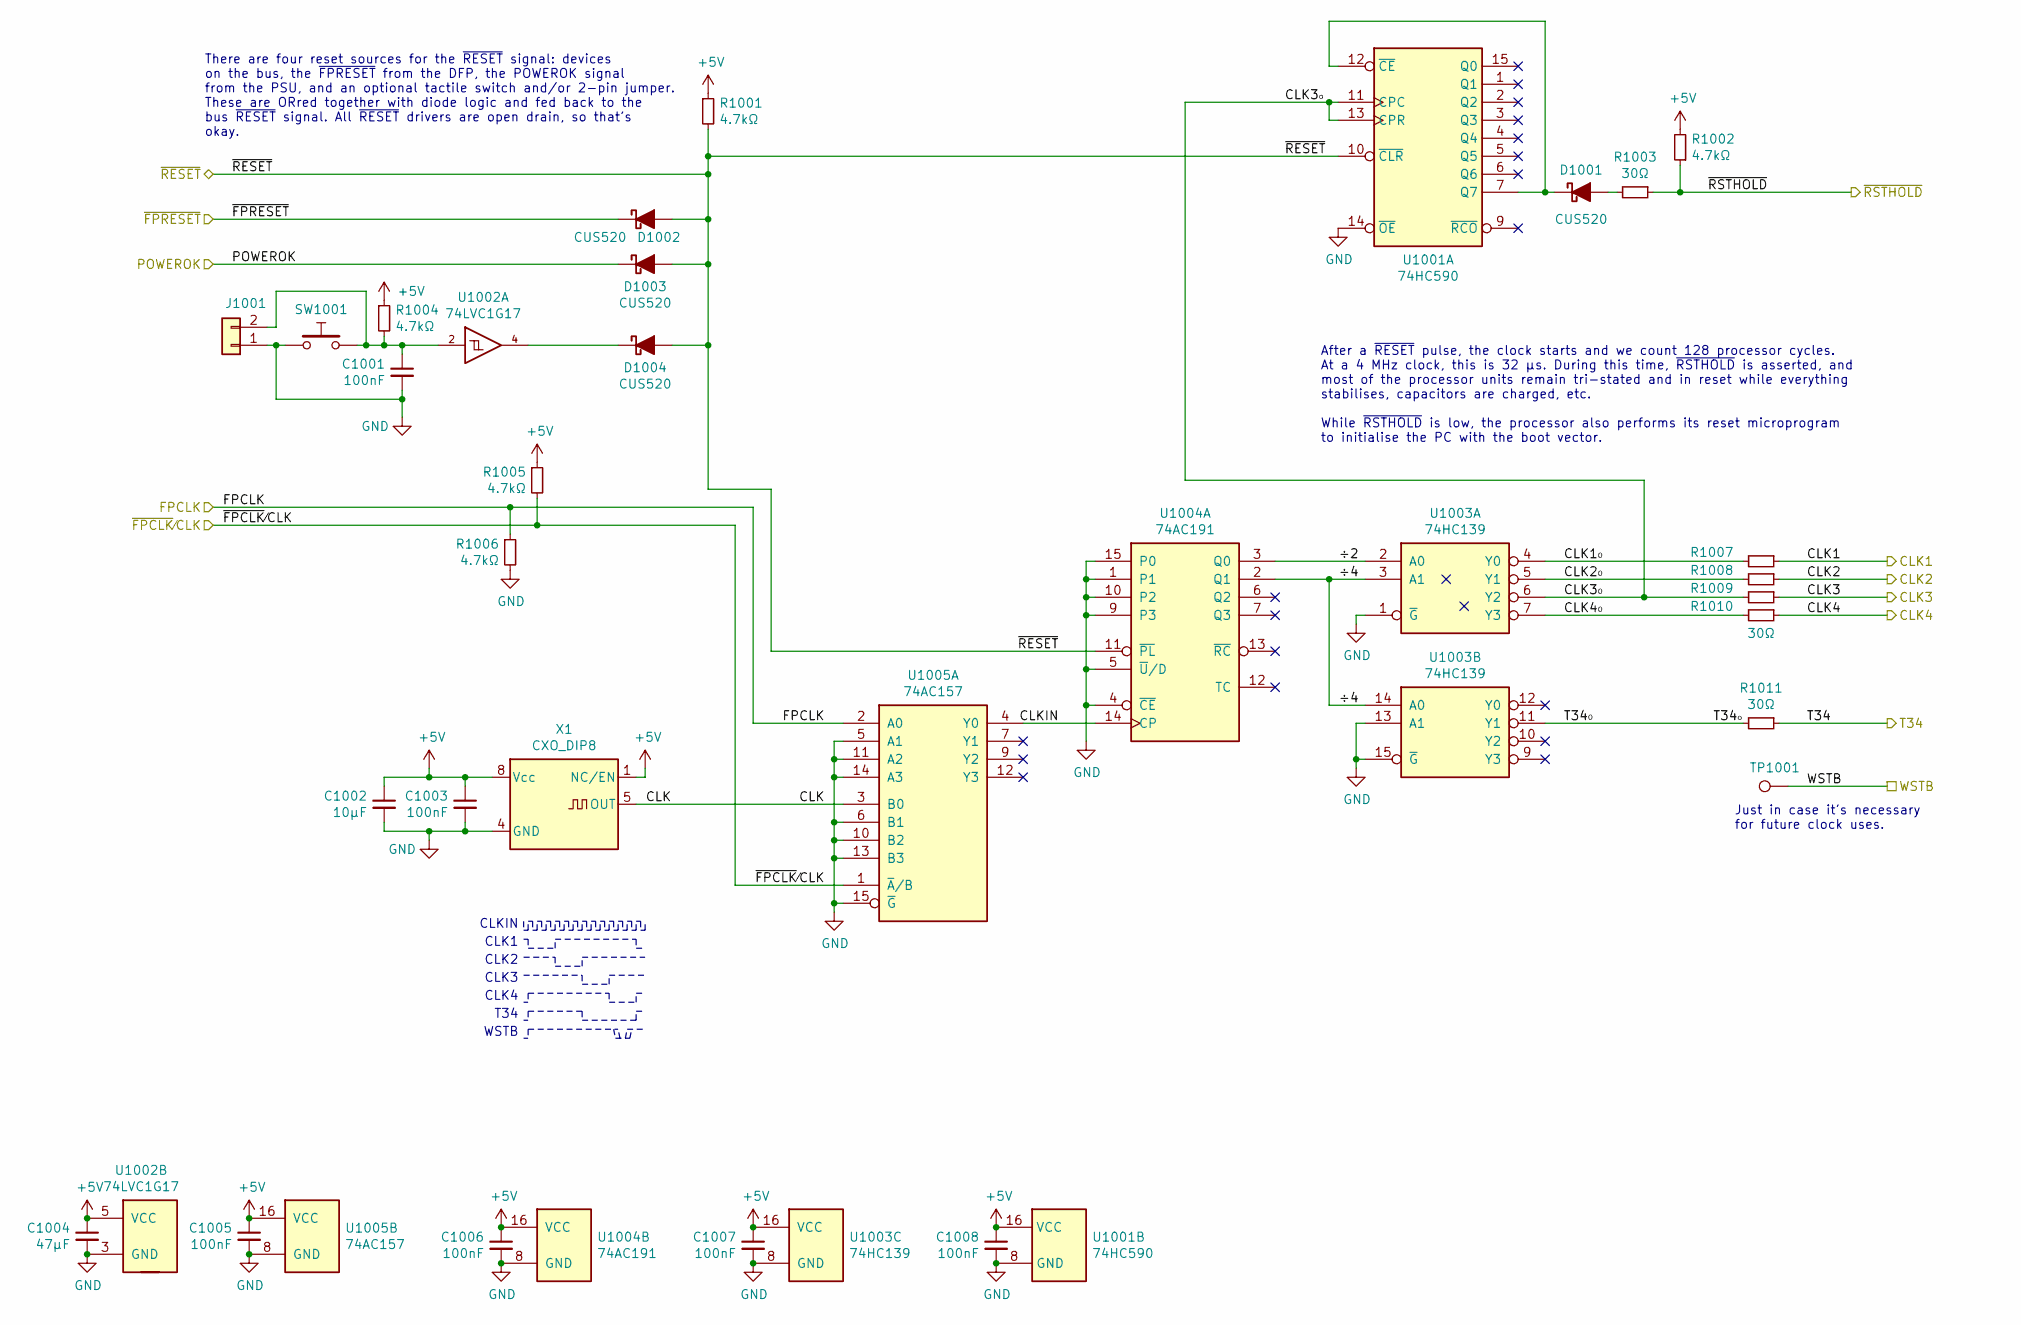
[picture p91: schematic cft_clk.sch, Clock Generator]

Parts:
C1001, C1003, C1005, C1006, C1007, C1008: 100nF; C_SMD_0805_2012Metric_Pad1.15x1.40mm_HandSolder
C1002: 10µF; C_SMD_0805_2012Metric_Pad1.15x1.40mm_HandSolder
C1004: 47µF; C_SMD_0805_2012Metric_Pad1.15x1.40mm_HandSolder
D1001, D1002, D1003, D1004: CUS520; SOD-323
J1001: Conn_01x02; PinHeader_1x02_P2.54mm_Horizontal
R1001, R1002, R1004, R1005, R1006: 4.7kΩ; R_SMD_0805_2012Metric_Pad1.15x1.40mm_HandSolder
R1003, R1007, R1008, R1009, R1010, R1011: 30Ω; R_SMD_0805_2012Metric_Pad1.15x1.40mm_HandSolder
SW1001: tactile_switch; SW_Tactile_SPST_Angled_PTS645Vx39-2LFS
TP1001: TestPoint; TestPoint_Pad_1.0x1.0mm
U1001: 74HC590; DIP-16_W7.62mm_Socket
U1002: 74LVC1G17; SOT-23-5_HandSoldering
U1003: 74HC139; DIP-16_W7.62mm_Socket
U1004: 74AC191; DIP-16_W7.62mm_Socket
U1005: 74AC157; DIP-16_W7.62mm_Socket
X1: CXO_DIP8; Oscillator_DIP-8-socket

Connections:
+5V: C1002.1, C1003.1, C1004.1, C1005.1, C1006.1, C1007.1, C1008.1, R1001.1, R1002.2, R1004.1, R1005.1, U1001.16 (VCC), U1002.5 (VCC), U1003.16 (VCC), U1004.16 (VCC), U1005.16 (VCC), X1.1 (NC/EN), X1.8 (Vcc); also elsewhere on the board
/CLK1: R1007.1; also elsewhere on the board
/CLK2: R1008.1; also elsewhere on the board
/CLK3: R1009.1; also elsewhere on the board
/CLK4: R1010.1; also elsewhere on the board
/Clock Generator/CLK: U1005.3 (B0), X1.5 (OUT)
/Clock Generator/CLK1₀: R1007.2, U1003.4 (Y0)
/Clock Generator/CLK2₀: R1008.2, U1003.5 (Y1)
/Clock Generator/CLK3₀: R1009.2, U1001.11 (CPC), U1001.13 (CPR), U1003.6 (Y2)
/Clock Generator/CLK4₀: R1010.2, U1003.7 (Y3)
/Clock Generator/CLKIN: U1004.14 (CP), U1005.4 (Y0)
/Clock Generator/T34₀: R1011.2, U1003.11 (Y1)
/Clock Generator/÷2: U1003.2 (A0), U1004.3 (Q0)
/Clock Generator/÷4: U1003.3 (A1), U1003.14 (A0), U1004.2 (Q1)
/FPCLK: R1006.1, U1005.2 (A0)
/POWEROK: D1003.1 (K)
/T34: R1011.1; also elsewhere on the board
/WSTB: TP1001.1
/~FPCLK~⁄CLK: R1005.2, U1005.1 (~A~/B)
/~FPRESET: D1002.1 (K)
/~RESET: D1002.2 (A), D1003.2 (A), D1004.2 (A), R1001.2, U1001.10 (~CLR), U1004.11 (~PL); also elsewhere on the board
/~RSTHOLD: R1002.1, R1003.1; also elsewhere on the board
GND: C1001.2, C1002.2, C1003.2, C1004.2, C1005.2, C1006.2, C1007.2, C1008.2, J1001.1, R1006.2, SW1001.2 (B), U1001.8 (GND), U1001.14 (~OE), U1002.3 (GND), U1003.1 (~G), U1003.8 (GND), U1003.13 (A1), U1003.15 (~G), U1004.1, U1004.4 (~CE), U1004.5 (~U~/D), U1004.8 (GND), U1004.9 (P3), U1004.10 (P2), U1004.15 (P0), U1005.5 (A1), U1005.6 (B1), U1005.8 (GND), U1005.10 (B2), U1005.11 (A2), U1005.13 (B3), U1005.14 (A3), U1005.15 (~G), X1.2 (GND), X1.3 (GND), X1.4 (GND), X1.6 (GND), X1.7 (GND); also elsewhere on the board
unnamed: C1001.1, J1001.2, R1004.2, SW1001.1 (A), U1002.2
unnamed: D1001.1 (K), U1001.7 (Q7), U1001.12 (~CE)
unnamed: D1001.2 (A), R1003.2
unnamed: D1004.1 (K), U1002.4

Notes on the sheet:
CLKIN
T34
CLK2
CLK3
CLK4
CLK1
WSTB
After a ~RESET~ pulse, the clock starts and we count 128 processor cycles. At a 4 MHz clock, this is 32 µs. During this time, ~RSTHOLD~ is asserted, and most of the processor units remain tri-stated and in reset while everything stabilises, capacitors are charged, etc. While ~RSTHOLD~ is low, the p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
There are four reset sources for the ~RESET~ signal: devices on the bus, the ~FPRESET~ from the DFP, the POWEROK signal from the PSU, and an optional tactile switch and/or 2-pin jumper. These are ORred together with diode logic and fed back to the bus ~RESET~ signal. All ~RESET~ drivers are open dr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
Just in case it's necessary for future clock uses.

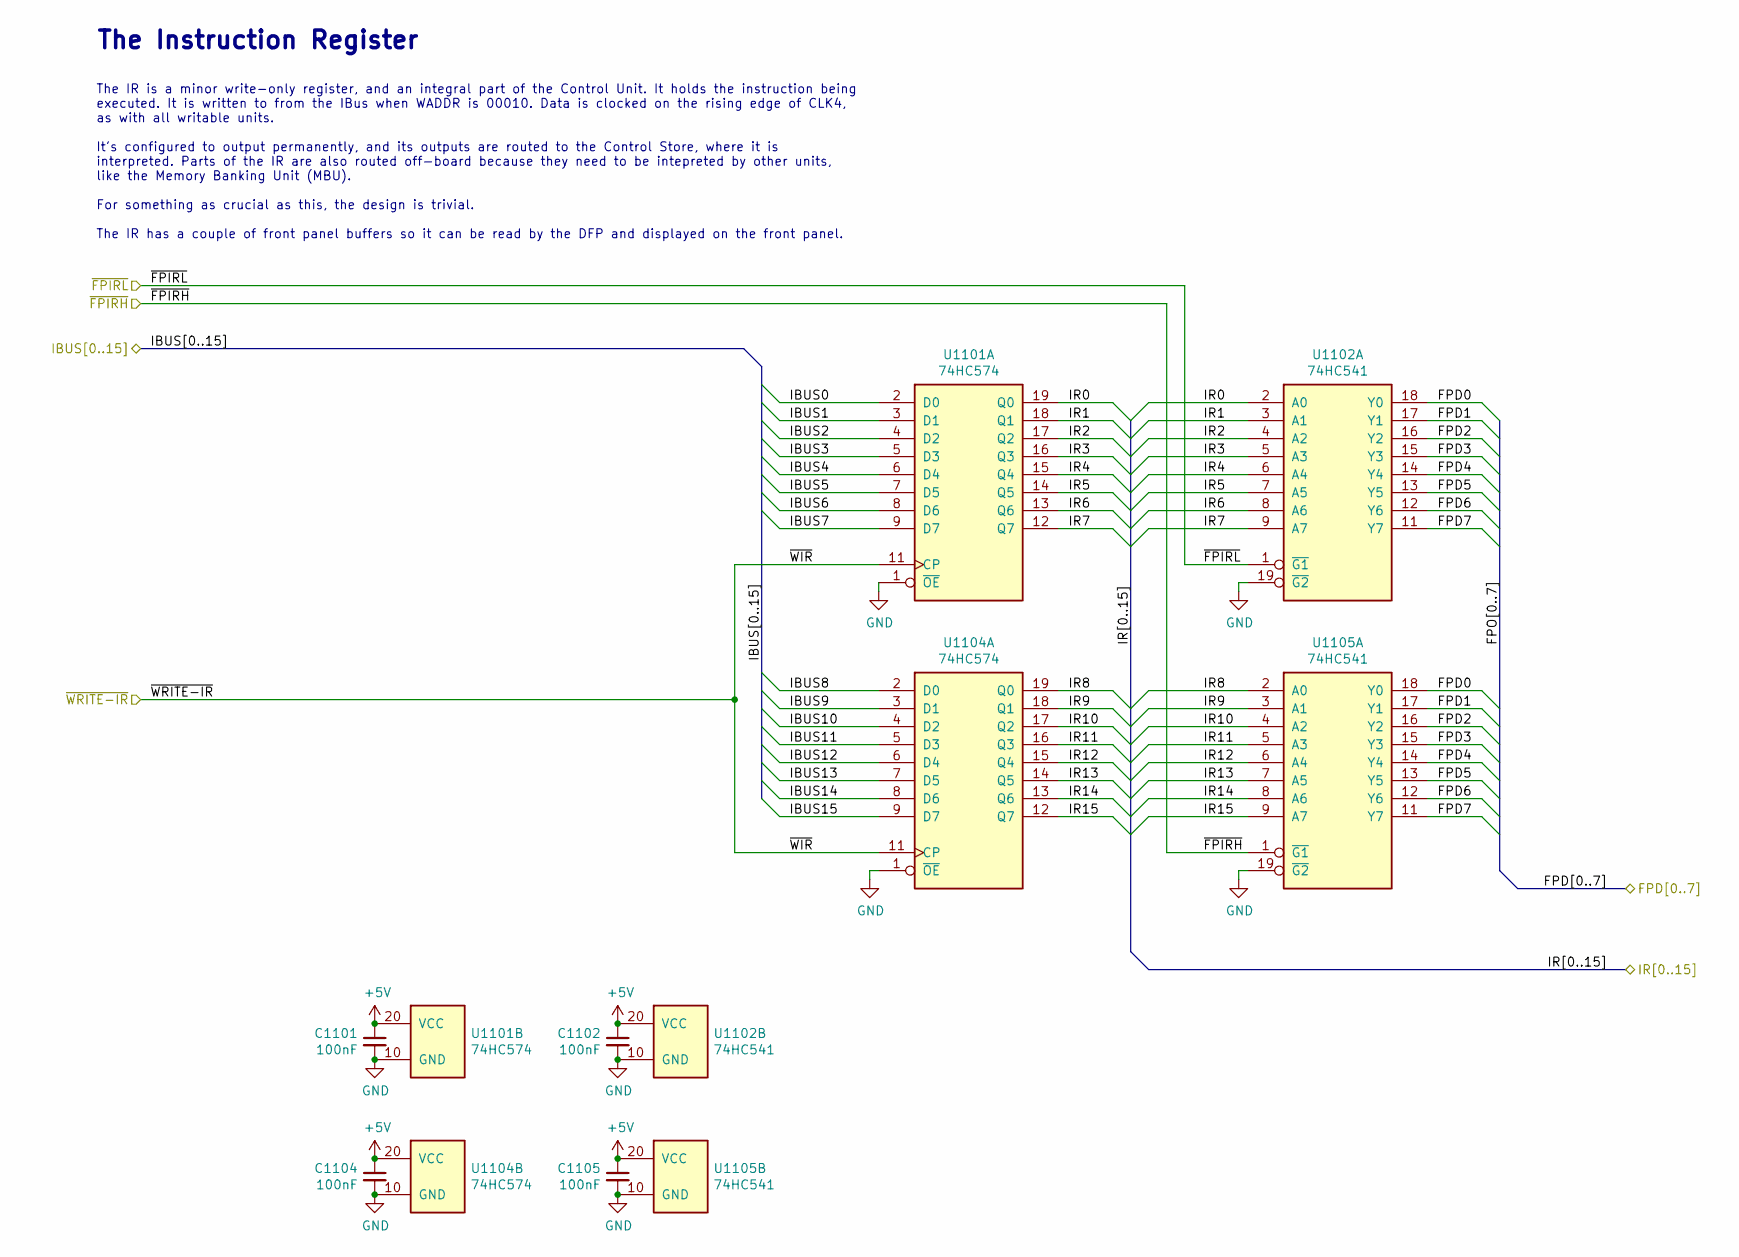
[picture p92: schematic cfg_reg_ir.sch, Instruction Register (IR)]

Parts:
C1101, C1102, C1104, C1105: 100nF; C_SMD_0805_2012Metric_Pad1.15x1.40mm_HandSolder
U1101, U1104: 74HC574; DIP-20_W7.62mm_Socket
U1102, U1105: 74HC541; DIP-20_W7.62mm_Socket

Connections:
+5V: C1101.1, C1102.1, C1104.1, C1105.1, U1101.20 (VCC), U1102.20 (VCC), U1104.20 (VCC), U1105.20 (VCC); also elsewhere on the board
/FPD0: U1102.18 (Y0), U1105.18 (Y0); also elsewhere on the board
/FPD1: U1102.17 (Y1), U1105.17 (Y1); also elsewhere on the board
/FPD2: U1102.16 (Y2), U1105.16 (Y2); also elsewhere on the board
/FPD3: U1102.15 (Y3), U1105.15 (Y3); also elsewhere on the board
/FPD4: U1102.14 (Y4), U1105.14 (Y4); also elsewhere on the board
/FPD5: U1102.13 (Y5), U1105.13 (Y5); also elsewhere on the board
/FPD6: U1102.12 (Y6), U1105.12 (Y6); also elsewhere on the board
/FPD7: U1102.11 (Y7), U1105.11 (Y7); also elsewhere on the board
/IBUS0: U1101.2 (D0); also elsewhere on the board
/IBUS1: U1101.3 (D1); also elsewhere on the board
/IBUS2: U1101.4 (D2); also elsewhere on the board
/IBUS3: U1101.5 (D3); also elsewhere on the board
/IBUS4: U1101.6 (D4); also elsewhere on the board
/IBUS5: U1101.7 (D5); also elsewhere on the board
/IBUS6: U1101.8 (D6); also elsewhere on the board
/IBUS7: U1101.9 (D7); also elsewhere on the board
/IBUS8: U1104.2 (D0); also elsewhere on the board
/IBUS9: U1104.3 (D1); also elsewhere on the board
/IBUS10: U1104.4 (D2); also elsewhere on the board
/IBUS11: U1104.5 (D3); also elsewhere on the board
/IBUS12: U1104.6 (D4); also elsewhere on the board
/IBUS13: U1104.7 (D5); also elsewhere on the board
/IBUS14: U1104.8 (D6); also elsewhere on the board
/IBUS15: U1104.9 (D7); also elsewhere on the board
/IR0: U1101.19 (Q0), U1102.2 (A0); also elsewhere on the board
/IR1: U1101.18 (Q1), U1102.3 (A1); also elsewhere on the board
/IR2: U1101.17 (Q2), U1102.4 (A2); also elsewhere on the board
/IR3: U1101.16 (Q3), U1102.5 (A3); also elsewhere on the board
/IR4: U1101.15 (Q4), U1102.6 (A4); also elsewhere on the board
/IR5: U1101.14 (Q5), U1102.7 (A5); also elsewhere on the board
/IR6: U1101.13 (Q6), U1102.8 (A6); also elsewhere on the board
/IR7: U1101.12 (Q7), U1102.9 (A7); also elsewhere on the board
/IR8: U1104.19 (Q0), U1105.2 (A0); also elsewhere on the board
/IR9: U1104.18 (Q1), U1105.3 (A1); also elsewhere on the board
/IR10: U1104.17 (Q2), U1105.4 (A2); also elsewhere on the board
/IR11: U1104.16 (Q3), U1105.5 (A3); also elsewhere on the board
/IR12: U1104.15 (Q4), U1105.6 (A4); also elsewhere on the board
/IR13: U1104.14 (Q5), U1105.7 (A5); also elsewhere on the board
/IR14: U1104.13 (Q6), U1105.8 (A6); also elsewhere on the board
/IR15: U1104.12 (Q7), U1105.9 (A7); also elsewhere on the board
/~FPIRH: U1105.1 (~G1)
/~FPIRL: U1102.1 (~G1)
/~WRITE-IR: U1101.11 (CP), U1104.11 (CP)
GND: C1101.2, C1102.2, C1104.2, C1105.2, U1101.1 (~OE), U1101.10 (GND), U1102.10 (GND), U1102.19 (~G2), U1104.1 (~OE), U1104.10 (GND), U1105.10 (GND), U1105.19 (~G2); also elsewhere on the board

Notes on the sheet:
The IR is a minor write-only register, and an integral part of the Control Unit. It holds the instruction being executed. It is written to from the IBus when WADDR is 00010. Data is clocked on the rising edge of CLK4, as with all writable units. It's configured to output permanently, and its output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
The Instruction Register
