alexiosc/cft/kicad/cft/cft-board0/cft-board0.kicad_pcb

## KiCad design kicad/cft/cft-board0/cft-board0.kicad_pcb (continued)

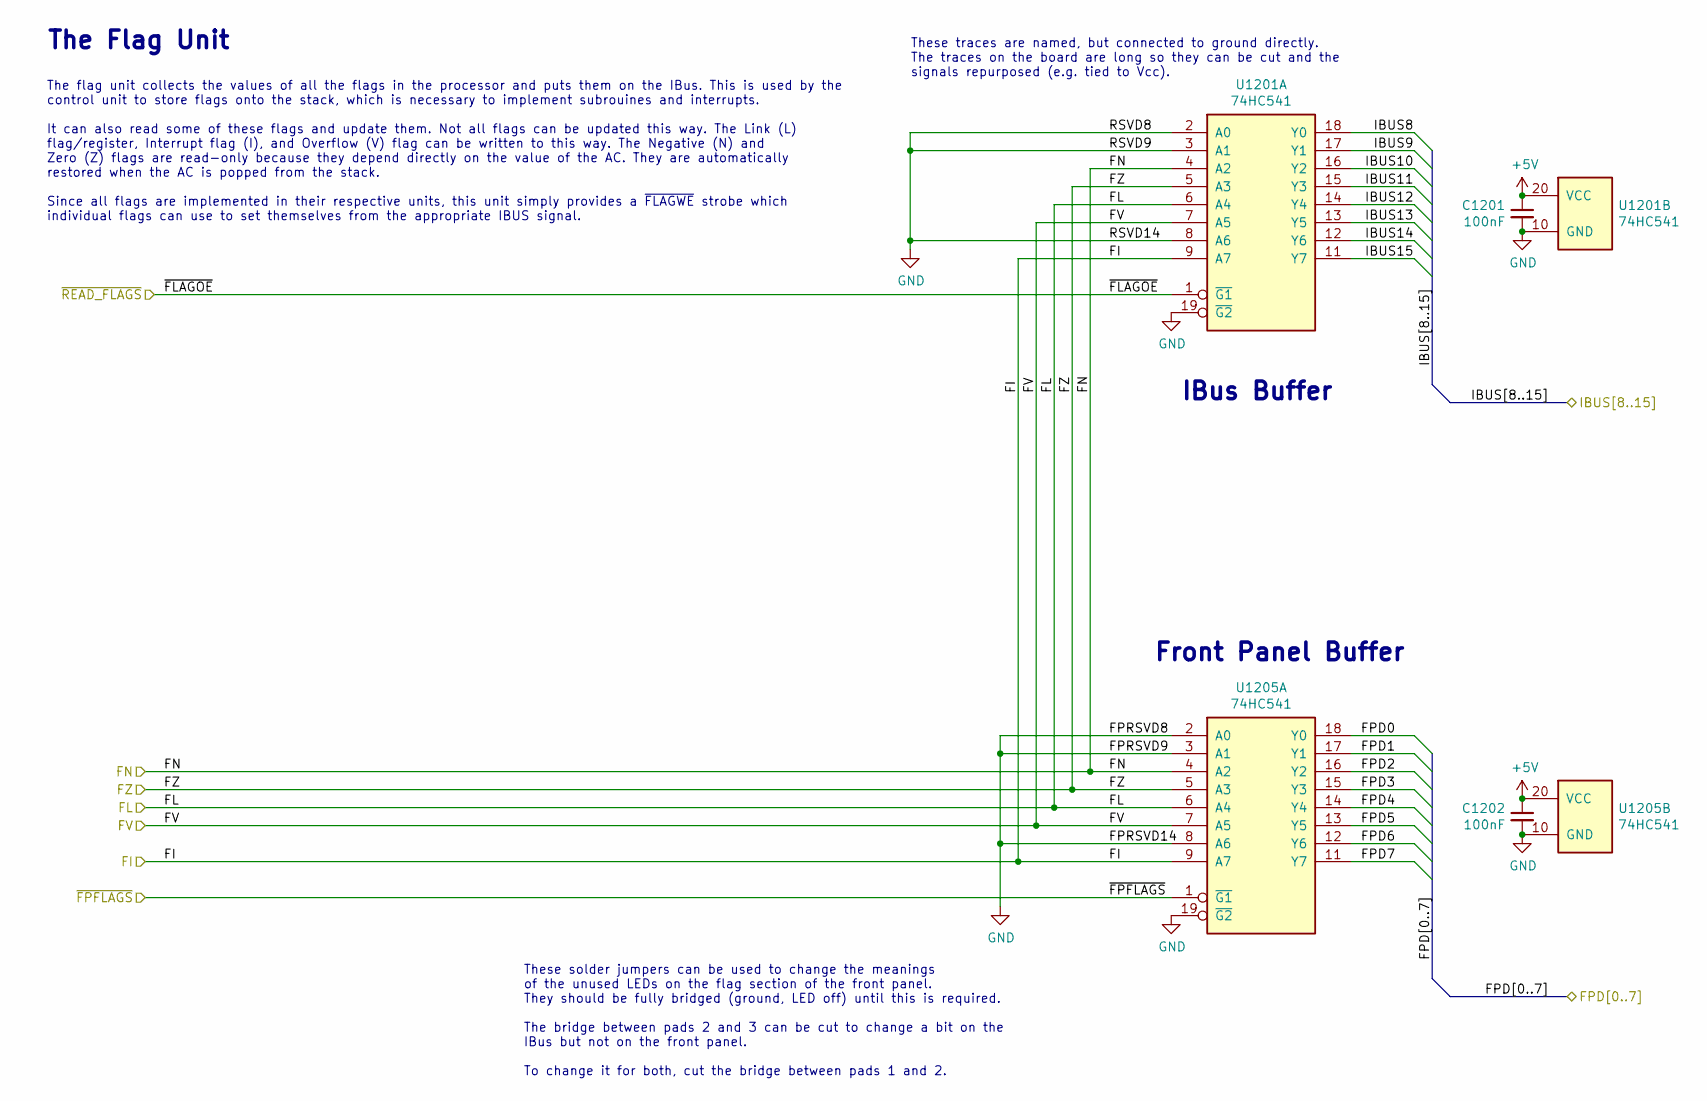
[picture p93: schematic flag_unit.sch, Flag Unit]

Parts:
C1201, C1202: 100nF; C_SMD_0805_2012Metric_Pad1.15x1.40mm_HandSolder
U1201, U1205: 74HC541; DIP-20_W7.62mm_Socket

Connections:
+5V: C1201.1, C1202.1, U1201.20 (VCC), U1205.20 (VCC); also elsewhere on the board
/FI: U1201.9 (A7), U1205.9 (A7); also elsewhere on the board
/FL: U1201.6 (A4), U1205.6 (A4); also elsewhere on the board
/FN: U1201.4 (A2), U1205.4 (A2); also elsewhere on the board
/FPD0: U1205.18 (Y0); also elsewhere on the board
/FPD1: U1205.17 (Y1); also elsewhere on the board
/FPD2: U1205.16 (Y2); also elsewhere on the board
/FPD3: U1205.15 (Y3); also elsewhere on the board
/FPD4: U1205.14 (Y4); also elsewhere on the board
/FPD5: U1205.13 (Y5); also elsewhere on the board
/FPD6: U1205.12 (Y6); also elsewhere on the board
/FPD7: U1205.11 (Y7); also elsewhere on the board
/FV: U1201.7 (A5), U1205.7 (A5); also elsewhere on the board
/FZ: U1201.5 (A3), U1205.5 (A3); also elsewhere on the board
/Flag Unit/~READ_FLAGS: U1201.1 (~G1)
/IBUS8: U1201.18 (Y0); also elsewhere on the board
/IBUS9: U1201.17 (Y1); also elsewhere on the board
/IBUS10: U1201.16 (Y2); also elsewhere on the board
/IBUS11: U1201.15 (Y3); also elsewhere on the board
/IBUS12: U1201.14 (Y4); also elsewhere on the board
/IBUS13: U1201.13 (Y5); also elsewhere on the board
/IBUS14: U1201.12 (Y6); also elsewhere on the board
/IBUS15: U1201.11 (Y7); also elsewhere on the board
/~FPFLAGS: U1205.1 (~G1)
GND: C1201.2, C1202.2, U1201.2 (A0), U1201.3 (A1), U1201.8 (A6), U1201.10 (GND), U1201.19 (~G2), U1205.2 (A0), U1205.3 (A1), U1205.8 (A6), U1205.10 (GND), U1205.19 (~G2); also elsewhere on the board

Notes on the sheet:
Front Panel Buffer
IBus Buffer
The flag unit collects the values of all the flags in the processor and puts them on the IBus. This is used by the control unit to store flags onto the stack, which is necessary to implement subrouines and interrupts. It can also read some of these flags and update them. Not all flags can be update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
The Flag Unit
These solder jumpers can be used to change the meanings of the unused LEDs on the flag section of the front panel. They should be fully bridged (ground, LED off) until this is required. The bridge between pads 2 and 3 can be cut to change a bit on the IBus but not on the front panel. To change it f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
These traces are named, but connected to ground directly. The traces on the board are long so they can be cut and the signals repurposed (e.g. tied to Vcc).

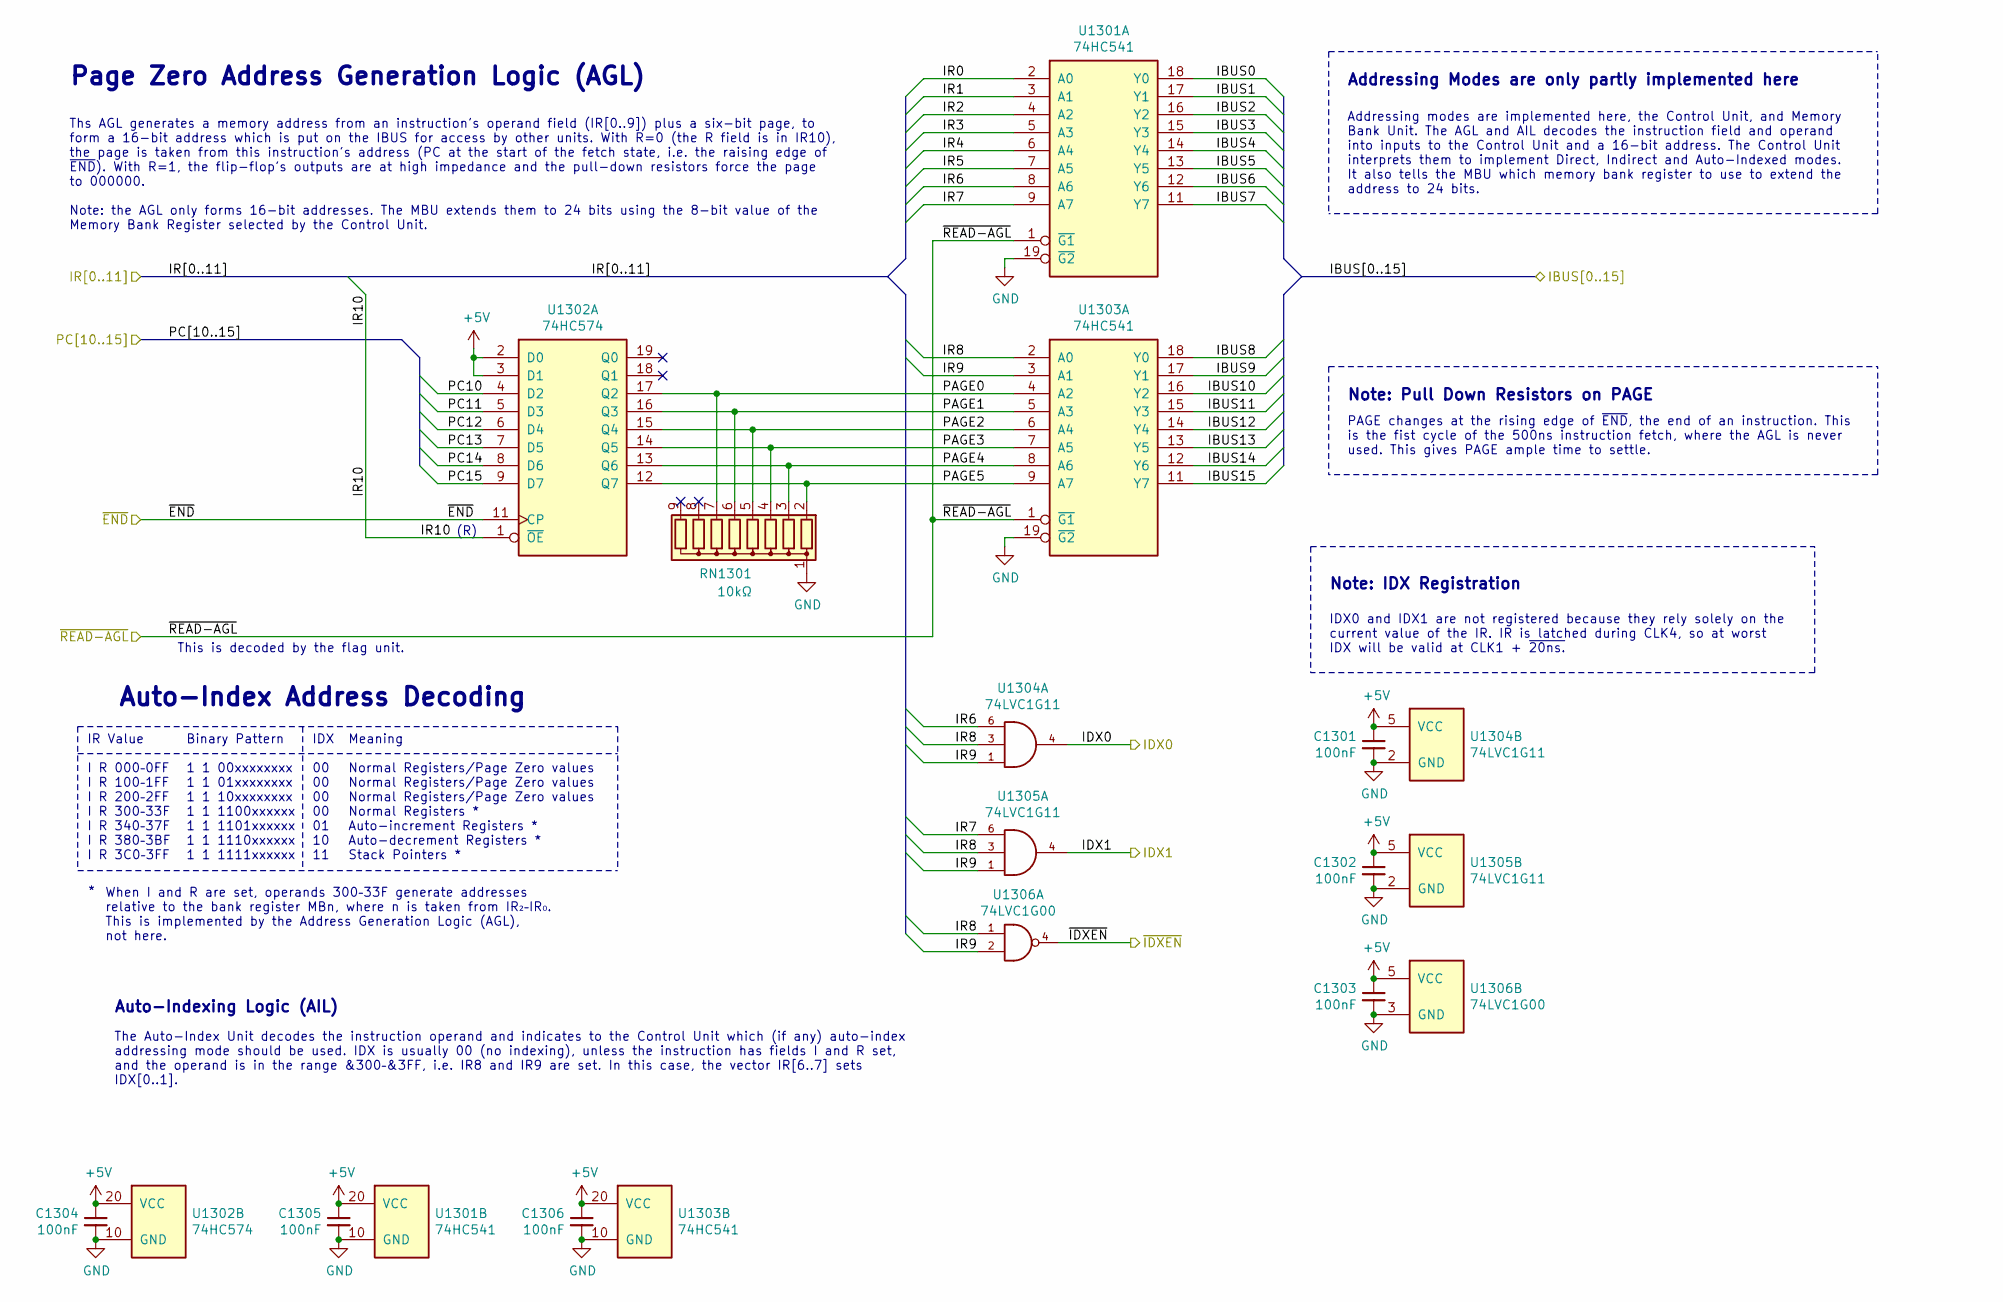
[picture p94: schematic cft_agl.sch, Addressing Modes]

Parts:
C1301, C1302, C1303, C1304, C1305, C1306: 100nF; C_SMD_0805_2012Metric_Pad1.15x1.40mm_HandSolder
RN1301: 10kΩ; R_Array_SIP9
U1301, U1303: 74HC541; DIP-20_W7.62mm_Socket
U1302: 74HC574; DIP-20_W7.62mm_Socket
U1304, U1305: 74LVC1G11; SOT-23-6_Handsoldering
U1306: 74LVC1G00; SOT-23-5_HandSoldering

Connections:
+5V: C1301.1, C1302.1, C1303.1, C1304.1, C1305.1, C1306.1, U1301.20 (VCC), U1302.2 (D0), U1302.3 (D1), U1302.20 (VCC), U1303.20 (VCC), U1304.5 (VCC), U1305.5 (VCC), U1306.5 (VCC); also elsewhere on the board
/Addressing Modes/PAGE0: RN1301.7 (R6), U1302.17 (Q2), U1303.4 (A2)
/Addressing Modes/PAGE1: RN1301.6 (R5), U1302.16 (Q3), U1303.5 (A3)
/Addressing Modes/PAGE2: RN1301.5 (R4), U1302.15 (Q4), U1303.6 (A4)
/Addressing Modes/PAGE3: RN1301.4 (R3), U1302.14 (Q5), U1303.7 (A5)
/Addressing Modes/PAGE4: RN1301.3 (R2), U1302.13 (Q6), U1303.8 (A6)
/Addressing Modes/PAGE5: RN1301.2 (R1), U1302.12 (Q7), U1303.9 (A7)
/IBUS0: U1301.18 (Y0); also elsewhere on the board
/IBUS1: U1301.17 (Y1); also elsewhere on the board
/IBUS2: U1301.16 (Y2); also elsewhere on the board
/IBUS3: U1301.15 (Y3); also elsewhere on the board
/IBUS4: U1301.14 (Y4); also elsewhere on the board
/IBUS5: U1301.13 (Y5); also elsewhere on the board
/IBUS6: U1301.12 (Y6); also elsewhere on the board
/IBUS7: U1301.11 (Y7); also elsewhere on the board
/IBUS8: U1303.18 (Y0); also elsewhere on the board
/IBUS9: U1303.17 (Y1); also elsewhere on the board
/IBUS10: U1303.16 (Y2); also elsewhere on the board
/IBUS11: U1303.15 (Y3); also elsewhere on the board
/IBUS12: U1303.14 (Y4); also elsewhere on the board
/IBUS13: U1303.13 (Y5); also elsewhere on the board
/IBUS14: U1303.12 (Y6); also elsewhere on the board
/IBUS15: U1303.11 (Y7); also elsewhere on the board
/IDX0: U1304.4; also elsewhere on the board
/IDX1: U1305.4; also elsewhere on the board
/IR0: U1301.2 (A0); also elsewhere on the board
/IR1: U1301.3 (A1); also elsewhere on the board
/IR2: U1301.4 (A2); also elsewhere on the board
/IR3: U1301.5 (A3); also elsewhere on the board
/IR4: U1301.6 (A4); also elsewhere on the board
/IR5: U1301.7 (A5); also elsewhere on the board
/IR6: U1301.8 (A6), U1304.6; also elsewhere on the board
/IR7: U1301.9 (A7), U1305.6; also elsewhere on the board
/IR8: U1303.2 (A0), U1304.3, U1305.3, U1306.1; also elsewhere on the board
/IR9: U1303.3 (A1), U1304.1, U1305.1, U1306.2; also elsewhere on the board
/IR10: U1302.1 (~OE); also elsewhere on the board
/PC10: U1302.4 (D2); also elsewhere on the board
/PC11: U1302.5 (D3); also elsewhere on the board
/PC12: U1302.6 (D4); also elsewhere on the board
/PC13: U1302.7 (D5); also elsewhere on the board
/PC14: U1302.8 (D6); also elsewhere on the board
/PC15: U1302.9 (D7); also elsewhere on the board
/~END: U1302.11 (CP); also elsewhere on the board
/~IDXEN: U1306.4; also elsewhere on the board
/~READ-AGL: U1301.1 (~G1), U1303.1 (~G1)
GND: C1301.2, C1302.2, C1303.2, C1304.2, C1305.2, C1306.2, RN1301.1 (common), U1301.10 (GND), U1301.19 (~G2), U1302.10 (GND), U1303.10 (GND), U1303.19 (~G2), U1304.2 (GND), U1305.2 (GND), U1306.3 (GND); also elsewhere on the board

Notes on the sheet:
Ths AGL generates a memory address from an instruction's operand field (IR[0..9]) plus a six-bit page, to form a 16-bit address which is put on the IBUS for access by other units. With R=0 (the R field is in IR10), the page is taken from this instruction's address (PC at the start of the fetch stat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
Auto-Index Address Decoding
When I and R are set, operands 300–33F generate addresses relative to the bank register MBn, where n is taken from IR₂–IR₀. This is implemented by the Address Generation Logic (AGL), not here.
Meaning Normal Registers/Page Zero values Normal Registers/Page Zero values Normal Registers/Page Zero values Normal Registers * Auto-increment Registers * Auto-decrement Registers * Stack Pointers *
Binary Pattern 1 1 00xxxxxxxx 1 1 01xxxxxxxx 1 1 10xxxxxxxx 1 1 1100xxxxxx 1 1 1101xxxxxx 1 1 1110xxxxxx 1 1 1111xxxxxx
IR Value I R 000–0FF I R 100–1FF I R 200–2FF I R 300–33F I R 340–37F I R 380–3BF I R 3C0–3FF
IDX 00 00 00 00 01 10 11
Page Zero Address Generation Logic (AGL)
Auto-Indexing Logic (AIL)
(R)
Note: Pull Down Resistors on PAGE
PAGE changes at the rising edge of ~END~, the end of an instruction. This is the fist cycle of the 500ns instruction fetch, where the AGL is never used. This gives PAGE ample time to settle.
The Auto-Index Unit decodes the instruction operand and indicates to the Control Unit which (if any) auto-index addressing mode should be used. IDX is usually 00 (no indexing), unless the instruction has fields I and R set, and the operand is in the range &300–&3FF, i.e. IR8 and IR9 are set. In thi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
Addressing Modes are only partly implemented here
Addressing modes are implemented here, the Control Unit, and Memory Bank Unit. The AGL and AIL decodes the instruction field and operand into inputs to the Control Unit and a 16-bit address. The Control Unit interprets them to implement Direct, Indirect and Auto-Indexed modes. It also tells the MBU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
This is decoded by the flag unit.
Note: IDX Registration
IDX0 and IDX1 are not registered because they rely solely on the current value of the IR. IR is latched during CLK4, so at worst IDX will be valid at CLK1 + ~20ns.

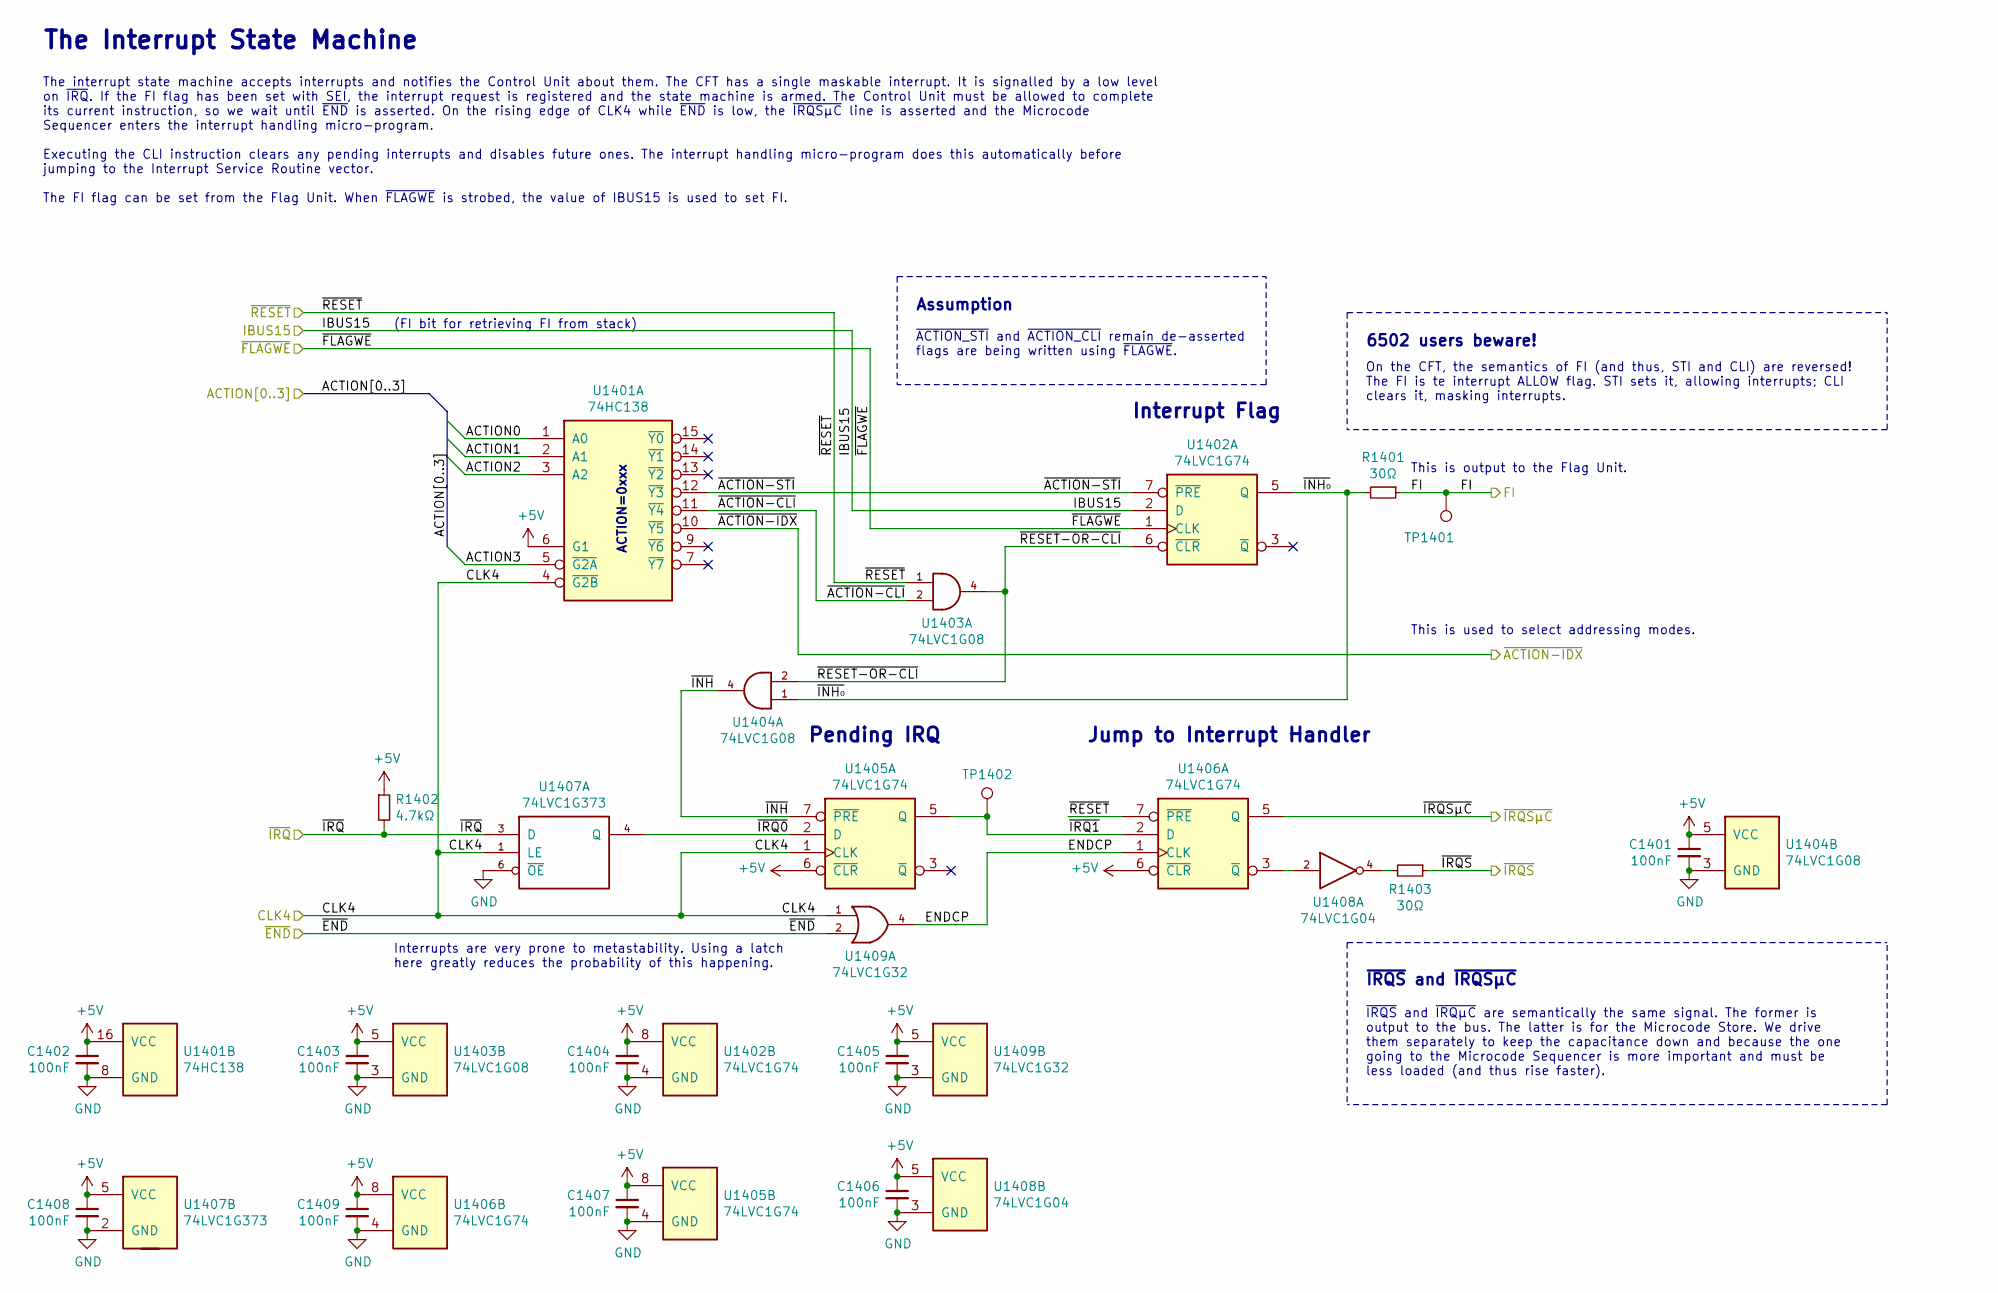
[picture p95: schematic cft_int_fsm.sch, Interrupt State Machine]

Parts:
C1401, C1402, C1403, C1404, C1405, C1406, C1407, C1408, C1409: 100nF; C_SMD_0805_2012Metric_Pad1.15x1.40mm_HandSolder
R1401, R1403: 30Ω; R_SMD_0805_2012Metric_Pad1.15x1.40mm_HandSolder
R1402: 4.7kΩ; R_SMD_0805_2012Metric_Pad1.15x1.40mm_HandSolder
TP1401, TP1402: TestPoint; TestPoint_Pad_1.0x1.0mm
U1401: 74HC138; DIP-16_W7.62mm_Socket
U1402, U1405, U1406: 74LVC1G74; TSSOP-8_3x3mm_P0.65mm
U1403, U1404: 74LVC1G08; SOT-23-5_HandSoldering
U1407: 74LVC1G373; SOT-23-6_Handsoldering
U1408: 74LVC1G04; SOT-23-5_HandSoldering
U1409: 74LVC1G32; SOT-23-5_HandSoldering

Connections:
+5V: C1401.1, C1402.1, C1403.1, C1404.1, C1405.1, C1406.1, C1407.1, C1408.1, C1409.1, R1402.1, U1401.6 (G1), U1401.16 (VCC), U1402.8 (VCC), U1403.5 (VCC), U1404.5 (VCC), U1405.6 (~CLR), U1405.8 (VCC), U1406.6 (~CLR), U1406.8 (VCC), U1407.5 (VCC), U1408.5 (VCC), U1409.5 (VCC); also elsewhere on the board
/ACTION0: U1401.1 (A0); also elsewhere on the board
/ACTION1: U1401.2 (A1); also elsewhere on the board
/ACTION2: U1401.3 (A2); also elsewhere on the board
/ACTION3: U1401.5 (~G2A); also elsewhere on the board
/CLK4: U1401.4 (~G2B), U1405.1 (CLK), U1407.1 (LE), U1409.1; also elsewhere on the board
/FI: R1401.1, TP1401.1; also elsewhere on the board
/IBUS15: U1402.2 (D); also elsewhere on the board
/Interrupt State Machine/ENDCP: U1406.1 (CLK), U1409.4
/Interrupt State Machine/~ACTION-CLI: U1401.11 (~Y4), U1403.2
/Interrupt State Machine/~ACTION-STI: U1401.12 (~Y3), U1402.7 (~PRE)
/Interrupt State Machine/~INH: U1404.4, U1405.7 (~PRE)
/Interrupt State Machine/~INH₀: R1401.2, U1402.5 (Q), U1404.1
/Interrupt State Machine/~IRQ0: U1405.2 (D), U1407.4 (Q)
/Interrupt State Machine/~IRQ1: TP1402.1, U1405.5 (Q), U1406.2 (D)
/Interrupt State Machine/~RESET-OR-CLI: U1402.6 (~CLR), U1403.4, U1404.2
/~ACTION-IDX: U1401.10 (~Y5); also elsewhere on the board
/~END: U1409.2; also elsewhere on the board
/~FLAGWE: U1402.1 (CLK); also elsewhere on the board
/~IRQ: R1402.2, U1407.3 (D); also elsewhere on the board
/~IRQS: R1403.1; also elsewhere on the board
/~IRQSµC: U1406.5 (Q); also elsewhere on the board
/~RESET: U1403.1, U1406.7 (~PRE); also elsewhere on the board
GND: C1401.2, C1402.2, C1403.2, C1404.2, C1405.2, C1406.2, C1407.2, C1408.2, C1409.2, U1401.8 (GND), U1402.4 (GND), U1403.3 (GND), U1404.3 (GND), U1405.4 (GND), U1406.4 (GND), U1407.2 (GND), U1407.6 (~OE), U1408.3 (GND), U1409.3 (GND); also elsewhere on the board
unnamed: R1403.2, U1408.4
unnamed: U1406.3 (~Q), U1408.2

Notes on the sheet:
Interrupt Flag
(FI bit for retrieving FI from stack)
Assumption
~ACTION_STI~ and ~ACTION_CLI~ remain de-asserted flags are being written using ~FLAGWE~.
ACTION=0xxx
Interrupts are very prone to metastability. Using a latch here greatly reduces the probability of this happening.
6502 users beware!
On the CFT, the semantics of FI (and thus, STI and CLI) are reversed! The FI is te interrupt ALLOW flag. STI sets it, allowing interrupts; CLI clears it, masking interrupts.
Jump to Interrupt Handler
Pending IRQ
The Interrupt State Machine
The interrupt state machine accepts interrupts and notifies the Control Unit about them. The CFT has a single maskable interrupt. It is signalled by a low level on ~IRQ~. If the FI flag has been set with SEI, the interrupt request is registered and the state machine is armed. The Control Unit must 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
~IRQS~ and ~IRQµC~ are semantically the same signal. The former is output to the bus. The latter is for the Microcode Store. We drive them separately to keep the capacitance down and because the one going to the Microcode Sequencer is more important and must be less loaded (and thus rise faster).
~IRQS~ and ~IRQSµC~
This is used to select addressing modes.
This is output to the Flag Unit.

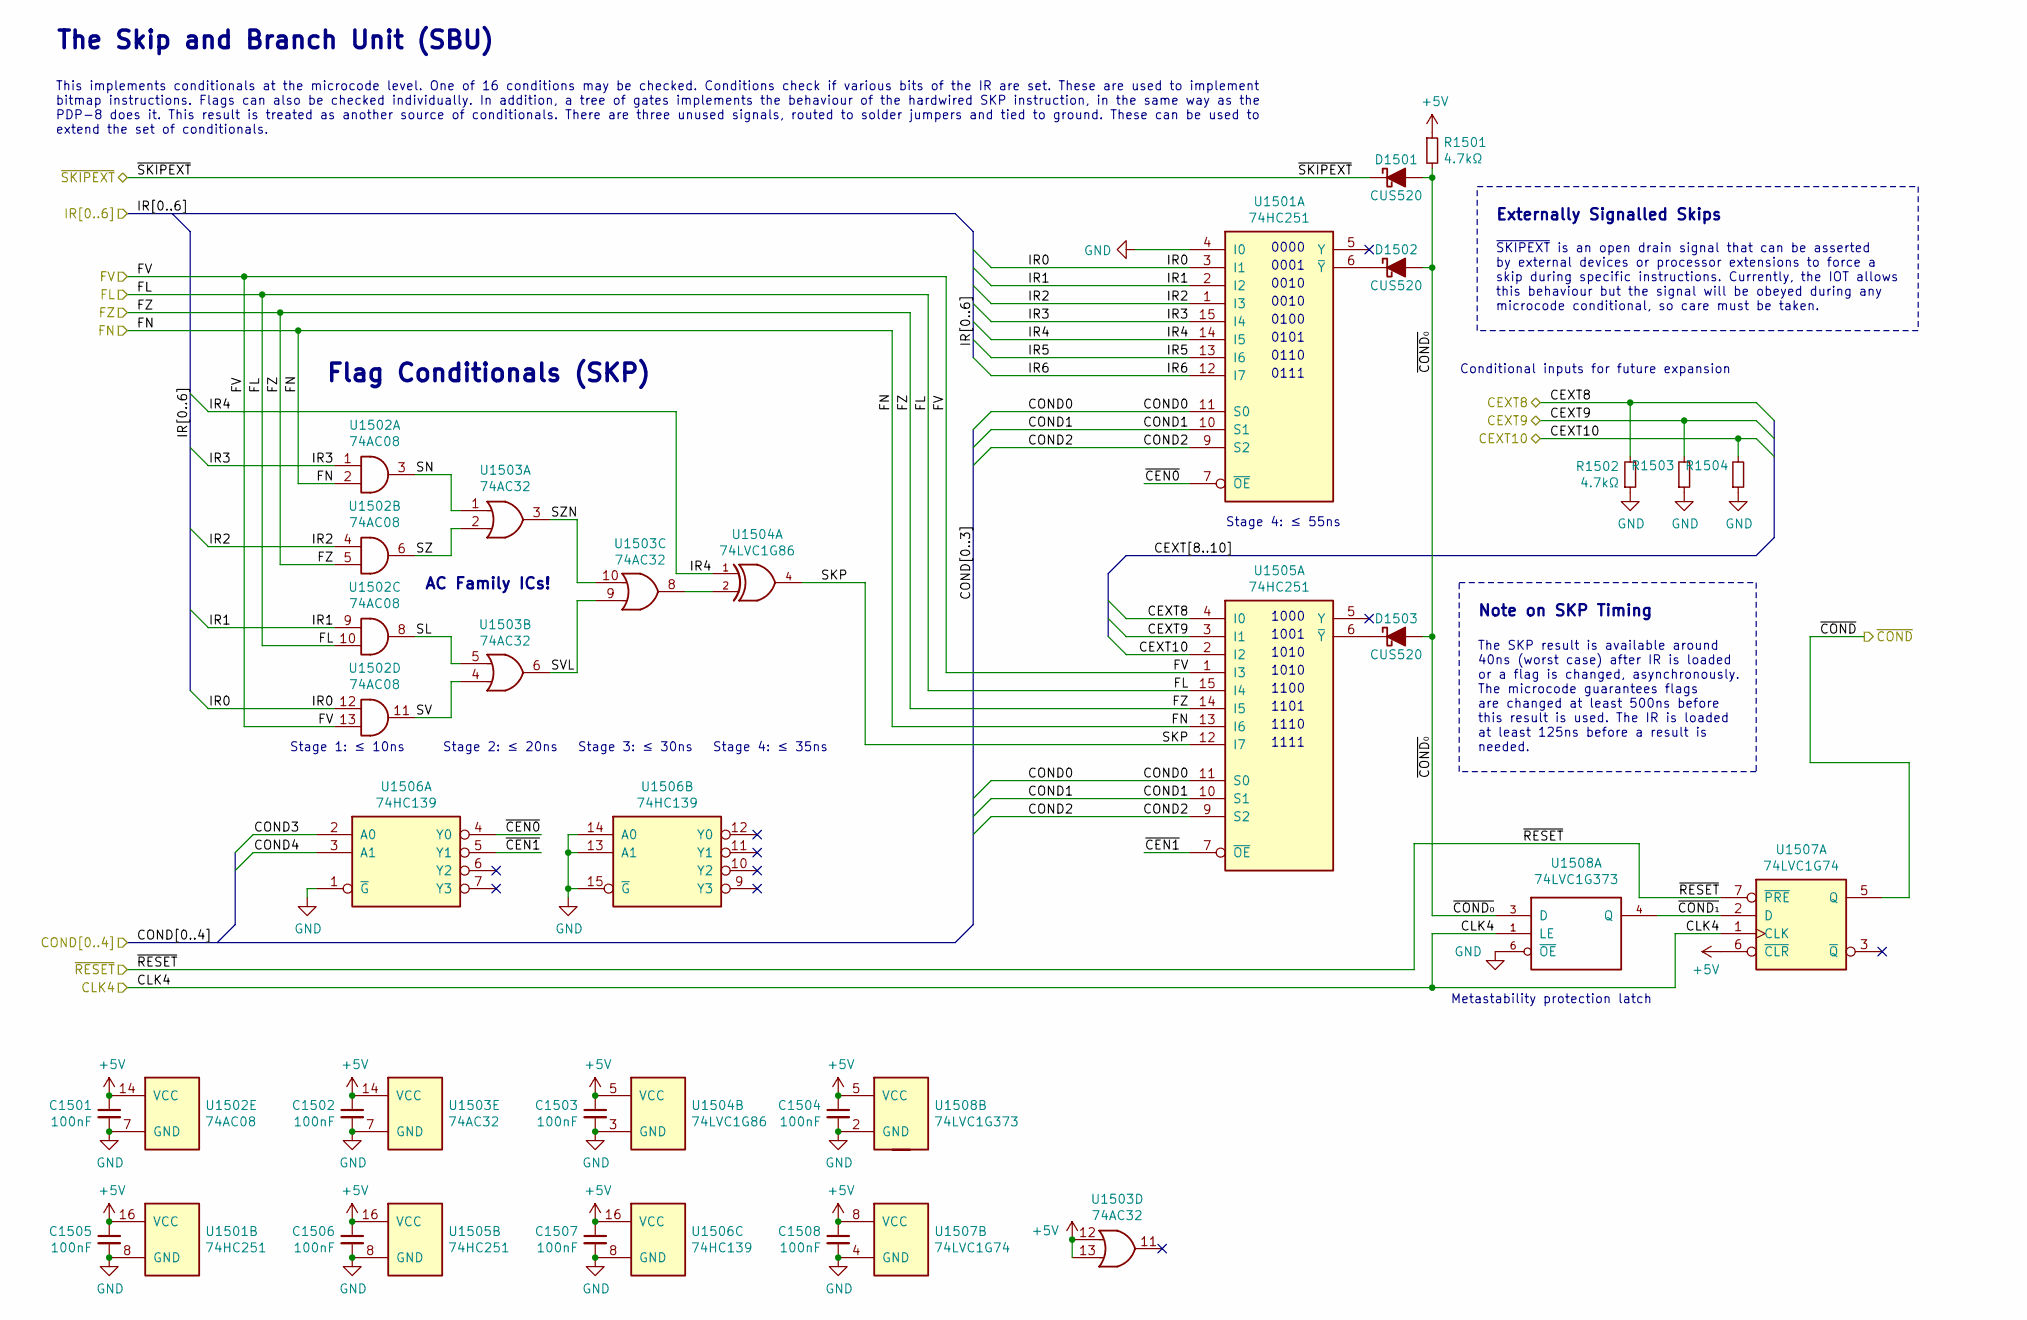
[picture p96: schematic cft_sbu.sch, Skip/Branch Unit]

Parts:
C1501, C1502, C1503, C1504, C1505, C1506, C1507, C1508: 100nF; C_SMD_0805_2012Metric_Pad1.15x1.40mm_HandSolder
D1501: CUS520; SOD-323; Mouser 757-CUS520H3F; £0.043/100
D1502, D1503: CUS520; SOD-323
R1501, R1502, R1503, R1504: 4.7kΩ; R_SMD_0805_2012Metric_Pad1.15x1.40mm_HandSolder
U1501, U1505: 74HC251; DIP-16_W7.62mm_Socket
U1502: 74AC08; DIP-14_W7.62mm_Socket
U1503: 74AC32; DIP-14_W7.62mm_Socket
U1504: 74LVC1G86; SOT-23-5_HandSoldering
U1506: 74HC139; DIP-16_W7.62mm_Socket
U1507: 74LVC1G74; TSSOP-8_3x3mm_P0.65mm
U1508: 74LVC1G373; SOT-23-6_Handsoldering

Connections:
+5V: C1501.1, C1502.1, C1503.1, C1504.1, C1505.1, C1506.1, C1507.1, C1508.1, R1501.1, U1501.16 (VCC), U1502.14 (VCC), U1503.12, U1503.13, U1503.14 (VCC), U1504.5 (VCC), U1505.16 (VCC), U1506.16 (VCC), U1507.6 (~CLR), U1507.8 (VCC), U1508.5 (VCC); also elsewhere on the board
/CEXT8: R1502.2, U1505.4 (I0)
/CEXT9: R1503.2, U1505.3 (I1)
/CEXT10: R1504.2, U1505.2 (I2); also elsewhere on the board
/CLK4: U1507.1 (CLK), U1508.1 (LE); also elsewhere on the board
/COND0: U1501.11 (S0), U1505.11 (S0); also elsewhere on the board
/COND1: U1501.10 (S1), U1505.10 (S1); also elsewhere on the board
/COND2: U1501.9 (S2), U1505.9 (S2); also elsewhere on the board
/COND3: U1506.2 (A0); also elsewhere on the board
/COND4: U1506.3 (A1); also elsewhere on the board
/FL: U1502.10, U1505.15 (I4); also elsewhere on the board
/FN: U1502.2, U1505.13 (I6); also elsewhere on the board
/FV: U1502.13, U1505.1 (I3); also elsewhere on the board
/FZ: U1502.5, U1505.14 (I5); also elsewhere on the board
/IR0: U1501.3 (I1), U1502.12; also elsewhere on the board
/IR1: U1501.2 (I2), U1502.9; also elsewhere on the board
/IR2: U1501.1 (I3), U1502.4; also elsewhere on the board
/IR3: U1501.15 (I4), U1502.1; also elsewhere on the board
/IR4: U1501.14 (I5), U1504.1; also elsewhere on the board
/IR5: U1501.13 (I6); also elsewhere on the board
/IR6: U1501.12 (I7); also elsewhere on the board
/Skip/Branch Unit/SKP: U1504.4, U1505.12 (I7)
/Skip/Branch Unit/SL: U1502.8, U1503.5
/Skip/Branch Unit/SN: U1502.3, U1503.1
/Skip/Branch Unit/SV: U1502.11, U1503.4
/Skip/Branch Unit/SVL: U1503.6, U1503.9
/Skip/Branch Unit/SZ: U1502.6, U1503.2
/Skip/Branch Unit/SZN: U1503.3, U1503.10
/Skip/Branch Unit/~CEN0: U1501.7 (~OE), U1506.4 (Y0)
/Skip/Branch Unit/~CEN1: U1505.7 (~OE), U1506.5 (Y1)
/Skip/Branch Unit/~COND₀: D1501.2 (A), D1502.2 (A), D1503.2 (A), R1501.2, U1508.3 (D)
/Skip/Branch Unit/~COND₁: U1507.2 (D), U1508.4 (Q)
/~COND: U1507.5 (Q); also elsewhere on the board
/~RESET: U1507.7 (~PRE); also elsewhere on the board
/~SKIPEXT: D1501.1 (K); also elsewhere on the board
GND: C1501.2, C1502.2, C1503.2, C1504.2, C1505.2, C1506.2, C1507.2, C1508.2, R1502.1, R1503.1, R1504.1, U1501.4 (I0), U1501.8 (GND), U1502.7 (GND), U1503.7 (GND), U1504.3 (GND), U1505.8 (GND), U1506.1 (~G), U1506.8 (GND), U1506.13 (A1), U1506.14 (A0), U1506.15 (~G), U1507.4 (GND), U1508.2 (GND), U1508.6 (~OE); also elsewhere on the board
unnamed: D1502.1 (K), U1501.6 (~Y)
unnamed: D1503.1 (K), U1505.6 (~Y)
unnamed: U1503.8, U1504.2

Notes on the sheet:
Flag Conditionals (SKP)
Metastability protection latch
0000
0001
0010
0100
0101
0110
0111
1000
1001
1010
1100
1101
1110
1111
AC Family ICs!
Stage 1: ≤ 10ns
Stage 2: ≤ 20ns
Stage 3: ≤ 30ns
Stage 4: ≤ 35ns
Stage 4: ≤ 55ns
The SKP result is available around 40ns (worst case) after IR is loaded or a flag is changed, asynchronously. The microcode guarantees flags are changed at least 500ns before this result is used. The IR is loaded at least 125ns before a result is needed.
Note on SKP Timing
The Skip and Branch Unit (SBU)
This implements conditionals at the microcode level. One of 16 conditions may be checked. Conditions check if various bits of the IR are set. These are used to implement bitmap instructions. Flags can also be checked individually. In addition, a tree of gates implements the behaviour of the hardwir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
~SKIPEXT~ is an open drain signal that can be asserted by external devices or processor extensions to force a skip during specific instructions. Currently, the IOT allows this behaviour but the signal will be obeyed during any microcode conditional, so care must be taken.
Externally Signalled Skips
Conditional inputs for future expansion

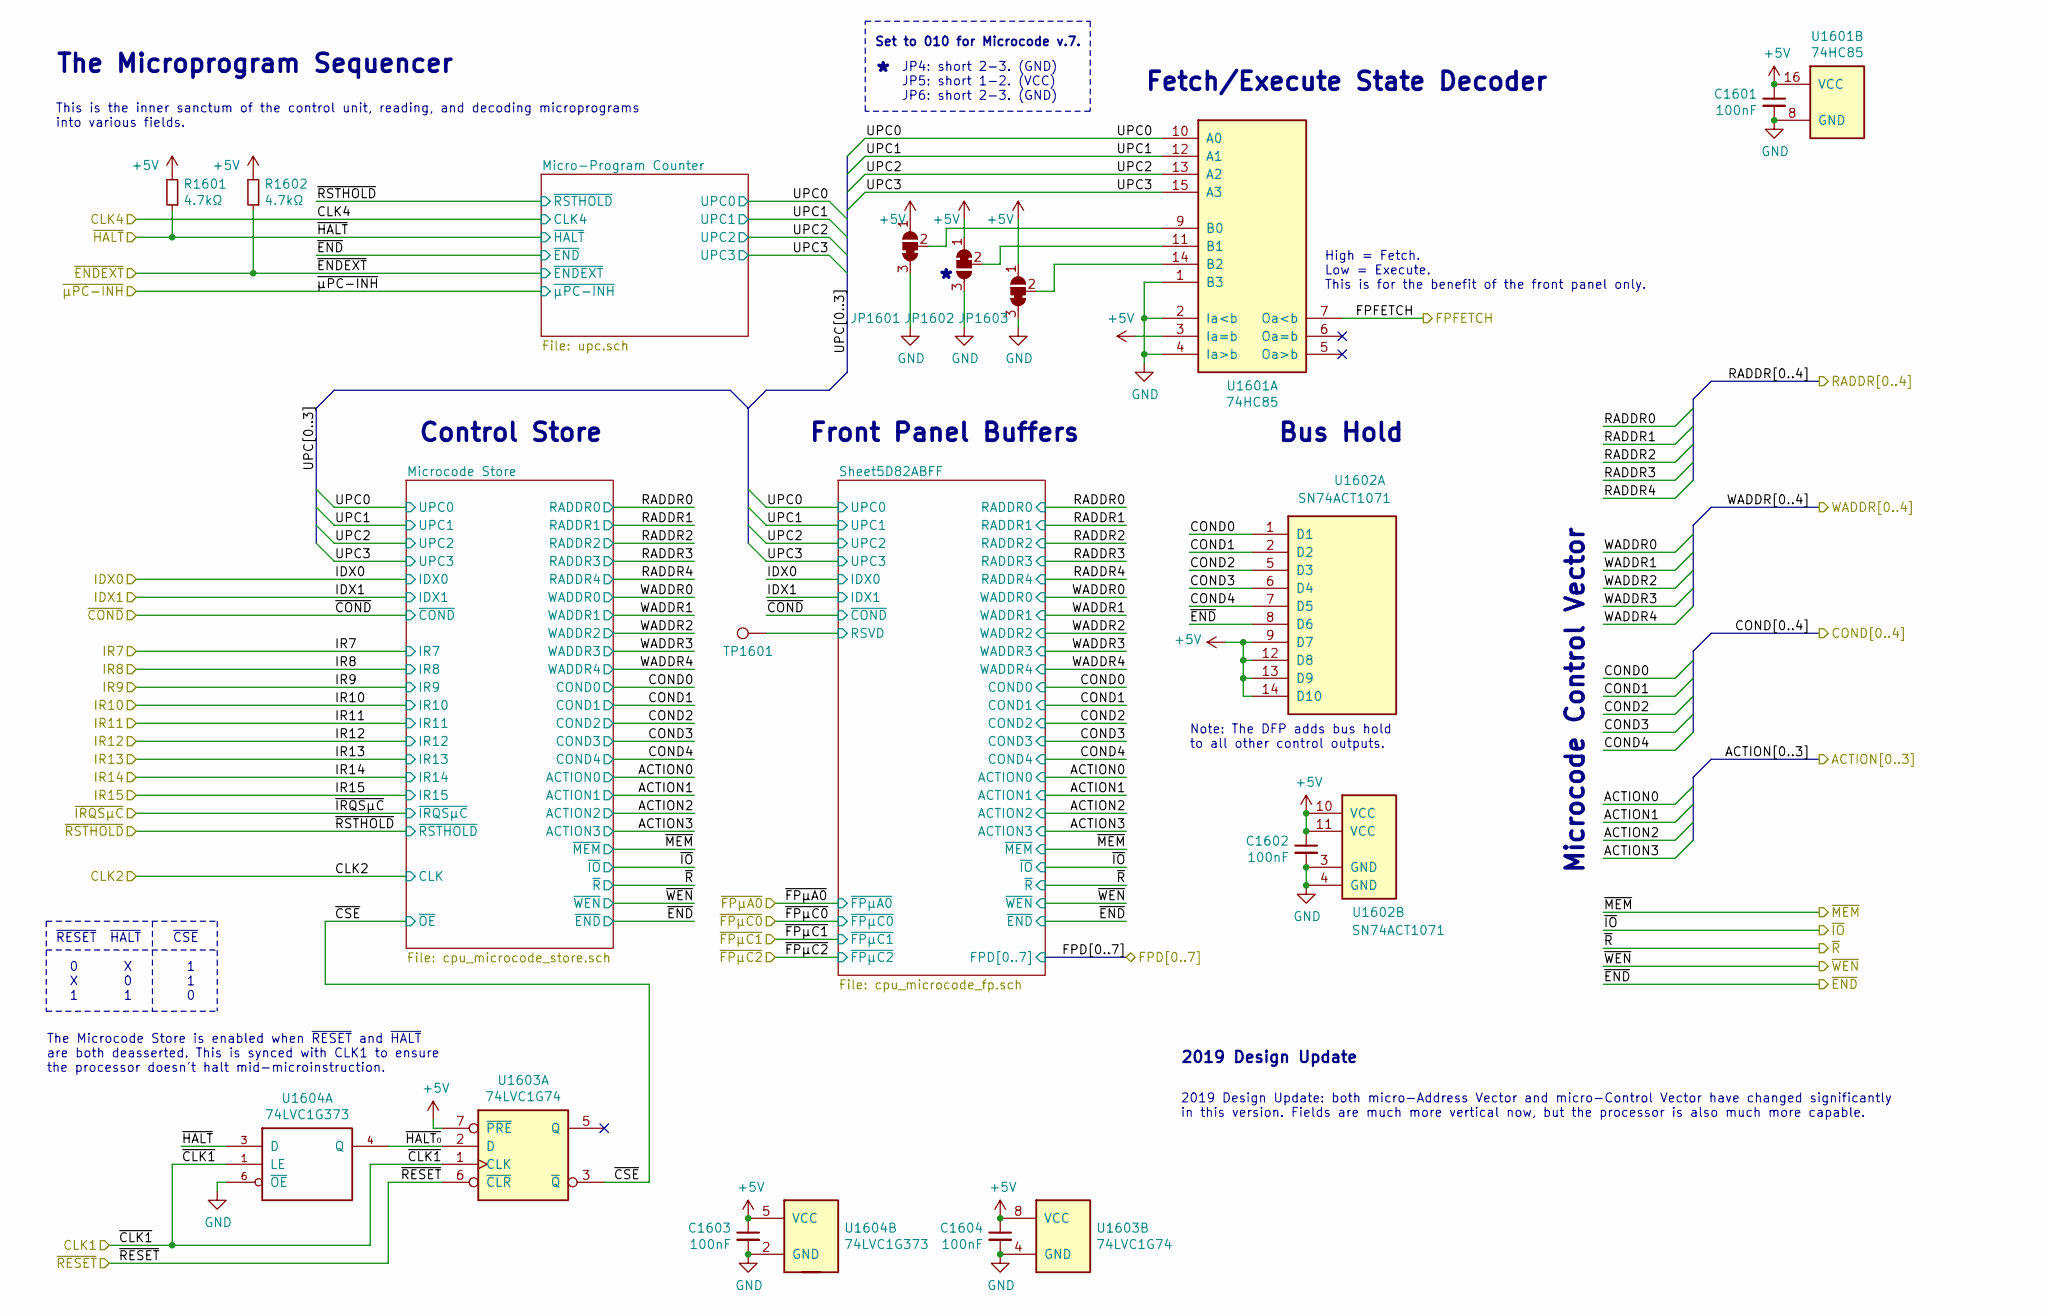
[picture p97: schematic cft_microcode.sch, Microcode Sequencer]

Parts:
C1601, C1602, C1603, C1604: 100nF; C_SMD_0805_2012Metric_Pad1.15x1.40mm_HandSolder
JP1601, JP1603: SolderJumper_3_Bridged23; SolderJumper-3_P1.3mm_Open_RoundedPad1.0x1.5mm
JP1602: SolderJumper_3_Bridged12; SolderJumper-3_P1.3mm_Open_RoundedPad1.0x1.5mm
R1601, R1602: 4.7kΩ; R_SMD_0805_2012Metric_Pad1.15x1.40mm_HandSolder
TP1601: TestPoint; TestPoint_Pad_1.0x1.0mm
U1601: 74HC85; DIP-16_W7.62mm_Socket
U1602: SN74ACT1071; SOIC-14
U1603: 74LVC1G74; TSSOP-8_3x3mm_P0.65mm
U1604: 74LVC1G373; SOT-23-6_Handsoldering

Connections:
+5V: C1601.1, C1602.1, C1603.1, C1604.1, JP1601.1 (A), JP1602.1 (A), JP1603.1 (A), R1601.2, R1602.2, U1601.3 (Ia=b), U1601.16 (VCC), U1602.9 (D7), U1602.10 (VCC), U1602.11 (VCC), U1602.12 (D8), U1602.13 (D9), U1602.14 (D10), U1603.7 (~PRE), U1603.8 (VCC), U1604.5 (VCC); also elsewhere on the board
/CLK1: U1603.1 (CLK), U1604.1 (LE); also elsewhere on the board
/COND0: U1602.1 (D1); also elsewhere on the board
/COND1: U1602.2 (D2); also elsewhere on the board
/COND2: U1602.5 (D3); also elsewhere on the board
/COND3: U1602.6 (D4); also elsewhere on the board
/COND4: U1602.7 (D5); also elsewhere on the board
/FPFETCH∕~EXEC: U1601.7 (Oa<b)
/Microprogram Sequencer/Sheet5D82ABFF/RSVD: TP1601.1; also elsewhere on the board
/Microprogram Sequencer/UPC0: U1601.10 (A0); also elsewhere on the board
/Microprogram Sequencer/UPC1: U1601.12 (A1); also elsewhere on the board
/Microprogram Sequencer/UPC2: U1601.13 (A2); also elsewhere on the board
/Microprogram Sequencer/UPC3: U1601.15 (A3); also elsewhere on the board
/Microprogram Sequencer/~CSE: U1603.3 (~Q); also elsewhere on the board
/Microprogram Sequencer/~HALT₀: U1603.2 (D), U1604.4 (Q)
/~END: U1602.8 (D6); also elsewhere on the board
/~ENDEXT: R1602.1; also elsewhere on the board
/~HALT: R1601.1, U1604.3 (D); also elsewhere on the board
/~RESET: U1603.6 (~CLR); also elsewhere on the board
GND: C1601.2, C1602.2, C1603.2, C1604.2, JP1601.3 (B), JP1602.3 (B), JP1603.3 (B), U1601.1 (B3), U1601.2 (Ia<b), U1601.4 (Ia>b), U1601.8 (GND), U1602.3 (GND), U1602.4 (GND), U1603.4 (GND), U1604.2 (GND), U1604.6 (~OE); also elsewhere on the board
unnamed: JP1601.2 (C), U1601.9 (B0)
unnamed: JP1602.2 (C), U1601.11 (B1)
unnamed: JP1603.2 (C), U1601.14 (B2)

Notes on the sheet:
2019 Design Update: both micro-Address Vector and micro-Control Vector have changed significantly in this version. Fields are much more vertical now, but the processor is also much more capable.
2019 Design Update
Microcode Control Vector
Front Panel Buffers
Control Store
Bus Hold
The Microcode Store is enabled when ~RESET~ and ~HALT~ are both deasserted. This is synced with CLK1 to ensure the processor doesn't halt mid-microinstruction.
Note: The DFP adds bus hold to all other control outputs.
~RESET~ 0 X 1
~HALT~ X 0 1
~CSE~ 1 1 0
Set to 010 for Microcode v.7.
High = Fetch. Low = Execute. This is for the benefit of the front panel only.
JP4: short 2-3. (GND) JP5: short 1-2. (VCC) JP6: short 2-3. (GND)
Fetch/Execute State Decoder
This is the inner sanctum of the control unit, reading, and decoding microprograms into various fields.
The Microprogram Sequencer
