alexiosc/cft/kicad/cft/cft-board0/cft-board0.kicad_pcb

## KiCad design kicad/cft/cft-board0/cft-board0.kicad_pcb (continued)

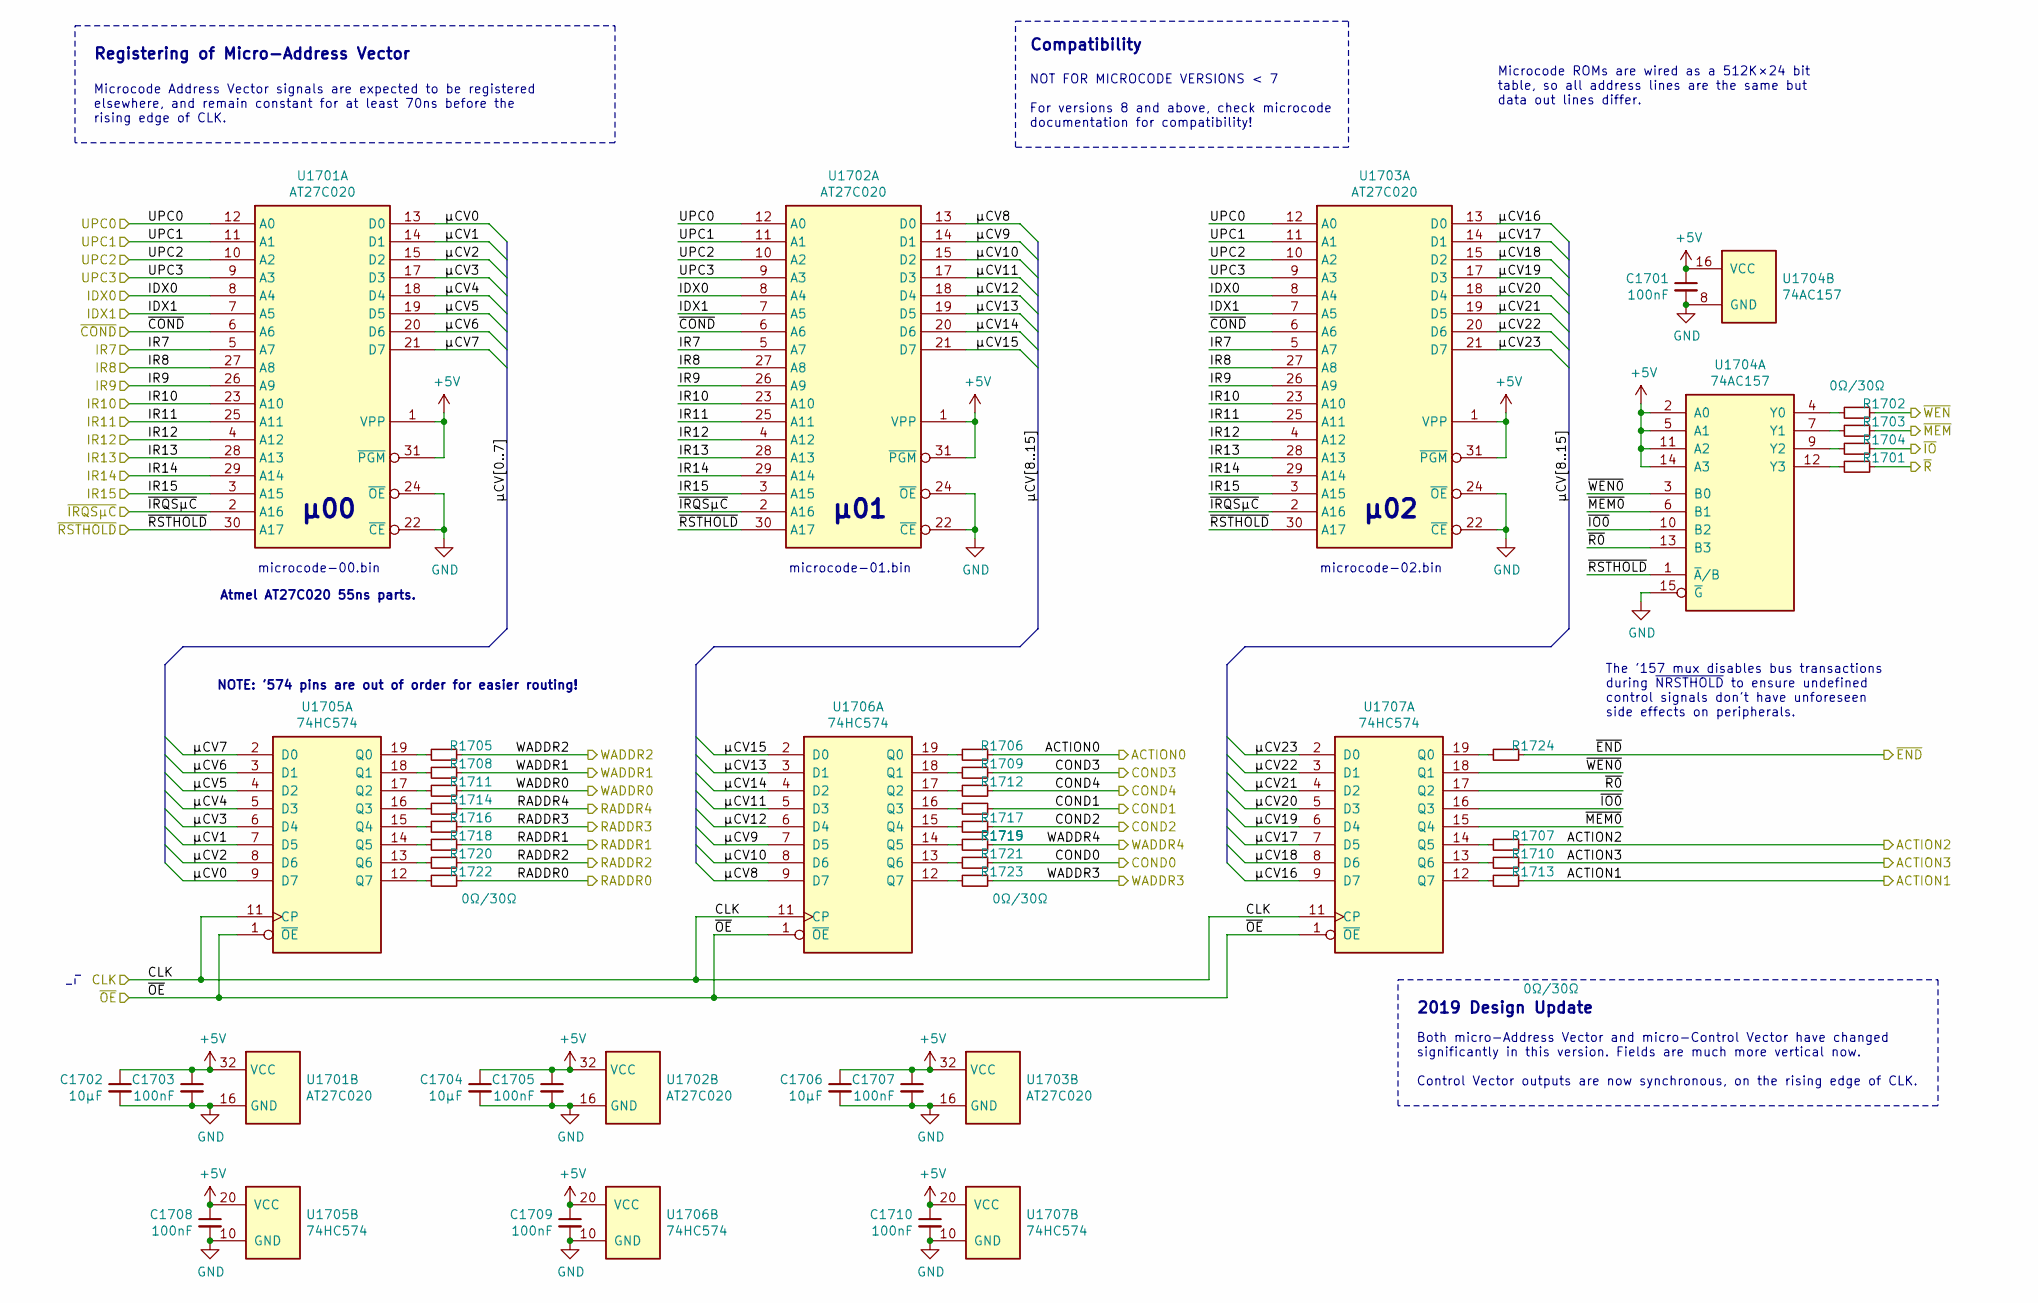
[picture p98: schematic cpu_microcode_store.sch, Control Store (24×512k ROM)]

Parts:
C1701, C1703, C1705, C1707, C1708, C1709, C1710: 100nF; C_SMD_0805_2012Metric_Pad1.15x1.40mm_HandSolder
C1702, C1704, C1706: 10µF; C_SMD_0805_2012Metric_Pad1.15x1.40mm_HandSolder
R1701, R1702, R1703, R1704, R1705, R1706, R1707, R1708, R1709, R1710, R1711, R1712, R1713, R1714, R1715, R1716, R1717, R1718, R1719, R1720, R1721, R1722, R1723, R1724: 0Ω/30Ω; R_SMD_0805_2012Metric_Pad1.15x1.40mm_HandSolder
U1701, U1702, U1703: AT27C020; PLCC32; Mouser 556-AT27C020-55JU; €3.02
U1704: 74AC157; DIP-16_W7.62mm_Socket
U1705, U1706, U1707: 74HC574; DIP-20_W7.62mm_Socket

Connections:
+5V: C1701.1, C1702.1, C1703.1, C1704.1, C1705.1, C1706.1, C1707.1, C1708.1, C1709.1, C1710.1, U1701.1 (VPP), U1701.31 (~PGM), U1701.32 (VCC), U1702.1 (VPP), U1702.31 (~PGM), U1702.32 (VCC), U1703.1 (VPP), U1703.31 (~PGM), U1703.32 (VCC), U1704.2 (A0), U1704.5 (A1), U1704.11 (A2), U1704.14 (A3), U1704.16 (VCC), U1705.20 (VCC), U1706.20 (VCC), U1707.20 (VCC); also elsewhere on the board
/ACTION0: R1706.1; also elsewhere on the board
/ACTION1: R1713.1; also elsewhere on the board
/ACTION2: R1707.1; also elsewhere on the board
/ACTION3: R1710.1; also elsewhere on the board
/CLK2: U1705.11 (CP), U1706.11 (CP), U1707.11 (CP); also elsewhere on the board
/COND0: R1721.1; also elsewhere on the board
/COND1: R1717.1; also elsewhere on the board
/COND2: R1715.1; also elsewhere on the board
/COND3: R1709.1; also elsewhere on the board
/COND4: R1712.1; also elsewhere on the board
/IDX0: U1701.8 (A4), U1702.8 (A4), U1703.8 (A4); also elsewhere on the board
/IDX1: U1701.7 (A5), U1702.7 (A5), U1703.7 (A5); also elsewhere on the board
/IR7: U1701.5 (A7), U1702.5 (A7), U1703.5 (A7); also elsewhere on the board
/IR8: U1701.27 (A8), U1702.27 (A8), U1703.27 (A8); also elsewhere on the board
/IR9: U1701.26 (A9), U1702.26 (A9), U1703.26 (A9); also elsewhere on the board
/IR10: U1701.23 (A10), U1702.23 (A10), U1703.23 (A10); also elsewhere on the board
/IR11: U1701.25 (A11), U1702.25 (A11), U1703.25 (A11); also elsewhere on the board
/IR12: U1701.4 (A12), U1702.4 (A12), U1703.4 (A12); also elsewhere on the board
/IR13: U1701.28 (A13), U1702.28 (A13), U1703.28 (A13); also elsewhere on the board
/IR14: U1701.29 (A14), U1702.29 (A14), U1703.29 (A14); also elsewhere on the board
/IR15: U1701.3 (A15), U1702.3 (A15), U1703.3 (A15); also elsewhere on the board
/Microprogram Sequencer/Microcode Store/~IO0: U1704.10 (B2), U1707.16 (Q3)
/Microprogram Sequencer/Microcode Store/~MEM0: U1704.6 (B1), U1707.15 (Q4)
/Microprogram Sequencer/Microcode Store/~R0: U1704.13 (B3), U1707.17 (Q2)
/Microprogram Sequencer/Microcode Store/~WEN0: U1704.3 (B0), U1707.18 (Q1)
/Microprogram Sequencer/Microcode Store/µCV0: U1701.13 (D0), U1705.9 (D7)
/Microprogram Sequencer/Microcode Store/µCV1: U1701.14 (D1), U1705.7 (D5)
/Microprogram Sequencer/Microcode Store/µCV2: U1701.15 (D2), U1705.8 (D6)
/Microprogram Sequencer/Microcode Store/µCV3: U1701.17 (D3), U1705.6 (D4)
/Microprogram Sequencer/Microcode Store/µCV4: U1701.18 (D4), U1705.5 (D3)
/Microprogram Sequencer/Microcode Store/µCV5: U1701.19 (D5), U1705.4 (D2)
/Microprogram Sequencer/Microcode Store/µCV6: U1701.20 (D6), U1705.3 (D1)
/Microprogram Sequencer/Microcode Store/µCV7: U1701.21 (D7), U1705.2 (D0)
/Microprogram Sequencer/Microcode Store/µCV8: U1702.13 (D0), U1706.9 (D7)
/Microprogram Sequencer/Microcode Store/µCV9: U1702.14 (D1), U1706.7 (D5)
/Microprogram Sequencer/Microcode Store/µCV10: U1702.15 (D2), U1706.8 (D6)
/Microprogram Sequencer/Microcode Store/µCV11: U1702.17 (D3), U1706.5 (D3)
/Microprogram Sequencer/Microcode Store/µCV12: U1702.18 (D4), U1706.6 (D4)
/Microprogram Sequencer/Microcode Store/µCV13: U1702.19 (D5), U1706.3 (D1)
/Microprogram Sequencer/Microcode Store/µCV14: U1702.20 (D6), U1706.4 (D2)
/Microprogram Sequencer/Microcode Store/µCV15: U1702.21 (D7), U1706.2 (D0)
/Microprogram Sequencer/Microcode Store/µCV16: U1703.13 (D0), U1707.9 (D7)
/Microprogram Sequencer/Microcode Store/µCV17: U1703.14 (D1), U1707.7 (D5)
/Microprogram Sequencer/Microcode Store/µCV18: U1703.15 (D2), U1707.8 (D6)
/Microprogram Sequencer/Microcode Store/µCV19: U1703.17 (D3), U1707.6 (D4)
/Microprogram Sequencer/Microcode Store/µCV20: U1703.18 (D4), U1707.5 (D3)
/Microprogram Sequencer/Microcode Store/µCV21: U1703.19 (D5), U1707.4 (D2)
/Microprogram Sequencer/Microcode Store/µCV22: U1703.20 (D6), U1707.3 (D1)
/Microprogram Sequencer/Microcode Store/µCV23: U1703.21 (D7), U1707.2 (D0)
/Microprogram Sequencer/UPC0: U1701.12 (A0), U1702.12 (A0), U1703.12 (A0); also elsewhere on the board
/Microprogram Sequencer/UPC1: U1701.11 (A1), U1702.11 (A1), U1703.11 (A1); also elsewhere on the board
/Microprogram Sequencer/UPC2: U1701.10 (A2), U1702.10 (A2), U1703.10 (A2); also elsewhere on the board
/Microprogram Sequencer/UPC3: U1701.9 (A3), U1702.9 (A3), U1703.9 (A3); also elsewhere on the board
/Microprogram Sequencer/~CSE: U1705.1 (~OE), U1706.1 (~OE), U1707.1 (~OE); also elsewhere on the board
/RADDR0: R1722.1; also elsewhere on the board
/RADDR1: R1718.1; also elsewhere on the board
/RADDR2: R1720.1; also elsewhere on the board
/RADDR3: R1716.1; also elsewhere on the board
/RADDR4: R1714.1; also elsewhere on the board
/WADDR0: R1711.1; also elsewhere on the board
/WADDR1: R1708.1; also elsewhere on the board
/WADDR2: R1705.1; also elsewhere on the board
/WADDR3: R1723.1; also elsewhere on the board
/WADDR4: R1719.1; also elsewhere on the board
/~COND: U1701.6 (A6), U1702.6 (A6), U1703.6 (A6); also elsewhere on the board
/~END: R1724.1; also elsewhere on the board
/~IO: R1704.1; also elsewhere on the board
/~IRQSµC: U1701.2 (A16), U1702.2 (A16), U1703.2 (A16); also elsewhere on the board
/~MEM: R1703.1; also elsewhere on the board
/~R: R1701.1; also elsewhere on the board
/~RSTHOLD: U1701.30 (A17), U1702.30 (A17), U1703.30 (A17), U1704.1 (~A~/B); also elsewhere on the board
/~WEN: R1702.1; also elsewhere on the board
GND: C1701.2, C1702.2, C1703.2, C1704.2, C1705.2, C1706.2, C1707.2, C1708.2, C1709.2, C1710.2, U1701.16 (GND), U1701.22 (~CE), U1701.24 (~OE), U1702.16 (GND), U1702.22 (~CE), U1702.24 (~OE), U1703.16 (GND), U1703.22 (~CE), U1703.24 (~OE), U1704.8 (GND), U1704.15 (~G), U1705.10 (GND), U1706.10 (GND), U1707.10 (GND); also elsewhere on the board
unnamed: R1701.2, U1704.12 (Y3)
unnamed: R1702.2, U1704.4 (Y0)
unnamed: R1703.2, U1704.7 (Y1)
unnamed: R1704.2, U1704.9 (Y2)
unnamed: R1705.2, U1705.19 (Q0)
unnamed: R1706.2, U1706.19 (Q0)
unnamed: R1707.2, U1707.14 (Q5)
unnamed: R1708.2, U1705.18 (Q1)
unnamed: R1709.2, U1706.18 (Q1)
unnamed: R1710.2, U1707.13 (Q6)
unnamed: R1711.2, U1705.17 (Q2)
unnamed: R1712.2, U1706.17 (Q2)
unnamed: R1713.2, U1707.12 (Q7)
unnamed: R1714.2, U1705.16 (Q3)
unnamed: R1715.2, U1706.15 (Q4)
unnamed: R1716.2, U1705.15 (Q4)
unnamed: R1717.2, U1706.16 (Q3)
unnamed: R1718.2, U1705.14 (Q5)
unnamed: R1719.2, U1706.14 (Q5)
unnamed: R1720.2, U1705.13 (Q6)
unnamed: R1721.2, U1706.13 (Q6)
unnamed: R1722.2, U1705.12 (Q7)
unnamed: R1723.2, U1706.12 (Q7)
unnamed: R1724.2, U1707.19 (Q0)

Notes on the sheet:
Microcode ROMs are wired as a 512K×24 bit table, so all address lines are the same but data out lines differ.
Both micro-Address Vector and micro-Control Vector have changed significantly in this version. Fields are much more vertical now. Control Vector outputs are now synchronous, on the rising edge of CLK.
2019 Design Update
µ00
µ02
µ01
Microcode Address Vector signals are expected to be registered elsewhere, and remain constant for at least 70ns before the rising edge of CLK.
Registering of Micro-Address Vector
microcode-00.bin
microcode-01.bin
microcode-02.bin
NOT FOR MICROCODE VERSIONS < 7 For versions 8 and above, check microcode documentation for compatibility!
Compatibility
The '157 mux disables bus transactions during ~NRSTHOLD~ to ensure undefined control signals don't have unforeseen side effects on peripherals.
Atmel AT27C020 55ns parts.
NOTE: '574 pins are out of order for easier routing!

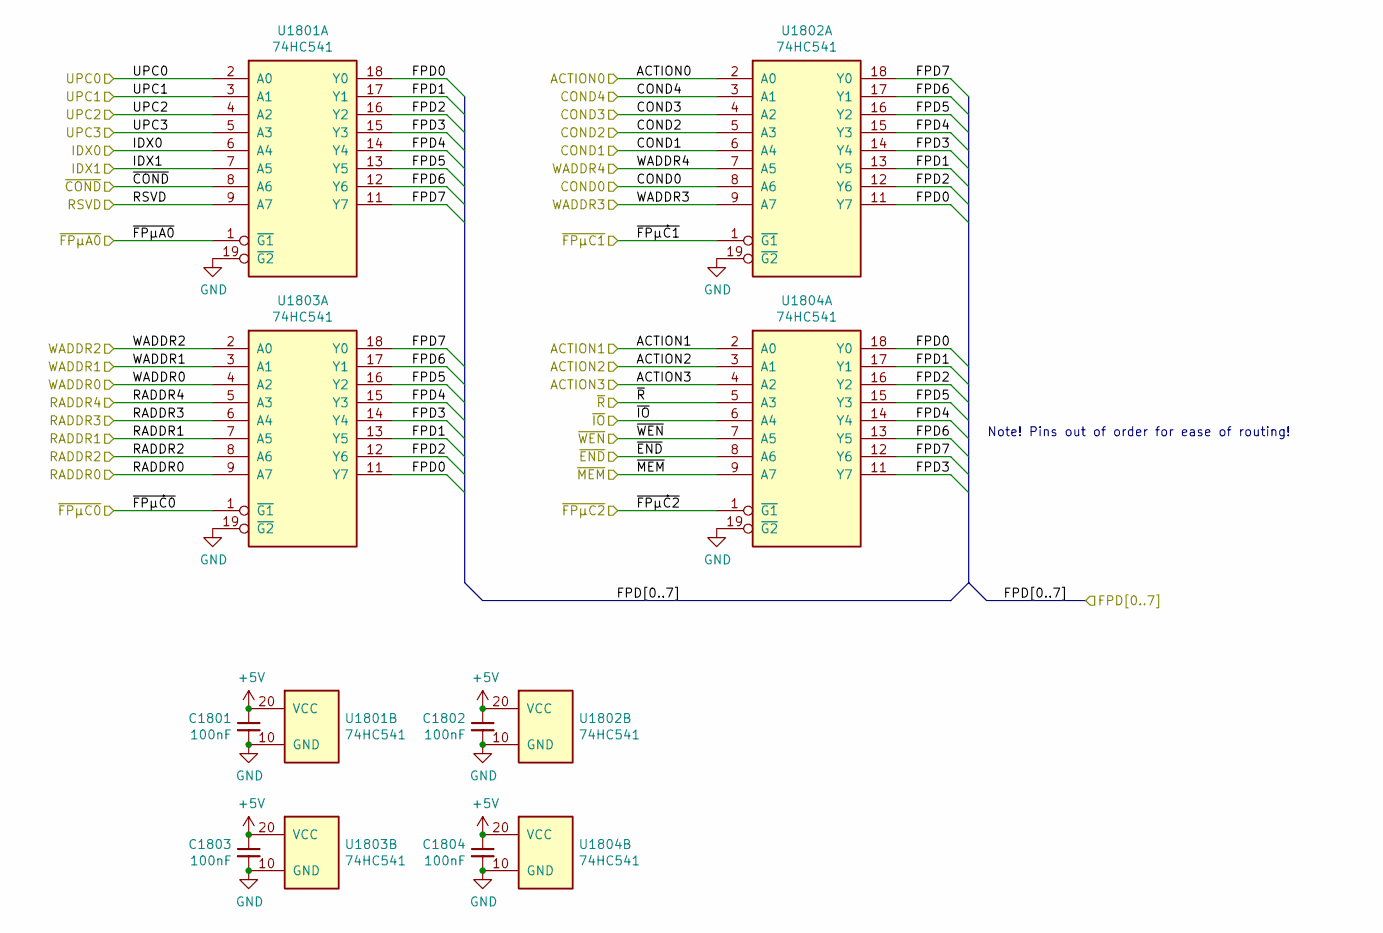
[picture p99: schematic cpu_microcode_fp.sch, Microcode Front Panel Buffers]

Parts:
C1801, C1802, C1803, C1804: 100nF; C_SMD_0805_2012Metric_Pad1.15x1.40mm_HandSolder
U1801, U1802, U1803, U1804: 74HC541; DIP-20_W7.62mm_Socket

Connections:
+5V: C1801.1, C1802.1, C1803.1, C1804.1, U1801.20 (VCC), U1802.20 (VCC), U1803.20 (VCC), U1804.20 (VCC); also elsewhere on the board
/ACTION0: U1802.2 (A0); also elsewhere on the board
/ACTION1: U1804.2 (A0); also elsewhere on the board
/ACTION2: U1804.3 (A1); also elsewhere on the board
/ACTION3: U1804.4 (A2); also elsewhere on the board
/COND0: U1802.8 (A6); also elsewhere on the board
/COND1: U1802.6 (A4); also elsewhere on the board
/COND2: U1802.5 (A3); also elsewhere on the board
/COND3: U1802.4 (A2); also elsewhere on the board
/COND4: U1802.3 (A1); also elsewhere on the board
/FPD0: U1801.18 (Y0), U1802.11 (Y7), U1803.11 (Y7), U1804.18 (Y0); also elsewhere on the board
/FPD1: U1801.17 (Y1), U1802.13 (Y5), U1803.13 (Y5), U1804.17 (Y1); also elsewhere on the board
/FPD2: U1801.16 (Y2), U1802.12 (Y6), U1803.12 (Y6), U1804.16 (Y2); also elsewhere on the board
/FPD3: U1801.15 (Y3), U1802.14 (Y4), U1803.14 (Y4), U1804.11 (Y7); also elsewhere on the board
/FPD4: U1801.14 (Y4), U1802.15 (Y3), U1803.15 (Y3), U1804.14 (Y4); also elsewhere on the board
/FPD5: U1801.13 (Y5), U1802.16 (Y2), U1803.16 (Y2), U1804.15 (Y3); also elsewhere on the board
/FPD6: U1801.12 (Y6), U1802.17 (Y1), U1803.17 (Y1), U1804.13 (Y5); also elsewhere on the board
/FPD7: U1801.11 (Y7), U1802.18 (Y0), U1803.18 (Y0), U1804.12 (Y6); also elsewhere on the board
/IDX0: U1801.6 (A4); also elsewhere on the board
/IDX1: U1801.7 (A5); also elsewhere on the board
/Microprogram Sequencer/Sheet5D82ABFF/RSVD: U1801.9 (A7); also elsewhere on the board
/Microprogram Sequencer/UPC0: U1801.2 (A0); also elsewhere on the board
/Microprogram Sequencer/UPC1: U1801.3 (A1); also elsewhere on the board
/Microprogram Sequencer/UPC2: U1801.4 (A2); also elsewhere on the board
/Microprogram Sequencer/UPC3: U1801.5 (A3); also elsewhere on the board
/RADDR0: U1803.9 (A7); also elsewhere on the board
/RADDR1: U1803.7 (A5); also elsewhere on the board
/RADDR2: U1803.8 (A6); also elsewhere on the board
/RADDR3: U1803.6 (A4); also elsewhere on the board
/RADDR4: U1803.5 (A3); also elsewhere on the board
/WADDR0: U1803.4 (A2); also elsewhere on the board
/WADDR1: U1803.3 (A1); also elsewhere on the board
/WADDR2: U1803.2 (A0); also elsewhere on the board
/WADDR3: U1802.9 (A7); also elsewhere on the board
/WADDR4: U1802.7 (A5); also elsewhere on the board
/~COND: U1801.8 (A6); also elsewhere on the board
/~END: U1804.8 (A6); also elsewhere on the board
/~FPµA0: U1801.1 (~G1)
/~FPµC0: U1803.1 (~G1)
/~FPµC1: U1802.1 (~G1)
/~FPµC2: U1804.1 (~G1)
/~IO: U1804.6 (A4); also elsewhere on the board
/~MEM: U1804.9 (A7); also elsewhere on the board
/~R: U1804.5 (A3); also elsewhere on the board
/~WEN: U1804.7 (A5); also elsewhere on the board
GND: C1801.2, C1802.2, C1803.2, C1804.2, U1801.10 (GND), U1801.19 (~G2), U1802.10 (GND), U1802.19 (~G2), U1803.10 (GND), U1803.19 (~G2), U1804.10 (GND), U1804.19 (~G2); also elsewhere on the board

Notes on the sheet:
Note! Pins out of order for ease of routing!

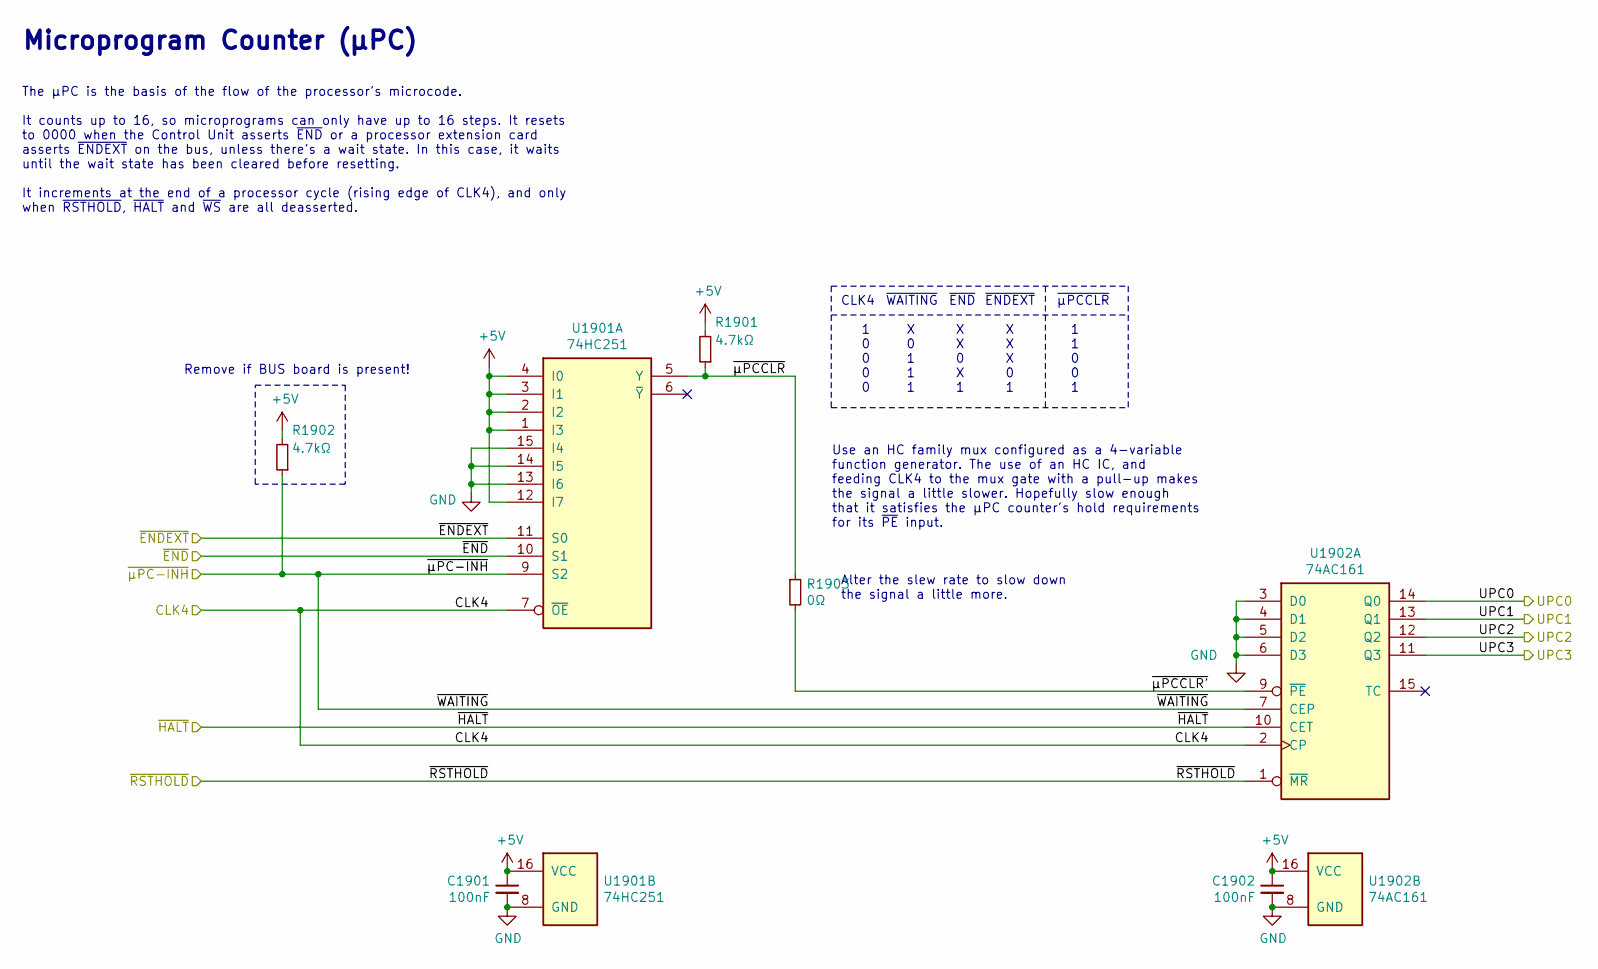
[picture p100: schematic upc.sch, Microprogram Counter]

Parts:
C1901, C1902: 100nF; C_SMD_0805_2012Metric_Pad1.15x1.40mm_HandSolder
R1901, R1902: 4.7kΩ; R_SMD_0805_2012Metric_Pad1.15x1.40mm_HandSolder
R1903: 0Ω; R_SMD_0805_2012Metric_Pad1.15x1.40mm_HandSolder
U1901: 74HC251; DIP-16_W7.62mm_Socket
U1902: 74AC161; DIP-16_W7.62mm_Socket

Connections:
+5V: C1901.1, C1902.1, R1901.2, R1902.2, U1901.1 (I3), U1901.2 (I2), U1901.3 (I1), U1901.4 (I0), U1901.12 (I7), U1901.16 (VCC), U1902.16 (VCC); also elsewhere on the board
/CLK4: U1901.7 (~OE), U1902.2 (CP); also elsewhere on the board
/Microprogram Sequencer/Micro-Program Counter/~µPCCLR: R1901.1, R1903.1, U1901.5 (Y)
/Microprogram Sequencer/Micro-Program Counter/~µPCCLR': R1903.2, U1902.9 (~PE)
/Microprogram Sequencer/UPC0: U1902.14 (Q0); also elsewhere on the board
/Microprogram Sequencer/UPC1: U1902.13 (Q1); also elsewhere on the board
/Microprogram Sequencer/UPC2: U1902.12 (Q2); also elsewhere on the board
/Microprogram Sequencer/UPC3: U1902.11 (Q3); also elsewhere on the board
/~END: U1901.10 (S1); also elsewhere on the board
/~ENDEXT: U1901.11 (S0); also elsewhere on the board
/~HALT: U1902.10 (CET); also elsewhere on the board
/~RSTHOLD: U1902.1 (~MR); also elsewhere on the board
/~µPC-INH: R1902.1, U1901.9 (S2), U1902.7 (CEP); also elsewhere on the board
GND: C1901.2, C1902.2, U1901.8 (GND), U1901.13 (I6), U1901.14 (I5), U1901.15 (I4), U1902.3 (D0), U1902.4 (D1), U1902.5 (D2), U1902.6 (D3), U1902.8 (GND); also elsewhere on the board

Notes on the sheet:
Remove if BUS board is present!
~WAITING~ X 0 1 1 1
~END~ X X 0 X 1
~ENDEXT~ X X X 0 1
CLK4 1 0 0 0 0
Use an HC family mux configured as a 4-variable function generator. The use of an HC IC, and feeding CLK4 to the mux gate with a pull-up makes the signal a little slower. Hopefully slow enough that it satisfies the µPC counter's hold requirements for its ~PE~ input.
Alter the slew rate to slow down the signal a little more.
The µPC is the basis of the flow of the processor's microcode. It counts up to 16, so microprograms can only have up to 16 steps. It resets to 0000 when the Control Unit asserts ~END~ or a processor extension card asserts ~ENDEXT~ on the bus, unless there's a wait state. In this case, it waits unti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
Microprogram Counter (µPC)
~µPCCLR~ 1 1 0 0 1

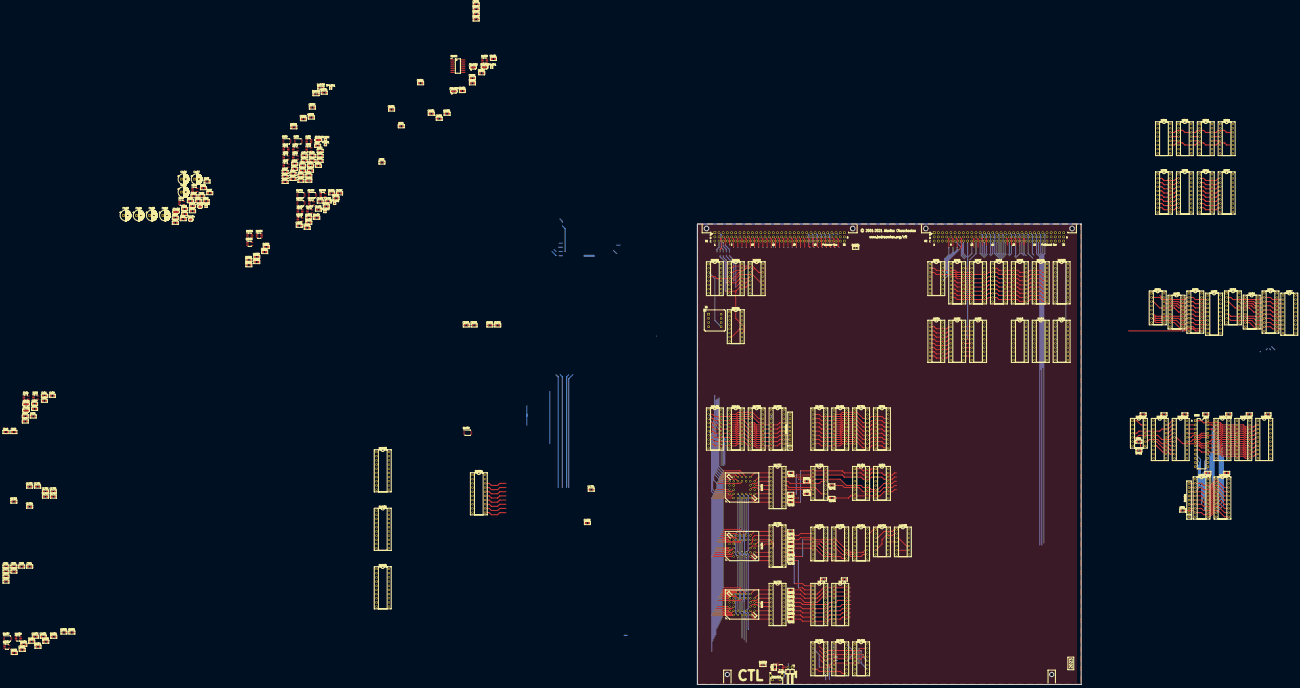
[picture p101: board cft-board0.kicad_pcb from above]

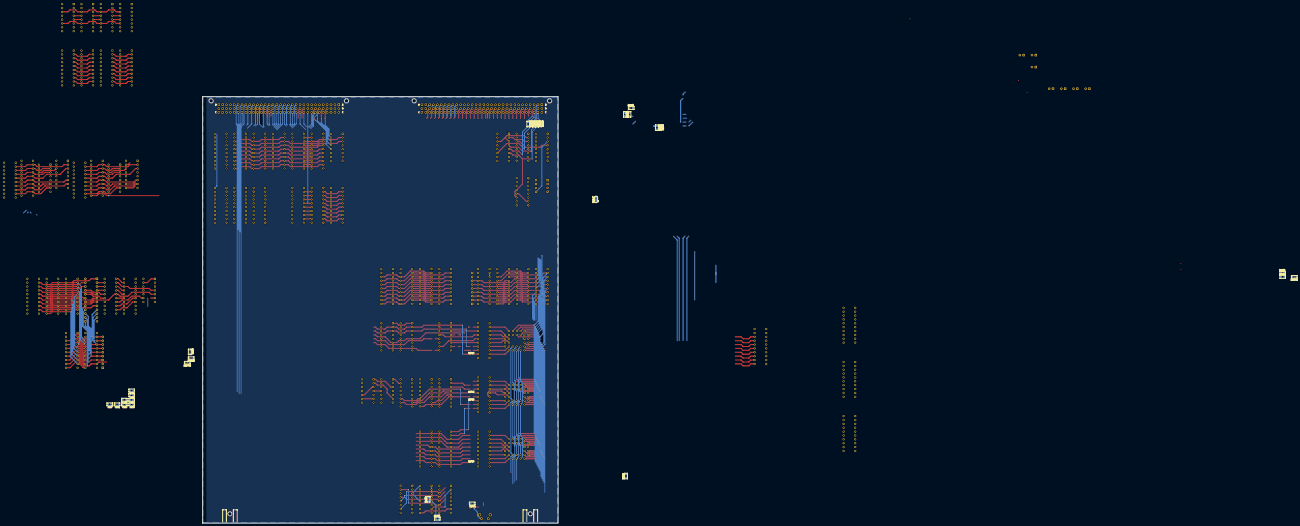
[picture p102: board cft-board0.kicad_pcb from below]

Board: 2 copper layers, 233.4 x 280.0 mm, 327 parts (29 on the bottom side), 386 nets.
