alexiosc/cft/kicad/cft/sri/sri.kicad_pcb

## KiCad design kicad/cft/sri/sri.kicad_pcb (2020-12-05)

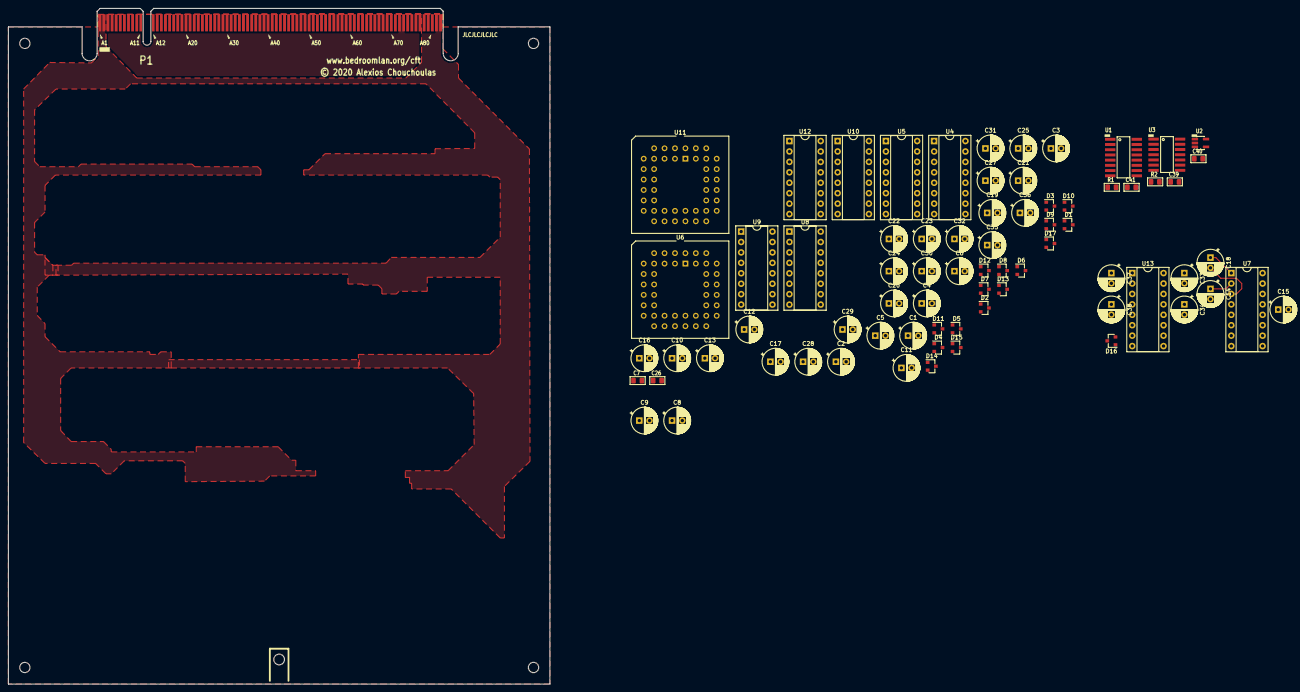
[picture p103: board sri.kicad_pcb from above]

Board: 2 copper layers, 131.9 x 164.6 mm, 74 parts (0 on the bottom side), 130 nets.

Parts:
C1, C2, C5, C6, C14, C15, C16, C17, C22, C23, C24, C25, C31, C32, C33, C34: 10μF; CP_Radial_D6.3mm_P2.50mm
C3, C4, C8, C9: 47µF; CP_Radial_D6.3mm_P2.50mm
C7, C26: C_Small; C_SMD_0805_2012Metric_Pad1.15x1.40mm_HandSolder
C10, C11, C12, C13, C18, C19, C20, C21, C27, C28, C29, C30, C35, C36, C37, C38: 1μF; CP_Radial_D6.3mm_P2.50mm
C39, C40, C41: 100nF; C_SMD_0805_2012Metric_Pad1.15x1.40mm_HandSolder
D1, D2, D3, D4, D5, D6, D7, D8, D9, D10, D11, D12, D13, D14, D15, D16, D17: PESD15VS2UT; SOT-23
P1: CFT-2019-Bus; CFT-2019-Card-Edge
R1, R2: 30Ω; R_SMD_0805_2012Metric_Pad1.15x1.40mm_HandSolder
U1: 74HC138; SOIC-16
U2: 74LVC1G04; SOT-23-5_HandSoldering
U3: 74HC32; SOIC-14
U4, U5, U7, U8, U9, U10, U12, U13: MAX232; DIP-16_W7.62mm_Socket
U6, U11: 16C2550; PLCC-44_THT-Socket

Connections:
+5V: C1.2, C3.1, C4.1, C5.2, C7.1, C8.1, C9.1, C14.2, C16.2, C22.2, C24.2, C26.1, C31.2, C33.2, C39.1, C40.1, C41.1, P1.A1, P1.A2, P1.A81, P1.A82, U1.16, U2.5, U3.14, U4.16, U5.16, U6.44, U7.16, U8.16, U9.16, U10.16, U11.44, U12.16, U13.16
/A0: U6.31, U11.31
/A1: U6.30, U11.30
/A2: U6.29, U11.29
/AB3: P1.A10, U1.1
/AB4: P1.A11, U1.2
/AB5: P1.A12, U1.3
/AB6: P1.A13, U2.2
/AB7: P1.A14, U1.5
/Bus Interface/~AB6: U1.6, U2.4
/D0: U6.2, U11.2
/D1: U6.3, U11.3
/D2: U6.4, U11.4
/D3: U6.5, U11.5
/D4: U6.6, U11.6
/D5: U6.7, U11.7
/D6: U6.8, U11.8
/D7: U6.9, U11.9
/RESET: U6.39, U11.39
/RX0: U4.12, U6.11
/RX1: U6.10, U7.12
/RX2: U9.11, U9.12, U11.11
/RX3: U11.10, U12.11, U12.12
/TX0: U4.11, U6.13
/TX1: U6.14, U7.11
/~CD0: U5.9, U6.42
/~CD1: U6.21, U8.9
/~CD2: U10.9, U11.42
/~CD3: U11.21, U13.9
/~CSTTY0: U1.15, U6.16
/~CSTTY1: U1.14, U6.17
/~CSTTY2: U1.13, U11.16
/~CSTTY3: U1.12, U11.17
/~CTS0: U4.9, U6.40
/~CTS1: U6.28, U7.9
/~CTS2: U9.9, U11.40
/~CTS3: U11.28, U12.9
/~DSR0: U5.12, U6.41
/~DSR1: U6.25, U8.12
/~DSR2: U10.12, U11.41
/~DSR3: U11.25, U13.12
/~DTR0: U5.11, U6.37
/~DTR1: U6.38, U8.11
/~DTR2: U10.11, U11.37
/~DTR3: U11.38, U13.11
/~IODEV1xx: P1.A24, U1.4, U3.1, U3.9
/~IOR: R1.1, U6.24, U11.24
/~IOW: R2.1, U6.20, U11.20
/~R: P1.A27, U3.2
/~RTS0: U4.10, U6.36
/~RTS1: U6.27, U7.10
/~RTS2: U9.10, U11.36
/~RTS3: U11.27, U12.10
/~W: P1.A28, U3.10
GND: C2.1, C3.2, C4.2, C6.1, C7.2, C8.2, C9.2, C15.1, C17.1, C23.1, C25.1, C26.2, C32.1, C34.1, C39.2, C40.2, C41.2, P1.A72, P1.A73, P1.B1, P1.B2, P1.B81, P1.B82, U1.8, U2.3, U3.7, U4.15, U5.15, U6.22, U7.15, U8.15, U9.15, U10.15, U11.22, U12.15, U13.15
unnamed: C1.1, U4.2
unnamed: C2.2, U4.6
unnamed: C5.1, U5.2
unnamed: C6.2, U5.6
unnamed: C10.1, U4.1
unnamed: C10.2, U4.3
unnamed: C11.1, U4.4
unnamed: C11.2, U4.5
unnamed: C12.1, U5.1
unnamed: C12.2, U5.3
unnamed: C13.1, U5.4
unnamed: C13.2, U5.5
unnamed: C14.1, U7.2
unnamed: C15.2, U7.6
unnamed: C16.1, U8.2
unnamed: C17.2, U8.6
unnamed: C18.1, U7.1
unnamed: C18.2, U7.3
unnamed: C19.1, U7.4
unnamed: C19.2, U7.5
unnamed: C20.1, U8.1
unnamed: C20.2, U8.3
unnamed: C21.1, U8.4
unnamed: C21.2, U8.5
unnamed: C22.1, U9.2
unnamed: C23.2, U9.6
unnamed: C24.1, U10.2
unnamed: C25.2, U10.6
unnamed: C27.1, U9.1
unnamed: C27.2, U9.3
unnamed: C28.1, U9.4
unnamed: C28.2, U9.5
unnamed: C29.1, U10.1
unnamed: C29.2, U10.3
unnamed: C30.1, U10.4
unnamed: C30.2, U10.5
unnamed: C31.1, U12.2
unnamed: C32.2, U12.6
unnamed: C33.1, U13.2
unnamed: C34.2, U13.6
unnamed: C35.1, U12.1
unnamed: C35.2, U12.3
unnamed: C36.1, U12.4
unnamed: C36.2, U12.5
unnamed: C37.1, U13.1
unnamed: C37.2, U13.3
unnamed: C38.1, U13.4
unnamed: C38.2, U13.5
unnamed: D2.1, U4.8
unnamed: D3.1, U4.7
unnamed: D3.2, U4.14
unnamed: D4.1, U5.8
unnamed: D4.2, U5.13
unnamed: D5.2, U5.14
unnamed: D6.1, U7.8
unnamed: D7.1, U7.7
unnamed: D7.2, U7.14
unnamed: D8.1, U8.8
unnamed: D9.2, U8.14
unnamed: D10.1, U9.8
unnamed: D11.1, U9.7
unnamed: D11.2, U9.14
unnamed: D12.1, U10.8
unnamed: D13.2, U10.14
unnamed: D14.1, U12.8
unnamed: D14.2, U12.13
unnamed: D15.1, U12.7
unnamed: D15.2, U12.14
unnamed: D16.1, U13.8
unnamed: D16.2, U13.13
unnamed: D17.2, U13.14
unnamed: R1.2, U3.6
unnamed: R2.2, U3.11
unnamed: U3.3, U3.4, U3.5
unnamed: U3.8, U3.12, U3.13
