alexiosc/cft/kicad/cft/cft-front-panel/cft-front-panel.kicad_pcb

## KiCad design kicad/cft/cft-front-panel/cft-front-panel.kicad_pcb (2020-10-14)

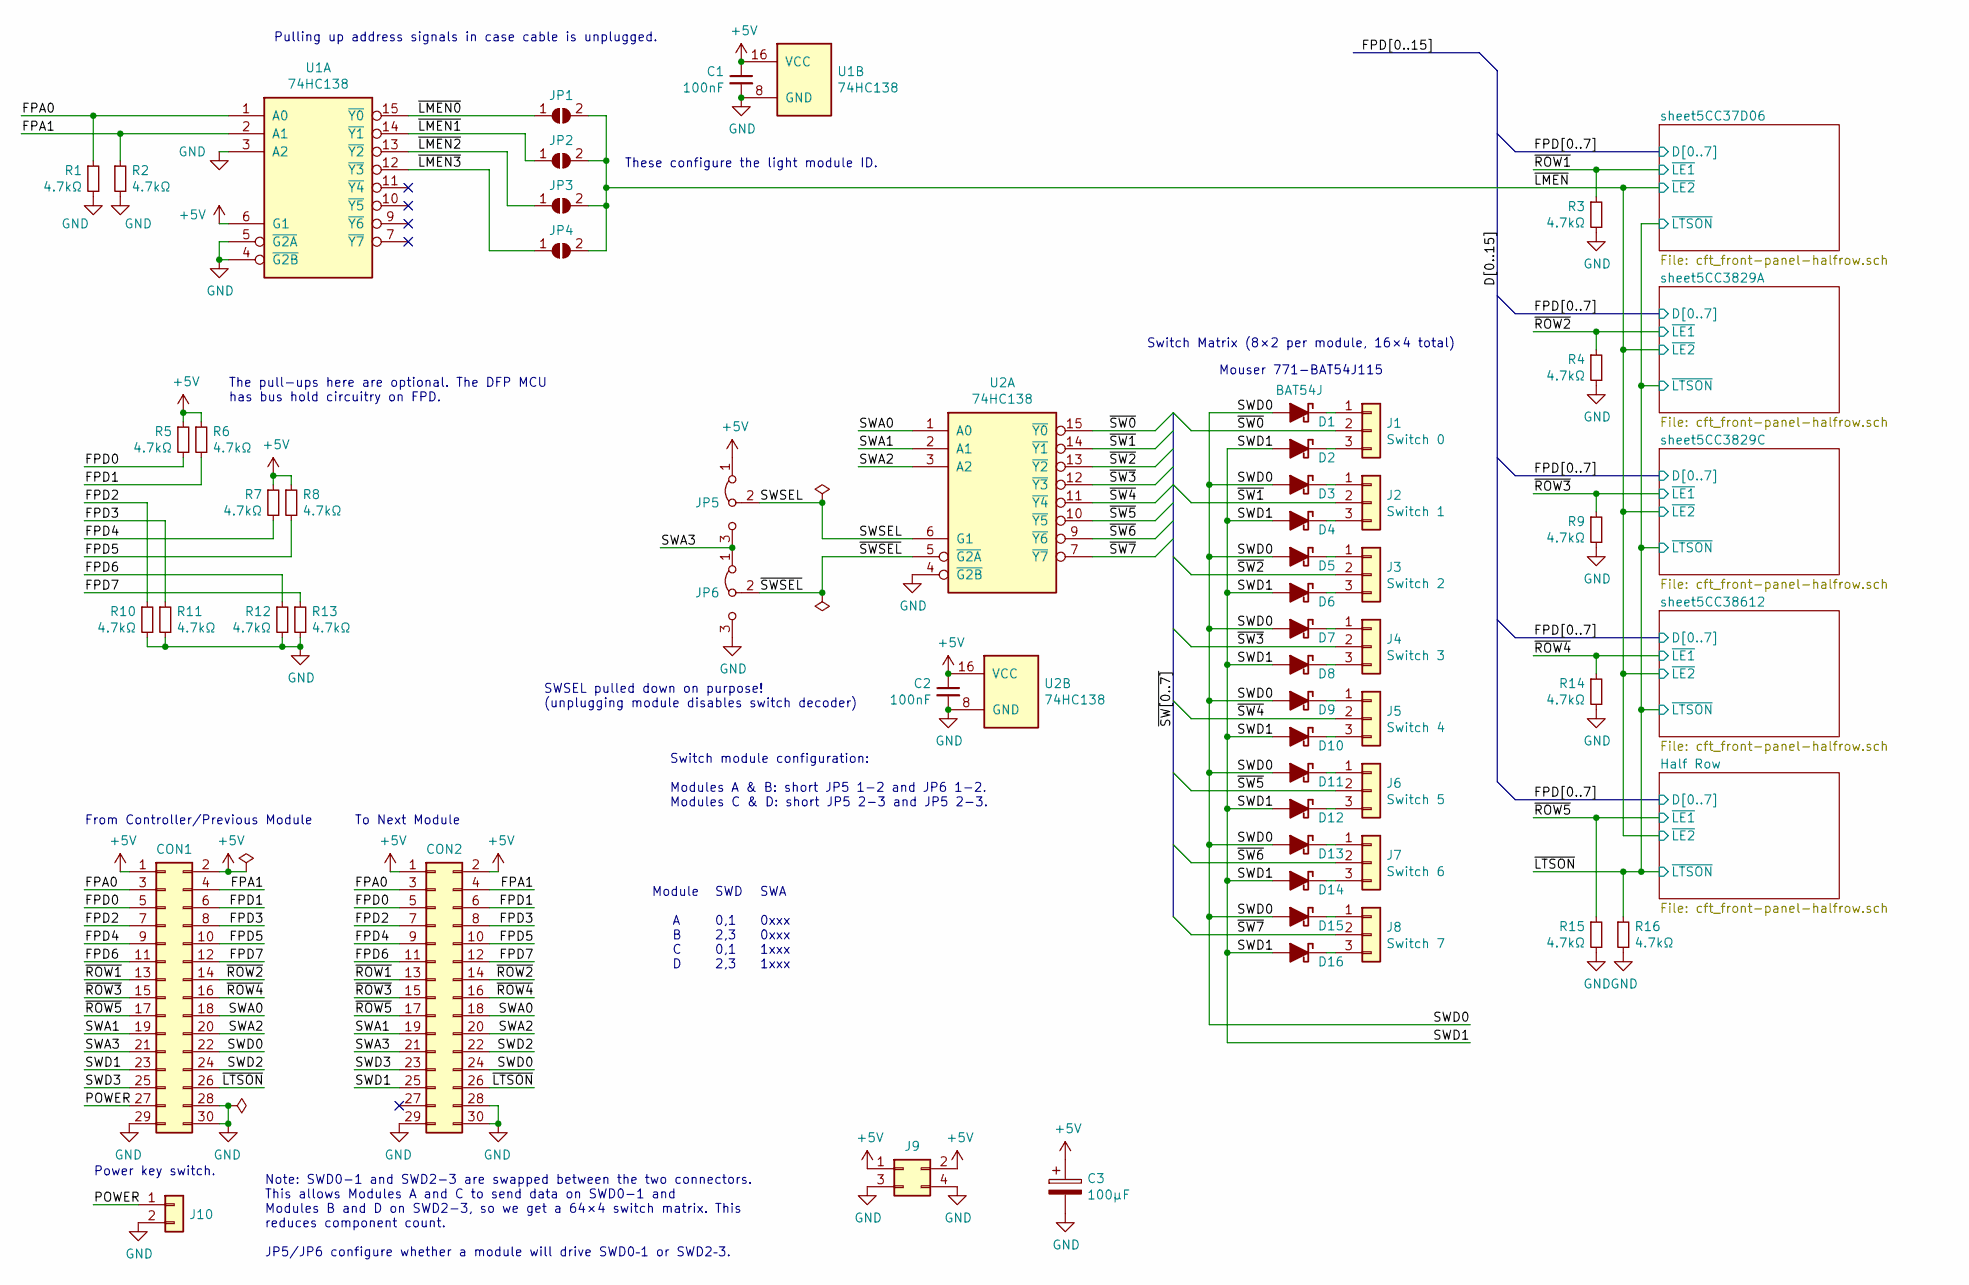
[picture p104: schematic cft-front-panel.sch, Front Panel Module]

Parts:
C1, C2: 100nF; C_SMD_0805_2012Metric_Pad1.15x1.40mm_HandSolder
C3: 100µF; CP_Radial_D6.3mm_P2.50mm
CON1, CON2: Conn_02x15_Odd_Even; IDC-Header_2x15_P2.54mm_Vertical
D1, D3, D5, D7, D9, D11, D13, D15: BAT54J; SOD-323
D2, D4, D6, D8, D10, D12, D14, D16: D_Schottky_ALT; SOD-323
J1: Switch 0; PinHeader_1x03_P2.54mm_Vertical
J2: Switch 1; PinHeader_1x03_P2.54mm_Vertical
J3: Switch 2; PinHeader_1x03_P2.54mm_Vertical
J4: Switch 3; PinHeader_1x03_P2.54mm_Vertical
J5: Switch 4; PinHeader_1x03_P2.54mm_Vertical
J6: Switch 5; PinHeader_1x03_P2.54mm_Vertical
J7: Switch 6; PinHeader_1x03_P2.54mm_Vertical
J8: Switch 7; PinHeader_1x03_P2.54mm_Vertical
J9: Conn_02x02_Odd_Even; Molex_Mini-Fit_Jr_5566-04A2_2x02_P4.20mm_Vertical
J10: Conn_01x02; PinHeader_1x02_P2.54mm_Vertical
JP1, JP2, JP3, JP4: SolderJumper_2_Open; SolderJumper-2_P1.3mm_Open_Pad1.0x1.5mm
JP5, JP6: Jumper_3_Bridged12; SolderJumper-3_P1.3mm_Open_Pad1.0x1.5mm
R1, R2, R3, R4, R5, R6, R7, R8, R9, R10, R11, R12, R13, R14, R15, R16: 4.7kΩ; R_SMD_0805_2012Metric_Pad1.15x1.40mm_HandSolder
U1, U2: 74HC138; SOIC-16

Connections:
+5V: C1.1, C2.1, C3.1, CON1.1, CON1.2, CON2.1, CON2.2, J9.1, J9.2, JP5.1 (A), R5.1, R6.1, R7.1, R8.1, U1.6 (G1), U1.16 (VCC), U2.16 (VCC); also elsewhere on the board
/FPA0: CON1.3, CON2.3, R1.1, U1.1 (A0)
/FPA1: CON1.4, CON2.4, R2.1, U1.2 (A1)
/FPD0: CON1.5, CON2.5, R5.2; also elsewhere on the board
/FPD1: CON1.6, CON2.6, R6.2; also elsewhere on the board
/FPD2: CON1.7, CON2.7, R10.1; also elsewhere on the board
/FPD3: CON1.8, CON2.8, R11.1; also elsewhere on the board
/FPD4: CON1.9, CON2.9, R7.2; also elsewhere on the board
/FPD5: CON1.10, CON2.10, R8.2; also elsewhere on the board
/FPD6: CON1.11, CON2.11, R12.1; also elsewhere on the board
/FPD7: CON1.12, CON2.12, R13.1; also elsewhere on the board
/POWER: CON1.27, J10.1
/SWA0: CON1.18, CON2.18, U2.1 (A0)
/SWA1: CON1.19, CON2.19, U2.2 (A1)
/SWA2: CON1.20, CON2.20, U2.3 (A2)
/SWA3: CON1.21, CON2.21, JP5.3 (B), JP6.1 (A)
/SWD0: CON1.22, CON2.24, D1.2 (A), D3.2 (A), D5.2 (A), D7.2 (A), D9.2 (A), D11.2 (A), D13.2 (A), D15.2 (A)
/SWD1: CON1.23, CON2.25, D2.2 (A), D4.2 (A), D6.2 (A), D8.2 (A), D10.2 (A), D12.2 (A), D14.2 (A), D16.2 (A)
/SWD2: CON1.24, CON2.22
/SWD3: CON1.25, CON2.23
/SWSEL: JP5.2 (C), U2.6 (G1)
/~LMEN: JP1.2 (B), JP2.2 (B), JP3.2 (B), JP4.2 (B); also elsewhere on the board
/~LMEN0: JP1.1 (A), U1.15 (~Y0)
/~LMEN1: JP2.1 (A), U1.14 (~Y1)
/~LMEN2: JP3.1 (A), U1.13 (~Y2)
/~LMEN3: JP4.1 (A), U1.12 (~Y3)
/~LTSON: CON1.26, CON2.26, R16.1; also elsewhere on the board
/~ROW1: CON1.13, CON2.13, R3.1; also elsewhere on the board
/~ROW2: CON1.14, CON2.14, R4.1; also elsewhere on the board
/~ROW3: CON1.15, CON2.15, R9.1; also elsewhere on the board
/~ROW4: CON1.16, CON2.16, R14.1; also elsewhere on the board
/~ROW5: CON1.17, CON2.17, R15.1; also elsewhere on the board
/~SW0: J1.2, U2.15 (~Y0)
/~SW1: J2.2, U2.14 (~Y1)
/~SW2: J3.2, U2.13 (~Y2)
/~SW3: J4.2, U2.12 (~Y3)
/~SW4: J5.2, U2.11 (~Y4)
/~SW5: J6.2, U2.10 (~Y5)
/~SW6: J7.2, U2.9 (~Y6)
/~SW7: J8.2, U2.7 (~Y7)
/~SWSEL: JP6.2 (C), U2.5 (~G2A)
GND: C1.2, C2.2, C3.2, CON1.28, CON1.29, CON1.30, CON2.28, CON2.29, CON2.30, J9.3, J9.4, J10.2, JP6.3 (B), R1.2, R2.2, R3.2, R4.2, R9.2, R10.2, R11.2, R12.2, R13.2, R14.2, R15.2, R16.2, U1.3 (A2), U1.4 (~G2B), U1.5 (~G2A), U1.8 (GND), U2.4 (~G2B), U2.8 (GND); also elsewhere on the board
unnamed: D1.1 (K), J1.1
unnamed: D2.1 (K), J1.3
unnamed: D3.1 (K), J2.1
unnamed: D4.1 (K), J2.3
unnamed: D5.1 (K), J3.1
unnamed: D6.1 (K), J3.3
unnamed: D7.1 (K), J4.1
unnamed: D8.1 (K), J4.3
unnamed: D9.1 (K), J5.1
unnamed: D10.1 (K), J5.3
unnamed: D11.1 (K), J6.1
unnamed: D12.1 (K), J6.3
unnamed: D13.1 (K), J7.1
unnamed: D14.1 (K), J7.3
unnamed: D15.1 (K), J8.1
unnamed: D16.1 (K), J8.3

Notes on the sheet:
From Controller/Previous Module
To Next Module
Switch module configuration: Modules A & B: short JP5 1-2 and JP6 1-2. Modules C & D: short JP5 2-3 and JP5 2-3.
Power key switch.
These configure the light module ID.
SWSEL pulled down on purpose! (unplugging module disables switch decoder)
Pulling up address signals in case cable is unplugged.
The pull-ups here are optional. The DFP MCU has bus hold circuitry on FPD.
Mouser 771-BAT54J115
Switch Matrix (8×2 per module, 16×4 total)
Note: SWD0-1 and SWD2-3 are swapped between the two connectors. This allows Modules A and C to send data on SWD0-1 and Modules B and D on SWD2-3, so we get a 64×4 switch matrix. This reduces component count. JP5/JP6 configure whether a module will drive SWD0–1 or SWD2–3.
Module A B C D
SWA 0xxx 0xxx 1xxx 1xxx
SWD 0,1 2,3 0,1 2,3

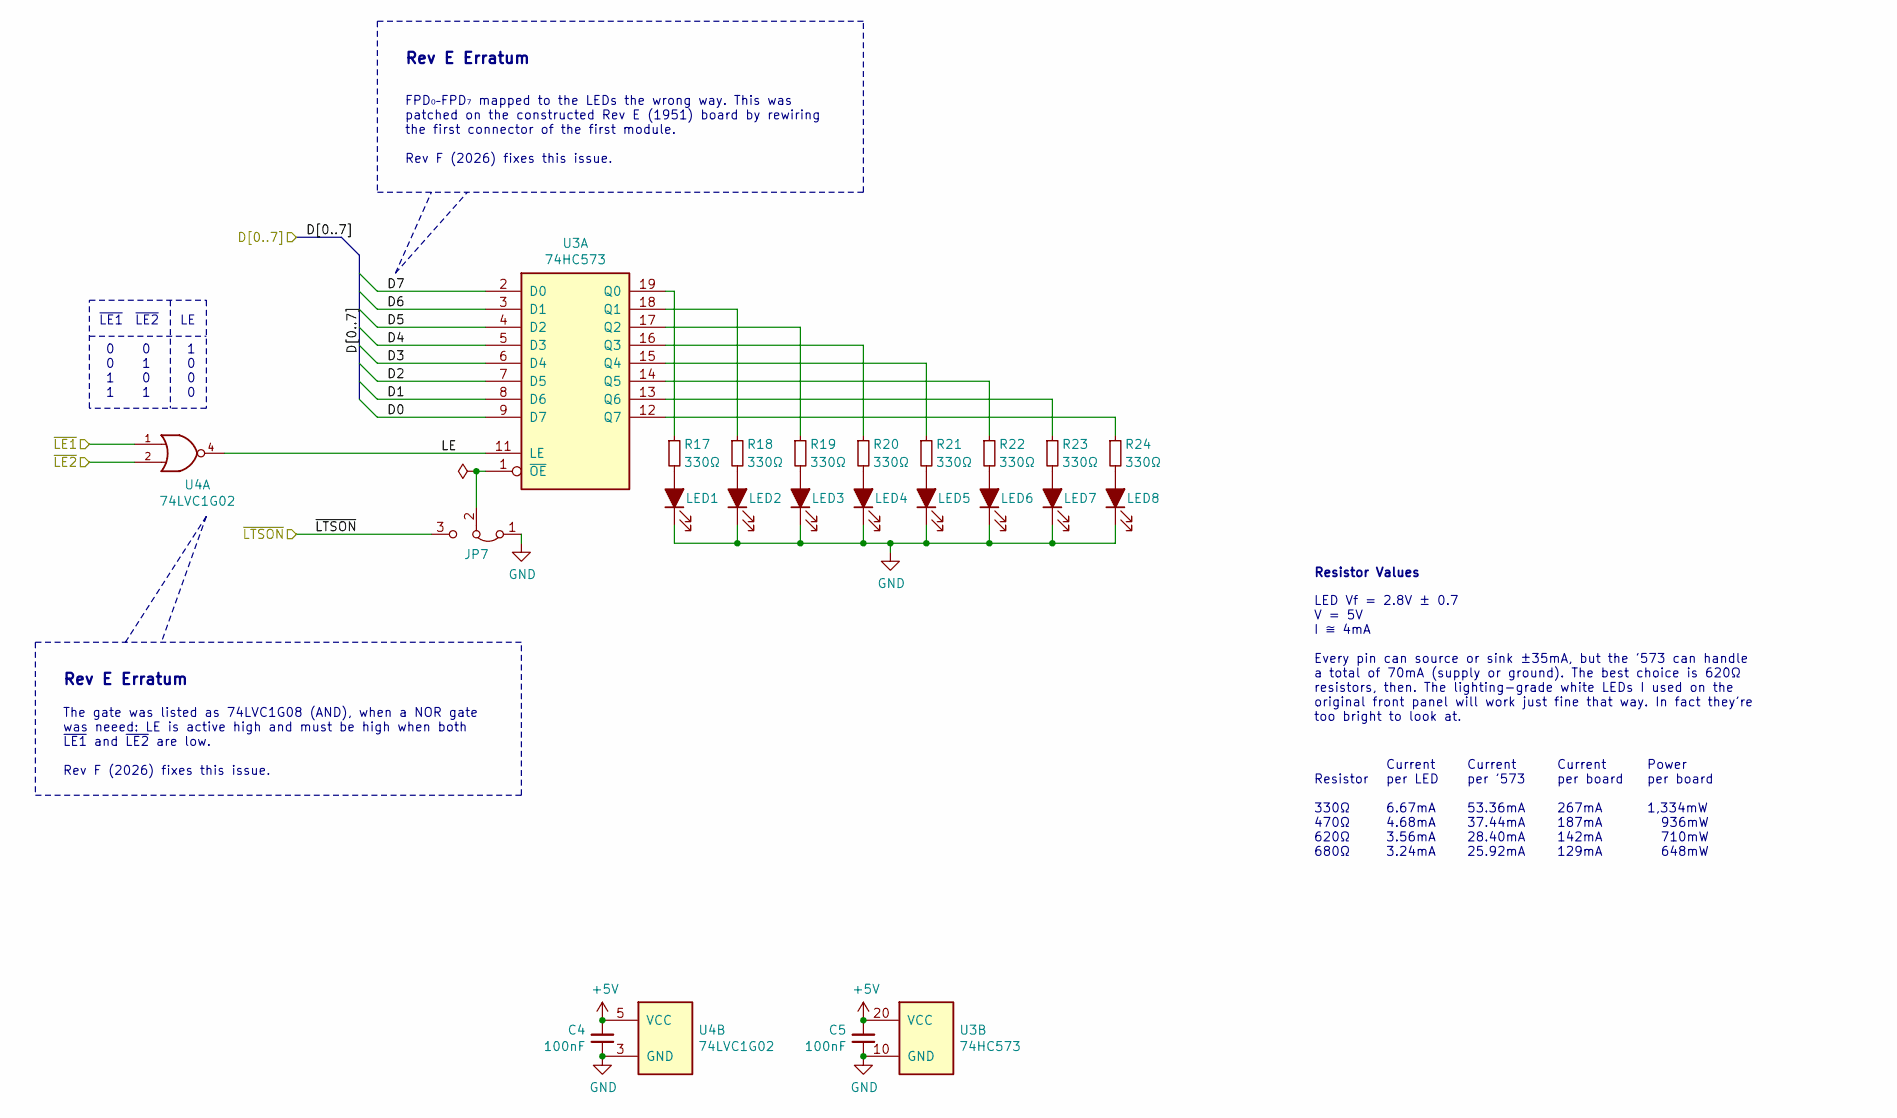
[picture p105: schematic cft_front-panel-halfrow.sch, Single 8-LED Row]

Parts:
C12, C13: 100nF; C_SMD_0805_2012Metric_Pad1.15x1.40mm_HandSolder
JP11: Jumper_3_Bridged12; PinHeader_1x03_P2.54mm_Vertical
LED33, LED34, LED35, LED36, LED37, LED38, LED39, LED40: LED_ALT; LED_1210_3225
R49, R50, R51, R52, R53, R54, R55, R56: 330Ω; R_SMD_0805_2012Metric_Pad1.15x1.40mm_HandSolder
U4: 74LVC1G02; SOT-23-5_HandSoldering
U11: 74HC573; SOIC-20W

Connections:
+5V: C12.2, C13.2, U4.5 (VCC), U11.20 (VCC); also elsewhere on the board
/FPD0: U11.9 (D7); also elsewhere on the board
/FPD1: U11.8 (D6); also elsewhere on the board
/FPD2: U11.7 (D5); also elsewhere on the board
/FPD3: U11.6 (D4); also elsewhere on the board
/FPD4: U11.5 (D3); also elsewhere on the board
/FPD5: U11.4 (D2); also elsewhere on the board
/FPD6: U11.3 (D1); also elsewhere on the board
/FPD7: U11.2 (D0); also elsewhere on the board
/~LMEN: U4.2; also elsewhere on the board
/~LTSON: JP11.3 (B); also elsewhere on the board
/~ROW1: U4.1; also elsewhere on the board
GND: C12.1, C13.1, JP11.1 (A), LED33.1 (K), LED34.1 (K), LED35.1 (K), LED36.1 (K), LED37.1 (K), LED38.1 (K), LED39.1 (K), LED40.1 (K), U4.3 (GND), U11.10 (GND); also elsewhere on the board
unnamed: JP11.2 (C), U11.1 (~OE)
unnamed: LED33.2 (A), R49.2
unnamed: LED34.2 (A), R50.2
unnamed: LED35.2 (A), R51.2
unnamed: LED36.2 (A), R52.2
unnamed: LED37.2 (A), R53.2
unnamed: LED38.2 (A), R54.2
unnamed: LED39.2 (A), R55.2
unnamed: LED40.2 (A), R56.2
unnamed: R49.1, U11.19 (Q0)
unnamed: R50.1, U11.18 (Q1)
unnamed: R51.1, U11.17 (Q2)
unnamed: R52.1, U11.16 (Q3)
unnamed: R53.1, U11.15 (Q4)
unnamed: R54.1, U11.14 (Q5)
unnamed: R55.1, U11.13 (Q6)
unnamed: R56.1, U11.12 (Q7)

Parts of its further copies:
C4, C5, C6, C7, C8, C9, C10, C11: 100nF; C_SMD_0805_2012Metric_Pad1.15x1.40mm_HandSolder
JP7, JP8, JP9, JP10: Jumper_3_Bridged12; PinHeader_1x03_P2.54mm_Vertical
LED1, LED2, LED3, LED4, LED5, LED6, LED7, LED8, LED9, LED10, LED11, LED12, LED13, LED14, LED15, LED16, LED17, LED18, LED19, LED20, LED21, LED22, LED23, LED24, LED25, LED26, LED27, LED28, LED29, LED30, LED31, LED32: LED_ALT; LED_1210_3225
R17, R18, R19, R20, R21, R22, R23, R24, R25, R26, R27, R28, R29, R30, R31, R32, R33, R34, R35, R36, R37, R38, R39, R40, R41, R42, R43, R44, R45, R46, R47, R48: 330Ω; R_SMD_0805_2012Metric_Pad1.15x1.40mm_HandSolder
U3, U5, U7, U9: 74HC573; SOIC-20W
U6, U8, U10, U12: 74LVC1G02; SOT-23-5_HandSoldering

Connections of its further copies:
+5V: C4.2, C5.2, C6.2, C7.2, C8.2, C9.2, C10.2, C11.2, U3.20 (VCC), U5.20 (VCC), U6.5 (VCC), U7.20 (VCC), U8.5 (VCC), U9.20 (VCC), U10.5 (VCC), U12.5 (VCC); also elsewhere on the board
/FPD0: U3.9 (D7), U5.9 (D7), U7.9 (D7), U9.9 (D7); also elsewhere on the board
/FPD1: U3.8 (D6), U5.8 (D6), U7.8 (D6), U9.8 (D6); also elsewhere on the board
/FPD2: U3.7 (D5), U5.7 (D5), U7.7 (D5), U9.7 (D5); also elsewhere on the board
/FPD3: U3.6 (D4), U5.6 (D4), U7.6 (D4), U9.6 (D4); also elsewhere on the board
/FPD4: U3.5 (D3), U5.5 (D3), U7.5 (D3), U9.5 (D3); also elsewhere on the board
/FPD5: U3.4 (D2), U5.4 (D2), U7.4 (D2), U9.4 (D2); also elsewhere on the board
/FPD6: U3.3 (D1), U5.3 (D1), U7.3 (D1), U9.3 (D1); also elsewhere on the board
/FPD7: U3.2 (D0), U5.2 (D0), U7.2 (D0), U9.2 (D0); also elsewhere on the board
/sheet5CC3829A/LE: U5.11 (LE), U6.4
/sheet5CC3829C/LE: U7.11 (LE), U8.4
/sheet5CC38612/LE: U9.11 (LE), U10.4
/~LMEN: U6.2, U8.2, U10.2, U12.2; also elsewhere on the board
/~LTSON: JP7.3 (B), JP8.3 (B), JP9.3 (B), JP10.3 (B); also elsewhere on the board
/~ROW2: U6.1; also elsewhere on the board
/~ROW3: U8.1; also elsewhere on the board
/~ROW4: U10.1; also elsewhere on the board
/~ROW5: U12.1; also elsewhere on the board
GND: C4.1, C5.1, C6.1, C7.1, C8.1, C9.1, C10.1, C11.1, JP7.1 (A), JP8.1 (A), JP9.1 (A), JP10.1 (A), LED1.1 (K), LED2.1 (K), LED3.1 (K), LED4.1 (K), LED5.1 (K), LED6.1 (K), LED7.1 (K), LED8.1 (K), LED9.1 (K), LED10.1 (K), LED11.1 (K), LED12.1 (K), LED13.1 (K), LED14.1 (K), LED15.1 (K), LED16.1 (K), LED17.1 (K), LED18.1 (K), LED19.1 (K), LED20.1 (K), LED21.1 (K), LED22.1 (K), LED23.1 (K), LED24.1 (K), LED25.1 (K), LED26.1 (K), LED27.1 (K), LED28.1 (K), LED29.1 (K), LED30.1 (K), LED31.1 (K), LED32.1 (K), U3.10 (GND), U5.10 (GND), U6.3 (GND), U7.10 (GND), U8.3 (GND), U9.10 (GND), U10.3 (GND), U12.3 (GND); also elsewhere on the board
unnamed: JP7.2 (C), U3.1 (~OE)
unnamed: JP8.2 (C), U5.1 (~OE)
unnamed: JP9.2 (C), U7.1 (~OE)
unnamed: JP10.2 (C), U9.1 (~OE)
unnamed: LED1.2 (A), R17.2
unnamed: LED2.2 (A), R18.2
unnamed: LED3.2 (A), R19.2
unnamed: LED4.2 (A), R20.2
unnamed: LED5.2 (A), R21.2
unnamed: LED6.2 (A), R22.2
unnamed: LED7.2 (A), R23.2
unnamed: LED8.2 (A), R24.2
unnamed: LED9.2 (A), R25.2
unnamed: LED10.2 (A), R26.2
unnamed: LED11.2 (A), R27.2
unnamed: LED12.2 (A), R28.2
unnamed: LED13.2 (A), R29.2
unnamed: LED14.2 (A), R30.2
unnamed: LED15.2 (A), R31.2
unnamed: LED16.2 (A), R32.2
unnamed: LED17.2 (A), R33.2
unnamed: LED18.2 (A), R34.2
unnamed: LED19.2 (A), R35.2
unnamed: LED20.2 (A), R36.2
unnamed: LED21.2 (A), R37.2
unnamed: LED22.2 (A), R38.2
unnamed: LED23.2 (A), R39.2
unnamed: LED24.2 (A), R40.2
unnamed: LED25.2 (A), R41.2
unnamed: LED26.2 (A), R42.2
unnamed: LED27.2 (A), R43.2
unnamed: LED28.2 (A), R44.2
unnamed: LED29.2 (A), R45.2
unnamed: LED30.2 (A), R46.2
unnamed: LED31.2 (A), R47.2
unnamed: LED32.2 (A), R48.2
unnamed: R17.1, U3.19 (Q0)
unnamed: R18.1, U3.18 (Q1)
unnamed: R19.1, U3.17 (Q2)
unnamed: R20.1, U3.16 (Q3)
unnamed: R21.1, U3.15 (Q4)
unnamed: R22.1, U3.14 (Q5)
unnamed: R23.1, U3.13 (Q6)
unnamed: R24.1, U3.12 (Q7)
unnamed: R25.1, U5.19 (Q0)
unnamed: R26.1, U5.18 (Q1)
unnamed: R27.1, U5.17 (Q2)
unnamed: R28.1, U5.16 (Q3)
unnamed: R29.1, U5.15 (Q4)
unnamed: R30.1, U5.14 (Q5)
unnamed: R31.1, U5.13 (Q6)
unnamed: R32.1, U5.12 (Q7)
unnamed: R33.1, U7.19 (Q0)
unnamed: R34.1, U7.18 (Q1)
unnamed: R35.1, U7.17 (Q2)
unnamed: R36.1, U7.16 (Q3)
unnamed: R37.1, U7.15 (Q4)
unnamed: R38.1, U7.14 (Q5)
unnamed: R39.1, U7.13 (Q6)
unnamed: R40.1, U7.12 (Q7)
unnamed: R41.1, U9.19 (Q0)
unnamed: R42.1, U9.18 (Q1)
unnamed: R43.1, U9.17 (Q2)
unnamed: R44.1, U9.16 (Q3)
unnamed: R45.1, U9.15 (Q4)
unnamed: R46.1, U9.14 (Q5)
unnamed: R47.1, U9.13 (Q6)
unnamed: R48.1, U9.12 (Q7)

Notes on the sheet:
Resistor Values
LED Vf = 2.8V ± 0.7 V = 5V I ≅ 4mA Every pin can source or sink ±35mA, but the '573 can handle a total of 70mA (supply or ground). The best choice is 620Ω resistors, then. The lighting-grade white LEDs I used on the original front panel will work just fine that way. In fact they're too bright to lo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
Resistor 330Ω 470Ω 620Ω 680Ω
Current per LED 6.67mA 4.68mA 3.56mA 3.24mA
Current per '573 53.36mA 37.44mA 28.40mA 25.92mA
Current per board 267mA 187mA 142mA 129mA
Power per board 1,334mW 936mW 710mW 648mW
Rev E Erratum
FPD₀–FPD₇ mapped to the LEDs the wrong way. This was patched on the constructed Rev E (1951) board by rewiring the first connector of the first module. Rev F (2026) fixes this issue.
~LE1~ 0 0 1 1
~LE2~ 0 1 0 1
LE 1 0 0 0
The gate was listed as 74LVC1G08 (AND), when a NOR gate was neeed: LE is active high and must be high when both ~LE1~ and ~LE2~ are low. Rev F (2026) fixes this issue.

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
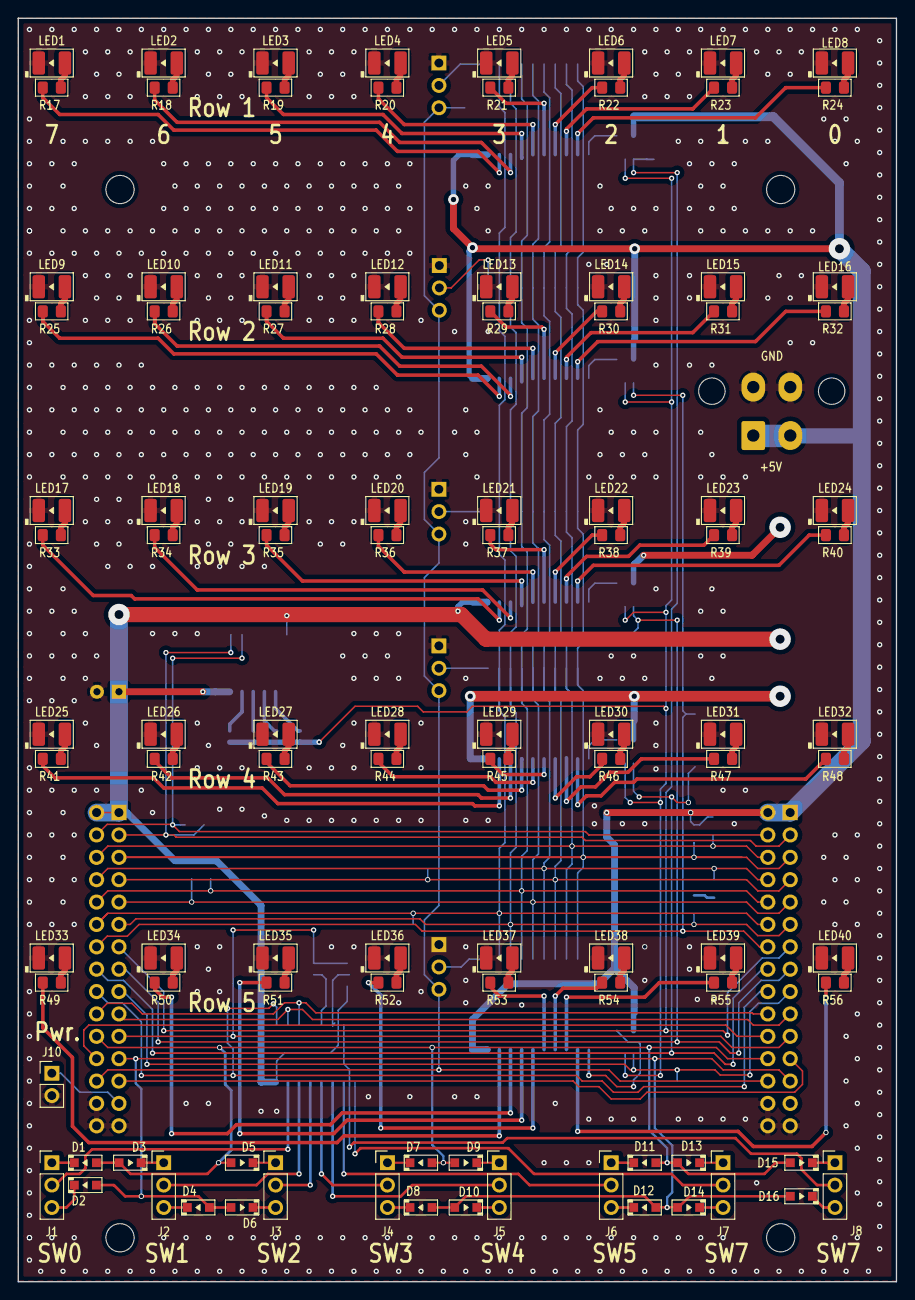
[picture p106: board cft-front-panel.kicad_pcb from above]

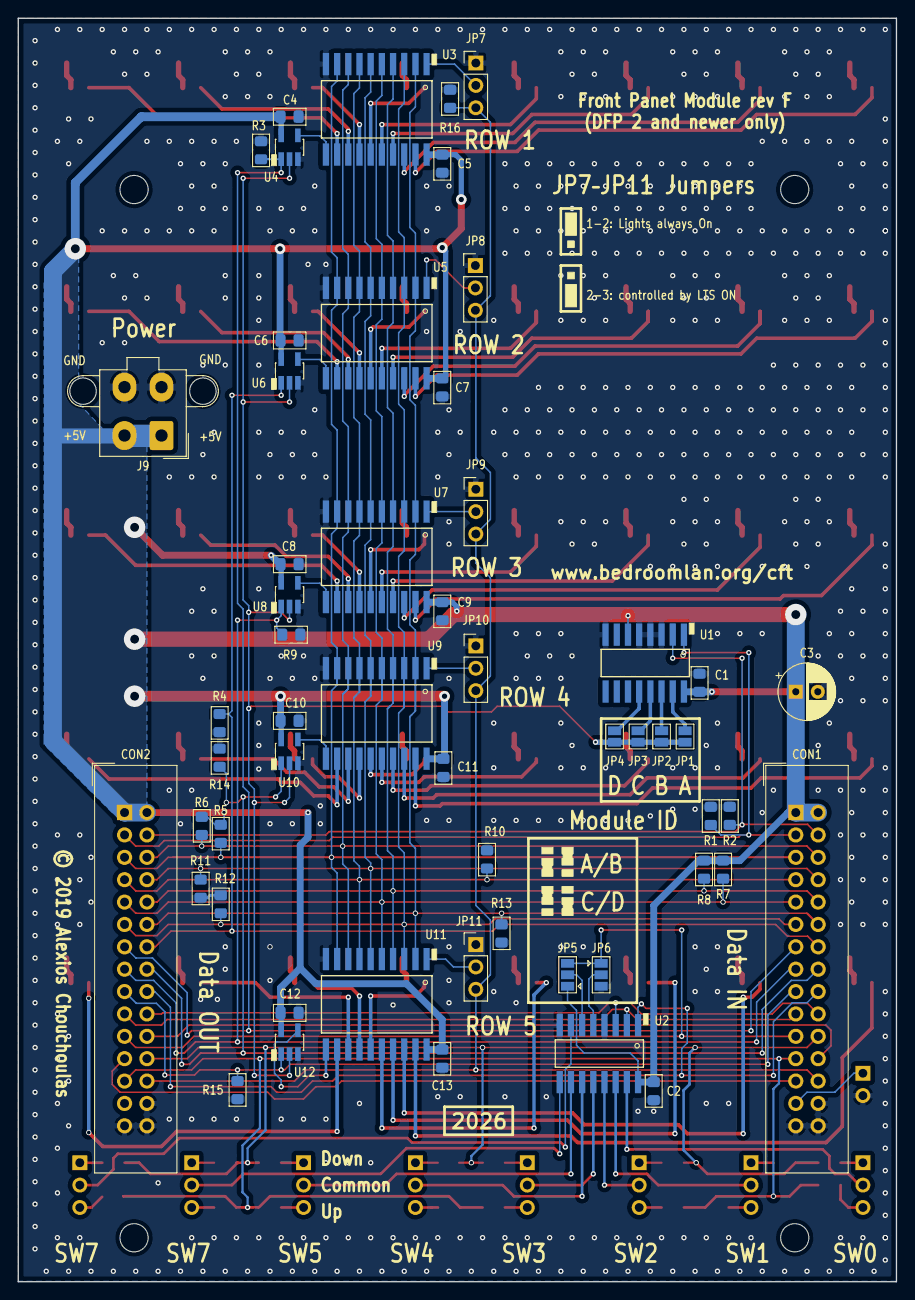
[picture p107: board cft-front-panel.kicad_pcb from below]

Board: 2 copper layers, 99.7 x 143.4 mm, 160 parts (55 on the bottom side), 148 nets.
