alexiosc/cft/kicad/cft/tst/tst.kicad_pcb

## KiCad design kicad/cft/tst/tst.kicad_pcb (2020-06-10)

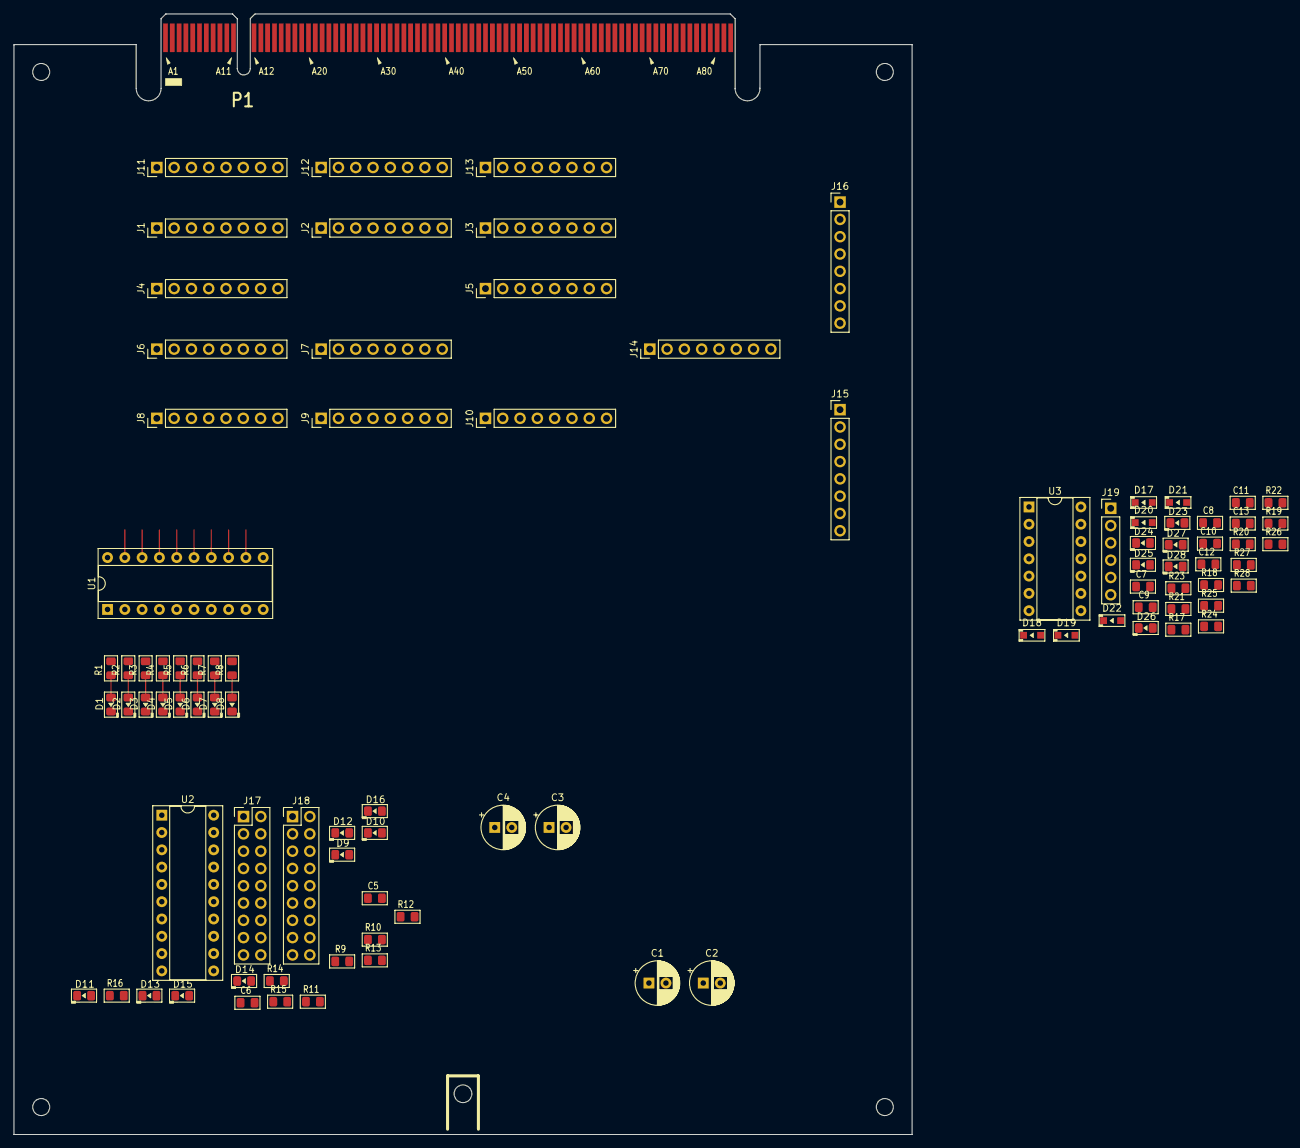
[picture p108: board tst.kicad_pcb from above]

Board: 4 copper layers, 131.9 x 164.6 mm, 92 parts (0 on the bottom side), 181 nets.

Parts:
C1, C2, C3, C4: 47µF; CP_Radial_D6.3mm_P2.50mm
C5, C6, C13: 100nF; C_SMD_0805_2012Metric_Pad1.15x1.40mm_HandSolder
C7: 1µF; C_SMD_0805_2012Metric_Pad1.15x1.40mm_HandSolder
C8, C9, C10, C11, C12: 1µF; SMD_0805_2012Metric_Pad1.15x1.40mm_HandSolder
D1, D2, D3, D4, D5, D6, D7, D8, D9, D10, D11, D12, D13, D14, D15, D16: D_ALT; LED_0805_2012Metric_Pad1.15x1.40mm_HandSolder
D17, D18, D19, D20, D21, D22: CUS520; SOD-323
D23, D24, D25, D26, D27, D28: LED_ALT; LED_0805_2012Metric_Pad1.15x1.40mm_HandSolder
J1, J2, J3, J4, J5, J6, J7, J8, J9, J10, J11, J12, J13, J14, J15, J16: Conn_01x08; PinHeader_1x08_P2.54mm_Vertical
J17, J18: Conn_02x09_Odd_Even; PinHeader_2x09_P2.54mm_Vertical
J19: Conn_01x06; PinHeader_1x06_P2.54mm_Vertical
P1: CFT-2019-Bus; CFT-2019-Card-Edge
R1, R2, R3, R4, R5, R6, R7, R8, R9, R10, R11, R12, R13, R14, R15, R16: R_Small; R_SMD_0805_2012Metric_Pad1.15x1.40mm_HandSolder
R17, R18, R19, R20, R21, R22: 100kΩ; SMD_0805_2012Metric_Pad1.15x1.40mm_HandSolder
R23, R24, R25, R26, R27, R28: 150Ω; SMD_0805_2012Metric_Pad1.15x1.40mm_HandSolder
U1, U2: 74HCT574; DIP-20_W7.62mm_Socket
U3: 74HC14; DIP-14_W7.62mm_Socket

Connections:
+5V: C1.1, C2.1, C3.1, C4.1, C5.1, C6.1, C13.1, D23.1, D24.1, D25.1, D26.1, D27.1, D28.1, J15.1, J15.2, J15.3, J15.4, J15.5, J15.6, J15.7, J15.8, P1.A1, P1.A2, P1.A81, P1.A82, U1.20, U2.20, U3.14
/AB0: J1.1, P1.A7
/AB1: J1.2, P1.A8
/AB2: J1.3, P1.A9
/AB3: J1.4, P1.A10
/AB4: J1.5, P1.A11
/AB5: J1.6, P1.A12
/AB6: J1.7, P1.A13
/AB7: J1.8, P1.A14
/AB8: J2.1, P1.A34
/AB9: J2.2, P1.A35
/AB10: J2.3, P1.A36
/AB11: J2.4, P1.A37
/AB12: J2.5, P1.A38
/AB13: J2.6, P1.A39
/AB14: J2.7, P1.A40
/AB15: J2.8, P1.A41
/AB16: J3.1, P1.A42
/AB17: J3.2, P1.A43
/AB18: J3.3, P1.A44
/AB19: J3.4, P1.A45
/AB20: J3.5, P1.A46
/AB21: J3.6, P1.A47
/AB22: J3.7, P1.A48
/AB23: J3.8, P1.A49
/ACTION0: J9.3, P1.B30
/ACTION1: J9.4, P1.B31
/ACTION2: J9.5, P1.B32
/ACTION3: J9.6, P1.B33
/C33: J14.1, P1.A77
/C34: J14.2, P1.B77
/C35: J14.3, P1.A78
/C36: J14.4, P1.B78
/C37: J14.5, P1.A79
/C38: J14.6, P1.B79
/C39: J14.7, P1.A80
/C40: J14.8, P1.B80
/CLK1: J11.3, P1.B3
/CLK2: J11.4, P1.B4
/CLK3: J11.5, P1.A3
/CLK4: J11.6, P1.A4
/DB0: J4.1, P1.A15
/DB1: J4.2, P1.A16
/DB2: J4.3, P1.A17
/DB3: J4.4, P1.A18
/DB4: J4.5, P1.A19
/DB5: J4.6, P1.A20
/DB6: J4.7, P1.A21
/DB7: J4.8, P1.A22
/DB8: J5.1, P1.A56
/DB9: J5.2, P1.A57
/DB10: J5.3, P1.A58
/DB11: J5.4, P1.A59
/DB12: J5.5, P1.A60
/DB13: J5.6, P1.A61
/DB14: J5.7, P1.A62
/DB15: J5.8, P1.A63
/IBUS0: J6.1, P1.B7
/IBUS1: J6.2, P1.B8
/IBUS2: J6.3, P1.B9
/IBUS3: J6.4, P1.B10
/IBUS4: J6.5, P1.B11
/IBUS5: J6.6, P1.B12
/IBUS6: J6.7, P1.B13
/IBUS7: J6.8, P1.B14
/IBUS8: J7.1, P1.B34
/IBUS9: J7.2, P1.B35
/IBUS10: J7.3, P1.B36
/IBUS11: J7.4, P1.B37
/IBUS12: J7.5, P1.B38
/IBUS13: J7.6, P1.B39
/IBUS14: J7.7, P1.B40
/IBUS15: J7.8, P1.B41
/RADDR0: J8.1, P1.B15
/RADDR1: J8.2, P1.B16
/RADDR2: J8.3, P1.B17
/RADDR3: J8.4, P1.B18
/RADDR4: J8.5, P1.B19
/Strobe LEDs/LED1: D17.2, J19.1
/Strobe LEDs/LED2: D18.2, J19.2
/Strobe LEDs/LED3: D19.2, J19.3
/Strobe LEDs/LED4: D20.2, J19.4
/Strobe LEDs/LED5: D21.2, J19.5
/Strobe LEDs/LED6: D22.2, J19.6
/T34: J11.7, P1.B5
/WADDR0: J8.6, P1.B20
/WADDR1: J8.7, P1.B21
/WADDR2: J8.8, P1.B22
/WADDR3: J9.1, P1.B23
/WADDR4: J9.2, P1.B24
/~HALT: J10.6, P1.B60
/~IO: J10.2, P1.B26
/~IODEV1xx: J12.3, P1.A24
/~IODEV2xx: J12.4, P1.A25
/~IODEV3xx: J12.5, P1.A26
/~IRQ: J11.8, P1.B42
/~IRQ0: J13.1, P1.A51
/~IRQ1: J13.2, P1.A52
/~IRQ2: J13.3, P1.A53
/~IRQ3: J13.4, P1.A54
/~IRQ4: J13.5, P1.A55
/~IRQ5: J13.6, P1.A67
/~IRQ6: J13.7, P1.A68
/~IRQ7: J13.8, P1.A70
/~IRQS: J12.1, P1.B43
/~MEM: J10.1, P1.B25
/~R: J10.3, P1.A27
/~RESET: J11.1, P1.B6
/~RSTHOLD: J11.2, P1.A6
/~SYSDEV: J12.2, P1.A23
/~W: J10.4, P1.A28
/~WS: J10.5, P1.B27
GND: C1.2, C2.2, C3.2, C4.2, C5.2, C6.2, C7.2, C8.2, C9.2, C10.2, C11.2, C12.2, C13.2, D1.1, D2.1, D3.1, D4.1, D5.1, D6.1, D7.1, D8.1, D9.1, D10.1, D11.1, D12.1, D13.1, D14.1, D15.1, D16.1, J16.1, J16.2, J16.3, J16.4, J16.5, J16.6, J16.7, J16.8, J17.1, J17.3, J17.5, J17.7, J17.9, J17.11, J17.13, J17.15, J17.17, J18.1, J18.3, J18.5, J18.7, J18.9, J18.11, J18.13, J18.15, J18.17, P1.A72, P1.A73, P1.B1, P1.B2, P1.B81, P1.B82, R17.1, R18.1, R19.1, R20.1, R21.1, R22.1, U1.1, U1.10, U2.1, U2.10, U3.7
unnamed: C7.1, D17.1, R17.2, U3.1
unnamed: C8.1, D18.1, R18.2, U3.3
unnamed: C9.1, D19.1, R19.2, U3.5
unnamed: C10.1, D20.1, R20.2, U3.9
unnamed: C11.1, D21.1, R21.2, U3.11
unnamed: C12.1, D22.1, R22.2, U3.13
unnamed: D1.2, R1.1
unnamed: D2.2, R2.1
unnamed: D3.2, R3.1
unnamed: D4.2, R4.1
unnamed: D5.2, R5.1
unnamed: D6.2, R6.1
unnamed: D7.2, R7.1
unnamed: D8.2, R8.1
unnamed: D9.2, R10.1
unnamed: D10.2, R12.1
unnamed: D11.2, R14.1
unnamed: D12.2, R16.1
unnamed: D13.2, R9.1
unnamed: D14.2, R11.1
unnamed: D15.2, R13.1
unnamed: D16.2, R15.1
unnamed: D23.2, R23.1
unnamed: D24.2, R24.1
unnamed: D25.2, R25.1
unnamed: D26.2, R26.1
unnamed: D27.2, R27.1
unnamed: D28.2, R28.1
unnamed: J17.2, U1.2
unnamed: J17.4, U1.3
unnamed: J17.6, U1.4
unnamed: J17.8, U1.5
unnamed: J17.10, U1.6
unnamed: J17.12, U1.7
unnamed: J17.14, U1.8
unnamed: J17.16, U1.9
unnamed: J17.18, U1.11
unnamed: J18.2, U2.2
unnamed: J18.4, U2.3
unnamed: J18.6, U2.4
unnamed: J18.8, U2.5
unnamed: J18.10, U2.6
unnamed: J18.12, U2.7
unnamed: J18.14, U2.8
unnamed: J18.16, U2.9
unnamed: J18.18, U2.11
unnamed: R1.2, U1.19
unnamed: R2.2, U1.18
unnamed: R3.2, U1.17
unnamed: R4.2, U1.16
unnamed: R5.2, U1.15
unnamed: R6.2, U1.14
unnamed: R7.2, U1.13
unnamed: R8.2, U1.12
unnamed: R9.2, U2.19
unnamed: R10.2, U2.18
unnamed: R11.2, U2.17
unnamed: R12.2, U2.16
unnamed: R13.2, U2.15
unnamed: R14.2, U2.14
unnamed: R15.2, U2.13
unnamed: R16.2, U2.12
unnamed: R23.2, U3.2
unnamed: R24.2, U3.4
unnamed: R25.2, U3.6
unnamed: R26.2, U3.8
unnamed: R27.2, U3.10
unnamed: R28.2, U3.12
