alexiosc/cft/kicad/cft/cft-card-blank-single/cft-card-blank-single.kicad_pcb

## KiCad design kicad/cft/cft-card-blank-single/cft-card-blank-single.kicad_pcb (2019-08-18)

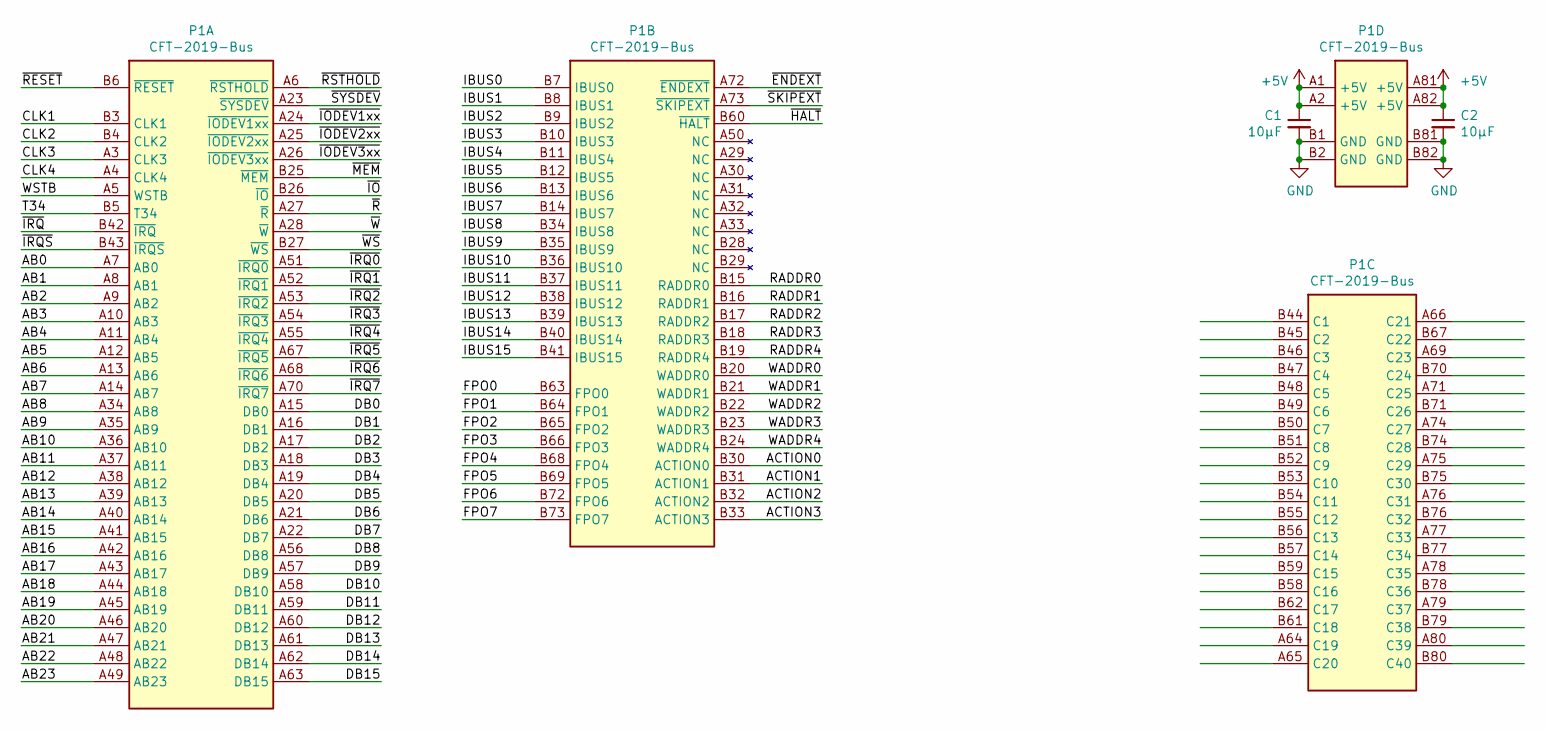
[picture p109: schematic cft-card-blank-single.sch]

Parts:
C1, C2: 10µF; CP_Radial_D4.0mm_P1.50mm
P1: CFT-2019-Bus; CFT-2019-Card-Edge

Connections:
+5V: C1.1, C2.1, P1.A1 (+5V), P1.A2 (+5V), P1.A81 (+5V), P1.A82 (+5V)
/AB0: P1.A7 (AB0)
/AB1: P1.A8 (AB1)
/AB2: P1.A9 (AB2)
/AB3: P1.A10 (AB3)
/AB4: P1.A11 (AB4)
/AB5: P1.A12 (AB5)
/AB6: P1.A13 (AB6)
/AB7: P1.A14 (AB7)
/AB8: P1.A34 (AB8)
/AB9: P1.A35 (AB9)
/AB10: P1.A36 (AB10)
/AB11: P1.A37 (AB11)
/AB12: P1.A38 (AB12)
/AB13: P1.A39 (AB13)
/AB14: P1.A40 (AB14)
/AB15: P1.A41 (AB15)
/AB16: P1.A42 (AB16)
/AB17: P1.A43 (AB17)
/AB18: P1.A44 (AB18)
/AB19: P1.A45 (AB19)
/AB20: P1.A46 (AB20)
/AB21: P1.A47 (AB21)
/AB22: P1.A48 (AB22)
/AB23: P1.A49 (AB23)
/ACTION0: P1.B30 (ACTION0)
/ACTION1: P1.B31 (ACTION1)
/ACTION2: P1.B32 (ACTION2)
/ACTION3: P1.B33 (ACTION3)
/CLK1: P1.B3 (CLK1)
/CLK2: P1.B4 (CLK2)
/CLK3: P1.A3 (CLK3)
/CLK4: P1.A4 (CLK4)
/DB0: P1.A15 (DB0)
/DB1: P1.A16 (DB1)
/DB2: P1.A17 (DB2)
/DB3: P1.A18 (DB3)
/DB4: P1.A19 (DB4)
/DB5: P1.A20 (DB5)
/DB6: P1.A21 (DB6)
/DB7: P1.A22 (DB7)
/DB8: P1.A56 (DB8)
/DB9: P1.A57 (DB9)
/DB10: P1.A58 (DB10)
/DB11: P1.A59 (DB11)
/DB12: P1.A60 (DB12)
/DB13: P1.A61 (DB13)
/DB14: P1.A62 (DB14)
/DB15: P1.A63 (DB15)
/FPO0: P1.B63 (FPO0)
/FPO1: P1.B64 (FPO1)
/FPO2: P1.B65 (FPO2)
/FPO3: P1.B66 (FPO3)
/FPO4: P1.B68 (FPO4)
/FPO5: P1.B69 (FPO5)
/FPO6: P1.B72 (FPO6)
/FPO7: P1.B73 (FPO7)
/IBUS0: P1.B7 (IBUS0)
/IBUS1: P1.B8 (IBUS1)
/IBUS2: P1.B9 (IBUS2)
/IBUS3: P1.B10 (IBUS3)
/IBUS4: P1.B11 (IBUS4)
/IBUS5: P1.B12 (IBUS5)
/IBUS6: P1.B13 (IBUS6)
/IBUS7: P1.B14 (IBUS7)
/IBUS8: P1.B34 (IBUS8)
/IBUS9: P1.B35 (IBUS9)
/IBUS10: P1.B36 (IBUS10)
/IBUS11: P1.B37 (IBUS11)
/IBUS12: P1.B38 (IBUS12)
/IBUS13: P1.B39 (IBUS13)
/IBUS14: P1.B40 (IBUS14)
/IBUS15: P1.B41 (IBUS15)
/RADDR0: P1.B15 (RADDR0)
/RADDR1: P1.B16 (RADDR1)
/RADDR2: P1.B17 (RADDR2)
/RADDR3: P1.B18 (RADDR3)
/RADDR4: P1.B19 (RADDR4)
/T34: P1.B5 (T34)
/WADDR0: P1.B20 (WADDR0)
/WADDR1: P1.B21 (WADDR1)
/WADDR2: P1.B22 (WADDR2)
/WADDR3: P1.B23 (WADDR3)
/WADDR4: P1.B24 (WADDR4)
/WSTB: P1.A5 (WSTB)
/~ENDEXT: P1.A72 (~ENDEXT)
/~HALT: P1.B60 (~HALT)
/~IO: P1.B26 (~IO)
/~IODEV1xx: P1.A24 (~IODEV1xx)
/~IODEV2xx: P1.A25 (~IODEV2xx)
/~IODEV3xx: P1.A26 (~IODEV3xx)
/~IRQ: P1.B42 (~IRQ)
/~IRQ0: P1.A51 (~IRQ0)
/~IRQ1: P1.A52 (~IRQ1)
/~IRQ2: P1.A53 (~IRQ2)
/~IRQ3: P1.A54 (~IRQ3)
/~IRQ4: P1.A55 (~IRQ4)
/~IRQ5: P1.A67 (~IRQ5)
/~IRQ6: P1.A68 (~IRQ6)
/~IRQ7: P1.A70 (~IRQ7)
/~IRQS: P1.B43 (~IRQS)
/~MEM: P1.B25 (~MEM)
/~R: P1.A27 (~R)
/~RESET: P1.B6 (~RESET)
/~RSTHOLD: P1.A6 (~RSTHOLD)
/~SKIPEXT: P1.A73 (~SKIPEXT)
/~SYSDEV: P1.A23 (~SYSDEV)
/~W: P1.A28 (~W)
/~WS: P1.B27 (~WS)
GND: C1.2, C2.2, P1.B1 (GND), P1.B2 (GND), P1.B81 (GND), P1.B82 (GND)

Board: 2 copper layers, 3 parts (0 on the bottom side), 2 nets, no tracks yet.
