alexiosc/cft/kicad/cft/tic/tic-r2044.kicad_pcb

## KiCad design kicad/cft/tic/tic-r2044.kicad_pcb (2020-11-11)

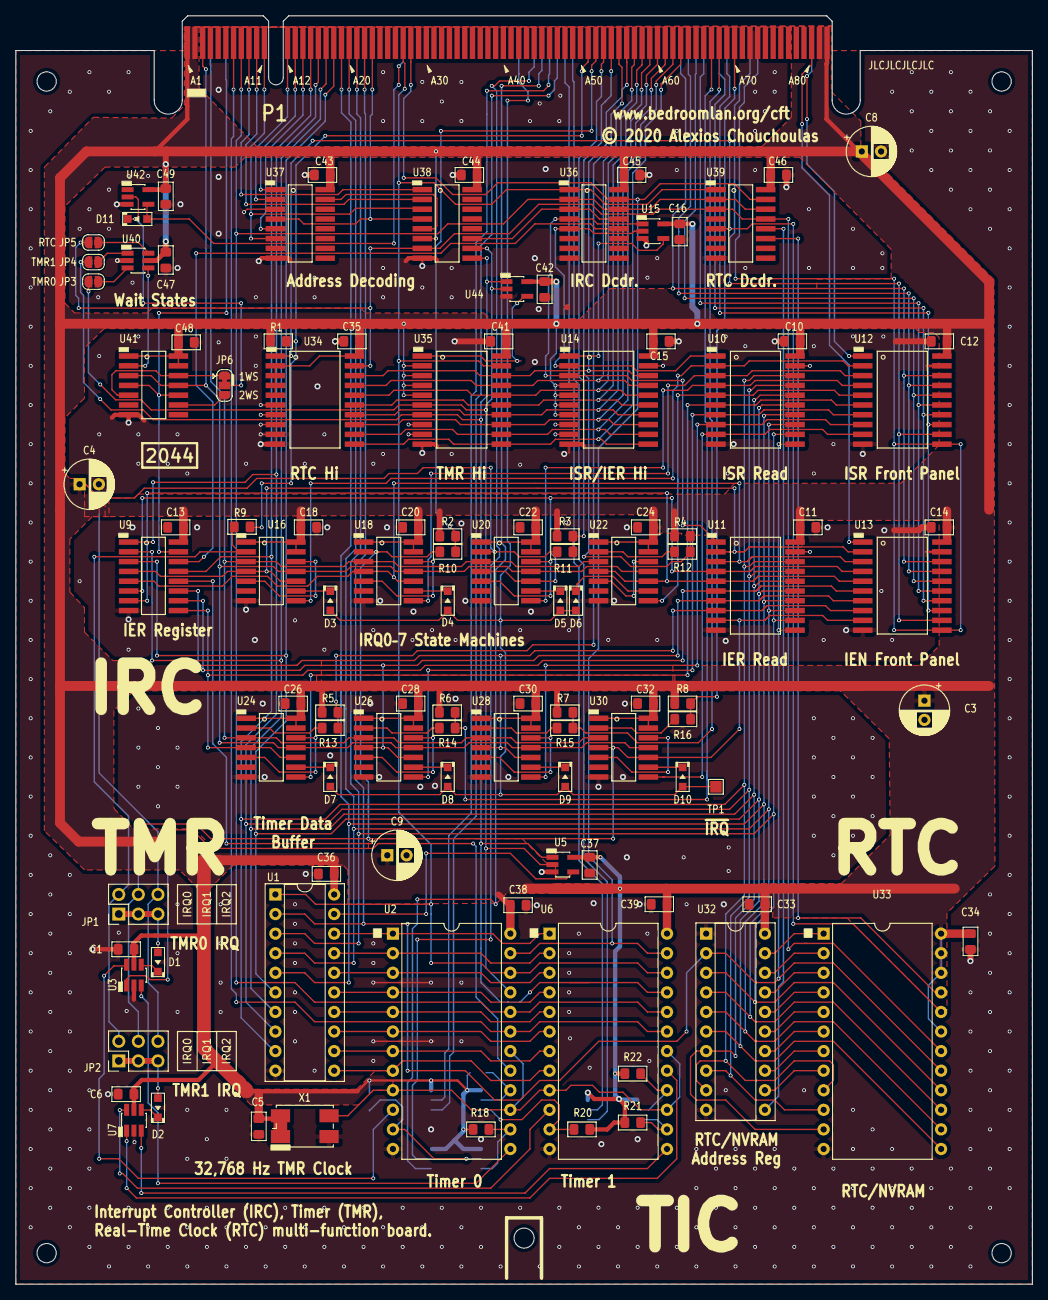
[picture p112: board tic-r2044.kicad_pcb from above]

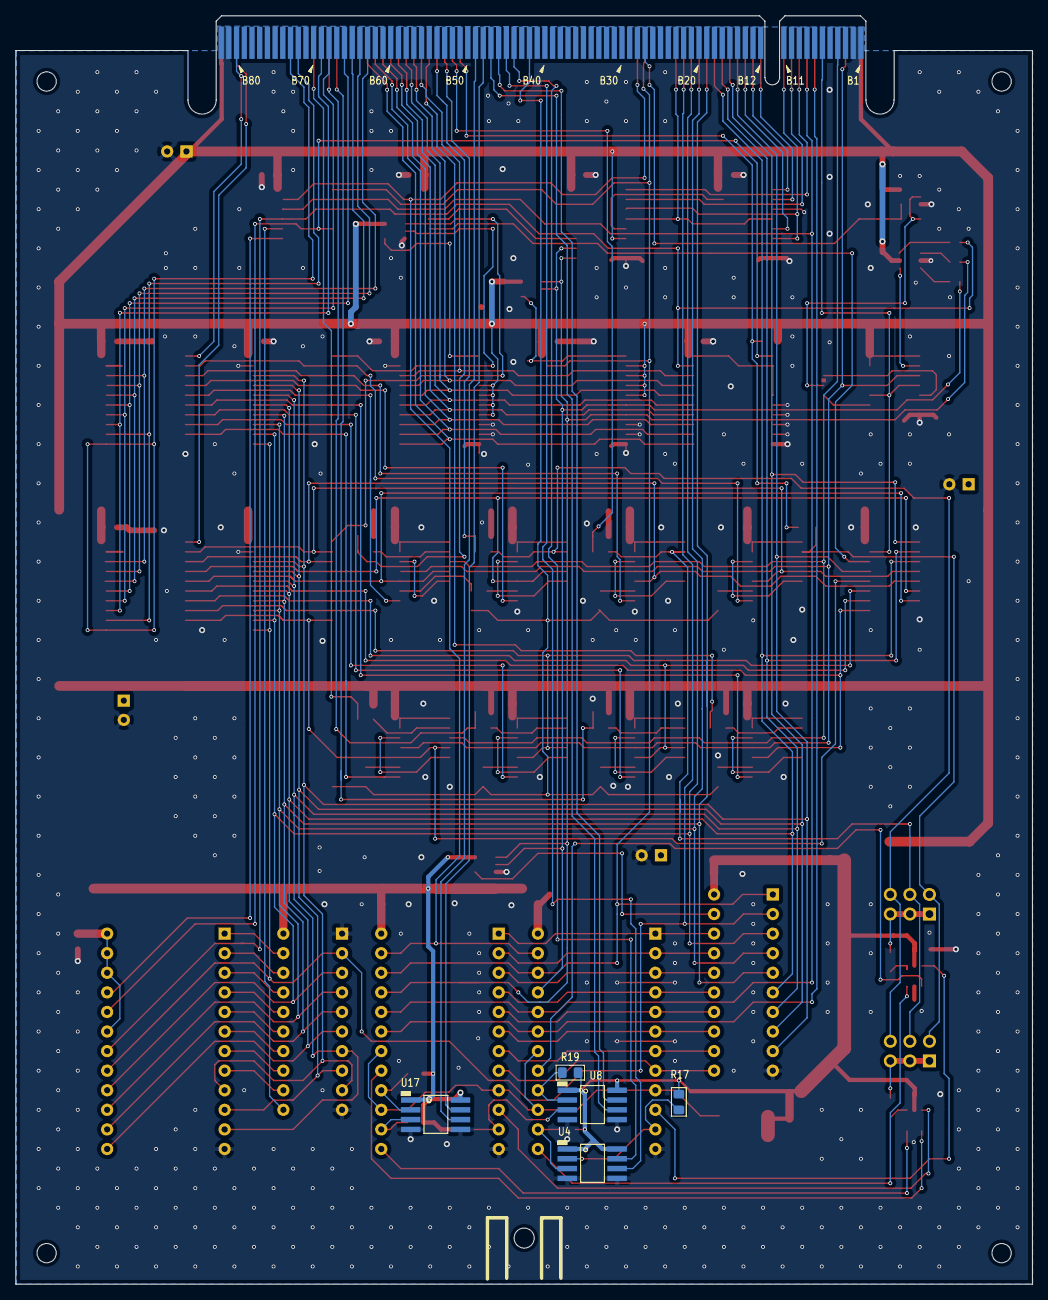
[picture p113: board tic-r2044.kicad_pcb from below]

Board: 2 copper layers, 131.9 x 164.6 mm, 116 parts (5 on the bottom side), 152 nets.

Parts:
C1, C5, C6, C10, C11, C12, C13, C14, C15, C16, C33, C34, C35, C36, C37, C38, C39, C41, C42, C43, C44, C45, C46, C47, C48, C49: 100nF; C_SMD_0805_2012Metric_Pad1.15x1.40mm_HandSolder
C3, C4, C8, C9: 47µF; CP_Radial_D6.3mm_P2.50mm
C18, C20, C22, C24, C26, C28, C30, C32: 100n; C_SMD_0805_2012Metric_Pad1.15x1.40mm_HandSolder
D1, D2, D3, D4, D5, D6, D7, D8, D9, D10, D11: CUS520; SOD-323
JP1, JP2: Conn_02x03_Odd_Even; PinHeader_2x03_P2.54mm_Vertical
JP3, JP4, JP5: SolderJumper_2_Open; SolderJumper-2_P1.3mm_Open_RoundedPad1.0x1.5mm
JP6: SolderJumper_3_Open; SolderJumper-3_P1.3mm_Bridged12_RoundedPad1.0x1.5mm
P1: CFT-2019-Bus; CFT-2019-Card-Edge
R1, R2, R3, R4, R5, R6, R7, R8, R17, R18, R19, R20, R21, R22: 4.7kΩ; R_SMD_0805_2012Metric_Pad1.15x1.40mm_HandSolder
R9, R10, R11, R12, R13, R14, R15, R16: 100Ω; R_SMD_0805_2012Metric_Pad1.15x1.40mm_HandSolder
TP1: TestPoint; TestPoint_Pad_1.5x1.5mm
U1: 74HCT245; DIP-20_W7.62mm_Socket
U2, U6: 8254; DIP-24_W15.24mm_socket
U3, U7: 74LVC1G10; SOT-23-6_Handsoldering
U4, U8, U17: USB6B1; SOIC-8
U5, U15, U44: 74LVC1G08; SOT-23-5_HandSoldering
U9: 74HC259; SOIC-16
U10, U11, U12, U13, U14, U34, U35: 74HC541; SOIC-20W
U16, U18, U20, U22, U24, U26, U28, U30, U41: 74HC74; SOIC-14
U32: 74HC574; DIP-20_W7.62mm_Socket
U33: M48T02-70PC1; eDIP-24_W15.24mm
U36, U39: 74HC139; SOIC-16
U37, U38: 74HC138; SOIC-16
U40: 74LVC1G11; SOT-23-6_Handsoldering
U42: 74LVC1G07; SOT-23-5_HandSoldering
X1: 32.768 kHz; Crystal_SMD_7050-4Pin_7.0x5.0mm

Connections:
+5V: C1.1, C3.1, C4.1, C5.1, C6.1, C8.1, C9.1, C10.1, C11.1, C12.1, C13.1, C14.1, C15.1, C16.1, C18.1, C20.1, C22.1, C24.1, C26.1, C28.1, C30.1, C32.1, C33.1, C34.1, C35.1, C36.1, C37.1, C38.1, C39.1, C41.1, C42.1, C43.1, C44.1, C45.1, C46.1, C47.1, C48.1, C49.1, P1.A1, P1.A2, P1.A81, P1.A82, R1.1, R2.1, R3.1, R4.1, R5.1, R6.1, R7.1, R8.1, R17.1, R18.1, R19.1, R20.1, R21.1, R22.1, U1.20, U2.24, U3.5, U4.1, U4.8, U5.5, U6.24, U7.5, U8.1, U8.8, U9.16, U10.20, U11.20, U12.20, U13.20, U14.4, U14.5, U14.6, U14.7, U14.20, U15.5, U16.1, U16.13, U16.14, U17.1, U17.8, U18.1, U18.13, U18.14, U20.1, U20.13, U20.14, U22.1, U22.13, U22.14, U24.1, U24.13, U24.14, U26.1, U26.13, U26.14, U28.1, U28.13, U28.14, U30.1, U30.13, U30.14, U32.20, U33.19, U33.22, U33.23, U33.24, U34.2, U34.3, U34.4, U34.5, U34.20, U35.2, U35.3, U35.4, U35.5, U35.20, U36.16, U37.16, U38.6, U38.16, U39.16, U40.5, U41.1, U41.13, U41.14, U42.5, U44.5, X1.1, X1.4
/AB0: P1.A7, U2.19, U6.19
/AB1: P1.A8, U2.20, U6.20, U36.2, U36.14, U39.2, U39.14
/AB2: P1.A9, U38.1
/AB3: P1.A10, U38.2
/AB4: P1.A11, U37.6, U38.3
/AB5: P1.A12, U37.2
/AB6: P1.A13, U37.1
/AB7: P1.A14, U37.5
/Bus Interface/~IRCCS: U36.3, U36.13, U38.11
/Bus Interface/~SEL: U40.4, U41.2
/CLK2: P1.B4, U16.3, U18.3, U20.3, U22.3, U24.3, U26.3, U28.3, U30.3
/CLK3: P1.A3, U16.11, U18.11, U20.11, U22.11, U24.11, U26.11, U28.11, U30.11, U41.3, U41.11
/G0-0: P1.B44, U4.7
/G0-1: P1.B45, U4.6
/G0-2: P1.B46, U8.7
/G1-0: P1.B47, U8.6
/G1-1: P1.B49, U17.6
/G1-2: P1.B48, U17.7
/Interrupt Controller/DB0: P1.A15, U1.9, U9.13, U10.18, U11.18, U32.9, U33.9
/Interrupt Controller/DB1: P1.A16, U1.8, U9.1, U10.17, U11.17, U32.8, U33.10
/Interrupt Controller/DB2: P1.A17, U1.7, U9.2, U10.16, U11.16, U32.7, U33.11
/Interrupt Controller/DB3: P1.A18, U1.6, U9.3, U10.15, U11.15, U32.6, U33.13
/Interrupt Controller/DB4: P1.A19, U1.5, U10.14, U11.14, U32.5, U33.14
/Interrupt Controller/DB5: P1.A20, U1.4, U10.13, U11.13, U32.4, U33.15
/Interrupt Controller/DB6: P1.A21, U1.3, U10.12, U11.12, U32.3, U33.16
/Interrupt Controller/DB7: P1.A22, U1.2, U10.11, U11.11, U32.2, U33.17
/Interrupt Controller/DB8: P1.A56, U14.18, U34.18, U35.18
/Interrupt Controller/DB9: P1.A57, U14.17, U34.17, U35.17
/Interrupt Controller/DB10: P1.A58, U14.16, U34.16, U35.16
/Interrupt Controller/DB11: P1.A59, U14.15, U34.15, U35.15
/Interrupt Controller/DB12: P1.A60, U14.14, U34.14, U35.14
/Interrupt Controller/DB13: P1.A61, U14.13, U34.13, U35.13
/Interrupt Controller/DB14: P1.A62, U14.12, U34.12, U35.12
/Interrupt Controller/DB15: P1.A63, U14.11, U34.11, U35.11
/Interrupt Controller/FPD0: P1.B63, U12.18, U13.18
/Interrupt Controller/FPD1: P1.B64, U12.17, U13.17
/Interrupt Controller/FPD2: P1.B65, U12.16, U13.16
/Interrupt Controller/FPD3: P1.B66, U12.15, U13.15
/Interrupt Controller/FPD4: P1.B68, U12.14, U13.14
/Interrupt Controller/FPD5: P1.B69, U12.13, U13.13
/Interrupt Controller/FPD6: P1.B72, U12.12, U13.12
/Interrupt Controller/FPD7: P1.B73, U12.11, U13.11
/Interrupt Controller/IEN0: U9.4, U11.2, U13.2, U16.4, U16.10
/Interrupt Controller/IEN1: U9.5, U11.3, U13.3, U18.4, U18.10
/Interrupt Controller/IEN2: U9.6, U11.4, U13.4, U20.4, U20.10
/Interrupt Controller/IEN3: U9.7, U11.5, U13.5, U22.4, U22.10
/Interrupt Controller/IEN4: U9.9, U11.6, U13.6, U24.4, U24.10
/Interrupt Controller/IEN5: U9.10, U11.7, U13.7, U26.4, U26.10
/Interrupt Controller/IEN6: U9.11, U11.8, U13.8, U28.4, U28.10
/Interrupt Controller/IEN7: U9.12, U11.9, U13.9, U30.4, U30.10
/Interrupt Controller/IRF0: U10.2, U12.2, U16.8
/Interrupt Controller/IRF1: U10.3, U12.3, U18.8
/Interrupt Controller/IRF2: U10.4, U12.4, U20.8
/Interrupt Controller/IRF3: U10.5, U12.5, U22.8
/Interrupt Controller/IRF4: U10.6, U12.6, U24.8
/Interrupt Controller/IRF5: U10.7, U12.7, U26.8
/Interrupt Controller/IRF6: U10.8, U12.8, U28.8
/Interrupt Controller/IRF7: U10.9, U12.9, U30.8
/Interrupt Controller/sheet5FC1EA73/~IRQTP: D3.1, U16.9
/Interrupt Controller/sheet5FC1EA73/~IRQn-CLK2: U16.5, U16.12
/Interrupt Controller/sheet5FD4BB79/~IRQTP: D4.1, U18.9
/Interrupt Controller/sheet5FD4BB79/~IRQn-CLK2: U18.5, U18.12
/Interrupt Controller/sheet5FD6EAC2/~IRQTP: D5.1, U20.9
/Interrupt Controller/sheet5FD6EAC2/~IRQn-CLK2: U20.5, U20.12
/Interrupt Controller/sheet5FD6EAC3/~IRQTP: D6.1, U22.9
/Interrupt Controller/sheet5FD6EAC3/~IRQn-CLK2: U22.5, U22.12
/Interrupt Controller/sheet5FD81CDA/~IRQTP: D7.1, U24.9
/Interrupt Controller/sheet5FD81CDA/~IRQn-CLK2: U24.5, U24.12
/Interrupt Controller/sheet5FD81CDB/~IRQTP: D8.1, U26.9
/Interrupt Controller/sheet5FD81CDB/~IRQn-CLK2: U26.5, U26.12
/Interrupt Controller/sheet5FD81CDC/~IRQTP: D9.1, U28.9
/Interrupt Controller/sheet5FD81CDC/~IRQn-CLK2: U28.5, U28.12
/Interrupt Controller/sheet5FD81CDD/~IRQTP: D10.1, U30.9
/Interrupt Controller/sheet5FD81CDD/~IRQn-CLK2: U30.5, U30.12
/Interrupt Controller/~IRQ0: P1.A51, R1.2, R9.2
/Interrupt Controller/~IRQ1: P1.A52, R2.2, R10.2
/Interrupt Controller/~IRQ2: P1.A53, R3.2, R11.2
/Interrupt Controller/~IRQ3: P1.A54, R4.2, R12.2
/Interrupt Controller/~IRQ3i: R12.1, U22.2
/Interrupt Controller/~IRQ4: P1.A55, R5.2, R13.2
/Interrupt Controller/~IRQ4i: R13.1, U24.2
/Interrupt Controller/~IRQ5: P1.A67, R6.2, R14.2
/Interrupt Controller/~IRQ5i: R14.1, U26.2
/Interrupt Controller/~IRQ6: P1.A68, R7.2, R15.2
/Interrupt Controller/~IRQ6i: R15.1, U28.2
/Interrupt Controller/~IRQ7: P1.A70, R8.2, R16.2
/Interrupt Controller/~IRQ7i: R16.1, U30.2
/Real Time Clock/RTCA0: U32.12, U33.8
/Real Time Clock/RTCA1: U32.13, U33.7
/Real Time Clock/RTCA2: U32.14, U33.6
/Real Time Clock/RTCA3: U32.15, U33.5
/Real Time Clock/RTCA4: U32.16, U33.4
/Real Time Clock/RTCA5: U32.17, U33.3
/Real Time Clock/RTCA6: U32.18, U33.2
/Real Time Clock/RTCA7: U32.19, U33.1
/Timers/G0-0: R17.2, U2.11, U4.2
/Timers/G0-1: R18.2, U2.14, U4.3
/Timers/G0-2: R19.2, U2.16, U8.2
/Timers/G1-0: R20.2, U6.11, U8.3
/Timers/G1-1: R21.2, U6.14, U17.3
/Timers/G1-2: R22.2, U6.16, U17.2
/Timers/OUT0-0: U2.10, U3.6
/Timers/OUT0-1: U2.13, U3.3
/Timers/OUT0-2: U2.17, U3.1
/Timers/OUT1-0: U6.10, U7.6
/Timers/OUT1-1: U6.13, U7.3
/Timers/OUT1-2: U6.17, U7.1
/Timers/TCLK: U2.9, U2.15, U2.18, U6.9, U6.15, U6.18, X1.3
/Timers/TD0: U1.11, U2.8, U6.8
/Timers/TD1: U1.12, U2.7, U6.7
/Timers/TD2: U1.13, U2.6, U6.6
/Timers/TD3: U1.14, U2.5, U6.5
/Timers/TD4: U1.15, U2.4, U6.4
/Timers/TD5: U1.16, U2.3, U6.3
/Timers/TD6: U1.17, U2.2, U6.2
/Timers/TD7: U1.18, U2.1, U6.1
/Timers/~CS: U1.19, U5.4
/~FPIEN: P1.A80, U13.1
/~FPIRF: P1.B80, U12.1
/~IRQ: D3.2, D4.2, D5.2, D6.2, D7.2, D8.2, D9.2, D10.2, P1.B42, TP1.1
/~IRQ0i: JP1.2, JP2.2, R9.1, U16.2
/~IRQ1i: JP1.4, JP2.4, R10.1, U18.2
/~IRQ2i: JP1.6, JP2.6, R11.1, U20.2
/~R: P1.A27, U1.1, U2.22, U6.22, U35.19, U36.1, U39.1
/~RESET: P1.B6, U9.15, U41.4, U41.10
/~RIER: U11.1, U14.3, U15.1, U36.4
/~RISR: U10.1, U14.2, U15.2, U36.5
/~RTCAW: U32.11, U39.12
/~RTCCS: JP5.1, U33.18, U34.19, U38.7, U39.3, U39.13
/~RTCR: U33.20, U34.1, U39.5
/~RTCW: U33.21, U39.11
/~SYSDEV: P1.A23, U37.4, U38.4
/~T0CS: JP3.1, U2.21, U5.2, U35.6, U38.10, U44.2
/~T1CS: JP4.1, U5.1, U6.21, U35.7, U38.9, U44.1
/~W: P1.A28, U2.23, U6.23, U36.15, U39.15
/~WIER: U9.14, U36.12
/~WS: D11.2, P1.B27, U42.4
GND: C1.2, C3.2, C4.2, C5.2, C6.2, C8.2, C9.2, C10.2, C11.2, C12.2, C13.2, C14.2, C15.2, C16.2, C18.2, C20.2, C22.2, C24.2, C26.2, C28.2, C30.2, C32.2, C33.2, C34.2, C35.2, C36.2, C37.2, C38.2, C39.2, C41.2, C42.2, C43.2, C44.2, C45.2, C46.2, C47.2, C48.2, C49.2, P1.A72, P1.A73, P1.B1, P1.B2, P1.B81, P1.B82, U1.10, U2.12, U3.2, U4.4, U4.5, U5.3, U6.12, U7.2, U8.4, U8.5, U9.8, U10.10, U10.19, U11.10, U11.19, U12.10, U12.19, U13.10, U13.19, U14.8, U14.9, U14.10, U14.19, U15.3, U16.7, U17.4, U17.5, U18.7, U20.7, U22.7, U24.7, U26.7, U28.7, U30.7, U32.1, U32.10, U33.12, U34.6, U34.7, U34.8, U34.9, U34.10, U35.8, U35.9, U35.10, U36.8, U37.3, U37.8, U38.8, U39.8, U40.2, U41.7, U42.3, U44.3, X1.2
unnamed: D1.1, U3.4
unnamed: D1.2, JP1.1, JP1.3, JP1.5
unnamed: D2.1, U7.4
unnamed: D2.2, JP2.1, JP2.3, JP2.5
unnamed: D11.1, JP6.2, U42.2
unnamed: JP3.2, U40.3
unnamed: JP4.2, U40.1
unnamed: JP5.2, U40.6
unnamed: JP6.1, U41.5, U41.12
unnamed: JP6.3, U41.9
unnamed: U14.1, U15.4
unnamed: U35.1, U44.4
unnamed: U37.15, U38.5
