alexiosc/cft/kicad/cft/mem/cft-ctl-dip.kicad_pcb

## KiCad design kicad/cft/mem/cft-ctl-dip.kicad_pcb (2021-02-09)

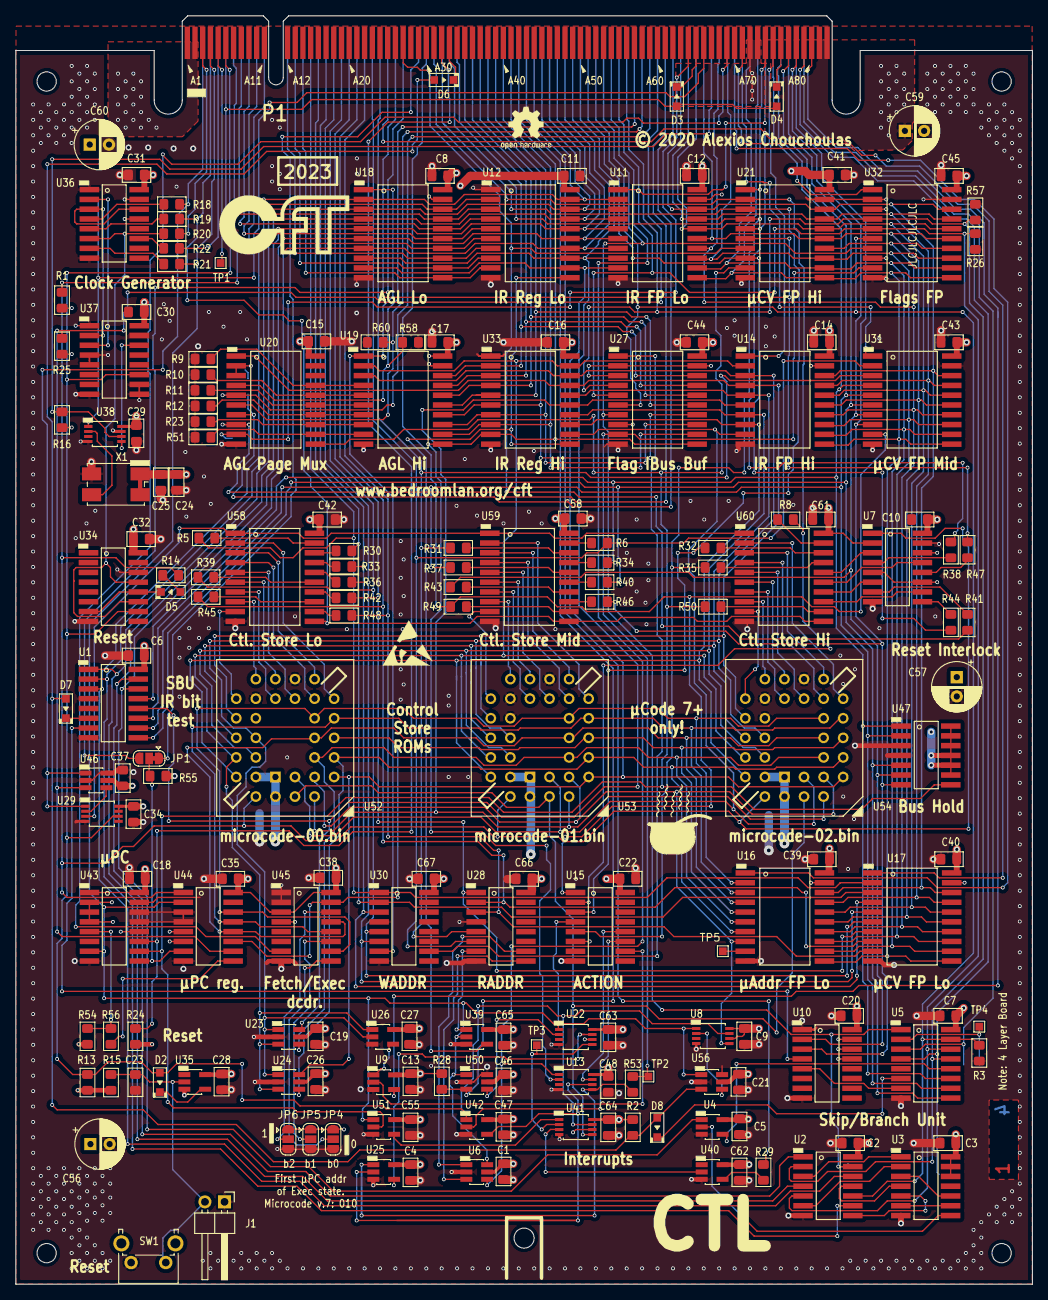
[picture p114: board cft-ctl-dip.kicad_pcb from above]

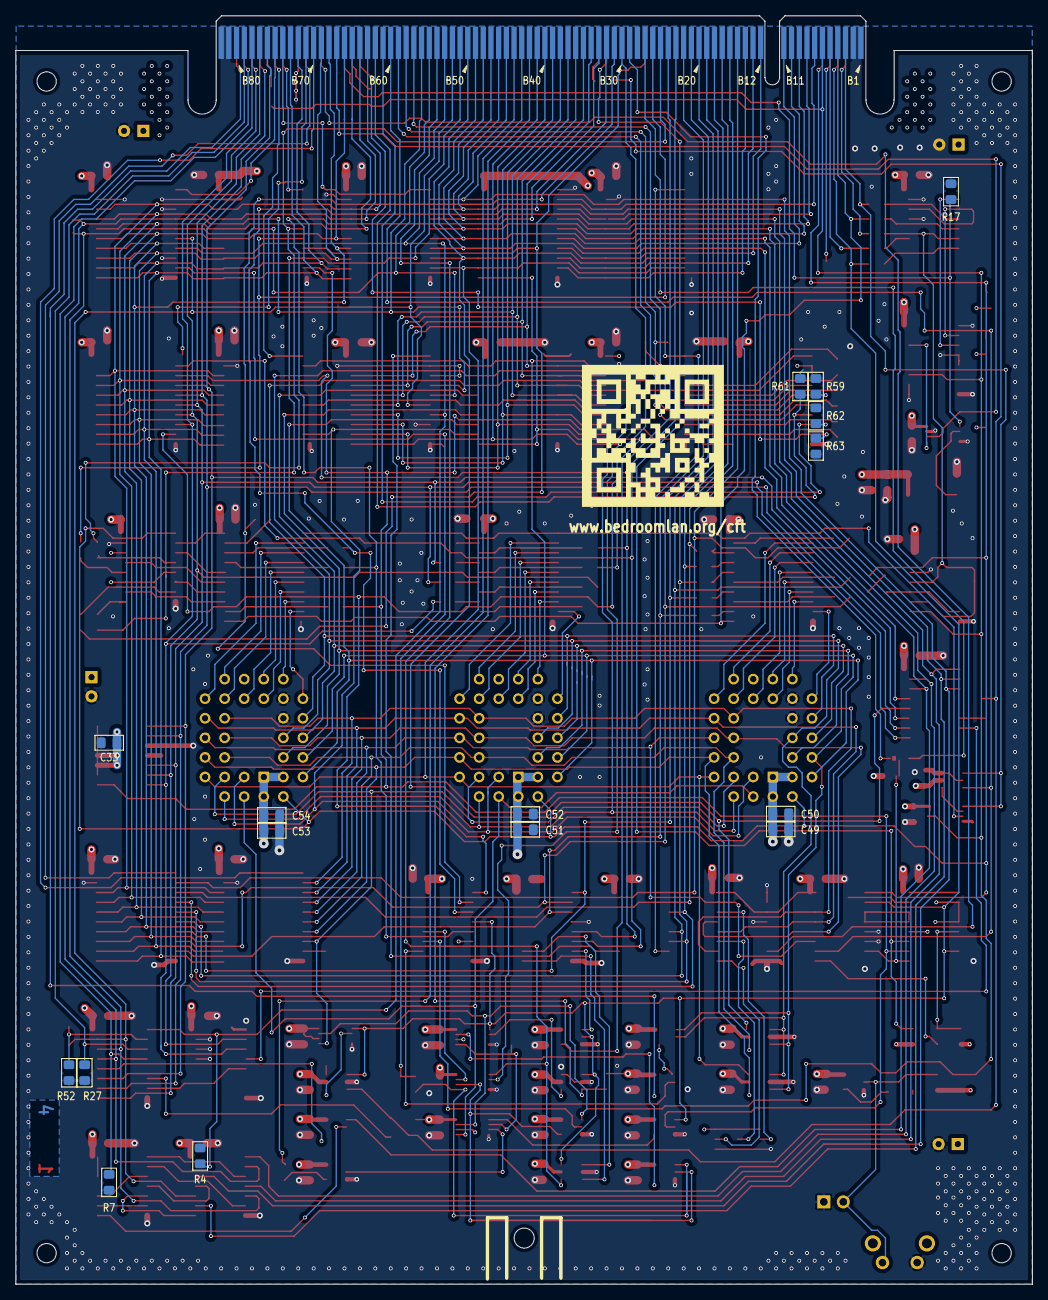
[picture p115: board cft-ctl-dip.kicad_pcb from below]

Board: 4 copper layers, 131.9 x 164.6 mm, 205 parts (16 on the bottom side), 229 nets.

Parts:
C1, C2, C3, C4, C5, C6, C7, C8, C9, C10, C11, C12, C13, C14, C15, C16, C17, C18, C19, C20, C21, C22, C23, C25, C26, C27, C29, C30, C31, C32, C33, C34, C35, C37, C38, C39, C40, C41, C42, C43, C44, C45, C46, C47, C48, C50, C52, C54, C55, C58, C61, C62, C63, C64, C65, C66, C67: 100nF; C_SMD_0805_2012Metric_Pad1.15x1.40mm_HandSolder
C24, C49, C51, C53: 10µF; C_SMD_0805_2012Metric_Pad1.15x1.40mm_HandSolder
C28: 47µF; C_SMD_0805_2012Metric_Pad1.15x1.40mm_HandSolder
C56, C57, C59, C60: 47µF; CP_Radial_D6.3mm_P2.50mm
D2, D3, D4, D5, D6, D7, D8: CUS520; SOD-323
J1: Conn_01x02; PinHeader_1x02_P2.54mm_Horizontal
JP1: Jumper_3_Bridged12; SolderJumper-3_P1.3mm_Bridged12_RoundedPad1.0x1.5mm
JP4, JP6: SolderJumper_3_Bridged23; SolderJumper-3_P1.3mm_Open_RoundedPad1.0x1.5mm
JP5: SolderJumper_3_Bridged12; SolderJumper-3_P1.3mm_Open_RoundedPad1.0x1.5mm
P1: CFT-2019-Bus; CFT-2019-Card-Edge
R1, R2, R3, R4, R7, R9, R10, R11, R12, R13, R15, R16, R17, R23, R24, R25, R26, R27, R28, R51, R52, R54, R55, R57, R58, R59, R60, R61, R62, R63: 4.7kΩ; R_SMD_0805_2012Metric_Pad1.15x1.40mm_HandSolder
R5, R6, R8, R30, R31, R32, R33, R34, R35, R36, R37, R38, R39, R40, R41, R42, R43, R44, R45, R46, R47, R48, R49, R50: 0Ω/30Ω; R_SMD_0805_2012Metric_Pad1.15x1.40mm_HandSolder
R14, R18, R19, R20, R21, R22, R29, R53: 30Ω; R_SMD_0805_2012Metric_Pad1.15x1.40mm_HandSolder
R56: 0Ω; R_SMD_0805_2012Metric_Pad1.15x1.40mm_HandSolder
SW1: tactile_switch; SW_Tactile_SPST_Angled_PTS645Vx39-2LFS
TP1, TP2, TP3, TP4, TP5: TestPoint; TestPoint_Pad_1.0x1.0mm
U1, U5, U43: 74HC251; SOIC-16
U2: 74AC08; SOIC-14
U3: 74AC32; SOIC-14
U4: 74LVC1G86; SOT-23-5_HandSoldering
U6: 74LVC1G0832; SOT-23-6_Handsoldering
U7: 74AC157; SOIC-16
U8, U13, U22, U29, U41: 74LVC1G74; TSSOP-8_3x3mm_P0.65mm
U9, U39, U51: 74LVC1G32; SOT-23-5_HandSoldering
U10, U36: 74HC139; SOIC-16
U11, U14, U16, U17, U18, U19, U21, U27, U31, U32: 74HC541; SOIC-20W
U12, U20, U33, U58, U59, U60: 74HC574; SOIC-20W
U15, U28, U30: 74HC138; SOIC-16
U23, U24: 74LVC1G11; SOT-23-6_Handsoldering
U25, U42: 74LVC1G08; SOT-23-5_HandSoldering
U26: 74LVC1G00; SOT-23-5_HandSoldering
U34: 74HC590; SOIC-16
U35: 74LVC1G17; SOT-23-5_HandSoldering
U37: 74AC191; SOIC-16
U38: 74LVC2G157; TSSOP-8_3x3mm_P0.65mm
U40: 74LVC1G04; SOT-23-5_HandSoldering
U44: 74AC161; SOIC-16
U45: 74HC85; SOIC-16
U46, U50, U56: 74LVC1G373; SOT-23-6_Handsoldering
U47: SN74ACT1071; SOIC-14
U52, U53, U54: AT27C020; PLCC32
X1: 16 MHz; Crystal_SMD_7050-4Pin_7.0x5.0mm

Connections:
+5V: C1.1, C2.1, C3.1, C4.1, C5.1, C6.1, C7.1, C8.1, C9.1, C10.1, C11.1, C12.1, C13.1, C14.1, C15.1, C16.1, C17.1, C18.1, C19.1, C20.1, C21.1, C22.1, C24.1, C25.1, C26.1, C27.1, C28.1, C29.1, C30.1, C31.1, C32.1, C33.1, C34.1, C35.1, C37.1, C38.1, C39.1, C40.1, C41.1, C42.1, C43.1, C44.1, C45.1, C46.1, C47.1, C48.1, C49.1, C50.1, C51.1, C52.1, C53.1, C54.1, C55.1, C56.1, C57.1, C58.1, C59.1, C60.1, C61.1, C62.1, C63.1, C64.1, C65.1, C66.1, C67.1, JP4.1, JP5.1, JP6.1, P1.A1, P1.A2, P1.A81, P1.A82, R1.2, R2.1, R13.1, R15.1, R16.1, R24.2, R25.2, R28.1, R54.2, R55.2, U1.16, U2.14, U3.12, U3.13, U3.14, U4.5, U5.16, U6.5, U7.2, U7.5, U7.11, U7.14, U7.16, U8.6, U8.8, U9.5, U10.16, U11.20, U12.20, U13.8, U14.20, U15.6, U15.16, U16.20, U17.20, U18.20, U19.20, U20.2, U20.3, U20.20, U21.20, U22.6, U22.8, U23.5, U24.5, U25.5, U26.5, U27.20, U28.16, U29.7, U29.8, U30.16, U31.20, U32.20, U33.20, U34.16, U35.5, U36.16, U37.16, U38.8, U39.5, U40.5, U41.6, U41.8, U42.5, U43.1, U43.2, U43.3, U43.4, U43.12, U43.16, U44.16, U45.3, U45.16, U46.5, U47.9, U47.10, U47.11, U47.12, U47.13, U47.14, U50.5, U51.5, U52.1, U52.31, U52.32, U53.1, U53.31, U53.32, U54.1, U54.31, U54.32, U56.5, U58.20, U59.20, U60.20, X1.1, X1.4
/Addressing Modes/IBUS0: P1.B7, U12.2, U18.18
/Addressing Modes/IBUS1: P1.B8, U12.3, U18.17
/Addressing Modes/IBUS2: P1.B9, U12.4, U18.16
/Addressing Modes/IBUS3: P1.B10, U12.5, U18.15
/Addressing Modes/IBUS4: P1.B11, U12.6, U18.14
/Addressing Modes/IBUS5: P1.B12, U12.7, U18.13
/Addressing Modes/IBUS6: P1.B13, U12.8, U18.12
/Addressing Modes/IBUS7: P1.B14, U12.9, U18.11
/Addressing Modes/IBUS8: P1.B34, U19.18, U27.18, U33.2
/Addressing Modes/IBUS9: P1.B35, U19.17, U27.17, U33.3
/Addressing Modes/IBUS10: P1.B36, U19.16, U27.16, U33.4
/Addressing Modes/IBUS11: P1.B37, U19.15, U27.15, U33.5
/Addressing Modes/IBUS12: P1.B38, U19.14, U27.14, U33.6
/Addressing Modes/IBUS13: P1.B39, U19.13, U27.13, U33.7
/Addressing Modes/IBUS14: P1.B40, U19.12, U27.12, U33.8
/Addressing Modes/PAGE0: R9.1, U19.4, U20.17
/Addressing Modes/PAGE1: R10.1, U19.5, U20.16
/Addressing Modes/PAGE2: R11.1, U19.6, U20.15
/Addressing Modes/PAGE3: R12.1, U19.7, U20.14
/Addressing Modes/PAGE4: R23.1, U19.8, U20.13
/Addressing Modes/PAGE5: R51.1, U19.9, U20.12
/CEXT8: P1.A79, R7.2, U5.4
/CEXT9: P1.B79, R27.2, U5.3
/CEXT10: R52.2, TP4.1, U5.2
/CLK1: P1.B3, R18.1, U29.1, U46.1
/CLK2: P1.B4, R19.1, U58.11, U59.11, U60.11
/CLK3: P1.A3, R20.1
/CLK4: P1.A4, R21.1, U6.6, U8.1, U15.4, U22.1, U39.2, U43.7, U44.2, U50.1, U51.1, U56.1
/COND0: P1.B76, R34.1, U1.11, U5.11, U31.4, U47.1
/COND1: P1.A77, R37.1, U1.10, U5.10, U31.5, U47.2
/COND2: P1.B77, R40.1, U1.9, U5.9, U31.6, U47.5
/COND3: P1.A78, R43.1, U10.2, U31.7, U47.6
/COND4: P1.B78, R46.1, U10.3, U31.8, U47.7
/Clock Generator/CLK: U38.2, X1.3
/Clock Generator/CLK1₀: R18.2, U36.4
/Clock Generator/CLK2₀: R19.2, U36.5
/Clock Generator/CLK3₀: R20.2, U34.11, U34.13, U36.6
/Clock Generator/CLK4₀: R21.2, U36.7
/Clock Generator/CLKIN: U37.14, U38.5
/Clock Generator/T34₀: R22.2, U36.11
/Clock Generator/÷2: U36.2, U37.3
/Clock Generator/÷4: U36.3, U36.14, U37.2
/FI: R53.1, TP2.1, U27.9, U32.9
/FL: P1.B52, R3.1, U2.10, U5.15, U27.6, U32.6
/FN: P1.B56, R57.1, U2.2, U5.13, U27.4, U32.4
/FPCLK: P1.A66, R17.1, U38.1
/FPFETCH∕~EXEC: P1.A69, U45.7
/FV: P1.B53, R4.1, U2.13, U5.1, U27.7, U32.7
/FZ: P1.B55, R26.1, U2.5, U5.14, U27.5, U32.5
/Flag Unit/FPD0: P1.B63, U11.18, U14.18, U16.18, U17.18, U21.18, U31.18, U32.18
/Flag Unit/FPD1: P1.B64, U11.17, U14.17, U16.17, U17.17, U21.17, U31.17, U32.17
/Flag Unit/FPD2: P1.B65, U11.16, U14.16, U16.16, U17.16, U21.16, U31.16, U32.16
/Flag Unit/FPD3: P1.B66, U11.15, U14.15, U16.15, U17.15, U21.15, U31.15, U32.15
/Flag Unit/FPD4: P1.B68, U11.14, U14.14, U16.14, U17.14, U21.14, U31.14, U32.14
/Flag Unit/FPD5: P1.B69, U11.13, U14.13, U16.13, U17.13, U21.13, U31.13, U32.13
/Flag Unit/FPD6: P1.B72, U11.12, U14.12, U16.12, U17.12, U21.12, U31.12, U32.12
/Flag Unit/FPD7: P1.B73, U11.11, U14.11, U16.11, U17.11, U21.11, U31.11, U32.11
/Flag Unit/RADDR0: P1.B15, R5.1, U17.2, U30.1
/Flag Unit/RADDR1: P1.B16, R30.1, U17.3, U30.2
/Flag Unit/RADDR2: P1.B17, R33.1, U17.4, U30.3
/Flag Unit/RADDR3: P1.B18, R36.1, U17.5, U30.6
/Flag Unit/RADDR4: P1.B19, R39.1, U17.6, U30.5
/Flag Unit/WADDR0: P1.B20, R42.1, U17.7, U28.1
/Flag Unit/WADDR1: P1.B21, R45.1, U17.8, U28.2
/Flag Unit/WADDR2: P1.B22, R48.1, U17.9, U28.3
/Flag Unit/WADDR3: P1.B23, R6.1, U28.6, U31.2
/Flag Unit/WADDR4: P1.B24, R31.1, U28.5, U31.3
/Flag Unit/~FLAGOE: U27.1, U30.10
/Flag Unit/~WRITE-FLAGS: U6.3, U28.9
/Flag Unit/~WRITE-MBP+FLAGS: U6.1, U28.10
/IBUS15: P1.B41, U13.2, U19.11, U27.11, U33.9
/IDX0: U16.6, U23.4, U52.8, U53.8, U54.8
/IDX1: U16.7, U24.4, U52.7, U53.7, U54.7
/IR0: P1.B44, U1.3, U2.12, U11.2, U12.19, U18.2
/IR1: P1.B45, U1.2, U2.9, U11.3, U12.18, U18.3
/IR2: P1.B46, U1.1, U2.4, U11.4, U12.17, U18.4
/IR3: P1.B47, U1.15, U2.1, U11.5, U12.16, U18.5
/IR4: P1.B48, U1.14, U4.1, U11.6, U12.15, U18.6
/IR5: P1.B49, U1.13, U11.7, U12.14, U18.7
/IR6: P1.B50, U1.12, U11.8, U12.13, U18.8, U23.6
/IR7: U11.9, U12.12, U18.9, U24.6, U52.5, U53.5, U54.5
/IR8: U14.2, U19.2, U23.3, U24.3, U26.1, U33.19, U52.27, U53.27, U54.27
/IR9: U14.3, U19.3, U23.1, U24.1, U26.2, U33.18, U52.26, U53.26, U54.26
/IR10: U14.4, U20.1, U33.17, U52.23, U53.23, U54.23
/IR11: U14.5, U33.16, U52.25, U53.25, U54.25
/IR12: U14.6, U33.15, U52.4, U53.4, U54.4
/IR13: U14.7, U33.14, U52.28, U53.28, U54.28
/IR14: U14.8, U33.13, U52.29, U53.29, U54.29
/IR15: U14.9, U33.12, U52.3, U53.3, U54.3
/Instruction Register (IR)/~WIR: U12.11, U33.11, U39.4
/Interrupt State Machine/ACTION0: P1.B30, R49.1, U15.1, U31.9
/Interrupt State Machine/ACTION1: P1.B31, R8.1, U15.2, U21.2
/Interrupt State Machine/ACTION2: P1.B32, R32.1, U15.3, U21.3
/Interrupt State Machine/ACTION3: P1.B33, R35.1, U15.5, U21.4
/Interrupt State Machine/ENDCP: U41.1, U51.4
/Interrupt State Machine/~ACTION-CLI: U15.11, U42.2
/Interrupt State Machine/~ACTION-STI: U13.7, U15.12
/Interrupt State Machine/~INH: U22.7, U25.4
/Interrupt State Machine/~INH₀: R53.2, U13.5, U25.1
/Interrupt State Machine/~IRQ0: U22.2, U50.4
/Interrupt State Machine/~IRQ1: TP3.1, U22.5, U41.2
/Interrupt State Machine/~RESET-OR-CLI: U13.6, U25.2, U42.4
/Microprogram Sequencer/Micro-Program Counter/~µPCCLR: R54.1, R56.1, U43.5
/Microprogram Sequencer/Micro-Program Counter/~µPCCLR': R56.2, U44.9
/Microprogram Sequencer/Microcode Store/~IO0: U7.13, U60.15
/Microprogram Sequencer/Microcode Store/~MEM0: U7.3, U60.16
/Microprogram Sequencer/Microcode Store/~R0: U7.6, U60.14
/Microprogram Sequencer/Microcode Store/~WEN0: U7.10, U60.13
/Microprogram Sequencer/Microcode Store/µCV0: U52.13, U58.2
/Microprogram Sequencer/Microcode Store/µCV1: U52.14, U58.3
/Microprogram Sequencer/Microcode Store/µCV2: U52.15, U58.4
/Microprogram Sequencer/Microcode Store/µCV3: U52.17, U58.5
/Microprogram Sequencer/Microcode Store/µCV4: U52.18, U58.6
/Microprogram Sequencer/Microcode Store/µCV5: U52.19, U58.7
/Microprogram Sequencer/Microcode Store/µCV6: U52.20, U58.8
/Microprogram Sequencer/Microcode Store/µCV7: U52.21, U58.9
/Microprogram Sequencer/Microcode Store/µCV8: U53.13, U59.2
/Microprogram Sequencer/Microcode Store/µCV9: U53.14, U59.3
/Microprogram Sequencer/Microcode Store/µCV10: U53.15, U59.4
/Microprogram Sequencer/Microcode Store/µCV11: U53.17, U59.5
/Microprogram Sequencer/Microcode Store/µCV12: U53.18, U59.6
/Microprogram Sequencer/Microcode Store/µCV13: U53.19, U59.7
/Microprogram Sequencer/Microcode Store/µCV14: U53.20, U59.8
/Microprogram Sequencer/Microcode Store/µCV15: U53.21, U59.9
/Microprogram Sequencer/Microcode Store/µCV16: U54.13, U60.2
/Microprogram Sequencer/Microcode Store/µCV17: U54.14, U60.3
/Microprogram Sequencer/Microcode Store/µCV18: U54.15, U60.4
/Microprogram Sequencer/Microcode Store/µCV19: U54.17, U60.5
/Microprogram Sequencer/Microcode Store/µCV20: U54.18, U60.6
/Microprogram Sequencer/Microcode Store/µCV21: U54.19, U60.7
/Microprogram Sequencer/Microcode Store/µCV22: U54.20, U60.8
/Microprogram Sequencer/Microcode Store/µCV23: U54.21, U60.9
/Microprogram Sequencer/Sheet5D82ABFF/RSVD: TP5.1, U16.9
/Microprogram Sequencer/UPC0: U16.2, U44.14, U45.10, U52.12, U53.12, U54.12
/Microprogram Sequencer/UPC1: U16.3, U44.13, U45.12, U52.11, U53.11, U54.11
/Microprogram Sequencer/UPC2: U16.4, U44.12, U45.13, U52.10, U53.10, U54.10
/Microprogram Sequencer/UPC3: U16.5, U44.11, U45.15, U52.9, U53.9, U54.9
/Microprogram Sequencer/~CSE: U29.3, U58.1, U59.1, U60.1
/Microprogram Sequencer/~HALT₀: U29.2, U46.4
/PC10: P1.B57, R58.1, U20.4
/PC11: P1.B59, R59.1, U20.5
/PC12: P1.B58, R60.1, U20.6
/PC13: P1.B62, R61.1, U20.7
/PC14: P1.B61, R62.1, U20.8
/PC15: P1.A64, R63.1, U20.9
/POWEROK: D4.1, P1.A76
/Skip/Branch Unit/SKP: U4.4, U5.12
/Skip/Branch Unit/SL: U2.8, U3.5
/Skip/Branch Unit/SN: U2.3, U3.1
/Skip/Branch Unit/SV: U2.11, U3.4
/Skip/Branch Unit/SVL: U3.6, U3.9
/Skip/Branch Unit/SZ: U2.6, U3.2
/Skip/Branch Unit/SZN: U3.3, U3.10
/Skip/Branch Unit/~CEN0: U1.7, U10.4
/Skip/Branch Unit/~CEN1: U5.7, U10.5
/Skip/Branch Unit/~COND₀: D6.2, D7.2, D8.2, R2.2, U56.3
/Skip/Branch Unit/~COND₁: U8.2, U56.4
/T34: P1.B5, R22.1
/WSTB: P1.A5, TP1.1
/~ACTION-IDX: U9.2, U15.10
/~COND: U8.5, U16.8, U52.6, U53.6, U54.6
/~END: R50.1, U20.11, U21.9, U43.10, U47.8, U51.2
/~ENDEXT: P1.A32, R24.1, U43.11
/~FLAGWE: P1.B54, U6.4, U13.1
/~FPCLK~⁄CLK: P1.B67, R16.2, U38.6
/~FPFLAGS: P1.B75, U32.1
/~FPIRH: P1.A75, U14.1
/~FPIRL: P1.B74, U11.1
/~FPRESET: D3.1, P1.A65
/~FPµA0: P1.B70, U16.1
/~FPµC0: P1.A71, U17.1
/~FPµC1: P1.B71, U31.1
/~FPµC2: P1.A74, U21.1
/~HALT: P1.B60, R25.1, U44.10, U46.3
/~IDXEN: U9.1, U26.4
/~IO: P1.B26, R47.1, U21.6
/~IR-IDX: P1.A80, U9.4
/~IRQ: P1.B42, R28.2, U50.3
/~IRQS: P1.B43, R29.1
/~IRQSµC: U41.5, U52.2, U53.2, U54.2
/~MEM: P1.B25, R38.1, U21.5
/~R: P1.A27, R41.1, U21.7
/~READ-AGL: U18.1, U19.1, U30.7
/~RESET: D2.2, D3.2, D4.2, P1.B6, R13.2, U8.7, U29.6, U34.10, U37.11, U41.7, U42.1
/~RSTHOLD: P1.A6, R1.1, R14.1, U7.1, U44.1, U52.30, U53.30, U54.30
/~SKIPEXT: D6.1, P1.A33
/~WAITING: JP1.1, P1.B29
/~WEN: P1.B51, R44.1, U21.8
/~WRITE-IR: U28.7, U39.1
/~WS: JP1.3, P1.B27
/~µPC-INH: JP1.2, R55.1, U43.9, U44.7
GND: C1.2, C2.2, C3.2, C4.2, C5.2, C6.2, C7.2, C8.2, C9.2, C10.2, C11.2, C12.2, C13.2, C14.2, C15.2, C16.2, C17.2, C18.2, C19.2, C20.2, C21.2, C22.2, C23.2, C24.2, C25.2, C26.2, C27.2, C28.2, C29.2, C30.2, C31.2, C32.2, C33.2, C34.2, C35.2, C37.2, C38.2, C39.2, C40.2, C41.2, C42.2, C43.2, C44.2, C45.2, C46.2, C47.2, C48.2, C49.2, C50.2, C51.2, C52.2, C53.2, C54.2, C55.2, C56.2, C57.2, C58.2, C59.2, C60.2, C61.2, C62.2, C63.2, C64.2, C65.2, C66.2, C67.2, J1.1, JP4.3, JP5.3, JP6.3, P1.A72, P1.A73, P1.B1, P1.B2, P1.B81, P1.B82, R3.2, R4.2, R7.1, R9.2, R10.2, R11.2, R12.2, R17.2, R23.2, R26.2, R27.1, R51.2, R52.1, R57.2, R58.2, R59.2, R60.2, R61.2, R62.2, R63.2, SW1.2, U1.4, U1.8, U2.7, U3.7, U4.3, U5.8, U6.2, U7.8, U7.15, U8.4, U9.3, U10.1, U10.8, U10.13, U10.14, U10.15, U11.10, U11.19, U12.1, U12.10, U13.4, U14.10, U14.19, U15.8, U16.10, U16.19, U17.10, U17.19, U18.10, U18.19, U19.10, U19.19, U20.10, U21.10, U21.19, U22.4, U23.2, U24.2, U25.3, U26.3, U27.2, U27.3, U27.8, U27.10, U27.19, U28.4, U28.8, U29.4, U30.4, U30.8, U31.10, U31.19, U32.2, U32.3, U32.8, U32.10, U32.19, U33.1, U33.10, U34.8, U34.14, U35.3, U36.1, U36.8, U36.13, U36.15, U37.1, U37.4, U37.5, U37.8, U37.9, U37.10, U37.15, U38.4, U38.7, U39.3, U40.3, U41.4, U42.3, U43.8, U43.13, U43.14, U43.15, U44.3, U44.4, U44.5, U44.6, U44.8, U45.1, U45.2, U45.4, U45.8, U46.2, U46.6, U47.3, U47.4, U50.2, U50.6, U51.3, U52.16, U52.22, U52.24, U53.16, U53.22, U53.24, U54.16, U54.22, U54.24, U56.2, U56.6, U58.10, U59.10, U60.10, X1.2
unnamed: C23.1, J1.2, R15.2, SW1.1, U35.2
unnamed: D2.1, U35.4
unnamed: D5.1, U34.7, U34.12
unnamed: D5.2, R14.2
unnamed: D7.1, U1.6
unnamed: D8.1, U5.6
unnamed: JP4.2, U45.9
unnamed: JP5.2, U45.11
unnamed: JP6.2, U45.14
unnamed: R5.2, U58.19
unnamed: R6.2, U59.19
unnamed: R8.2, U60.19
unnamed: R29.2, U40.4
unnamed: R30.2, U58.18
unnamed: R31.2, U59.18
unnamed: R32.2, U60.18
unnamed: R33.2, U58.17
unnamed: R34.2, U59.17
unnamed: R35.2, U60.17
unnamed: R36.2, U58.16
unnamed: R37.2, U59.16
unnamed: R38.2, U7.4
unnamed: R39.2, U58.15
unnamed: R40.2, U59.15
unnamed: R41.2, U7.7
unnamed: R42.2, U58.14
unnamed: R43.2, U59.14
unnamed: R44.2, U7.9
unnamed: R45.2, U58.13
unnamed: R46.2, U59.13
unnamed: R47.2, U7.12
unnamed: R48.2, U58.12
unnamed: R49.2, U59.12
unnamed: R50.2, U60.12
unnamed: U3.8, U4.2
unnamed: U40.2, U41.3
