alexiosc/cft/kicad/cft/mem/cft-reg.kicad_pcb

## KiCad design kicad/cft/mem/cft-reg.kicad_pcb (2021-02-09)

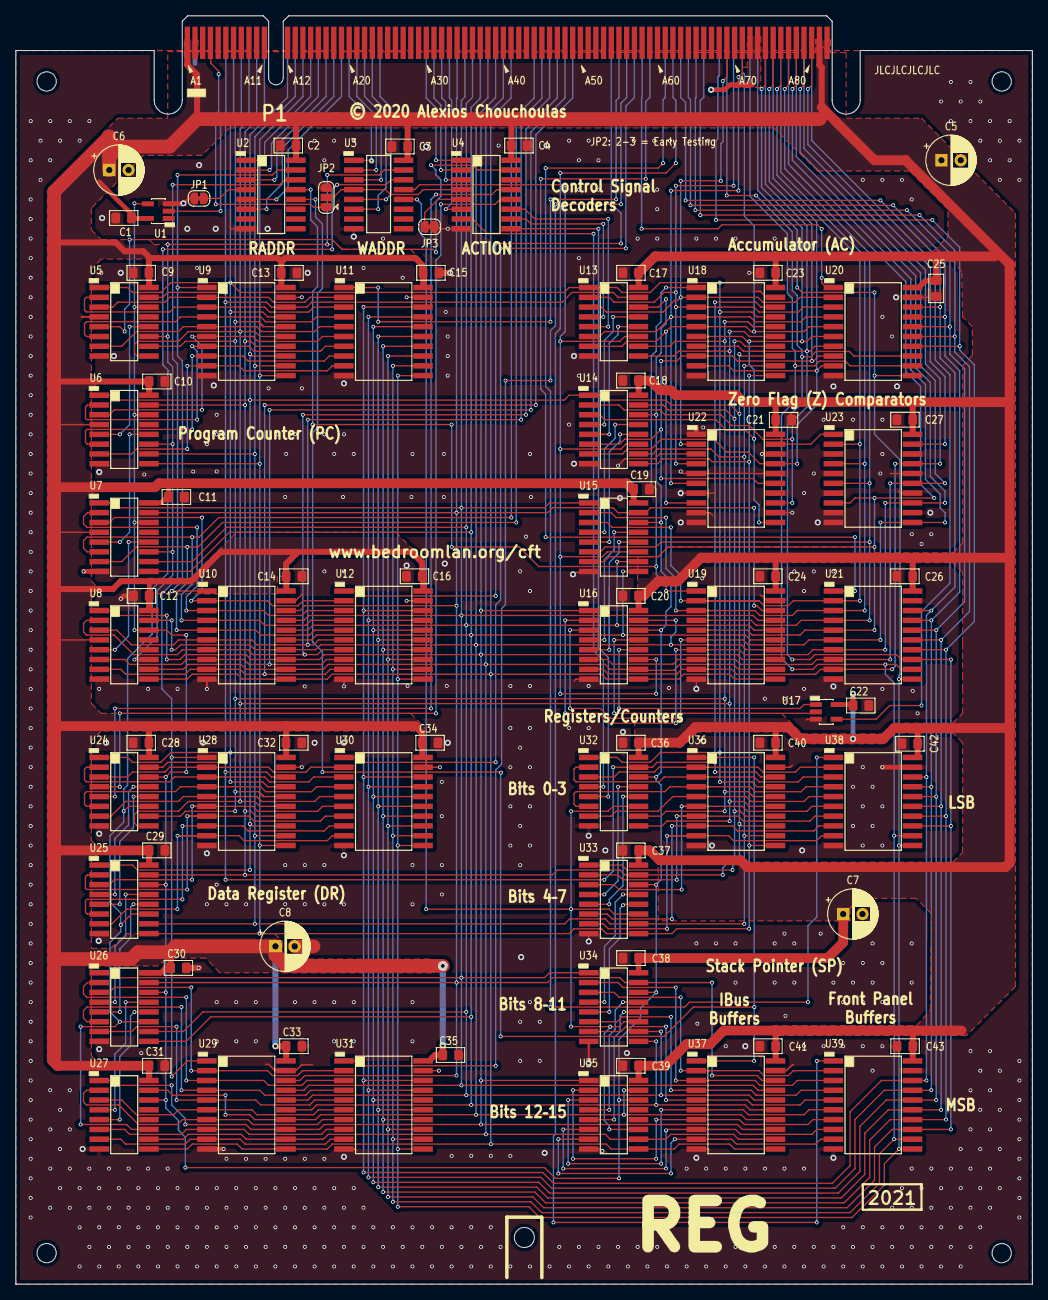
[picture p116: board cft-reg.kicad_pcb from above]

Board: 2 copper layers, 131.9 x 164.6 mm, 86 parts (0 on the bottom side), 159 nets.

Parts:
C1, C2, C3, C4, C9, C10, C11, C12, C13, C14, C15, C16, C17, C18, C19, C20, C21, C22, C23, C24, C25, C26, C27, C28, C29, C30, C31, C32, C33, C34, C35, C36, C37, C38, C39, C40, C41, C42, C43: 100nF; SMD_0805_2012Metric_Pad1.15x1.40mm_HandSolder
C5, C6, C7, C8: 47µF; CP_Radial_D6.3mm_P2.50mm
JP1, JP3: Jumper_NC_Small; SolderJumper-2_P1.3mm_Bridged_RoundedPad1.0x1.5mm
JP2: SolderJumper_3_Open; SolderJumper-3_P1.3mm_Open_RoundedPad1.0x1.5mm
P1: CFT-2019-Bus; CFT-2019-Card-Edge
U1: 74LVC1G04; SOT-23-5_HandSoldering
U2, U3, U4: 74HC138; SOIC-16
U5, U6, U7, U8, U13, U14, U15, U16, U24, U25, U26, U27, U32, U33, U34, U35: 74HC193; SOIC-16
U9, U10, U11, U12, U18, U19, U20, U21, U28, U29, U30, U31, U36, U37, U38, U39: 74HCT541; SOIC-20W
U17: 74AHC1G08; SOT-23-5_HandSoldering
U22, U23: 74HC688; SOIC-20W

Connections:
+5V: C1.1, C2.1, C3.1, C4.1, C5.1, C6.1, C7.1, C8.1, C9.1, C10.1, C11.1, C12.1, C13.1, C14.1, C15.1, C16.1, C17.1, C18.1, C19.1, C20.1, C21.1, C22.1, C23.1, C24.1, C25.1, C26.1, C27.1, C28.1, C29.1, C30.1, C31.1, C32.1, C33.1, C34.1, C35.1, C36.1, C37.1, C38.1, C39.1, C40.1, C41.1, C42.1, C43.1, P1.A1, P1.A2, P1.A81, P1.A82, U1.5, U2.16, U3.16, U4.16, U5.4, U5.16, U6.4, U6.16, U7.4, U7.16, U8.4, U8.16, U9.20, U10.20, U11.20, U12.20, U13.16, U14.16, U15.16, U16.16, U17.5, U18.20, U19.20, U20.20, U21.20, U22.20, U23.20, U24.16, U25.16, U26.16, U27.16, U28.20, U29.20, U30.20, U31.20, U32.16, U33.16, U34.16, U35.16, U36.20, U37.20, U38.20, U39.20
/AC0: P1.A69, U13.3, U18.2, U20.2, U22.2
/AC1: P1.B70, U13.2, U18.3, U20.3, U22.4
/AC2: P1.A71, U13.6, U18.4, U20.4, U22.6
/AC3: P1.B71, U13.7, U18.5, U20.5, U22.8
/AC4: P1.A74, U14.3, U18.6, U20.6, U22.11
/AC5: P1.B74, U14.2, U18.7, U20.7, U22.13
/AC6: P1.A75, U14.6, U18.8, U20.8, U22.15
/AC7: P1.B75, U14.7, U18.9, U20.9, U22.17
/AC8: P1.A76, U15.3, U19.2, U21.2, U23.2
/AC9: P1.B76, U15.2, U19.3, U21.3, U23.4
/AC10: P1.A77, U15.6, U19.4, U21.4, U23.6
/AC11: P1.B77, U15.7, U19.5, U21.5, U23.8
/AC12: P1.A78, U16.3, U19.6, U21.6, U23.11
/AC13: P1.B78, U16.2, U19.7, U21.7, U23.13
/AC14: P1.A79, U16.6, U19.8, U21.8, U23.15
/AC15: P1.B79, U16.7, U19.9, U21.9, U23.17
/ACTION0: P1.B30, U4.1
/ACTION1: P1.B31, U4.2
/ACTION2: P1.B32, U4.3
/ACTION3: P1.B33, U4.6
/Accumulator/FPD0: P1.B63, U11.18, U12.18, U20.18, U21.18, U30.18, U31.18, U38.18, U39.18
/Accumulator/FPD1: P1.B64, U11.17, U12.17, U20.17, U21.17, U30.17, U31.17, U38.17, U39.17
/Accumulator/FPD2: P1.B65, U11.16, U12.16, U20.16, U21.16, U30.16, U31.16, U38.16, U39.16
/Accumulator/FPD3: P1.B66, U11.15, U12.15, U20.15, U21.15, U30.15, U31.15, U38.15, U39.15
/Accumulator/FPD4: P1.B68, U11.14, U12.14, U20.14, U21.14, U30.14, U31.14, U38.14, U39.14
/Accumulator/FPD5: P1.B69, U11.13, U12.13, U20.13, U21.13, U30.13, U31.13, U38.13, U39.13
/Accumulator/FPD6: P1.B72, U11.12, U12.12, U20.12, U21.12, U30.12, U31.12, U38.12, U39.12
/Accumulator/FPD7: P1.B73, U11.11, U12.11, U20.11, U21.11, U30.11, U31.11, U38.11, U39.11
/Accumulator/IBUS0: P1.B7, U5.15, U9.18, U13.15, U18.18, U24.15, U28.18, U32.15, U36.18
/Accumulator/IBUS1: P1.B8, U5.1, U9.17, U13.1, U18.17, U24.1, U28.17, U32.1, U36.17
/Accumulator/IBUS2: P1.B9, U5.10, U9.16, U13.10, U18.16, U24.10, U28.16, U32.10, U36.16
/Accumulator/IBUS3: P1.B10, U5.9, U9.15, U13.9, U18.15, U24.9, U28.15, U32.9, U36.15
/Accumulator/IBUS4: P1.B11, U6.15, U9.14, U14.15, U18.14, U25.15, U28.14, U33.15, U36.14
/Accumulator/IBUS5: P1.B12, U6.1, U9.13, U14.1, U18.13, U25.1, U28.13, U33.1, U36.13
/Accumulator/IBUS6: P1.B13, U6.10, U9.12, U14.10, U18.12, U25.10, U28.12, U33.10, U36.12
/Accumulator/IBUS7: P1.B14, U6.9, U9.11, U14.9, U18.11, U25.9, U28.11, U33.9, U36.11
/Accumulator/IBUS8: P1.B34, U7.15, U10.18, U15.15, U19.18, U26.15, U29.18, U34.15, U37.18
/Accumulator/IBUS9: P1.B35, U7.1, U10.17, U15.1, U19.17, U26.1, U29.17, U34.1, U37.17
/Accumulator/IBUS10: P1.B36, U7.10, U10.16, U15.10, U19.16, U26.10, U29.16, U34.10, U37.16
/Accumulator/IBUS11: P1.B37, U7.9, U10.15, U15.9, U19.15, U26.9, U29.15, U34.9, U37.15
/Accumulator/IBUS12: P1.B38, U8.15, U10.14, U16.15, U19.14, U27.15, U29.14, U35.15, U37.14
/Accumulator/IBUS13: P1.B39, U8.1, U10.13, U16.1, U19.13, U27.1, U29.13, U35.1, U37.13
/Accumulator/IBUS14: P1.B40, U8.10, U10.12, U16.10, U19.12, U27.10, U29.12, U35.10, U37.12
/Accumulator/IBUS15: P1.B41, U8.9, U10.11, U16.9, U19.11, U27.9, U29.11, U35.9, U37.11
/CLK4: JP2.1, P1.A4
/CLK4': JP2.2, U3.4, U4.4
/Data Register/Q0: U24.3, U28.2, U30.2
/Data Register/Q1: U24.2, U28.3, U30.3
/Data Register/Q2: U24.6, U28.4, U30.4
/Data Register/Q3: U24.7, U28.5, U30.5
/Data Register/Q4: U25.3, U28.6, U30.6
/Data Register/Q5: U25.2, U28.7, U30.7
/Data Register/Q6: U25.6, U28.8, U30.8
/Data Register/Q7: U25.7, U28.9, U30.9
/Data Register/Q8: U26.3, U29.2, U31.2
/Data Register/Q9: U26.2, U29.3, U31.3
/Data Register/Q10: U26.6, U29.4, U31.4
/Data Register/Q11: U26.7, U29.5, U31.5
/Data Register/Q12: U27.3, U29.6, U31.6
/Data Register/Q13: U27.2, U29.7, U31.7
/Data Register/Q14: U27.6, U29.8, U31.8
/Data Register/Q15: U27.7, U29.9, U31.9
/FZ: P1.A80, U23.19
/PC10: P1.B44, U7.6, U10.4, U12.4
/PC11: P1.B45, U7.7, U10.5, U12.5
/PC12: P1.B46, U8.3, U10.6, U12.6
/PC13: P1.B47, U8.2, U10.7, U12.7
/PC14: P1.B48, U8.6, U10.8, U12.8
/PC15: P1.B49, U8.7, U10.9, U12.9
/Program Counter/PC0: U5.3, U9.2, U11.2
/Program Counter/PC1: U5.2, U9.3, U11.3
/Program Counter/PC2: U5.6, U9.4, U11.4
/Program Counter/PC3: U5.7, U9.5, U11.5
/Program Counter/PC4: U6.3, U9.6, U11.6
/Program Counter/PC5: U6.2, U9.7, U11.7
/Program Counter/PC6: U6.6, U9.8, U11.8
/Program Counter/PC7: U6.7, U9.9, U11.9
/Program Counter/PC8: U7.3, U10.2, U12.2
/Program Counter/PC9: U7.2, U10.3, U12.3
/RADDR0: P1.B15, U2.1
/RADDR1: P1.B16, U2.2
/RADDR2: P1.B17, U2.3
/RADDR3: P1.B18, U2.6
/RADDR4: P1.B19, U2.5
/RESET: U1.4, U5.14, U6.14, U7.14, U8.14, U13.14, U14.14, U15.14, U16.14, U24.14, U25.14, U26.14, U27.14, U32.14, U33.14, U34.14, U35.14
/Stack Pointer/Q0: U32.3, U36.2, U38.2
/Stack Pointer/Q1: U32.2, U36.3, U38.3
/Stack Pointer/Q2: U32.6, U36.4, U38.4
/Stack Pointer/Q3: U32.7, U36.5, U38.5
/Stack Pointer/Q4: U33.3, U36.6, U38.6
/Stack Pointer/Q5: U33.2, U36.7, U38.7
/Stack Pointer/Q6: U33.6, U36.8, U38.8
/Stack Pointer/Q7: U33.7, U36.9, U38.9
/Stack Pointer/Q8: U34.3, U37.2, U39.2
/Stack Pointer/Q9: U34.2, U37.3, U39.3
/Stack Pointer/Q10: U34.6, U37.4, U39.4
/Stack Pointer/Q11: U34.7, U37.5, U39.5
/Stack Pointer/Q12: U35.3, U37.6, U39.6
/Stack Pointer/Q13: U35.2, U37.7, U39.7
/Stack Pointer/Q14: U35.6, U37.8, U39.8
/Stack Pointer/Q15: U35.7, U37.9, U39.9
/WADDR0: P1.B20, U3.1
/WADDR1: P1.B21, U3.2
/WADDR2: P1.B22, U3.3
/WADDR3: P1.B23, U3.6
/WADDR4: P1.B24, U3.5
/~ACCPL: P1.B80, U17.4
/~ACTION-DECAC: U4.10, U13.4
/~ACTION-DECDR: U4.12, U24.4
/~ACTION-DECSP: U4.7, U32.4
/~ACTION-INCAC: U4.11, U13.5
/~ACTION-INCDR: U4.13, U24.5
/~ACTION-INCPC: U4.15, U5.5
/~ACTION-INCSP: U4.9, U32.5
/~FPACH: P1.B59, U21.1
/~FPACL: P1.B58, U20.1
/~FPDRH: P1.B56, U31.1
/~FPDRL: P1.B57, U30.1
/~FPPCH: P1.B54, U12.1
/~FPPCL: P1.B55, U11.1
/~FPSPH: P1.B62, U39.1
/~FPSPL: P1.B61, U38.1
/~READ-AC: U2.13, U18.1, U19.1
/~READ-DR: U2.14, U28.1, U29.1
/~READ-PC: U2.15, U9.1, U10.1
/~READ-SP: U2.12, U36.1, U37.1
/~RESET: P1.B6, U1.2
/~WRITE-AC: U3.13, U13.11, U14.11, U15.11, U16.11
/~WRITE-DR: U3.14, U24.11, U25.11, U26.11, U27.11
/~WRITE-PC: U3.15, U5.11, U6.11, U7.11, U8.11
/~WRITE-SP: U3.12, U32.11, U33.11, U34.11, U35.11
GND: C1.2, C2.2, C3.2, C4.2, C5.2, C6.2, C7.2, C8.2, C9.2, C10.2, C11.2, C12.2, C13.2, C14.2, C15.2, C16.2, C17.2, C18.2, C19.2, C20.2, C21.2, C22.2, C23.2, C24.2, C25.2, C26.2, C27.2, C28.2, C29.2, C30.2, C31.2, C32.2, C33.2, C34.2, C35.2, C36.2, C37.2, C38.2, C39.2, C40.2, C41.2, C42.2, C43.2, JP1.1, JP2.3, JP3.1, P1.A72, P1.A73, P1.B1, P1.B2, P1.B81, P1.B82, U1.3, U2.8, U3.8, U4.8, U5.8, U6.8, U7.8, U8.8, U9.10, U9.19, U10.10, U10.19, U11.10, U11.19, U12.10, U12.19, U13.8, U14.8, U15.8, U16.8, U17.3, U18.10, U18.19, U19.10, U19.19, U20.10, U20.19, U21.10, U21.19, U22.1, U22.3, U22.5, U22.7, U22.9, U22.10, U22.12, U22.14, U22.16, U22.18, U23.3, U23.5, U23.7, U23.9, U23.10, U23.12, U23.14, U23.16, U23.18, U24.8, U25.8, U26.8, U27.8, U28.10, U28.19, U29.10, U29.19, U30.10, U30.19, U31.10, U31.19, U32.8, U33.8, U34.8, U35.8, U36.10, U36.19, U37.10, U37.19, U38.10, U38.19, U39.10, U39.19
unnamed: JP1.2, U2.4
unnamed: JP3.2, U4.5
unnamed: U5.12, U6.5
unnamed: U6.12, U7.5
unnamed: U7.12, U8.5
unnamed: U13.12, U14.5
unnamed: U13.13, U14.4
unnamed: U14.12, U15.5
unnamed: U14.13, U15.4
unnamed: U15.12, U16.5
unnamed: U15.13, U16.4
unnamed: U16.12, U17.1
unnamed: U16.13, U17.2
unnamed: U22.19, U23.1
unnamed: U24.12, U25.5
unnamed: U24.13, U25.4
unnamed: U25.12, U26.5
unnamed: U25.13, U26.4
unnamed: U26.12, U27.5
unnamed: U26.13, U27.4
unnamed: U32.12, U33.5
unnamed: U32.13, U33.4
unnamed: U33.12, U34.5
unnamed: U33.13, U34.4
unnamed: U34.12, U35.5
unnamed: U34.13, U35.4
