alexiosc/cft/kicad/cft/mem-old/mem-ram-horizontal.kicad_pcb

## KiCad design kicad/cft/mem-old/mem-ram-horizontal.kicad_pcb (2019-09-16, an earlier design)

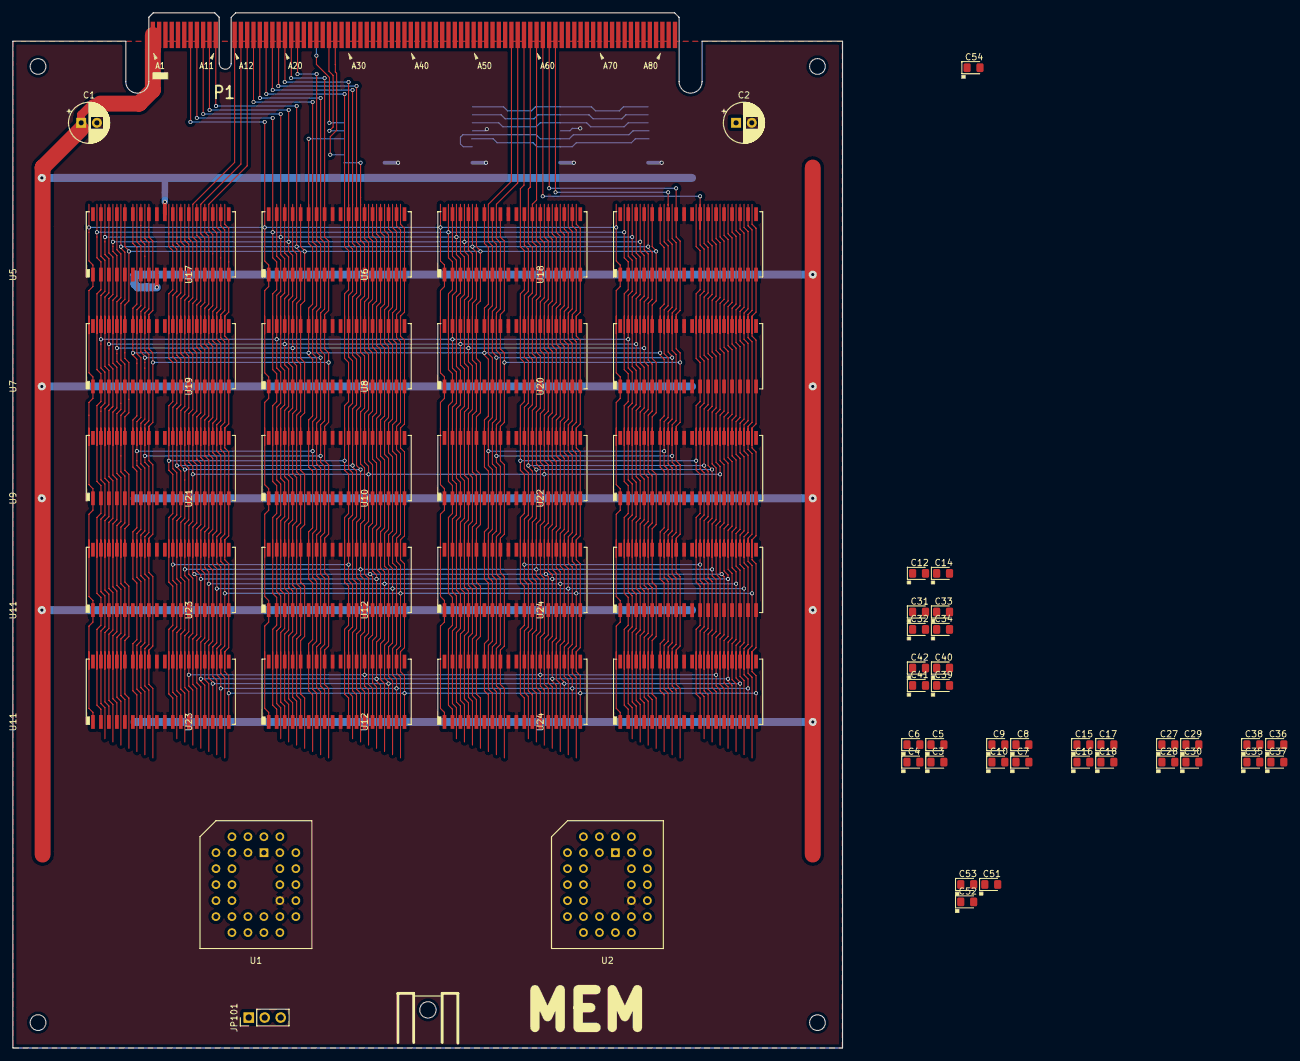
[picture p117: board mem-ram-horizontal.kicad_pcb from above]

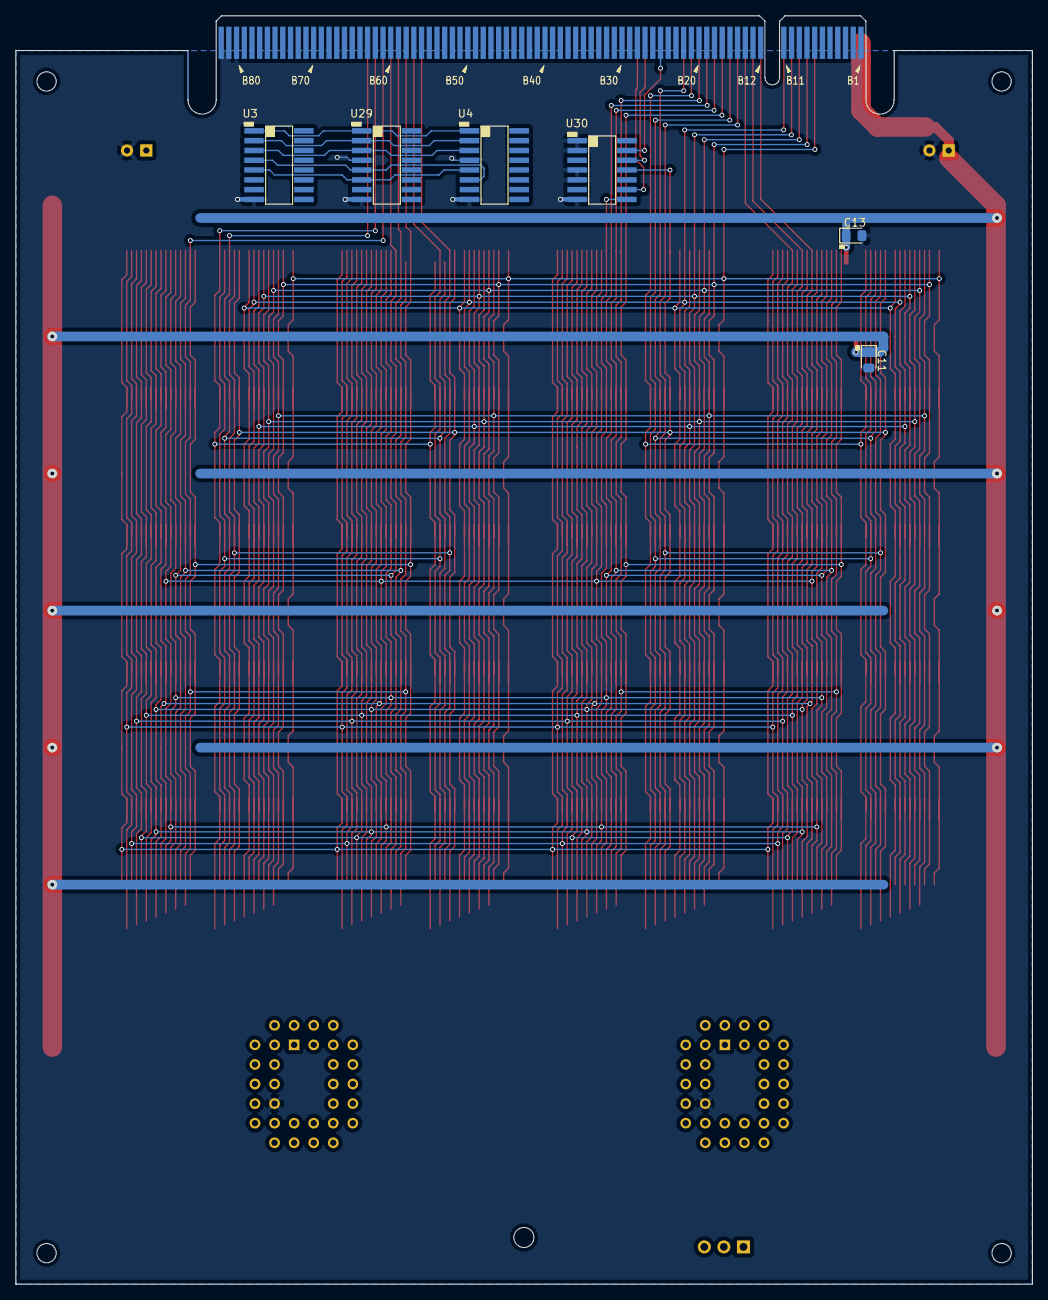
[picture p118: board mem-ram-horizontal.kicad_pcb from below]

Board: 2 copper layers, 131.9 x 164.6 mm, 66 parts (6 on the bottom side), 67 nets.

Parts:
C1, C2: 47µF; CP_Radial_D6.3mm_P2.50mm
C3, C4, C5, C6, C7, C8, C9, C10, C11, C12, C13, C14, C15, C16, C17, C18, C27, C28, C29, C30, C31, C32, C33, C34, C35, C36, C37, C38, C39, C40, C41, C42, C51, C52, C53, C54: 100nF; LED_0805_2012Metric_Pad1.15x1.40mm_HandSolder
JP101: Jumper_3_Bridged12; PinHeader_1x03_P2.54mm_Vertical
P1: CFT-2019-Bus; CFT-2019-Card-Edge
U1, U2: 29W040; PLCC32
U3, U4, U29: 74HC138; SOIC-16
U5, U6, U7, U8, U9, U10, U11, U11#2, U12, U12#2, U17, U18, U19, U20, U21, U22, U23, U23#2, U24, U24#2: IS61C5128AL; SOJ-36_10.16x23.49mm_P1.27mm
U30: 74AC32; SOIC-14

Connections:
+5V: C1.1, C2.1, C3.1, C4.1, C5.1, C6.1, C7.1, C8.1, C9.1, C10.1, C11.1, C12.1, C13.1, C14.1, C15.1, C16.1, C17.1, C18.1, C27.1, C28.1, C29.1, C30.1, C31.1, C32.1, C33.1, C34.1, C35.1, C36.1, C37.1, C38.1, C39.1, C40.1, C41.1, C42.1, C51.1, C52.1, C53.1, C54.1, JP101.3, P1.A1, P1.A2, P1.A81, P1.A82, U1.8, U2.8, U3.6, U3.16, U4.16, U5.9, U5.27, U6.9, U6.27, U7.9, U7.27, U8.9, U8.27, U9.9, U9.27, U10.9, U10.27, U11.9, U11.27, U11#2.9, U11#2.27, U12.9, U12.27, U12#2.9, U12#2.27, U17.9, U17.27, U18.9, U18.27, U19.9, U19.27, U20.9, U20.27, U21.9, U21.27, U22.9, U22.27, U23.9, U23.27, U23#2.9, U23#2.27, U24.9, U24.27, U24#2.9, U24#2.27, U29.16, U30.14
/AB0: P1.A7, U1.20, U2.20, U5.1, U6.1, U7.1, U8.1, U9.1, U10.1, U11.1, U11#2.1, U12.1, U12#2.1, U17.1, U18.1, U19.1, U20.1, U21.1, U22.1, U23.1, U23#2.1, U24.1, U24#2.1
/AB1: P1.A8, U1.19, U2.19, U5.2, U6.2, U7.2, U8.2, U9.2, U10.2, U11.2, U11#2.2, U12.2, U12#2.2, U17.2, U18.2, U19.2, U20.2, U21.2, U22.2, U23.2, U23#2.2, U24.2, U24#2.2
/AB2: P1.A9, U1.18, U2.18, U5.3, U6.3, U7.3, U8.3, U9.3, U10.3, U11.3, U11#2.3, U12.3, U12#2.3, U17.3, U18.3, U19.3, U20.3, U21.3, U22.3, U23.3, U23#2.3, U24.3, U24#2.3
/AB3: P1.A10, U1.17, U2.17, U5.4, U6.4, U7.4, U8.4, U9.4, U10.4, U11.4, U11#2.4, U12.4, U12#2.4, U17.4, U18.4, U19.4, U20.4, U21.4, U22.4, U23.4, U23#2.4, U24.4, U24#2.4
/AB4: P1.A11, U1.16, U2.16, U5.5, U6.5, U7.5, U8.5, U9.5, U10.5, U11.5, U11#2.5, U12.5, U12#2.5, U17.5, U18.5, U19.5, U20.5, U21.5, U22.5, U23.5, U23#2.5, U24.5, U24#2.5
/AB5: P1.A12, U1.15, U2.15, U5.14, U6.14, U7.14, U8.14, U9.14, U10.14, U11.14, U11#2.14, U12.14, U12#2.14, U17.14, U18.14, U19.14, U20.14, U21.14, U22.14, U23.14, U23#2.14, U24.14, U24#2.14
/AB6: P1.A13, U1.14, U2.14, U5.15, U6.15, U7.15, U8.15, U9.15, U10.15, U11.15, U11#2.15, U12.15, U12#2.15, U17.15, U18.15, U19.15, U20.15, U21.15, U22.15, U23.15, U23#2.15, U24.15, U24#2.15
/AB7: P1.A14, U1.13, U2.13, U5.16, U6.16, U7.16, U8.16, U9.16, U10.16, U11.16, U11#2.16, U12.16, U12#2.16, U17.16, U18.16, U19.16, U20.16, U21.16, U22.16, U23.16, U23#2.16, U24.16, U24#2.16
/AB8: P1.A34, U1.3, U2.3, U5.17, U6.17, U7.17, U8.17, U9.17, U10.17, U11.17, U11#2.17, U12.17, U12#2.17, U17.17, U18.17, U19.17, U20.17, U21.17, U22.17, U23.17, U23#2.17, U24.17, U24#2.17
/AB9: P1.A35, U1.2, U2.2, U5.18, U6.18, U7.18, U8.18, U9.18, U10.18, U11.18, U11#2.18, U12.18, U12#2.18, U17.18, U18.18, U19.18, U20.18, U21.18, U22.18, U23.18, U23#2.18, U24.18, U24#2.18
/AB10: P1.A36, U1.31, U2.31, U5.20, U6.20, U7.20, U8.20, U9.20, U10.20, U11.20, U11#2.20, U12.20, U12#2.20, U17.20, U18.20, U19.20, U20.20, U21.20, U22.20, U23.20, U23#2.20, U24.20, U24#2.20
/AB11: P1.A37, U1.1, U2.1, U5.21, U6.21, U7.21, U8.21, U9.21, U10.21, U11.21, U11#2.21, U12.21, U12#2.21, U17.21, U18.21, U19.21, U20.21, U21.21, U22.21, U23.21, U23#2.21, U24.21, U24#2.21
/AB12: P1.A38, U1.12, U2.12, U5.22, U6.22, U7.22, U8.22, U9.22, U10.22, U11.22, U11#2.22, U12.22, U12#2.22, U17.22, U18.22, U19.22, U20.22, U21.22, U22.22, U23.22, U23#2.22, U24.22, U24#2.22
/AB13: P1.A39, U1.4, U2.4, U5.23, U6.23, U7.23, U8.23, U9.23, U10.23, U11.23, U11#2.23, U12.23, U12#2.23, U17.23, U18.23, U19.23, U20.23, U21.23, U22.23, U23.23, U23#2.23, U24.23, U24#2.23
/AB14: P1.A40, U1.5, U2.5, U5.24, U6.24, U7.24, U8.24, U9.24, U10.24, U11.24, U11#2.24, U12.24, U12#2.24, U17.24, U18.24, U19.24, U20.24, U21.24, U22.24, U23.24, U23#2.24, U24.24, U24#2.24
/AB15: P1.A41, U1.11, U2.11, U5.32, U6.32, U7.32, U8.32, U9.32, U10.32, U11.32, U11#2.32, U12.32, U12#2.32, U17.32, U18.32, U19.32, U20.32, U21.32, U22.32, U23.32, U23#2.32, U24.32, U24#2.32
/AB16: P1.A42, U1.10, U2.10, U5.33, U6.33, U7.33, U8.33, U9.33, U10.33, U11.33, U11#2.33, U12.33, U12#2.33, U17.33, U18.33, U19.33, U20.33, U21.33, U22.33, U23.33, U23#2.33, U24.33, U24#2.33
/AB17: P1.A43, U1.6, U2.6, U5.34, U6.34, U7.34, U8.34, U9.34, U10.34, U11.34, U11#2.34, U12.34, U12#2.34, U17.34, U18.34, U19.34, U20.34, U21.34, U22.34, U23.34, U23#2.34, U24.34, U24#2.34
/AB18: P1.A44, U1.9, U2.9, U5.35, U6.35, U7.35, U8.35, U9.35, U10.35, U11.35, U11#2.35, U12.35, U12#2.35, U17.35, U18.35, U19.35, U20.35, U21.35, U22.35, U23.35, U23#2.35, U24.35, U24#2.35
/AB19: P1.A45, U3.1, U4.1, U29.1
/AB20: P1.A46, U3.2, U4.2, U29.2
/AB21: P1.A47, U3.3, U4.3, U29.3
/AB22: P1.A48, U3.5, U4.5, U29.6
/AB23: P1.A49, U3.4, U4.6, U29.5
/DB0: P1.A15, U1.21, U5.7, U7.7, U9.7, U11.7, U11#2.7, U17.7, U19.7, U21.7, U23.7, U23#2.7
/DB1: P1.A16, U1.22, U5.8, U7.8, U9.8, U11.8, U11#2.8, U17.8, U19.8, U21.8, U23.8, U23#2.8
/DB2: P1.A17, U1.23, U5.11, U7.11, U9.11, U11.11, U11#2.11, U17.11, U19.11, U21.11, U23.11, U23#2.11
/DB3: P1.A18, U1.25, U5.12, U7.12, U9.12, U11.12, U11#2.12, U17.12, U19.12, U21.12, U23.12, U23#2.12
/DB4: P1.A19, U1.26, U5.25, U7.25, U9.25, U11.25, U11#2.25, U17.25, U19.25, U21.25, U23.25, U23#2.25
/DB5: P1.A20, U1.27, U5.26, U7.26, U9.26, U11.26, U11#2.26, U17.26, U19.26, U21.26, U23.26, U23#2.26
/DB6: P1.A21, U1.28, U5.29, U7.29, U9.29, U11.29, U11#2.29, U17.29, U19.29, U21.29, U23.29, U23#2.29
/DB7: P1.A22, U1.29, U5.30, U7.30, U9.30, U11.30, U11#2.30, U17.30, U19.30, U21.30, U23.30, U23#2.30
/DB8: P1.A56, U2.21, U6.7, U8.7, U10.7, U12.7, U12#2.7, U18.7, U20.7, U22.7, U24.7, U24#2.7
/DB9: P1.A57, U2.22, U6.8, U8.8, U10.8, U12.8, U12#2.8, U18.8, U20.8, U22.8, U24.8, U24#2.8
/DB10: P1.A58, U2.23, U6.11, U8.11, U10.11, U12.11, U12#2.11, U18.11, U20.11, U22.11, U24.11, U24#2.11
/DB11: P1.A59, U2.25, U6.12, U8.12, U10.12, U12.12, U12#2.12, U18.12, U20.12, U22.12, U24.12, U24#2.12
/DB12: P1.A60, U2.26, U6.25, U8.25, U10.25, U12.25, U12#2.25, U18.25, U20.25, U22.25, U24.25, U24#2.25
/DB13: P1.A61, U2.27, U6.26, U8.26, U10.26, U12.26, U12#2.26, U18.26, U20.26, U22.26, U24.26, U24#2.26
/DB14: P1.A62, U2.28, U6.29, U8.29, U10.29, U12.29, U12#2.29, U18.29, U20.29, U22.29, U24.29, U24#2.29
/DB15: P1.A63, U2.29, U6.30, U8.30, U10.30, U12.30, U12#2.30, U18.30, U20.30, U22.30, U24.30, U24#2.30
/sheet5EC75B7C/~CE: U11#2.6, U12#2.6
/sheet5ECDEC41/~CE: U23#2.6, U24#2.6
/~CS0: U3.15, U5.6, U6.6
/~CS1: U3.14, U17.6, U18.6
/~CS2: U3.13, U7.6, U8.6
/~CS3: U3.12, U19.6, U20.6
/~CS4: U3.11, U9.6, U10.6
/~CS5: U3.10, U21.6, U22.6
/~CS6: U3.9, U11.6, U12.6
/~CS7: U3.7, U23.6, U24.6
/~MEM: P1.B25, U30.10, U30.13
/~MEMR: JP101.1, U1.32, U2.32, U5.31, U6.31, U7.31, U8.31, U9.31, U10.31, U11.31, U12.31, U17.31, U18.31, U19.31, U20.31, U21.31, U22.31, U23.31, U24.31, U30.11
/~MEMW: U5.13, U6.13, U7.13, U8.13, U9.13, U10.13, U11.13, U12.13, U17.13, U18.13, U19.13, U20.13, U21.13, U22.13, U23.13, U24.13, U30.8
/~R: P1.A27, U11#2.31, U12#2.31, U23#2.31, U24#2.31, U30.12
/~ROMCS: U1.30, U2.30, U4.15
/~ROMW: JP101.2, U1.7, U2.7
/~W: P1.A28, U11#2.13, U12#2.13, U23#2.13, U24#2.13, U30.9
GND: C1.2, C2.2, C3.2, C4.2, C5.2, C6.2, C7.2, C8.2, C9.2, C10.2, C11.2, C12.2, C13.2, C14.2, C15.2, C16.2, C17.2, C18.2, C27.2, C28.2, C29.2, C30.2, C31.2, C32.2, C33.2, C34.2, C35.2, C36.2, C37.2, C38.2, C39.2, C40.2, C41.2, C42.2, C51.2, C52.2, C53.2, C54.2, P1.B1, P1.B2, P1.B80, P1.B81, P1.B82, U1.24, U2.24, U3.8, U4.4, U4.8, U5.10, U5.28, U6.10, U6.28, U7.10, U7.28, U8.10, U8.28, U9.10, U9.28, U10.10, U10.28, U11.10, U11.28, U11#2.10, U11#2.28, U12.10, U12.28, U12#2.10, U12#2.28, U17.10, U17.28, U18.10, U18.28, U19.10, U19.28, U20.10, U20.28, U21.10, U21.28, U22.10, U22.28, U23.10, U23.28, U23#2.10, U23#2.28, U24.10, U24.28, U24#2.10, U24#2.28, U29.4, U29.8, U30.1, U30.2, U30.4, U30.5, U30.7
unnamed: U11.19, U11#2.19
unnamed: U11.36, U11#2.36
unnamed: U12.19, U12#2.19
unnamed: U12.36, U12#2.36
unnamed: U23.19, U23#2.19
unnamed: U23.36, U23#2.36
unnamed: U24.19, U24#2.19
unnamed: U24.36, U24#2.36
