alexiosc/cft/kicad/cft/cft-alu/cft-alu.kicad_pcb

## KiCad design kicad/cft/cft-alu/cft-alu.kicad_pcb (2020-11-13)

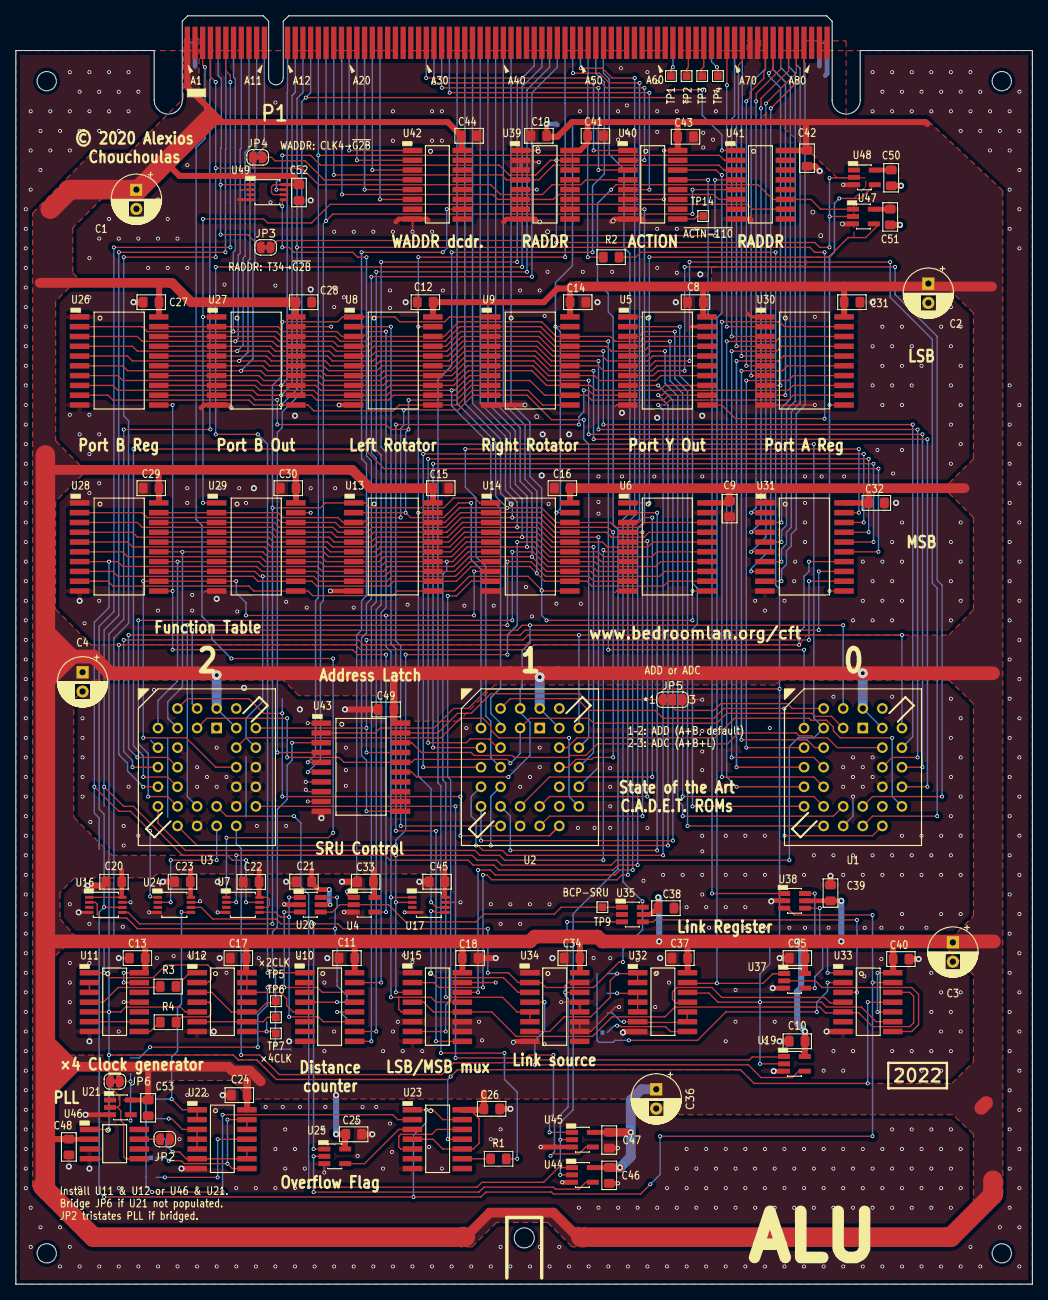
[picture p119: board cft-alu.kicad_pcb from above]

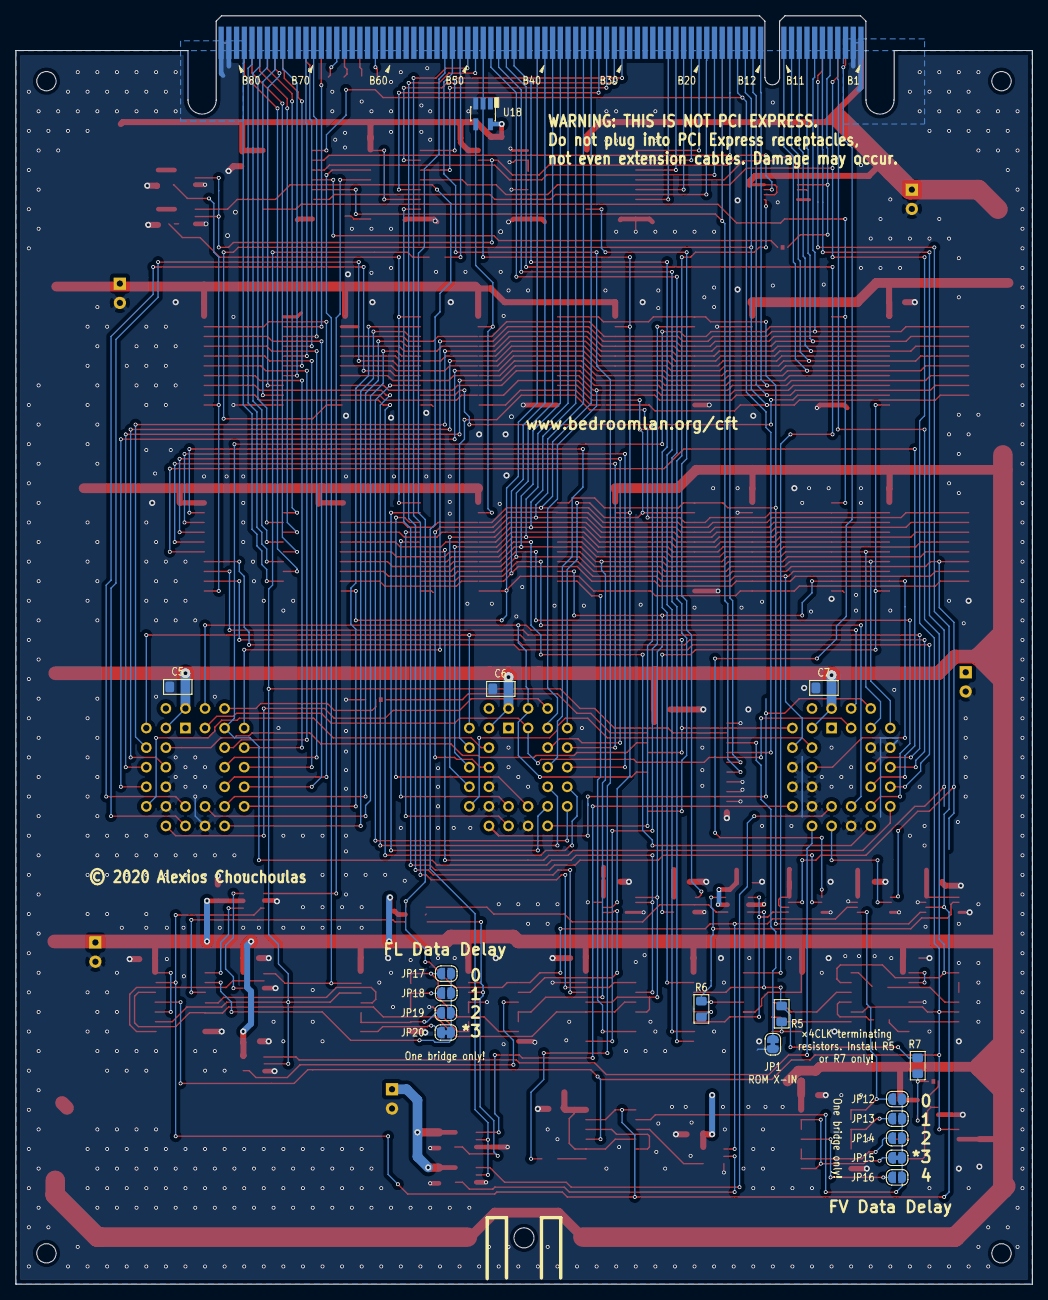
[picture p120: board cft-alu.kicad_pcb from below]

Board: 2 copper layers, 131.9 x 164.6 mm, 133 parts (17 on the bottom side), 191 nets.

Parts:
C1, C2, C3, C4, C36: 47µF; CP_Radial_D6.3mm_P2.50mm
C5, C6, C7, C8, C9, C10, C11, C12, C13, C14, C15, C16, C17, C18, C19, C20, C21, C22, C23, C24, C25, C26, C27, C28, C29, C30, C31, C32, C33, C34, C35, C37, C38, C39, C40, C41, C42, C43, C44, C45, C46, C47, C48, C49, C50, C51, C52, C53: 100nF; C_SMD_0805_2012Metric_Pad1.15x1.40mm_HandSolder
JP1, JP6, JP15, JP20: SolderJumper_2_Bridged; SolderJumper-2_P1.3mm_Bridged_RoundedPad1.0x1.5mm
JP2, JP12, JP13, JP14, JP16, JP17, JP18, JP19: SolderJumper_2_Open; SolderJumper-2_P1.3mm_Open_RoundedPad1.0x1.5mm
JP3, JP4: Jumper_NC_Small; SolderJumper-2_P1.3mm_Bridged_RoundedPad1.0x1.5mm
JP5: SolderJumper_3_Bridged12; SolderJumper-3_P1.3mm_Bridged12_RoundedPad1.0x1.5mm_NumberL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
P1: CFT-2019-Bus; CFT-2019-Card-Edge
R1, R2: 30Ω; R_SMD_0805_2012Metric_Pad1.15x1.40mm_HandSolder
R3, R4, R5, R6, R7: 0Ω; R_SMD_0805_2012Metric_Pad1.15x1.40mm_HandSolder
TP1, TP2, TP3, TP4, TP5, TP6, TP7, TP9, TP14: TestPoint; TestPoint_Pad_1.0x1.0mm
U1, U2, U3: 29W010; PLCC32
U4, U25, U47: 74LVC1G08; SOT-23-5_HandSoldering
U5, U6, U27, U29: 74HC541; SOIC-20W
U7: 74AUC1G74; TSSOP-8_3x3mm_P0.65mm
U8, U9, U13, U14: 74AC541; SOIC-20W
U10: 74AC191; SOIC-16
U11: 74HC04; SOIC-14
U12: 74AC86; SOIC-14
U15: 74AC253; SOIC-16
U16, U17, U24: 74LVC2G157; TSSOP-8_3x3mm_P0.65mm
U18, U21, U48: 74LVC1G04; SOT-23-5_HandSoldering
U19: 74LVC1G86; SOT-23-5_HandSoldering
U20: 74LVC1G0832; SOT-23-6_Handsoldering
U22: 74HC08; SOIC-14
U23, U33: 74AC74; SOIC-14
U26, U28, U30, U31: 74HC574; SOIC-20W
U32: 74HC32; SOIC-14
U34: 74HC253; SOIC-16
U35, U38: 74LVC1G11; SOT-23-6_Handsoldering
U37, U44, U45: 74LVC1G32; SOT-23-5_HandSoldering
U39: 74AC138; SOIC-16
U40, U41, U42: 74HC138; SOIC-16
U43: 74HC573; SOIC-20W
U46: ICS501; SOIC-8
U49: 74LVC1G74; TSSOP-8_3x3mm_P0.65mm

Connections:
+5V: C1.1, C2.1, C3.1, C4.1, C5.1, C6.1, C7.1, C8.1, C9.1, C10.1, C11.1, C12.1, C13.1, C14.1, C15.1, C16.1, C17.1, C18.1, C19.1, C20.1, C21.1, C22.1, C23.1, C24.1, C25.1, C26.1, C27.1, C28.1, C29.1, C30.1, C31.1, C32.1, C33.1, C34.1, C35.1, C36.1, C37.1, C38.1, C39.1, C40.1, C41.1, C42.1, C43.1, C44.1, C45.1, C46.1, C47.1, C48.1, C49.1, C50.1, C51.1, C52.1, C53.1, P1.A1, P1.A2, P1.A81, P1.A82, U1.31, U1.32, U2.31, U2.32, U3.31, U3.32, U4.5, U5.20, U6.20, U7.6, U7.8, U8.20, U9.20, U10.5, U10.16, U11.13, U11.14, U12.12, U12.13, U12.14, U13.20, U14.20, U15.16, U16.1, U16.8, U17.8, U18.5, U19.5, U20.5, U21.5, U22.14, U23.4, U23.10, U23.14, U24.8, U25.5, U26.20, U27.20, U28.20, U29.20, U30.20, U31.20, U32.14, U33.10, U33.14, U34.16, U35.5, U37.5, U38.5, U39.16, U40.6, U40.16, U41.16, U42.16, U43.20, U44.5, U45.5, U46.2, U47.5, U48.5, U49.6, U49.8
/AC0: P1.A69, U30.2
/AC1: P1.B70, U30.3
/AC2: P1.A71, U30.4
/AC3: P1.B71, U30.5
/AC4: P1.A74, U30.6
/AC5: P1.B74, U30.7
/AC6: P1.A75, U30.8
/AC7: P1.B75, U30.9
/AC8: P1.A76, U31.2
/AC9: P1.B76, U31.3
/AC10: P1.A77, U31.4
/AC11: P1.B77, U31.5
/AC12: P1.A78, U31.6
/AC13: P1.B78, U31.7
/AC14: P1.A79, U31.8
/AC15: P1.B79, U31.9
/BCP: TP9.1, U4.2, U20.4, U35.1
/CLK2: P1.B4, U11.1, U12.2
/CLK3: P1.A3, U7.1
/CLK4: JP4.1, P1.A4, U11.5, U12.5, U23.11, U33.11, U40.4, U46.1
/Decoders/ACP: U30.11, U31.11, U48.4
/Decoders/ACTION0: P1.B30, U40.1
/Decoders/ACTION1: P1.B31, U40.2
/Decoders/ACTION2: P1.B32, U40.3
/Decoders/ACTION3: P1.B33, U40.5
/Decoders/RADDR3: P1.B18, U39.4, U41.3
/Decoders/RADDR4: P1.B19, U39.6, U41.6
/Decoders/WADDR0: P1.B20, U42.1
/Decoders/WADDR1: P1.B21, U42.2
/Decoders/WADDR2: P1.B22, U42.5
/Decoders/WADDR3: P1.B23, U42.3
/Decoders/WADDR4: P1.B24, U42.6
/FL: R2.2, U19.2, U32.12, U33.9, U43.2
/FL-OFFBOARD: P1.B51, R2.1
/FLFAST: U15.4, U15.12, U33.5, U33.12
/FLOUT-ROM: U3.20, U19.1
/FLOUT-SRU: U17.5, U34.3
/FV: P1.B52, R1.1
/FVOUT-ROM: U3.18, U24.2
/IBUS12: P1.B38, U6.14, U13.14, U14.14, U28.6, U29.14, U34.5, U34.6
/IBUS13: P1.B39, U6.13, U13.13, U14.13, U24.1, U28.7, U29.13
/IR0: P1.B44, U10.15
/IR1: P1.B45, U10.1
/IR2: P1.B46, U10.10
/IR3: P1.B47, U10.9
/IR4: P1.B48, U8.19, U13.19, U17.6, U18.2
/IR5: P1.B49, U15.14
/IR6: P1.B50, U15.2
/Left Edge Connector/C17: P1.B62, TP1.1
/Left Edge Connector/C19: P1.A64, TP2.1
/Left Edge Connector/C21: P1.A66, TP3.1
/Left Edge Connector/C22: P1.B67, TP4.1
/Left Edge Connector/IBUS0: P1.B7, U5.18, U8.18, U9.18, U26.2, U27.18
/Left Edge Connector/IBUS1: P1.B8, U5.17, U8.17, U9.17, U26.3, U27.17
/Left Edge Connector/IBUS2: P1.B9, U5.16, U8.16, U9.16, U26.4, U27.16
/Left Edge Connector/IBUS3: P1.B10, U5.15, U8.15, U9.15, U26.5, U27.15
/Left Edge Connector/IBUS4: P1.B11, U5.14, U8.14, U9.14, U26.6, U27.14
/Left Edge Connector/IBUS5: P1.B12, U5.13, U8.13, U9.13, U26.7, U27.13
/Left Edge Connector/IBUS6: P1.B13, U5.12, U8.12, U9.12, U26.8, U27.12
/Left Edge Connector/IBUS7: P1.B14, U5.11, U8.11, U9.11, U26.9, U27.11
/Left Edge Connector/IBUS8: P1.B34, U6.18, U13.18, U14.18, U28.2, U29.18
/Left Edge Connector/IBUS9: P1.B35, U6.17, U13.17, U14.17, U28.3, U29.17
/Left Edge Connector/IBUS10: P1.B36, U6.16, U13.16, U14.16, U28.4, U29.16
/Left Edge Connector/IBUS11: P1.B37, U6.15, U13.15, U14.15, U28.5, U29.15
/Left Edge Connector/IBUS14: P1.B40, U6.12, U13.12, U14.12, U28.8, U29.12
/Left Edge Connector/IBUS15: P1.B41, U6.11, U13.11, U14.11, U28.9, U29.11
/Link Register (L)/CLKL: U33.3, U35.4
/Link Register (L)/LD: JP17.1, JP18.1, JP19.1, JP20.1, U33.2
/Link Register (L)/LD0: JP17.2, U32.1, U32.2, U34.7
/Link Register (L)/LD1: JP18.2, U32.3, U32.4, U32.5
/Link Register (L)/LD2: JP19.2, U32.6, U32.9, U32.10
/Link Register (L)/LD3: JP20.2, U32.8
/Link Register (L)/~CLRL: U33.1, U38.4
/Link Register (L)/~FL: U33.8, U37.2
/Link Register (L)/~SETL: U32.11, U33.4
/Overflow Register (V)/CLKV: U23.3, U25.4
/Overflow Register (V)/FV0: U23.5, U23.12
/Overflow Register (V)/VD: JP12.1, JP13.1, JP14.1, JP15.1, JP16.1, U23.2
/Overflow Register (V)/VD0: JP12.2, U22.1, U22.2, U24.5
/Overflow Register (V)/VD1: JP13.2, U22.3, U22.4, U22.5
/Overflow Register (V)/VD2: JP14.2, U22.6, U22.9, U22.10
/Overflow Register (V)/VD3: JP15.2, U22.8, U22.12, U22.13
/Overflow Register (V)/VD4: JP16.2, U22.11
/Port A/A0: U1.12, U30.19
/Port A/A1: U1.11, U30.18
/Port A/A2: U1.10, U30.17
/Port A/A3: U1.9, U30.16
/Port A/A4: U1.8, U30.15
/Port A/A5: U1.7, U30.14
/Port A/A6: U2.12, U30.13
/Port A/A7: U2.11, U30.12
/Port A/A8: U2.10, U31.19
/Port A/A9: U2.9, U31.18
/Port A/A10: U2.8, U31.17
/Port A/A11: U2.7, U31.16
/Port A/A12: U3.12, U31.15
/Port A/A13: U3.11, U31.14
/Port A/A14: U3.10, U31.13
/Port A/A15: U3.9, U31.12
/Port B/B0: U1.6, U8.3, U15.3, U17.2, U26.19, U27.2
/Port B/B1: U1.5, U8.4, U9.2, U26.18, U27.3
/Port B/B2: U1.27, U8.5, U9.3, U26.17, U27.4
/Port B/B3: U1.26, U8.6, U9.4, U26.16, U27.5
/Port B/B4: U1.23, U8.7, U9.5, U26.15, U27.6
/Port B/B5: U1.25, U8.8, U9.6, U26.14, U27.7
/Port B/B6: U2.6, U8.9, U9.7, U26.13, U27.8
/Port B/B7: U2.5, U9.8, U13.2, U26.12, U27.9
/Port B/B8: U2.27, U9.9, U13.3, U28.19, U29.2
/Port B/B9: U2.26, U13.4, U14.2, U28.18, U29.3
/Port B/B10: U2.23, U13.5, U14.3, U28.17, U29.4
/Port B/B11: U2.25, U13.6, U14.4, U28.16, U29.5
/Port B/B12: U3.6, U13.7, U14.5, U28.15, U29.6
/Port B/B13: U3.5, U13.8, U14.6, U28.14, U29.7
/Port B/B14: U3.27, U13.9, U14.7, U28.13, U29.8
/Port B/B15: U3.26, U14.8, U15.5, U15.13, U17.1, U28.12, U29.9
/Port B/CP: U4.4, U26.11, U28.11
/RADDR0: P1.B15, U41.1, U43.4
/RADDR1: P1.B16, U41.2, U43.5
/RADDR2: P1.B17, U41.5, U43.6
/T34: JP3.1, P1.B5, U49.1
/X0: U1.21, U2.28
/X1: U2.21, U3.28
/X-IN: JP1.2, U43.3
/sheet5DE3C026/C0: U1.20, U2.4
/sheet5DE3C026/C1: U2.20, U3.4
/sheet5DE3C026/FL-REG: JP5.2, U1.4
/sheet5DE3C026/OP0: U1.29, U2.29, U3.29, U43.17
/sheet5DE3C026/OP1: U1.3, U2.3, U3.3, U43.16
/sheet5DE3C026/OP2: U1.2, U2.2, U3.2, U43.15
/sheet5DE3C026/REGLE: U43.11, U49.5
/sheet5DE3C026/X-IN-REG: U1.28, U43.18
/sheet5DE3C026/Y0: U1.13, U5.2
/sheet5DE3C026/Y1: U1.14, U5.3
/sheet5DE3C026/Y2: U1.15, U5.4
/sheet5DE3C026/Y3: U1.17, U5.5
/sheet5DE3C026/Y4: U1.18, U5.6
/sheet5DE3C026/Y5: U1.19, U5.7
/sheet5DE3C026/Y6: U2.13, U5.8
/sheet5DE3C026/Y7: U2.14, U5.9
/sheet5DE3C026/Y8: U2.15, U6.2
/sheet5DE3C026/Y9: U2.17, U6.3
/sheet5DE3C026/Y10: U2.18, U6.4
/sheet5DE3C026/Y11: U2.19, U6.5
/sheet5DE3C026/Y12: U3.13, U6.6
/sheet5DE3C026/Y13: U3.14, U6.7
/sheet5DE3C026/Y14: U3.15, U6.8
/sheet5DE3C026/Y15: U3.17, U6.9
/sheet5DE3C026/~ALUOE: U5.1, U6.1, U47.4
/sheet5DE3C026/~SETL: U3.21, U45.1
/sheet5DE3C026/~SETV: U3.19, U44.1
/sheet5DF75CCD/LSB: U8.2, U15.9
/sheet5DF75CCD/MSB: U14.9, U15.7
/sheet5DF75CCD/TC: R6.1, U10.4, U16.2, U20.6
/sheet5DF75CCD/x4CLK: R5.1, R7.1, U10.14, U20.3
/sheet5DF75CCD/~EN: U8.1, U9.1, U13.1, U14.1, U16.5
/sheet5DF75CCD/~RIGHT: U9.19, U14.19, U18.4
/sheet5DF75CCD/~START-SYNC: U7.5, U10.11, U20.1
/~ACTION-110: TP14.1, U40.9
/~ACTION-CLL: U38.1, U40.13
/~ACTION-CPL: U32.13, U37.1, U40.14
/~ACTION-SRU: U7.2, U40.7
/~ALU-OP: U39.15, U47.2, U48.2, U49.7
/~FLAGWE: P1.B53, U24.6, U25.1, U34.2, U35.6
/~READ-ALU-B: U27.1, U29.1, U41.10
/~READ-ALU-Y: U41.11, U44.2, U45.2, U47.1
/~RESET: P1.B6, U7.7
/~RSTHOLD: P1.A6, U16.6, U23.1, U23.13, U33.13, U38.3
/~SETL-ROM: U34.14, U35.3, U45.4
/~SETV-ROM: U25.2, U44.4
/~WRITE-ALU-B: U4.1, U42.10
GND: C1.2, C2.2, C3.2, C4.2, C5.2, C6.2, C7.2, C8.2, C9.2, C10.2, C11.2, C12.2, C13.2, C14.2, C15.2, C16.2, C17.2, C18.2, C19.2, C20.2, C21.2, C22.2, C23.2, C24.2, C25.2, C26.2, C27.2, C28.2, C29.2, C30.2, C31.2, C32.2, C33.2, C34.2, C35.2, C36.2, C37.2, C38.2, C39.2, C40.2, C41.2, C42.2, C43.2, C44.2, C45.2, C46.2, C47.2, C48.2, C49.2, C50.2, C51.2, C52.2, C53.2, JP1.1, JP2.2, JP5.3, P1.A72, P1.A73, P1.B1, P1.B2, P1.B81, P1.B82, U1.16, U1.22, U1.24, U2.16, U2.22, U2.24, U3.7, U3.8, U3.16, U3.22, U3.23, U3.24, U3.25, U4.3, U5.10, U5.19, U6.10, U6.19, U7.4, U8.10, U9.10, U10.8, U11.7, U11.11, U12.7, U13.10, U14.10, U15.1, U15.6, U15.8, U15.10, U15.11, U15.15, U16.4, U16.7, U17.4, U17.7, U18.3, U19.3, U20.2, U21.3, U22.7, U23.7, U24.4, U24.7, U25.3, U26.1, U26.10, U27.10, U27.19, U28.1, U28.10, U29.10, U29.19, U30.1, U30.10, U31.1, U31.10, U32.7, U33.7, U34.1, U34.8, U34.10, U34.11, U34.12, U34.13, U34.15, U35.2, U37.3, U38.2, U39.1, U39.2, U39.3, U39.5, U39.8, U40.8, U41.8, U42.8, U43.1, U43.7, U43.8, U43.9, U43.10, U44.3, U45.3, U46.3, U46.4, U46.6, U47.3, U48.3, U49.2, U49.4
unnamed: JP2.1, U46.7
unnamed: JP3.2, U41.4
unnamed: JP4.2, U42.4
unnamed: JP5.1, U43.19
unnamed: JP6.1, U21.2, U46.5
unnamed: JP6.2, R7.2, U21.4
unnamed: R1.2, U23.9
unnamed: R3.1, U12.1
unnamed: R3.2, U11.4
unnamed: R4.1, U12.4
unnamed: R4.2, U11.8
unnamed: R5.2, TP6.1, U12.8
unnamed: R6.2, U10.12
unnamed: TP5.1, U12.3, U12.10
unnamed: TP7.1, U12.6, U12.9
unnamed: U11.2, U11.3
unnamed: U11.6, U11.9
unnamed: U19.4, U34.4
unnamed: U37.4, U38.6
