alexiosc/cft/kicad/cft/cft-dfp/cft-dfp-20191126-r1945.kicad_pcb

## KiCad design kicad/cft/cft-dfp/cft-dfp-20191126-r1945.kicad_pcb (2019-11-23)

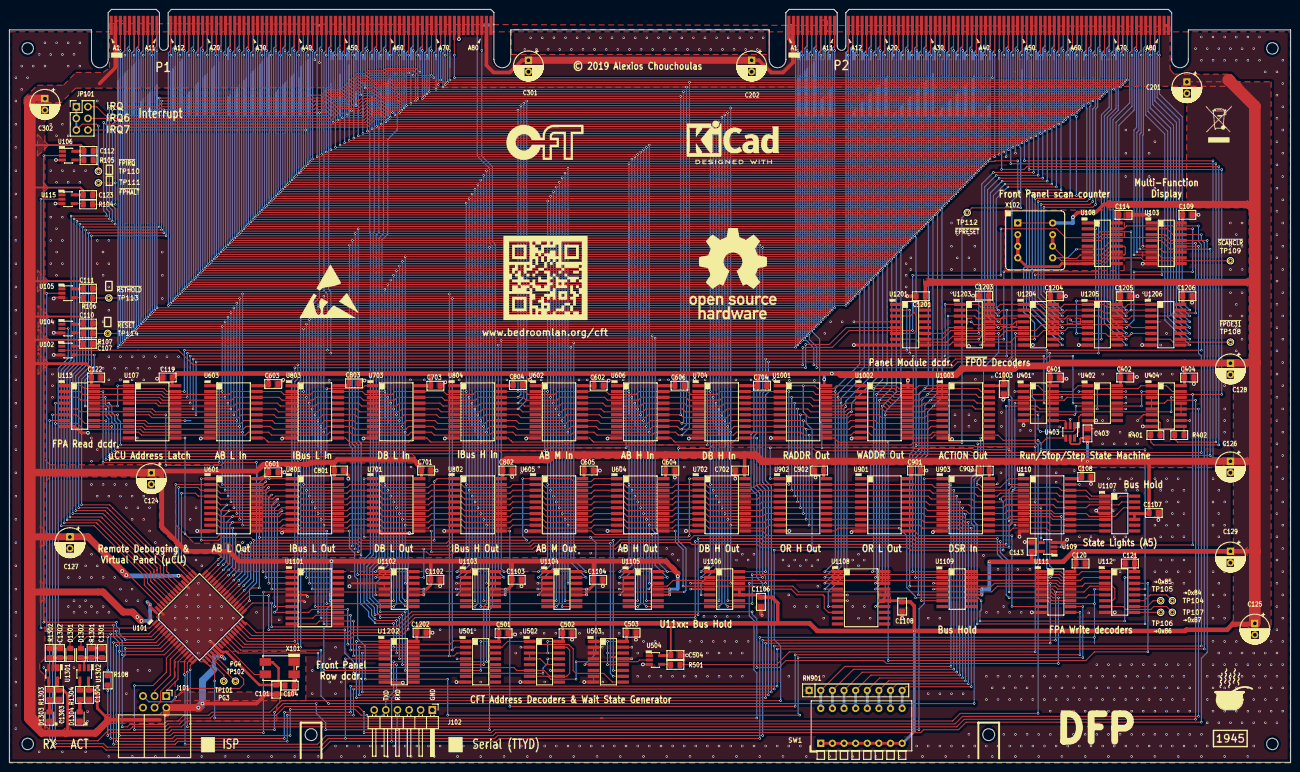
[picture p121: board cft-dfp-20191126-r1945.kicad_pcb from above]

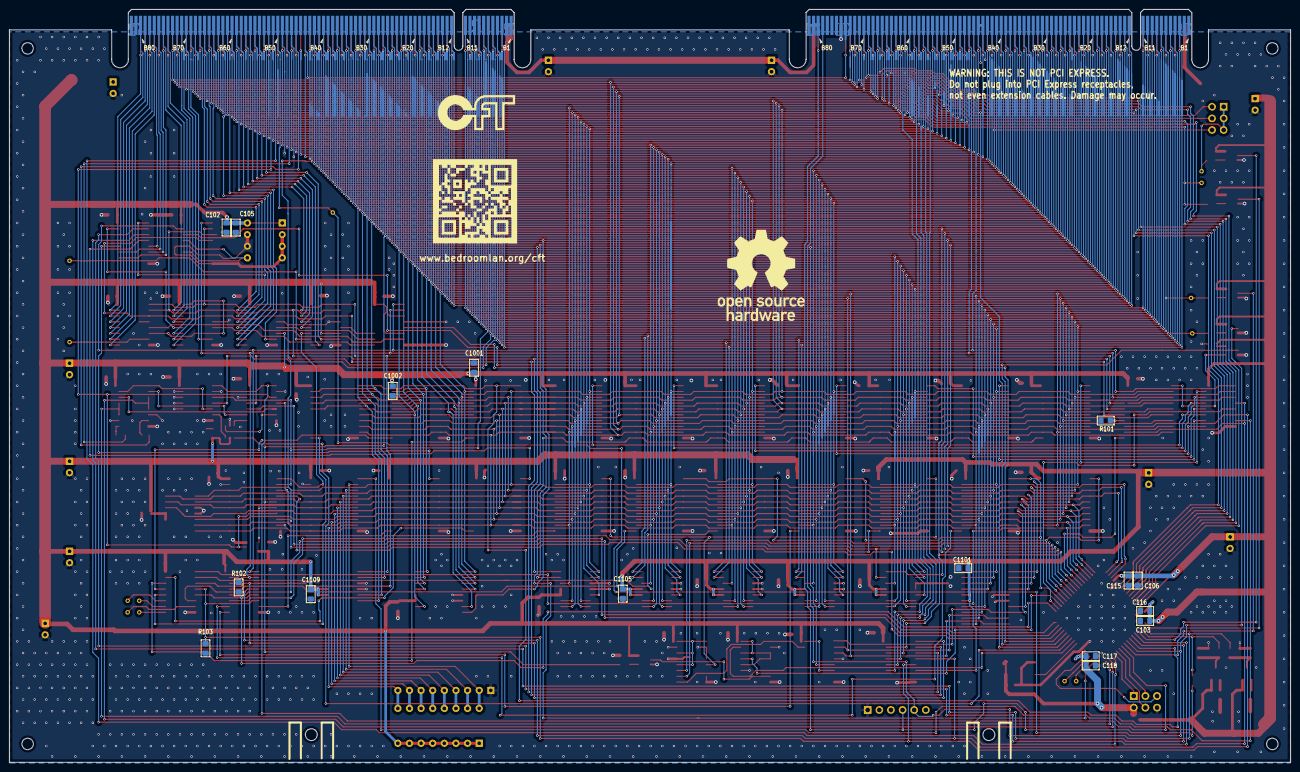
[picture p122: board cft-dfp-20191126-r1945.kicad_pcb from below]

Board: 2 copper layers, 280.0 x 164.6 mm, 180 parts (16 on the bottom side), 280 nets.

Parts:
C101, C102, C103, C106, C117: 1µF; SMD_0805_2012Metric_Pad1.15x1.40mm_HandSolder
C104, C105, C107, C108, C109, C110, C111, C112, C113, C114, C115, C116, C118, C119, C120, C121, C122, C123, C401, C402, C403, C404, C501, C502, C503, C504, C601, C602, C603, C604, C605, C606, C701, C702, C703, C704, C801, C802, C803, C804, C901, C902, C903, C1001, C1002, C1003, C1101, C1102, C1103, C1104, C1105, C1106, C1107, C1108, C1109, C1201, C1202, C1203, C1204, C1205, C1206, C1301, C1302, C1303, C1304: 100nF; SMD_0805_2012Metric_Pad1.15x1.40mm_HandSolder
C124, C125, C126, C127, C128, C129, C201, C202, C301, C302: 47µF; CP_Radial_D6.3mm_P2.50mm
D1301, D1302: D_ALT; D_0805_2012Metric_Pad1.15x1.40mm_HandSolder
D1303, D1304: LED_ALT; LED_0805_2012Metric_Pad1.15x1.40mm_HandSolder
J101: AVR-ISP-6; IDC-Header_2x03_P2.54mm_Horizontal
J102: Conn_01x06; PinHeader_1x06_P2.54mm_Horizontal
JP101: Conn_02x03_Odd_Even; PinHeader_2x03_P2.54mm_Vertical
P1: CFT-2019-Bus; CFT-2019-Card-Edge-Double-Width
P2: CFT-2019-Bus; CFT-2019-Card-Edge-P2-Connector
R101, R102, R103: 4.7kΩ; SMD_0805_2012Metric_Pad1.15x1.40mm_HandSolder
R104, R105, R106, R107, R108, R401, R402, R501: 30Ω; SMD_0805_2012Metric_Pad1.15x1.40mm_HandSolder
R1301, R1302: 220kΩ; SMD_0805_2012Metric_Pad1.15x1.40mm_HandSolder
R1303, R1304: 1.2kΩ; SMD_0805_2012Metric_Pad1.15x1.40mm_HandSolder
RN901: 4.7kΩ; R_Array_SIP9
SW1: SW_DIP_x08; SW_DIP_SPSTx08_Piano_10.8x21.88mm_W7.62mm_P2.54mm
TP101, TP102, TP104, TP105, TP106, TP107, TP108, TP109, TP110, TP111, TP112, TP113, TP114: TestPoint; TestPoint_THTPad_D1.0mm_Drill0.5mm
U101: ATmega64-16AU; TQFP-64
U102, U109: 74LVC1G04; SOT-23-5_HandSoldering
U103: 74HC139; SOIC-16
U104, U105, U106, U115, U504: 74LVC1G07; SOT-23-5_HandSoldering
U107: 74AC573; SOIC-20W
U108: 74HC590; SOIC-16
U110: 74HC540; SOIC-20W
U111, U112, U113, U501, U1201, U1202, U1203, U1204, U1205, U1206: 74HC138; SOIC-16
U401, U402: 74HC74; SOIC-14
U403: 74LVC1G11; SOT-23-6_Handsoldering
U404: 74HC253; SOIC-16
U502: 74HC112; SOIC-16
U503: 74HC251; SOIC-16
U601, U602, U603, U604, U605, U606, U701, U702, U703, U704, U801, U802, U803, U804, U901, U902, U1001, U1002, U1003: 74HC574; SOIC-20W
U903: 74HC541; SOIC-20W
U1101, U1108: SN74ACT1073; SOIC-20W
U1102, U1103, U1104, U1105, U1106, U1107, U1109: SN74ACT1071; SOIC-14
U1301, U1302: 74LVC1G17; SOT-23-5_HandSoldering
X101: CXO; Crystal_SMD_7050-4Pin_7.0x5.0mm
X102: 33 MHz?; Oscillator_DIP-8-socket

Connections:
+5V: C101.1, C102.1, C103.1, C104.1, C105.1, C106.1, C107.1, C108.1, C109.1, C110.1, C111.1, C112.1, C113.1, C114.1, C115.1, C116.1, C117.1, C118.1, C119.1, C120.1, C121.1, C122.1, C123.2, C124.1, C125.1, C126.1, C127.1, C128.1, C129.1, C201.1, C202.1, C301.1, C302.1, C401.1, C402.1, C403.1, C404.1, C501.2, C502.2, C503.2, C504.1, C601.1, C602.1, C603.1, C604.1, C605.1, C606.1, C701.1, C702.1, C703.1, C704.1, C801.1, C802.1, C803.1, C804.1, C901.1, C902.1, C903.1, C1001.1, C1002.1, C1003.1, C1101.2, C1102.1, C1103.1, C1104.1, C1105.1, C1106.1, C1107.1, C1108.1, C1109.1, C1201.1, C1202.1, C1203.1, C1204.1, C1205.1, C1206.1, C1303.1, C1304.1, J101.2, P1.A1, P1.A2, P1.A81, P1.A82, P1.B44, P1.B45, P2.A1, P2.A2, P2.A81, P2.A82, SW1.1, SW1.2, SW1.3, SW1.4, SW1.5, SW1.6, SW1.7, SW1.8, U101.21, U101.52, U101.62, U101.64, U102.5, U103.16, U104.5, U105.5, U106.5, U107.20, U108.16, U109.5, U110.20, U111.16, U112.16, U113.16, U115.5, U401.14, U402.14, U403.5, U404.16, U501.6, U501.16, U502.3, U502.4, U502.12, U502.14, U502.16, U503.1, U503.12, U503.14, U503.16, U504.5, U601.20, U602.20, U603.20, U604.20, U605.20, U606.20, U701.20, U702.20, U703.20, U704.20, U801.20, U802.20, U803.20, U804.20, U901.20, U902.20, U903.20, U1001.20, U1002.20, U1003.20, U1101.15, U1101.16, U1102.10, U1102.11, U1103.10, U1103.11, U1104.10, U1104.11, U1105.10, U1105.11, U1106.10, U1106.11, U1107.10, U1107.11, U1108.15, U1108.16, U1109.10, U1109.11, U1201.3, U1201.6, U1201.16, U1202.6, U1202.16, U1203.6, U1203.16, U1204.6, U1204.16, U1205.6, U1205.16, U1206.6, U1206.16, U1301.5, U1302.5, X101.1, X101.4, X102.1, X102.8
/ALE: U101.43, U107.11
/Address Bus Pod/AB0: P1.A7, P2.A7, U601.19, U603.2, U1101.1
/Address Bus Pod/AB1: P1.A8, P2.A8, U601.18, U603.3, U1101.2
/Address Bus Pod/AB2: P1.A9, P2.A9, U601.17, U603.4, U1101.3
/Address Bus Pod/AB3: P1.A10, P2.A10, U601.16, U603.5, U1101.4
/Address Bus Pod/AB4: P1.A11, P2.A11, U601.15, U603.6, U1101.7
/Address Bus Pod/AB5: P1.A12, P2.A12, U501.1, U601.14, U603.7, U1101.8
/Address Bus Pod/AB6: P1.A13, P2.A13, U501.2, U601.13, U603.8, U1101.9
/Address Bus Pod/AB7: P1.A14, P2.A14, U501.3, U601.12, U603.9, U1101.10
/Address Bus Pod/AB8: P1.A34, P2.A34, U602.2, U605.19, U1104.1
/Address Bus Pod/AB9: P1.A35, P2.A35, U602.3, U605.18, U1104.2
/Address Bus Pod/AB10: P1.A36, P2.A36, U602.4, U605.17, U1104.5
/Address Bus Pod/AB11: P1.A37, P2.A37, U602.5, U605.16, U1104.6
/Address Bus Pod/AB12: P1.A38, P2.A38, U602.6, U605.15, U1104.7
/Address Bus Pod/AB13: P1.A39, P2.A39, U602.7, U605.14, U1104.8
/Address Bus Pod/AB14: P1.A40, P2.A40, U602.8, U605.13, U1104.9
/Address Bus Pod/AB15: P1.A41, P2.A41, U602.9, U605.12, U1104.12
/Address Bus Pod/AB16: P1.A42, P2.A42, U604.19, U606.2, U1105.1
/Address Bus Pod/AB17: P1.A43, P2.A43, U604.18, U606.3, U1105.2
/Address Bus Pod/AB18: P1.A44, P2.A44, U604.17, U606.4, U1105.5
/Address Bus Pod/AB19: P1.A45, P2.A45, U604.16, U606.5, U1105.6
/Address Bus Pod/AB20: P1.A46, P2.A46, U604.15, U606.6, U1105.7
/Address Bus Pod/AB21: P1.A47, P2.A47, U604.14, U606.7, U1105.8
/Address Bus Pod/AB22: P1.A48, P2.A48, U604.13, U606.8, U1105.9
/Address Bus Pod/AB23: P1.A49, P2.A49, U604.12, U606.9, U1105.12
/Address Decoder & Wait States/~DFPSEL: U501.15, U502.1, U503.9
/BUSCP: U101.17, U602.11, U603.11, U606.11, U703.11, U704.11, U803.11, U804.11
/Bus Hold/ACTION0: P1.B30, P2.B30, U1003.19, U1109.1
/Bus Hold/ACTION1: P1.B31, P2.B31, U1003.18, U1109.2
/Bus Hold/ACTION2: P1.B32, P2.B32, U1003.17, U1109.5
/Bus Hold/ACTION3: P1.B33, P2.B33, U1003.16, U1109.6
/Bus Hold/DB0: P1.A15, P2.A15, U701.19, U703.2, U1102.1
/Bus Hold/DB1: P1.A16, P2.A16, U701.18, U703.3, U1102.2
/Bus Hold/DB2: P1.A17, P2.A17, U701.17, U703.4, U1102.5
/Bus Hold/DB3: P1.A18, P2.A18, U701.16, U703.5, U1102.6
/Bus Hold/DB4: P1.A19, P2.A19, U701.15, U703.6, U1102.7
/Bus Hold/DB5: P1.A20, P2.A20, U701.14, U703.7, U1102.8
/Bus Hold/DB6: P1.A21, P2.A21, U701.13, U703.8, U1102.9
/Bus Hold/DB7: P1.A22, P2.A22, U701.12, U703.9, U1102.12
/Bus Hold/DB8: P1.A56, P2.A56, U702.19, U704.2, U1106.1
/Bus Hold/DB9: P1.A57, P2.A57, U702.18, U704.3, U1106.2
/Bus Hold/DB10: P1.A58, P2.A58, U702.17, U704.4, U1106.5
/Bus Hold/DB11: P1.A59, P2.A59, U702.16, U704.5, U1106.6
/Bus Hold/DB12: P1.A60, P2.A60, U702.15, U704.6, U1106.7
/Bus Hold/DB13: P1.A61, P2.A61, U702.14, U704.7, U1106.8
/Bus Hold/DB14: P1.A62, P2.A62, U702.13, U704.8, U1106.9
/Bus Hold/DB15: P1.A63, P2.A63, U702.12, U704.9, U1106.12
/Bus Hold/IBUS0: P1.B7, P2.B7, U801.19, U803.2, U1101.20
/Bus Hold/IBUS1: P1.B8, P2.B8, U801.18, U803.3, U1101.19
/Bus Hold/IBUS2: P1.B9, P2.B9, U801.17, U803.4, U1101.18
/Bus Hold/IBUS3: P1.B10, P2.B10, U801.16, U803.5, U1101.17
/Bus Hold/IBUS4: P1.B11, P2.B11, U801.15, U803.6, U1101.14
/Bus Hold/IBUS5: P1.B12, P2.B12, U801.14, U803.7, U1101.13
/Bus Hold/IBUS6: P1.B13, P2.B13, U801.13, U803.8, U1101.12
/Bus Hold/IBUS7: P1.B14, P2.B14, U801.12, U803.9, U1101.11
/Bus Hold/IBUS8: P1.B34, P2.B34, U802.19, U804.2, U1103.1
/Bus Hold/IBUS9: P1.B35, P2.B35, U802.18, U804.3, U1103.2
/Bus Hold/IBUS10: P1.B36, P2.B36, U802.17, U804.4, U1103.5
/Bus Hold/IBUS11: P1.B37, P2.B37, U802.16, U804.5, U1103.6
/Bus Hold/IBUS12: P1.B38, P2.B38, U802.15, U804.6, U1103.7
/Bus Hold/IBUS13: P1.B39, P2.B39, U802.14, U804.7, U1103.8
/Bus Hold/IBUS14: P1.B40, P2.B40, U802.13, U804.8, U1103.9
/Bus Hold/IBUS15: P1.B41, P2.B41, U802.12, U804.9, U1103.12
/Bus Hold/RADDR0: P1.B15, P2.B15, U1001.19, U1108.1
/Bus Hold/RADDR1: P1.B16, P2.B16, U1001.18, U1108.2
/Bus Hold/RADDR2: P1.B17, P2.B17, U1001.17, U1108.3
/Bus Hold/RADDR3: P1.B18, P2.B18, U1001.16, U1108.4
/Bus Hold/RADDR4: P1.B19, P2.B19, U1001.15, U1108.7
/Bus Hold/WADDR0: P1.B20, P2.B20, U1002.19, U1108.20
/Bus Hold/WADDR1: P1.B21, P2.B21, U1002.18, U1108.19
/Bus Hold/WADDR2: P1.B22, P2.B22, U1002.17, U1108.18
/Bus Hold/WADDR3: P1.B23, P2.B23, U1002.16, U1108.17
/Bus Hold/WADDR4: P1.B24, P2.B24, U1002.15, U1108.14
/CLK1: P1.B3, P2.B3, U1104.13
/CLK2: P1.B4, P2.B4, U1104.14
/CLK3: P1.A3, P2.A3, U1103.13
/CLK4: P1.A4, P2.A4, U401.11, U1103.14
/CLRWS: U101.35, U502.13
/FP Scan Logic/Decoder/~LMOE0: U1201.11, U1203.5
/FP Scan Logic/Decoder/~LMOE1: U1201.10, U1204.5
/FP Scan Logic/Decoder/~LMOE2: U1201.9, U1205.5
/FP Scan Logic/Decoder/~LMOE3: U1201.7, U1206.5
/FPA0: P1.B46, U107.19, U108.15, U111.1, U112.1, U113.1, U1201.1
/FPA1: P1.B47, U107.18, U108.1, U111.2, U112.2, U113.2, U1201.2
/FPA2: U107.17, U108.2, U111.3, U112.3, U113.3, U1202.1, U1203.1, U1204.1, U1205.1, U1206.1
/FPA3: U107.16, U108.3, U1202.2, U1203.2, U1204.2, U1205.2, U1206.2
/FPA4: U107.15, U108.4, U1202.3, U1203.3, U1204.3, U1205.3, U1206.3
/FPA5: R101.1, U107.14
/FPA6: R103.1, U107.13, U111.6, U112.4, U113.6, U1202.5
/FPA7: R102.1, U107.12, U111.4, U112.6, U113.4, U1202.4
/FPCLKEN: P2.B46, R401.1
/FPCLKEN-IN: U101.15, U404.3, U404.4, U404.5
/FPD0: P1.B48, P1.B63, P2.B63, U101.51, U107.2, U110.18, U601.2, U602.19, U603.19, U604.2, U605.2, U606.19, U701.2, U702.2, U703.19, U704.19, U801.2, U802.2, U803.19, U804.19, U901.2, U901.19, U902.2, U902.19, U903.18, U1001.2, U1002.2, U1003.2, U1107.1
/FPD1: P1.B49, P1.B64, P2.B64, U101.50, U107.3, U110.17, U601.3, U602.18, U603.18, U604.3, U605.3, U606.18, U701.3, U702.3, U703.18, U704.18, U801.3, U802.3, U803.18, U804.18, U901.3, U901.18, U902.3, U902.18, U903.17, U1001.3, U1002.3, U1003.3, U1107.14
/FPD2: P1.B50, P1.B65, P2.B65, U101.49, U107.4, U110.16, U601.4, U602.17, U603.17, U604.4, U605.4, U606.17, U701.4, U702.4, U703.17, U704.17, U801.4, U802.4, U803.17, U804.17, U901.4, U901.17, U902.4, U902.17, U903.16, U1001.4, U1002.4, U1003.4, U1107.2
/FPD3: P1.B51, P1.B66, P2.B66, U101.48, U107.5, U110.15, U601.5, U602.16, U603.16, U604.5, U605.5, U606.16, U701.5, U702.5, U703.16, U704.16, U801.5, U802.5, U803.16, U804.16, U901.5, U901.16, U902.5, U902.16, U903.15, U1001.5, U1002.5, U1003.5, U1107.13
/FPD4: P1.B52, P1.B68, P2.B68, U101.47, U107.6, U110.14, U601.6, U602.15, U603.15, U604.6, U605.6, U606.15, U701.6, U702.6, U703.15, U704.15, U801.6, U802.6, U803.15, U804.15, U901.6, U901.15, U902.6, U902.15, U903.14, U1001.6, U1002.6, U1003.6, U1107.12
/FPD5: P1.B53, P1.B69, P2.B69, U101.46, U107.7, U110.13, U601.7, U602.14, U603.14, U604.7, U605.7, U606.14, U701.7, U702.7, U703.14, U704.14, U801.7, U802.7, U803.14, U804.14, U901.7, U901.14, U902.7, U902.14, U903.13, U1001.7, U1002.7, U1003.7, U1107.5
/FPD6: P1.B54, P1.B72, P2.B72, U101.45, U107.8, U110.12, U601.8, U602.13, U603.13, U604.8, U605.8, U606.13, U701.8, U702.8, U703.13, U704.13, U801.8, U802.8, U803.13, U804.13, U901.8, U901.13, U902.8, U902.13, U903.12, U1001.8, U1002.8, U1003.8, U1107.6
/FPD7: P1.B55, P1.B73, P2.B73, U101.44, U107.9, U110.11, U601.9, U602.12, U603.12, U604.9, U605.9, U606.12, U701.9, U702.9, U703.12, U704.12, U801.9, U802.9, U803.12, U804.12, U901.9, U901.12, U902.9, U902.12, U903.11, U1001.9, U1002.9, U1003.9, U1107.7
/FPFETCH∕~EXEC: P2.B52, U109.2, U110.7, U401.3
/FPµSTEP: P2.B48, R402.1
/FPµSTEP-IN: U101.16, U404.11, U404.12, U404.13
/Left Edge Connector/RSVD1: P1.A50, P2.A50
/Left Edge Connector/RSVD2: P1.A29, P2.A29
/Left Edge Connector/RSVD3: P1.A30, P2.A30
/Left Edge Connector/RSVD4: P1.A31, P2.A31
/Left Edge Connector/RSVD5: P1.A32, P2.A32
/Left Edge Connector/RSVD6: P1.A33, P2.A33
/Left Edge Connector/RSVD7: P1.B28, P2.B28
/Left Edge Connector/RSVD8: P1.B29, P2.B29
/Left Edge Connector/~IRQ0: P1.A51, P2.A51
/Left Edge Connector/~IRQ1: P1.A52, P2.A52
/Left Edge Connector/~IRQ2: P1.A53, P2.A53
/Left Edge Connector/~IRQ3: P1.A54, P2.A54
/Left Edge Connector/~IRQ4: P1.A55, P2.A55
/Left Edge Connector/~IRQ5: P1.A67, P2.A67
/MFD0: U101.5, U103.2, U103.14
/MFD1: U101.6, U103.3, U103.13
/MISO: J101.1, U101.13
/MOSI: J101.4, U101.12
/POWER: P1.A74, P2.B44
/RXD: D1301.2, J102.5, P1.B79, U101.2
/Run Control State Machine/RESETTING: U402.5, U404.1, U404.15
/Run Control State Machine/STEPPING: U401.5, U404.14
/Run Control State Machine/µSTEPPING: U401.9, U404.2
/SCANCLK: U108.11, U108.13, X102.5
/SCANEN: U102.4, U107.1
/SCK: J101.3, U101.11
/STEP∕~RUN: U101.31, U110.3, U401.4
/SWA0: P1.B61, U101.61
/SWA1: P1.A64, U101.60
/SWA2: P1.A65, U101.59
/SWA3: P1.A66, U101.58
/SWD0: P1.B67, U101.57
/SWD1: P1.A69, U101.56
/SWD2: P1.B70, U101.55
/SWD3: P1.A71, U101.54
/T34: P1.B5, P2.B5, U1105.14
/TXD: D1302.2, R108.2, U101.3
/TXD1: J102.4, P1.A80, R108.1
/WSTB: P1.A5, P2.A5, U1105.13
/~ABOE: U101.37, U601.1, U604.1, U605.1
/~CLR: U101.10, U401.1, U401.13, U402.1
/~DBOE: U101.38, U503.11
/~DBOE1: U503.5, U701.1, U702.1
/~ENDEXT: P1.A72, P2.A72
/~FPDRHOE: P2.B77, U103.5
/~FPDRLOE: P2.A76, U103.11
/~FPHALT: U101.1, U115.2
/~FPIRQ: U101.4, U106.2
/~FPOE0: P2.B58, U1203.15
/~FPOE1: P2.B67, U1204.15
/~FPOE2: P2.B75, U1205.15
/~FPOE3: P2.A80, U1206.15
/~FPOE4: P2.B57, U1203.14
/~FPOE5: P2.A66, U1204.14
/~FPOE6: P2.A74, U1205.14
/~FPOE7: P2.B80, U1206.14
/~FPOE8: P2.B56, U1203.13
/~FPOE9: P2.A65, U1204.13
/~FPOE10: P2.B74, U1205.13
/~FPOE11: P2.A79, U1206.13
/~FPOE12: P2.B55, U1203.12
/~FPOE13: U103.1, U1204.12
/~FPOE14: U103.15, U1205.12
/~FPOE15: P2.B79, U1206.12
/~FPOE16: U110.1, U1203.11
/~FPOE17: P2.A64, U1204.11
/~FPOE18: P2.A71, U1205.11
/~FPOE19: P2.A78, U1206.11
/~FPOE21: P2.B62, U1204.10
/~FPOE22: P2.B71, U1205.10
/~FPOE23: P2.B78, U1206.10
/~FPOE24: P2.B54, U1203.9
/~FPOE25: P2.B61, U1204.9
/~FPOE26: P2.B70, U1205.9
/~FPOE27: P2.A77, U1206.9
/~FPOE28: P2.B53, U1203.7
/~FPOE29: P2.B59, U1204.7
/~FPOE30: P2.A69, U1205.7
/~FPOE31: TP108.1, U1206.7
/~FPRAM~∕ROM: P2.B51, U101.14
/~FPRESET: P2.B50, TP112.1, U101.8, U104.2
/~FPRSTHOLD: U101.9, U105.2
/~FPSPHOE: P2.B76, U103.6
/~FPSPLOE: P2.A75, U103.10
/~HALT: P1.B60, P2.B60, R104.1, TP111.1
/~IBOE: U101.36, U801.1, U802.1
/~IO: P1.B26, P2.B26, U101.40, U1108.8
/~IODEV1xx: P1.A24, P2.A24, U501.5, U1106.14
/~IODEV2xx: P1.A25, P2.A25
/~IODEV3xx: P1.A26, P2.A26
/~IOINT: U101.25, U502.6, U502.10, U502.15
/~IRQ: JP101.6, P1.B42, P2.B42
/~IRQ6: JP101.4, P1.A68, P2.A68
/~IRQ7: JP101.2, P1.A70, P2.A70
/~IRQS: P1.B43, P2.B43, U110.8
/~LED-FETCH: U109.4, U110.6
/~LED-STOP: U101.30, U110.4
/~LTSON: P1.B71, U101.27
/~MEM: P1.B25, P2.B25, U101.39, U1106.13
/~ORHOE: U103.4, U902.1
/~ORLOE: U103.12, U901.1
/~PANELEN: U101.29, U1201.5
/~R: P1.A27, P2.A27, U101.41, U503.10, U1102.13
/~RABH: U113.13, U606.1
/~RABL: U113.15, U603.1
/~RABM: U113.14, U602.1
/~RD: U101.34, U113.5
/~RDBH: U113.11, U704.1
/~RDBL: U113.12, U703.1
/~RDSR: U113.7, U903.1
/~RESET: P1.B6, P2.B6, R107.1, TP114.1, U402.4
/~RIBH: U113.9, U804.1
/~RIBL: U113.10, U803.1
/~ROW1: P1.B56, U1202.15
/~ROW2: P1.B57, U1202.14
/~ROW3: P1.B59, U1202.13
/~ROW4: P1.B58, U1202.12
/~ROW5: P1.B62, U1202.11
/~RSTHOLD: P1.A6, P2.A6, R106.1, TP113.1, U110.2, U402.3
/~SCANCLR: TP109.1, U108.10, U1203.10
/~SCANEN: U101.28, U102.2, U108.14
/~SKIPEXT: P1.A73, P2.A73
/~SYSDEV: P1.A23, P2.A23
/~W: P1.A28, P2.A28, U101.42, U1102.14
/~WABH: U111.13, U604.11
/~WABL: U111.15, U601.11
/~WABM: U111.14, U605.11
/~WAIT: U101.26, U403.4
/~WDBH: U111.11, U702.11
/~WDBL: U111.12, U701.11
/~WIBH: U111.9, U802.11
/~WIBL: U111.10, U801.11
/~WORH: U112.15, U902.11
/~WORL: U111.7, U901.11
/~WR: U101.33, U111.5, U112.5
/~WS: P1.B27, P2.B27, R501.1, U110.5
/~µCRST: J101.5, U101.20
/~µCVCPH: U112.12, U1003.11
/~µCVCPL: U112.14, U1001.11
/~µCVCPM: U112.13, U1002.11
/~µCVOE: U101.7, U1001.1, U1002.1, U1003.1
/~µSTEP: U101.32, U401.10
/µCCLK: U101.24, X101.3
GND: C101.2, C102.2, C103.2, C104.2, C105.2, C106.2, C107.2, C108.2, C109.2, C110.2, C111.2, C112.2, C113.2, C114.2, C115.2, C116.2, C117.2, C118.2, C119.2, C120.2, C121.2, C122.2, C123.1, C124.2, C125.2, C126.2, C127.2, C128.2, C129.2, C201.2, C202.2, C301.2, C302.2, C401.2, C402.2, C403.2, C404.2, C501.1, C502.1, C503.1, C504.2, C601.2, C602.2, C603.2, C604.2, C605.2, C606.2, C701.2, C702.2, C703.2, C704.2, C801.2, C802.2, C803.2, C804.2, C901.2, C902.2, C903.2, C1001.2, C1002.2, C1003.2, C1101.1, C1102.2, C1103.2, C1104.2, C1105.2, C1106.2, C1107.2, C1108.2, C1109.2, C1201.2, C1202.2, C1203.2, C1204.2, C1205.2, C1206.2, C1301.2, C1302.2, C1303.2, C1304.2, D1303.1, D1304.1, J101.6, J102.1, P1.A75, P1.B1, P1.B2, P1.B74, P1.B75, P1.B80, P1.B81, P1.B82, P2.B1, P2.B2, P2.B47, P2.B49, P2.B81, P2.B82, R101.2, R102.2, R103.2, R1301.1, R1302.1, RN901.1, U101.22, U101.53, U101.63, U102.3, U103.8, U104.3, U105.3, U106.3, U107.10, U108.8, U108.12, U109.3, U110.9, U110.10, U110.19, U111.8, U112.8, U113.8, U115.3, U401.2, U401.7, U401.12, U402.2, U402.7, U402.10, U402.11, U402.12, U402.13, U403.2, U404.6, U404.8, U404.10, U501.4, U501.8, U502.2, U502.8, U502.11, U503.2, U503.3, U503.4, U503.7, U503.8, U503.13, U503.15, U504.3, U601.10, U602.10, U603.10, U604.10, U605.10, U606.10, U701.10, U702.10, U703.10, U704.10, U801.10, U802.10, U803.10, U804.10, U901.10, U902.10, U903.10, U903.19, U1001.10, U1002.10, U1003.10, U1101.5, U1101.6, U1102.3, U1102.4, U1103.3, U1103.4, U1104.3, U1104.4, U1105.3, U1105.4, U1106.3, U1106.4, U1107.3, U1107.4, U1108.5, U1108.6, U1109.3, U1109.4, U1201.4, U1201.8, U1202.8, U1203.4, U1203.8, U1204.4, U1204.8, U1205.4, U1205.8, U1206.4, U1206.8, U1301.3, U1302.3, X101.2, X102.2, X102.3, X102.4, X102.6, X102.7
unnamed: C1301.1, D1302.1, R1301.2, U1302.2
unnamed: C1302.1, D1301.1, R1302.2, U1301.2
unnamed: D1303.2, R1303.1
unnamed: D1304.2, R1304.1
unnamed: JP101.1, JP101.3, JP101.5, R105.1, TP110.1
unnamed: R104.2, U115.4
unnamed: R105.2, U106.4
unnamed: R106.2, U105.4
unnamed: R107.2, U104.4
unnamed: R401.2, U404.7
unnamed: R402.2, U404.9
unnamed: R501.2, U504.4
unnamed: R1303.2, U1301.4
unnamed: R1304.2, U1302.4
unnamed: RN901.2, SW1.16, U903.2
unnamed: RN901.3, SW1.15, U903.3
unnamed: RN901.4, SW1.14, U903.4
unnamed: RN901.5, SW1.13, U903.5
unnamed: RN901.6, SW1.12, U903.6
unnamed: RN901.7, SW1.11, U903.7
unnamed: RN901.8, SW1.10, U903.8
unnamed: RN901.9, SW1.9, U903.9
unnamed: TP101.1, U101.18
unnamed: TP102.1, U101.19
unnamed: TP104.1, U112.11
unnamed: TP105.1, U112.10
unnamed: TP106.1, U112.9
unnamed: TP107.1, U112.7
unnamed: U401.6, U403.1
unnamed: U401.8, U403.3
unnamed: U402.6, U403.6
unnamed: U502.7, U504.2
