alexiosc/cft/eagle/video-max5-revG-eagle7.brd

## EAGLE design eagle/video-max5-revG-eagle7.brd (continued)

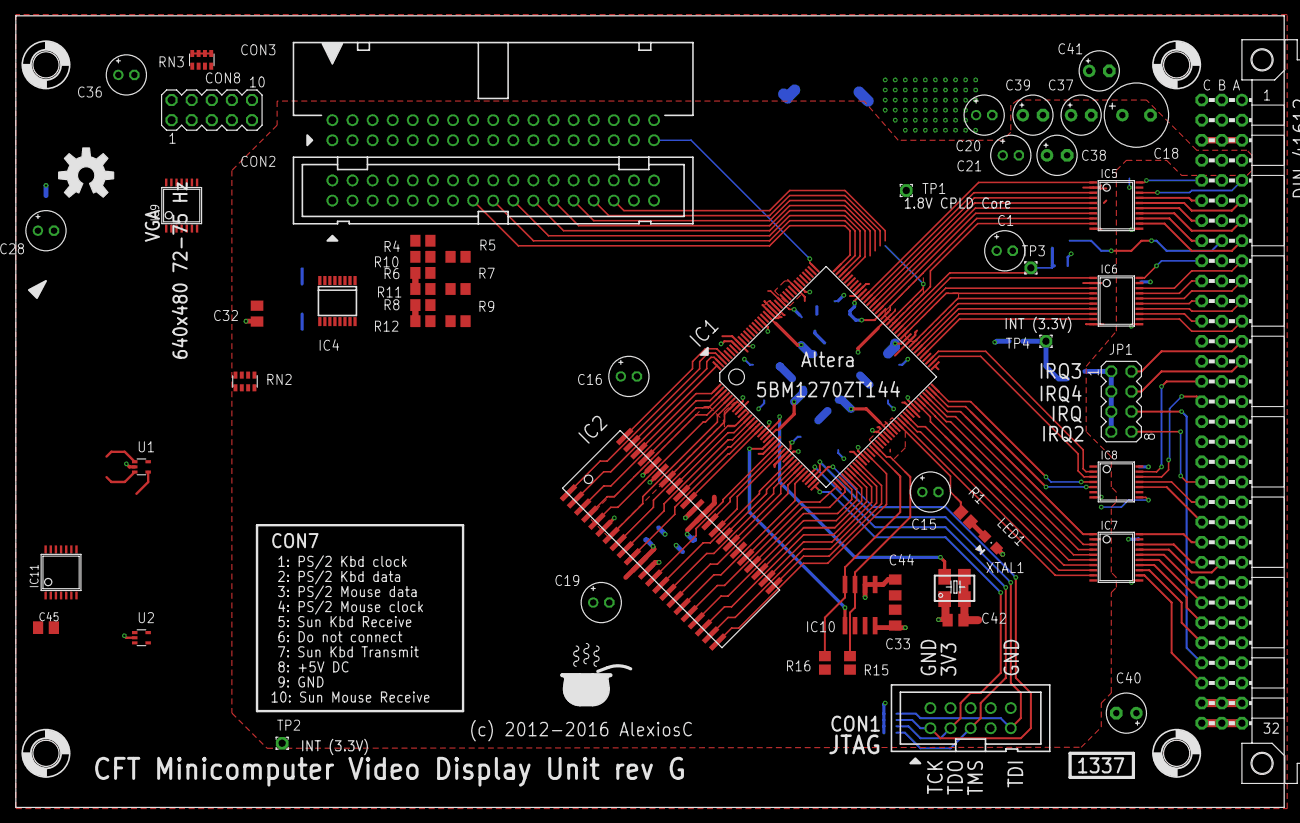
[picture p128: board video-max5-revG-eagle7.brd from above]

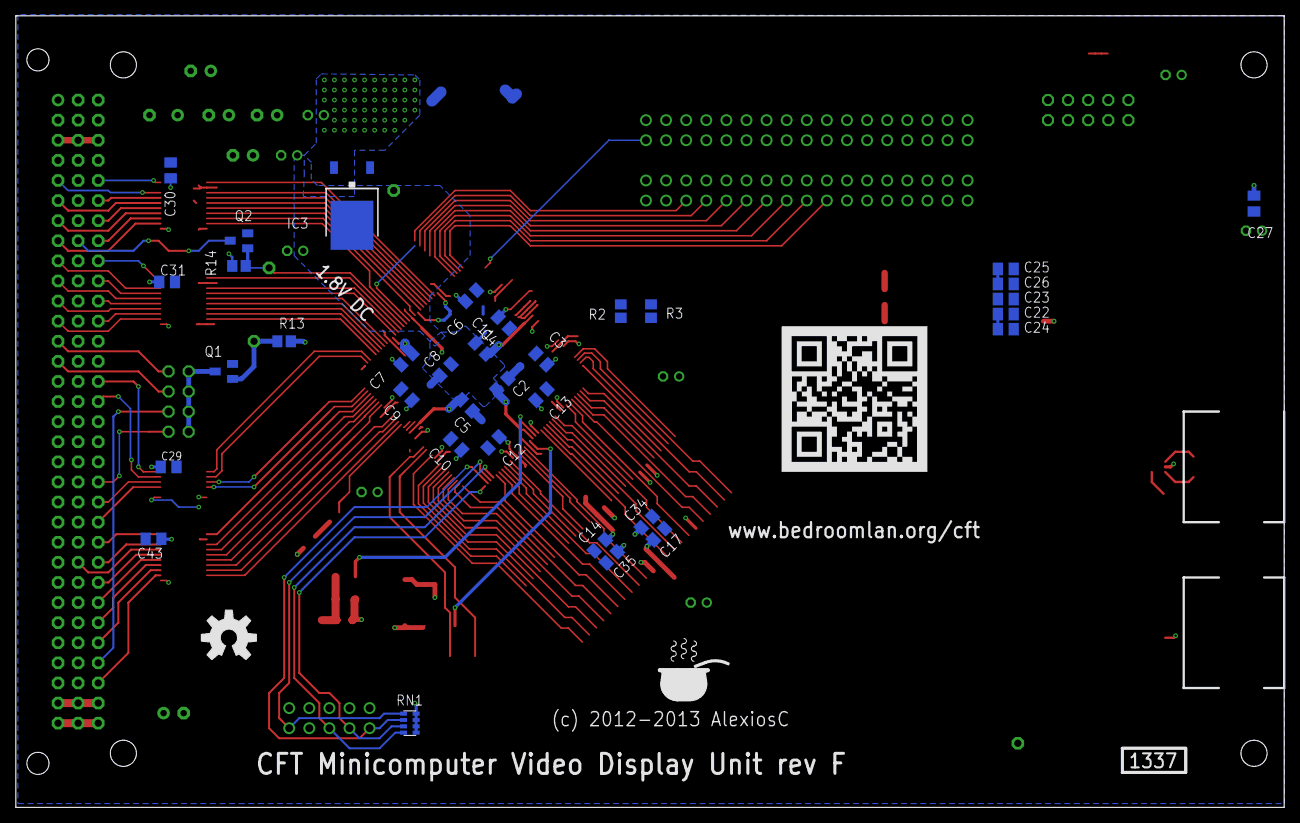
[picture p129: board video-max5-revG-eagle7.brd from below]

Board: 2 copper layers, 160.3 x 100.0 mm, 100 parts (37 on the bottom side), 156 nets.

Other parts of the board:
U$1: SIGNATURESILK; SIGNATURE
