alexiosc/cft/eagle/cft-deb-board.brd

## EAGLE design eagle/cft-deb-board.brd (2019-05-06)

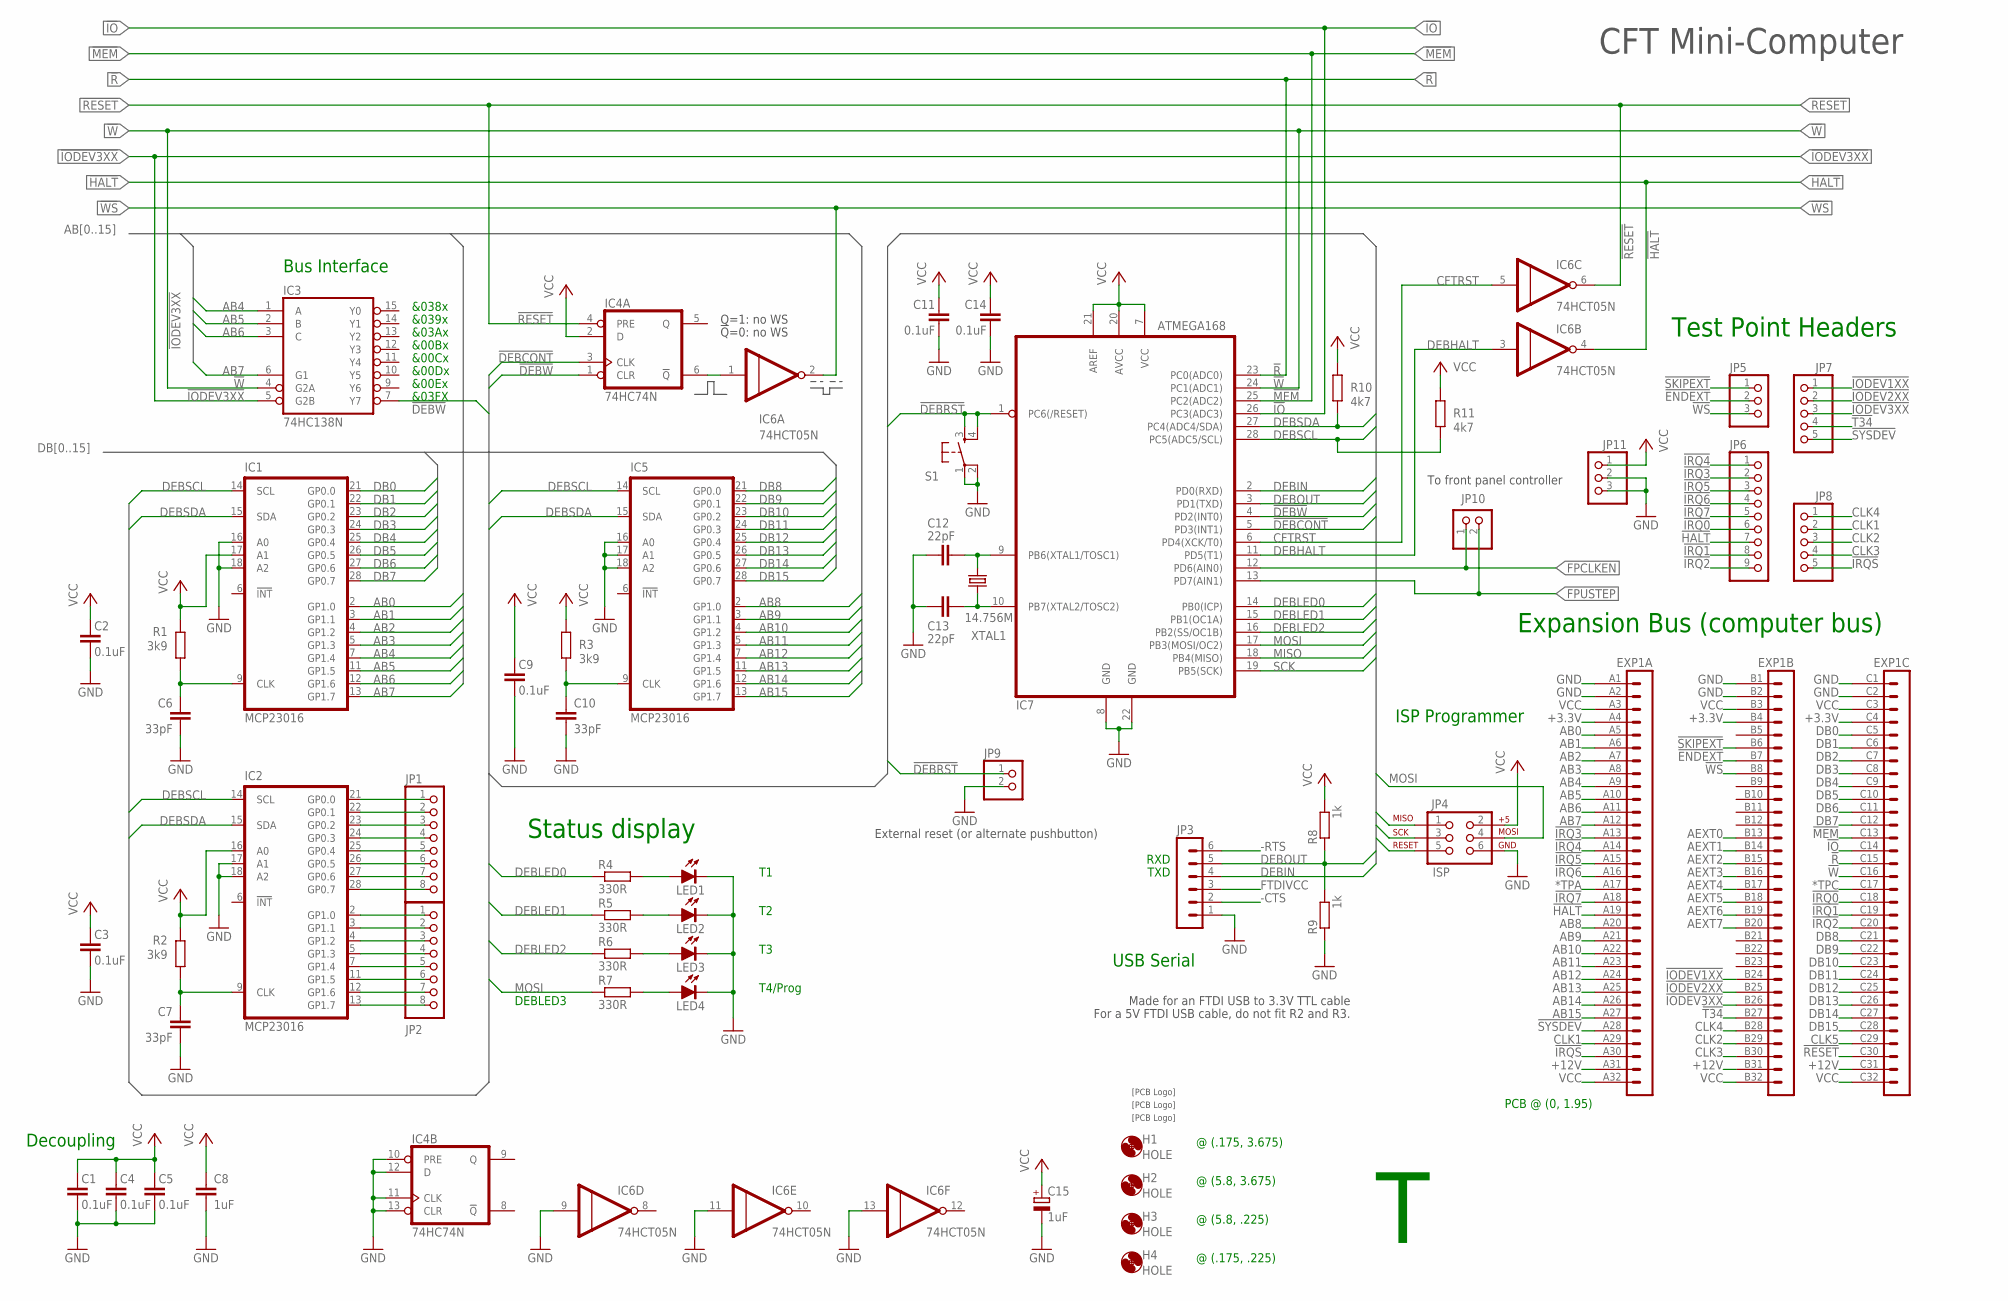
[picture p130: schematic cft-deb-board.sch]

Parts:
C1, C2, C3, C4, C5, C9, C11, C14: 0.1uF; C025-024X044
C6, C7, C10: 33pF; C025-024X044
C8: 1uF; C025-024X044
C12, C13: 22pF; C025-024X044
C15: 1uF; E2,5-5
EXP1: VG96-3K; VG96K
H1, H2, H3, H4: HOLE; STANDOFF_28_60
IC1, IC2, IC5: MCP23016; DIL28-3
IC3: 74HC138N; DIL16
IC4: 74HC74N; DIL14
IC6: 74HCT05N; DIL14
IC7: ATMEGA168; DIL28-3
JP1, JP2: PINHD-1X8; 1X08
JP3: MA06-1
JP4: ISP; 2X3-NS
JP5, JP11: PINHD-1X3; 1X03
JP6: PINHD-1X9; 1X09
JP7, JP8: PINHD-1X5; 1X05
JP9, JP10: PINHD-1X2; 1X02
LED1, LED2, LED3, LED4: LED-5MM-RED; LED5MM
R1, R2, R3: 3k9; 0207/7
R4, R5, R6, R7: 330R; 0207/7
R8, R9: 1k; 0207/7
R10, R11: 4k7; 0207/7
S1: TAC_SWITCHPTH; TACTILE-PTH
U$1: SIGNATURESILK; SIGNATURE
U$2, U$3: SIGNATUREPLANE; SIGNATURE_PLANE
XTAL1: 14.756M; HC49U-V

Connections:
!DEBCONT: IC4.3 (CLK), IC7.5 (PD3(INT1))
!DEBRST: IC7.1 (PC6(/RESET)), JP4.5, JP9.1, S1.3, S1.4
!DEBW: IC3.7 (Y7), IC4.1 (CLR), IC7.4 (PD2(INT0))
!ENDEXT: EXP1.B7 (7), JP5.2
!HALT: EXP1.A19 (19), IC6.4 (O), JP6.7
!IO: EXP1.C14 (14), IC7.26 (PC3(ADC3))
!IODEV1XX: EXP1.B24 (24), JP7.1
!IODEV2XX: EXP1.B25 (25), JP7.2
!IODEV3XX: EXP1.B26 (26), IC3.5 (G2B), JP7.3
!IRQ0: EXP1.C18 (18), JP6.6
!IRQ1: EXP1.C19 (19), JP6.8
!IRQ2: EXP1.C20 (20), JP6.9
!IRQ3: EXP1.A13 (13), JP6.2
!IRQ4: EXP1.A14 (14), JP6.1
!IRQ5: EXP1.A15 (15), JP6.3
!IRQ6: EXP1.A16 (16), JP6.4
!IRQ7: EXP1.A18 (18), JP6.5
!IRQS: EXP1.A30 (30), JP8.5
!MEM: EXP1.C13 (13), IC7.25 (PC2(ADC2))
!R: EXP1.C15 (15), IC7.23 (PC0(ADC0))
!RESET: EXP1.C30 (30), IC4.4 (PRE), IC6.6 (O)
!SKIPEXT: EXP1.B6 (6), JP5.1
!SYSDEV: EXP1.A28 (28), JP7.5
!T34: EXP1.B27 (27), JP7.4
!W: EXP1.C16 (16), IC3.4 (G2A), IC7.24 (PC1(ADC1))
!WS: EXP1.B8 (8), IC6.2 (O), JP5.3
*TPA: EXP1.A17 (17)
*TPC: EXP1.C17 (17)
+3.3V: EXP1.A4 (4), EXP1.B4 (4), EXP1.C4 (4)
+12V: EXP1.A31 (31), EXP1.B31 (31), EXP1.C31 (31)
-CTS: JP3.2
-RTS: JP3.6
AB0: EXP1.A5 (5), IC1.2 (GP1.0)
AB1: EXP1.A6 (6), IC1.3 (GP1.1)
AB2: EXP1.A7 (7), IC1.4 (GP1.2)
AB3: EXP1.A8 (8), IC1.5 (GP1.3)
AB4: EXP1.A9 (9), IC1.7 (GP1.4), IC3.1 (A)
AB5: EXP1.A10 (10), IC1.11 (GP1.5), IC3.2 (B)
AB6: EXP1.A11 (11), IC1.12 (GP1.6), IC3.3 (C)
AB7: EXP1.A12 (12), IC1.13 (GP1.7), IC3.6 (G1)
AB8: EXP1.A20 (20), IC5.2 (GP1.0)
AB9: EXP1.A21 (21), IC5.3 (GP1.1)
AB10: EXP1.A22 (22), IC5.4 (GP1.2)
AB11: EXP1.A23 (23), IC5.5 (GP1.3)
AB12: EXP1.A24 (24), IC5.7 (GP1.4)
AB13: EXP1.A25 (25), IC5.11 (GP1.5)
AB14: EXP1.A26 (26), IC5.12 (GP1.6)
AB15: EXP1.A27 (27), IC5.13 (GP1.7)
AEXT0: EXP1.B13 (13)
AEXT1: EXP1.B14 (14)
AEXT2: EXP1.B15 (15)
AEXT3: EXP1.B16 (16)
AEXT4: EXP1.B17 (17)
AEXT5: EXP1.B18 (18)
AEXT6: EXP1.B19 (19)
AEXT7: EXP1.B20 (20)
CFTRST: IC6.5 (I), IC7.6 (PD4(XCK/T0))
CLK1: EXP1.A29 (29), JP8.2
CLK2: EXP1.B29 (29), JP8.3
CLK3: EXP1.B30 (30), JP8.4
CLK4: EXP1.B28 (28), JP8.1
CLK5: EXP1.C29 (29)
DB0: EXP1.C5 (5), IC1.21 (GP0.0)
DB1: EXP1.C6 (6), IC1.22 (GP0.1)
DB2: EXP1.C7 (7), IC1.23 (GP0.2)
DB3: EXP1.C8 (8), IC1.24 (GP0.3)
DB4: EXP1.C9 (9), IC1.25 (GP0.4)
DB5: EXP1.C10 (10), IC1.26 (GP0.5)
DB6: EXP1.C11 (11), IC1.27 (GP0.6)
DB7: EXP1.C12 (12), IC1.28 (GP0.7)
DB8: EXP1.C21 (21), IC5.21 (GP0.0)
DB9: EXP1.C22 (22), IC5.22 (GP0.1)
DB10: EXP1.C23 (23), IC5.23 (GP0.2)
DB11: EXP1.C24 (24), IC5.24 (GP0.3)
DB12: EXP1.C25 (25), IC5.25 (GP0.4)
DB13: EXP1.C26 (26), IC5.26 (GP0.5)
DB14: EXP1.C27 (27), IC5.27 (GP0.6)
DB15: EXP1.C28 (28), IC5.28 (GP0.7)
DEBHALT: IC6.3 (I), IC7.11 (PD5(T1))
DEBIN: IC7.2 (PD0(RXD)), JP3.4
DEBLED0: IC7.14 (PB0(ICP)), R4.1
DEBLED1: IC7.15 (PB1(OC1A)), R5.1
DEBLED2: IC7.16 (PB2(SS/OC1B)), R6.1
DEBOUT: IC7.3 (PD1(TXD)), JP3.5, R8.1, R9.2
DEBSCL: IC1.14 (SCL), IC2.14 (SCL), IC5.14 (SCL), IC7.28 (PC5(ADC5/SCL)), R11.2
DEBSDA: IC1.15 (SDA), IC2.15 (SDA), IC5.15 (SDA), IC7.27 (PC4(ADC4/SDA)), R10.2
FPCLKEN: IC7.12 (PD6(AIN0)), JP10.1
FPUSTEP: IC7.13 (PD7(AIN1)), JP10.2
FTDIVCC: JP3.3
GND: C1.1, C2.1, C3.1, C4.1, C5.1, C6.2, C7.2, C8.2, C9.1, C10.2, C11.1, C12.2, C13.2, C14.1, C15.-, EXP1.A1 (1), EXP1.A2 (2), EXP1.B1 (1), EXP1.B2 (2), EXP1.C1 (1), EXP1.C2 (2), IC1.1 (GND), IC1.8 (GND), IC1.16 (A0), IC1.18 (A2), IC1.19 (GND), IC2.1 (GND), IC2.8 (GND), IC2.17 (A1), IC2.18 (A2), IC2.19 (GND), IC3.8 (GND), IC4.7 (GND), IC4.10 (PRE), IC4.11 (CLK), IC4.12 (D), IC4.13 (CLR), IC5.1 (GND), IC5.8 (GND), IC5.16 (A0), IC5.17 (A1), IC5.18 (A2), IC5.19 (GND), IC6.7 (GND), IC6.9 (I), IC6.11 (I), IC6.13 (I), IC7.8 (GND), IC7.22 (GND), JP3.1, JP4.6, JP9.2, JP11.2, JP11.3, LED1.K (C), LED2.K (C), LED3.K (C), LED4.K (C), R9.1, S1.1, S1.2
MISO: IC7.18 (PB4(MISO)), JP4.1
MOSI: IC7.17 (PB3(MOSI/OC2)), JP4.4, R7.1
unnamed: C12.1, IC7.9 (PB6(XTAL1/TOSC1)), XTAL1.1
unnamed: C13.1, IC7.10 (PB7(XTAL2/TOSC2)), XTAL1.2
unnamed: IC4.6 (!Q), IC6.1 (I)
unnamed: LED1.A, R4.2
unnamed: C6.1, IC1.9 (CLK), R1.2
unnamed: LED2.A, R5.2
unnamed: C10.1, IC5.9 (CLK), R3.2
unnamed: C7.1, IC2.9 (CLK), R2.2
unnamed: IC2.21 (GP0.0), JP1.1
unnamed: LED3.A, R6.2
unnamed: LED4.A, R7.2
unnamed: IC2.22 (GP0.1), JP1.2
unnamed: IC2.23 (GP0.2), JP1.3
unnamed: IC2.24 (GP0.3), JP1.4
unnamed: IC2.25 (GP0.4), JP1.5
unnamed: IC2.26 (GP0.5), JP1.6
unnamed: IC2.27 (GP0.6), JP1.7
unnamed: IC2.28 (GP0.7), JP1.8
unnamed: IC2.2 (GP1.0), JP2.1
unnamed: IC2.3 (GP1.1), JP2.2
unnamed: IC2.4 (GP1.2), JP2.3
unnamed: IC2.5 (GP1.3), JP2.4
unnamed: IC2.7 (GP1.4), JP2.5
unnamed: IC2.11 (GP1.5), JP2.6
unnamed: IC2.12 (GP1.6), JP2.7
unnamed: IC2.13 (GP1.7), JP2.8
SCK: IC7.19 (PB5(SCK)), JP4.3
VCC: C1.2, C2.2, C3.2, C4.2, C5.2, C8.1, C9.2, C11.2, C14.2, C15.+, EXP1.A3 (3), EXP1.A32 (32), EXP1.B3 (3), EXP1.B32 (32), EXP1.C3 (3), EXP1.C32 (32), IC1.17 (A1), IC1.20 (VCC), IC2.16 (A0), IC2.20 (VCC), IC3.16 (VCC), IC4.2 (D), IC4.14 (VCC), IC5.20 (VCC), IC6.14 (VCC), IC7.7 (VCC), IC7.20 (AVCC), IC7.21 (AREF), JP4.2, JP11.1, R1.1, R2.1, R3.1, R8.2, R10.1, R11.1

Notes on the sheet:
Expansion Bus (computer bus)
PCB @ (0, 1.95)
@ (.175, 3.675)
@ (5.8, 3.675)
@ (5.8, .225)
@ (.175, .225)
CFT Mini-Computer
USB Serial
Made for an FTDI USB to 3.3V TTL cable
For a 5V FTDI USB cable, do not fit R2 and R3.
ISP Programmer
&038x
&039x
&03Ax
&00Bx
&00Cx
&00Dx
&00Ex
&03FX
Bus Interface
RXD
TXD
Decoupling
Test Point Headers
Q=1: no WS
!Q!=0: no WS
Status display
DEBLED3
T4/Prog
External reset (or alternate pushbutton)
To front panel controller

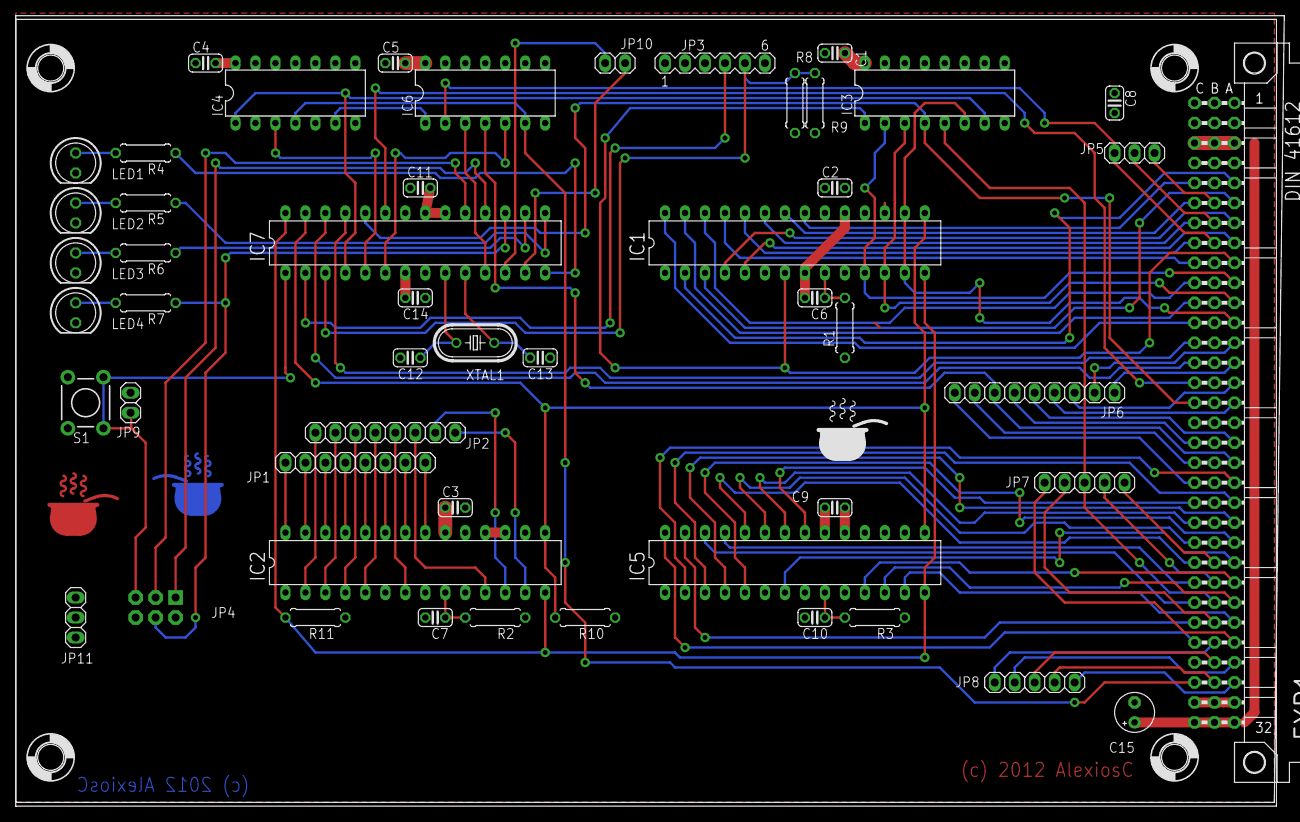
[picture p131: board cft-deb-board.brd from above]

Board: 2 copper layers, 161.3 x 100.0 mm, 58 parts (1 on the bottom side), 106 nets.
