alexiosc/cft/eagle/CFT-PB1-revG-TSSOP.brd

## EAGLE design eagle/CFT-PB1-revG-TSSOP.brd (2019-05-06)

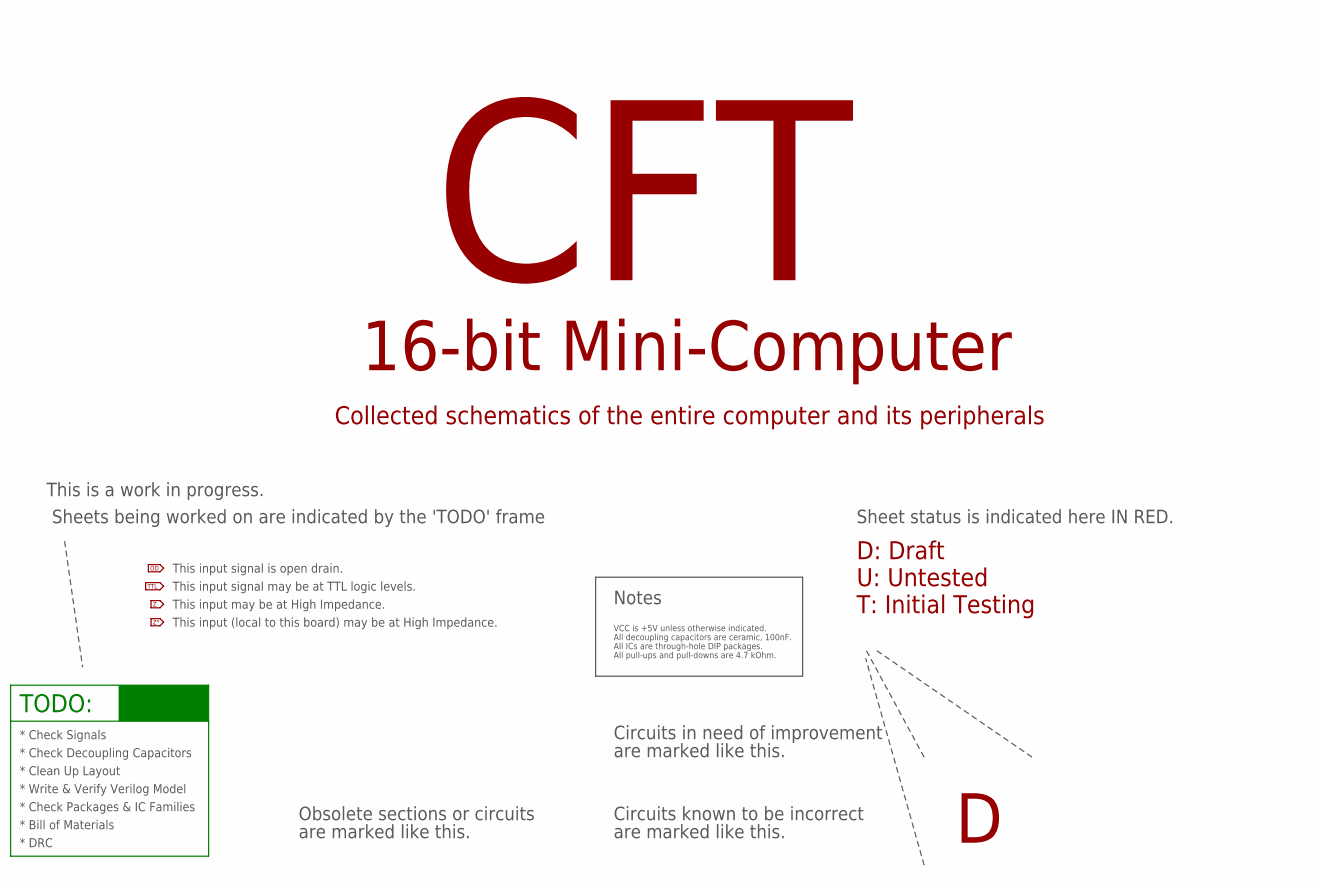
[picture p132: schematic CFT-PB1-revG-TSSOP.sch, sheet 1]

Notes on the sheet:
TODO:
* Check Signals
* Check Decoupling Capacitors
* Clean Up Layout
* Write & Verify Verilog Model
* Check Packages & IC Families
* Bill of Materials
* DRC
CFT
16-bit Mini-Computer
Collected schematics of the entire computer and its peripherals
This is a work in progress.
Sheet status is indicated here IN RED.
D: Draft
U: Untested
T: Initial Testing
Sheets being worked on are indicated by the 'TODO' frame
VCC is +5V unless otherwise indicated.
Notes
All decoupling capacitors are ceramic, 100nF.
All ICs are through-hole DIP packages.
Circuits known to be incorrect
are marked like this.
Circuits in need of improvement
All pull-ups and pull-downs are 4.7 kOhm.
Obsolete sections or circuits
This input signal is open drain.
This input signal may be at TTL logic levels.
This input may be at High Impedance.
This input (local to this board) may be at High Impedance.

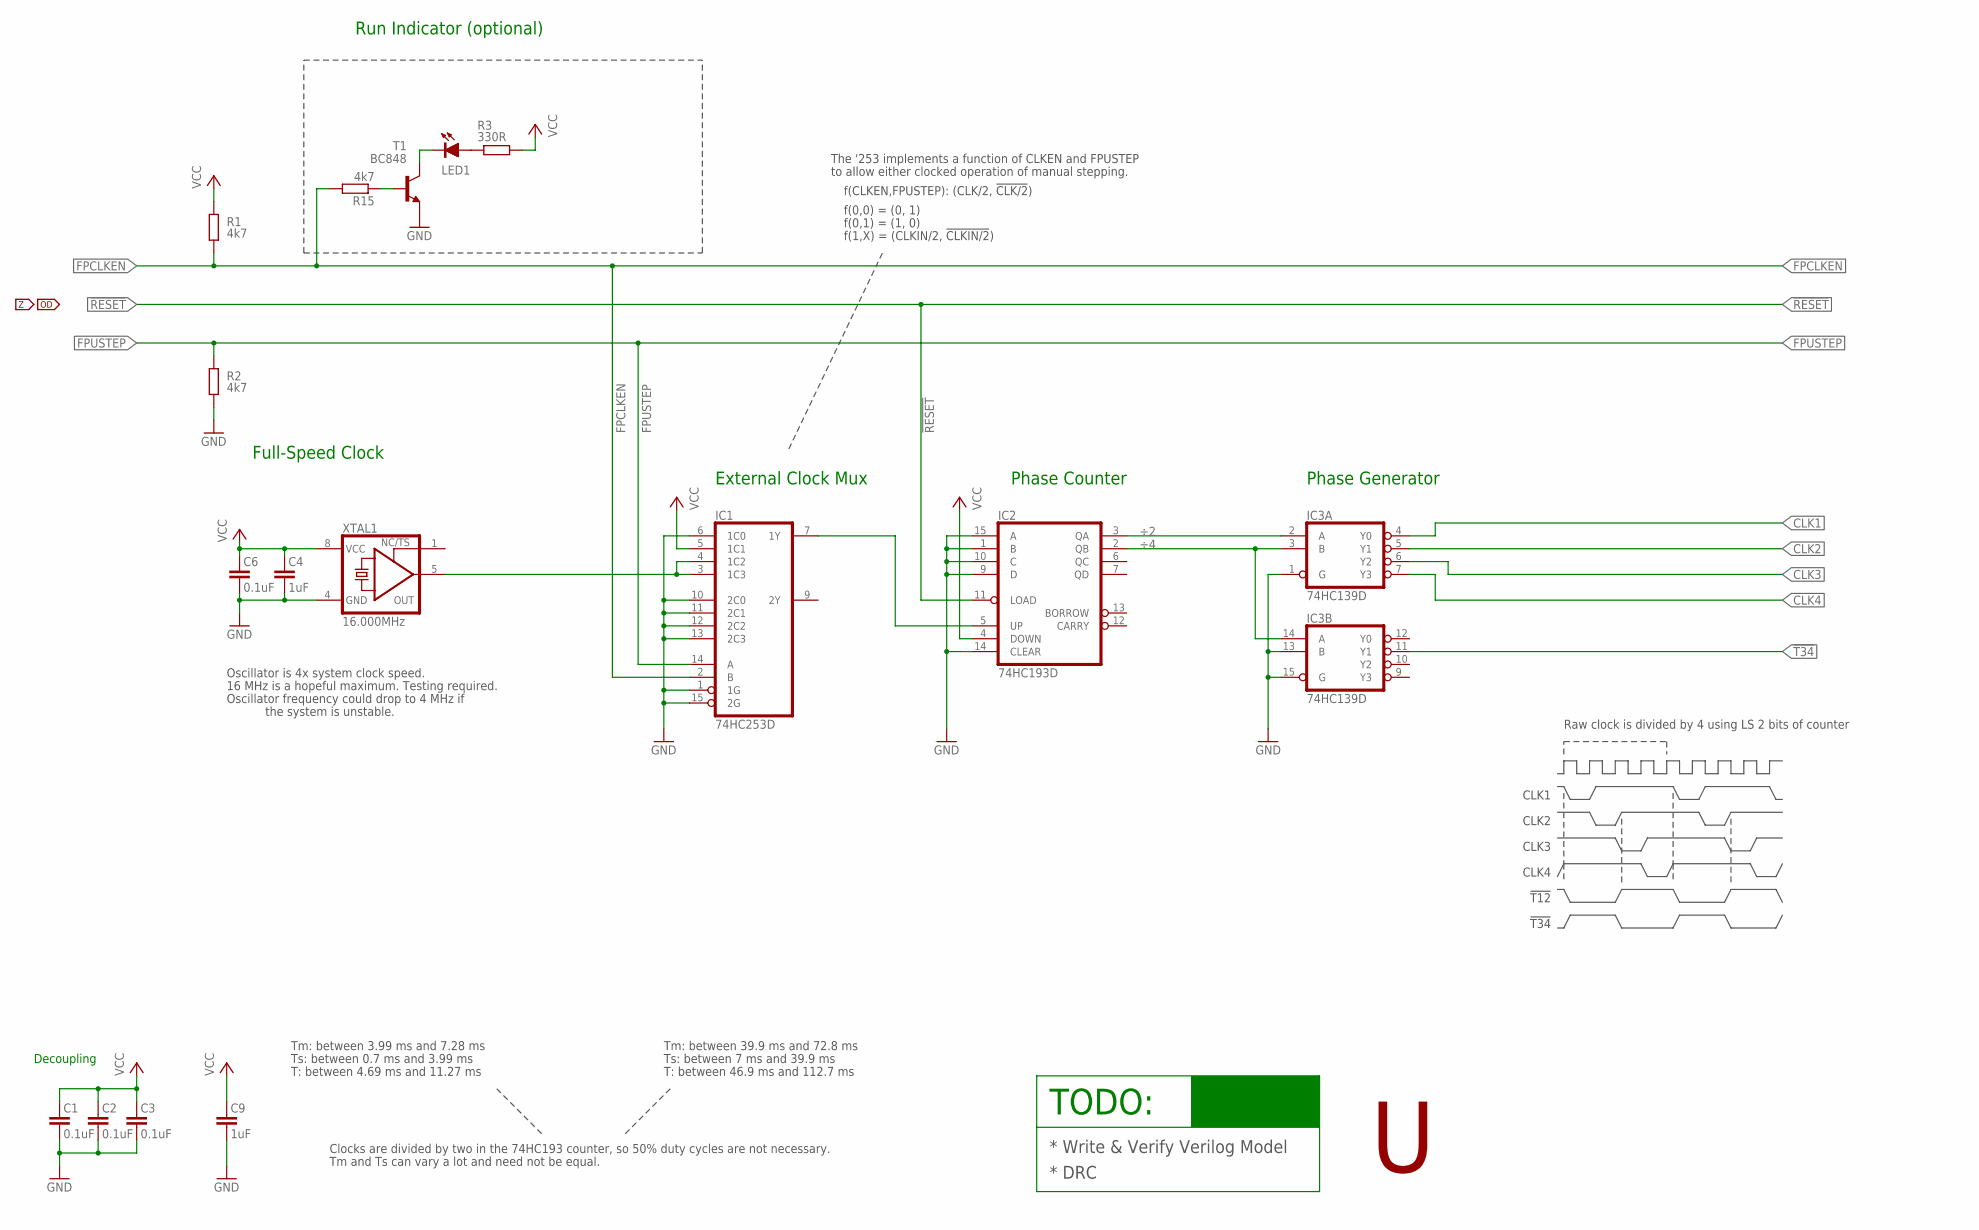
[picture p133: schematic CFT-PB1-revG-TSSOP.sch, sheet 2]

Parts:
C1, C2, C3, C6: 0.1uF; C0805K
C4, C9: 1uF; C0805K
IC1: 74HC253D; SO16
IC2: 74HC193D; SO16D
IC3: 74HC139D; SO16
LED1: LED-5MM-GREEN; CHIPLED_0805
R1, R2, R15: 4k7; R0805
R3: 330R; R0805
T1: BC848; SOT23
XTAL1: 16.000MHz; DIL08S-SOCKET

Connections:
!RESET: IC2.11 (LOAD); also elsewhere on the board
!T34: IC3.11 (Y1); also elsewhere on the board
CLK1: IC3.4 (Y0); also elsewhere on the board
CLK2: IC3.5 (Y1); also elsewhere on the board
CLK3: IC3.6 (Y2); also elsewhere on the board
CLK4: IC3.7 (Y3); also elsewhere on the board
CLKIN: IC1.7 (1Y), IC2.5 (UP)
FASTCLK: IC1.3 (1C3), IC1.4 (1C2), XTAL1.5 (OUT)
FPCLKEN: IC1.2 (B), R1.1, R15.2; also elsewhere on the board
FPUSTEP: IC1.14 (A), R2.2; also elsewhere on the board
GND: C1.1, C2.1, C3.1, C4.1, C6.1, C9.1, IC1.1 (1G), IC1.6 (1C0), IC1.8 (GND), IC1.10 (2C0), IC1.11 (2C1), IC1.12 (2C2), IC1.13 (2C3), IC1.15 (2G), IC2.1 (B), IC2.8 (GND), IC2.9 (D), IC2.10 (C), IC2.14 (CLEAR), IC2.15 (A), IC3.1 (G), IC3.8 (GND), IC3.13 (B), IC3.15 (G), R2.1, T1.2 (E), XTAL1.4 (GND); also elsewhere on the board
unnamed: R15.1, T1.1 (B)
unnamed: LED1.C, T1.3 (C)
unnamed: LED1.A, R3.2
VCC: C1.2, C2.2, C3.2, C4.2, C6.2, C9.2, IC1.5 (1C1), IC1.16 (VCC), IC2.4 (DOWN), IC2.16 (VCC), IC3.16 (VCC), R1.2, R3.1, XTAL1.8 (VCC); also elsewhere on the board
÷2: IC2.3 (QA), IC3.2 (A)
÷4: IC2.2 (QB), IC3.3 (B), IC3.14 (A)

Notes on the sheet:
Run Indicator (optional)
Decoupling
TODO:
* Write & Verify Verilog Model
* DRC
f(CLKEN,FPUSTEP): (CLK/2, !CLK/2!)
f(0,0) = (0, 1)
f(0,1) = (1, 0)
f(1,X) = (CLKIN/2, !CLKIN/2!)
The '253 implements a function of CLKEN and FPUSTEP
to allow either clocked operation of manual stepping.
Raw clock is divided by 4 using LS 2 bits of counter
CLK1
CLK2
CLK3
CLK4
!T12
!T34
Tm: between 3.99 ms and 7.28 ms
Ts: between 0.7 ms and 3.99 ms
T: between 4.69 ms and 11.27 ms
Tm: between 39.9 ms and 72.8 ms
Ts: between 7 ms and 39.9 ms
T: between 46.9 ms and 112.7 ms
Clocks are divided by two in the 74HC193 counter, so 50% duty cycles are not necessary.
Tm and Ts can vary a lot and need not be equal.
External Clock Mux
Phase Counter
Phase Generator
Oscillator is 4x system clock speed.
16 MHz is a hopeful maximum. Testing required.
Oscillator frequency could drop to 4 MHz if
the system is unstable.
Full-Speed Clock

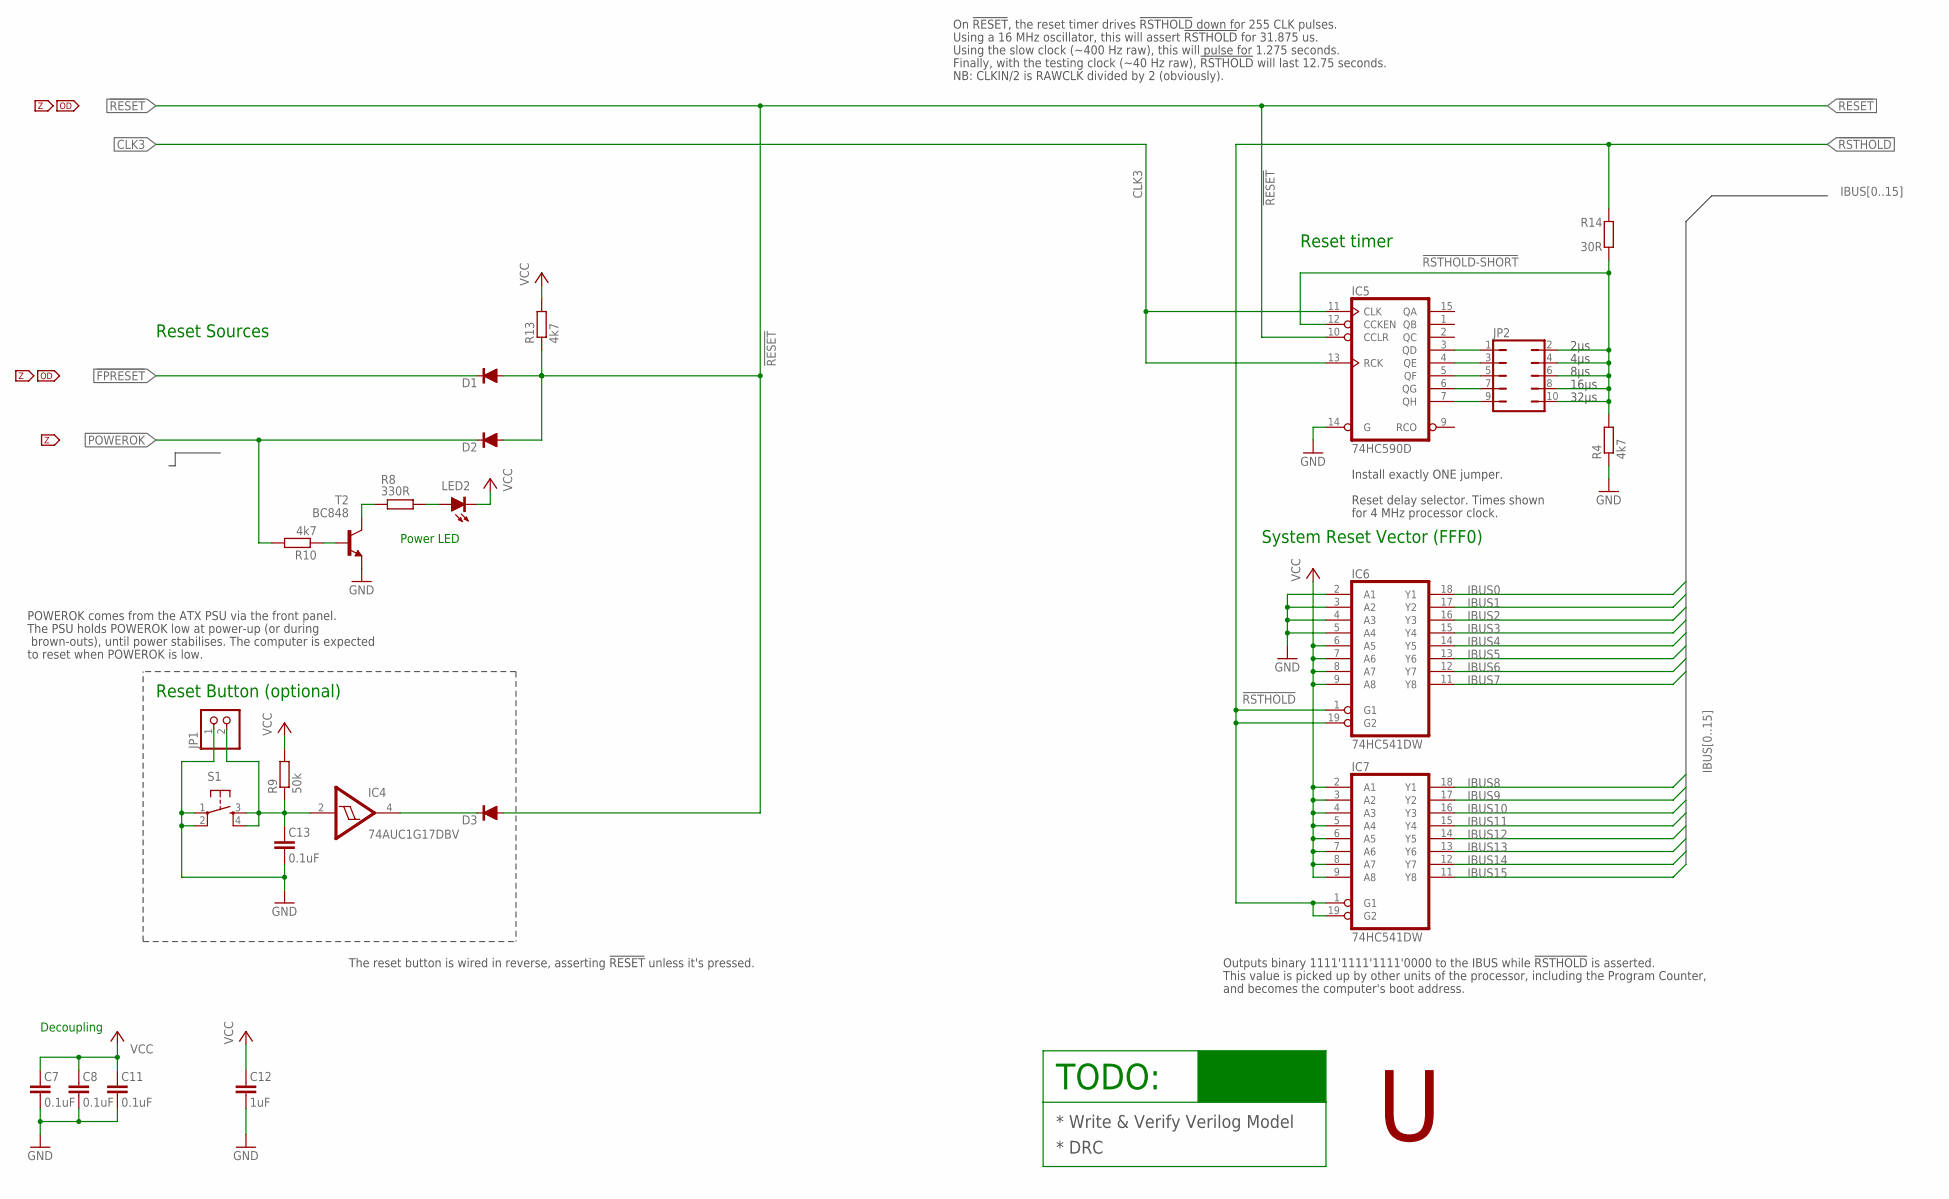
[picture p134: schematic CFT-PB1-revG-TSSOP.sch, sheet 3]

Parts:
C7, C8, C11, C13: 0.1uF; C0805K
C12: 1uF; C0805K
D1, D2, D3: DIODE-SOD123; SOD123
IC4: 74AUC1G17DBV; SOT23-5
IC5: 74HC590D; SO16
IC6, IC7: 74HC541DW; SO20W
JP1: PINHD-1X2; 1X02
JP2: JP5Q
LED2: LED-5MM-GREEN; CHIPLED_0805
R4, R10, R13: 4k7; R0805
R8: 330R; R0805
R9: 50k; R0805
R14: 30R; R0805
S1: TAC_SWITCHPTH; TACTILE-PTH
T2: BC848; SOT23

Connections:
!FPRESET: D1.C; also elsewhere on the board
!RESET: D1.A, D2.A, D3.A, IC5.10 (CCLR), R13.1; also elsewhere on the board
!RSTHOLD: IC6.1 (G1), IC6.19 (G2), IC7.1 (G1), IC7.19 (G2), R14.1; also elsewhere on the board
!RSTHOLD-SHORT: IC5.12 (CCKEN), JP2.2, JP2.4, JP2.6, JP2.8, JP2.10, R4.2, R14.2
CLK3: IC5.11 (CLK), IC5.13 (RCK); also elsewhere on the board
GND: C7.1, C8.1, C11.1, C12.1, C13.1, IC4.3 (GND), IC5.8 (GND), IC5.14 (G), IC6.2 (A1), IC6.3 (A2), IC6.4 (A3), IC6.5 (A4), IC6.10 (GND), IC7.10 (GND), JP1.1, R4.1, S1.1, S1.2, T2.2 (E); also elsewhere on the board
IBUS0: IC6.18 (Y1); also elsewhere on the board
IBUS1: IC6.17 (Y2); also elsewhere on the board
IBUS2: IC6.16 (Y3); also elsewhere on the board
IBUS3: IC6.15 (Y4); also elsewhere on the board
IBUS4: IC6.14 (Y5); also elsewhere on the board
IBUS5: IC6.13 (Y6); also elsewhere on the board
IBUS6: IC6.12 (Y7); also elsewhere on the board
IBUS7: IC6.11 (Y8); also elsewhere on the board
IBUS8: IC7.18 (Y1); also elsewhere on the board
IBUS9: IC7.17 (Y2); also elsewhere on the board
IBUS10: IC7.16 (Y3); also elsewhere on the board
IBUS11: IC7.15 (Y4); also elsewhere on the board
IBUS12: IC7.14 (Y5); also elsewhere on the board
IBUS13: IC7.13 (Y6); also elsewhere on the board
IBUS14: IC7.12 (Y7); also elsewhere on the board
IBUS15: IC7.11 (Y8); also elsewhere on the board
unnamed: D3.C, IC4.4 (O)
unnamed: R10.1, T2.1 (B)
unnamed: R8.2, T2.3 (C)
unnamed: C13.2, IC4.2 (I), JP1.2, R9.1, S1.3, S1.4
unnamed: IC5.7 (QH), JP2.9
unnamed: IC5.6 (QG), JP2.7
unnamed: IC5.5 (QF), JP2.5
unnamed: IC5.4 (QE), JP2.3
unnamed: IC5.3 (QD), JP2.1
POWERLED: LED2.A, R8.1
POWEROK: D2.C, R10.2; also elsewhere on the board
VCC: C7.2, C8.2, C11.2, C12.2, IC4.5 (VCC), IC5.16 (VCC), IC6.6 (A5), IC6.7 (A6), IC6.8 (A7), IC6.9 (A8), IC6.20 (VCC), IC7.2 (A1), IC7.3 (A2), IC7.4 (A3), IC7.5 (A4), IC7.6 (A5), IC7.7 (A6), IC7.8 (A7), IC7.9 (A8), IC7.20 (VCC), LED2.C, R9.2, R13.2; also elsewhere on the board

Notes on the sheet:
System Reset Vector (FFF0)
Power LED
Reset Button (optional)
Reset Sources
Reset timer
On !RESET!, the reset timer drives !RSTHOLD! down for 255 CLK pulses.
Using a 16 MHz oscillator, this will assert !RSTHOLD! for 31.875 us.
Using the slow clock (~400 Hz raw), this will pulse for 1.275 seconds.
Finally, with the testing clock (~40 Hz raw), !RSTHOLD! will last 12.75 seconds.
NB: CLKIN/2 is RAWCLK divided by 2 (obviously).
Outputs binary 1111'1111'1111'0000 to the IBUS while !RSTHOLD! is asserted.
This value is picked up by other units of the processor, including the Program Counter,
and becomes the computer's boot address.
TODO:
* Write & Verify Verilog Model
* DRC
POWEROK comes from the ATX PSU via the front panel.
The PSU holds POWEROK low at power-up (or during
brown-outs), until power stabilises. The computer is expected
to reset when POWEROK is low.
Reset delay selector. Times shown
for 4 MHz processor clock.
4µs
8µs
16µs
32µs
Install exactly ONE jumper.
2µs
Decoupling
The reset button is wired in reverse, asserting !RESET! unless it's pressed.
