alexiosc/cft/eagle/CFT-PB1-revG-TSSOP.brd

## EAGLE design eagle/CFT-PB1-revG-TSSOP.brd (continued)

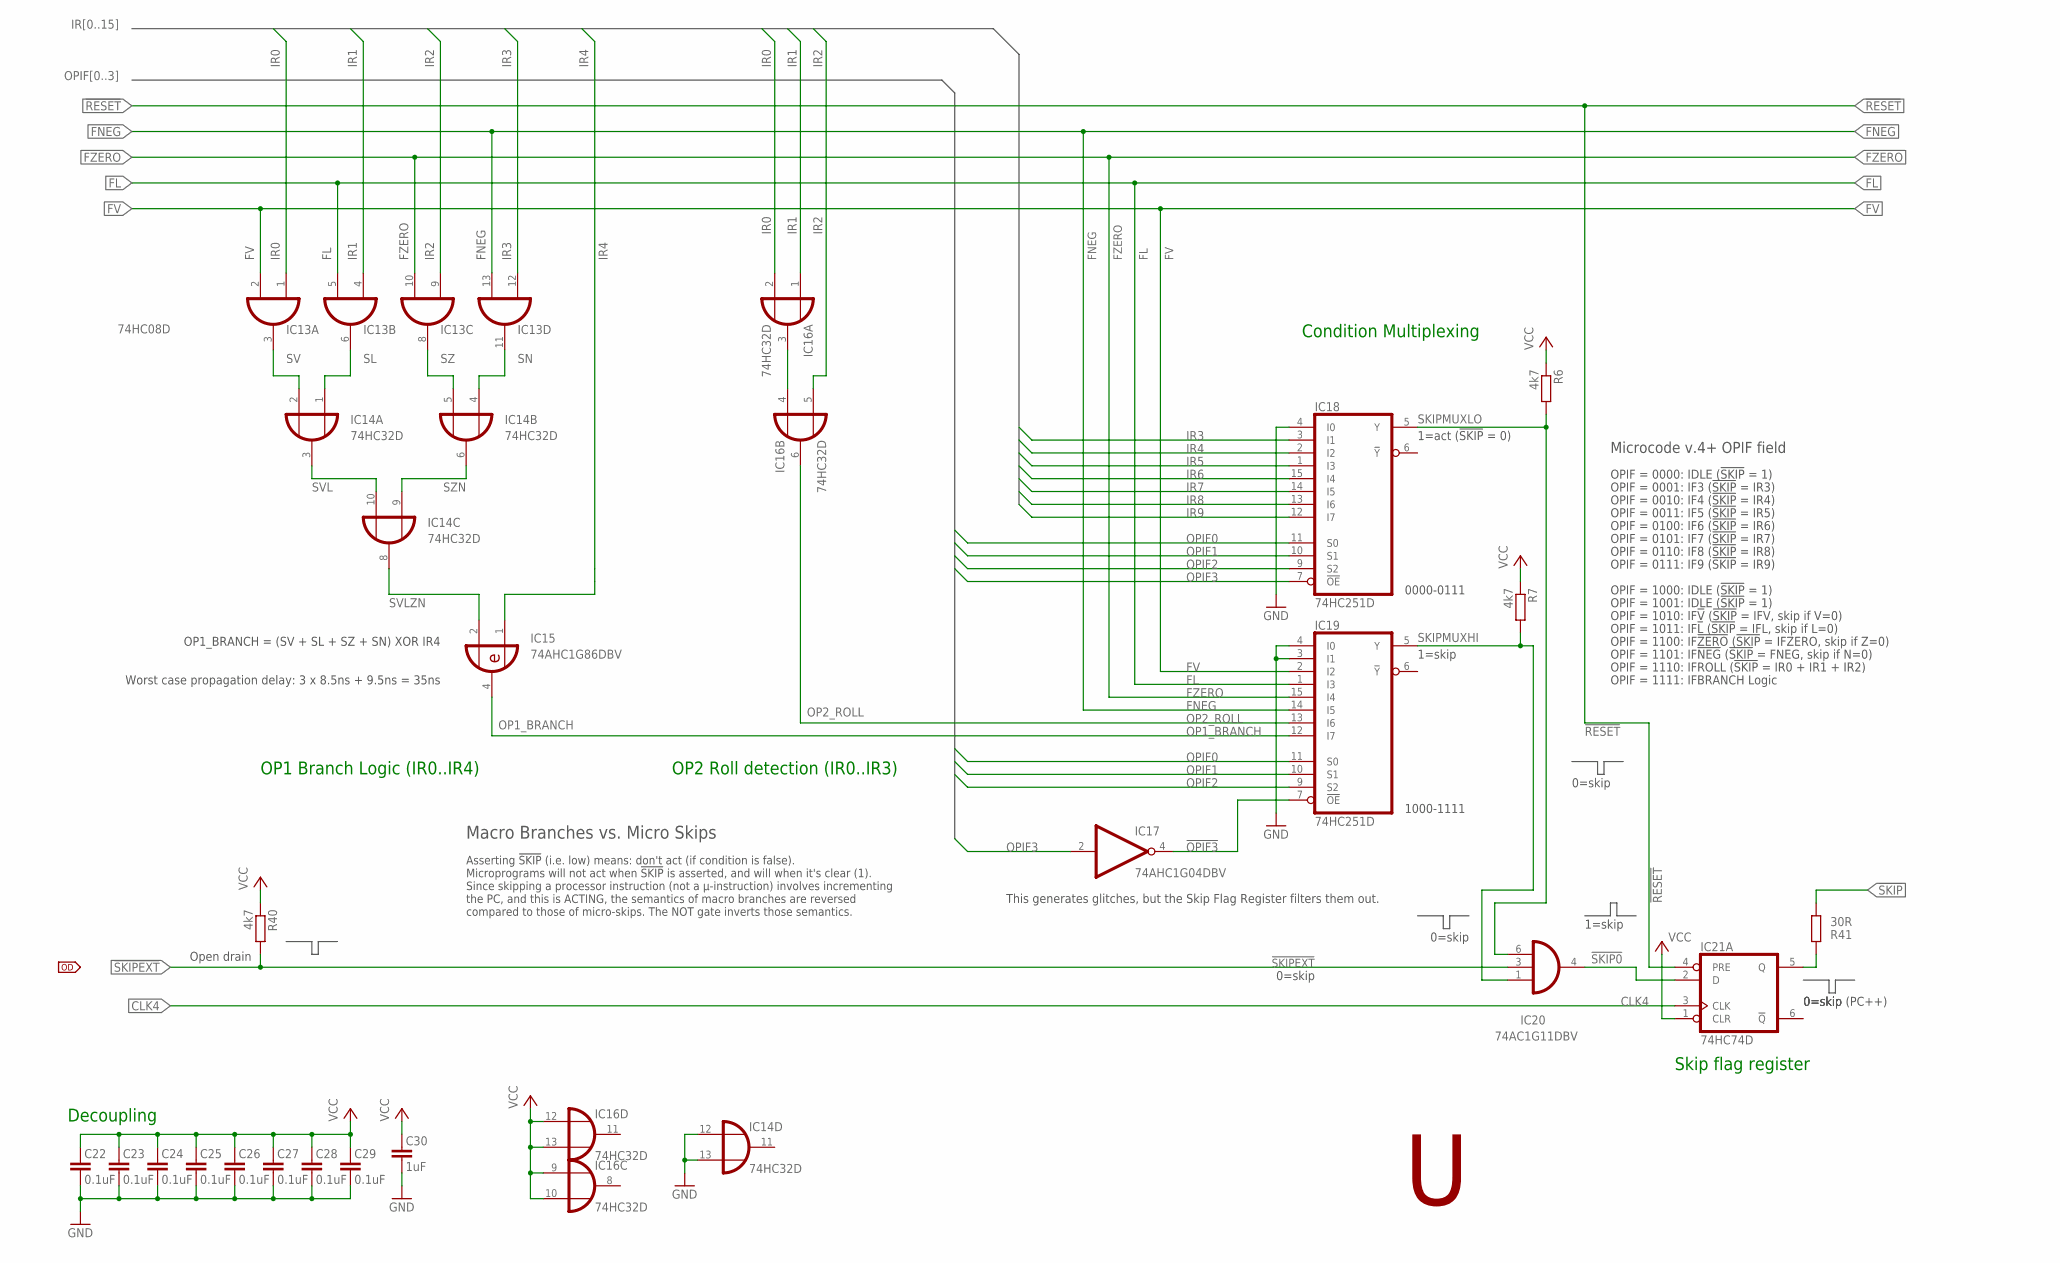
[picture p135: schematic CFT-PB1-revG-TSSOP.sch, sheet 4]

Parts:
C22, C23, C24, C25, C26, C27, C28, C29: 0.1uF; C0805K
C30: 1uF; C0805K
IC13: 74HC08D; SO14
IC14, IC16: 74HC32D; SO14
IC15: 74AHC1G86DBV; SOT23-5
IC17: 74AHC1G04DBV; SOT23-5
IC18, IC19: 74HC251D; SO16
IC20: 74AC1G11DBV; DBV_R-PDSO-G6
IC21: 74HC74D; SO14
R6, R7, R40: 4k7; R0805
R41: 30R; R0805

Connections:
!OPIF3: IC17.4 (O), IC19.7 (!OE)
!RESET: IC21.4 (PRE); also elsewhere on the board
!SKIP: R41.1; also elsewhere on the board
!SKIP0: IC20.4 (O), IC21.2 (D)
!SKIPEXT: IC20.3 (I1), R40.2; also elsewhere on the board
CLK4: IC21.3 (CLK); also elsewhere on the board
FL: IC13.5 (I1), IC19.1 (I3); also elsewhere on the board
FNEG: IC13.13 (I1), IC19.14 (I5); also elsewhere on the board
FV: IC13.2 (I1), IC19.2 (I2); also elsewhere on the board
FZERO: IC13.10 (I1), IC19.15 (I4); also elsewhere on the board
GND: C22.1, C23.1, C24.1, C25.1, C26.1, C27.1, C28.1, C29.1, C30.1, IC13.7 (GND), IC14.7 (GND), IC14.12 (I0), IC14.13 (I1), IC15.3 (GND), IC16.7 (GND), IC17.3 (GND), IC18.4 (I0), IC18.8 (GND), IC19.3 (I1), IC19.4 (I0), IC19.8 (GND), IC20.2 (GND), IC21.7 (GND); also elsewhere on the board
IR0: IC13.1 (I0), IC16.2 (I1); also elsewhere on the board
IR1: IC13.4 (I0), IC16.1 (I0); also elsewhere on the board
IR2: IC13.9 (I0), IC16.5 (I1); also elsewhere on the board
IR3: IC13.12 (I0), IC18.3 (I1); also elsewhere on the board
IR4: IC15.1 (I0), IC18.2 (I2); also elsewhere on the board
IR5: IC18.1 (I3); also elsewhere on the board
IR6: IC18.15 (I4); also elsewhere on the board
IR7: IC18.14 (I5); also elsewhere on the board
IR8: IC18.13 (I6); also elsewhere on the board
IR9: IC18.12 (I7); also elsewhere on the board
unnamed: IC16.3 (O), IC16.4 (I0)
unnamed: IC21.5 (Q), R41.2
OP1_ROLL: IC16.6 (O), IC19.13 (I6)
OP2_BRANCH: IC15.4 (O), IC19.12 (I7)
OPIF0: IC18.11 (S0), IC19.11 (S0); also elsewhere on the board
OPIF1: IC18.10 (S1), IC19.10 (S1); also elsewhere on the board
OPIF2: IC18.9 (S2), IC19.9 (S2); also elsewhere on the board
OPIF3: IC17.2 (I), IC18.7 (!OE); also elsewhere on the board
SKIPMUXHI: IC19.5 (Y), IC20.1 (I0), R7.2
SKIPMUXLO: IC18.5 (Y), IC20.6 (I2), R6.2
SL: IC13.6 (O), IC14.1 (I0)
SN: IC13.11 (O), IC14.4 (I0)
SV: IC13.3 (O), IC14.2 (I1)
SVL: IC14.3 (O), IC14.10 (I1)
SVLZN: IC14.8 (O), IC15.2 (I1)
SZ: IC13.8 (O), IC14.5 (I1)
SZN: IC14.6 (O), IC14.9 (I0)
VCC: C22.2, C23.2, C24.2, C25.2, C26.2, C27.2, C28.2, C29.2, C30.2, IC13.14 (VCC), IC14.14 (VCC), IC15.5 (VCC), IC16.9 (I0), IC16.10 (I1), IC16.12 (I0), IC16.13 (I1), IC16.14 (VCC), IC17.5 (VCC), IC18.16 (VCC), IC19.16 (VCC), IC20.5 (VCC), IC21.1 (CLR), IC21.14 (VCC), R6.1, R7.1, R40.1; also elsewhere on the board

Notes on the sheet:
OP1_BRANCH = (SV + SL + SZ + SN) XOR IR4
OPIF = 0000: IDLE (!SKIP! = 1)
OPIF = 0001: IF3 (!SKIP! = IR3)
OPIF = 0010: IF4 (!SKIP! = IR4)
OPIF = 0011: IF5 (!SKIP! = IR5)
OPIF = 0100: IF6 (!SKIP! = IR6)
OPIF = 0101: IF7 (!SKIP! = IR7)
OPIF = 0110: IF8 (!SKIP! = IR8)
OPIF = 0111: IF9 (!SKIP! = IR9)
OPIF = 1110: IFROLL (!SKIP! = IR0 + IR1 + IR2)
OPIF = 1111: IFBRANCH Logic
0000-0111
1000-1111
OPIF = 1010: IF!V! (!SKIP! = IFV, skip if V=0)
OPIF = 1011: IF!L! (!SKIP! = IFL, skip if L=0)
OPIF = 1100: IF!ZERO! (!SKIP! = IFZERO, skip if Z=0)
OPIF = 1101: IF!NEG! (!SKIP! = FNEG, skip if N=0)
Microcode v.4+ OPIF field
OP1 Branch Logic (IR0..IR4)
OP2 Roll detection (IR0..IR3)
Condition Multiplexing
Skip flag register
OPIF = 1000: IDLE (!SKIP! = 1)
OPIF = 1001: IDLE (!SKIP! = 1)
Worst case propagation delay: 3 x 8.5ns + 9.5ns = 35ns
Decoupling
This generates glitches, but the Skip Flag Register filters them out.
Open drain
1=act (!SKIP! = 0)
1=skip
0=skip
Asserting !SKIP! (i.e. low) means: don't act (if condition is false).
Microprograms will not act when !SKIP! is asserted, and will when it's clear (1).
Since skipping a processor instruction (not a µ-instruction) involves incrementing
the PC, and this is ACTING, the semantics of macro branches are reversed
compared to those of micro-skips. The NOT gate inverts those semantics.
Macro Branches vs. Micro Skips
0=skip (PC++)

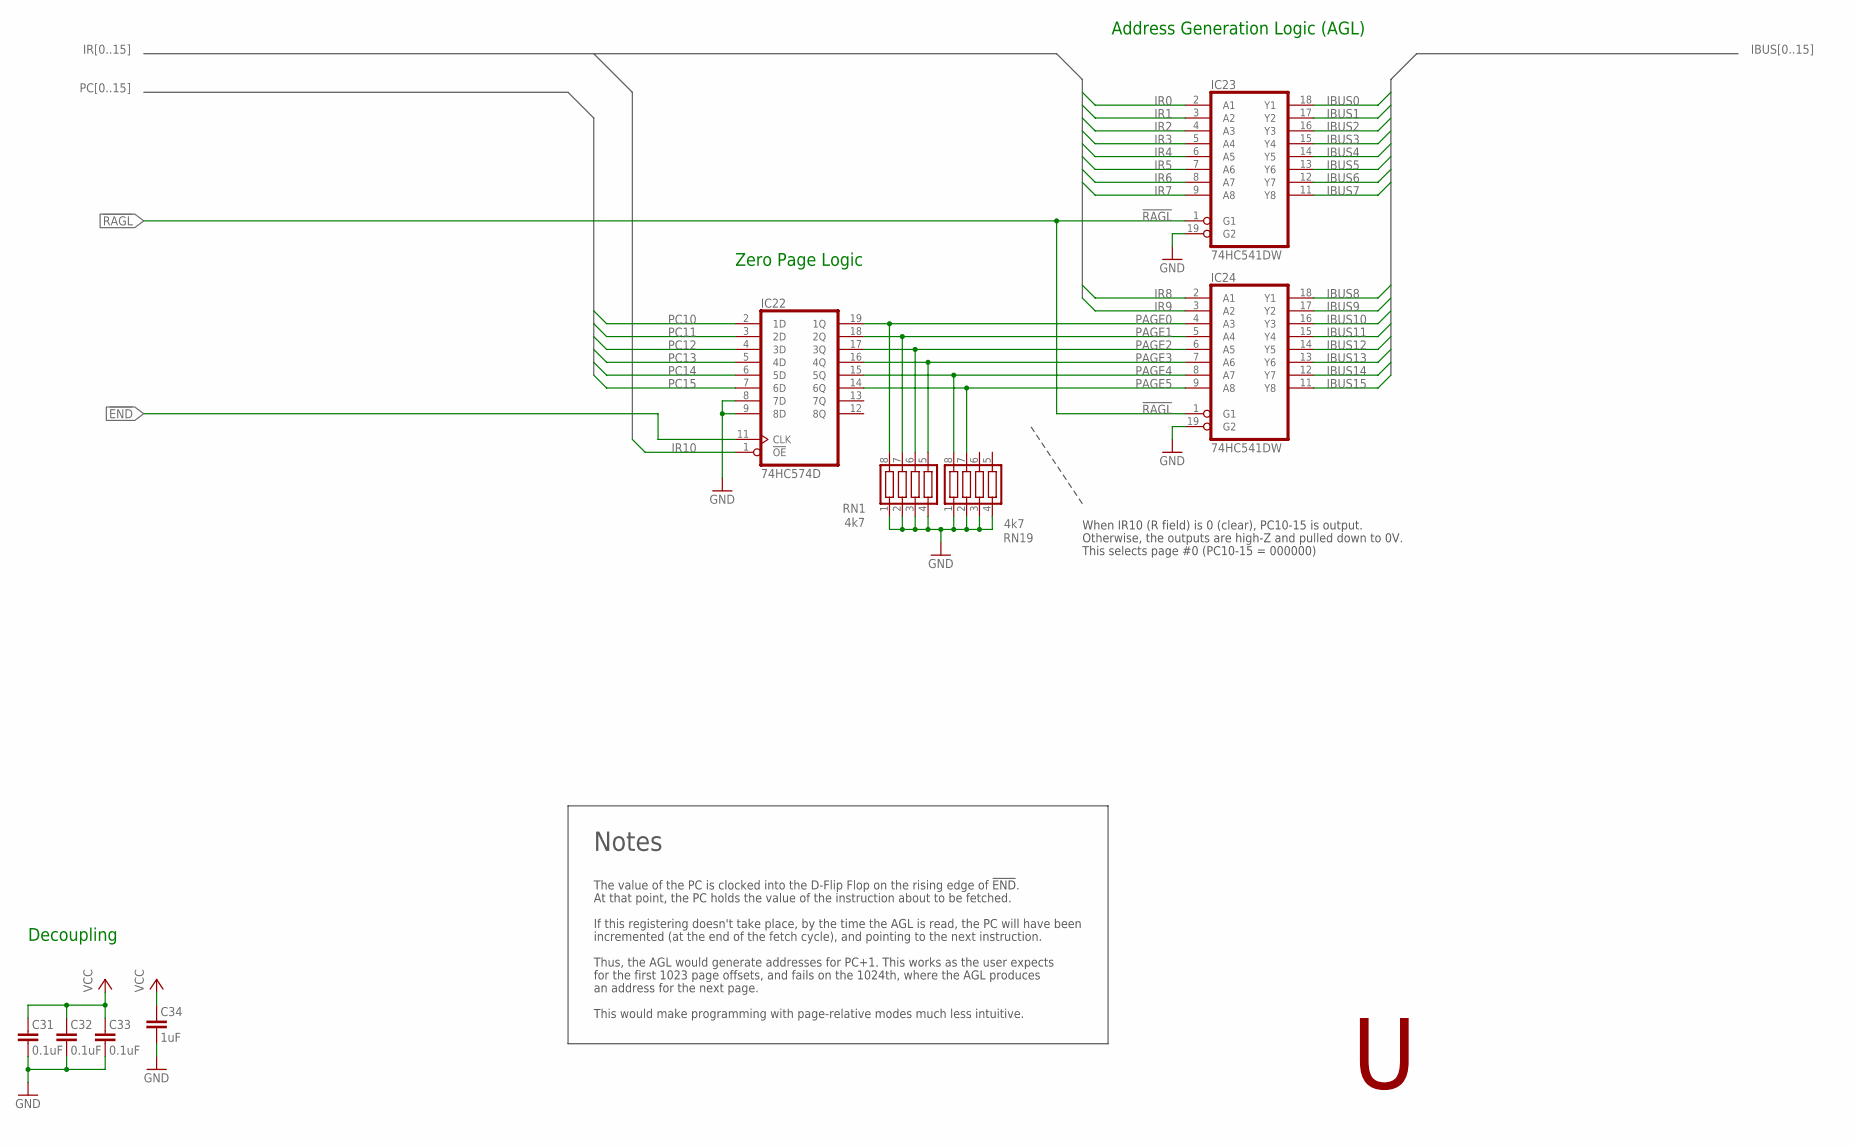
[picture p136: schematic CFT-PB1-revG-TSSOP.sch, sheet 5]

Parts:
C31, C32, C33: 0.1uF; C0805K
C34: 1uF; C0805K
IC22: 74HC574D; SO20W
IC23, IC24: 74HC541DW; SO20W
RN1, RN19: 4k7; CTS742C083

Connections:
!END: IC22.11 (CLK); also elsewhere on the board
!RAGL: IC23.1 (G1), IC24.1 (G1); also elsewhere on the board
GND: C31.1, C32.1, C33.1, C34.1, IC22.8 (7D), IC22.9 (8D), IC22.10 (GND), IC23.10 (GND), IC23.19 (G2), IC24.10 (GND), IC24.19 (G2), RN1.1, RN1.2, RN1.3, RN1.4, RN19.1, RN19.2, RN19.3, RN19.4; also elsewhere on the board
IBUS0: IC23.18 (Y1); also elsewhere on the board
IBUS1: IC23.17 (Y2); also elsewhere on the board
IBUS2: IC23.16 (Y3); also elsewhere on the board
IBUS3: IC23.15 (Y4); also elsewhere on the board
IBUS4: IC23.14 (Y5); also elsewhere on the board
IBUS5: IC23.13 (Y6); also elsewhere on the board
IBUS6: IC23.12 (Y7); also elsewhere on the board
IBUS7: IC23.11 (Y8); also elsewhere on the board
IBUS8: IC24.18 (Y1); also elsewhere on the board
IBUS9: IC24.17 (Y2); also elsewhere on the board
IBUS10: IC24.16 (Y3); also elsewhere on the board
IBUS11: IC24.15 (Y4); also elsewhere on the board
IBUS12: IC24.14 (Y5); also elsewhere on the board
IBUS13: IC24.13 (Y6); also elsewhere on the board
IBUS14: IC24.12 (Y7); also elsewhere on the board
IBUS15: IC24.11 (Y8); also elsewhere on the board
IR0: IC23.2 (A1); also elsewhere on the board
IR1: IC23.3 (A2); also elsewhere on the board
IR2: IC23.4 (A3); also elsewhere on the board
IR3: IC23.5 (A4); also elsewhere on the board
IR4: IC23.6 (A5); also elsewhere on the board
IR5: IC23.7 (A6); also elsewhere on the board
IR6: IC23.8 (A7); also elsewhere on the board
IR7: IC23.9 (A8); also elsewhere on the board
IR8: IC24.2 (A1); also elsewhere on the board
IR9: IC24.3 (A2); also elsewhere on the board
IR10: IC22.1 (!OE); also elsewhere on the board
PAGE0: IC22.19 (1Q), IC24.4 (A3), RN1.8
PAGE1: IC22.18 (2Q), IC24.5 (A4), RN1.7
PAGE2: IC22.17 (3Q), IC24.6 (A5), RN1.6
PAGE3: IC22.16 (4Q), IC24.7 (A6), RN1.5
PAGE4: IC22.15 (5Q), IC24.8 (A7), RN19.8
PAGE5: IC22.14 (6Q), IC24.9 (A8), RN19.7
PC10: IC22.2 (1D); also elsewhere on the board
PC11: IC22.3 (2D); also elsewhere on the board
PC12: IC22.4 (3D); also elsewhere on the board
PC13: IC22.5 (4D); also elsewhere on the board
PC14: IC22.6 (5D); also elsewhere on the board
PC15: IC22.7 (6D); also elsewhere on the board
VCC: C31.2, C32.2, C33.2, C34.2, IC22.20 (VCC), IC23.20 (VCC), IC24.20 (VCC); also elsewhere on the board

Notes on the sheet:
Zero Page Logic
Address Generation Logic (AGL)
When IR10 (R field) is 0 (clear), PC10-15 is output.
Otherwise, the outputs are high-Z and pulled down to 0V.
This selects page #0 (PC10-15 = 000000)
Notes
The value of the PC is clocked into the D-Flip Flop on the rising edge of !END!.
At that point, the PC holds the value of the instruction about to be fetched.
If this registering doesn't take place, by the time the AGL is read, the PC will have been
incremented (at the end of the fetch cycle), and pointing to the next instruction.
Thus, the AGL would generate addresses for PC+1. This works as the user expects
for the first 1023 page offsets, and fails on the 1024th, where the AGL produces
an address for the next page.
This would make programming with page-relative modes much less intuitive.
Decoupling

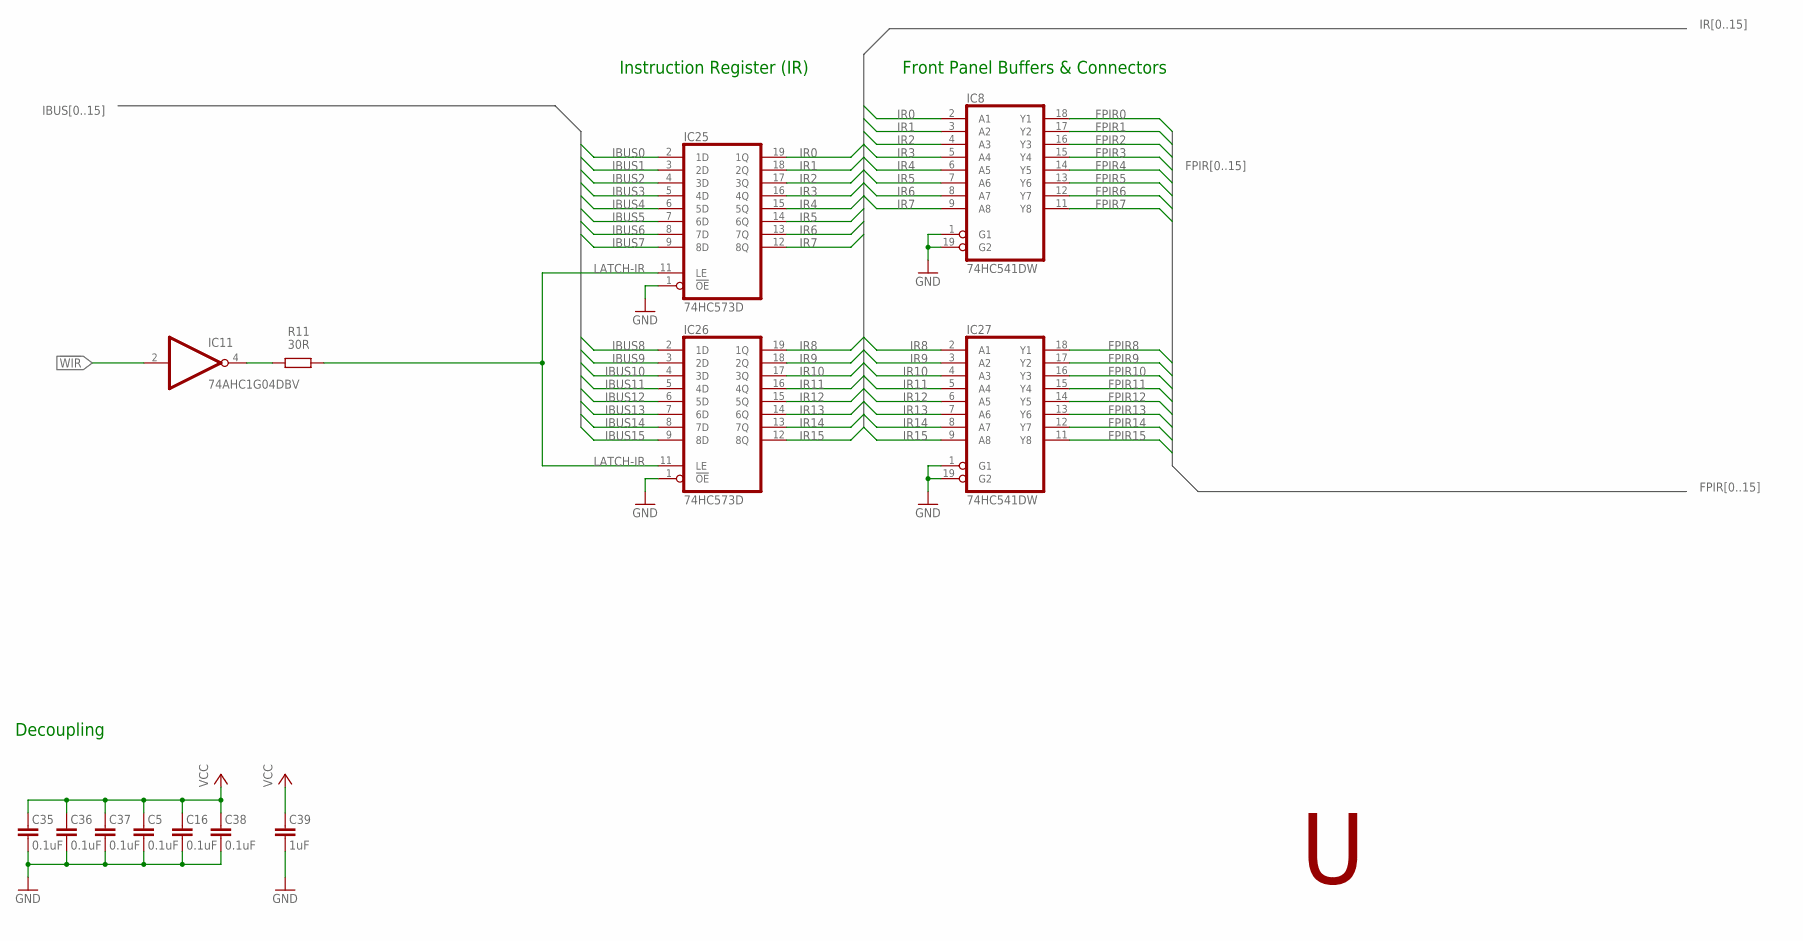
[picture p137: schematic CFT-PB1-revG-TSSOP.sch, sheet 6]

Parts:
C5, C16, C35, C36, C37, C38: 0.1uF; C0805K
C39: 1uF; C0805K
IC8, IC27: 74HC541DW; SO20W
IC11: 74AHC1G04DBV; SOT23-5
IC25, IC26: 74HC573D; SO20W
R11: 30R; R0805

Connections:
!WIR: IC11.2 (I); also elsewhere on the board
FPIR0: IC8.18 (Y1); also elsewhere on the board
FPIR1: IC8.17 (Y2); also elsewhere on the board
FPIR2: IC8.16 (Y3); also elsewhere on the board
FPIR3: IC8.15 (Y4); also elsewhere on the board
FPIR4: IC8.14 (Y5); also elsewhere on the board
FPIR5: IC8.13 (Y6); also elsewhere on the board
FPIR6: IC8.12 (Y7); also elsewhere on the board
FPIR7: IC8.11 (Y8); also elsewhere on the board
FPIR8: IC27.18 (Y1); also elsewhere on the board
FPIR9: IC27.17 (Y2); also elsewhere on the board
FPIR10: IC27.16 (Y3); also elsewhere on the board
FPIR11: IC27.15 (Y4); also elsewhere on the board
FPIR12: IC27.14 (Y5); also elsewhere on the board
FPIR13: IC27.13 (Y6); also elsewhere on the board
FPIR14: IC27.12 (Y7); also elsewhere on the board
FPIR15: IC27.11 (Y8); also elsewhere on the board
GND: C5.1, C16.1, C35.1, C36.1, C37.1, C38.1, C39.1, IC8.1 (G1), IC8.10 (GND), IC8.19 (G2), IC11.3 (GND), IC25.1 (!OE), IC25.10 (GND), IC26.1 (!OE), IC26.10 (GND), IC27.1 (G1), IC27.10 (GND), IC27.19 (G2); also elsewhere on the board
IBUS0: IC25.2 (1D); also elsewhere on the board
IBUS1: IC25.3 (2D); also elsewhere on the board
IBUS2: IC25.4 (3D); also elsewhere on the board
IBUS3: IC25.5 (4D); also elsewhere on the board
IBUS4: IC25.6 (5D); also elsewhere on the board
IBUS5: IC25.7 (6D); also elsewhere on the board
IBUS6: IC25.8 (7D); also elsewhere on the board
IBUS7: IC25.9 (8D); also elsewhere on the board
IBUS8: IC26.2 (1D); also elsewhere on the board
IBUS9: IC26.3 (2D); also elsewhere on the board
IBUS10: IC26.4 (3D); also elsewhere on the board
IBUS11: IC26.5 (4D); also elsewhere on the board
IBUS12: IC26.6 (5D); also elsewhere on the board
IBUS13: IC26.7 (6D); also elsewhere on the board
IBUS14: IC26.8 (7D); also elsewhere on the board
IBUS15: IC26.9 (8D); also elsewhere on the board
IR0: IC8.2 (A1), IC25.19 (1Q); also elsewhere on the board
IR1: IC8.3 (A2), IC25.18 (2Q); also elsewhere on the board
IR2: IC8.4 (A3), IC25.17 (3Q); also elsewhere on the board
IR3: IC8.5 (A4), IC25.16 (4Q); also elsewhere on the board
IR4: IC8.6 (A5), IC25.15 (5Q); also elsewhere on the board
IR5: IC8.7 (A6), IC25.14 (6Q); also elsewhere on the board
IR6: IC8.8 (A7), IC25.13 (7Q); also elsewhere on the board
IR7: IC8.9 (A8), IC25.12 (8Q); also elsewhere on the board
IR8: IC26.19 (1Q), IC27.2 (A1); also elsewhere on the board
IR9: IC26.18 (2Q), IC27.3 (A2); also elsewhere on the board
IR10: IC26.17 (3Q), IC27.4 (A3); also elsewhere on the board
IR11: IC26.16 (4Q), IC27.5 (A4); also elsewhere on the board
IR12: IC26.15 (5Q), IC27.6 (A5); also elsewhere on the board
IR13: IC26.14 (6Q), IC27.7 (A6); also elsewhere on the board
IR14: IC26.13 (7Q), IC27.8 (A7); also elsewhere on the board
IR15: IC26.12 (8Q), IC27.9 (A8); also elsewhere on the board
LATCH-IR: IC25.11 (LE), IC26.11 (LE), R11.2
unnamed: IC11.4 (O), R11.1
VCC: C5.2, C16.2, C35.2, C36.2, C37.2, C38.2, C39.2, IC8.20 (VCC), IC11.5 (VCC), IC25.20 (VCC), IC26.20 (VCC), IC27.20 (VCC); also elsewhere on the board

Notes on the sheet:
Instruction Register (IR)
Decoupling
Front Panel Buffers & Connectors

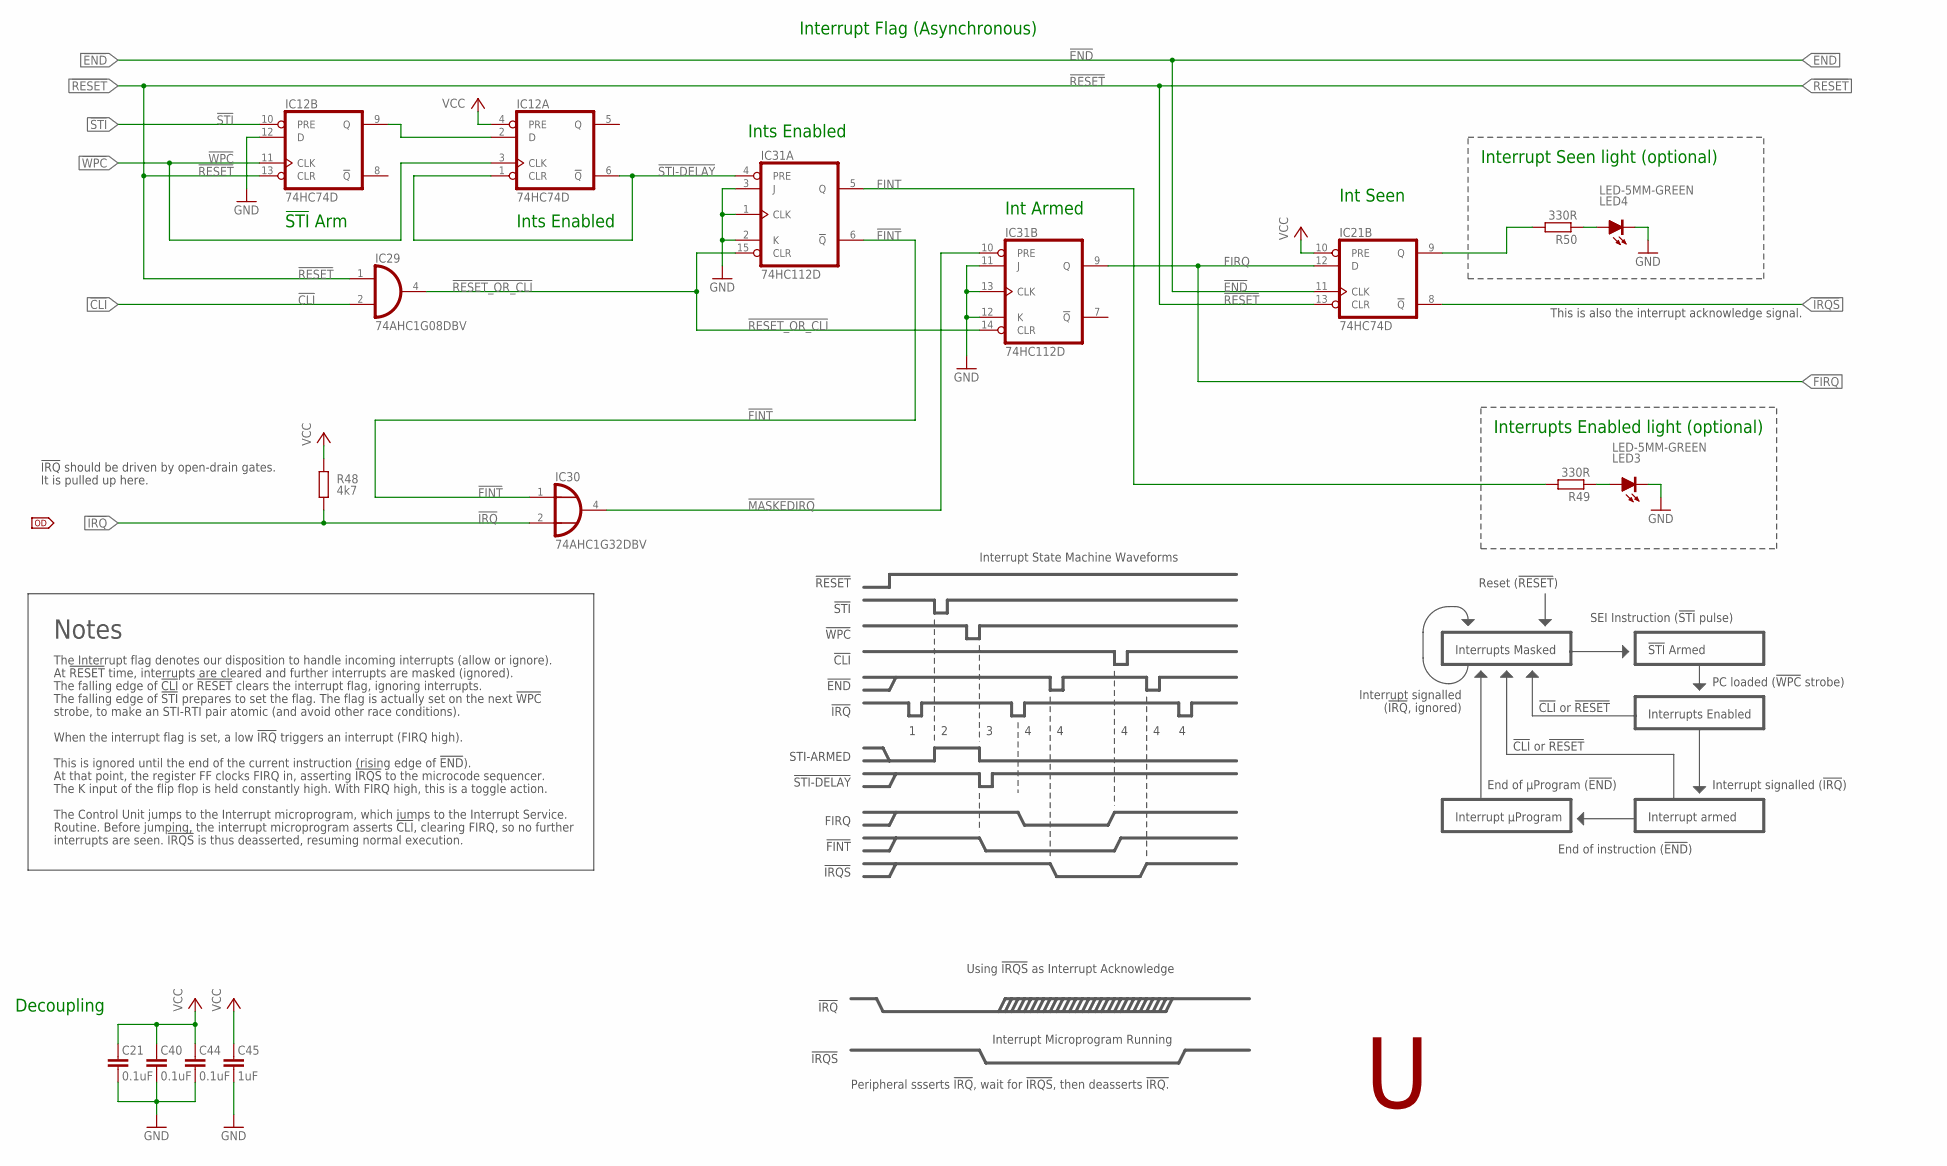
[picture p138: schematic CFT-PB1-revG-TSSOP.sch, sheet 7]

Parts:
C21, C40, C44: 0.1uF; C0805K
C45: 1uF; C0805K
IC12, IC21: 74HC74D; SO14
IC29: 74AHC1G08DBV; SOT23-5
IC30: 74AHC1G32DBV; SOT23-5
IC31: 74HC112D; SO16
LED3, LED4: LED-5MM-GREEN; CHIPLED_0805
R48: 4k7; R0805
R49, R50: 330R; R0805

Connections:
!CLI: IC29.2 (I1); also elsewhere on the board
!END: IC21.11 (CLK); also elsewhere on the board
!FINT: IC30.1 (I0), IC31.6 (!Q)
!IRQ: IC30.2 (I1), R48.1; also elsewhere on the board
!IRQS: IC21.8 (!Q); also elsewhere on the board
!MASKEDIRQ: IC30.4 (O), IC31.10 (PRE)
!RESET: IC12.13 (CLR), IC21.13 (CLR), IC29.1 (I0); also elsewhere on the board
!RESET_OR_CLI: IC29.4 (O), IC31.14 (CLR), IC31.15 (CLR)
!STI: IC12.10 (PRE); also elsewhere on the board
!STI-DELAY: IC12.1 (CLR), IC12.6 (!Q), IC31.4 (PRE)
!WPC: IC12.3 (CLK), IC12.11 (CLK); also elsewhere on the board
FINT: IC31.5 (Q), R49.2
FIRQ: IC21.12 (D), IC31.9 (Q); also elsewhere on the board
GND: C21.1, C40.1, C44.1, C45.1, IC12.7 (GND), IC12.12 (D), IC21.7 (GND), IC29.3 (GND), IC30.3 (GND), IC31.1 (CLK), IC31.2 (K), IC31.3 (J), IC31.8 (GND), IC31.11 (J), IC31.12 (K), IC31.13 (CLK), LED3.C, LED4.C; also elsewhere on the board
unnamed: IC12.2 (D), IC12.9 (Q)
unnamed: LED4.A, R50.1
unnamed: LED3.A, R49.1
unnamed: IC21.9 (Q), R50.2
VCC: C21.2, C40.2, C44.2, C45.2, IC12.4 (PRE), IC12.14 (VCC), IC21.10 (PRE), IC21.14 (VCC), IC29.5 (VCC), IC30.5 (VCC), IC31.16 (VCC), R48.2; also elsewhere on the board

Notes on the sheet:
Interrupts Enabled light (optional)
Interrupt Seen light (optional)
Interrupt Flag (Asynchronous)
!STI! Arm
Decoupling
!IRQ! should be driven by open-drain gates.
It is pulled up here.
This is also the interrupt acknowledge signal.
!IRQS
!IRQ
Using !IRQS! as Interrupt Acknowledge
Peripheral ssserts !IRQ, wait for !IRQS, then deasserts !IRQ.
Interrupt Microprogram Running
Notes
The Interrupt flag denotes our disposition to handle incoming interrupts (allow or ignore).
The falling edge of !CLI! or !RESET! clears the interrupt flag, ignoring interrupts.
The falling edge of !STI! prepares to set the flag. The flag is actually set on the next !WPC!
When the interrupt flag is set, a low !IRQ! triggers an interrupt (FIRQ high).
This is ignored until the end of the current instruction (rising edge of !END!).
At that point, the register FF clocks FIRQ in, asserting !IRQS! to the microcode sequencer.
The K input of the flip flop is held constantly high. With FIRQ high, this is a toggle action.
Routine. Before jumping, the interrupt microprogram asserts !CLI!, clearing FIRQ, so no further
interrupts are seen. !IRQS! is thus deasserted, resuming normal execution.
At !RESET! time, interrupts are cleared and further interrupts are masked (ignored).
Reset (!RESET!)
Interrupts Masked
SEI Instruction (!STI! pulse)
Interrupts Enabled
Interrupt signalled (!IRQ!)
Interrupt armed
End of instruction (!END!)
Interrupt µProgram
End of µProgram (!END!)
!STI! Armed
PC loaded (!WPC! strobe)
Interrupt signalled
(!IRQ!, ignored)
!STI
!CLI
!FINT
!RESET
Interrupt State Machine Waveforms
!WPC
STI-ARMED
!STI-DELAY
FIRQ
!END
Ints Enabled
!CLI! or !RESET!
Int Armed
Int Seen
strobe, to make an STI-RTI pair atomic (and avoid other race conditions).
The Control Unit jumps to the Interrupt microprogram, which jumps to the Interrupt Service.

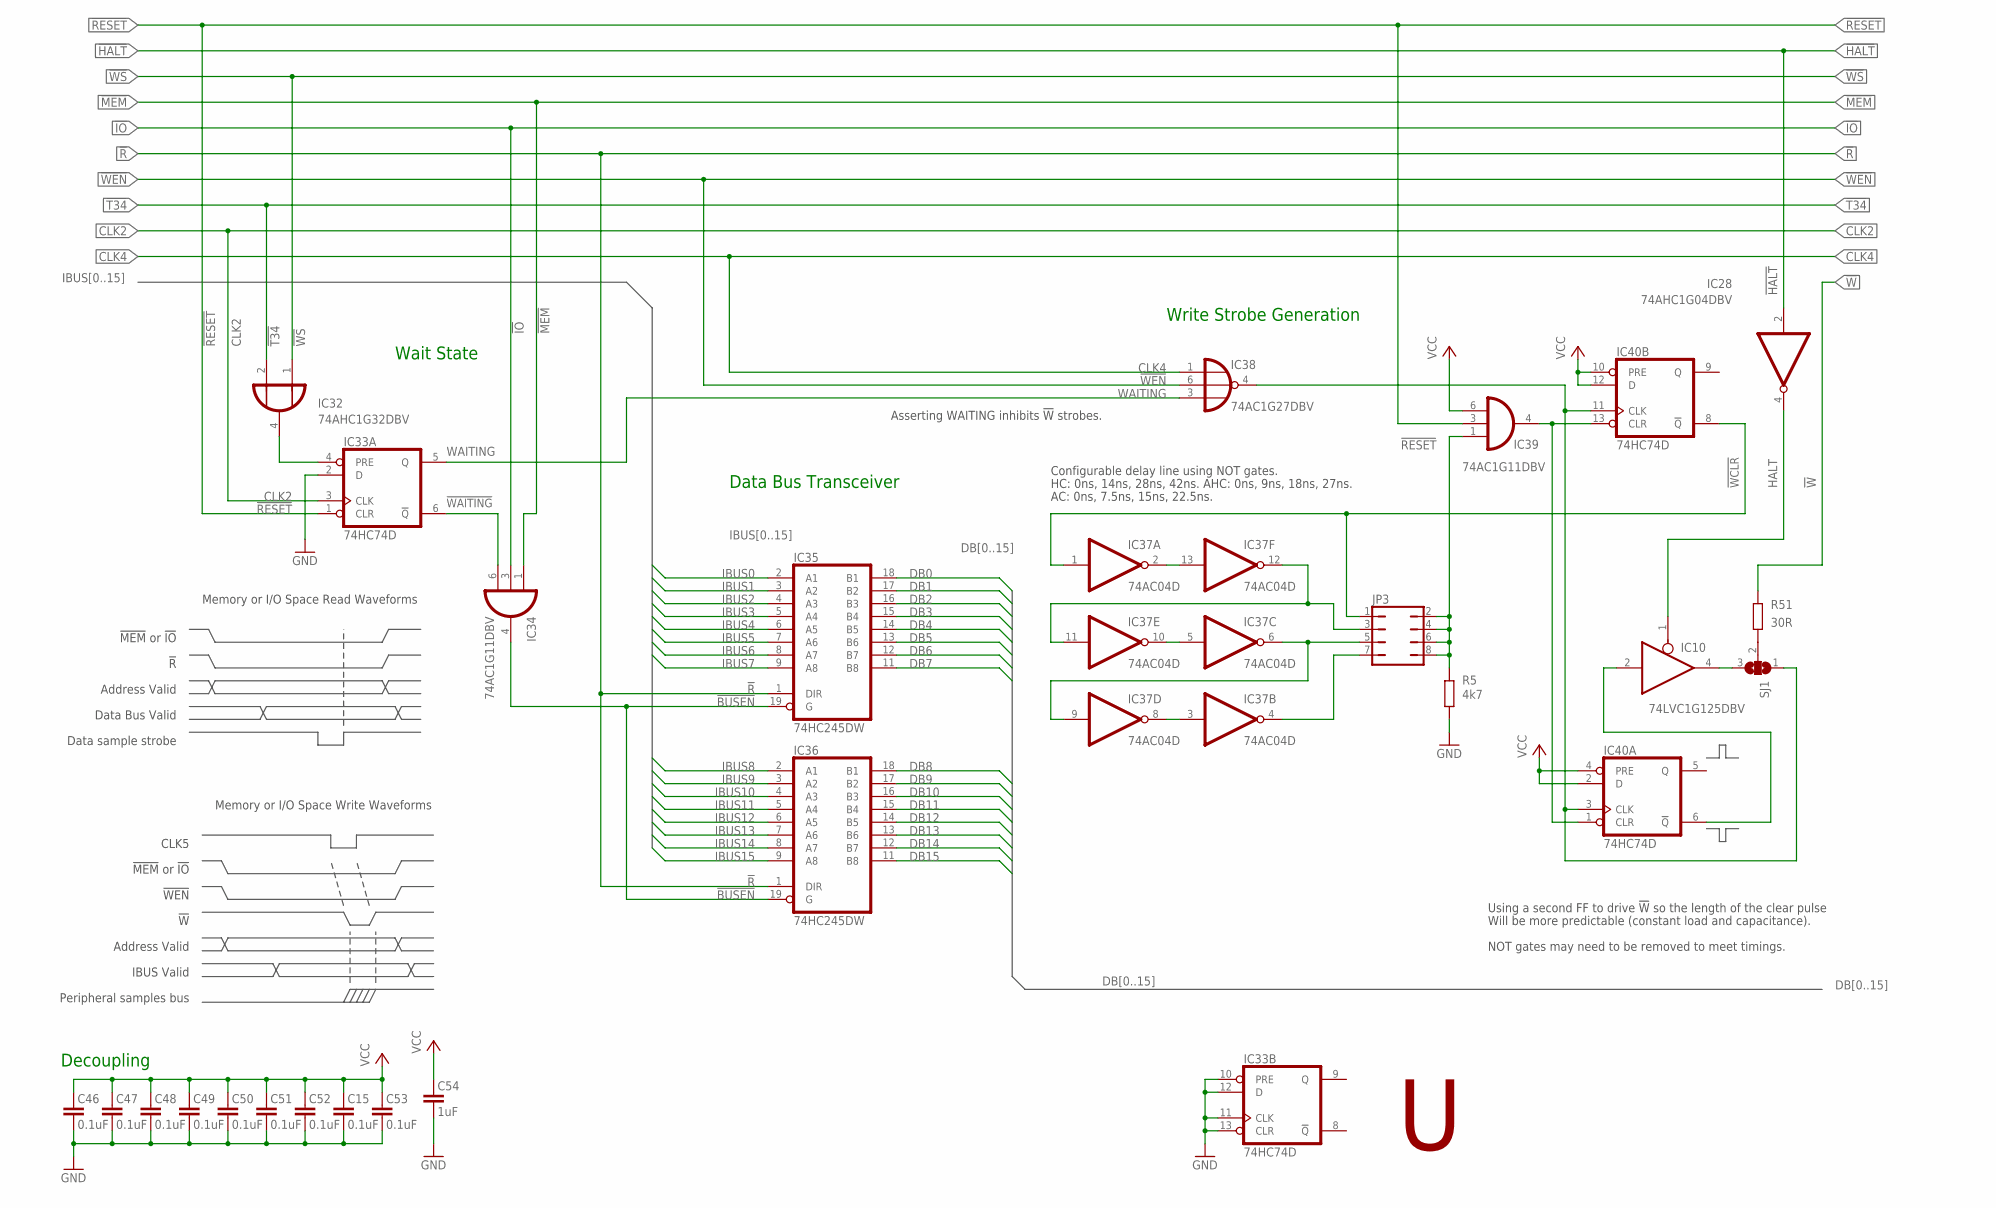
[picture p139: schematic CFT-PB1-revG-TSSOP.sch, sheet 8]

Parts:
C15, C46, C47, C48, C49, C50, C51, C52, C53: 0.1uF; C0805K
C54: 1uF; C0805K
IC10: 74LVC1G125DBV; SOT23-5
IC28: 74AHC1G04DBV; SOT23-5
IC32: 74AHC1G32DBV; SOT23-5
IC33, IC40: 74HC74D; SO14
IC34, IC39: 74AC1G11DBV; DBV_R-PDSO-G6
IC35, IC36: 74HC245DW; SO20W
IC37: 74AC04D; SO14
IC38: 74AC1G27DBV; DBV_R-PDSO-G6
JP3: JP4Q
R5: 4k7; R0805
R51: 30R; R0805
SJ1: SJ2W; SJ_2

Connections:
!BUSEN: IC34.4 (O), IC35.19 (G), IC36.19 (G)
!HALT: IC28.2 (I); also elsewhere on the board
!IO: IC34.3 (I1); also elsewhere on the board
!MEM: IC34.1 (I0); also elsewhere on the board
!R: IC35.1 (DIR), IC36.1 (DIR); also elsewhere on the board
!RESET: IC33.1 (CLR), IC39.3 (I1); also elsewhere on the board
!T34: IC32.2 (I1); also elsewhere on the board
!W: R51.1; also elsewhere on the board
!WAITING: IC33.6 (!Q), IC34.6 (I2)
!WCLR: IC37.1 (I), IC40.8 (!Q), JP3.1
!WEN: IC38.6 (I1); also elsewhere on the board
!WS: IC32.1 (I0); also elsewhere on the board
CLK2: IC33.3 (CLK); also elsewhere on the board
CLK4: IC38.1 (I0); also elsewhere on the board
DB0: IC35.18 (B1); also elsewhere on the board
DB1: IC35.17 (B2); also elsewhere on the board
DB2: IC35.16 (B3); also elsewhere on the board
DB3: IC35.15 (B4); also elsewhere on the board
DB4: IC35.14 (B5); also elsewhere on the board
DB5: IC35.13 (B6); also elsewhere on the board
DB6: IC35.12 (B7); also elsewhere on the board
DB7: IC35.11 (B8); also elsewhere on the board
DB8: IC36.18 (B1); also elsewhere on the board
DB9: IC36.17 (B2); also elsewhere on the board
DB10: IC36.16 (B3); also elsewhere on the board
DB11: IC36.15 (B4); also elsewhere on the board
DB12: IC36.14 (B5); also elsewhere on the board
DB13: IC36.13 (B6); also elsewhere on the board
DB14: IC36.12 (B7); also elsewhere on the board
DB15: IC36.11 (B8); also elsewhere on the board
GND: C15.1, C46.1, C47.1, C48.1, C49.1, C50.1, C51.1, C52.1, C53.1, C54.1, IC10.3 (GND), IC28.3 (GND), IC32.3 (GND), IC33.2 (D), IC33.7 (GND), IC33.10 (PRE), IC33.11 (CLK), IC33.12 (D), IC33.13 (CLR), IC34.2 (GND), IC35.10 (GND), IC36.10 (GND), IC37.7 (GND), IC38.2 (GND), IC39.2 (GND), IC40.7 (GND), R5.2; also elsewhere on the board
HALT: IC10.1 (OE), IC28.4 (O)
IBUS0: IC35.2 (A1); also elsewhere on the board
IBUS1: IC35.3 (A2); also elsewhere on the board
IBUS2: IC35.4 (A3); also elsewhere on the board
IBUS3: IC35.5 (A4); also elsewhere on the board
IBUS4: IC35.6 (A5); also elsewhere on the board
IBUS5: IC35.7 (A6); also elsewhere on the board
IBUS6: IC35.8 (A7); also elsewhere on the board
IBUS7: IC35.9 (A8); also elsewhere on the board
IBUS8: IC36.2 (A1); also elsewhere on the board
IBUS9: IC36.3 (A2); also elsewhere on the board
IBUS10: IC36.4 (A3); also elsewhere on the board
IBUS11: IC36.5 (A4); also elsewhere on the board
IBUS12: IC36.6 (A5); also elsewhere on the board
IBUS13: IC36.7 (A6); also elsewhere on the board
IBUS14: IC36.8 (A7); also elsewhere on the board
IBUS15: IC36.9 (A8); also elsewhere on the board
unnamed: IC38.4 (O), IC40.3 (CLK), IC40.11 (CLK), SJ1.1
unnamed: R51.2, SJ1.2
unnamed: IC10.2 (I), IC40.6 (!Q)
unnamed: IC37.11 (I), IC37.12 (O), JP3.3
unnamed: IC37.2 (O), IC37.13 (I)
unnamed: IC37.5 (I), IC37.10 (O)
unnamed: IC37.6 (O), IC37.9 (I), JP3.5
unnamed: IC32.4 (O), IC33.4 (PRE)
unnamed: IC37.3 (I), IC37.8 (O)
unnamed: IC37.4 (O), JP3.7
unnamed: IC10.4 (O), SJ1.3
unnamed: IC39.1 (I0), JP3.2, JP3.4, JP3.6, JP3.8, R5.1
unnamed: IC39.4 (O), IC40.1 (CLR), IC40.13 (CLR)
VCC: C15.2, C46.2, C47.2, C48.2, C49.2, C50.2, C51.2, C52.2, C53.2, C54.2, IC10.5 (VCC), IC28.5 (VCC), IC32.5 (VCC), IC33.14 (VCC), IC34.5 (VCC), IC35.20 (VCC), IC36.20 (VCC), IC37.14 (VCC), IC38.5 (VCC), IC39.5 (VCC), IC39.6 (I2), IC40.2 (D), IC40.4 (PRE), IC40.10 (PRE), IC40.12 (D), IC40.14 (VCC); also elsewhere on the board
WAITING: IC33.5 (Q), IC38.3 (I2)

Notes on the sheet:
Data Bus Transceiver
Decoupling
Address Valid
!MEM! or !IO
Memory or I/O Space Read Waveforms
Data Bus Valid
Data sample strobe
Memory or I/O Space Write Waveforms
IBUS Valid
Peripheral samples bus
!WEN
CLK5
Write Strobe Generation
Wait State
Asserting WAITING inhibits !W! strobes.
Using a second FF to drive !W! so the length of the clear pulse
Will be more predictable (constant load and capacitance).
NOT gates may need to be removed to meet timings.
Configurable delay line using NOT gates.
HC: 0ns, 14ns, 28ns, 42ns. AHC: 0ns, 9ns, 18ns, 27ns.
AC: 0ns, 7.5ns, 15ns, 22.5ns.
