alexiosc/cft/eagle/CFT-PB1-revG-TSSOP.brd

## EAGLE design eagle/CFT-PB1-revG-TSSOP.brd (continued)

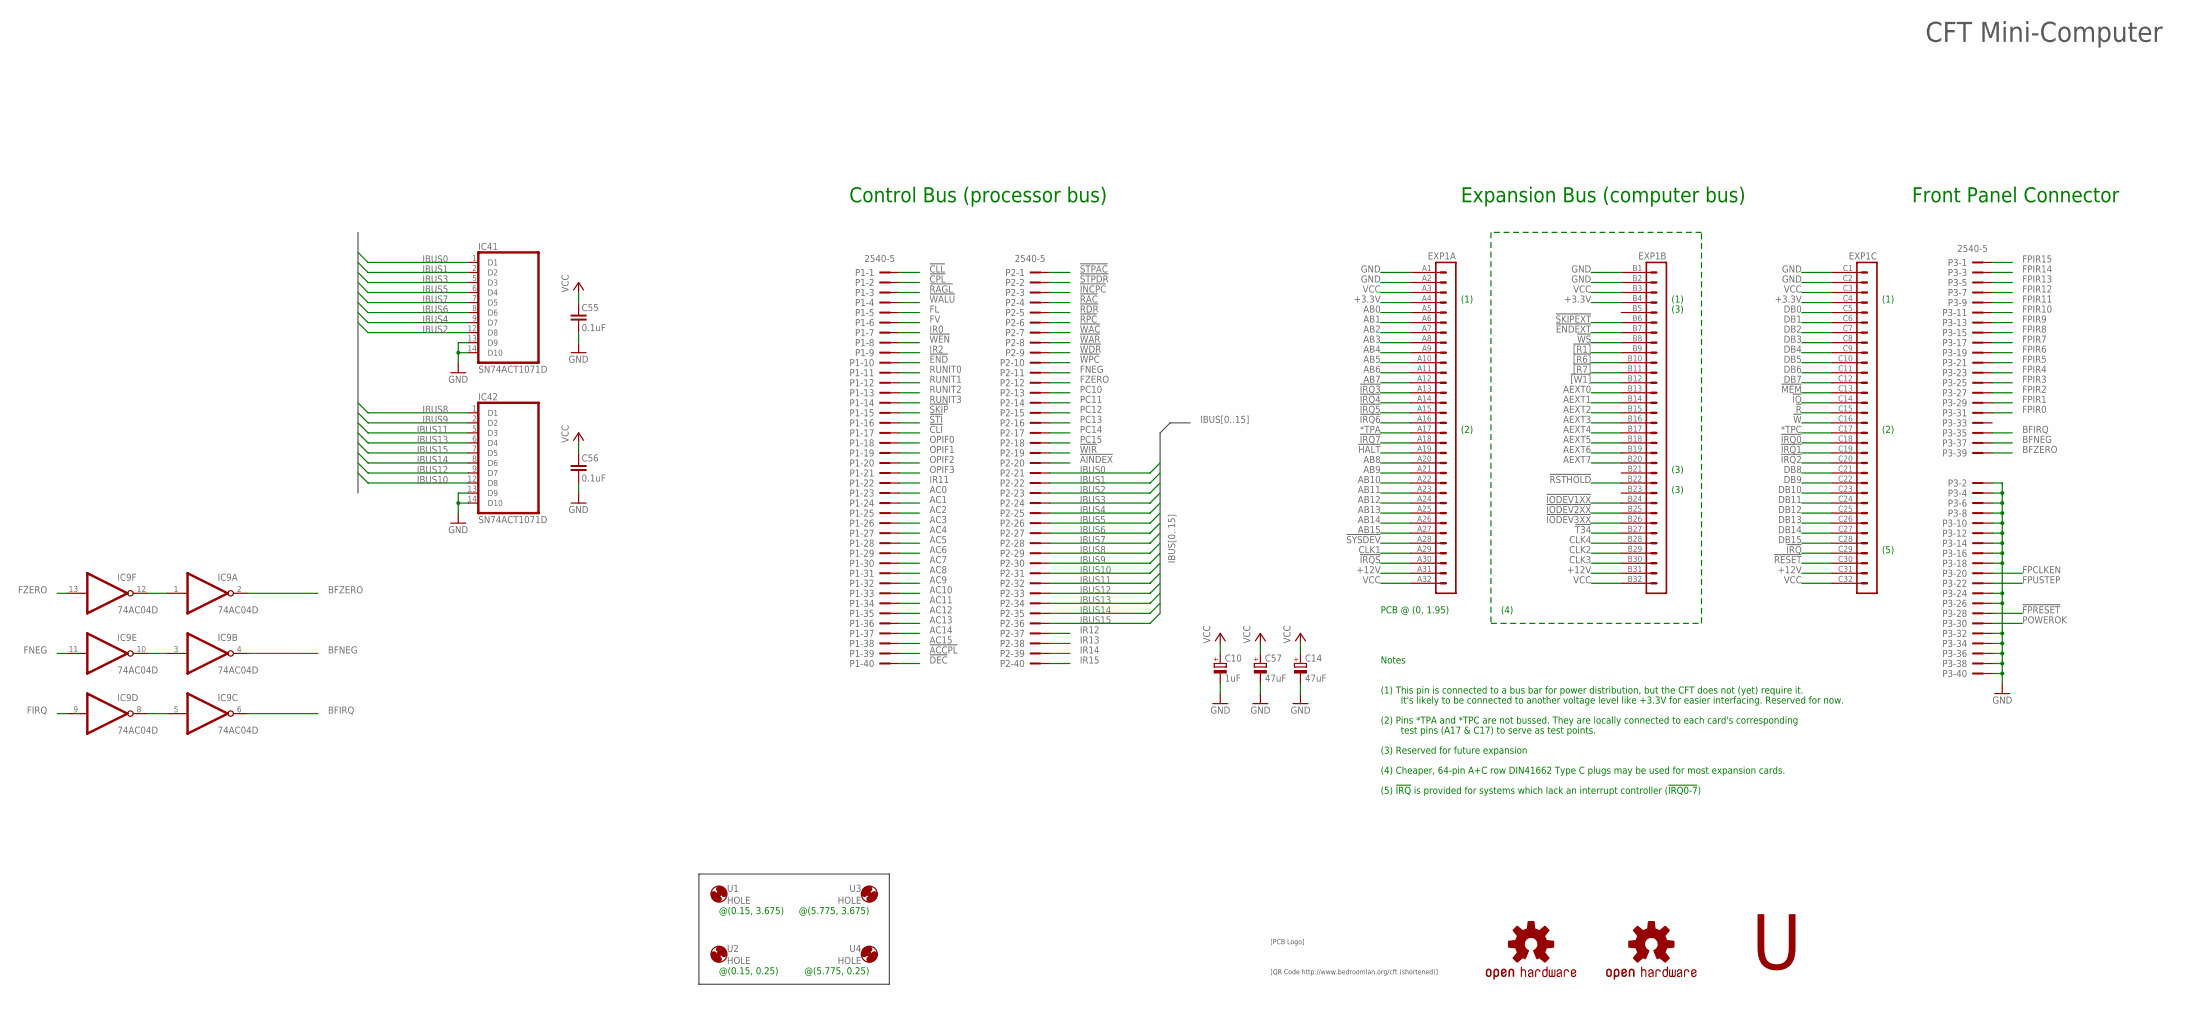
[picture p140: schematic CFT-PB1-revG-TSSOP.sch, sheet 9]

Parts:
$4_37_$1: SIGNATURESILK; SIGNATURE
$4_39_$, $4_39_$1: OSHW-LOGOL; OSHW-LOGO-L
$4_40_$: QRCODE-CFT; CFT-QRCODE
C10: 1uF; E2,5-5
C14, C57: 47uF; E2,5-5
C55, C56: 0.1uF; C0805K
EXP1: VG96-3K; VG96K
IC9: 74AC04D; SO14
IC41, IC42: SN74ACT1071D; SO14
P1, P2, P3: 2540-5; PAK100/2500-5-40
U1, U2, U3, U4: HOLE; STANDOFF_28_60

Connections:
!ACCPL: P1.39
!AINDEX: P2.20
!CLI: P1.17; also elsewhere on the board
!CLL: P1.1
!CPL: P1.2
!DEC: P1.40
!END: P1.10; also elsewhere on the board
!ENDEXT: EXP1.B7 (7)
!FPRESET: P3.28; also elsewhere on the board
!HALT: EXP1.A19 (19); also elsewhere on the board
!INCPC: P2.3
!IO: EXP1.C14 (14); also elsewhere on the board
!IODEV1XX: EXP1.B24 (24)
!IODEV2XX: EXP1.B25 (25)
!IODEV3XX: EXP1.B26 (26)
!IRQ: EXP1.C29 (29); also elsewhere on the board
!IRQ0: EXP1.C18 (18)
!IRQ1: EXP1.C19 (19)
!IRQ2: EXP1.C20 (20)
!IRQ3: EXP1.A13 (13)
!IRQ4: EXP1.A14 (14)
!IRQ5: EXP1.A15 (15)
!IRQ6: EXP1.A16 (16)
!IRQ7: EXP1.A18 (18)
!IRQS: EXP1.A30 (30); also elsewhere on the board
!MEM: EXP1.C13 (13); also elsewhere on the board
!R: EXP1.C15 (15); also elsewhere on the board
!RAC: P2.4
!RAGL: P1.3; also elsewhere on the board
!RDR: P2.5
!RESET: EXP1.C30 (30); also elsewhere on the board
!RPC: P2.6
!RSTHOLD: EXP1.B22 (22); also elsewhere on the board
!SKIP: P1.15; also elsewhere on the board
!SKIPEXT: EXP1.B6 (6); also elsewhere on the board
!STI: P1.16; also elsewhere on the board
!STPAC: P2.1
!STPDR: P2.2
!SYSDEV: EXP1.A28 (28)
!T34: EXP1.B27 (27); also elsewhere on the board
!W: EXP1.C16 (16); also elsewhere on the board
!WAC: P2.7
!WALU: P1.4
!WAR: P2.8
!WDR: P2.9
!WEN: P1.8; also elsewhere on the board
!WIR: P2.19; also elsewhere on the board
!WPC: P2.10; also elsewhere on the board
!WS: EXP1.B8 (8); also elsewhere on the board
![R1]: EXP1.B9 (9)
![R6]: EXP1.B10 (10)
![R7]: EXP1.B11 (11)
![W1]: EXP1.B12 (12)
*TPA: EXP1.A17 (17)
*TPC: EXP1.C17 (17)
+3.3V: EXP1.A4 (4), EXP1.B4 (4), EXP1.C4 (4)
+12V: EXP1.A31 (31), EXP1.B31 (31), EXP1.C31 (31)
AB0: EXP1.A5 (5)
AB1: EXP1.A6 (6)
AB2: EXP1.A7 (7)
AB3: EXP1.A8 (8)
AB4: EXP1.A9 (9)
AB5: EXP1.A10 (10)
AB6: EXP1.A11 (11)
AB7: EXP1.A12 (12)
AB8: EXP1.A20 (20)
AB9: EXP1.A21 (21)
AB10: EXP1.A22 (22)
AB11: EXP1.A23 (23)
AB12: EXP1.A24 (24)
AB13: EXP1.A25 (25)
AB14: EXP1.A26 (26)
AB15: EXP1.A27 (27)
AC0: P1.23
AC1: P1.24
AC2: P1.25
AC3: P1.26
AC4: P1.27
AC5: P1.28
AC6: P1.29
AC7: P1.30
AC8: P1.31
AC9: P1.32
AC10: P1.33
AC11: P1.34
AC12: P1.35
AC13: P1.36
AC14: P1.37
AC15: P1.38
AEXT0: EXP1.B13 (13)
AEXT1: EXP1.B14 (14)
AEXT2: EXP1.B15 (15)
AEXT3: EXP1.B16 (16)
AEXT4: EXP1.B17 (17)
AEXT5: EXP1.B18 (18)
AEXT6: EXP1.B19 (19)
AEXT7: EXP1.B20 (20)
BFIRQ: IC9.6 (O), P3.35
BFNEG: IC9.4 (O), P3.37
BFZERO: IC9.2 (O), P3.39
CLK1: EXP1.A29 (29); also elsewhere on the board
CLK2: EXP1.B29 (29); also elsewhere on the board
CLK3: EXP1.B30 (30); also elsewhere on the board
CLK4: EXP1.B28 (28); also elsewhere on the board
DB0: EXP1.C5 (5); also elsewhere on the board
DB1: EXP1.C6 (6); also elsewhere on the board
DB2: EXP1.C7 (7); also elsewhere on the board
DB3: EXP1.C8 (8); also elsewhere on the board
DB4: EXP1.C9 (9); also elsewhere on the board
DB5: EXP1.C10 (10); also elsewhere on the board
DB6: EXP1.C11 (11); also elsewhere on the board
DB7: EXP1.C12 (12); also elsewhere on the board
DB8: EXP1.C21 (21); also elsewhere on the board
DB9: EXP1.C22 (22); also elsewhere on the board
DB10: EXP1.C23 (23); also elsewhere on the board
DB11: EXP1.C24 (24); also elsewhere on the board
DB12: EXP1.C25 (25); also elsewhere on the board
DB13: EXP1.C26 (26); also elsewhere on the board
DB14: EXP1.C27 (27); also elsewhere on the board
DB15: EXP1.C28 (28); also elsewhere on the board
FIRQ: IC9.9 (I); also elsewhere on the board
FL: P1.5; also elsewhere on the board
FNEG: IC9.11 (I), P2.11; also elsewhere on the board
FPCLKEN: P3.20; also elsewhere on the board
FPIR0: P3.31; also elsewhere on the board
FPIR1: P3.29; also elsewhere on the board
FPIR2: P3.27; also elsewhere on the board
FPIR3: P3.25; also elsewhere on the board
FPIR4: P3.23; also elsewhere on the board
FPIR5: P3.21; also elsewhere on the board
FPIR6: P3.19; also elsewhere on the board
FPIR7: P3.17; also elsewhere on the board
FPIR8: P3.15; also elsewhere on the board
FPIR9: P3.13; also elsewhere on the board
FPIR10: P3.11; also elsewhere on the board
FPIR11: P3.9; also elsewhere on the board
FPIR12: P3.7; also elsewhere on the board
FPIR13: P3.5; also elsewhere on the board
FPIR14: P3.3; also elsewhere on the board
FPIR15: P3.1; also elsewhere on the board
FPUSTEP: P3.22; also elsewhere on the board
FV: P1.6; also elsewhere on the board
FZERO: IC9.13 (I), P2.12; also elsewhere on the board
GND: C10.-, C14.-, C55.1, C56.1, C57.-, EXP1.A1 (1), EXP1.A2 (2), EXP1.B1 (1), EXP1.B2 (2), EXP1.C1 (1), EXP1.C2 (2), IC9.7 (GND), IC41.3 (GND), IC41.4 (GND), IC41.13 (D9), IC41.14 (D10), IC42.3 (GND), IC42.4 (GND), IC42.13 (D9), IC42.14 (D10), P3.2, P3.4, P3.6, P3.8, P3.10, P3.12, P3.14, P3.16, P3.18, P3.24, P3.26, P3.32, P3.34, P3.36, P3.38, P3.40; also elsewhere on the board
IBUS0: IC41.1 (D1), P2.21; also elsewhere on the board
IBUS1: IC41.2 (D2), P2.22; also elsewhere on the board
IBUS2: IC41.12 (D8), P2.23; also elsewhere on the board
IBUS3: IC41.5 (D3), P2.24; also elsewhere on the board
IBUS4: IC41.9 (D7), P2.25; also elsewhere on the board
IBUS5: IC41.6 (D4), P2.26; also elsewhere on the board
IBUS6: IC41.8 (D6), P2.27; also elsewhere on the board
IBUS7: IC41.7 (D5), P2.28; also elsewhere on the board
IBUS8: IC42.1 (D1), P2.29; also elsewhere on the board
IBUS9: IC42.2 (D2), P2.30; also elsewhere on the board
IBUS10: IC42.12 (D8), P2.31; also elsewhere on the board
IBUS11: IC42.5 (D3), P2.32; also elsewhere on the board
IBUS12: IC42.9 (D7), P2.33; also elsewhere on the board
IBUS13: IC42.6 (D4), P2.34; also elsewhere on the board
IBUS14: IC42.8 (D6), P2.35; also elsewhere on the board
IBUS15: IC42.7 (D5), P2.36; also elsewhere on the board
IR0: P1.7; also elsewhere on the board
IR2: P1.9; also elsewhere on the board
IR11: P1.22; also elsewhere on the board
IR12: P2.37; also elsewhere on the board
IR13: P2.38; also elsewhere on the board
IR14: P2.39; also elsewhere on the board
IR15: P2.40; also elsewhere on the board
unnamed: IC9.1 (I), IC9.12 (O)
unnamed: IC9.3 (I), IC9.10 (O)
unnamed: IC9.5 (I), IC9.8 (O)
OPIF0: P1.18; also elsewhere on the board
OPIF1: P1.19; also elsewhere on the board
OPIF2: P1.20; also elsewhere on the board
OPIF3: P1.21; also elsewhere on the board
PC10: P2.13; also elsewhere on the board
PC11: P2.14; also elsewhere on the board
PC12: P2.15; also elsewhere on the board
PC13: P2.16; also elsewhere on the board
PC14: P2.17; also elsewhere on the board
PC15: P2.18; also elsewhere on the board
POWEROK: P3.30; also elsewhere on the board
RUNIT0: P1.11
RUNIT1: P1.12
RUNIT2: P1.13
RUNIT3: P1.14
VCC: C10.+, C14.+, C55.2, C56.2, C57.+, EXP1.A3 (3), EXP1.A32 (32), EXP1.B3 (3), EXP1.B32 (32), EXP1.C3 (3), EXP1.C32 (32), IC9.14 (VCC), IC41.10 (VCC), IC41.11 (VCC), IC42.10 (VCC), IC42.11 (VCC); also elsewhere on the board

Notes on the sheet:
(2) Pins *TPA and *TPC are not bussed. They are locally connected to each card's corresponding
test pins (A17 & C17) to serve as test points.
(1) This pin is connected to a bus bar for power distribution, but the CFT does not (yet) require it.
It's likely to be connected to another voltage level like +3.3V for easier interfacing. Reserved for now.
(3) Reserved for future expansion
Expansion Bus (computer bus)
(2)
(1)
(3)
(4) Cheaper, 64-pin A+C row DIN41662 Type C plugs may be used for most expansion cards.
(4)
Notes
(5) !IRQ! is provided for systems which lack an interrupt controller (!IRQ0-7!)
PCB @ (0, 1.95)
CFT Mini-Computer
(5)
Control Bus (processor bus)
@(0.15, 3.675)
@(0.15, 0.25)
@(5.775, 0.25)
@(5.775, 3.675)
Front Panel Connector

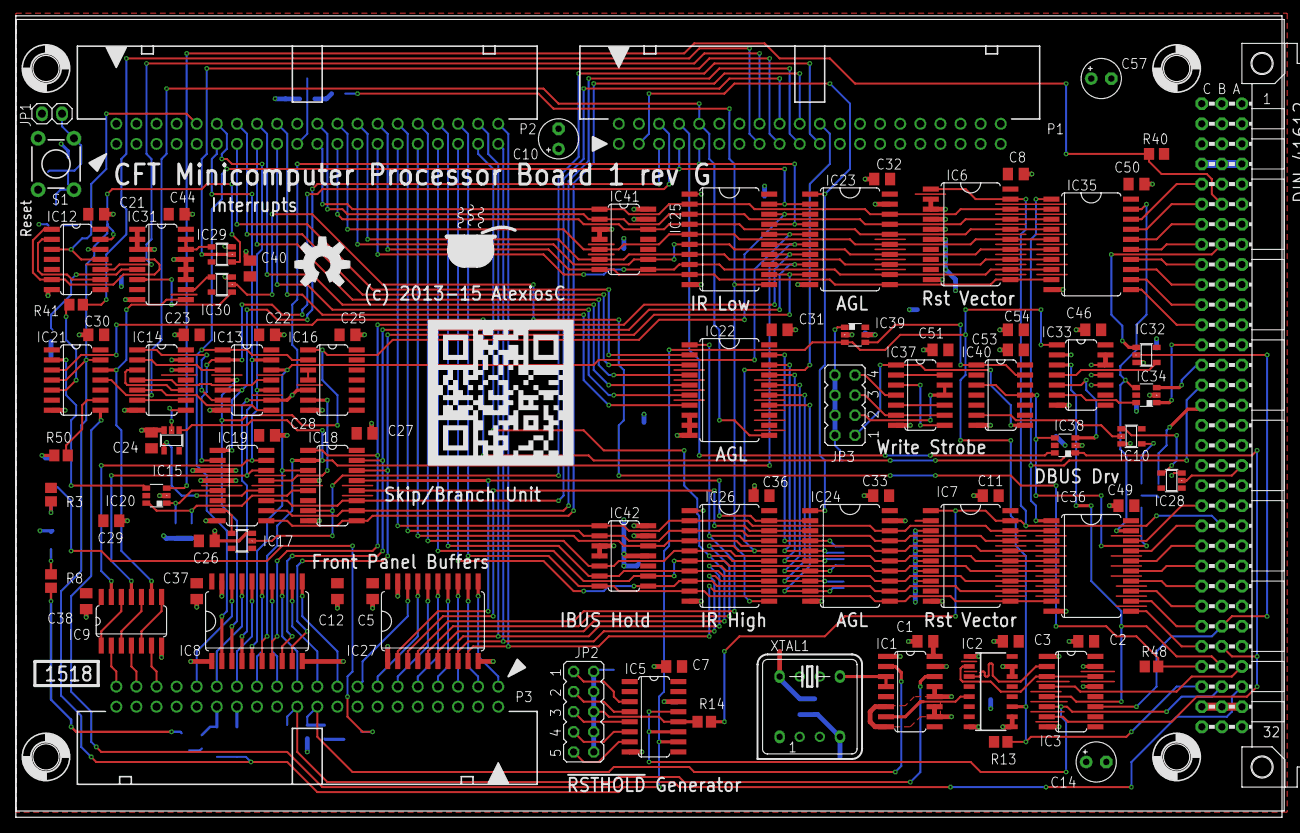
[picture p141: board CFT-PB1-revG-TSSOP.brd from above]

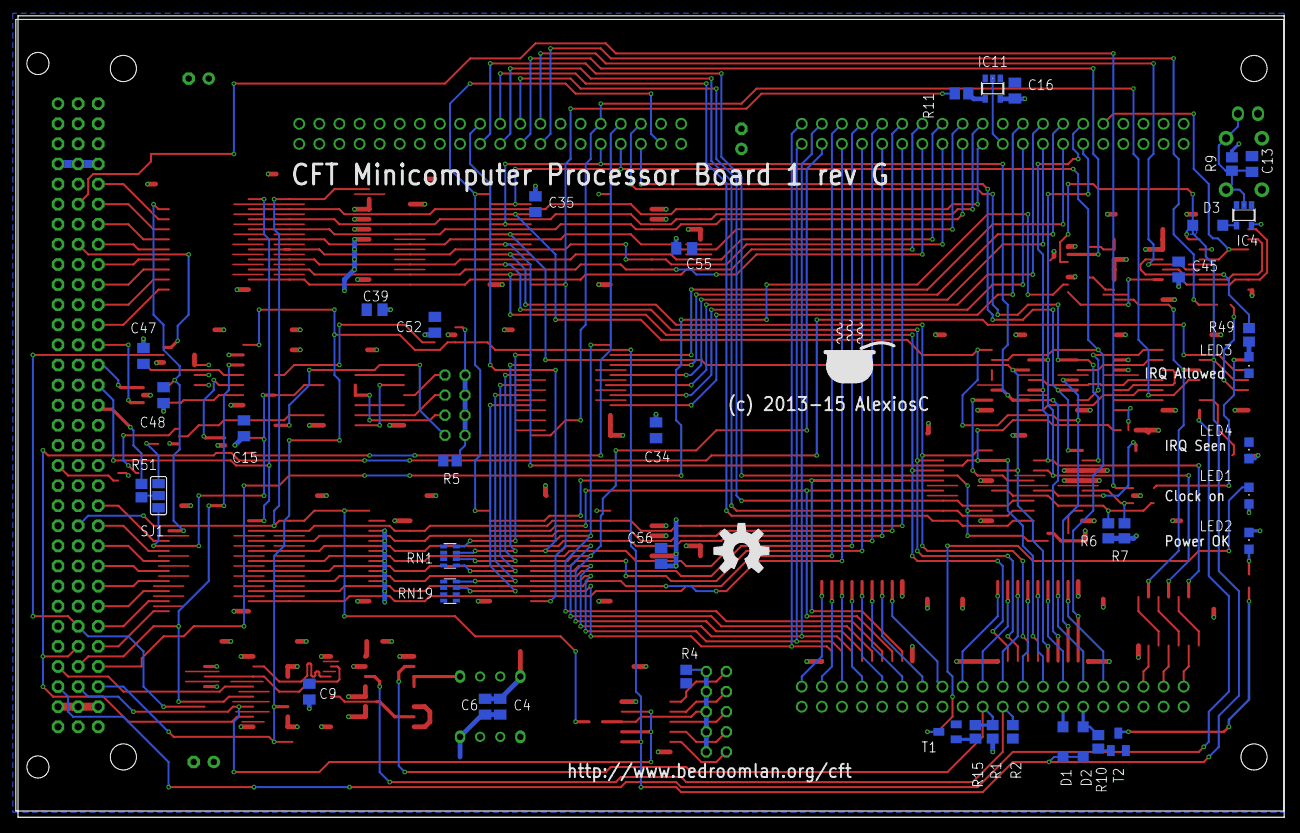
[picture p142: board CFT-PB1-revG-TSSOP.brd from below]

Board: 2 copper layers, 160.0 x 101.3 mm, 142 parts (43 on the bottom side), 185 nets.

Other parts of the board:
$4_37_$: SIGNATURESILK; SIGNATURE
