alexiosc/cft/kicad/protoboard/protoboard.sch

## KiCad design kicad/protoboard/protoboard.sch (2021-02-09)

Schematic: protoboard.sch

Parts:
J1: VG64_VME_3Rows_3x32_J1_P1; DIN41612_B_3x32_Horizontal
J2: VG64_VME_3Rows_3x32_J2_P2; DIN41612_B_3x32_Horizontal
