alexiosc/cft/emulator/FixedMedium-13.pcf

SplineFontDB: 3.0
FontName: FixedMedium
FullName: Fixed Medium
FamilyName: Fixed
Weight: Medium
Copyright: Public domain font.  Share and enjoy.
UComments: "2012-6-25: Created." 
Version: 001.000
ItalicAngle: 0
UnderlinePosition: -100
UnderlineWidth: 50
Ascent: 846
Descent: 154
LayerCount: 2
Layer: 0 0 "Back"  1
Layer: 1 0 "Fore"  0
XUID: [1021 790 1970473213 7833419]
OS2Version: 0
OS2_WeightWidthSlopeOnly: 0
OS2_UseTypoMetrics: 1
CreationTime: 1340628602
ModificationTime: 1340628602
OS2TypoAscent: 0
OS2TypoAOffset: 1
OS2TypoDescent: 0
OS2TypoDOffset: 1
OS2TypoLinegap: 0
OS2WinAscent: 0
OS2WinAOffset: 1
OS2WinDescent: 0
OS2WinDOffset: 1
HheadAscent: 0
HheadAOffset: 1
HheadDescent: 0
HheadDOffset: 1
OS2Vendor: 'PfEd'
DEI: 91125
Encoding: UnicodeBmp
UnicodeInterp: none
NameList: Adobe Glyph List
DisplaySize: 13
AntiAlias: 1
FitToEm: 1
WinInfo: 0 33 17
OnlyBitmaps: 1
BeginChars: 65534 3710

StartChar: char0
Encoding: 0 0 0
Width: 568
VWidth: 0
Flags: W
LayerCount: 2
EndChar

StartChar: space
Encoding: 32 32 1
Width: 568
VWidth: 0
Flags: W
LayerCount: 2
EndChar

StartChar: exclam
Encoding: 33 33 2
Width: 568
VWidth: 0
Flags: W
LayerCount: 2
EndChar

StartChar: quotedbl
Encoding: 34 34 3
Width: 568
VWidth: 0
Flags: W
LayerCount: 2
EndChar

StartChar: numbersign
Encoding: 35 35 4
Width: 568
VWidth: 0
Flags: W
LayerCount: 2
EndChar

StartChar: dollar
Encoding: 36 36 5
Width: 568
VWidth: 0
Flags: W
LayerCount: 2
EndChar

StartChar: percent
Encoding: 37 37 6
Width: 568
VWidth: 0
Flags: W
LayerCount: 2
EndChar

StartChar: ampersand
Encoding: 38 38 7
Width: 568
VWidth: 0
Flags: W
LayerCount: 2
EndChar

StartChar: quotesingle
Encoding: 39 39 8
Width: 568
VWidth: 0
Flags: W
LayerCount: 2
EndChar

StartChar: parenleft
Encoding: 40 40 9
Width: 568
VWidth: 0
Flags: W
LayerCount: 2
EndChar

StartChar: parenright
Encoding: 41 41 10
Width: 568
VWidth: 0
Flags: W
LayerCount: 2
EndChar

StartChar: asterisk
Encoding: 42 42 11
Width: 568
VWidth: 0
Flags: W
LayerCount: 2
EndChar

StartChar: plus
Encoding: 43 43 12
Width: 568
VWidth: 0
Flags: W
LayerCount: 2
EndChar

StartChar: comma
Encoding: 44 44 13
Width: 568
VWidth: 0
Flags: W
LayerCount: 2
EndChar

StartChar: hyphen
Encoding: 45 45 14
Width: 568
VWidth: 0
Flags: W
LayerCount: 2
EndChar

StartChar: period
Encoding: 46 46 15
Width: 568
VWidth: 0
Flags: W
LayerCount: 2
EndChar

StartChar: slash
Encoding: 47 47 16
Width: 568
VWidth: 0
Flags: W
LayerCount: 2
EndChar

StartChar: zero
Encoding: 48 48 17
Width: 568
VWidth: 0
Flags: W
LayerCount: 2
EndChar

StartChar: one
Encoding: 49 49 18
Width: 568
VWidth: 0
Flags: W
LayerCount: 2
EndChar

StartChar: two
Encoding: 50 50 19
Width: 568
VWidth: 0
Flags: W
LayerCount: 2
EndChar

StartChar: three
Encoding: 51 51 20
Width: 568
VWidth: 0
Flags: W
LayerCount: 2
EndChar

StartChar: four
Encoding: 52 52 21
Width: 568
VWidth: 0
Flags: W
LayerCount: 2
EndChar

StartChar: five
Encoding: 53 53 22
Width: 568
VWidth: 0
Flags: W
LayerCount: 2
EndChar

StartChar: six
Encoding: 54 54 23
Width: 568
VWidth: 0
Flags: W
LayerCount: 2
EndChar

StartChar: seven
Encoding: 55 55 24
Width: 568
VWidth: 0
Flags: W
LayerCount: 2
EndChar

StartChar: eight
Encoding: 56 56 25
Width: 568
VWidth: 0
Flags: W
LayerCount: 2
EndChar

StartChar: nine
Encoding: 57 57 26
Width: 568
VWidth: 0
Flags: W
LayerCount: 2
EndChar

StartChar: colon
Encoding: 58 58 27
Width: 568
VWidth: 0
Flags: W
LayerCount: 2
EndChar

StartChar: semicolon
Encoding: 59 59 28
Width: 568
VWidth: 0
Flags: W
LayerCount: 2
EndChar

StartChar: less
Encoding: 60 60 29
Width: 568
VWidth: 0
Flags: W
LayerCount: 2
EndChar

StartChar: equal
Encoding: 61 61 30
Width: 568
VWidth: 0
Flags: W
LayerCount: 2
EndChar

StartChar: greater
Encoding: 62 62 31
Width: 568
VWidth: 0
Flags: W
LayerCount: 2
EndChar

StartChar: question
Encoding: 63 63 32
Width: 568
VWidth: 0
Flags: W
LayerCount: 2
EndChar

StartChar: at
Encoding: 64 64 33
Width: 568
VWidth: 0
Flags: W
LayerCount: 2
EndChar

StartChar: A
Encoding: 65 65 34
Width: 568
VWidth: 0
Flags: W
LayerCount: 2
EndChar

StartChar: B
Encoding: 66 66 35
Width: 568
VWidth: 0
Flags: W
LayerCount: 2
EndChar

StartChar: C
Encoding: 67 67 36
Width: 568
VWidth: 0
Flags: W
LayerCount: 2
EndChar

StartChar: D
Encoding: 68 68 37
Width: 568
VWidth: 0
Flags: W
LayerCount: 2
EndChar

StartChar: E
Encoding: 69 69 38
Width: 568
VWidth: 0
Flags: W
LayerCount: 2
EndChar

StartChar: F
Encoding: 70 70 39
Width: 568
VWidth: 0
Flags: W
LayerCount: 2
EndChar

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
StartChar: afii57683
Encoding: 1507 1507 1254
Width: 568
VWidth: 0
Flags: W
LayerCount: 2
EndChar

StartChar: afii57684
Encoding: 1508 1508 1255
Width: 568
VWidth: 0
Flags: W
LayerCount: 2
EndChar

StartChar: afii57685
Encoding: 1509 1509 1256
Width: 568
VWidth: 0
Flags: W
LayerCount: 2
EndChar
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
