alexiosc/cft/emulator/cft.c

// -*- c -*-
// 
// cft.c — CFT processor emulation
// 
// Copyright © 2011–2020 Alexios Chouchoulas
// 
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
#include <stdio.h>
#include <stdlib.h>
#include <string.h>
#include <stdint.h>
#include <unistd.h>
#include <assert.h>
#include <time.h>
#include <sys/types.h>
#include <sys/stat.h>
#include <argp.h>

#include "cft.h"
#include "util.h"

#define LOG_MACROS_UNIT ctl_log_unit
#include "log.h"


static log_unit_t cpu_log_unit; // Logging unit for instruction trace etc.
static log_unit_t ctl_log_unit; // Logging unit for the Control Unit.
static log_unit_t mbu_log_unit; // Logging unit for the Control Unit.

// The emulator state
state_t cpu;

char *log_name = "output";
FILE *log_file = NULL;

int verbose = 0;
int sanity = 1;
int debug_microcode = 0;
int debug_mem = 0;
int debug_io = 0;
int debug_asm = 0;
int testing = 0;
int sentinel = 0;
int nvram = 0;


//#define ctl_debug(msg, ...) log_msg (LOG_DEBUG, log_ctl, msg, ## __VA_ARGS__)
//#define sbu_debug debug // (msg, ...) log_msg (LOG_DEBUG, log_sbu, msg, ## __VA_ARGS__)



///////////////////////////////////////////////////////////////////////////////
//
// FORWARD DEFINITIONS
//
///////////////////////////////////////////////////////////////////////////////

static int _dummy_memr(longaddr_t ab, word * db);

static int _dummy_memw(longaddr_t ab, word db);

static int _dummy_ior(longaddr_t ab, word * db);

static int _dummy_iow(longaddr_t ab, word db);


///////////////////////////////////////////////////////////////////////////////
//
// BASICS AND RUN CONTROL
//
///////////////////////////////////////////////////////////////////////////////


// Initialise the CPU (but don't reset it yet!)
void
cpu_init()
{
        // Clear everything in the CPU state.
        memset(&cpu, 0, sizeof(cpu));
        
        // Initialise logging
        cpu_log_unit = log_add_unit("CPU", -1, 0);
        ctl_log_unit = log_add_unit("CTL", -1, 0);
        mbu_log_unit = log_add_unit("MBU", -1, 0);

        // Register dummy callbacks
        cpu.memr = _dummy_memr;
        cpu.memw = _dummy_memw;
        cpu.ior = _dummy_ior;
        cpu.iow = _dummy_iow;

        // CTL: Control Unit
        cpu.ir = rand() & 0xffff;

        // REG: register file
        cpu.pc = rand() & 0xffff;
        cpu.dr = rand() & 0xffff;
        cpu.ac = rand() & 0xffff;
        cpu.sp = rand() & 0xffff;

        // BUS: Bus control
        cpu.ar = rand() & 0xffffff;
        srand(time(NULL));

        // MBU: Memory Banking Unit
        cpu.ctx = rand() & (0xff << 3);
        for (int i = 0; i < (NCTX * NMBR); i++) {
                cpu.mbr[i] = rand() & 0xff0000;
        }
        cpu.mbrdis = 0x800000;
        cpu.mbuen = 0;

        // ALU: Arithmetic & Logic
        cpu.alu_a = rand() & 0xffff;
        cpu.alu_b = rand() & 0xffff;

        // Flags
        cpu.fl = rand() & 1;
        cpu.fi = rand() & 1;
        cpu.fv = rand() & 1;
        cpu.fz = cpu.ac == 0;
        cpu.fn = (cpu.ac >> 15) & 1;
    
        cpu.irq = rand() & 1;

        cpu.rst_hold = -1;
        cpu.tick = 0;
}


void
cpu_done()
{
        // Nothing to deallocate yet.
}



// Implement the reset sequence (which is quite simple).
void
cpu_reset()
{
        // CTL
        cpu.uav.rst = 0;            // 0 = RESET# is ACTIVE */
        cpu.uav.int_ = 1;           // 1 = INT# is not active
        cpu.uav.uaddr = 0;          // The uPC resets to 0 on power on/reset
        cpu.irq = 0;                // Clear IRQ
        cpu.rst_hold = 2;           // We don't need to hold reset for long here
        cpu.ir = 0xdead;
        cpu.agl_page = GET_PAGE(cpu.pc);
        cpu.endext = 0;
        cpu.skipext = 0;

        // REG
        cpu.pc = 0;
        cpu.dr = 0;
        cpu.ac = 0;
        cpu.sp = 0;

        // ALU
        cpu.fl = 0;
        cpu.fv = 0;

        // MBU
        cpu.mbrdis = 0x800000;
        cpu.mbuen = 0;
}


// Simulate reset behaviour: the CFT's reset circuitry contains a counter
// which, when triggered using /RESET, holds the internal reset signal
// (/RST-HOLD) active for a number of cycles. The rising edge of /RST-HOLD, at
// the end of the count, has side effects in the hardware (e.g. AR reads its
// value from the IBUS, so both PC and AR are initialised to 0xfff0.)

static inline void
cpu_handle_reset()
{
        if (cpu.rst_hold > 0) {
                cpu.rst_hold--;
                cpu.resetting = 1;
        } else if (cpu.rst_hold == 0) {
                // When the counter runs out, de-assert the RST signal in the
                // microcode engine.
                cpu.uav.rst = 1;
                cpu.rst_hold = -1;
                cpu.resetting = 0;
                log_msg(LOG_DEBUG, cpu_log_unit, "RSTHOLD de-asserted.");
        }
}


void
cpu_halt()
{
        cpu.halt = 1;
        log_msg(LOG_INFO, cpu_log_unit, "Halted");
        // v.dirty++;
        // v.stdirty++;
}


void
cpu_start()
{
        cpu.halt = 0;
        log_msg(LOG_INFO, cpu_log_unit, "Resumed");
        // v.dirty++;
        // v.stdirty++;
}


void
quit(int quiet)
{
        cpu.quit = 1;
        // if (!quiet) {
        //     dump_state();
        //     dump_ustate();
        //     info("*** QUIT PRESSED ***");
        // }
}


///////////////////////////////////////////////////////////////////////////////
//
// READING FROM UNITS
//
///////////////////////////////////////////////////////////////////////////////


// The new Constant store is incredibly simple.
static inline word
read_cs(int raddr)
{
        return raddr & 3;
}


///////////////////////////////////////////////////////////////////////////////
//
// ACTIONS
//
///////////////////////////////////////////////////////////////////////////////
        

// The new Shift and Roll Unit. The calculation itself isn't cycle-accurate,
// but the microcode still waits for the correct number of cycles before
// reading the result, so we end up with a cycle-accurate behaviour anyway.
static inline void
action_sru()
{
        //            OP   I R 987 654 3210
        // SHL = SRU  0111'1'0'000'000'dddd    ; Bitwise shift left by d bits
        // SHR = SRU  0111'1'0'000'001'dddd    ; Bitwise shift right by d bits
        // ASR = SRU  0111'1'0'000'011'dddd    ; Arithmetic shift right by d bits
        // ROL = SRU  0111'1'0'000'100'dddd    ; Rotate <L,AC> left by d bits
        // ROR = SRU  0111'1'0'000'101'dddd    ; Rotate <L,AC> right by d bits

        int dist = cpu.ir & 15;
        if (dist == 0) return;

        int op = (cpu.ir >> 4) & 7;
        int l_ac;

        switch (op) {
        case 0:                     // SHL
                l_ac = (cpu.fl ? 0x10000 : 0) | (cpu.alu_b & 0xffff);
                l_ac <<= dist;
                cpu.fl = (l_ac & 0x10000) != 0;
                cpu.alu_b = l_ac & 0xffff;
                break;
                
        case 1:                     // SHR
                l_ac = (cpu.fl ? 0x10000 : 0) | (cpu.alu_b & 0xffff);
                l_ac >>= dist;
                cpu.fl = (l_ac & 0x10000) != 0;
                cpu.alu_b = l_ac & 0xffff;
                break;
                
        case 3:                     // ASR
                // ASR doesn't shifts AC, not <L,AC>. The Link is set to the last bit
                // shifted off the AC. Casting to a signed int makes C use the host
                // platform's arithmetic/sign-extending shift instruction.
                l_ac = (word)((int16_t)cpu.alu_b >> dist);
                cpu.fl = ((word)((int16_t)cpu.alu_b >> (dist - 1))) & 1;
                cpu.alu_b = l_ac & 0xffff;
                break;
                
        case 4:                     // ROL
                l_ac = (cpu.fl ? 0x10000 : 0) | (cpu.alu_b & 0xffff);
                l_ac = ((l_ac << dist) | (l_ac >> (17 - dist))) & 0x1ffff;
                cpu.fl = (l_ac & 0x10000) != 0;
                cpu.alu_b = l_ac & 0xffff;
                break;
                
        case 5:                     // ROR
                l_ac = (cpu.fl ? 0x10000 : 0) | (cpu.alu_b & 0xffff);
                l_ac = ((l_ac >> dist) | (l_ac << (17 - dist))) & 0x1ffff;
                cpu.fl = (l_ac & 0x10000) != 0;
                cpu.alu_b = l_ac & 0xffff;
                break;

        default:
                fatal("Undefined SRU op %d", op);
        }
}


/*

        // Step the PC
        if (incpc) {
            cpu.pc = (cpu.pc + 1) & 0xffff;
            debug("pc_inc: PC ← %04x", cpu.pc);
            // Sanity check
            if (sanity && (cpu.pc == 0)) {
                fatal("PC AT 0000, SHOULD NEVER HAPPEN");
            }
        }
                
        // Increment A, if requested by an OPx instruction.
        if (stpac) {
            if (dec) {
                set_a((cpu.a - 1) & 0xffff);
                if (cpu.a == 0xffff) cpu.l = !cpu.l;
            } else {
                set_a((cpu.a + 1) & 0xffff);
                if (cpu.a == 0) cpu.l = !cpu.l;
            }
            debug("inc_a: A ← %04x", cpu.a);
        }

        // Step the DR.
        if (stpdr) {
            cpu.dr = (dec ? cpu.dr - 1 : cpu.dr + 1) & 0xffff;
            debug("step_dr: DR ← %04x", cpu.dr);
        }

        // Set other stuff
        if (cpl) {
            cpu.l = !cpu.l;
        }
        if (cll) {
            cpu.l = 0;
            debug("cpl: L ← %d", cpu.l);
        }
        if (sti) {
            cpu.arm_sti = 1; // Arm STI.
        }
        if (cli) {
            cpu.i = 1;
            debug("CLI: PC=%04x, I ← %d", cpu.pc, cpu.i);
        }

*/


static inline void
handle_actions(int action)
{
        switch (action) {
        case FIELD_ACTION_CPL:
                cpu.fl ^= 1;
                debug3("action_cpl: L ← %d", cpu.fl);
                return;

        case FIELD_ACTION_CLL:
                cpu.fl = 0;
                debug3("action_cll: L ← %d", cpu.fl);
                return;

        case FIELD_ACTION_STI:
                cpu.fi = 1;
                debug3("action_sti: I ← %d", cpu.fi);
                return;

        case FIELD_ACTION_CLI:
                cpu.fi = 0;
                cpu.irq = 0;
                debug3("action_cli: I ← %d", cpu.fi);
                return;

        case FIELD_ACTION_IDX:
                debug3("action_idx");
                // This is decoded when write_ar_mbz is handled.
                return;

        case FIELD_ACTION_SRU:
                action_sru();
                return;

        case FIELD_ACTION_INCPC:
                cpu.pc = (cpu.pc + 1) & 0xffff;
                debug3("action_incpc: PC ← %04x", cpu.pc);
                // Sanity check
                if (cpu.pc == 0) {
                        fatal("PC wrapped around to 0000. This is software bug.");
                }
                return;

        case FIELD_ACTION_INCDR:
                cpu.dr = (cpu.dr + 1) & 0xffff;
                debug3("action_incdr: DR ← %04x", cpu.dr);
                return;
        
        case FIELD_ACTION_DECDR:
                cpu.dr = (cpu.dr - 1) & 0xffff;
                debug3("action_decdr: DR ← %04x", cpu.dr);
                return;

        case FIELD_ACTION_INCAC:
                if (cpu.ac == 0xffff) cpu.fl ^= 1;
                cpu.ac = (cpu.ac + 1) & 0xffff;
                debug3("action_incac: AC ← %04x [L=%d]", cpu.ac, cpu.fl);
                return;

        case FIELD_ACTION_DECAC:
                if (cpu.ac == 0) cpu.fl ^= 1;
                cpu.ac = (cpu.ac - 1) & 0xffff;
                debug3("action_decac: AC ← %04x [L=%d]", cpu.ac, cpu.fl);
                return;

        case FIELD_ACTION_INCSP:
                cpu.sp = (cpu.sp + 1) & 0xffff;
                debug3("action_incsp: SP ← %04x", cpu.sp);
                return;
        
        case FIELD_ACTION_DECSP:
                cpu.sp = (cpu.sp - 1) & 0xffff;
                debug3("action_decsp: SP ← %04x", cpu.sp);
                return;

        default:
                fatal("Unknown ACTION %x", action);
        }
}


///////////////////////////////////////////////////////////////////////////////
//
// THE BUS INTERFACE & MEMORY MANAGEMENT
//
///////////////////////////////////////////////////////////////////////////////

// Load the Data Bus with data from a memory or I/O space device.
inline void
bus_reads(int mem, int io)
{
        if (mem && io) {
                fatal("MEM and IO asserted simultaneously during read. Microcode bug!");
        }

        if (mem) {
                if ((*cpu.memr)(cpu.ar, &cpu.dbus) < 0) {
                        warning("Bus error: read from undecoded address %s",
                                format_longaddr(cpu.ar, NULL));
                }
        }

        if (io) {
                if ((*cpu.ior)(cpu.ar & 0x3ff, &cpu.dbus) < 0) {
                        warning("Bus error: read from undecoded I/O port %03x",
                                format_longaddr(cpu.ar & 0xffff, NULL));
                }
        }
}


// Write the value on the Data Bus to a memory or I/O space device.
inline void
bus_writes(int mem, int io)
{
        if (mem && io) {
                fatal("MEM and IO asserted simultaneously during write. Microcode bug!");
        }

        if (mem) {
                if ((*cpu.memw)(cpu.ar, cpu.dbus) < 0) {
                        warning("Bus error: write to undecoded address %s",
                                format_longaddr(cpu.ar, NULL));
                }
        }

        if (io) {
                if ((*cpu.iow)(cpu.ar & 0x3ff, cpu.dbus) < 0) {
                        warning("Bus error: write to undecoded I/O port %03x",
                                format_longaddr(cpu.ar & 0xffff, NULL));
                }
        }
}


// These allow the CPU to run, but not very well.
int
_dummy_memr(longaddr_t ab, word * db)
{
        warning("dummy callback %s called", __func__);
        return -1;
}
    

int
_dummy_memw(longaddr_t ab, word db)
{
        warning("dummy callback %s called", __func__);
        return -1;
}
    

int
_dummy_ior(longaddr_t ab, word * db)
{
        warning("dummy callback %s called", __func__);
        return -1;
}
    

int
_dummy_iow(longaddr_t ab, word db)
{
        warning("dummy callback %s called", __func__);
        return -1;
}


///////////////////////////////////////////////////////////////////////////////
//
// MEMORY BANKING UNIT
//
///////////////////////////////////////////////////////////////////////////////

void
mbu_set_ram_rom(int have_rom)
{
        cpu.mbrdis = have_rom ? 0x800000 : 0;
}


inline longaddr_t
get_mbr(int mbr)
{
        return cpu.mbuen ? cpu.mbr[cpu.ctx | (mbr & 7)] : cpu.mbrdis;
}


#if 0
// // Reading from the MBU 
// int
// mbu_read(longaddr_t a, word *d)
// {
//         // Note that the LMB instruction only drives the lower 8 bits of the
//         // IBus. We randomise the upper 8 bits here.
//         assert(d != NULL);
//         if (a >= 0x008 && a <= 0x00f) {
//                 *d = 0x5400 | (get_mbr(a & 7) >> 16);
//                 log_msg(LOG_DEBUG3, mbu_log_unit, "MBR[%0xd] → %02x (mbuen=%d)", a & 7, *d & 0xff, cpu.mbuen);
//                 return 1;
//         }
//         return 0;
// }


// int
// mbu_write(longaddr_t a, word d)
// {
// #error "Rewrite this for the new MBU"
//         if (a >= 0x008 && a <= 0x00f) {
//                 cpu.mbr[a & 7] = (d & 0xff) << 16;
//                 int enabling = cpu.mbuen == 0;
//                 cpu.mbuen = 1;
//                 log_msg(LOG_DEBUG3, mbu_log_unit, "MBR[%d] → %02x. "
//                         "%sMBRs now %02x %02x %02x %02x %02x %02x %02x %02x",
//                         a & 7, d & 0xff,
//                         enabling ? "Enabling MBU. " : "",
//                         get_mbr(0) >> 16, get_mbr(1) >> 16, get_mbr(2) >> 16, get_mbr(3) >> 16,
//                         get_mbr(4) >> 16, get_mbr(5) >> 16, get_mbr(6) >> 16, get_mbr(7) >> 16);
//                 return 1;
//         }
//         return 0;
// }
#endif


///////////////////////////////////////////////////////////////////////////////
//
// CONDITIONALS
//
///////////////////////////////////////////////////////////////////////////////

// Decode IFx signals, and update the SKIP flag in the uROM vector for the next
// microinstruction.

static inline void
decode_cond(int cond)
{
        cpu.uav.cond = 1;        // COND=1 means ‘do not skip’

        switch (cond) {
        case 0:
                // Idle, never skip
                cpu.uav.cond = 1;
                break;
        
        case FIELD_IF_IR0:
                cpu.uav.cond = (cpu.ir & 0x1) ? 0 : 1;
                debug3("IF0");
                break;
        
        case FIELD_IF_IR1:
                cpu.uav.cond = (cpu.ir & 0x2) ? 0 : 1;
                debug3("IF1");
                break;

        case FIELD_IF_IR2:
                cpu.uav.cond = (cpu.ir & 0x4) ? 0 : 1;
                debug3("IF2");
                break;

        case FIELD_IF_IR3:
                cpu.uav.cond = (cpu.ir & 0x8) ? 0 : 1;
                debug3("IF3");
                break;

        case FIELD_IF_IR4:
                cpu.uav.cond = (cpu.ir & 0x10) ? 0 : 1;
                debug3("IF4");
                break;

        case FIELD_IF_IR5:
                cpu.uav.cond = (cpu.ir & 0x20) ? 0 : 1;
                debug3("IF5");
                break;

        case FIELD_IF_IR6:
                cpu.uav.cond = (cpu.ir & 0x40) ? 0 : 1;
                debug3("IF6");
                break;

        case FIELD_IF_V:
                cpu.uav.cond = cpu.fv ? 0 : 1;
                debug3("IFV");
                break;

        case FIELD_IF_L:
                cpu.uav.cond = cpu.fl ? 0 : 1;
                debug3("IFL");
                break;

        case FIELD_IF_Z:
                cpu.uav.cond = cpu.fz ? 0 : 1;
                debug3("IFZ");
                break;

        case FIELD_IF_N:
                cpu.uav.cond = cpu.fn ? 0 : 1;
                debug3("IFN");
                break;

        case FIELD_IF_BRANCH:
        {
                // Simulate the hardware exactly.
                word data[5] = {
                        cpu.ir & 1,
                        (cpu.ir & 2) >> 1,
                        (cpu.ir & 4) >> 2,
                        (cpu.ir & 8) >> 3,
                        (cpu.ir & 16) >> 4
                };

                // This looks like a waste of space, but gcc optimises it to
                // the same assembly code as if we used one long, hard to read
                // expression.
                register int sn = cpu.fn & data[3];
                register int sz = cpu.fz & data[2];
                register int sl = cpu.fl & data[1];
                register int sv = cpu.fv & data[0];

                register int sx = sn || sz || sl || sv;

                // µCode signal COND is active low, so reverse it here.
                cpu.uav.cond = (sx ^ data[4]) ? 0 : 1;

                debug4("BRANCH: A=%04x, DATA=%d%d%d%d%d", cpu.ac, data[4], data[3], data[2], data[1], data[0]);
                debug4("BRANCH: A=%04x, SV=%d, SL=%d, SZ=%d, SN=%d", cpu.ac, sv, sl, sz, sn);
                debug4("BRANCH: A=%04x,  V=%d,  L=%d,  Z=%d,  N=%d", cpu.ac, cpu.fv, cpu.fl, cpu.fz, cpu.fn);
                debug4("IFBRANCH");
        }
        break;
    
        default:
                fatal("Unknown microcode conditional %x", cond);
        }

        if (cpu.uav.cond == 0) {
                debug3("Skip taken");
        }
}


///////////////////////////////////////////////////////////////////////////////
//
// READING FROM IBUS UNITS
//
///////////////////////////////////////////////////////////////////////////////


// Decode the read unit: the selected unit puts its value on the IBUS. Only one
// unit may be active at any one time (this is enforced by the microcode
// format: 4 bits identify the read unit).

static inline word
read_from_ibus_unit(int raddr)
{
        word tmp;

        switch (raddr) {
        case FIELD_READ_CS0:
                debug3("IBUS ← CS0 (0000)");
                return 0;

        case FIELD_READ_CS1:
                debug3("IBUS ← CS1 (0001)");
                return 1;

        case FIELD_READ_CS2:
                debug3("IBUS ← CS2 (0002)");
                return 2;

        case FIELD_READ_CS3:
                debug3("IBUS ← CS2 (0002)");
                return 3;

        case FIELD_READ_PC:
                debug3("IBUS ← PC (%04x)", cpu.pc);
                return cpu.pc;

        case FIELD_READ_DR:
                debug3("IBUS ← DR (%04x)", cpu.dr);
                return cpu.dr;

        case FIELD_READ_AC:
                debug3("IBUS ← AC (%04x)", cpu.ac);
                return cpu.ac;
        
        case FIELD_READ_SP:
                debug3("IBUS ← SP (%04x)", cpu.sp);
                return cpu.sp;

        case FIELD_READ_AGL:
                tmp = MAKE_SHORT_ADDRESS(get_r(cpu.ir) ? 0 : cpu.agl_page, cpu.ir);
                debug3("IBUS ← AGL (%04x)", tmp);
                return tmp;

        case FIELD_READ_ALU_ADD:
        {
                cpu.alu_a = cpu.ac;
                uint32_t sum = (uint32_t) cpu.alu_a + (uint32_t) cpu.alu_b;
                cpu.alu_y = sum & 0xffff;
                if (sum & 0x10000) cpu.fl = !cpu.fl;
                cpu.fv = (cpu.alu_a & 0x8000) == (cpu.alu_b & 0x8000) && \
                        (cpu.alu_a & 0x8000) != (cpu.alu_y & 0x8000);
                debug3("IBUS ← A + B (%04x), L ← %d, V ← %d", cpu.alu_y, cpu.fl, cpu.fv);
                return 0;               // Pretend we need extra time for the addition
        }
        
        case FIELD_READ_ALU_AND:
                cpu.alu_a = cpu.ac;
                cpu.alu_y = cpu.alu_a & cpu.alu_b;
                debug3("IBUS ← A AND B (%04x)", cpu.alu_y);
                return cpu.alu_y;
        
        case FIELD_READ_ALU_OR:
                cpu.alu_a = cpu.ac;
                cpu.alu_y = cpu.alu_a | cpu.alu_b;
                debug3("IBUS ← A OR B (%04x)", cpu.alu_y);
                return cpu.alu_y;
        
        case FIELD_READ_ALU_XOR:
                cpu.alu_a = cpu.ac;
                cpu.alu_y = cpu.alu_a ^ cpu.alu_b;
                debug3("IBUS ← A XOR B (%04x)", cpu.alu_y);
                return cpu.alu_y;
        
        case FIELD_READ_ALU_NOT:
                cpu.alu_a = cpu.ac;
                cpu.alu_y = cpu.alu_a ^ 0xffff;
                debug3("IBUS ← NOT A (%04x)", cpu.alu_y);
                return cpu.alu_y;
        
        case FIELD_READ_ALU_Y:
                debug3("IBUS ← ALU Y (%04x)", cpu.alu_y);
                return cpu.alu_y;

        case FIELD_READ_ALU_B:
                debug3("IBUS ← ALU B (%04x)", cpu.alu_b);
                return cpu.alu_b;
        
        case FIELD_READ_MBN:
                tmp = get_mbr(cpu.ir & 7) >> 16; // The MBR values are stored << 16.
                debug3("IBUS ← MB[%02x:%d] (%02x) (mbuen=%d, mbrdis=%08x)", cpu.ctx >> 3, cpu.ir & 7, tmp, cpu.mbuen, cpu.mbrdis);
                // Pretend we have bus hold. The last thing on the bus would
                // have been the last instruction fetched, so take its MSB.
                return (cpu.ir & 0xff00) | (tmp & 0xff);
        
        case FIELD_READ_MBP:
                tmp = cpu.mbr[cpu.ctx /* | 0 (implied) */] >> 16;
                debug3("IBUS ← MB[%02x:0] (%02x)", cpu.ctx >> 3, tmp);
                return tmp;
        
        case FIELD_READ_CTX:
                tmp = cpu.ctx >> 3;
                debug3("IBUS ← CTX (%02x)", tmp);
                return tmp;

        case FIELD_READ_CTX_FLAGS:
                tmp = ((cpu.ctx >> 3) & 0xff) | // bits 0-7 (0x00ff): CTX
                        cpu.fn << 10 |          // bit 10 (0x0400): N
                        cpu.fz << 11 |          // bit 11 (0x0800): Z
                        cpu.fl << 12 |          // bit 12 (0x1000): L
                        cpu.fv << 13 |          // bit 13 (0x2000): V
                        cpu.fi << 15;           // bit 15 (0x8000): I
                        
                debug3("IBUS ← CTX+FLAGS (%04x)", tmp);
                return tmp;

        case FIELD_READ_SWAB:
                tmp = ((cpu.ac << 8) | (cpu.ac >> 8));
                debug3("IBUS ← SWAB (%04x)", tmp);
                return tmp;

        default:
                fatal("Unknown RADDR %x.", raddr);
        }

        // We should never get here
        return cpu.ibus;
}


///////////////////////////////////////////////////////////////////////////////
//
// WRITING TO IBUS UNITS
//
///////////////////////////////////////////////////////////////////////////////


static inline void
write_to_ar(int mbr) {
        // If the microcode is requesting an MBR-relative indexing mode, and the
        // instruction has I=1 and R=1 and an operand >= 0x300, then we select an
        // MBR based on the least significant bits of the IR. It's very simple in
        // C, but this little fucker of a feature added several ICs to the Memory
        // Banking Unit!
        int from_ir = 0;
        if ((GET_ACTION(cpu.ucv) == FIELD_ACTION_IDX) && 
            (cpu.ir & 0x0f00) == 0x0f00) {
                mbr = cpu.ir & 7;
                from_ir = 1;
        }

        uint32_t mbr_value = get_mbr(mbr);
        assert ((mbr_value & 0xffff) == 0);
        
        cpu.ar = mbr_value | cpu.ibus;
        debug3("AR ← MB%d:IBUS (%s) [MBR selected by %s]", mbr, format_longaddr(cpu.ar, NULL),
               from_ir ? "operand field" : "microcode");
}

// Decode the write unit and handle side effects: the selected unit gets its
// value from the IBUS. This must run after a value has been put on the IBUS,
// which simulates the hardware behaviour too (write unit control pulses are
// delayed to allow the unit outputting a value to settle). Only one unit may
// be active at any one time (this is enforced by the microcode format: 4 bits
// identify the read unit).

static inline void
write_to_ibus_unit(int waddr)
{
        // MBZ-relative addressing as a more complicated special case for
        // auto-index MBR-relative addressing modes.
        switch(waddr){
        case FIELD_WRITE_AR_MBP:
                write_to_ar(MBR_MBP);
                return;

        case FIELD_WRITE_AR_MBD:
                write_to_ar(MBR_MBD);
                return;

        case FIELD_WRITE_AR_MBS:
                write_to_ar(MBR_MBS);
                return;

        case FIELD_WRITE_AR_MBZ:
                write_to_ar(MBR_MBZ);
                return;

        case FIELD_WRITE_PC:
                cpu.pc = cpu.ibus;
                debug3("PC ← IBUS (%04x)", cpu.ibus);
                // // Sanity check
                // if (sanity && (cpu.pc == 0)) {
                //     fatal("PC at 0000. This is probably a CFT software error.");
                // }
                return;

        case FIELD_WRITE_DR:
                cpu.dr = cpu.ibus;
                debug3("DR ← IBUS (%04x)", cpu.ibus);
                return;

        case FIELD_WRITE_AC:
                cpu.ac = cpu.ibus;
                cpu.fn = (cpu.ac & 0x8000) != 0;
                cpu.fz = cpu.ac == 0;
                debug3("AC ← IBUS (%04x)", cpu.ibus);
                return;

        case FIELD_WRITE_SP:
                cpu.sp = cpu.ibus;
                debug3("SP ← IBUS (%04x)", cpu.ibus);
                return;

        case FIELD_WRITE_IR:
                cpu.ir = cpu.ibus;
                debug3("IR ← IBUS (%04x): %s", cpu.ibus, disasm(cpu.ir, 1, NULL));
                return;
        
        case FIELD_WRITE_ALU_B:
                cpu.alu_b = cpu.ibus;
                debug3("ALU B ← IBUS (%04x)", cpu.ibus);
                return;
        
        case FIELD_WRITE_MBN:
                // Enable the MBU on the first write. This will usually be the
                // first SMB instruction.
                if (!cpu.mbuen) {
                        cpu.mbuen = 1;
                        debug3("Enabling MBU.");
                }

                // Get the number of the register from the IR (LS 3 bits)
                cpu.mbr[cpu.ctx | (cpu.ir & 7)] = (cpu.ibus & 0xff) << 16;
                debug3("MB[%02x:%d] ← IBUS (%02x)", cpu.ctx >> 3, cpu.ir & 7, cpu.ibus & 0xff);
                return;

        case FIELD_WRITE_MBP:
                // Writing directly to the MBP doesn't enable the MBU.
                cpu.mbr[cpu.ctx] = (cpu.ibus & 0xff) << 16;
                debug3("MB[%02x:0] ← IBUS (%02x)", cpu.ctx >> 3, cpu.ibus & 0xff);
                return;

        case FIELD_WRITE_CTX:
                cpu.ctx = (cpu.ibus & 0xff) << 3;
                debug3("Entering context %02x", cpu.ibus & 0xff);
                return;

        case FIELD_WRITE_CTX_FLAGS:
                cpu.ctx = (cpu.ibus & 0xff) << 3;
                cpu.fl = cpu.ibus & 0x1000 ? 1 : 0;
                cpu.fv = cpu.ibus & 0x2000 ? 1 : 0;
                cpu.fi = cpu.ibus & 0x8000 ? 1 : 0;
                debug3("CTX+FLAGS ← IBUS (%04x) [L=%d V=%d I=%d]", cpu.ibus, cpu.fl, cpu.fv, cpu.fi);
                return;
        
        case FIELD_WRITE_FLAGS:
                cpu.fl = cpu.ibus & 0x1000 ? 1 : 0;
                cpu.fv = cpu.ibus & 0x2000 ? 1 : 0;
                cpu.fi = cpu.ibus & 0x8000 ? 1 : 0;
                debug3("FLAGS ← IBUS (%04x) [L=%d V=%d I=%d]", cpu.ibus, cpu.fl, cpu.fv, cpu.fi);
                return;

        default:
                fatal("Unknown WADDR %x.", waddr);
        }
}


///////////////////////////////////////////////////////////////////////////////
//
// MAIN LOOP
//
///////////////////////////////////////////////////////////////////////////////

// Implement the control store.
static void
cpu_control_store()
{
        // 15  14  13  12  11  10   9   8   7   6   5   4   3   2   1   0
        // OP------------  I   R    SUB------
        //                 800 400 200 100  80  40  20  10  4   3   2   1


        // Much of the UAV comes from the IR, but it's split in four fields.
        cpu.uav.op = (cpu.ir >> 12) & 15;
        cpu.uav.i = (cpu.ir >> 11) & 1;
        cpu.uav.r = (cpu.ir >> 10) & 1;
        cpu.uav.subop = (cpu.ir >> 7) & 7;

        // Set the indexing mode if the IR operand is 0x300 to 0x3ff.
        cpu.uav.idx = ((cpu.ir & 0x0300) == 0x300) ? ((cpu.ir >> 6) & 3) : 0;

        // If an interrupt has been requested and interrupts are allowed, we jump
        // to the IRQ microprogram when the previous instruction ends.
        if (cpu.irq == 1 && cpu.fi == 1 && cpu.uav.uaddr == 0) {
                log_msg(LOG_NOTICE, cpu_log_unit, "Interrupt");
                cpu.uav.int_ = 0;       // Set the INT microcode condition 
        }

        // Update the uPC and read the microcode ROM.
        cpu.uaddr = MAKE_ADDR(cpu.uav.rst,
                              cpu.uav.int_,
                              cpu.uav.op,
                              cpu.uav.i,
                              cpu.uav.r,
                              cpu.uav.subop,
                              cpu.uav.cond,
                              cpu.uav.idx,
                              cpu.uav.uaddr);
        cpu.ucv = microcode[cpu.uaddr];
}


///////////////////////////////////////////////////////////////////////////////
//
// PRINT OUT THE CPU STATE
//
///////////////////////////////////////////////////////////////////////////////

int old_fn, old_fz, old_fv, old_fi, old_fl, old_irq;
int old_pc, old_ac, old_dr, old_sp;
int old_ctx, old_mbr[8];
int old_uaddr, old_ucv;

// BE AFRAID OF THE HACK
#define HI "\033[7m"
#define LO "\033[27m"
#define diffstate(val, old, printval)                                            \
        (((val) != (old)) && log_have_colour) ? HI : "",                 \
        (printval),                                                              \
        (((val) != (old)) && log_have_colour) ? LO : ""

static void
cpu_print_state()
{
        // Possibly the most manually-specified format specifiers in a single
        // string of my entire career.

        int log_level = cpu.uav.uaddr == 2 ? LOG_TRACE : LOG_DEBUG2;
        if (!log_is_enabled(log_level, cpu_log_unit)) return;

        log_msg(log_level, cpu_log_unit,
                "IR=%04x  "         // IR
                "%-14.14s  FL="     // disassembled instruction (no highlighting)
                "%s%c%s"            // FN
                "%s%c%s"            // FZ
                "%s%c%s"            // FV
                "%s%c%s"            // FI
                "%s%c%s"            // FL
                "  %s%s%s  "        // IRQ
                "PC=%s%04x%s  "     // PC (indicated on jumps only)
                "AC=%s%04x%s  "     // AC
                "DR=%s%04x%s  "     // DR
                "SP=%s%04x%s  "     // SP
                "CTX=%s%02x%s  MB{" // CTX
                "P=%s%02x%s "       // MB0
                "D=%s%02x%s "       // MB1
                "S=%s%02x%s "       // MB2
                "Z=%s%02x%s "       // MB3
                "4=%s%02x%s "       // MB4
                "5=%s%02x%s "       // MB5
                "6=%s%02x%s "       // MB6
                "7=%s%02x%s} "      // MB7
                "uAV=%s%06x%s "     // uAV
                "uCV=%s%06x%s "     // mCV
                "%s"                // COND
                ,
                cpu.ir,
                disasm(cpu.ir, 1, NULL),
                diffstate(cpu.fn, old_fn, cpu.fn ? 'N' : '-'),
                diffstate(cpu.fz, old_fz, cpu.fz ? 'Z' : '-'),
                diffstate(cpu.fv, old_fv, cpu.fv ? 'V' : '-'),
                diffstate(cpu.fi, old_fi, cpu.fi ? 'I' : '-'),
                diffstate(cpu.fl, old_fl, cpu.fl ? 'L' : '-'),
                diffstate(cpu.irq, old_irq, cpu.irq ? "IRQ" : "   "),

                diffstate((get_mbr(0) | cpu.pc), get_mbr(0) | ((old_pc + 1) & 0xffff), cpu.pc),
                diffstate(cpu.ac, old_ac, cpu.ac),
                diffstate(cpu.dr, old_dr, cpu.dr),
                diffstate(cpu.sp, old_sp, cpu.sp),

                diffstate(cpu.ctx, old_ctx, cpu.ctx >> 3),
                diffstate(get_mbr(0), old_mbr[0], get_mbr(0) >> 16),
                diffstate(get_mbr(1), old_mbr[1], get_mbr(1) >> 16),
                diffstate(get_mbr(2), old_mbr[2], get_mbr(2) >> 16),
                diffstate(get_mbr(3), old_mbr[3], get_mbr(3) >> 16),
                diffstate(get_mbr(4), old_mbr[4], get_mbr(4) >> 16),
                diffstate(get_mbr(5), old_mbr[5], get_mbr(5) >> 16),
                diffstate(get_mbr(6), old_mbr[6], get_mbr(6) >> 16),
                diffstate(get_mbr(7), old_mbr[7], get_mbr(7) >> 16),
                diffstate(cpu.uaddr, old_uaddr, cpu.uaddr),
                diffstate(cpu.ucv, old_ucv, cpu.ucv),
                cpu.uav.cond ? "    " : "COND");

        //old_ir = cpu.ir;
        old_fn = cpu.fn;
        old_fz = cpu.fz;
        old_fi = cpu.fi;
        old_fl = cpu.fl;
        old_irq = cpu.irq;
        old_pc = cpu.pc;
        old_ac = cpu.ac;
        old_dr = cpu.dr;
        old_sp = cpu.sp;
        old_ctx = cpu.ctx;
        old_mbr[0] = get_mbr(0);
        old_mbr[1] = get_mbr(1);
        old_mbr[2] = get_mbr(2);
        old_mbr[3] = get_mbr(3);
        old_mbr[4] = get_mbr(4);
        old_mbr[5] = get_mbr(5);
        old_mbr[6] = get_mbr(6);
        old_mbr[7] = get_mbr(7);
        old_uaddr = cpu.uaddr;
        old_ucv = cpu.ucv;
}

#undef HI
#undef LO
#undef diffstate


///////////////////////////////////////////////////////////////////////////////
//
// MAIN EMULATION LOOP
//
///////////////////////////////////////////////////////////////////////////////


void
cpu_run()
{
        assert (cpu.memr != NULL);
    
        // Reset the emulation and CPU 
        cpu.tick = 0;
        cpu.wait = 0;
        cpu.halt = 0;
        // extern int dfp_enabled;
        // cpu.pause = dfp_enabled ? 1 : 0;
        cpu_reset();

        // time_t t0 = time(NULL);
        // word oldpc = 0xbeef;
        
        //word addr;
        //static struct timespec ts;
        cpu.quit = 0;
        while(!cpu.quit) {
                volatile int p;
                for (p = 0; p < 50; p++);

                // Do nothing if the emulation is paused. 
                if (cpu.pause || cpu.halt) {
                        // ui_tick();
                        // dfp_tick(); // the DFP always runs
                        usleep(1000);
                        continue;
                }

                // Handle the reset pulse
                cpu_handle_reset();

                // Let the control store run.
                cpu_control_store();

                // Print out current address and instruction.
                // if(debug_asm) {
                //     if (cpu.uav.uaddr == 0) {
                //         oldpc = cpu.pc;
                //     } else if (cpu.uav.uaddr == 2) {
                //         dump_mini(oldpc);
                //     }
                // }

                // Decode the control vector from the uROM.

                int raddr = GET_READ(cpu.ucv);
                int waddr = GET_WRITE(cpu.ucv);
                int cond = GET_IF(cpu.ucv);
                int action = GET_ACTION(cpu.ucv);

                int mem = IS_MEM(cpu.ucv);
                int io = IS_IO(cpu.ucv);
                int r = IS_REN(cpu.ucv);
                int w = IS_WEN(cpu.ucv);
                int end = IS_END(cpu.ucv);

                // External END?
                if (cpu.endext) {
                        debug("End of instruction requested externally.");
                        end = 1;
                        cpu.endext = 0;
                }

                // Print CPU state.
                // if (debug_microcode) {
                //     printf("");
                //     info("PC: %04x/%d", cpu.pc, cpu.uav.uaddr);
                //     dump_state();
                //     dump_ustate();
                // }
                cpu_print_state();

                // Act on the signals of the control vector. All actions are
                // essentially level comparisons, edge-sensitive signals are
                // dealt with as if they too were level-sensitive. This could
                // give rise to a few bugs, which we'll kludge here.
                
                // Decode conditionals and set the SKIP signal for the next
                // microinstruction.
                decode_cond(cond);
                
                // Handle memory and I/O *READS*
                if (r) {
                        bus_reads(mem, io);
                        cpu.ibus = cpu.dbus;
                }
                
                // Read from a unit.
                if (raddr) {
                        cpu.ibus = read_from_ibus_unit(raddr);
                }

                // Write to a unit.
                if (waddr) {
                        write_to_ibus_unit(waddr);
                }

                // Drive the data bus if needed
                if (w) {
                        cpu.dbus = cpu.ibus;
                }

                // Handle memory and I/O *WRITES*
                if (w) bus_writes(mem, io);

                // Perform any decoded action.
                if (action) handle_actions(action);

                // External SKIP? Test this late, so either bus transactions can
                // trigger it.
                if (cpu.skipext) {
                        debug("Skip requested externally.");
                        cpu.uav.cond = 0;
                        cpu.skipext = 0;
                }

                // Next processor cycle!
                cpu.tick++;

                // End of the instruction?
                if (end) {
                        //dump_state();
                        cpu.agl_page = get_page(cpu.pc);
                        cpu.uav.uaddr = 0;
                        cpu.uav.int_ = 1; // Clear the INT microcode condition 
                        debug("End of microprogram.");
                } else if (!cpu.wait) {
                        // Support for wait states is present at this level, but nothing
                        // uses them (yet). All our emulated devices are super-fast.
                        cpu.uav.uaddr++;
                        if (cpu.uav.uaddr == 0) {
                                fatal("uPC wrapped around! Microcode bug?");
                        }
                }

                // Perform 'background' 'hardware' tasks.
                if (cpu.iotick != NULL) (*cpu.iotick)(&cpu, 0);
        }

        // One last forced I/O tick to flush out TTY buffers, etc
        if (cpu.iotick != NULL) (*cpu.iotick)(&cpu, 1);

        // time_t t1 = time(NULL);
        // if (t1 != t0) {
        //     info("Time: %s%lu%s s. Speed: %s%lu%s kHz",
        //          COL_WHI, t1 - t0, COL_GRE,
        //          COL_WHI, cpu.tick / (t1 - t0) / 1000, COL_GRE);
        // }
}

// End of file.
// Local Variables:
// eval: (c-set-style "K&R")
// c-basic-offset: 8
// indent-tabs-mode: nil
// fill-column: 79
// End:
